lynchaj/duodyne/!Development/16 input-output.VDCENET, V1.0/readme.txt

The VDCENET IO board provides MOSTEK 8568 VDC video and an RTL8019AS wired Ethernet interface
