lynchaj/duodyne/!Development/22 input-output.BusExtender, V1.0/readme.md

This board extends the duodyne bus to the top of the other boards to aid in debugging and new board development
