lynchaj/duodyne/!Development/21 input-output.MCU-CPLD, V1.0/readme.txt

This board provides a SAB80535 MCU and EPM7128S for prototyping electronic projects with prototyping area.
