lynchaj/duodyne/!Development/Slick/readme.txt

The processor.Z80 board is the central processor for the duodyne system.  It uses a Z80 8-bit CPU and includes dual-DMA channels.  It supports Interrupt Mode 2 (IM2) and an extended memory mapper.

Known Issues
1. Missing pull-up resistors on ~DREQ0 and ~DREQ1
