lynchaj/duodyne/!Development/13 input-output.GDC, V1.0/readme.txt

This board provides a blank template for making input-output boards.  GAL information is notional and should be replaced with project specifics using Digital
