lynchaj/duodyne/!Development/08 input-output.Disk, V1.1/readme.txt

This board provides PPIDE for IDE hard drives and/or CF adapters and floppy drive controller.  Primary intended uses are for CF adapters and 3.5" floppy drives
