lynchaj/duodyne/duodyne.interrupt.survey.pdf

BOARD | DEVICE | INTERRUPTS | ENABLE JUMPER | IN/OUT
Processor.Z80 | DMA1 | INT0 | YES | OUT
Processor.Z80 | DMA2 | INT0 | YES | OUT
Processor.Z80 | IM2 | INT0 | YES | OUT
Processor.Z80 | UART | EIRQ0 | YES | OUT
IO.Zilog | 1CTC | INT0 | YES | OUT
IO.Zilog | SIO | INT0 | YES | OUT
IO.Zilog | 1PIO | INT0 | YES | OUT
IO.Zilog | 2PIO | INT0 | YES | OUT
IO.Zilog | 2CTC | INT1, INT2 | YES | IN
IO.Zilog | 2CTC | INT0 | YES | OUT
IO.Multi | DUART.A | INT0, EIRQ0-7 | YES | OUT
IO.Multi | DUART.B | INT0, EIRQ0-7 | YES | OUT
IO.Multi | Parallel | INT0, EIRQ0-7 | YES | OUT
IO.Multi | KBDMSE | INT0, EIRQ0-7 | YES | OUT
IO.Multi | USB | INT0, EIRQ0-7 | YES | OUT
IO.Disk | FDC | INT0, EIRQ0-7 | YES | OUT
IO.Disk | Ethernet | INT0, EIRQ0-7 | YES | OUT
IO.Voice | ADC | INT0, EIRQ0-7 | YES | OUT
IO.Media | VDP | INT0, EIRQ0-7 | YES | OUT

All=
