lynchaj/duodyne/00 enclosure, V1.0/20250329_211026.jpg

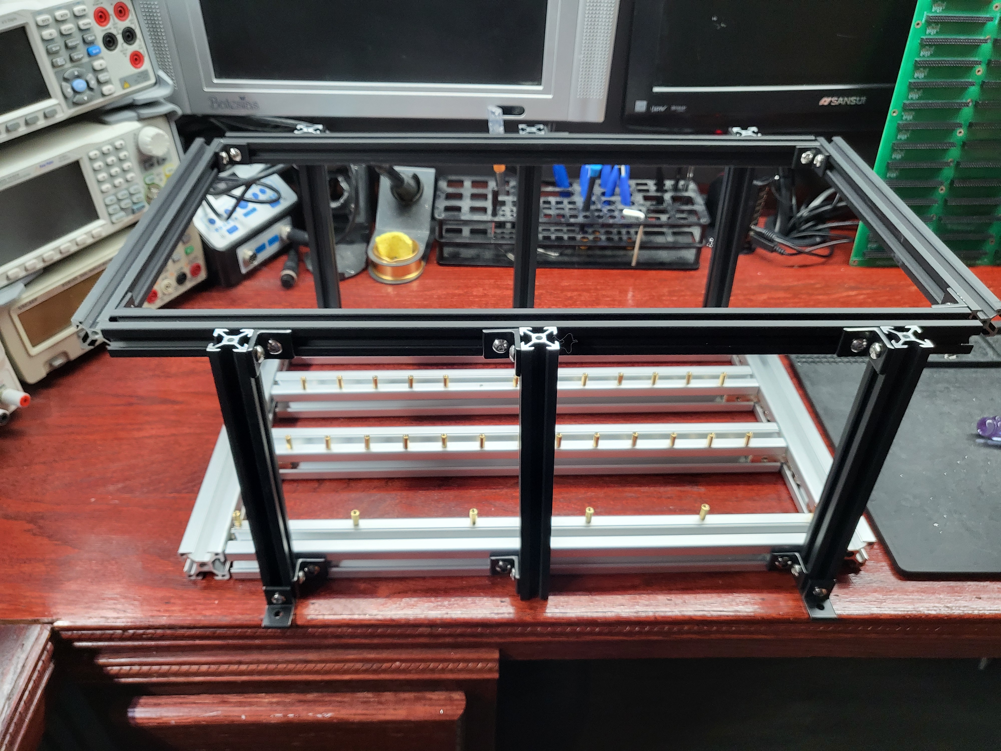
00 enclosure, V1.0/20250329_211026.jpg
