lynchaj/duodyne/00 enclosure, V1.0/Picture1.jpg

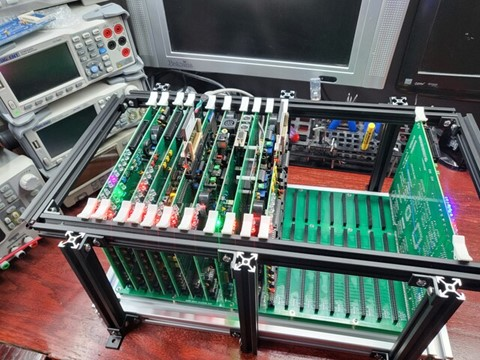
00 enclosure, V1.0/Picture1.jpg
