lynchaj/duodyne/00 enclosure, V1.0/Picture2.jpg

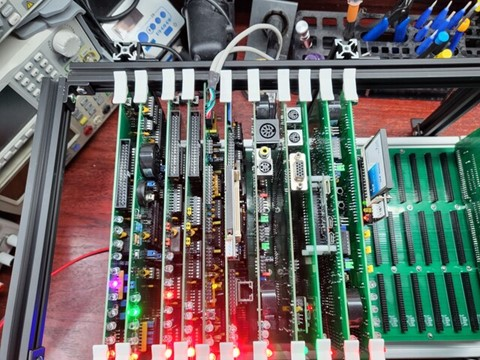
00 enclosure, V1.0/Picture2.jpg
