lynchaj/duodyne/01 template.prototyping, V1.0/template.prototyping.jpg

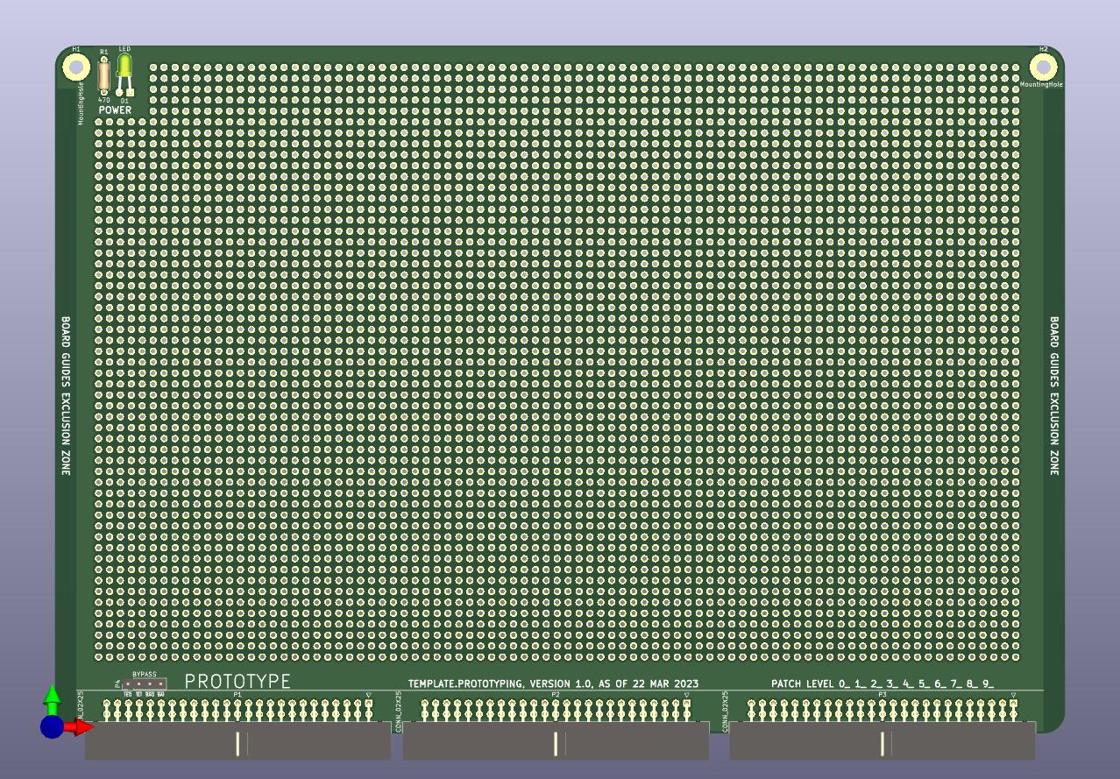
01 template.prototyping, V1.0/template.prototyping.jpg
