lynchaj/duodyne/02 backplane.8-slot, V1.0/backplane.8-slot.jpg

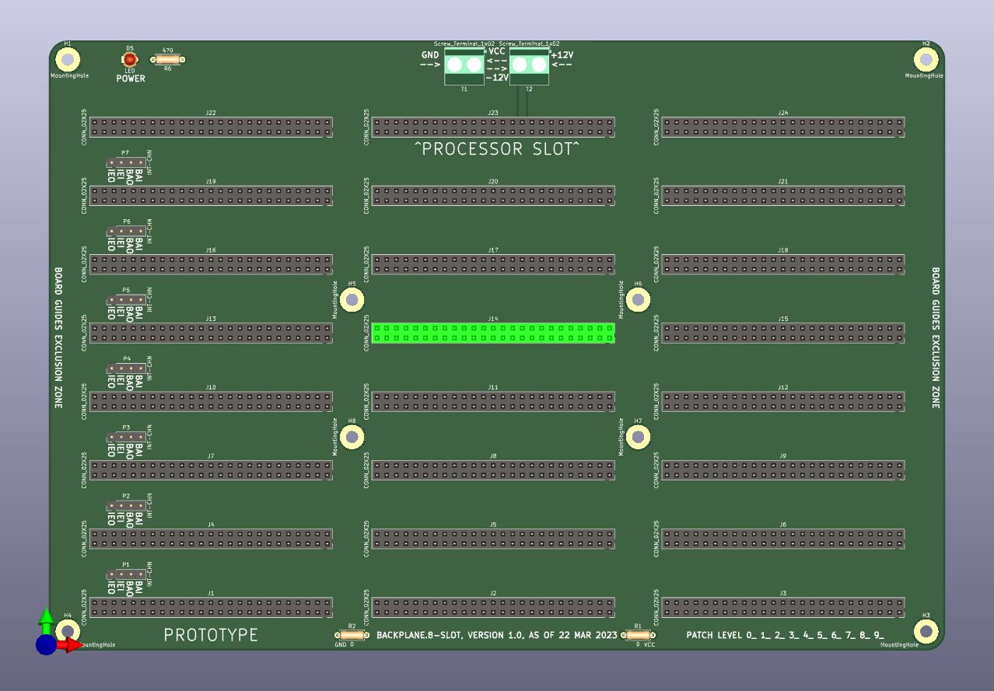
02 backplane.8-slot, V1.0/backplane.8-slot.jpg
