lynchaj/duodyne/03 processor.Z80, V1.1/CPU-DATA-DIR-GAL-V3.png

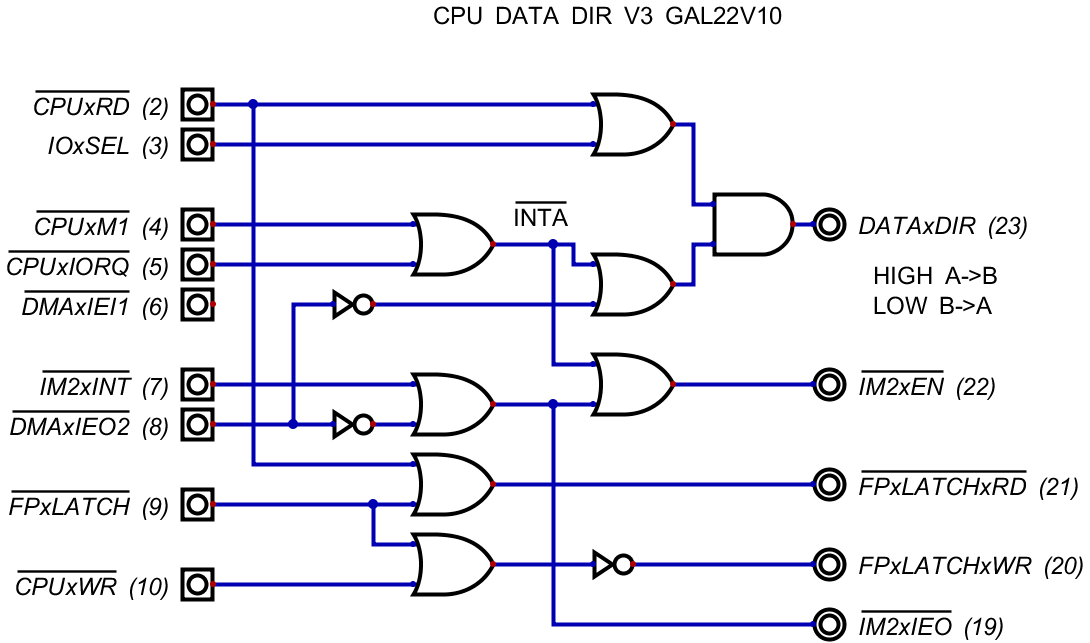
03 processor.Z80, V1.1/CPU-DATA-DIR-GAL-V3.png
