lynchaj/duodyne/03 processor.Z80, V1.1/CPU-MAPPER-V3.png

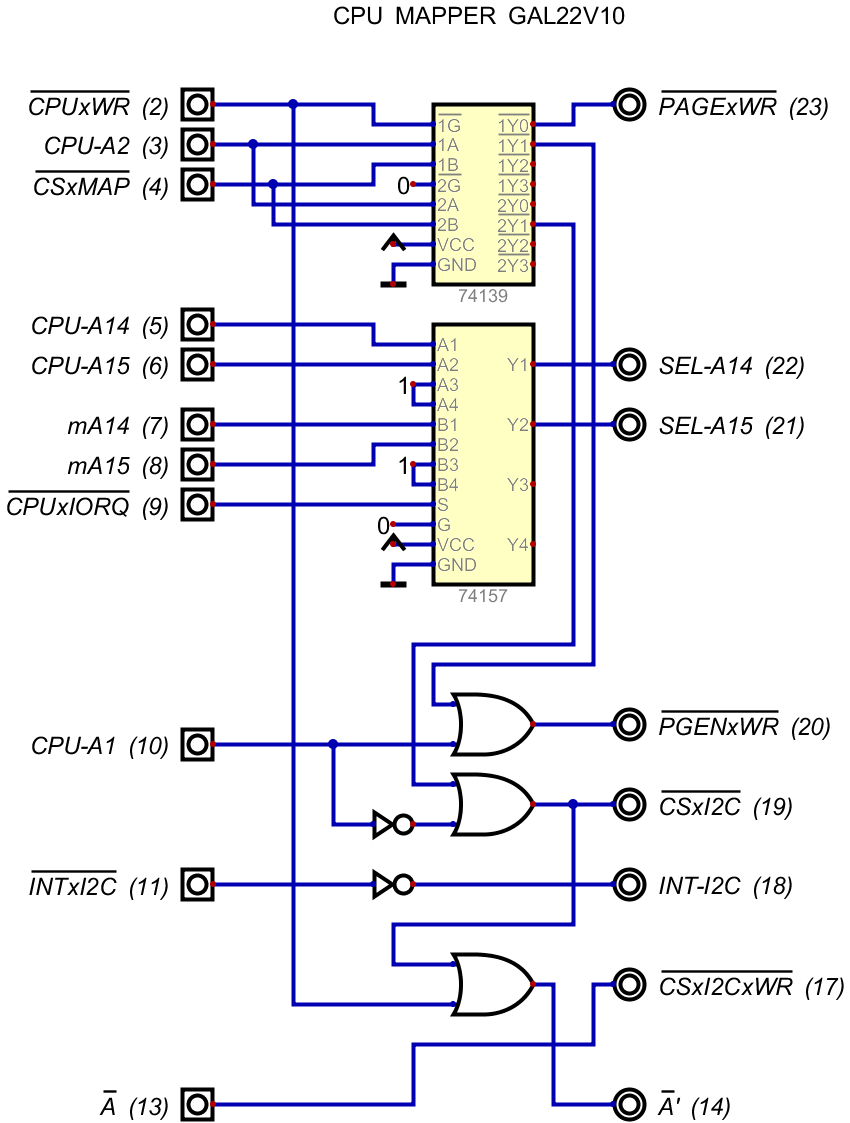
03 processor.Z80, V1.1/CPU-MAPPER-V3.png
