lynchaj/duodyne/03 processor.Z80, V1.1/DMA-CS-GAL-V4.png

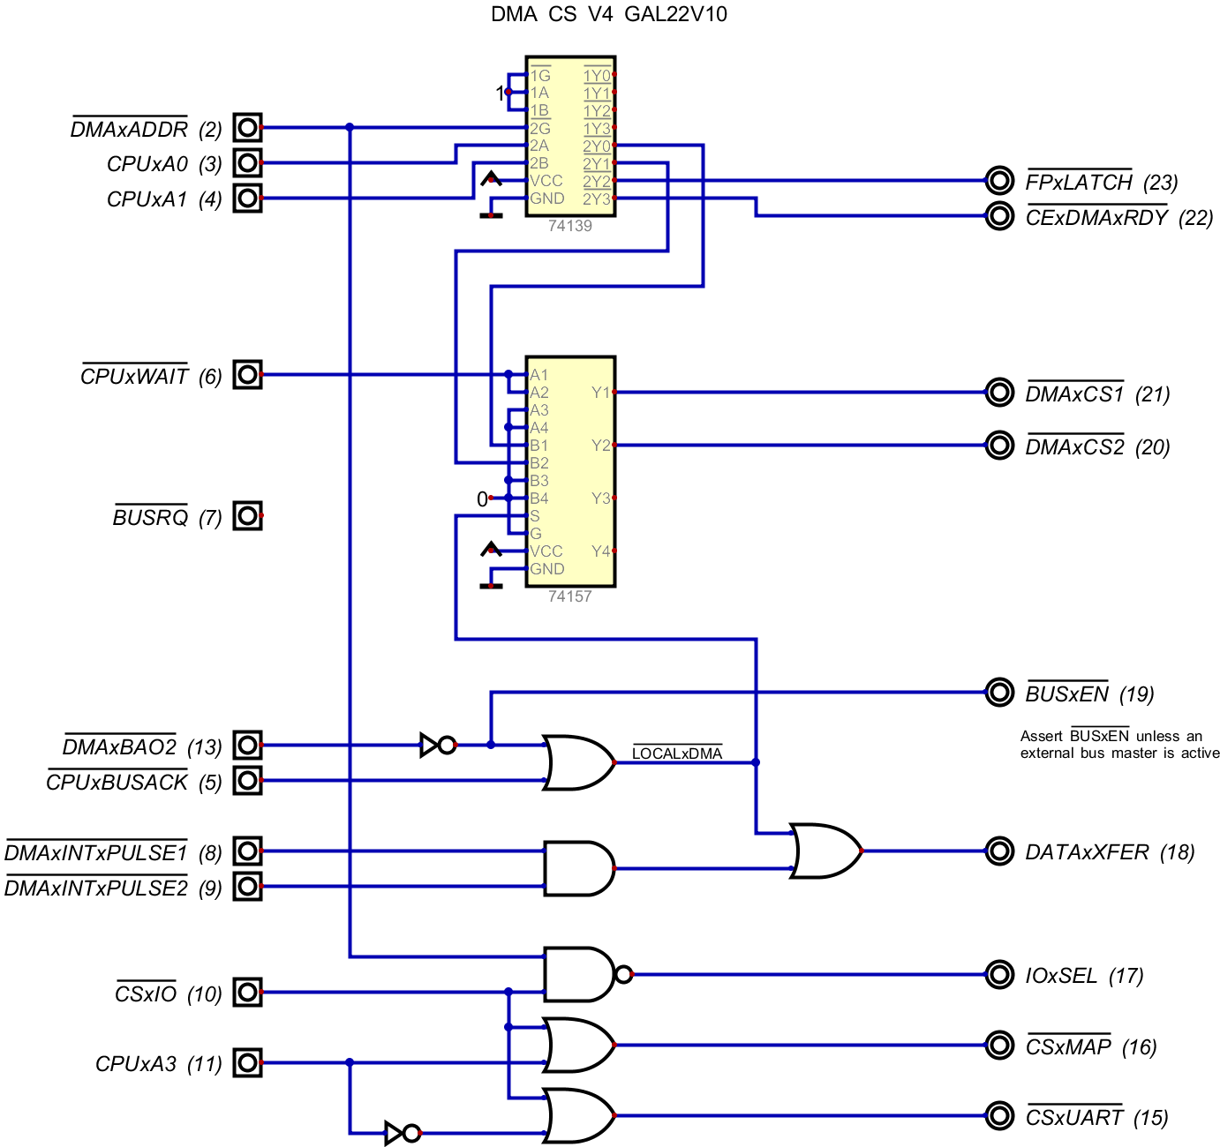
03 processor.Z80, V1.1/DMA-CS-GAL-V4.png
