lynchaj/duodyne/03 processor.Z80, V1.1/processor.Z80.jpg

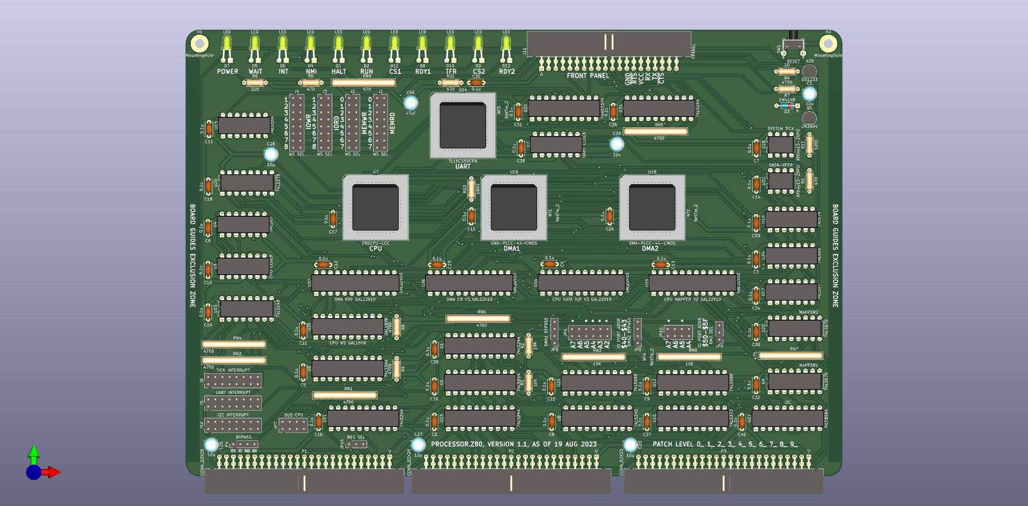
03 processor.Z80, V1.1/processor.Z80.jpg
