lynchaj/duodyne/04 memory.ROMRAM.8-bit, V1.1/memory.ROMRAM.jpg

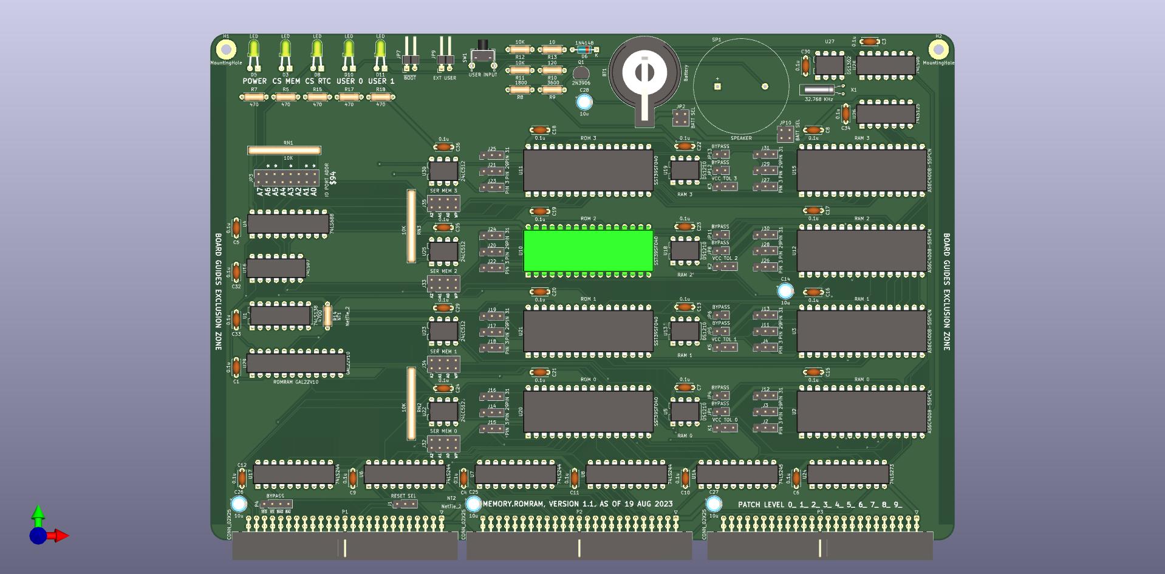
04 memory.ROMRAM.8-bit, V1.1/memory.ROMRAM.jpg
