lynchaj/duodyne/05 input-output.Zilog, V1.1/input-output.Zilog.jpg

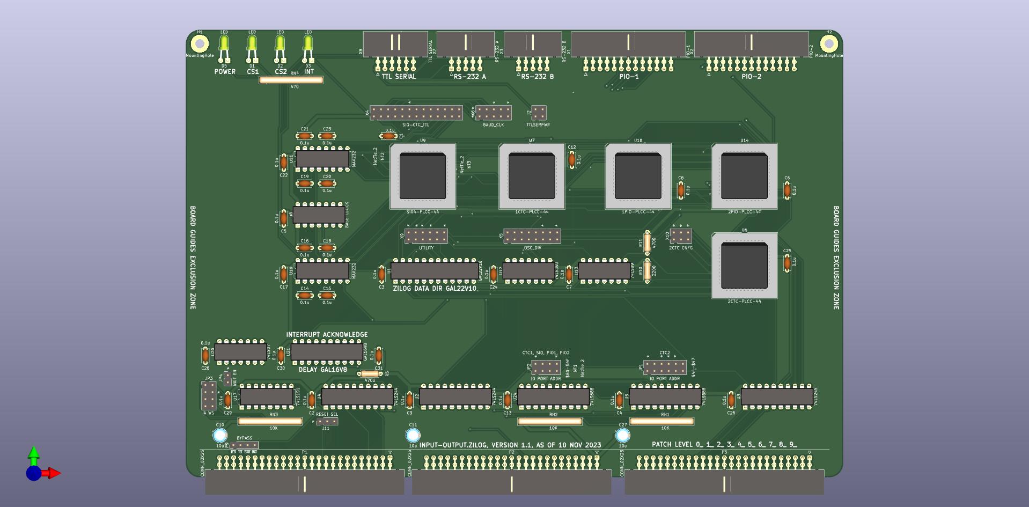
05 input-output.Zilog, V1.1/input-output.Zilog.jpg
