lynchaj/duodyne/05 input-output.Zilog, V1.1/temp/ZP-DATA-DIR-GAL.png

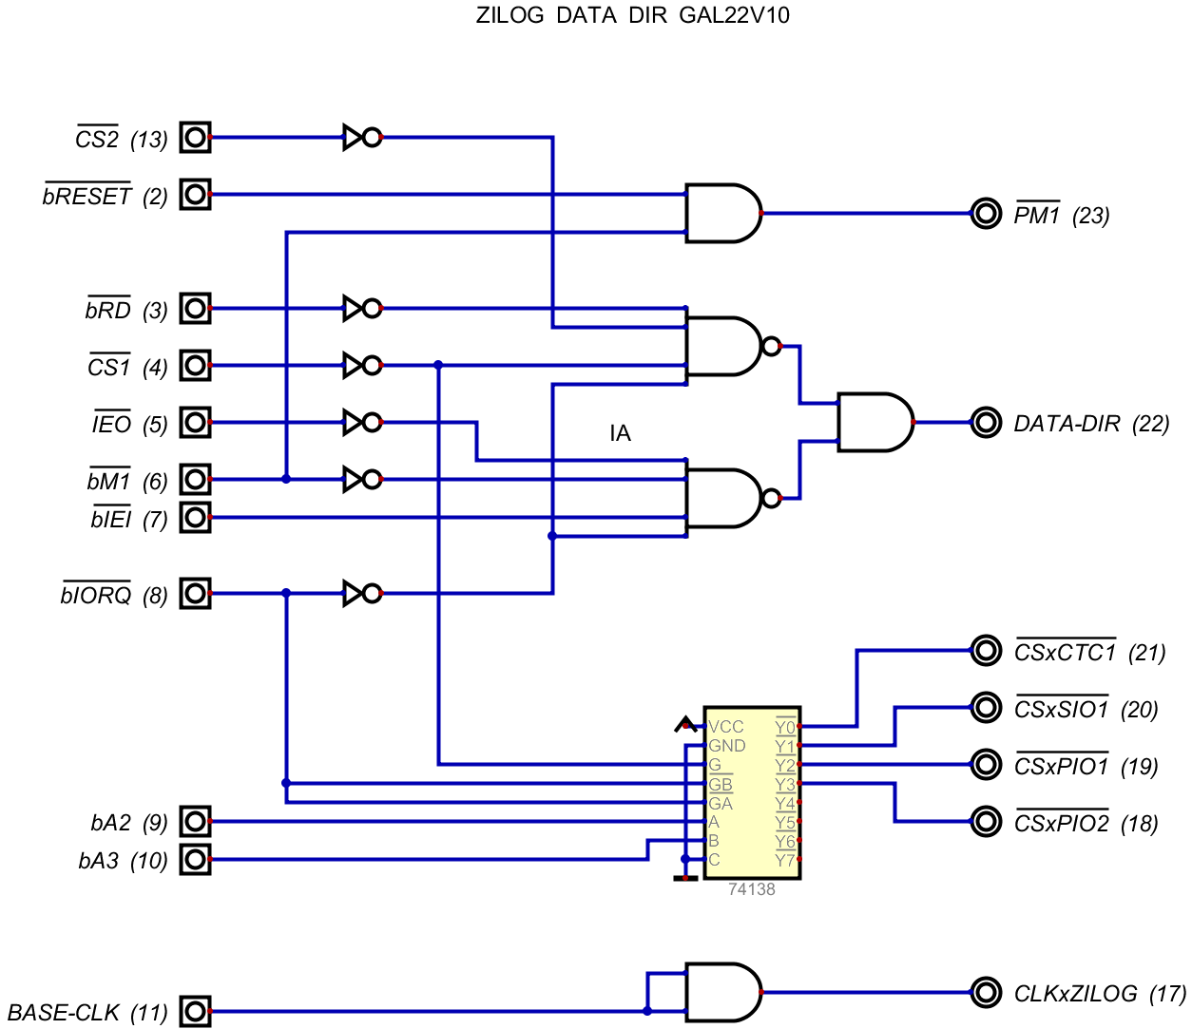
05 input-output.Zilog, V1.1/temp/ZP-DATA-DIR-GAL.png
