lynchaj/duodyne/05 input-output.Zilog, V1.1/ZP-DATA-DIR-GAL-V2.png

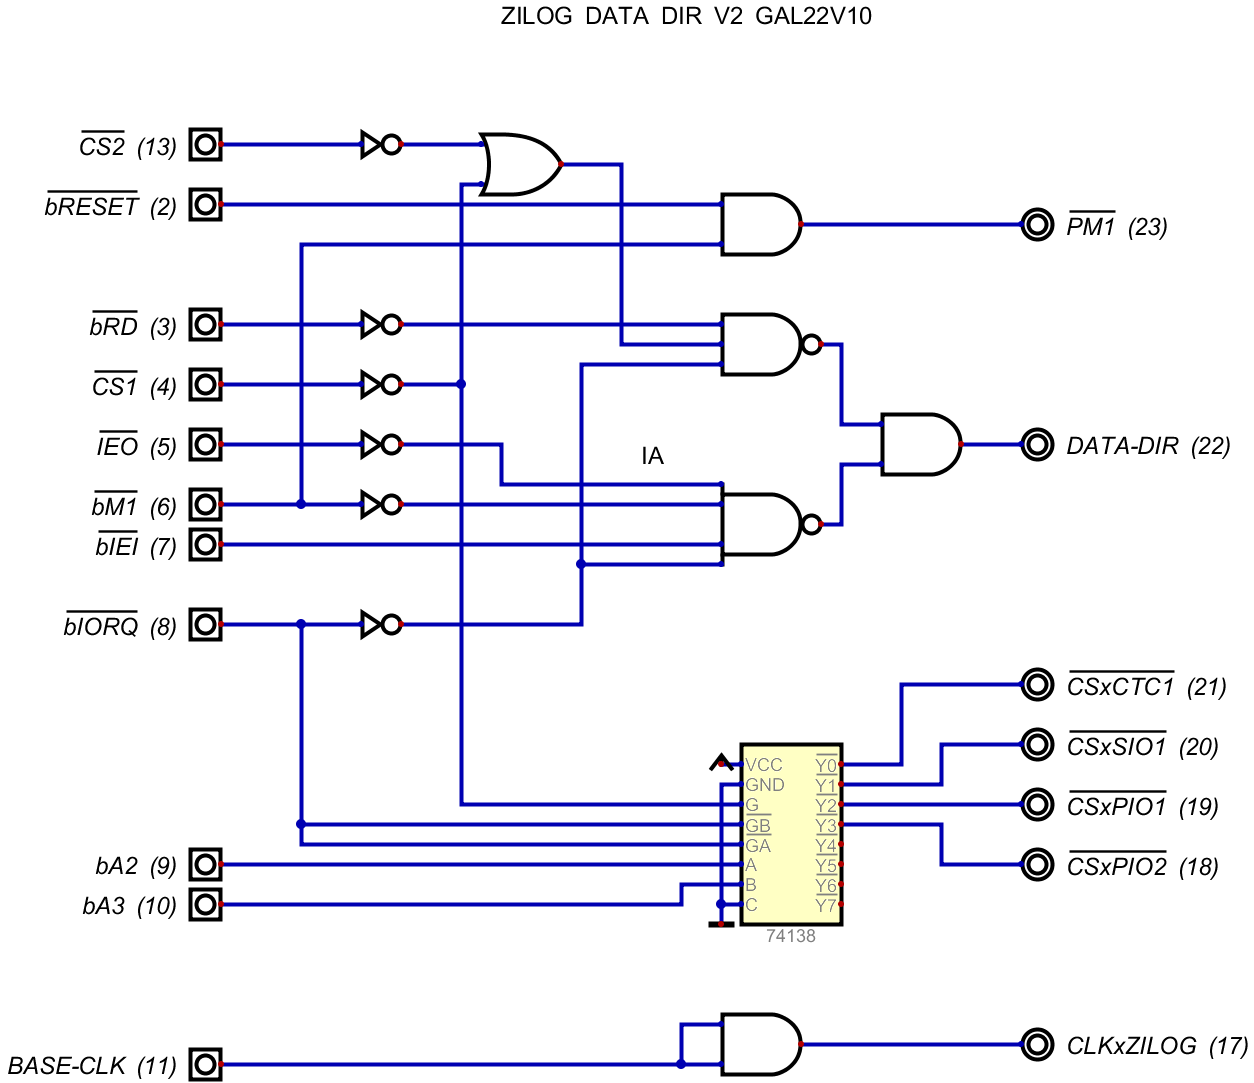
05 input-output.Zilog, V1.1/ZP-DATA-DIR-GAL-V2.png
