lynchaj/duodyne/05 input-output.Zilog, V1.1/ZP-IA-DELAY-GAL.png

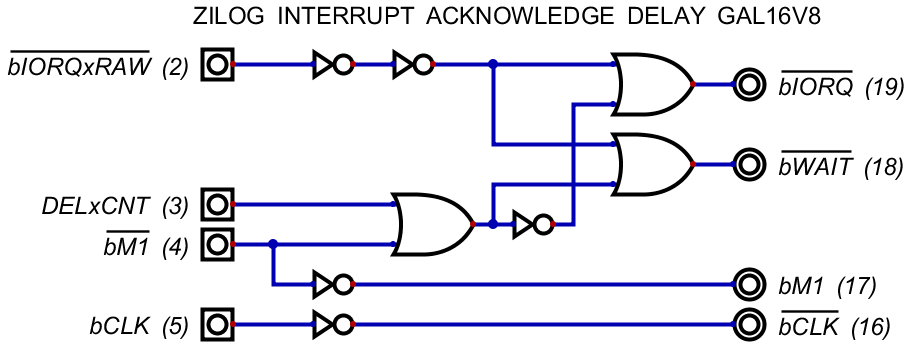
05 input-output.Zilog, V1.1/ZP-IA-DELAY-GAL.png
