lynchaj/duodyne/06 input-output.Multi, V1.0/input-output.Multi.jpg

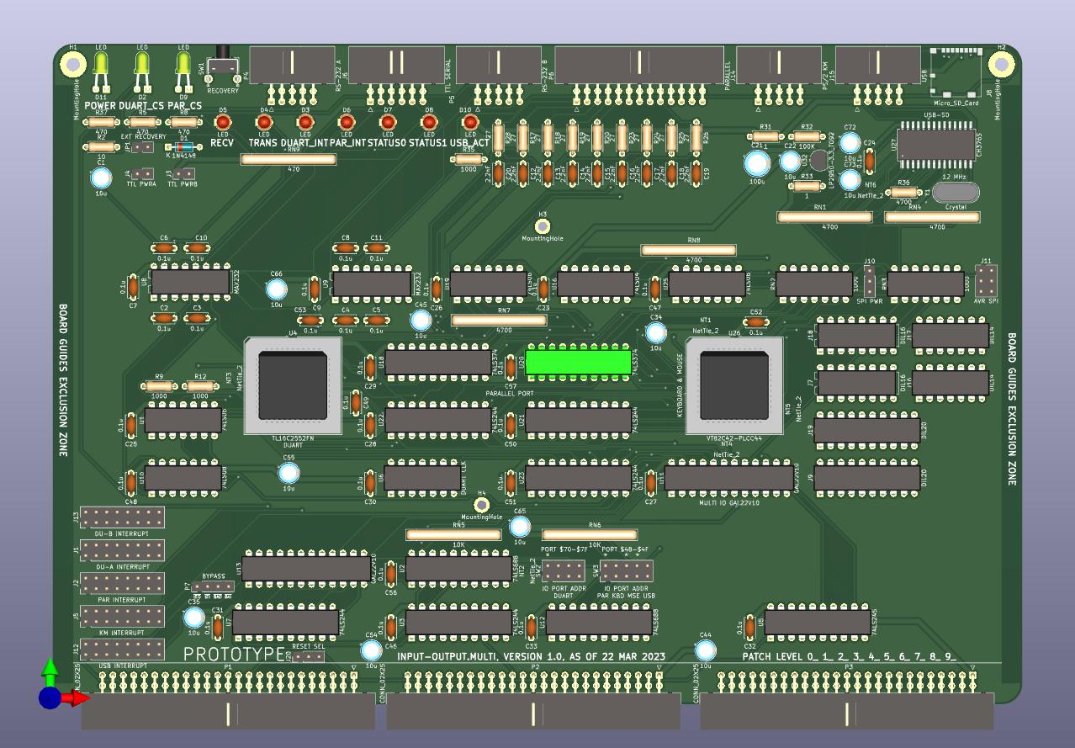
06 input-output.Multi, V1.0/input-output.Multi.jpg
