lynchaj/duodyne/07 backplane.4-slot, V1.0/backplane.4-slot.jpg

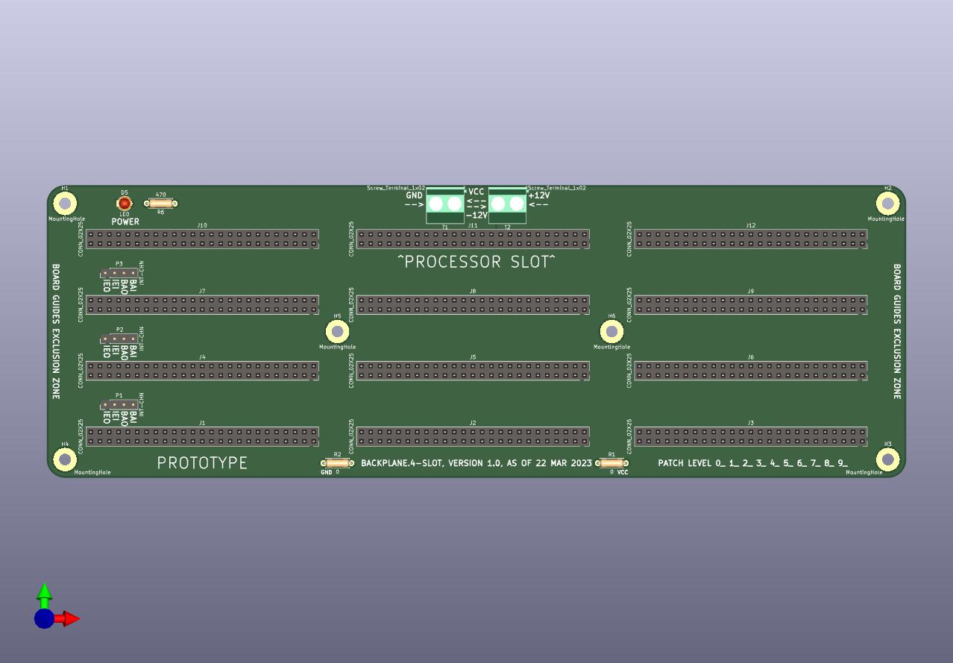
07 backplane.4-slot, V1.0/backplane.4-slot.jpg
