lynchaj/duodyne/08 input-output.Disk, V1.0/temp/3D-View_SD-Card_Holder.png

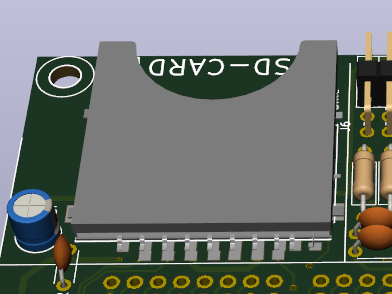
08 input-output.Disk, V1.0/temp/3D-View_SD-Card_Holder.png
