lynchaj/duodyne/08 input-output.Disk, V1.0/temp/FDC-CS-GAL.png

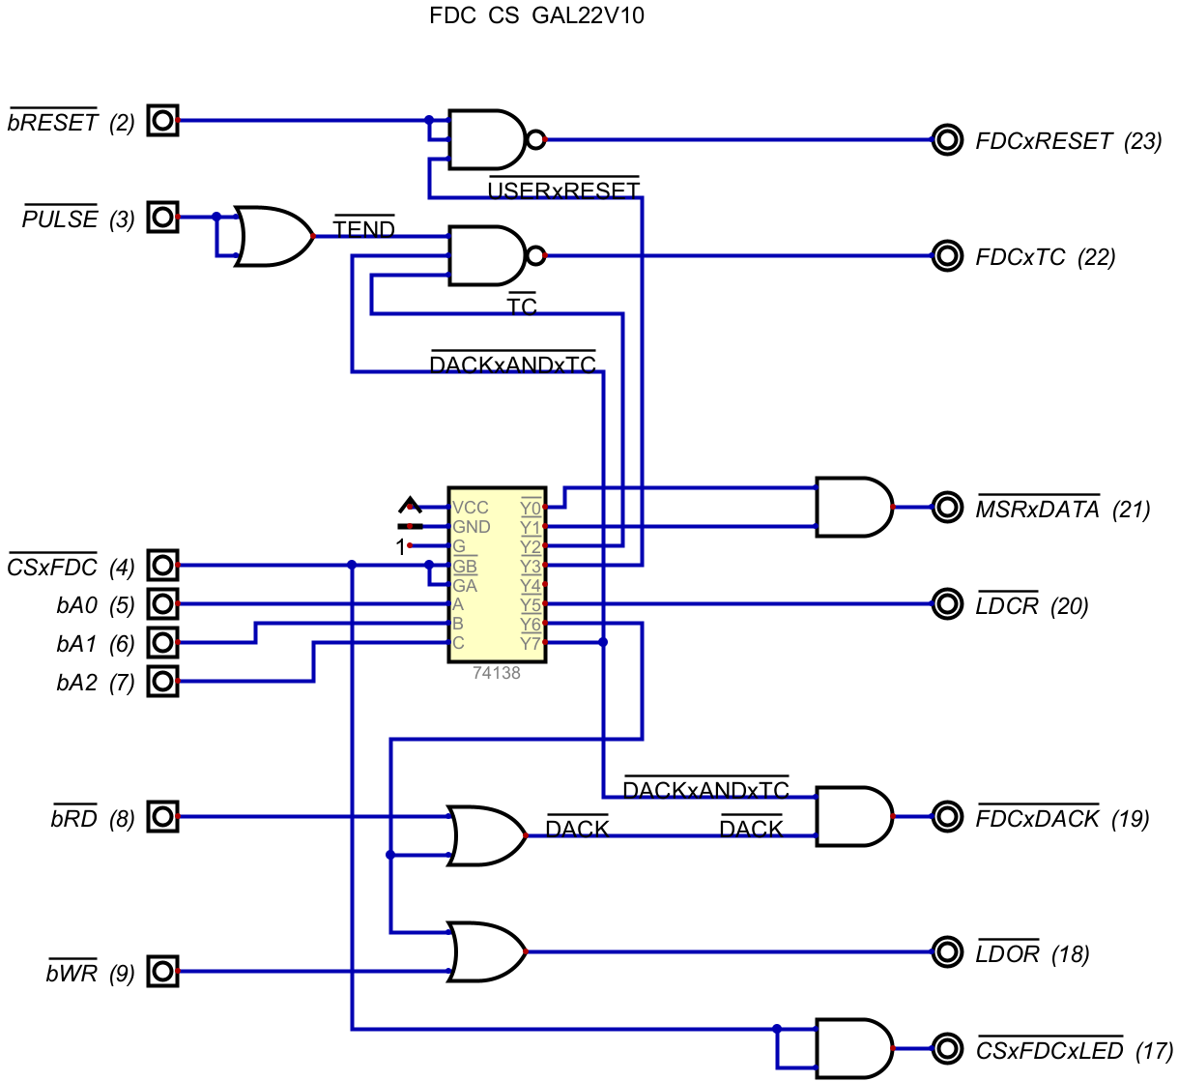
08 input-output.Disk, V1.0/temp/FDC-CS-GAL.png
