lynchaj/duodyne/08 input-output.Disk, V1.0/temp/SD-Card_Footprint_on_PCB.png

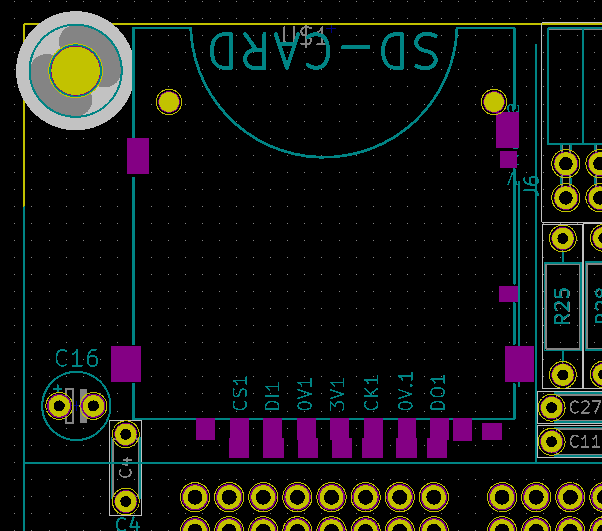
08 input-output.Disk, V1.0/temp/SD-Card_Footprint_on_PCB.png
