lynchaj/duodyne/10 input-output.Voice, V1.0/input-output.Voice.jpg

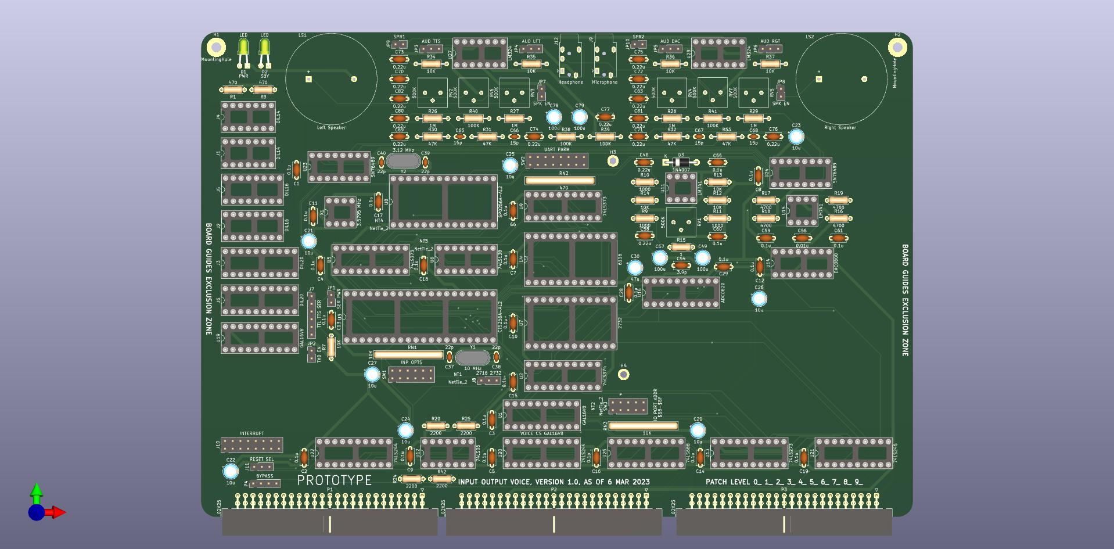
10 input-output.Voice, V1.0/input-output.Voice.jpg
