lynchaj/duodyne/10 input-output.Voice, V1.0/temp/VOICE-CS-GAL-V2.png

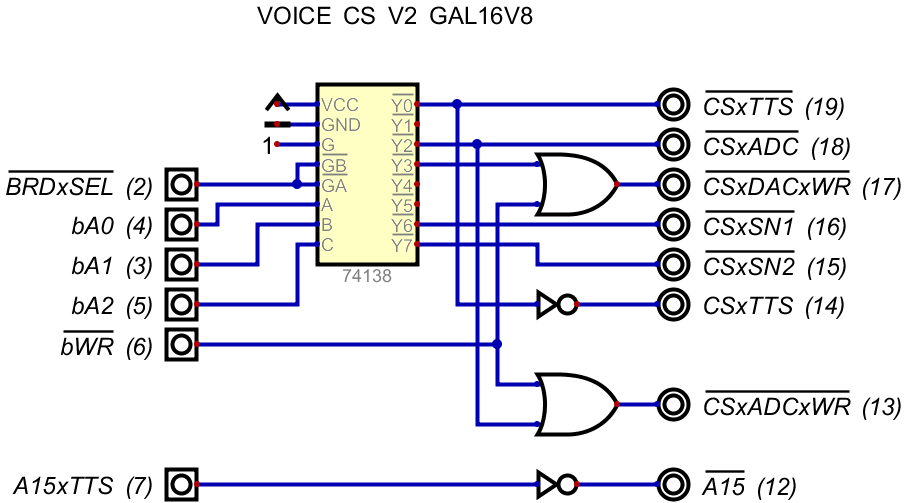
10 input-output.Voice, V1.0/temp/VOICE-CS-GAL-V2.png
