lynchaj/duodyne/10 input-output.Voice, V1.0/temp/Z180GDCV2-SND/U10.png

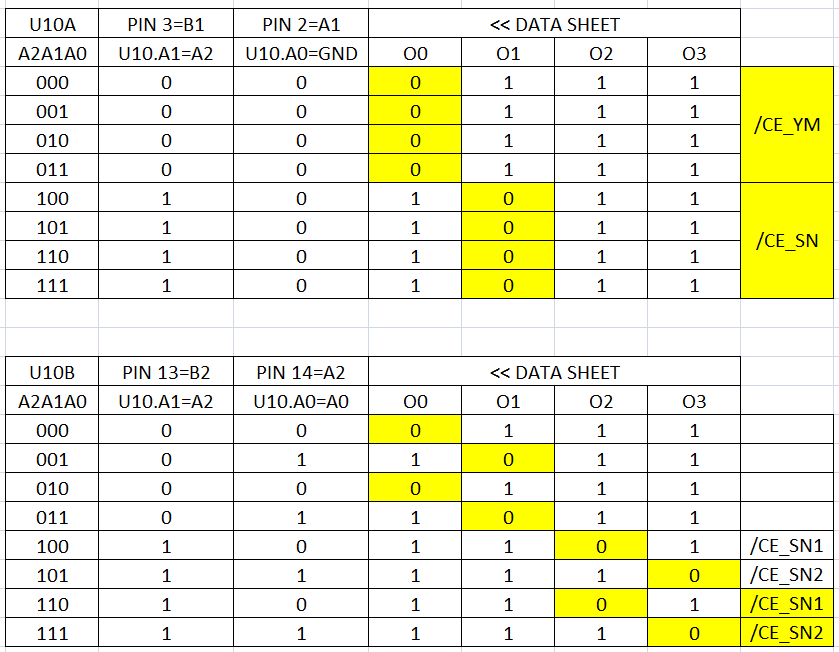
10 input-output.Voice, V1.0/temp/Z180GDCV2-SND/U10.png
