lynchaj/duodyne/10 input-output.Voice, V1.0/VOICE-CS-GAL-V3.png

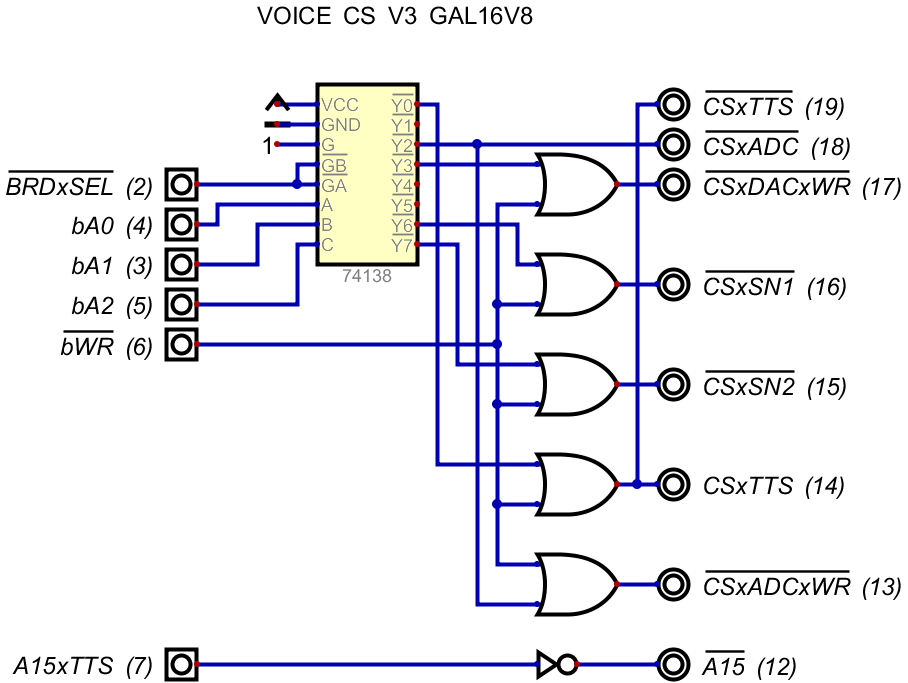
10 input-output.Voice, V1.0/VOICE-CS-GAL-V3.png
