lynchaj/duodyne/11 input-output.Media, V1.1/FPGA Emulator Interface.png

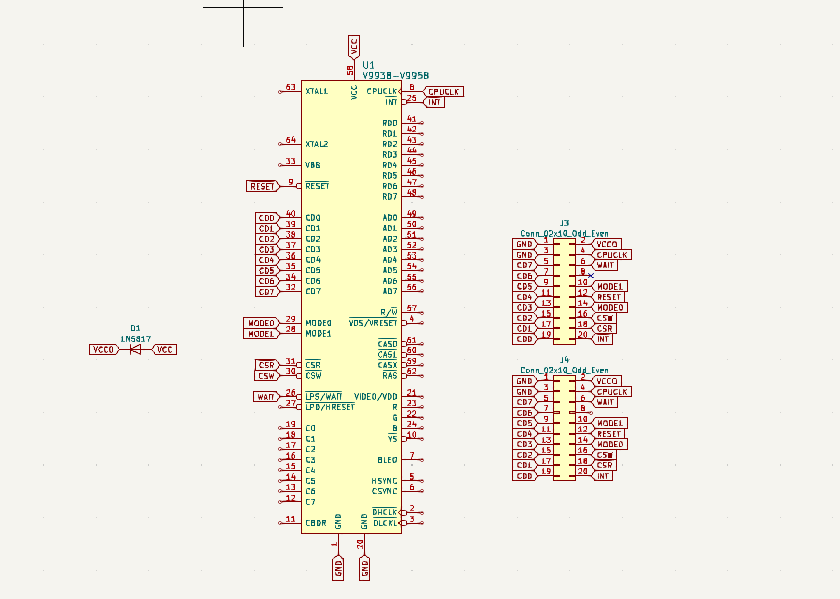
11 input-output.Media, V1.1/FPGA Emulator Interface.png
