lynchaj/duodyne/11 input-output.Media, V1.1/image001.png

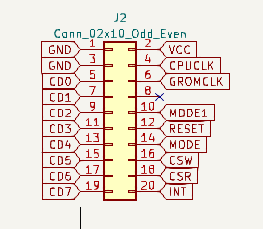
11 input-output.Media, V1.1/image001.png
