lynchaj/duodyne/11 input-output.Media, V1.1/input-output.Media-BACK.jpg

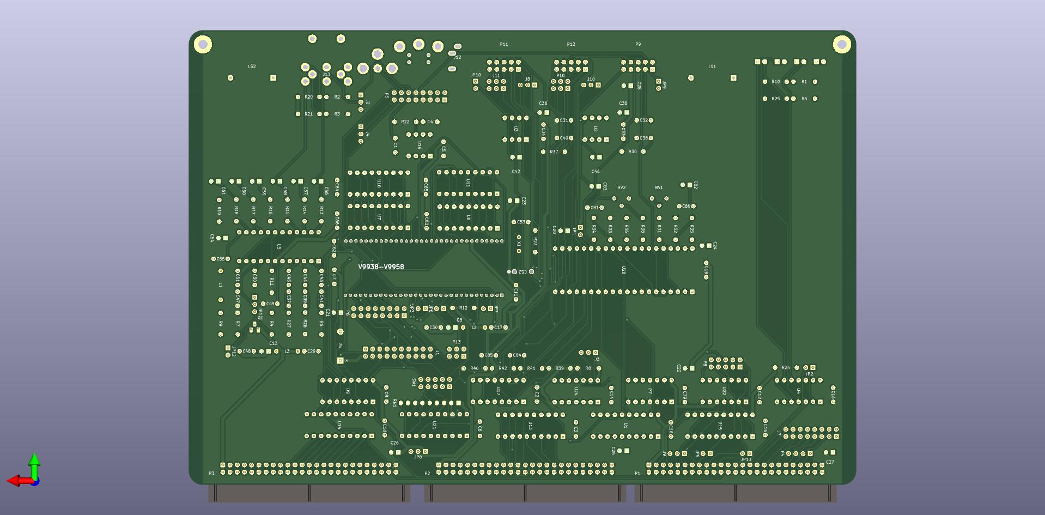
11 input-output.Media, V1.1/input-output.Media-BACK.jpg
