lynchaj/duodyne/11 input-output.Media, V1.1/MEDIA-CS-GAL-V3.png

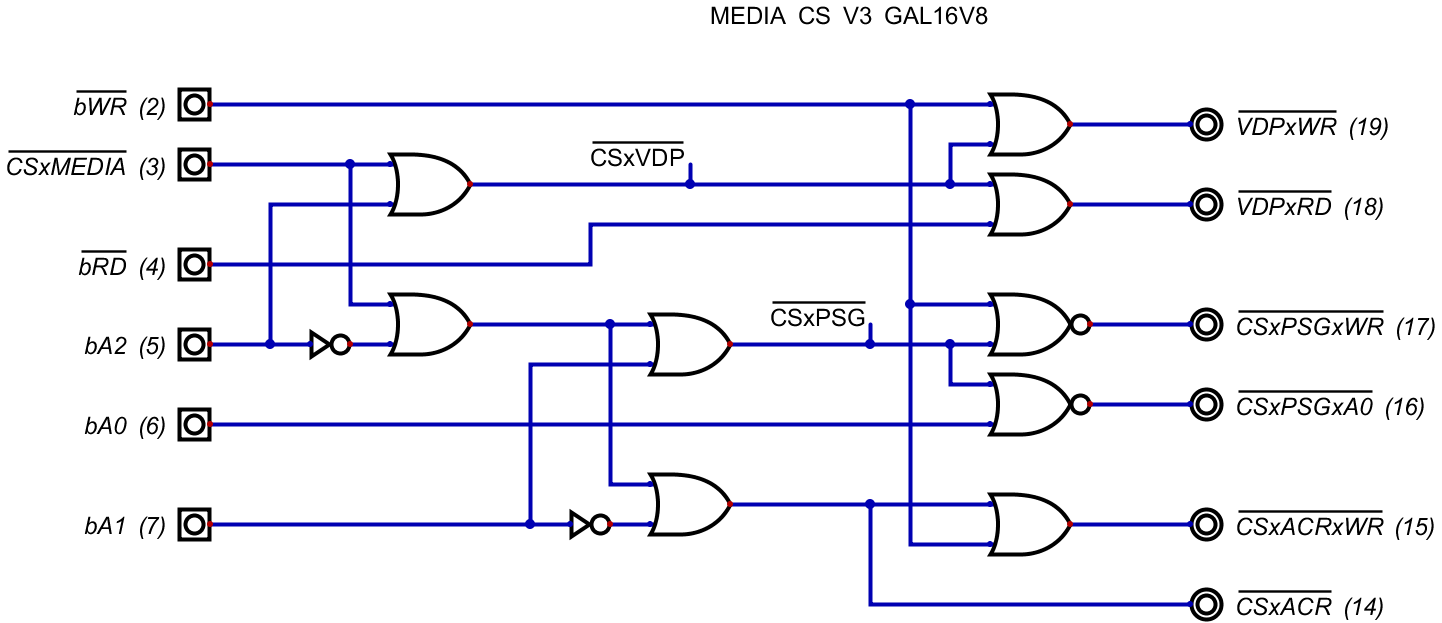
11 input-output.Media, V1.1/MEDIA-CS-GAL-V3.png
