lynchaj/duodyne/11 input-output.Media, V1.1/temp/MEDIA-CS-GAL.png

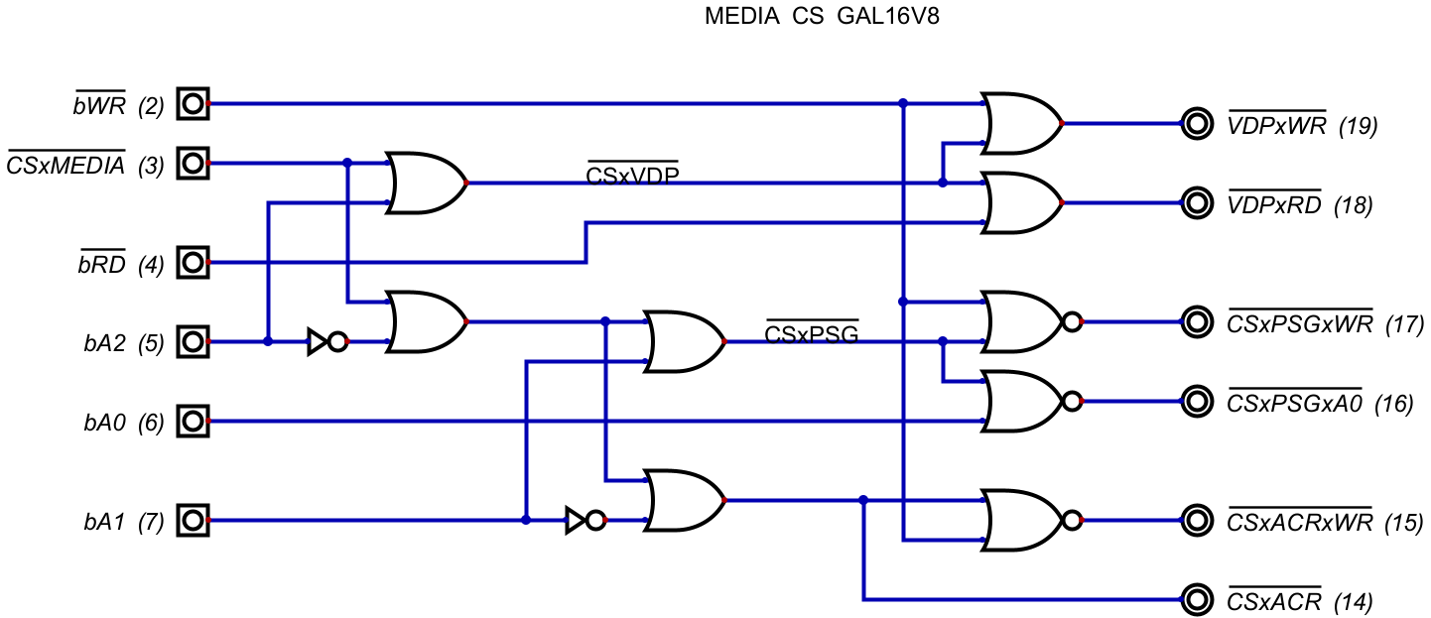
11 input-output.Media, V1.1/temp/MEDIA-CS-GAL.png
