lynchaj/duodyne/11 input-output.Media, V1.1/temp/MEDIA-CS-V2-GAL.png

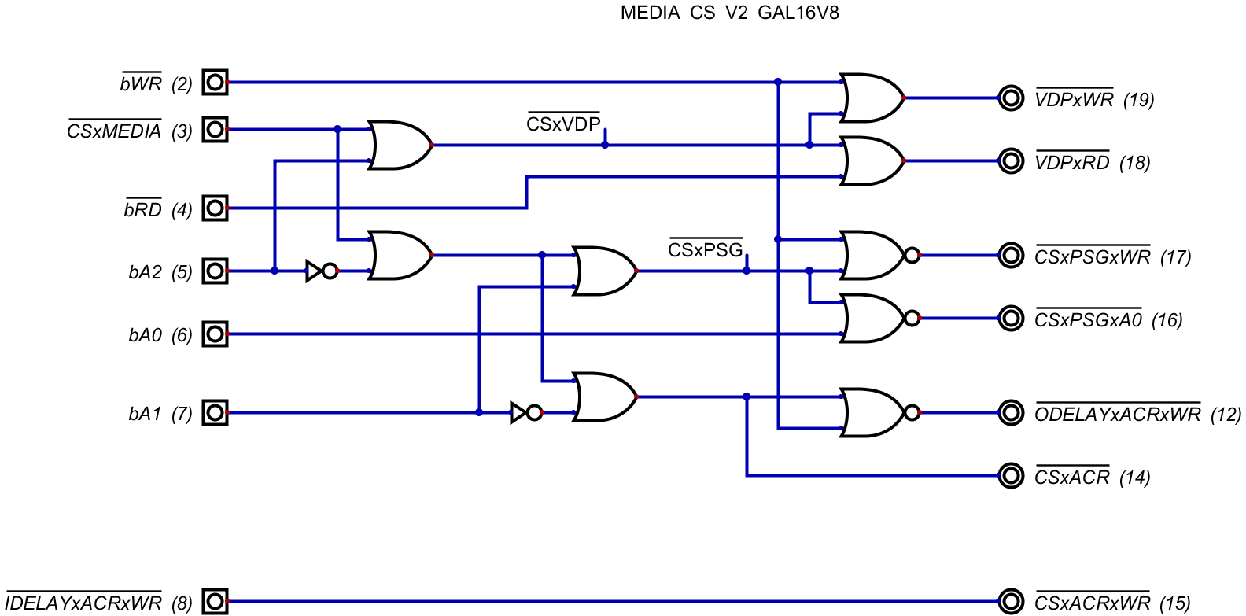
11 input-output.Media, V1.1/temp/MEDIA-CS-V2-GAL.png
