lynchaj/duodyne/13 front-panel.processor ALT/hardware/wayne front panel concept.png

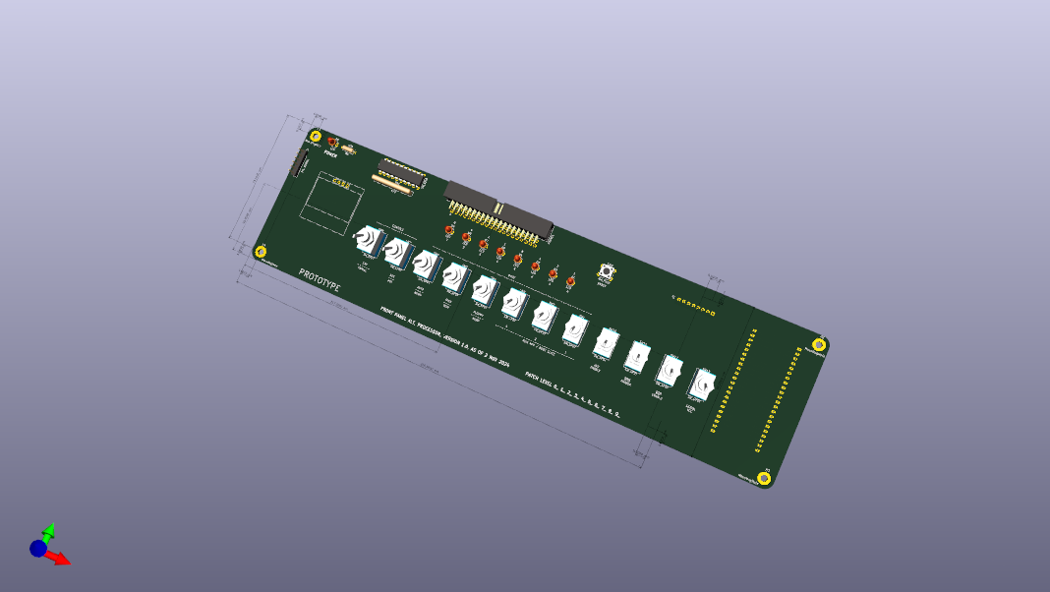
13 front-panel.processor ALT/hardware/wayne front panel concept.png
