lynchaj/duodyne/17 input-output.DualESP32, V1.0/hardware/DUALESP32 GAL.png

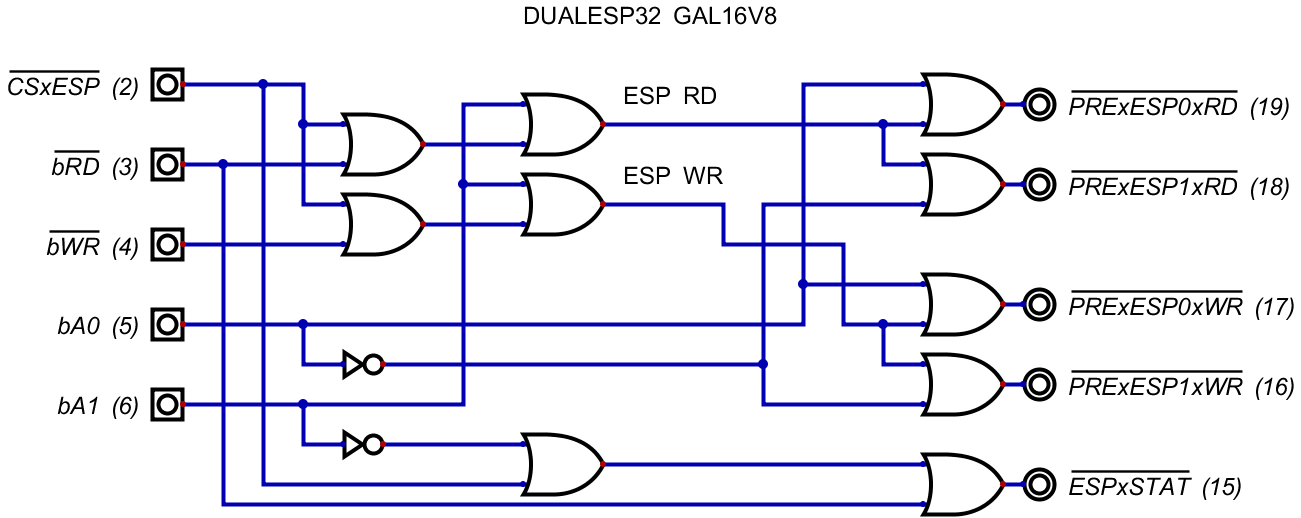
17 input-output.DualESP32, V1.0/hardware/DUALESP32 GAL.png
