lynchaj/duodyne/18 processor.65816, V1.0/processor.65816.jpg

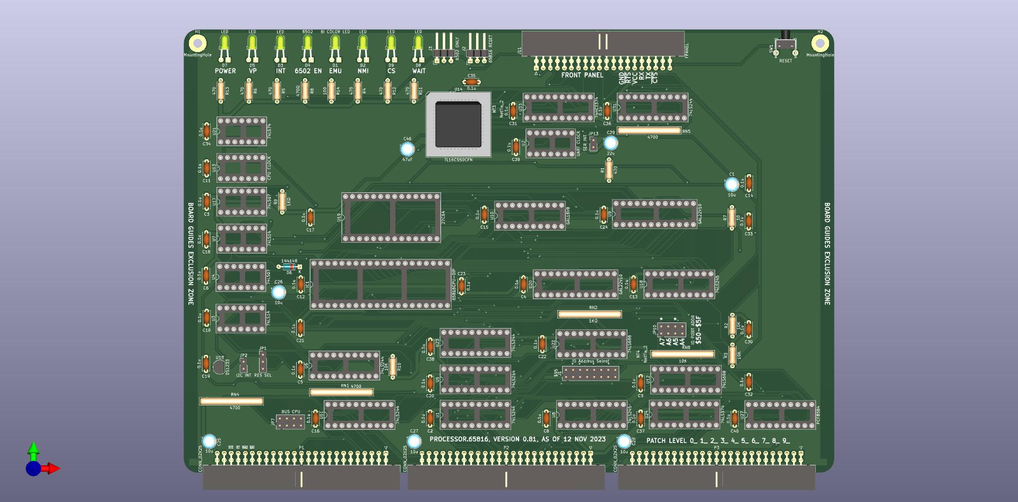
18 processor.65816, V1.0/processor.65816.jpg
