lynchaj/duodyne/20 processor.TMS9995/hardware/processor.tms9995.jpg

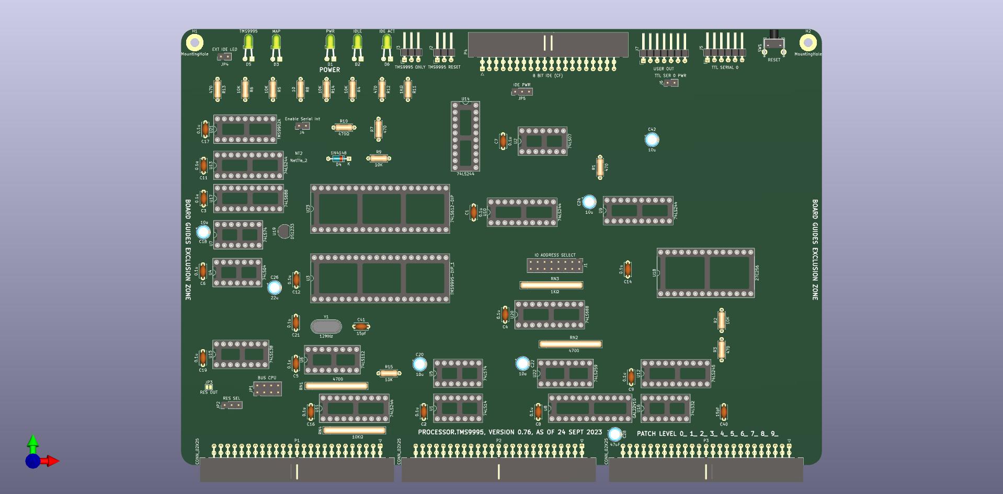
20 processor.TMS9995/hardware/processor.tms9995.jpg
