lynchaj/duodyne/23 processor.6809/hardware/processor.6809.jpg

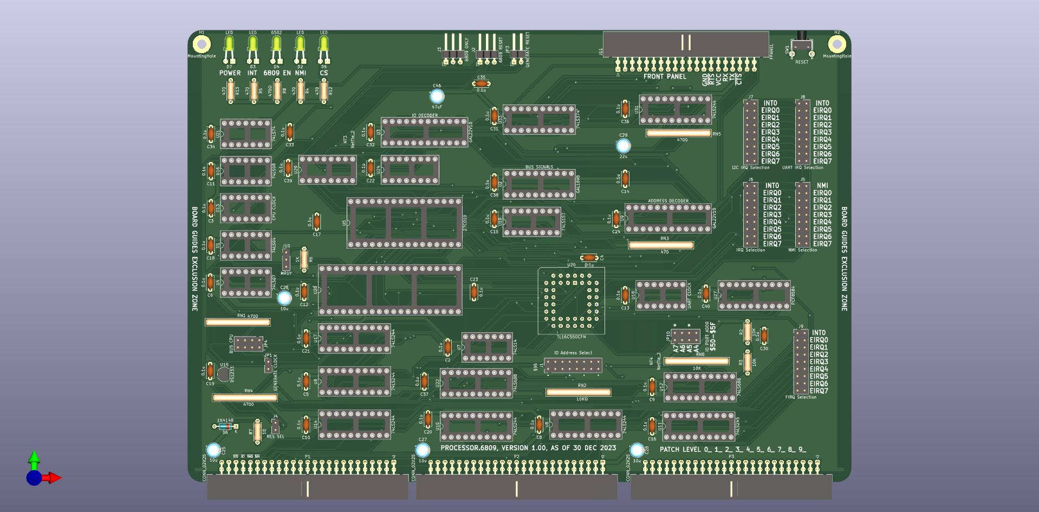
23 processor.6809/hardware/processor.6809.jpg
