lynchaj/duodyne/!Development/06 input-output.Multi, V1.1/input-output.Multi.jpg

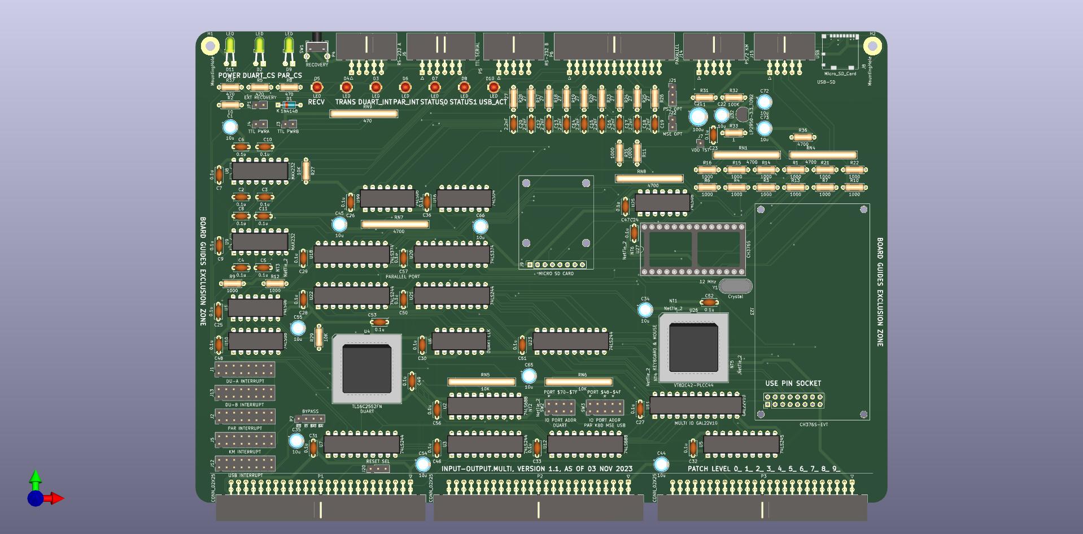
!Development/06 input-output.Multi, V1.1/input-output.Multi.jpg
