lynchaj/duodyne/!Development/06 input-output.Multi, V1.1/multi-GAL1.png

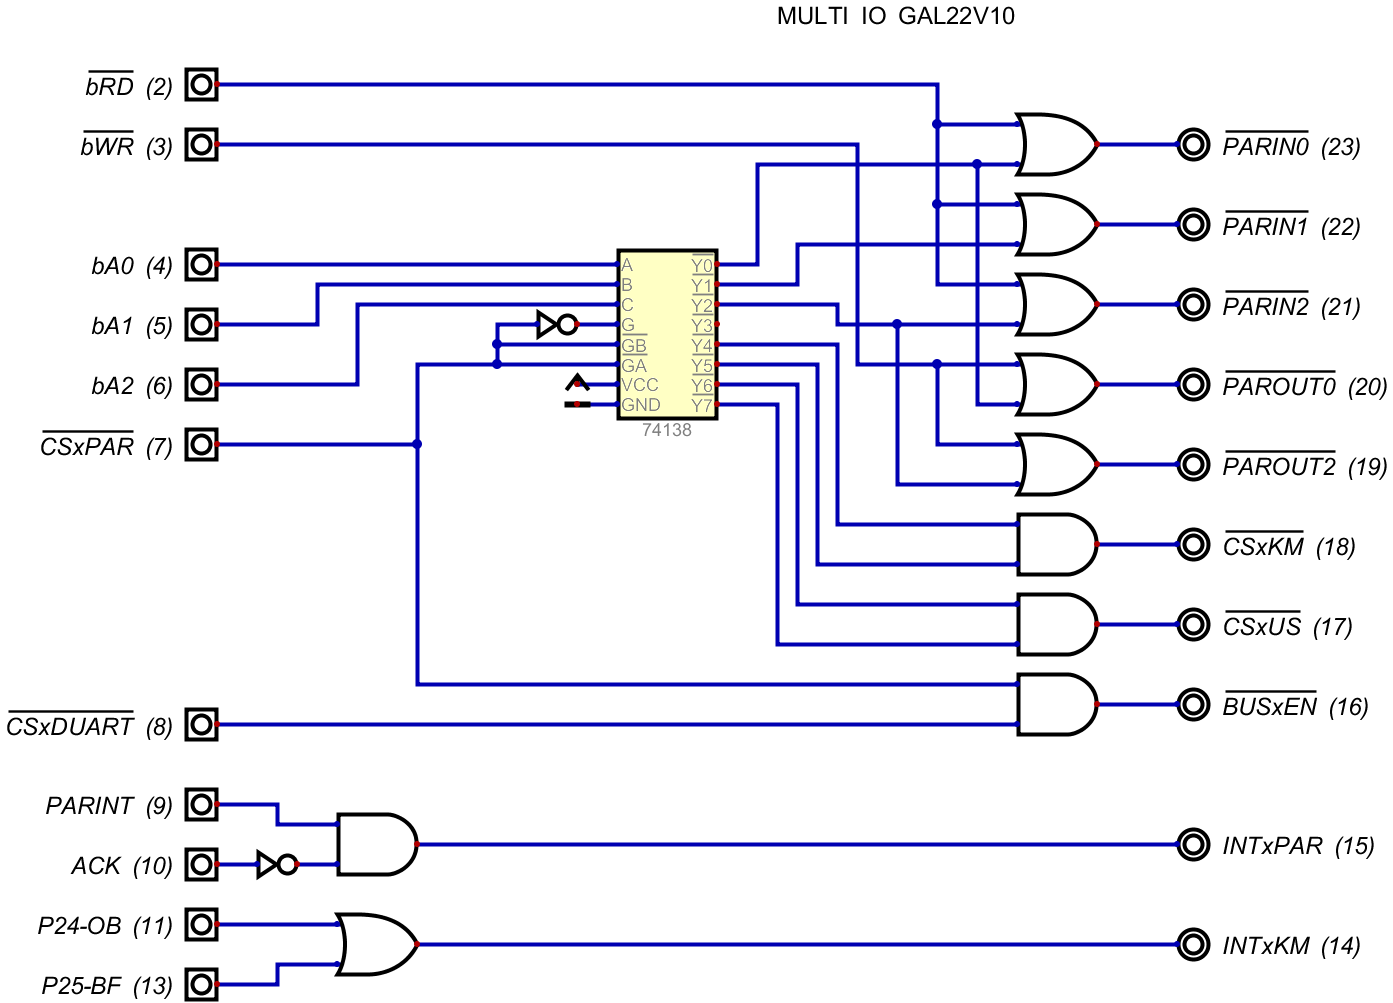
!Development/06 input-output.Multi, V1.1/multi-GAL1.png
