lynchaj/duodyne/!Development/08 input-output.Disk, V1.1/DISK-CS-GAL.png

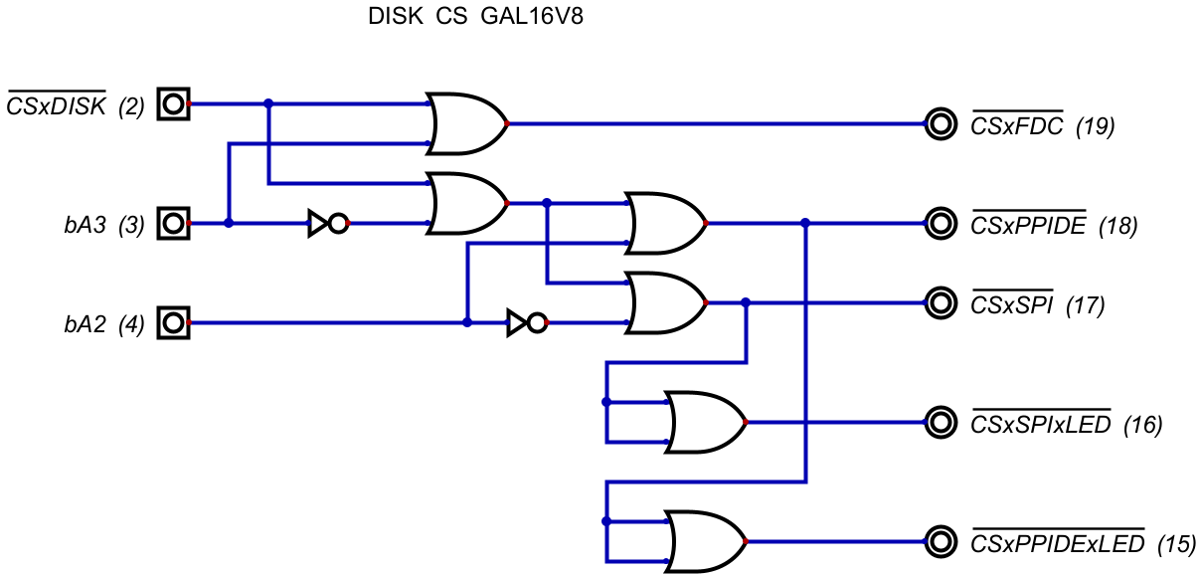
!Development/08 input-output.Disk, V1.1/DISK-CS-GAL.png
