lynchaj/duodyne/!Development/08 input-output.Disk, V1.1/input-output.Disk.jpg

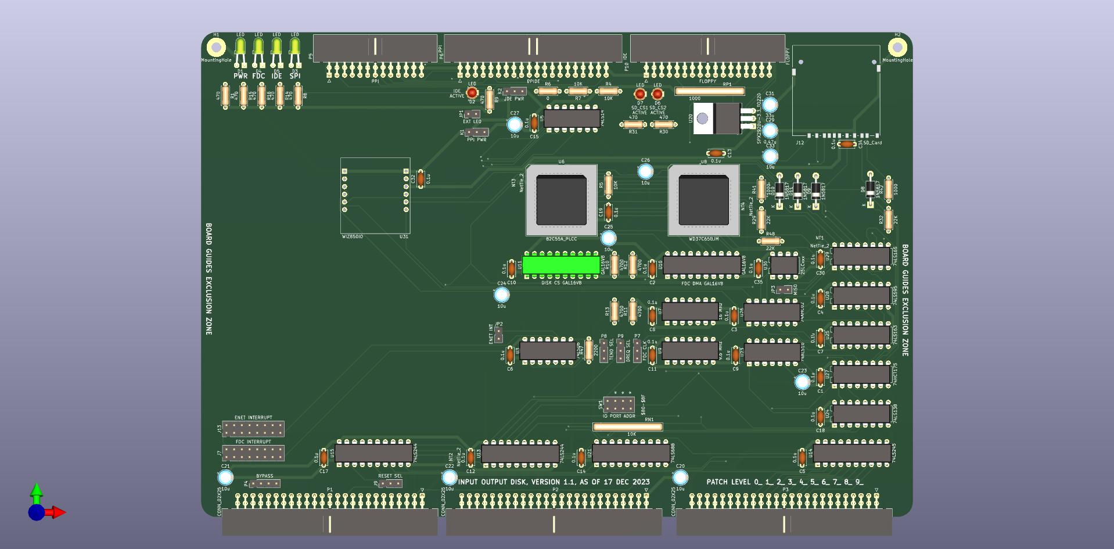
!Development/08 input-output.Disk, V1.1/input-output.Disk.jpg
