lynchaj/duodyne/!Development/12 front-panel.processor, V1.1/adafruit_products_fabprint.png

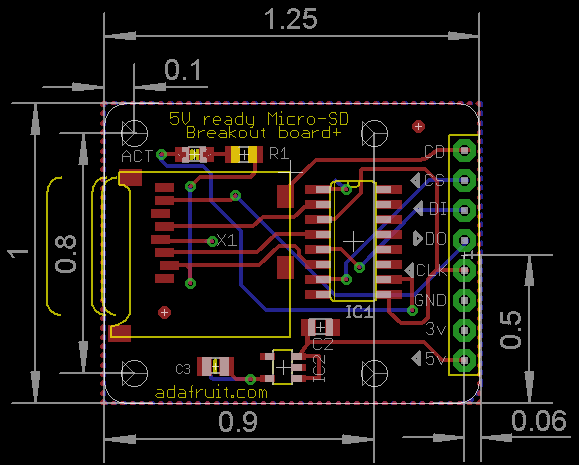
!Development/12 front-panel.processor, V1.1/adafruit_products_fabprint.png
