lynchaj/duodyne/!Development/12 front-panel.processor, V1.1/front-panel.processor.jpg

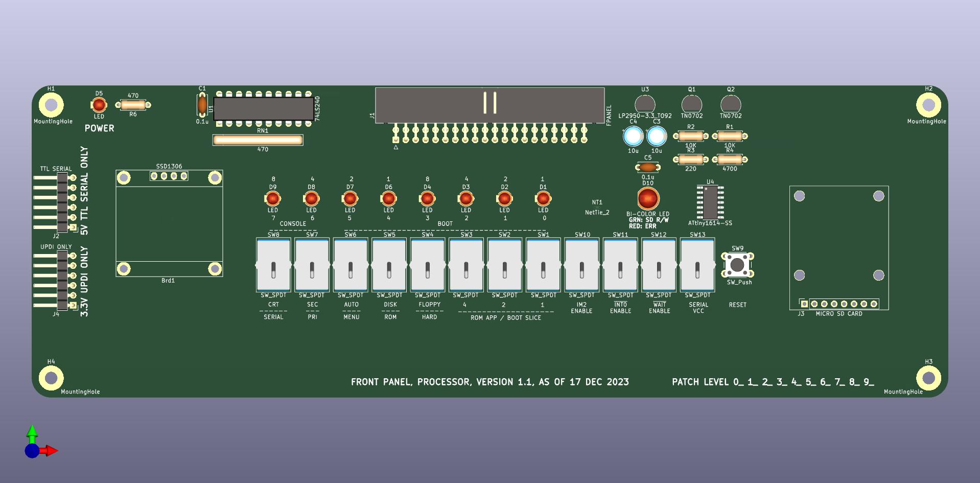
!Development/12 front-panel.processor, V1.1/front-panel.processor.jpg
