lynchaj/duodyne/!Development/12 front-panel.processor, V1.1/MC096-015.jpg

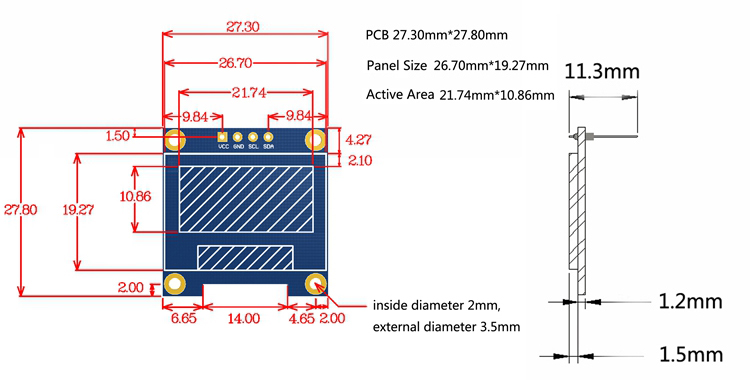
!Development/12 front-panel.processor, V1.1/MC096-015.jpg
