lynchaj/duodyne/!Development/12 front-panel.processor, V1.1/wayne front panel concept.png

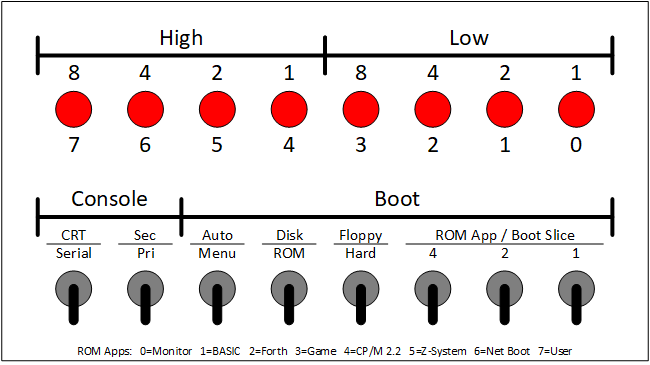
!Development/12 front-panel.processor, V1.1/wayne front panel concept.png
