lynchaj/duodyne/!Development/13 input-output.GDC, V1.0/GDC-CS-GAL.png

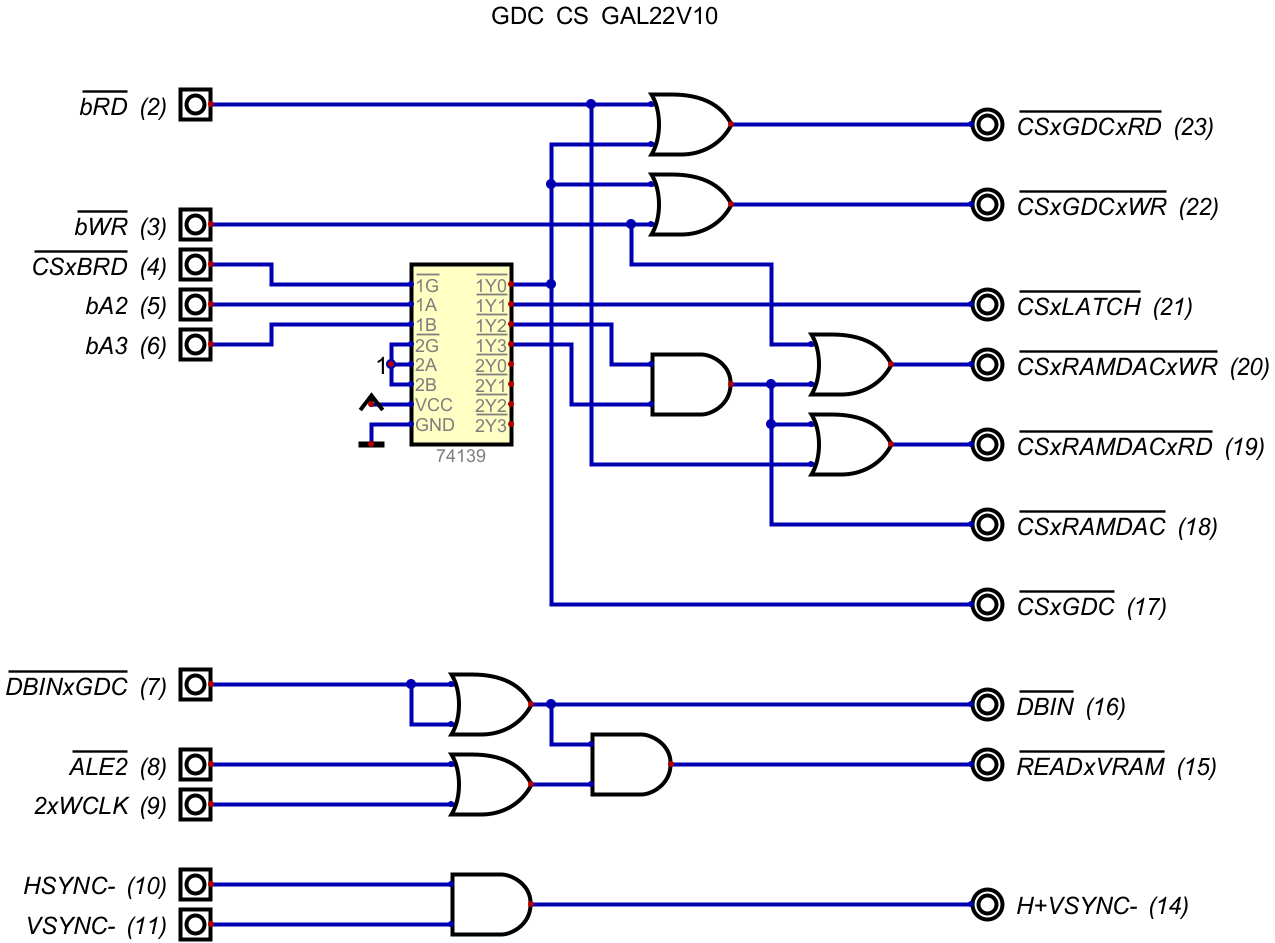
!Development/13 input-output.GDC, V1.0/GDC-CS-GAL.png
