lynchaj/duodyne/!Development/13 input-output.GDC, V1.0/input-output.GDC.jpg

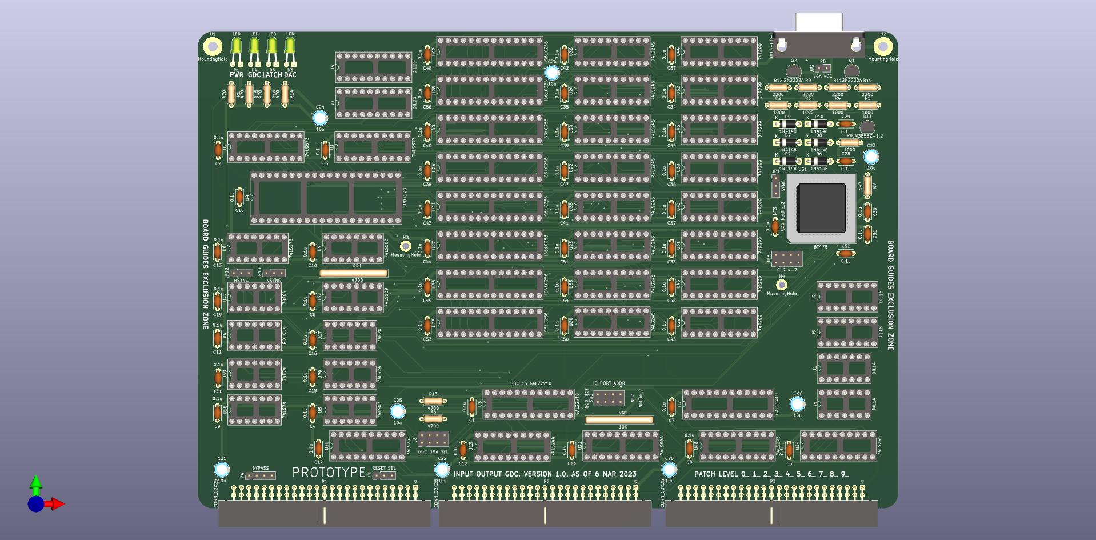
!Development/13 input-output.GDC, V1.0/input-output.GDC.jpg
