lynchaj/duodyne/!Development/13 input-output.GDC, V1.0/temp/GDC-MISC-GAL.png

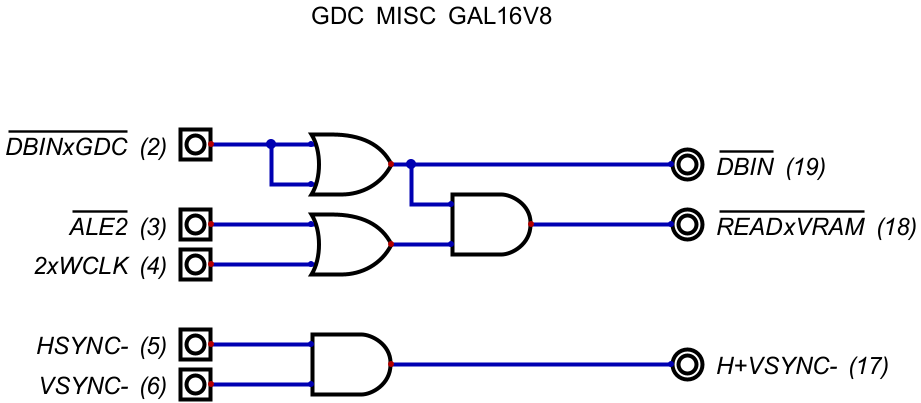
!Development/13 input-output.GDC, V1.0/temp/GDC-MISC-GAL.png
