lynchaj/duodyne/!Development/14 input-output.Text, V1.0/gdc_cc_jena_s.png

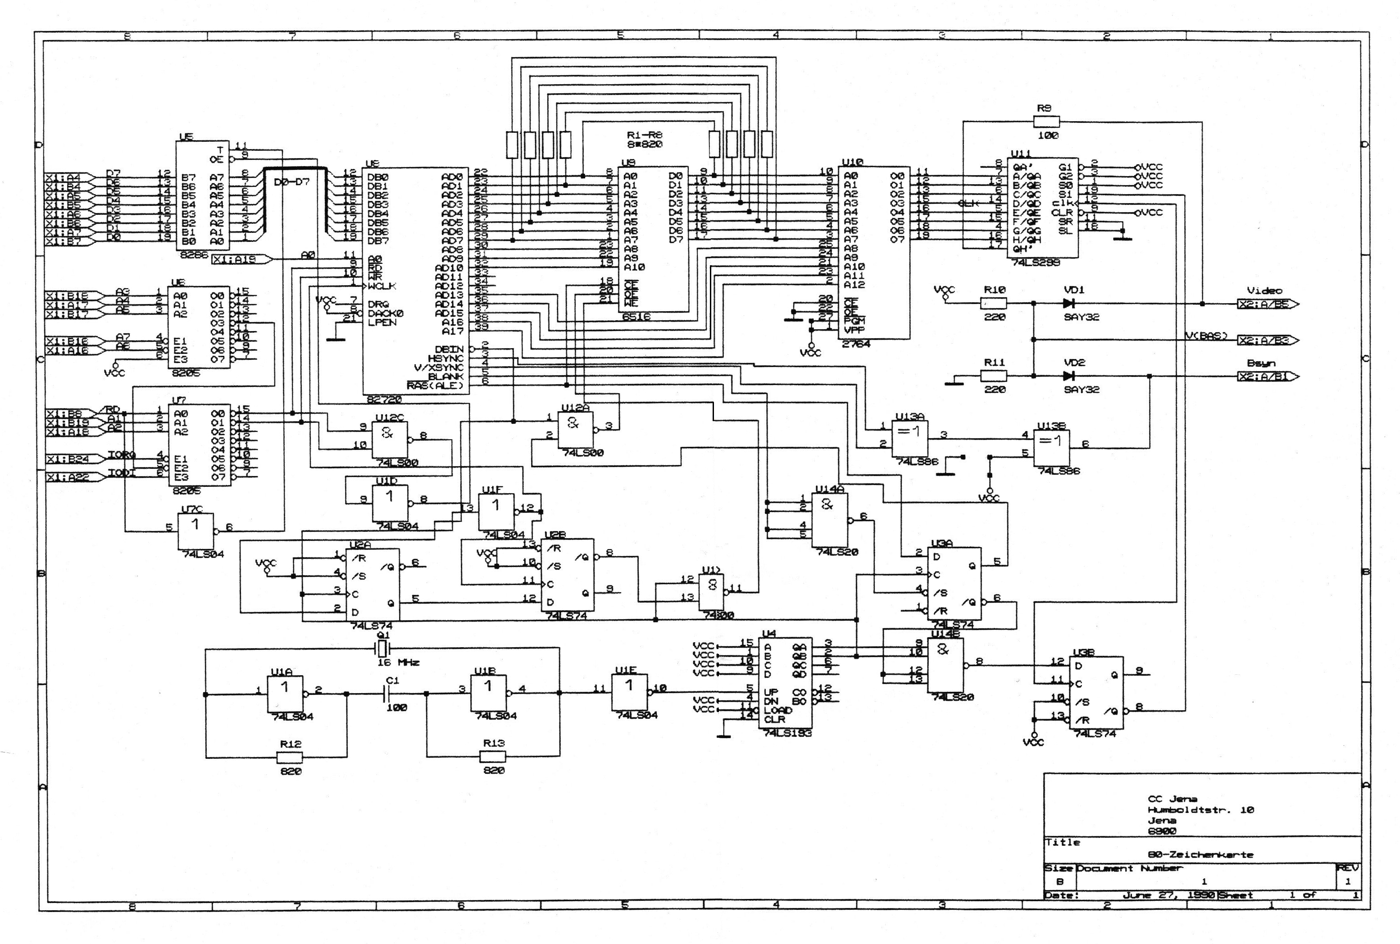
!Development/14 input-output.Text, V1.0/gdc_cc_jena_s.png
