lynchaj/duodyne/!Development/14 input-output.Text, V1.0/input-output.Text.jpg

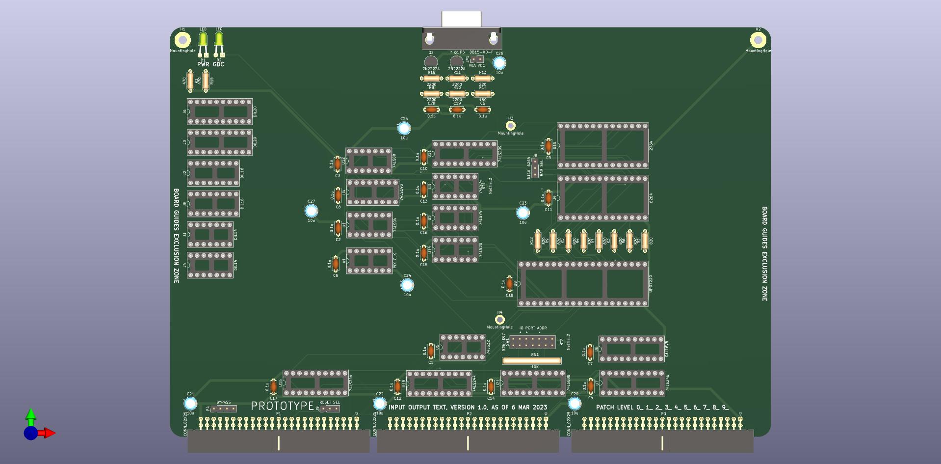
!Development/14 input-output.Text, V1.0/input-output.Text.jpg
