lynchaj/duodyne/!Development/15 input-output.PropESP32, V1.0/input-output.PropESP32.jpg

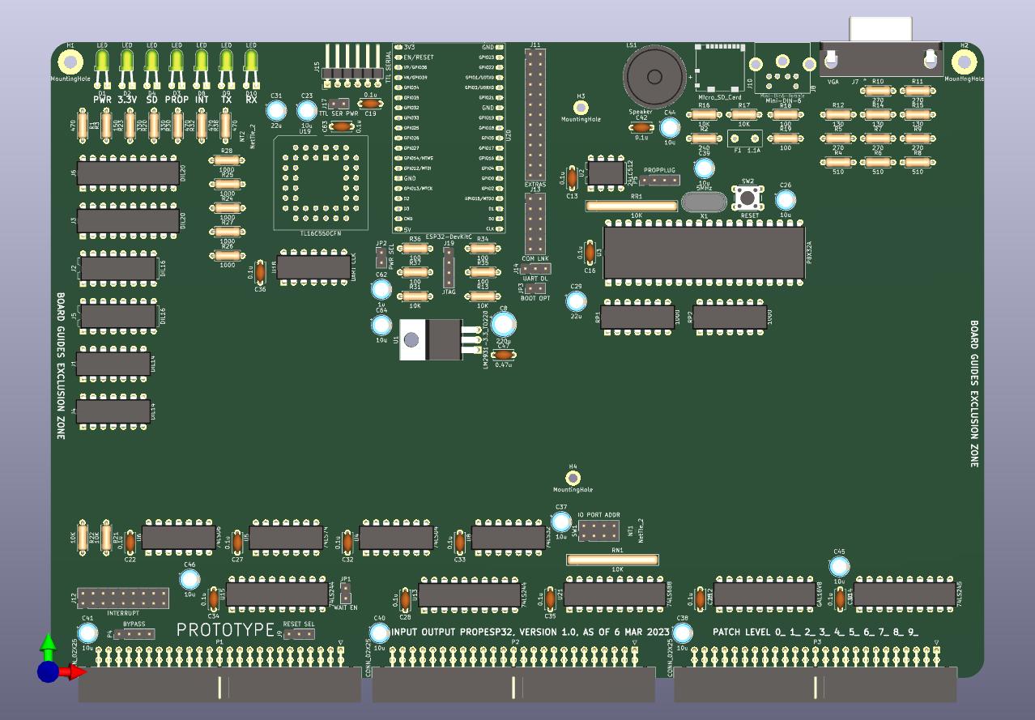
!Development/15 input-output.PropESP32, V1.0/input-output.PropESP32.jpg
