lynchaj/duodyne/!Development/16 input-output.VDCENET, V1.0/input-output.VDCENET.jpg

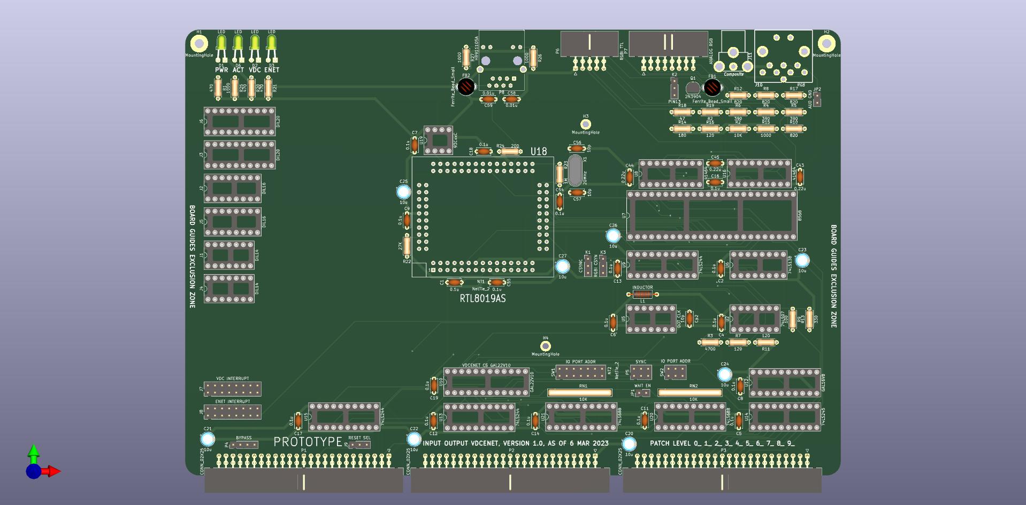
!Development/16 input-output.VDCENET, V1.0/input-output.VDCENET.jpg
