lynchaj/duodyne/!Development/16 input-output.VDCENET, V1.0/PQFP-100-Adapter/PQFP-100-Adapter.jpg

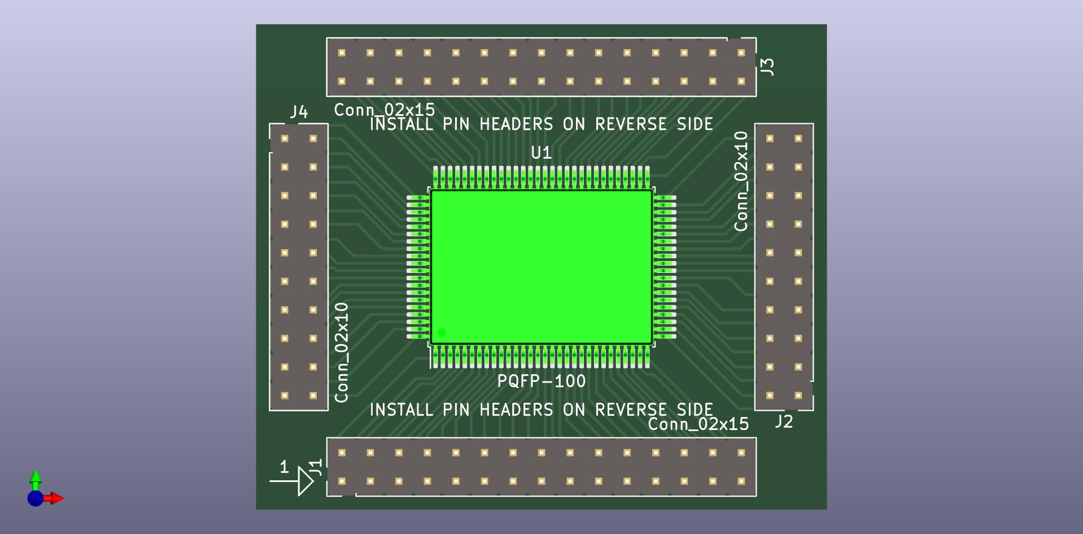
!Development/16 input-output.VDCENET, V1.0/PQFP-100-Adapter/PQFP-100-Adapter.jpg
