lynchaj/duodyne/!Development/16 input-output.VDCENET, V1.0/VDCENET-CS-GAL.png

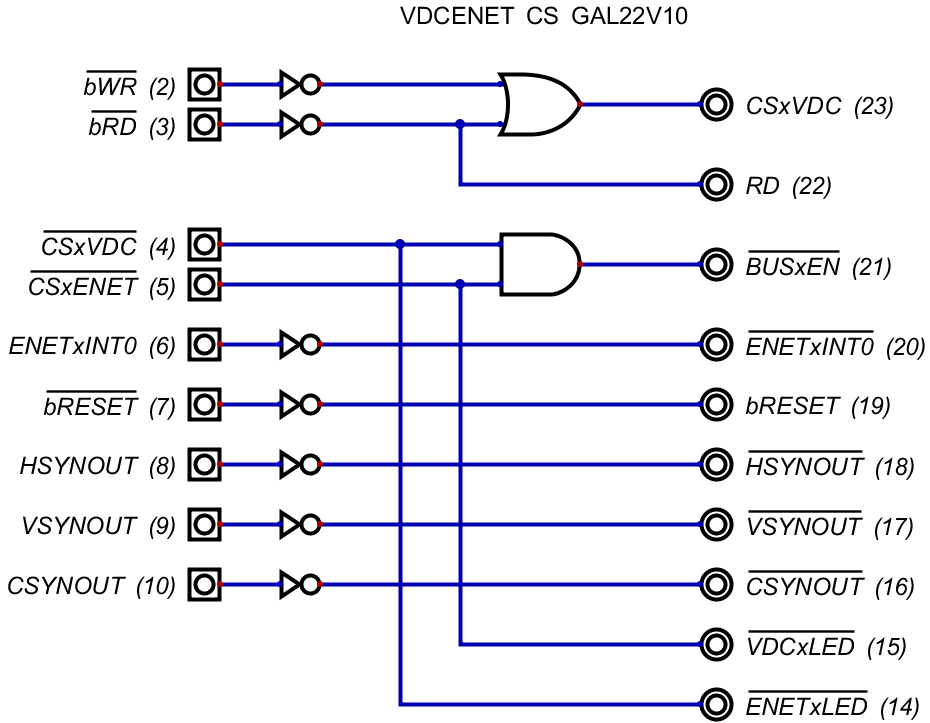
!Development/16 input-output.VDCENET, V1.0/VDCENET-CS-GAL.png
