lynchaj/duodyne/!Development/19 input-output.SelfHost, V1.1/0825-zero2w-img21.png

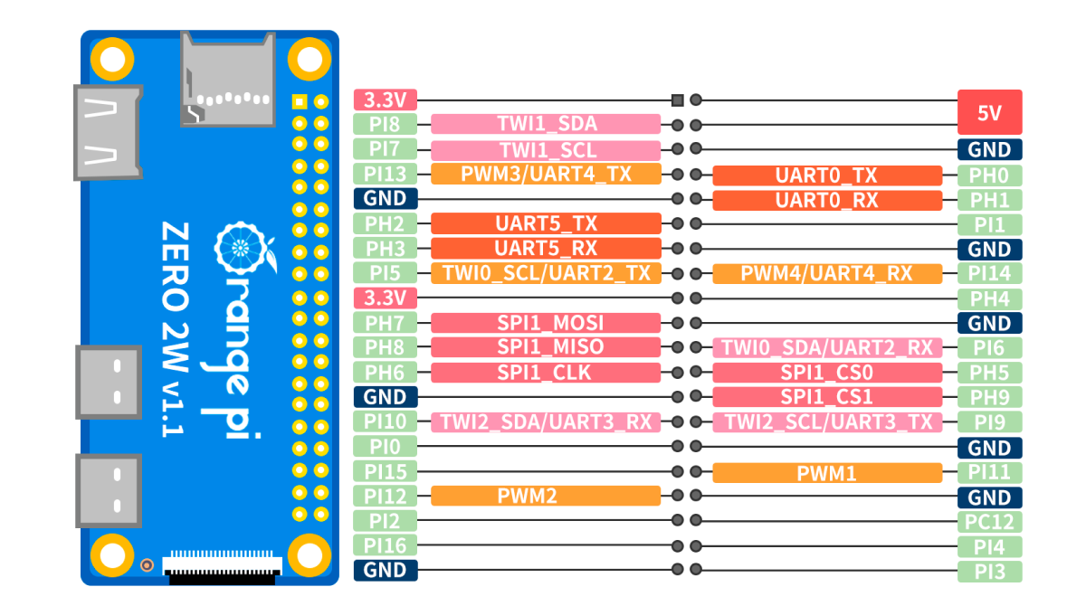
!Development/19 input-output.SelfHost, V1.1/0825-zero2w-img21.png
