lynchaj/duodyne/!Development/19 input-output.SelfHost, V1.1/input-output.SelfHost.jpg

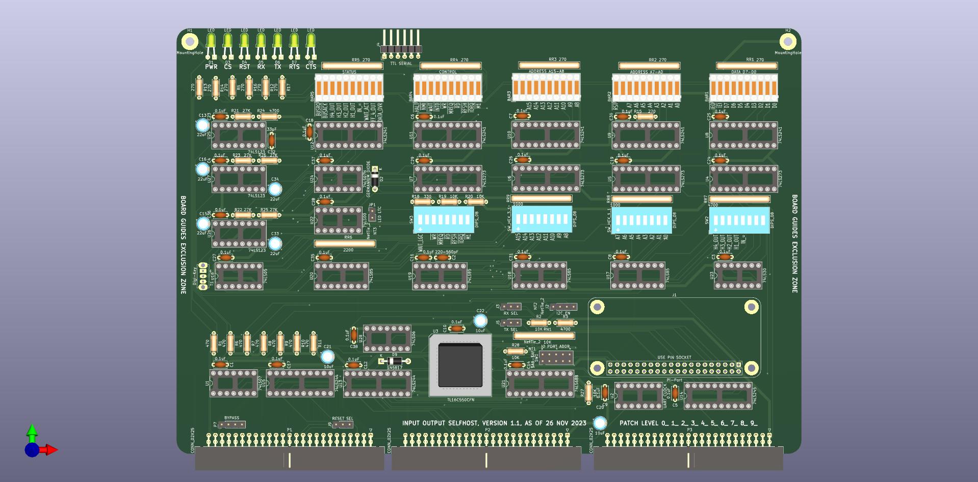
!Development/19 input-output.SelfHost, V1.1/input-output.SelfHost.jpg
