lynchaj/duodyne/!Development/19 input-output.SelfHost, V1.1/raspberry-pi-zero-2-w-dimensions.png

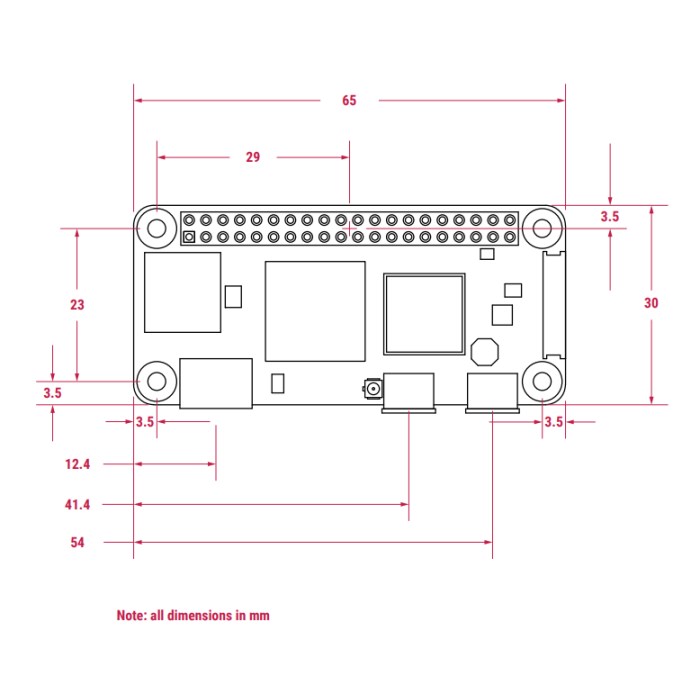
!Development/19 input-output.SelfHost, V1.1/raspberry-pi-zero-2-w-dimensions.png
