lynchaj/duodyne/!Development/21 input-output.MCU-CPLD, V1.0/input-output.MCU-CPLD.jpg

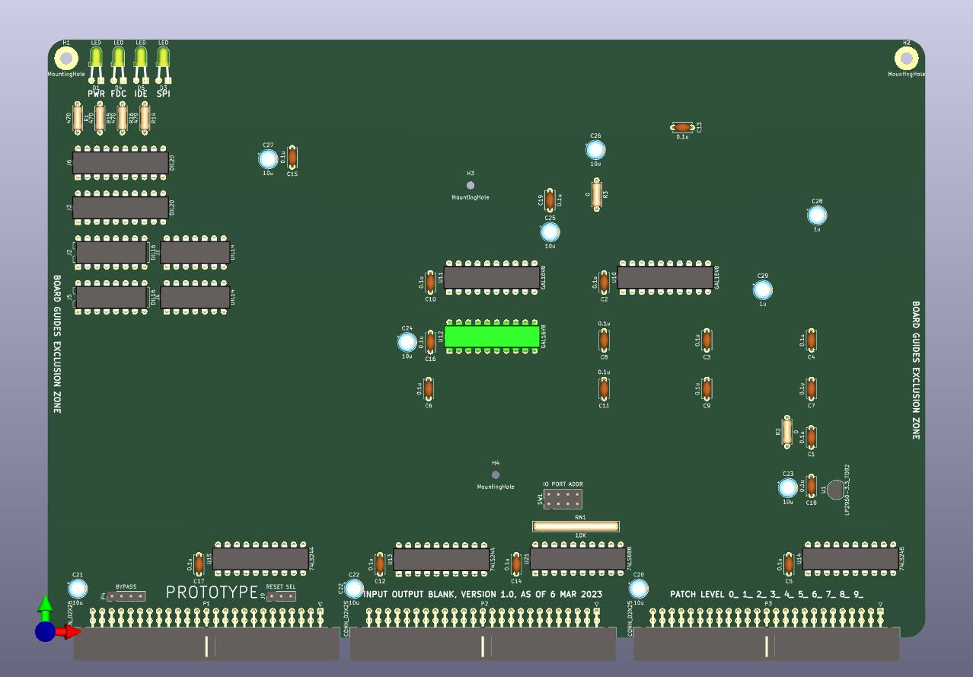
!Development/21 input-output.MCU-CPLD, V1.0/input-output.MCU-CPLD.jpg
