lynchaj/duodyne/!Development/22 input-output.BusExtender, V1.0/input-output.BusExtender.jpg

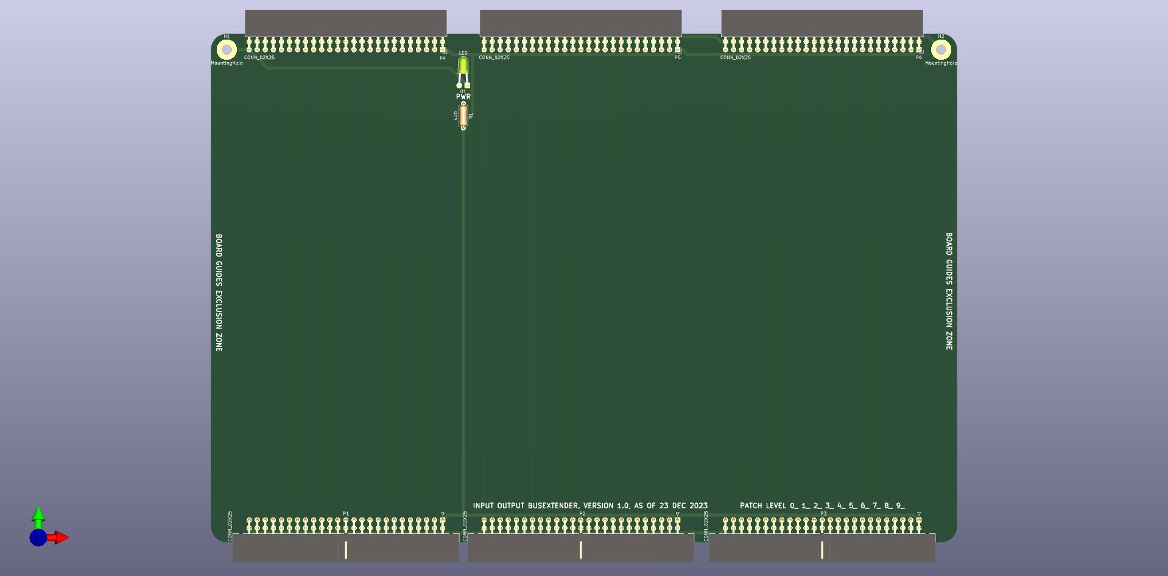
!Development/22 input-output.BusExtender, V1.0/input-output.BusExtender.jpg
