lynchaj/duodyne/!Development/24 DAISY256, V1.0/846665245_ChandlerBoards-2.jpg.8caed54e01b741a42bd71a7072ca7554.jpg

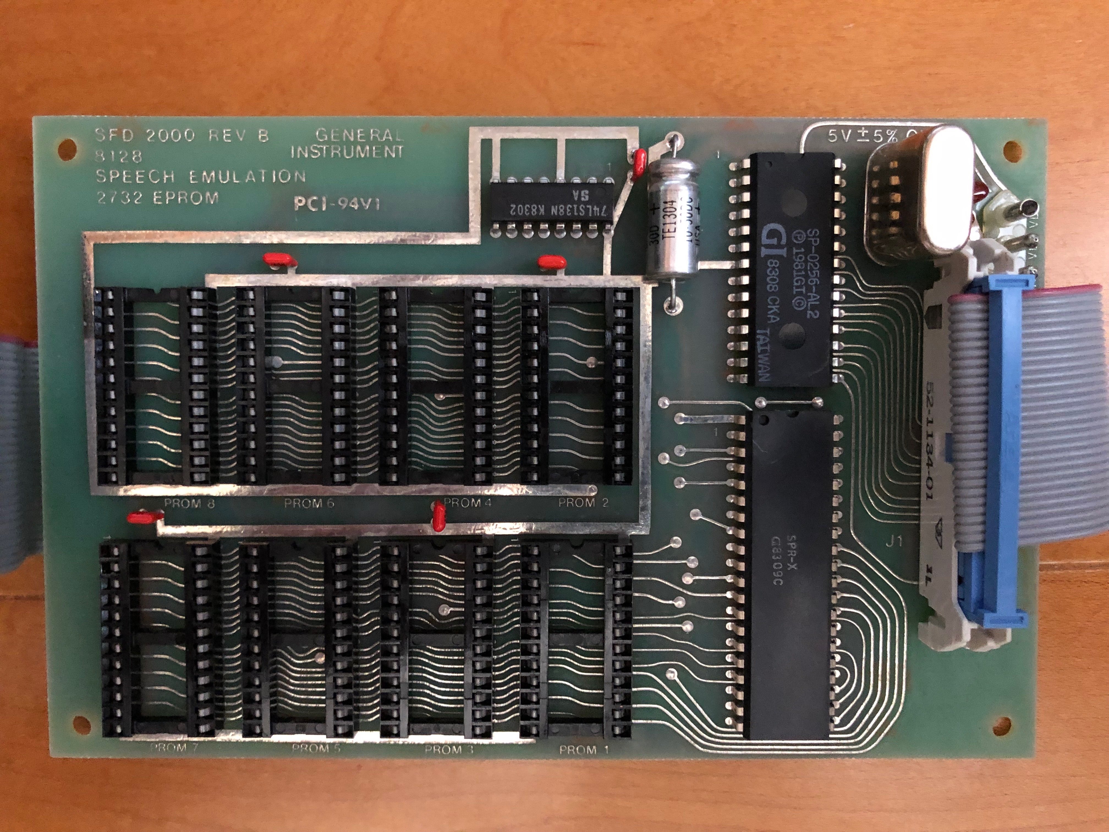
!Development/24 DAISY256, V1.0/846665245_ChandlerBoards-2.jpg.8caed54e01b741a42bd71a7072ca7554.jpg
