lynchaj/duodyne/!Development/24 DAISY256, V1.0/DAISY256.jpg

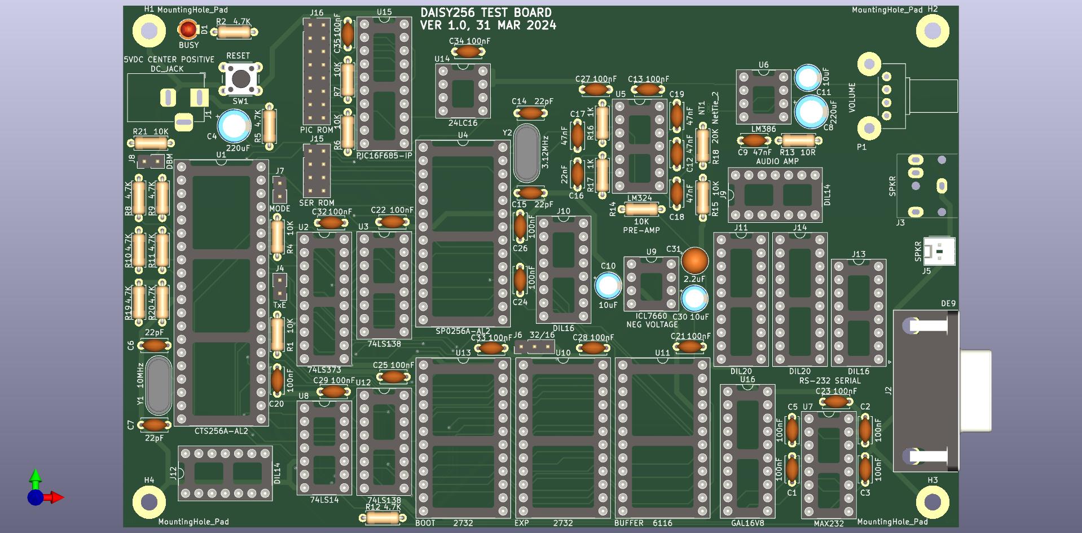
!Development/24 DAISY256, V1.0/DAISY256.jpg
