lynchaj/duodyne/!Development/24 DAISY256, V1.0/temp/Talker.jpg

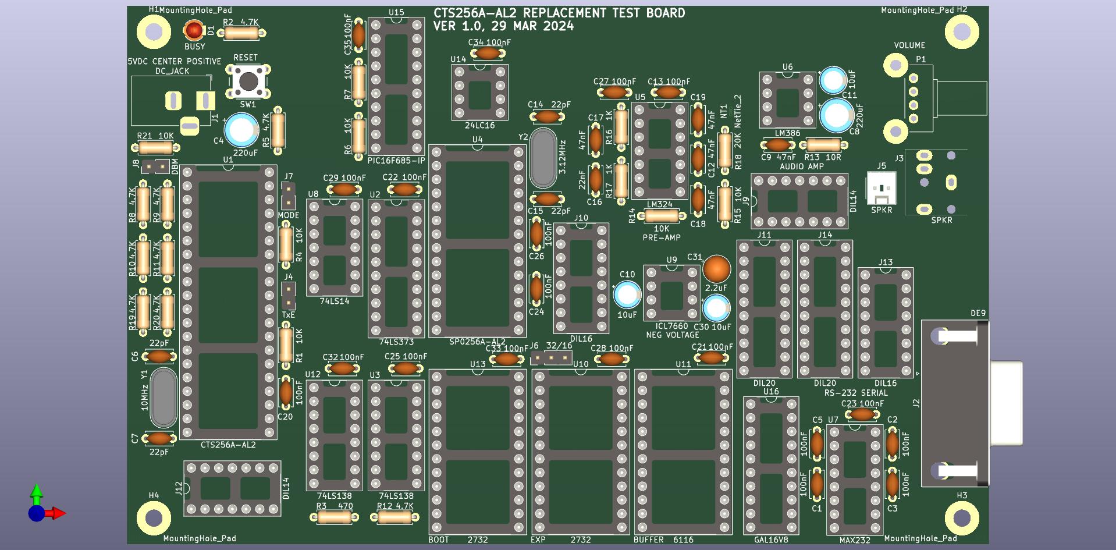
!Development/24 DAISY256, V1.0/temp/Talker.jpg
