lynchaj/duodyne/!Development/24 DAISY256, V1.0/temp/Talker_PCB.jpg

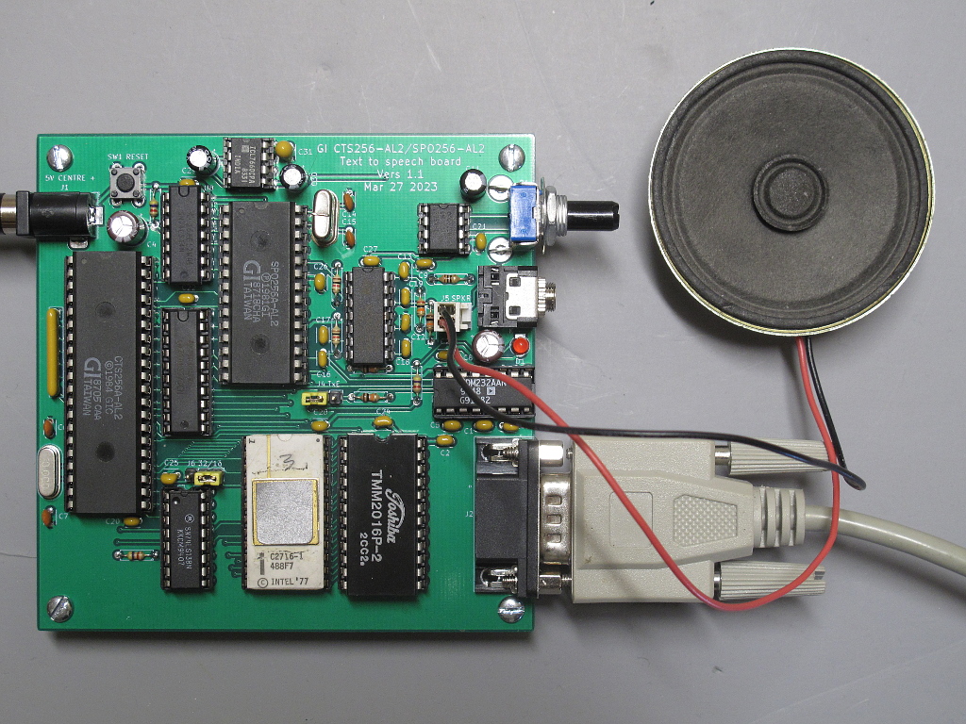
!Development/24 DAISY256, V1.0/temp/Talker_PCB.jpg
