lynchaj/duodyne/!Development/FirstZ80 V1.0/FirstZ80.jpg

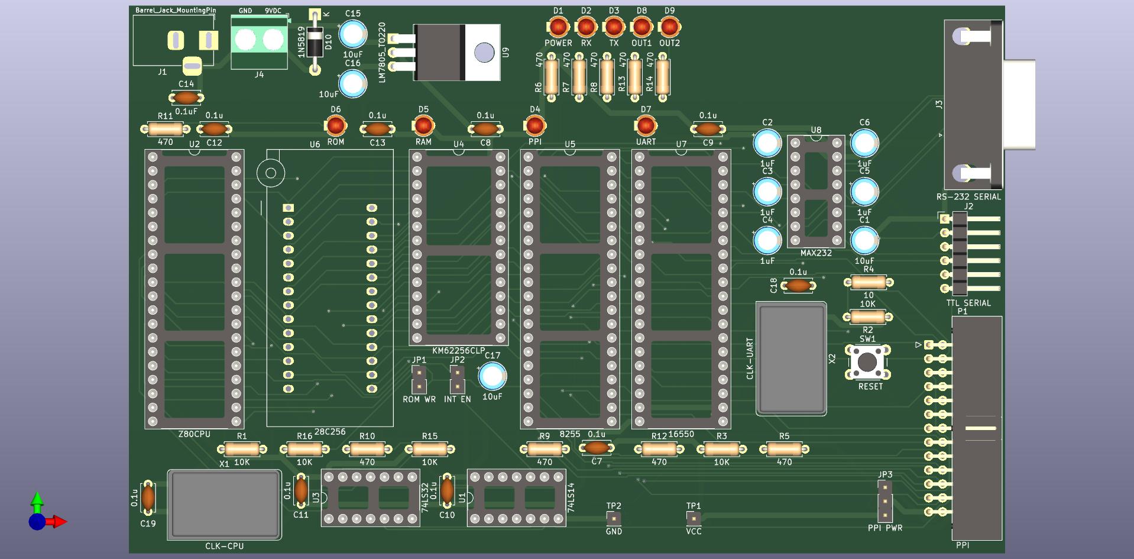
!Development/FirstZ80 V1.0/FirstZ80.jpg
