lynchaj/duodyne/!Development/retro-programmer/0J1073.1200.png

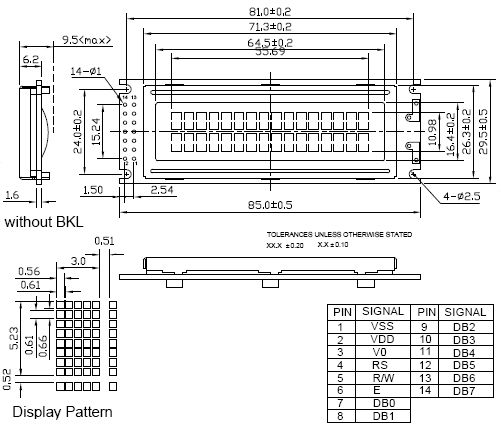
!Development/retro-programmer/0J1073.1200.png
