lynchaj/duodyne/!Development/retro-programmer/SAB80535-CS-1.png

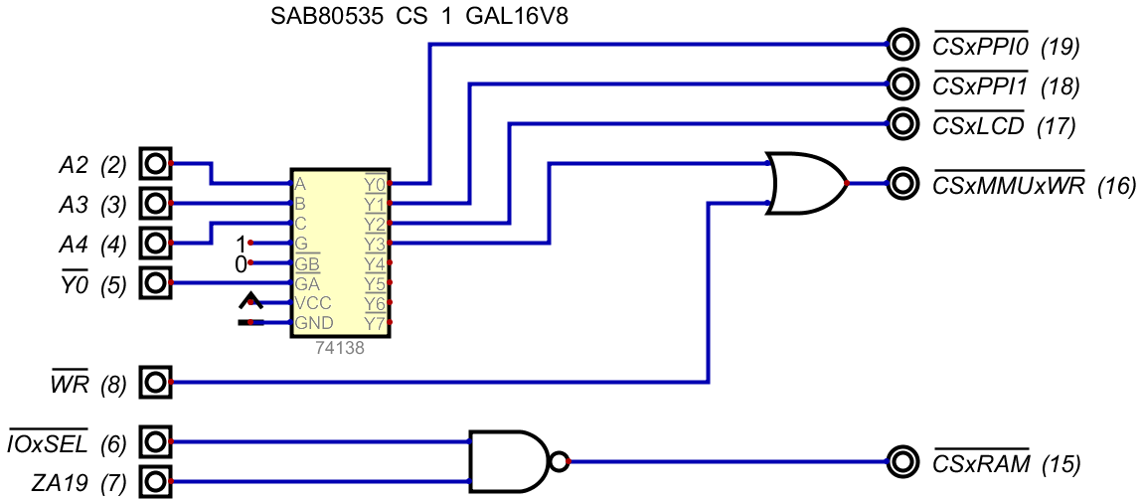
!Development/retro-programmer/SAB80535-CS-1.png
