lynchaj/duodyne/!Development/retro-programmer/SAB80535-CS-2.png

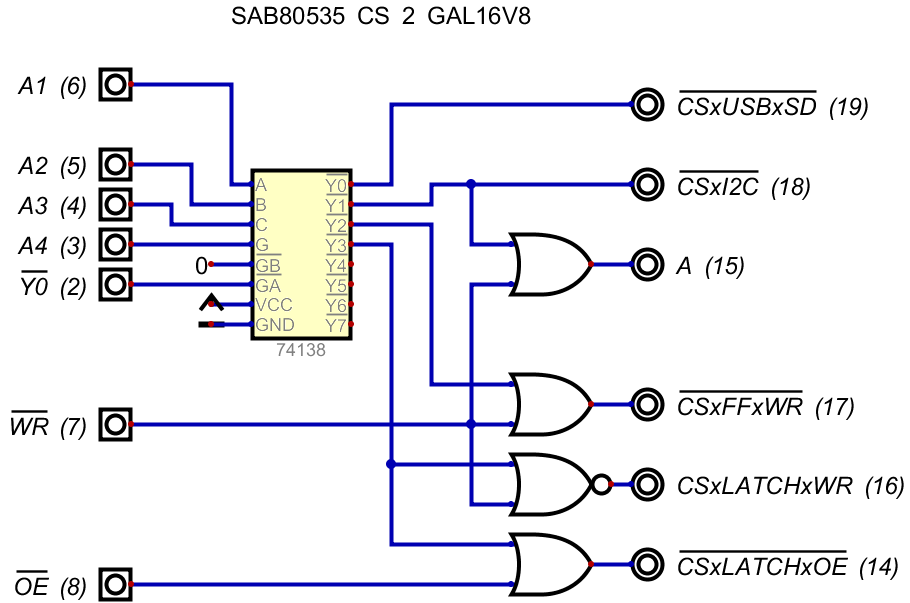
!Development/retro-programmer/SAB80535-CS-2.png
