lynchaj/duodyne/!Development/retro-programmer/SAB80535-RX-TX-V2.png

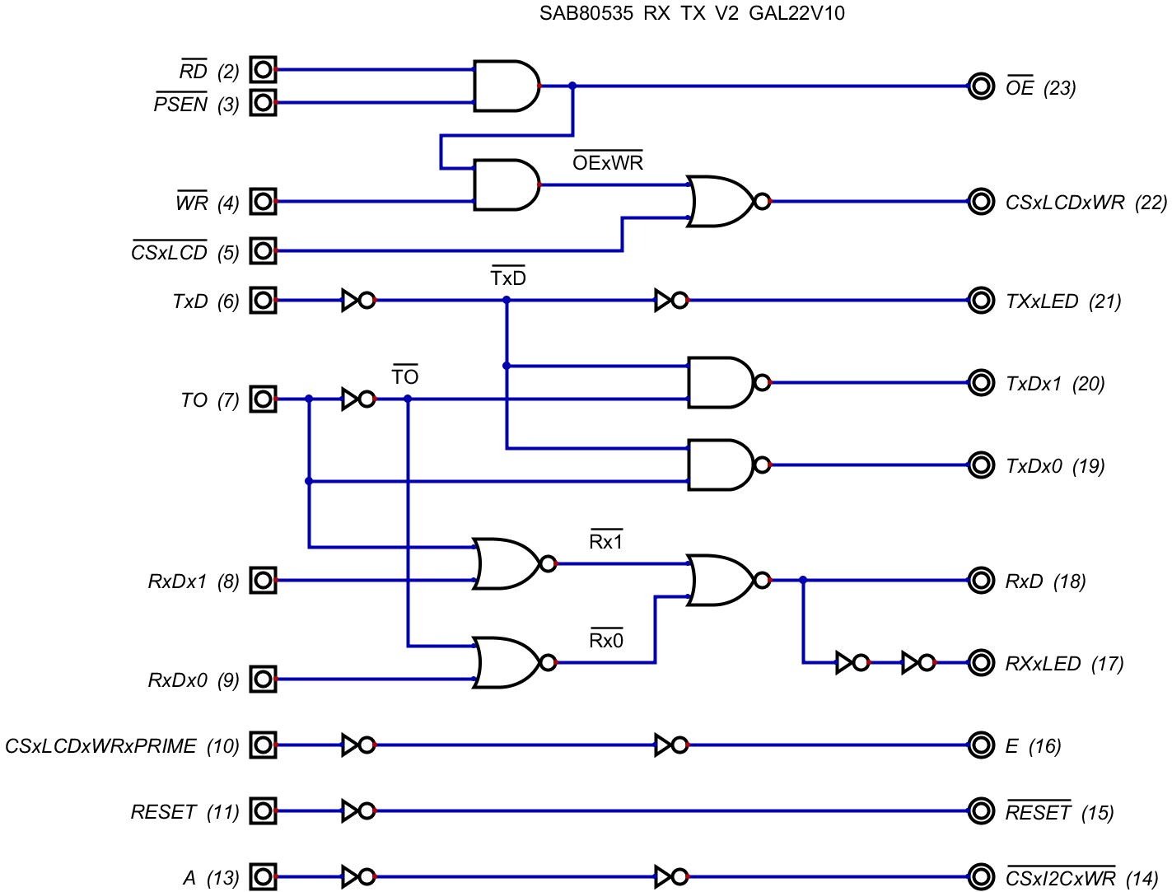
!Development/retro-programmer/SAB80535-RX-TX-V2.png
