lynchaj/duodyne/!Development/SAB80535-Dev-Board V1.1/3-Figure2-1.png

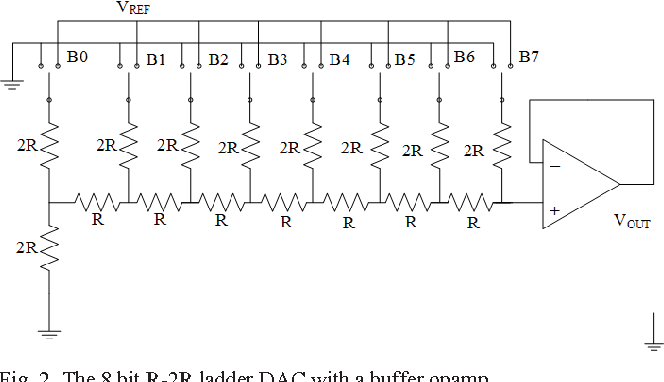
!Development/SAB80535-Dev-Board V1.1/3-Figure2-1.png
