lynchaj/duodyne/!Development/SAB80535-Dev-Board V1.1/Covox-Stecker.svg.png

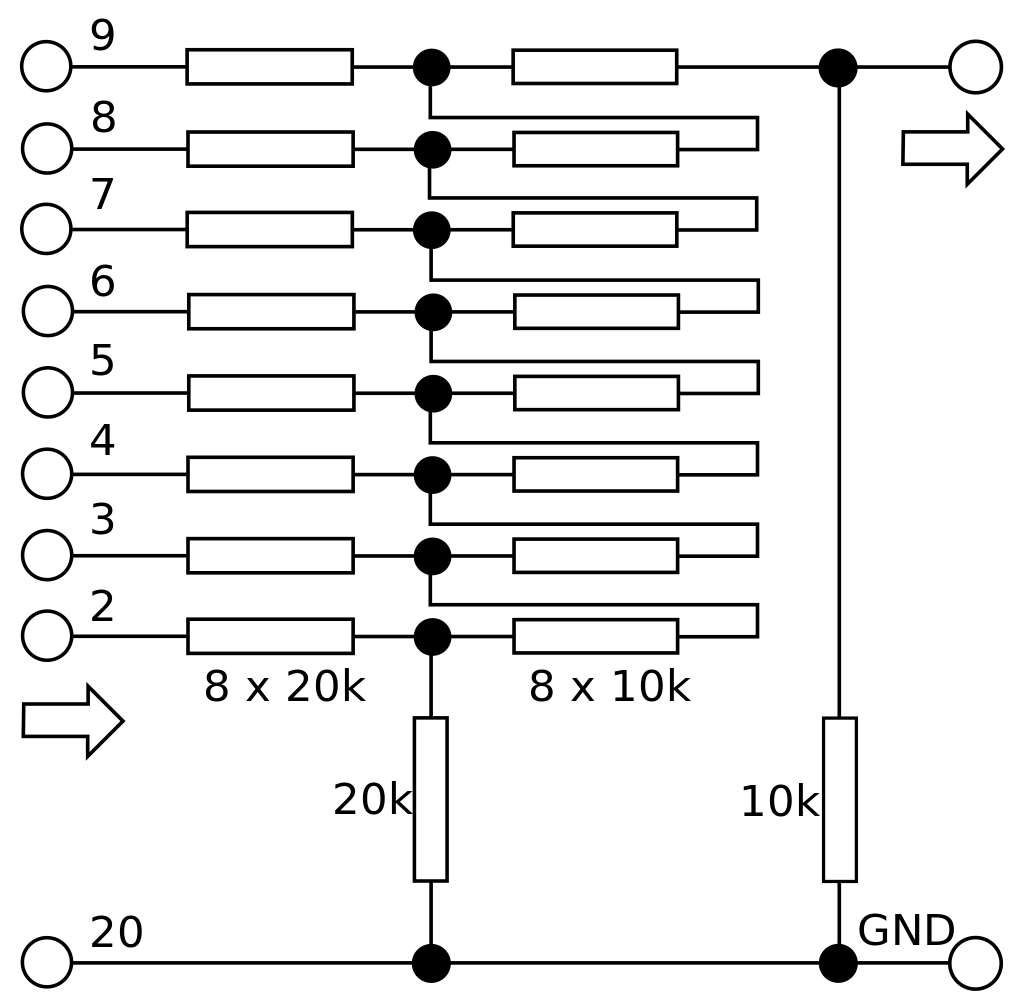
!Development/SAB80535-Dev-Board V1.1/Covox-Stecker.svg.png
