lynchaj/duodyne/!Development/SAB80535-Dev-Board V1.1/SAB80535-CS-1.png

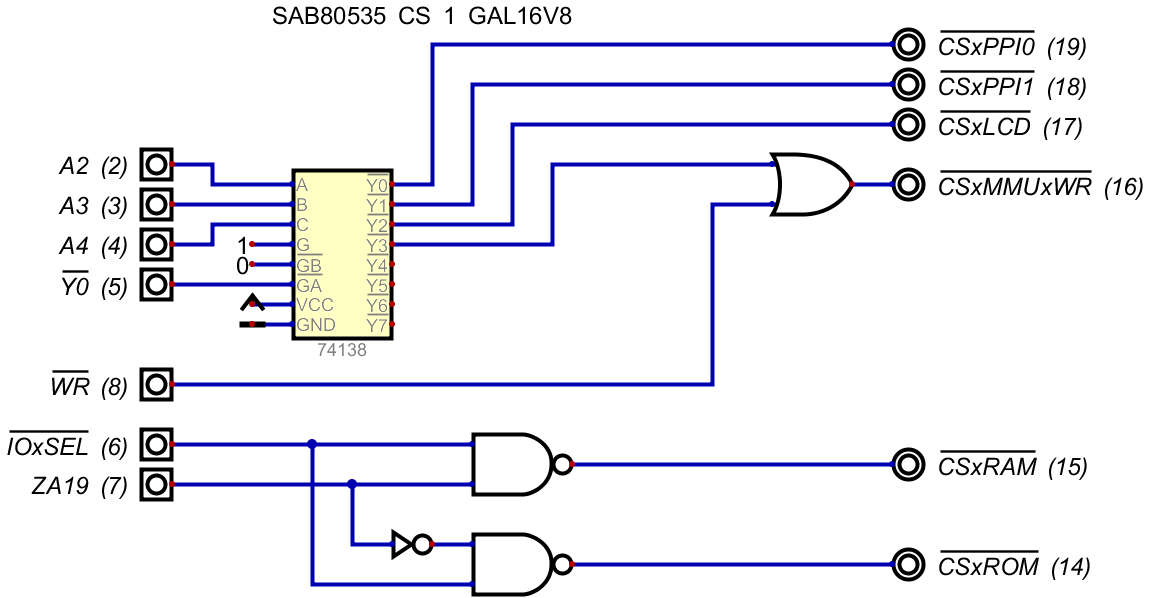
!Development/SAB80535-Dev-Board V1.1/SAB80535-CS-1.png
