lynchaj/duodyne/!Development/SAB80535-Dev-Board V1.1/SAB80535-Dev-Board.jpg

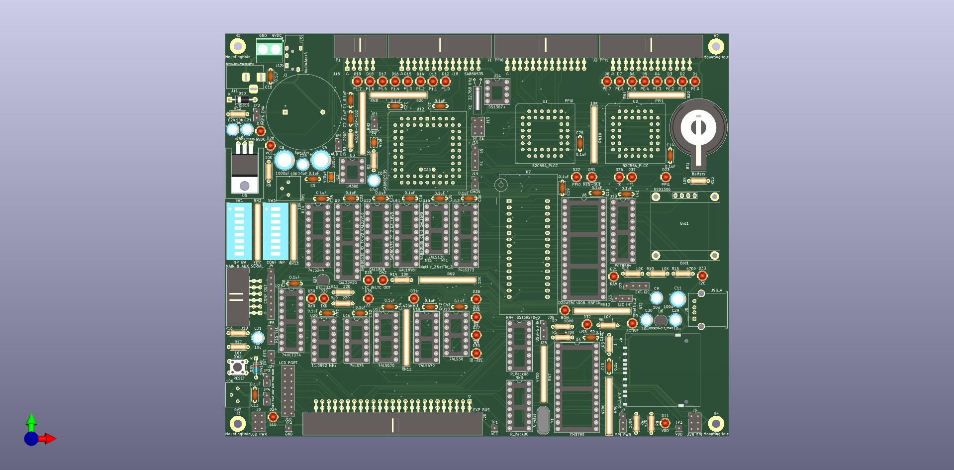
!Development/SAB80535-Dev-Board V1.1/SAB80535-Dev-Board.jpg
