lynchaj/duodyne/!Development/SAB80535-Dev-Board V1.1/temp/SAB80535-CS-V2.png

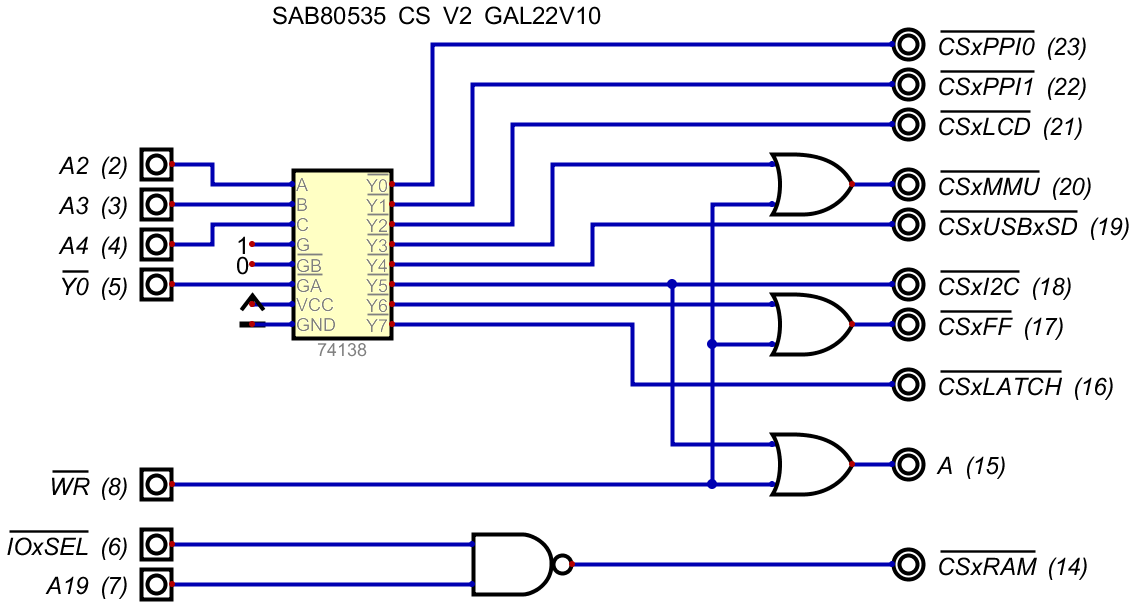
!Development/SAB80535-Dev-Board V1.1/temp/SAB80535-CS-V2.png
