lynchaj/duodyne/!Development/SAB80535-Dev-Board V1.1/temp/SAB80535-IO-SELECT.png

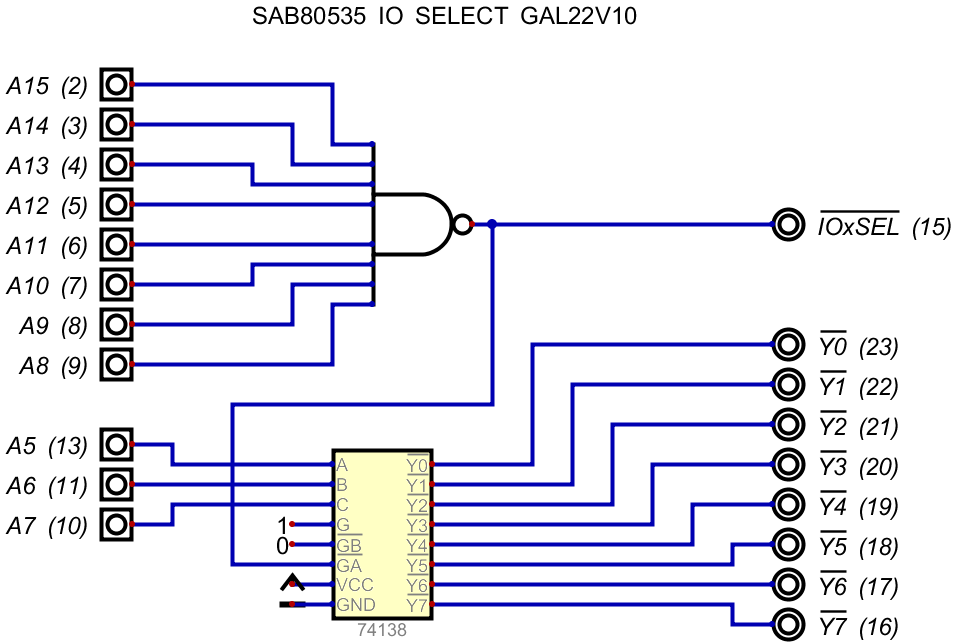
!Development/SAB80535-Dev-Board V1.1/temp/SAB80535-IO-SELECT.png
