lynchaj/duodyne/!Development/Slick/CPLDs/z80-processor-CPU/Z80-processor-CPU.png

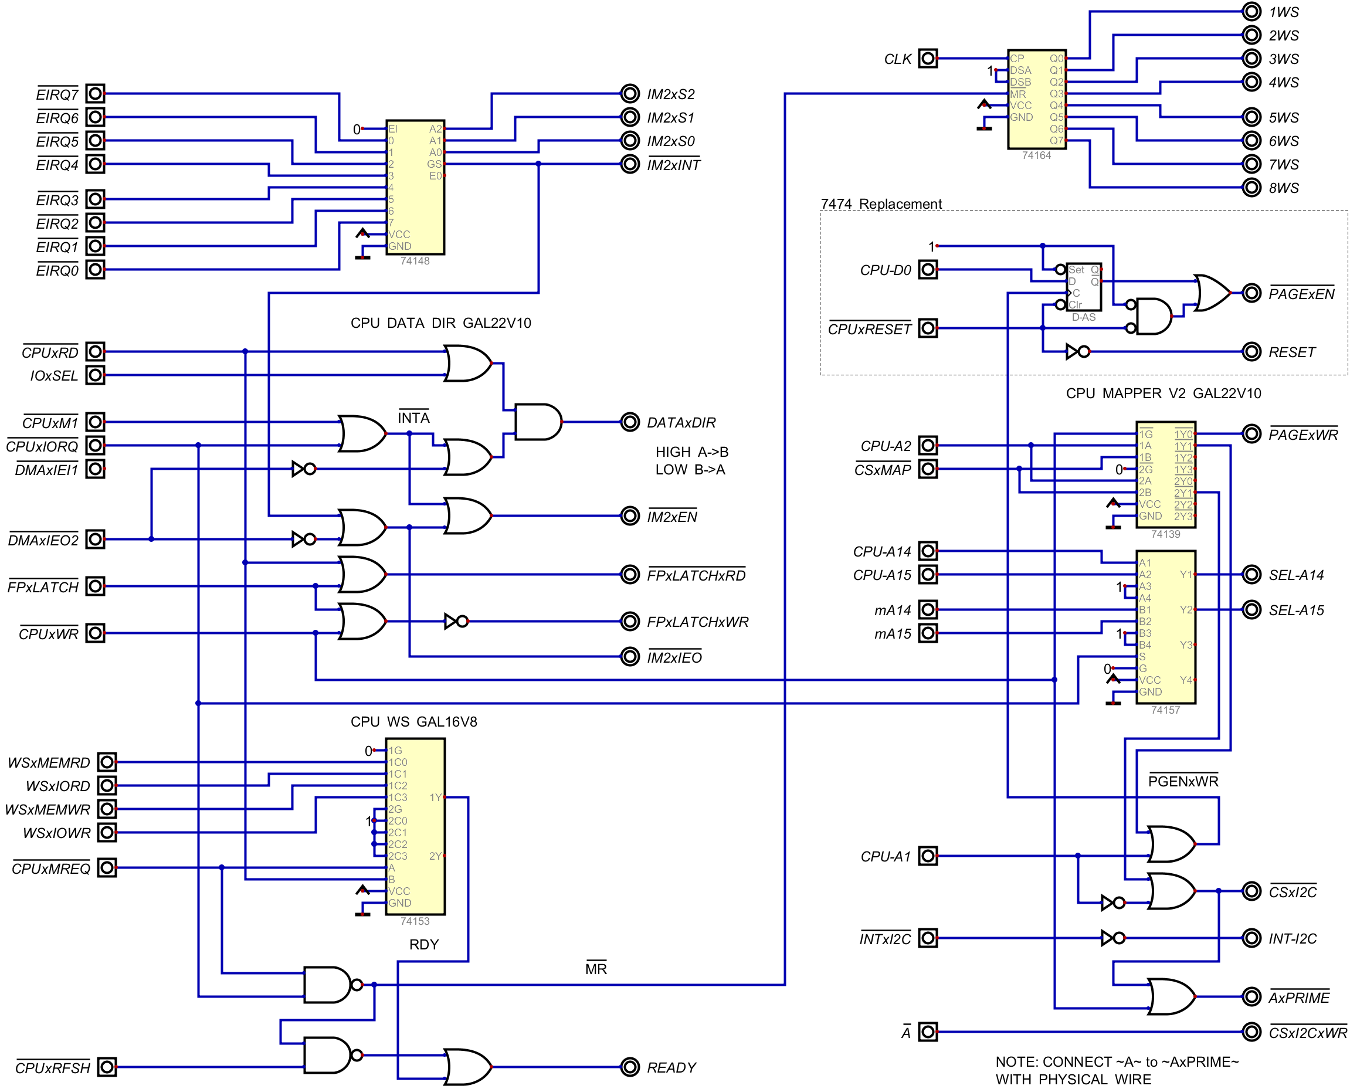
!Development/Slick/CPLDs/z80-processor-CPU/Z80-processor-CPU.png
