lynchaj/duodyne/!Development/Slick/CPLDs/z80-processor-DMA/Z80-processor-DMA.png

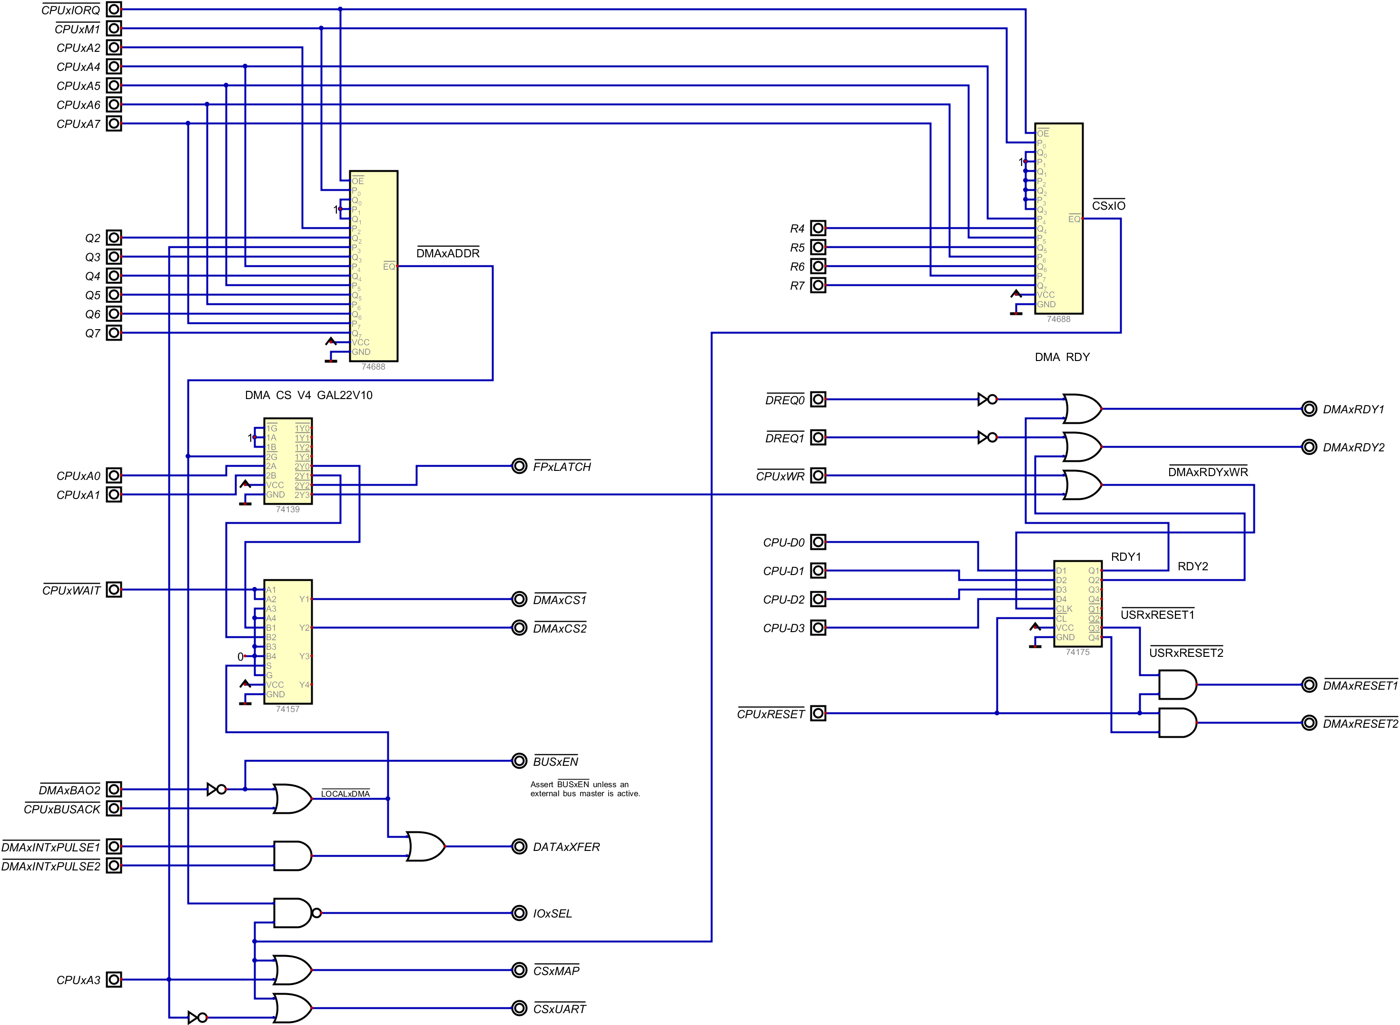
!Development/Slick/CPLDs/z80-processor-DMA/Z80-processor-DMA.png
