lynchaj/duodyne/!Development/Slick/Slick.jpg

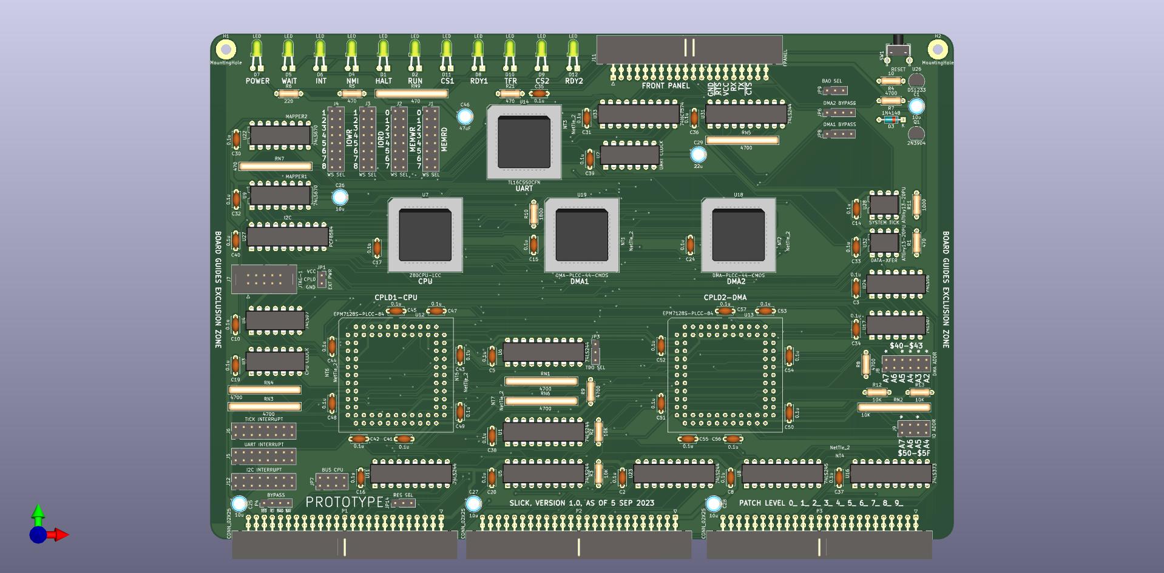
!Development/Slick/Slick.jpg
