lynchaj/duodyne/!Development/Slick/temp/processor.Z80.CPLD.jpg

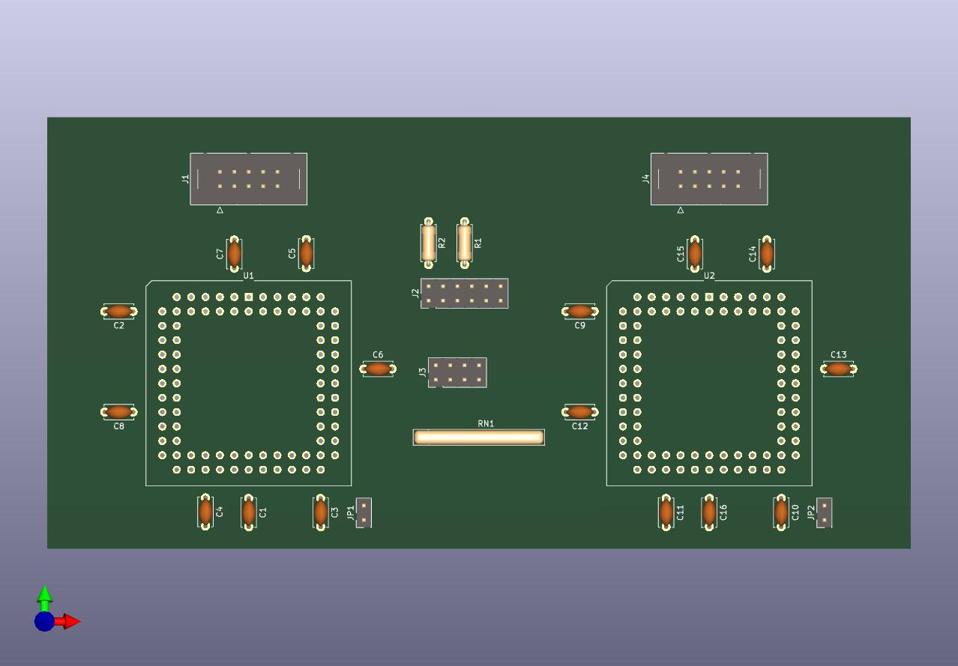
!Development/Slick/temp/processor.Z80.CPLD.jpg
