lynchaj/duodyne/EPM7128S-Dev-Board/EPM7128S-Dev-Board.jpg

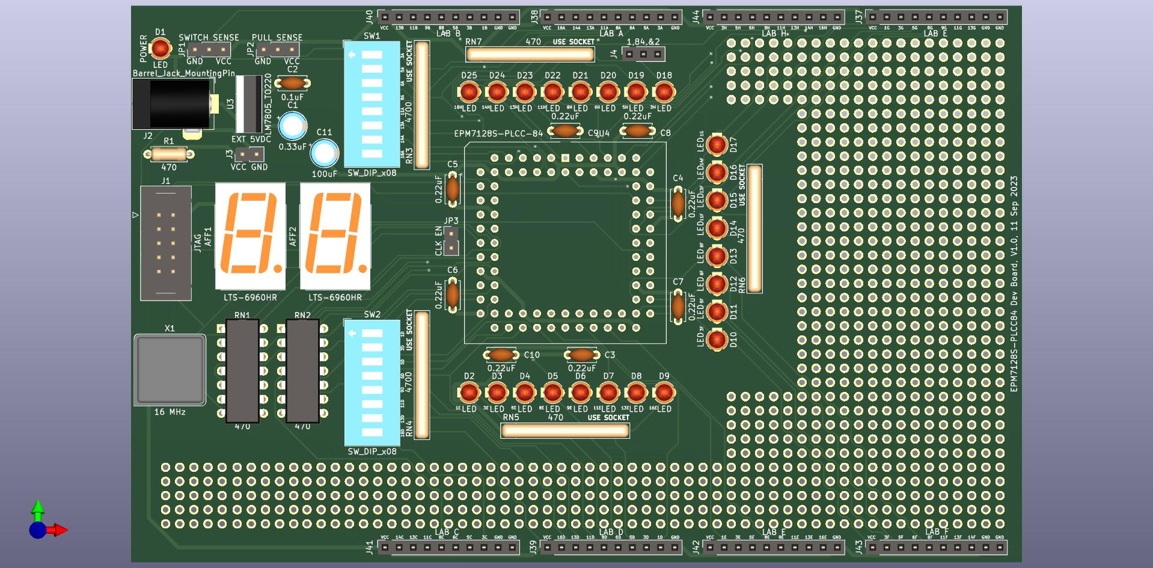
EPM7128S-Dev-Board/EPM7128S-Dev-Board.jpg
