lynchaj/duodyne/05 input-output.Zilog, V1.1/input-output.Zilog.csv

Source: | C:\Users\Andrew\Desktop\System CD Updates\data\duodyne\GitHub\05 input-output.Zilog, V1.1\input-output.Zilog.kicad_sch
Date: | 10/31/2023 6:13:35 AM
Tool: | Eeschema (6.0.11)
Generator: | C:\Program Files\KiCad\6.0\bin\scripting\plugins/bom_csv_grouped_by_value_with_fp.py
Component Count: | 83
Ref | Qnty | Value | Cmp name | Footprint | Description | Vendor
C1, C2, C3, C4, C5, C6, C7, C8, C9, C12, C13, C14, C15, C16, C17, C18, C19, C20, C21, C22, C23, C24, C25, C26, C28, C29, C30, C31, | 28 | 0.1u | C | Capacitor_THT:C_Disc_D5.0mm_W2.5mm_P5.00mm | Unpolarized capacitor
C10, C11, C27, | 3 | 10u | C_Polarized | Capacitor_THT:CP_Radial_D5.0mm_P2.50mm | Polarized capacitor
D1, D2, D3, D5, | 4 | LED | LED | LED_THT:LED_D3.0mm_Horizontal_O3.81mm_Z2.0mm | Light emitting diode
H1, H2, | 2 | MountingHole | MountingHole_Pad | MountingHole:MountingHole_3.2mm_M3_Pad | Mounting Hole with connection
J2, | 1 | TTLSERPWR | Conn_02x02_Odd_Even | Connector_PinHeader_2.54mm:PinHeader_2x02_P2.54mm_Vertical | Generic connector, double row, 02x02, odd/even pin numbering scheme (row 1 odd numbers, row 2 even numbers), script generated (kicad-library-utils/schlib/autogen/connector/)
J11, | 1 | RESET SEL | Conn_01x03 | Connector_PinHeader_2.54mm:PinHeader_1x03_P2.54mm_Vertical | Generic connector, single row, 01x03, script generated (kicad-library-utils/schlib/autogen/connector/)
JP1, | 1 | IO PORT ADDR | Conn_02x06_Odd_Even | Connector_PinHeader_2.54mm:PinHeader_2x06_P2.54mm_Vertical | Generic connector, double row, 02x06, odd/even pin numbering scheme (row 1 odd numbers, row 2 even numbers), script generated (kicad-library-utils/schlib/autogen/connector/)
JP2, | 1 | IO PORT ADDR | Conn_02x04_Odd_Even | Connector_PinHeader_2.54mm:PinHeader_2x04_P2.54mm_Vertical | Generic connector, double row, 02x04, odd/even pin numbering scheme (row 1 odd numbers, row 2 even numbers), script generated (kicad-library-utils/schlib/autogen/connector/)
JP3, | 1 | IA WS | Conn_02x04_Odd_Even | Connector_PinHeader_2.54mm:PinHeader_2x04_P2.54mm_Vertical | Generic connector, double row, 02x04, odd/even pin numbering scheme (row 1 odd numbers, row 2 even numbers), script generated (kicad-library-utils/schlib/autogen/connector/)
JP4, | 1 | WAIT EN | Jumper_2_Open | Connector_PinHeader_2.54mm:PinHeader_1x02_P2.54mm_Vertical | Jumper, 2-pole, open
P1, P2, P3, | 3 | CONN_02X25 | Conn_02x25_Odd_Even | Connector_IDC:IDC-Header_2x25_P2.54mm_Horizontal | Generic connector, double row, 02x25, odd/even pin numbering scheme (row 1 odd numbers, row 2 even numbers), script generated (kicad-library-utils/schlib/autogen/connector/)
P9, | 1 | BYPASS | Conn_01x04 | Connector_PinHeader_2.54mm:PinHeader_1x04_P2.54mm_Vertical | Generic connector, single row, 01x04, script generated (kicad-library-utils/schlib/autogen/connector/)
R5, R11, | 2 | 4700 | R | Resistor_THT:R_Axial_DIN0207_L6.3mm_D2.5mm_P7.62mm_Horizontal | Resistor
R10, | 1 | 2200 | R | Resistor_THT:R_Axial_DIN0207_L6.3mm_D2.5mm_P7.62mm_Horizontal | Resistor
RN1, RN2, RN3, | 3 | 10K | R_Network08 | Resistor_THT:R_Array_SIP9 | 8 resistor network, star topology, bussed resistors, small symbol
RN4, | 1 | 470 | R_Network08 | Resistor_THT:R_Array_SIP9 | 8 resistor network, star topology, bussed resistors, small symbol
U1, | 1 | GAL22V10 | GAL22V10 | Package_DIP:DIP-24_W7.62mm
U2, U4, | 2 | 74LS244 | 74LS244 | Package_DIP:DIP-20_W7.62mm | Octal Buffer and Line Driver With 3-State Output, active-low enables, non-inverting outputs
U3, | 1 | 74LS245 | 74LS245 | Package_DIP:DIP-20_W7.62mm | Octal BUS Transceivers, 3-State outputs
U5, U24, | 2 | 74LS688 | 74LS688 | Package_DIP:DIP-20_W7.62mm | 8-bit magnitude comparator
U6, | 1 | 2CTC-PLCC-44 | CTC-PLCC-44 | Package_LCC:PLCC-44_THT-Socket | Z8430 Zilog CTC
U7, | 1 | 1CTC-PLCC-44 | CTC-PLCC-44 | Package_LCC:PLCC-44_THT-Socket | Z8430 Zilog CTC
U8, | 1 | BASE CLOCK | Conn_02x07_Counter_Clockwise | Package_DIP:DIP-14_W7.62mm | Generic connector, double row, 02x07, counter clockwise pin numbering scheme (similar to DIP package numbering), script generated (kicad-library-utils/schlib/autogen/connector/)
U9, | 1 | SIO4-PLCC-44 | SIO3-PLCC-44 | Package_LCC:PLCC-44_THT-Socket | Z80 CMOS SIO/3 Z84C43 Zilog
U10, U11, | 2 | MAX232 | MAX232 | Package_DIP:DIP-16_W7.62mm | Dual RS232 driver/receiver, 5V supply, 120kb/s, 0C-70C
U12, | 1 | 74LS393 | 74LS393 | Package_DIP:DIP-14_W7.62mm | Dual BCD 4-bit counter
U13, | 1 | 74LS09 | 74LS09 | Package_DIP:DIP-14_W7.62mm | Quad 2-input AND Open Collect
U14, | 1 | 2PIO-PLCC-44 | PIO-PLCC-44 | Package_LCC:PLCC-44_THT-Socket | Z80 PIO Z84C20 Z8420 ZILOG, PLCC 44
U17, | 1 | 74LS191 | 74LS191 | Package_DIP:DIP-16_W7.62mm | 4-bit Synchronous Up/Down binary Counter
U18, | 1 | 1PIO-PLCC-44 | PIO-PLCC-44 | Package_LCC:PLCC-44_THT-Socket | Z80 PIO Z84C20 Z8420 ZILOG, PLCC 44
U20, | 1 | 74LS07 | 74LS07 | Package_DIP:DIP-14_W7.62mm | Hex Buffers and Drivers With Open Collector High Voltage Outputs
U21, | 1 | GAL16V8 | GAL16V8 | Package_DIP:DIP-20_W7.62mm | Programmable Logic Array, DIP-20/SOIC-20/PLCC-20
X1, | 1 | PIO-1 | Conn_02x13_Odd_Even | Connector_IDC:IDC-Header_2x13_P2.54mm_Horizontal | Generic connector, double row, 02x13, odd/even pin numbering scheme (row 1 odd numbers, row 2 even numbers), script generated (kicad-library-utils/schlib/autogen/connector/)
X2, | 1 | PIO-2 | Conn_02x13_Odd_Even | Connector_IDC:IDC-Header_2x13_P2.54mm_Horizontal | Generic connector, double row, 02x13, odd/even pin numbering scheme (row 1 odd numbers, row 2 even numbers), script generated (kicad-library-utils/schlib/autogen/connector/)
X3, | 1 | RS-232 B | Conn_02x05_Odd_Even | Connector_IDC:IDC-Header_2x05_P2.54mm_Horizontal | Generic connector, double row, 02x05, odd/even pin numbering scheme (row 1 odd numbers, row 2 even numbers), script generated (kicad-library-utils/schlib/autogen/connector/)
X4, | 1 | SIO-CTC_TTL | Conn_02x13_Odd_Even | Connector_PinHeader_2.54mm:PinHeader_2x13_P2.54mm_Vertical | Generic connector, double row, 02x13, odd/even pin numbering scheme (row 1 odd numbers, row 2 even numbers), script generated (kicad-library-utils/schlib/autogen/connector/)
X5, | 1 | OSC_DIV | Conn_02x08_Odd_Even | Connector_PinHeader_2.54mm:PinHeader_2x08_P2.54mm_Vertical | Generic connector, double row, 02x08, odd/even pin numbering scheme (row 1 odd numbers, row 2 even numbers), script generated (kicad-library-utils/schlib/autogen/connector/)
X6, | 1 | BAUD_CLK | Conn_02x05_Odd_Even | Connector_PinHeader_2.54mm:PinHeader_2x05_P2.54mm_Vertical | Generic connector, double row, 02x05, odd/even pin numbering scheme (row 1 odd numbers, row 2 even numbers), script generated (kicad-library-utils/schlib/autogen/connector/)
X7, | 1 | RS-232 A | Conn_02x05_Odd_Even | Connector_IDC:IDC-Header_2x05_P2.54mm_Horizontal | Generic connector, double row, 02x05, odd/even pin numbering scheme (row 1 odd numbers, row 2 even numbers), script generated (kicad-library-utils/schlib/autogen/connector/)
X8, | 1 | TTL SERIAL | Conn_02x06_Odd_Even | Connector_IDC:IDC-Header_2x06_P2.54mm_Horizontal | Generic connector, double row, 02x06, odd/even pin numbering scheme (row 1 odd numbers, row 2 even numbers), script generated (kicad-library-utils/schlib/autogen/connector/)
X9, | 1 | UTILITY | Conn_02x06_Odd_Even | Connector_PinHeader_2.54mm:PinHeader_2x06_P2.54mm_Vertical | Generic connector, double row, 02x06, odd/even pin numbering scheme (row 1 odd numbers, row 2 even numbers), script generated (kicad-library-utils/schlib/autogen/connector/)
X10, | 1 | 2CTC CNFG | Conn_02x03_Odd_Even | Connector_PinHeader_2.54mm:PinHeader_2x03_P2.54mm_Vertical | Generic connector, double row, 02x03, odd/even pin numbering scheme (row 1 odd numbers, row 2 even numbers), script generated (kicad-library-utils/schlib/autogen/connector/)
