lynchaj/duodyne/!Development/24 DAISY256, V1.0/DAISY256.csv

Source: | C:\Users\Andrew\Desktop\System CD Updates\data\Old designs\DAISY256\DAISY256.kicad_sch
Date: | 4/1/2024 3:28:49 PM
Tool: | Eeschema (6.0.11)
Generator: | C:\Program Files\KiCad\6.0\bin\scripting\plugins/bom_csv_grouped_by_value_with_fp.py
Component Count: | 96
Ref | Qnty | Value | Cmp name | Footprint | Description | Vendor
C1, C2, C3, C5, C13, C20, C21, C22, C23, C24, C25, C26, C27, C28, C29, C32, C33, C34, C35, | 19 | 100nF | C_Small | Capacitor_THT:C_Disc_D5.0mm_W2.5mm_P5.00mm | Unpolarized capacitor, small symbol
C4, C8, | 2 | 220uF | C_Polarized_US | Capacitor_THT:CP_Radial_D6.3mm_P2.50mm | Polarized capacitor, US symbol
C6, C7, C14, C15, | 4 | 22pF | C_Small | Capacitor_THT:C_Disc_D5.0mm_W2.5mm_P5.00mm | Unpolarized capacitor, small symbol
C9, C12, C17, C18, C19, | 5 | 47nF | C_Small | Capacitor_THT:C_Disc_D5.0mm_W2.5mm_P5.00mm | Unpolarized capacitor, small symbol
C10, C11, C30, | 3 | 10uF | C_Polarized_US | Capacitor_THT:CP_Radial_D5.0mm_P2.00mm | Polarized capacitor, US symbol
C16, | 1 | 22nF | C_Small | Capacitor_THT:C_Disc_D5.0mm_W2.5mm_P5.00mm | Unpolarized capacitor, small symbol
C31, | 1 | 2.2uF | C_Polarized_US | Capacitor_THT:CP_Radial_Tantal_D5.0mm_P2.50mm | Polarized capacitor, US symbol
D1, | 1 | BUSY | LED | LED_THT:LED_D3.0mm | Light emitting diode
H1, H2, H3, H4, | 4 | MountingHole_Pad | MountingHole_Pad | MountingHole:MountingHole_3.2mm_M3_Pad | Mounting Hole with connection
J1, | 1 | DC_JACK | Barrel_Jack_Switch | Connector_BarrelJack:BarrelJack_Horizontal | DC Barrel Jack with an internal switch
J2, | 1 | DE9 | DB9_Female_MountingHoles | Connector_Dsub:DSUB-9_Female_Horizontal_P2.77x2.84mm_EdgePinOffset7.70mm_Housed_MountingHolesOffset9.12mm | 9-pin female D-SUB connector, Mounting Hole
J3, | 1 | Audio Out | AudioJack3_SwitchT | Audio Jack:Jack_3.5mm_CUI_SJ1-3544_Horizontal | Audio Jack, 3 Poles (Stereo / TRS), Switched T Pole (Normalling)
J4, | 1 | TxE | Conn_01x02 | Connector_PinHeader_2.54mm:PinHeader_1x02_P2.54mm_Vertical | Generic connector, single row, 01x02, script generated (kicad-library-utils/schlib/autogen/connector/)
J5, | 1 | SPKR | Conn_01x02 | Connector_Molex:Molex_KK-254_AE-6410-02A_1x02_P2.54mm_Vertical | Generic connector, single row, 01x02, script generated (kicad-library-utils/schlib/autogen/connector/)
J6, | 1 | 32/16 | Conn_01x03 | Connector_PinHeader_2.54mm:PinHeader_1x03_P2.54mm_Vertical | Generic connector, single row, 01x03, script generated (kicad-library-utils/schlib/autogen/connector/)
J7, | 1 | MODE | Conn_01x02 | Connector_PinHeader_2.54mm:PinHeader_1x02_P2.54mm_Vertical | Generic connector, single row, 01x02, script generated (kicad-library-utils/schlib/autogen/connector/)
J8, | 1 | DBM | Conn_01x02 | Connector_PinHeader_2.54mm:PinHeader_1x02_P2.54mm_Vertical | Generic connector, single row, 01x02, script generated (kicad-library-utils/schlib/autogen/connector/)
J9, J12, | 2 | DIL14 | Conn_02x07_Counter_Clockwise | Package_DIP:DIP-14_W7.62mm_Socket_LongPads | Generic connector, double row, 02x07, counter clockwise pin numbering scheme (similar to DIP package numbering), script generated (kicad-library-utils/schlib/autogen/connector/)
J10, J13, | 2 | DIL16 | Conn_02x08_Counter_Clockwise | Package_DIP:DIP-16_W7.62mm_Socket_LongPads | Generic connector, double row, 02x08, counter clockwise pin numbering scheme (similar to DIP package numbering), script generated (kicad-library-utils/schlib/autogen/connector/)
J11, J14, | 2 | DIL20 | Conn_02x10_Counter_Clockwise | Package_DIP:DIP-20_W7.62mm_Socket_LongPads | Generic connector, double row, 02x10, counter clockwise pin numbering scheme (similar to DIP package numbering), script generated (kicad-library-utils/schlib/autogen/connector/)
J15, | 1 | SER ROM | Conn_02x04_Odd_Even | Connector_PinHeader_2.54mm:PinHeader_2x04_P2.54mm_Vertical | Generic connector, double row, 02x04, odd/even pin numbering scheme (row 1 odd numbers, row 2 even numbers), script generated (kicad-library-utils/schlib/autogen/connector/)
J16, | 1 | PIC ROM | Conn_02x08_Odd_Even | Connector_PinHeader_2.54mm:PinHeader_2x08_P2.54mm_Vertical | Generic connector, double row, 02x08, odd/even pin numbering scheme (row 1 odd numbers, row 2 even numbers), script generated (kicad-library-utils/schlib/autogen/connector/)
P1, | 1 | 10K | R_Potentiometer_US | Potentiometer:Potentiometer_Bourns_PTV111-1_Single_Horizontal | Potentiometer, US symbol
R1, R4, R6, R7, R14, R15, R21, | 7 | 10K | R | Resistor_THT:R_Axial_DIN0207_L6.3mm_D2.5mm_P7.62mm_Horizontal | Resistor
R2, R5, R8, R9, R10, R11, R12, R19, R20, | 9 | 4.7K | R | Resistor_THT:R_Axial_DIN0207_L6.3mm_D2.5mm_P7.62mm_Horizontal | Resistor
R13, | 1 | 10R | R | Resistor_THT:R_Axial_DIN0207_L6.3mm_D2.5mm_P7.62mm_Horizontal | Resistor
R16, R17, | 2 | 1K | R | Resistor_THT:R_Axial_DIN0207_L6.3mm_D2.5mm_P7.62mm_Horizontal | Resistor
R18, | 1 | 20K | R | Resistor_THT:R_Axial_DIN0207_L6.3mm_D2.5mm_P7.62mm_Horizontal | Resistor
SW1, | 1 | RESET | SW_Push | Button_Switch_THT:SW_PUSH_6mm | Push button switch, generic, two pins
U1, | 1 | CTS256A-AL2 | CTS256A-AL2 | Package_DIP:DIP-40_W15.24mm_Socket_LongPads
U2, | 1 | 74LS373 | 74LS373 | Package_DIP:DIP-20_W7.62mm_Socket_LongPads | 8-bit Latch, 3-state outputs
U3, U12, | 2 | 74LS138 | 74LS138 | Package_DIP:DIP-16_W7.62mm_Socket_LongPads | Decoder 3 to 8 active low outputs
U4, | 1 | SP0256A-AL2 | SP0256A-AL2 | Package_DIP:DIP-28_W15.24mm_Socket_LongPads
U5, | 1 | LM324 | LM324 | Package_DIP:DIP-14_W7.62mm_Socket_LongPads | Low-Power, Quad-Operational Amplifiers, DIP-14/SOIC-14/SSOP-14
U6, | 1 | LM386 | LM386 | Package_DIP:DIP-8_W7.62mm_Socket_LongPads | Low Voltage Audio Power Amplifier, DIP-8/SOIC-8/SSOP-8
U7, | 1 | MAX232 | MAX232 | Package_DIP:DIP-16_W7.62mm_Socket_LongPads | Dual RS232 driver/receiver, 5V supply, 120kb/s, 0C-70C
U8, | 1 | 74LS14 | 74LS14 | Package_DIP:DIP-14_W7.62mm_Socket_LongPads | Hex inverter schmitt trigger
U9, | 1 | ICL7660 | ICL7660 | Package_DIP:DIP-8_W7.62mm_Socket_LongPads | Switched-Capacitor Voltage Converter, 1.5V to 10.0V operating supply voltage, 10mA with a 0.5V output drop, SO-8/DIP-8/µMAX-8/TO-99
U10, U13, | 2 | 2732 | 2732 | Package_DIP:DIP-24_W15.24mm_Socket_LongPads
U11, | 1 | 6116 | 6116 | Package_DIP:DIP-24_W15.24mm_Socket_LongPads
U14, | 1 | 24LC16 | 24LC16 | Package_DIP:DIP-8_W7.62mm_Socket_LongPads | I2C Serial EEPROM, 16Kb, DIP-8/SOIC-8/TSSOP-8/DFN-8
U15, | 1 | PIC16F685-IP | PIC16F685-IP | Package_DIP:DIP-20_W7.62mm_Socket_LongPads | 4096W Flash, 256B SRAM, 256B EEPROM, DIP20
U16, | 1 | GAL16V8 | GAL16V8 | Package_DIP:DIP-20_W7.62mm_Socket_LongPads | Programmable Logic Array, DIP-20/SOIC-20/PLCC-20
Y1, | 1 | 10MHz | Crystal_Small | Crystal:Crystal_HC49-4H_Vertical | Two pin crystal, small symbol
Y2, | 1 | 3.12MHz | Crystal_Small | Crystal:Crystal_HC49-U_Vertical | Two pin crystal, small symbol
