lynchaj/duodyne/!Development/08 input-output.Disk, V1.1/input-output.Disk.csv

Source: | C:\Users\Andrew\Desktop\System CD Updates\data\duodyne\GitHub\08 input-output.Disk, V1.1\input-output.Disk.kicad_sch
Date: | 1/15/2024 12:08:55 PM
Tool: | Eeschema (6.0.11)
Generator: | C:\Program Files\KiCad\6.0\bin\scripting\plugins/bom_csv_grouped_by_value_with_fp.py
Component Count: | 112
Ref | Qnty | Value | Cmp name | Footprint | Description | Vendor
C1, C2, C3, C4, C5, C6, C7, C8, C9, C10, C11, C12, C13, C14, C15, C17, C18, C19, C30, C32, C34, C35, | 22 | 0.1u | C | Capacitor_THT:C_Disc_D5.0mm_W2.5mm_P5.00mm | Unpolarized capacitor
C20, C21, C22, C23, C24, C25, C26, C27, C33, | 9 | 10u | C_Polarized | Capacitor_THT:CP_Radial_D5.0mm_P2.50mm | Polarized capacitor
C29, | 1 | 0.47u | C_Polarized | Capacitor_THT:CP_Radial_D5.0mm_P2.50mm | Polarized capacitor
C31, | 1 | 33u | C_Polarized | Capacitor_THT:CP_Radial_D5.0mm_P2.50mm | Polarized capacitor
D1, D3, D4, D5, | 4 | LED | LED | LED_THT:LED_D3.0mm_Horizontal_O3.81mm_Z2.0mm | Light emitting diode
D2, D6, D7, | 3 | LED | LED | LED_THT:LED_D3.0mm | Light emitting diode
D8, D9, D10, D11, | 4 | 1N5817 | 1N5817 | Diode_THT:D_DO-41_SOD81_P10.16mm_Horizontal | 20V 1A Schottky Barrier Rectifier Diode, DO-41
H1, H2, | 2 | MountingHole | MountingHole_Pad | MountingHole:MountingHole_3.2mm_M3_Pad | Mounting Hole with connection
J7, | 1 | FDC INTERRUPT | Conn_02x08_Odd_Even | Connector_PinHeader_2.54mm:PinHeader_2x08_P2.54mm_Vertical | Generic connector, double row, 02x08, odd/even pin numbering scheme (row 1 odd numbers, row 2 even numbers), script generated (kicad-library-utils/schlib/autogen/connector/)
J9, | 1 | RESET SEL | Conn_01x03 | Connector_PinHeader_2.54mm:PinHeader_1x03_P2.54mm_Vertical | Generic connector, single row, 01x03, script generated (kicad-library-utils/schlib/autogen/connector/)
J12, | 1 | SD_Card | SD_Card | Amphenol SD Card:SD_Card_Receptacle | SD Card Reader
J13, | 1 | ENET INTERRUPT | Conn_02x08_Odd_Even | Connector_PinHeader_2.54mm:PinHeader_2x08_P2.54mm_Vertical | Generic connector, double row, 02x08, odd/even pin numbering scheme (row 1 odd numbers, row 2 even numbers), script generated (kicad-library-utils/schlib/autogen/connector/)
JP1, | 1 | EXT LED | Jumper_2_Open | Connector_PinHeader_2.54mm:PinHeader_1x02_P2.54mm_Vertical | Jumper, 2-pole, open
JP2, | 1 | ENET INT | Jumper_2_Open | Connector_PinHeader_2.54mm:PinHeader_1x02_P2.54mm_Vertical | Jumper, 2-pole, open
JP3, | 1 | MISO | Jumper_2_Open | Connector_PinHeader_2.54mm:PinHeader_1x02_P2.54mm_Vertical | Jumper, 2-pole, open
K1, | 1 | PPI PWR | Conn_01x03 | Connector_PinHeader_2.54mm:PinHeader_1x03_P2.54mm_Vertical | Generic connector, single row, 01x03, script generated (kicad-library-utils/schlib/autogen/connector/)
K2, | 1 | IDE PWR | Conn_01x03 | Connector_PinHeader_2.54mm:PinHeader_1x03_P2.54mm_Vertical | Generic connector, single row, 01x03, script generated (kicad-library-utils/schlib/autogen/connector/)
P1, P2, P3, | 3 | CONN_02X25 | Conn_02x25_Odd_Even | Connector_IDC:IDC-Header_2x25_P2.54mm_Horizontal | Generic connector, double row, 02x25, odd/even pin numbering scheme (row 1 odd numbers, row 2 even numbers), script generated (kicad-library-utils/schlib/autogen/connector/)
P4, | 1 | BYPASS | Conn_01x04 | Connector_PinHeader_2.54mm:PinHeader_1x04_P2.54mm_Vertical | Generic connector, single row, 01x04, script generated (kicad-library-utils/schlib/autogen/connector/)
P5, | 1 | PPI | Conn_02x13_Odd_Even | Connector_IDC:IDC-Header_2x13_P2.54mm_Horizontal | Generic connector, double row, 02x13, odd/even pin numbering scheme (row 1 odd numbers, row 2 even numbers), script generated (kicad-library-utils/schlib/autogen/connector/)
P6, | 1 | IDE | Conn_02x20_Odd_Even | Connector_IDC:IDC-Header_2x20_P2.54mm_Horizontal | Generic connector, double row, 02x20, odd/even pin numbering scheme (row 1 odd numbers, row 2 even numbers), script generated (kicad-library-utils/schlib/autogen/connector/)
P7, | 1 | FDC CLK | Conn_01x03 | Connector_PinHeader_2.54mm:PinHeader_1x03_P2.54mm_Vertical | Generic connector, single row, 01x03, script generated (kicad-library-utils/schlib/autogen/connector/)
P8, | 1 | TEND SEL | Conn_01x03 | Connector_PinHeader_2.54mm:PinHeader_1x03_P2.54mm_Vertical | Generic connector, single row, 01x03, script generated (kicad-library-utils/schlib/autogen/connector/)
P9, | 1 | DREQ SEL | Conn_01x03 | Connector_PinHeader_2.54mm:PinHeader_1x03_P2.54mm_Vertical | Generic connector, single row, 01x03, script generated (kicad-library-utils/schlib/autogen/connector/)
P10, | 1 | FLOPPY | Conn_02x17_Odd_Even | Connector_IDC:IDC-Header_2x17_P2.54mm_Horizontal | Generic connector, double row, 02x17, odd/even pin numbering scheme (row 1 odd numbers, row 2 even numbers), script generated (kicad-library-utils/schlib/autogen/connector/)
R1, R8, R9, R14, R15, R16, R30, R31, | 8 | 470 | R | Resistor_THT:R_Axial_DIN0207_L6.3mm_D2.5mm_P7.62mm_Horizontal | Resistor
R4, R5, R7, | 3 | 10K | R | Resistor_THT:R_Axial_DIN0207_L6.3mm_D2.5mm_P7.62mm_Horizontal | Resistor
R6, | 1 | 0 | R | Resistor_THT:R_Axial_DIN0207_L6.3mm_D2.5mm_P7.62mm_Horizontal | Resistor
R10, R11, R12, R13, | 4 | 4700 | R | Resistor_THT:R_Axial_DIN0207_L6.3mm_D2.5mm_P7.62mm_Horizontal | Resistor
R29, R32, R48, | 3 | 22K | R | Resistor_THT:R_Axial_DIN0207_L6.3mm_D2.5mm_P7.62mm_Horizontal | Resistor
R41, R42, | 2 | 1000 | R | Resistor_THT:R_Axial_DIN0207_L6.3mm_D2.5mm_P7.62mm_Horizontal | Resistor
R47, | 1 | 2200 | R | Resistor_THT:R_Axial_DIN0207_L6.3mm_D2.5mm_P7.62mm_Horizontal | Resistor
RN1, | 1 | 10K | R_Network08 | Resistor_THT:R_Array_SIP9 | 8 resistor network, star topology, bussed resistors, small symbol
RP1, | 1 | 1000 | R_Network08 | Resistor_THT:R_Array_SIP9 | 8 resistor network, star topology, bussed resistors, small symbol
SW1, | 1 | IO PORT ADDR | Conn_02x04_Odd_Even | Connector_PinHeader_2.54mm:PinHeader_2x04_P2.54mm_Vertical | Generic connector, double row, 02x04, odd/even pin numbering scheme (row 1 odd numbers, row 2 even numbers), script generated (kicad-library-utils/schlib/autogen/connector/)
U3, | 1 | 74LS06 | 74LS06 | Package_DIP:DIP-14_W7.62mm | Inverter Open Collect
U5, | 1 | 74LS14 | 74LS14 | Package_DIP:DIP-14_W7.62mm | Hex inverter schmitt trigger
U6, | 1 | 82C55A_PLCC | 82C55A_PLCC | Package_LCC:PLCC-44_THT-Socket | CHMOS Programmable Peripheral Interface, PLCC-44
U7, | 1 | 16 MHz | Conn_02x07_Counter_Clockwise | Package_DIP:DIP-14_W7.62mm | Generic connector, double row, 02x07, counter clockwise pin numbering scheme (similar to DIP package numbering), script generated (kicad-library-utils/schlib/autogen/connector/)
U8, | 1 | WD37C65BJM | WD37C65BJW | Package_LCC:PLCC-44_THT-Socket
U9, | 1 | 9.6 MHz | Conn_02x07_Counter_Clockwise | Package_DIP:DIP-14_W7.62mm | Generic connector, double row, 02x07, counter clockwise pin numbering scheme (similar to DIP package numbering), script generated (kicad-library-utils/schlib/autogen/connector/)
U10, U11, | 2 | GAL16V8 | GAL16V8 | Package_DIP:DIP-20_W7.62mm | Programmable Logic Array, DIP-20/SOIC-20/PLCC-20
U13, U15, | 2 | 74LS244 | 74LS244 | Package_DIP:DIP-20_W7.62mm | Octal Buffer and Line Driver With 3-State Output, active-low enables, non-inverting outputs
U14, | 1 | 74LS245 | 74LS245 | Package_DIP:DIP-20_W7.62mm | Octal BUS Transceivers, 3-State outputs
U20, | 1 | SPX2920U-3.3_TO220 | SPX2920U-3.3_TO220 | Package_TO_SOT_THT:TO-220-3_Horizontal_TabDown | 400mA Low drop-out regulator, Fixed Output 3.3V, TO-220
U21, | 1 | 74LS688 | 74LS688 | Package_DIP:DIP-20_W7.62mm | 8-bit magnitude comparator
U23, | 1 | 74ALS10 | 74LS10 | Package_DIP:DIP-14_W7.62mm | Triple 3-input NAND
U24, | 1 | 74LS138 | 74LS138 | Package_DIP:DIP-16_W7.62mm | Decoder 3 to 8 active low outputs
U25, | 1 | 74LS163 | 74LS163 | Package_DIP:DIP-16_W7.62mm | Synchronous 4-bit programmable binary Counter
U26, | 1 | 74AHC02 | 74HC02 | Package_DIP:DIP-14_W7.62mm | quad 2-input NOR gate
U27, | 1 | 74HCT175 | 74LS175 | Package_DIP:DIP-16_W7.62mm | 4-bit D Flip-Flop, reset
U28, | 1 | 74LS595 | 74LS595 | Package_DIP:DIP-16_W7.62mm | 8-bit serial in/out Shift Register 3-State Outputs
U29, | 1 | 74LS165 | 74LS165 | Package_DIP:DIP-16_W7.62mm | Shift Register 8-bit, parallel load
U30, | 1 | 25LCxxx | 25LCxxx | Package_DIP:DIP-8_W7.62mm | SPI Serial EEPROM, DIP-8/SOIC-8/TSSOP-8
U31, | 1 | WIZ850IO | WIZ850IO | WIZ850IO:WIZ850IO
