lynchaj/duodyne/!Development/13 input-output.GDC, V1.0/input-output.GDC.csv

Source: | C:\Users\Andrew\Desktop\System CD Updates\data\duodyne\GitHub\13 input-output.GDC, V1.0\input-output.GDC.kicad_sch
Date: | 1/15/2024 9:13:48 AM
Tool: | Eeschema (6.0.11)
Generator: | C:\Program Files\KiCad\6.0\bin\scripting\plugins/bom_csv_grouped_by_value_with_fp.py
Component Count: | 157
Ref | Qnty | Value | Cmp name | Footprint | Description | Vendor
C1, C2, C3, C4, C5, C6, C7, C8, C9, C10, C11, C12, C13, C14, C15, C16, C17, C18, C19, C28, C29, C30, C31, C32, C33, C34, C35, C36, C37, C38, C39, C40, C41, C42, C43, C44, C45, C46, C47, C48, C49, C50, C51, C52, C53, C54, C55, C56, C57, C58, | 50 | 0.1u | C | Capacitor_THT:C_Disc_D5.0mm_W2.5mm_P5.00mm | Unpolarized capacitor
C20, C21, C22, C23, C24, C25, C26, C27, | 8 | 10u | C_Polarized | Capacitor_THT:CP_Radial_D5.0mm_P2.50mm | Polarized capacitor
D1, D3, D4, D5, | 4 | LED | LED | LED_THT:LED_D3.0mm_Horizontal_O3.81mm_Z2.0mm | Light emitting diode
D2, D6, D7, D8, D9, D10, | 6 | 1N4148 | D | Diode_THT:D_DO-41_SOD81_P7.62mm_Horizontal | Diode
D11, | 1 | LM385BZ-1.2 | D_Zener | Package_TO_SOT_THT:TO-92L_HandSolder | Zener diode
H1, H2, | 2 | MountingHole | MountingHole_Pad | MountingHole:MountingHole_3.2mm_M3_Pad | Mounting Hole with connection
H3, H4, | 2 | MountingHole | MountingHole | MountingHole:MountingHole_2.2mm_M2_DIN965_Pad | Mounting Hole without connection
J1, J4, | 2 | DIL14 | Conn_02x07_Counter_Clockwise | Package_DIP:DIP-14_W7.62mm_Socket | Generic connector, double row, 02x07, counter clockwise pin numbering scheme (similar to DIP package numbering), script generated (kicad-library-utils/schlib/autogen/connector/)
J2, J5, | 2 | DIL16 | Conn_02x08_Counter_Clockwise | Package_DIP:DIP-16_W7.62mm_Socket | Generic connector, double row, 02x08, counter clockwise pin numbering scheme (similar to DIP package numbering), script generated (kicad-library-utils/schlib/autogen/connector/)
J3, J6, | 2 | DIL20 | Conn_02x10_Counter_Clockwise | Package_DIP:DIP-20_W7.62mm_Socket | Generic connector, double row, 02x10, counter clockwise pin numbering scheme (similar to DIP package numbering), script generated (kicad-library-utils/schlib/autogen/connector/)
J8, | 1 | GDC DMA SEL | Conn_02x04_Odd_Even | Connector_PinHeader_2.54mm:PinHeader_2x04_P2.54mm_Vertical | Generic connector, double row, 02x04, odd/even pin numbering scheme (row 1 odd numbers, row 2 even numbers), script generated (kicad-library-utils/schlib/autogen/connector/)
J9, | 1 | RESET SEL | Conn_01x03 | Connector_PinHeader_2.54mm:PinHeader_1x03_P2.54mm_Vertical | Generic connector, single row, 01x03, script generated (kicad-library-utils/schlib/autogen/connector/)
JP1, | 1 | SYNC | Conn_01x03 | Connector_PinHeader_2.54mm:PinHeader_1x03_P2.54mm_Vertical | Generic connector, single row, 01x03, script generated (kicad-library-utils/schlib/autogen/connector/)
JP2, | 1 | VGA VCC | Jumper_2_Open | Connector_PinHeader_2.54mm:PinHeader_1x02_P2.54mm_Vertical | Jumper, 2-pole, open
JP3, | 1 | CLR 4-7 | Conn_02x04_Odd_Even | Connector_PinHeader_2.54mm:PinHeader_2x04_P2.54mm_Vertical | Generic connector, double row, 02x04, odd/even pin numbering scheme (row 1 odd numbers, row 2 even numbers), script generated (kicad-library-utils/schlib/autogen/connector/)
JP12, | 1 | HSYNC | Conn_01x03 | Connector_PinHeader_2.54mm:PinHeader_1x03_P2.54mm_Vertical | Generic connector, single row, 01x03, script generated (kicad-library-utils/schlib/autogen/connector/)
JP13, | 1 | VSYNC | Conn_01x03 | Connector_PinHeader_2.54mm:PinHeader_1x03_P2.54mm_Vertical | Generic connector, single row, 01x03, script generated (kicad-library-utils/schlib/autogen/connector/)
P1, P2, P3, | 3 | CONN_02X25 | Conn_02x25_Odd_Even | Connector_IDC:IDC-Header_2x25_P2.54mm_Horizontal | Generic connector, double row, 02x25, odd/even pin numbering scheme (row 1 odd numbers, row 2 even numbers), script generated (kicad-library-utils/schlib/autogen/connector/)
P4, | 1 | BYPASS | Conn_01x04 | Connector_PinHeader_2.54mm:PinHeader_1x04_P2.54mm_Vertical | Generic connector, single row, 01x04, script generated (kicad-library-utils/schlib/autogen/connector/)
P5, | 1 | DB15-HD-F | DB15_Female_HighDensity_MountingHoles | Connector_Dsub:DSUB-15-HD_Female_Horizontal_P2.29x1.98mm_EdgePinOffset3.03mm_Housed_MountingHolesOffset4.94mm | 15-pin female D-SUB connector, High density (3 columns), Triple Row, Generic, VGA-connector, Mounting Hole
Q1, Q2, | 2 | 2N2222A | Q_NPN_EBC | Package_TO_SOT_THT:TO-92L_HandSolder | NPN transistor, emitter/base/collector
R1, R14, R15, R16, | 4 | 470 | R | Resistor_THT:R_Axial_DIN0207_L6.3mm_D2.5mm_P7.62mm_Horizontal | Resistor
R2, R3, R4, R5, R8, | 5 | 1000 | R | Resistor_THT:R_Axial_DIN0207_L6.3mm_D2.5mm_P7.62mm_Horizontal | Resistor
R6, R13, | 2 | 4700 | R | Resistor_THT:R_Axial_DIN0207_L6.3mm_D2.5mm_P7.62mm_Horizontal | Resistor
R7, | 1 | 147 | R | Resistor_THT:R_Axial_DIN0207_L6.3mm_D2.5mm_P7.62mm_Horizontal | Resistor
R9, R10, R11, R12, | 4 | 2200 | R | Resistor_THT:R_Axial_DIN0207_L6.3mm_D2.5mm_P7.62mm_Horizontal | Resistor
RN1, | 1 | 10K | R_Network08 | Resistor_THT:R_Array_SIP9 | 8 resistor network, star topology, bussed resistors, small symbol
RR1, | 1 | 4700 | R_Network08 | Resistor_THT:R_Array_SIP9 | 8 resistor network, star topology, bussed resistors, small symbol
SW1, | 1 | IO PORT ADDR | Conn_02x04_Odd_Even | Connector_PinHeader_2.54mm:PinHeader_2x04_P2.54mm_Vertical | Generic connector, double row, 02x04, odd/even pin numbering scheme (row 1 odd numbers, row 2 even numbers), script generated (kicad-library-utils/schlib/autogen/connector/)
U1, U2, | 2 | 74LS573 | 74LS573 | Package_DIP:DIP-20_W7.62mm_Socket | 8-bit Latch 3-state outputs
U3, U7, | 2 | GAL22V10 | GAL22V10 | Package_DIP:DIP-24_W7.62mm_Socket
U4, | 1 | uPD7220 | UPD7220 | Package_DIP:DIP-40_W15.24mm_Socket
U5, | 1 | 74LS07 | 74LS07 | Package_DIP:DIP-14_W7.62mm_Socket | Hex Buffers and Drivers With Open Collector High Voltage Outputs
U6, | 1 | 74LS175 | 74LS175 | Package_DIP:DIP-16_W7.62mm_Socket | 4-bit D Flip-Flop, reset
U9, | 1 | 74LS163 | 74LS163 | Package_DIP:DIP-16_W7.62mm_Socket | Synchronous 4-bit programmable binary Counter
U13, U15, | 2 | 74LS244 | 74LS244 | Package_DIP:DIP-20_W7.62mm_Socket | Octal Buffer and Line Driver With 3-State Output, active-low enables, non-inverting outputs
U14, U20, U22, U23, U24, U33, U34, U35, U36, | 9 | 74LS245 | 74LS245 | Package_DIP:DIP-20_W7.62mm_Socket | Octal BUS Transceivers, 3-State outputs
U17, | 1 | 74F20 | 74LS20 | Package_DIP:DIP-12_W7.62mm_Socket | Dual 4-input NAND
U18, U79, | 2 | 74LS74 | 74LS74 | Package_DIP:DIP-14_W7.62mm_Socket | Dual D Flip-flop, Set & Reset
U21, | 1 | 74LS688 | 74LS688 | Package_DIP:DIP-20_W7.62mm_Socket | 8-bit magnitude comparator
U25, U26, U27, U28, U38, U40, U41, U42, | 8 | IS61C256 | KM62256CLP | Package_DIP:DIP-28_W7.62mm_Socket | 32Kx8 bit Low Power CMOS Static RAM, 55/70ns, DIP-28
U29, U30, U31, U32, U43, U44, U45, U46, | 8 | 74F299 | 74LS299 | Package_DIP:DIP-20_W7.62mm_Socket | 8-bit Universal shift/storage Register
U37, | 1 | 74LS139 | 74LS139 | Package_DIP:DIP-16_W7.62mm_Socket | Dual Decoder 1 of 4, Active low outputs
U47, | 1 | 74F04 | 74LS04 | Package_DIP:DIP-14_W7.62mm_Socket | Hex Inverter
U48, | 1 | 74LS273 | 74LS273 | Package_DIP:DIP-20_W7.62mm_Socket | 8-bit D Flip-Flop, reset
U51, | 1 | BT478 | BT478-brooktre1 | Package_LCC:PLCC-44_THT-Socket
U59, | 1 | 74F74 | 74LS74 | Package_DIP:DIP-14_W7.62mm_Socket | Dual D Flip-flop, Set & Reset
X4, | 1 | PIX CLK | Conn_02x07_Counter_Clockwise | Package_DIP:DIP-14_W7.62mm_Socket | Generic connector, double row, 02x07, counter clockwise pin numbering scheme (similar to DIP package numbering), script generated (kicad-library-utils/schlib/autogen/connector/)
