lynchaj/duodyne/!Development/22 input-output.BusExtender, V1.0/input-output.BusExtender.csv

Source: | C:\Users\Andrew\Desktop\System CD Updates\data\duodyne\GitHub\22 input-output.BusExtender, V1.0\input-output.BusExtender.kicad_sch
Date: | 12/23/2023 11:40:26 AM
Tool: | Eeschema (6.0.11)
Generator: | C:\Program Files\KiCad\6.0\bin\scripting\plugins/bom_csv_grouped_by_value_with_fp.py
Component Count: | 10
Ref | Qnty | Value | Cmp name | Footprint | Description | Vendor
D1, | 1 | LED | LED | LED_THT:LED_D3.0mm_Horizontal_O3.81mm_Z2.0mm | Light emitting diode
H1, H2, | 2 | MountingHole | MountingHole_Pad | MountingHole:MountingHole_3.2mm_M3_Pad | Mounting Hole with connection
P1, P2, P3, | 3 | CONN_02X25 | Conn_02x25_Odd_Even | Connector_IDC:IDC-Header_2x25_P2.54mm_Horizontal | Generic connector, double row, 02x25, odd/even pin numbering scheme (row 1 odd numbers, row 2 even numbers), script generated (kicad-library-utils/schlib/autogen/connector/)
P4, P5, P6, | 3 | CONN_02X25 | Conn_02x25_Odd_Even | Connector_PinSocket_2.54mm:PinSocket_2x25_P2.54mm_Horizontal | Generic connector, double row, 02x25, odd/even pin numbering scheme (row 1 odd numbers, row 2 even numbers), script generated (kicad-library-utils/schlib/autogen/connector/)
R1, | 1 | 470 | R | Resistor_THT:R_Axial_DIN0207_L6.3mm_D2.5mm_P7.62mm_Horizontal | Resistor
