lynchaj/duodyne/10 input-output.Voice, V1.0/temp/Z180GDCV2-SND/Terminal block 5mm.step

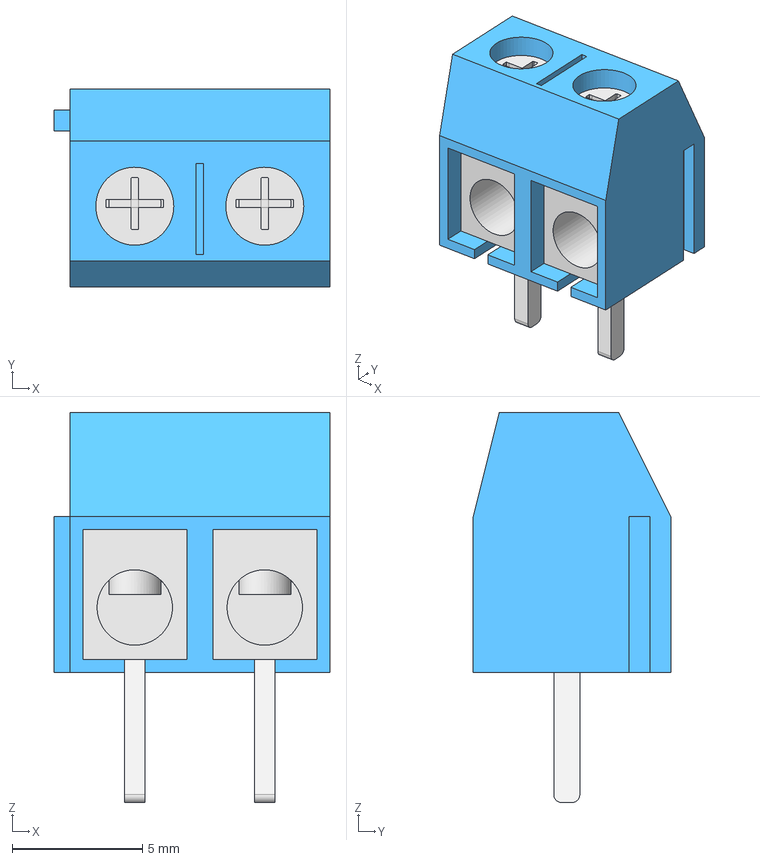
[picture p96: CAD file, 2023-04-09]
10 input-output.Voice, V1.0/temp/Z180GDCV2-SND/Terminal block 5mm.step
10.6 x 7.60 x 15.0 mm
Tornillos001
