lynchaj/duodyne/!Initial Build and Test/Andrew's DualESP32 build.jpg

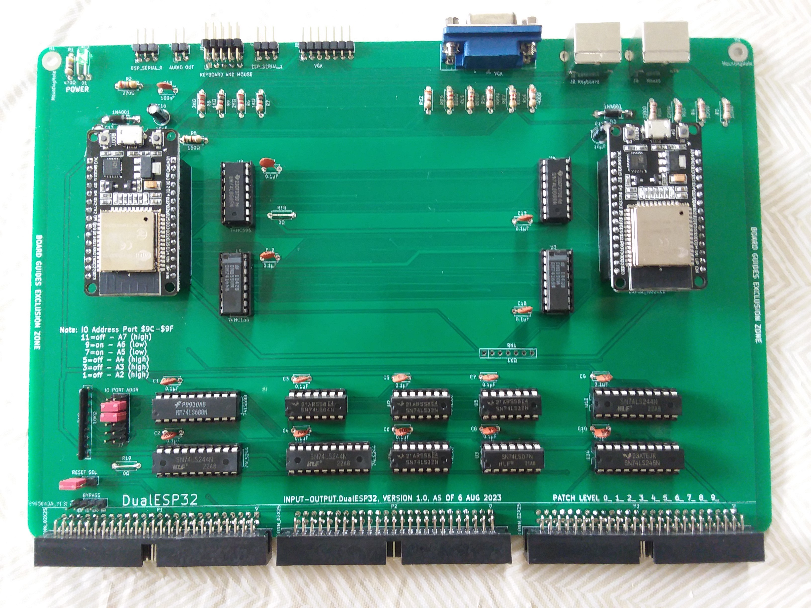
!Initial Build and Test/Andrew's DualESP32 build.jpg
