lynchaj/duodyne/!Initial Build and Test/Andrew's power supply.jpg

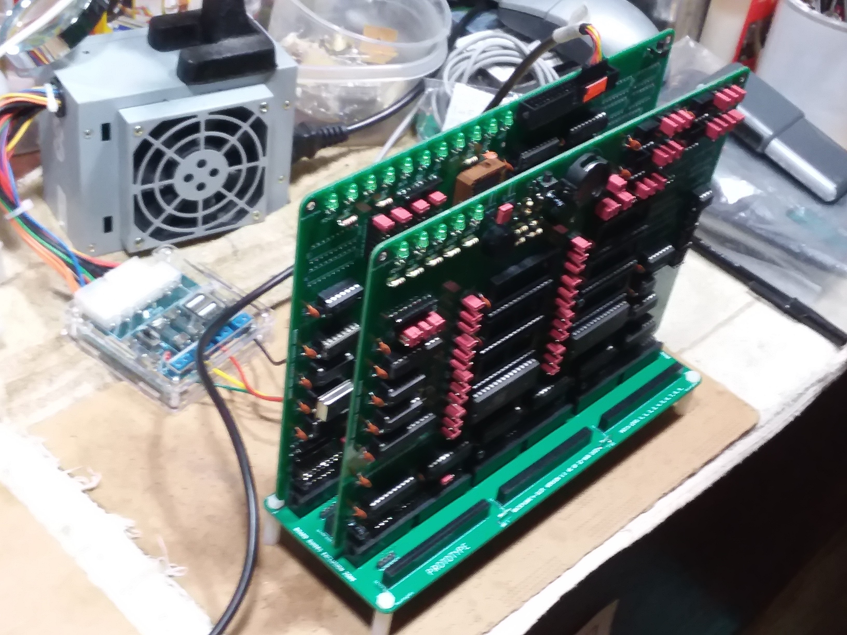
!Initial Build and Test/Andrew's power supply.jpg
