lynchaj/duodyne/!Initial Build and Test/Andrew's ROMWBW boot.jpg

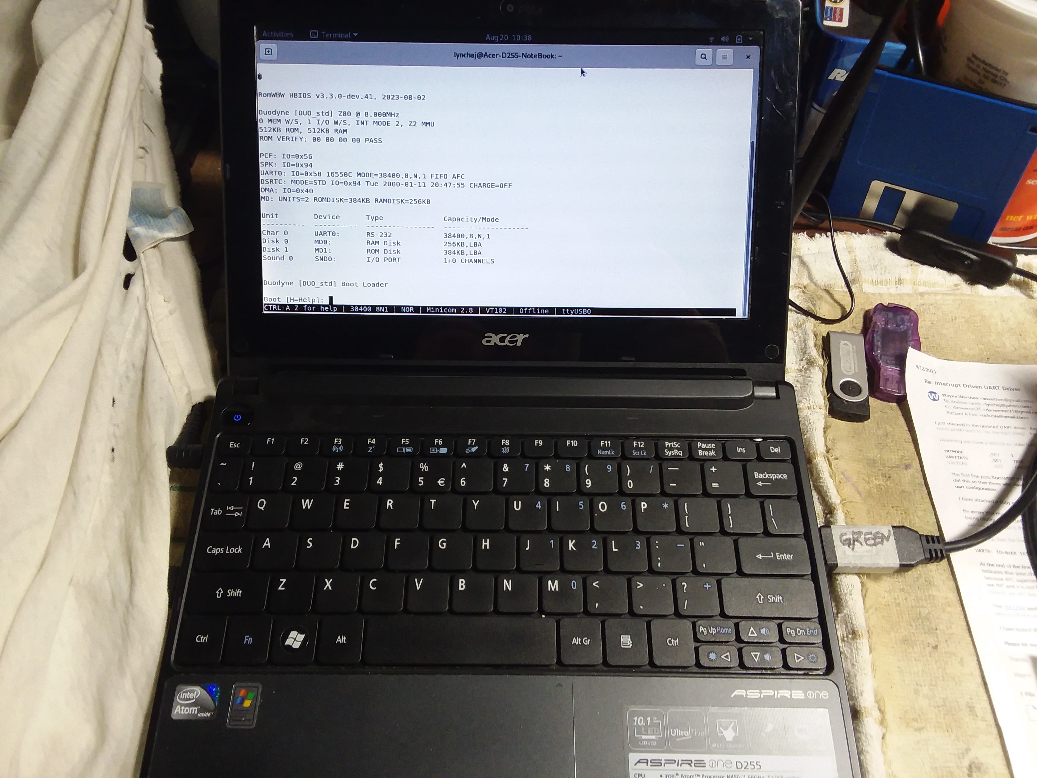
!Initial Build and Test/Andrew's ROMWBW boot.jpg
