lynchaj/duodyne/!Initial Build and Test/Dan's ESP32 build.jpg

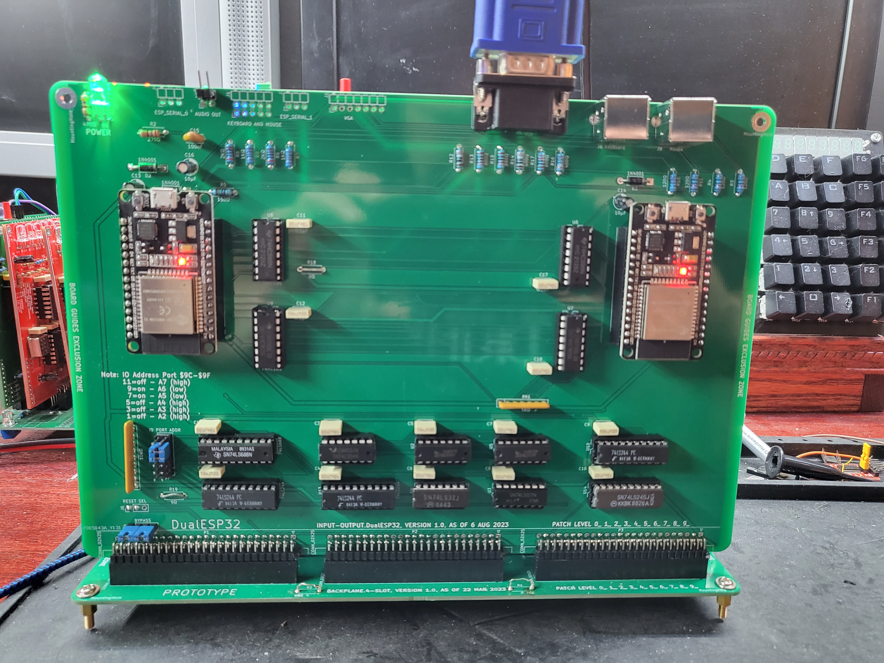
!Initial Build and Test/Dan's ESP32 build.jpg
