lynchaj/duodyne/!Initial Build and Test/Dan's ESP32 demo.jpg

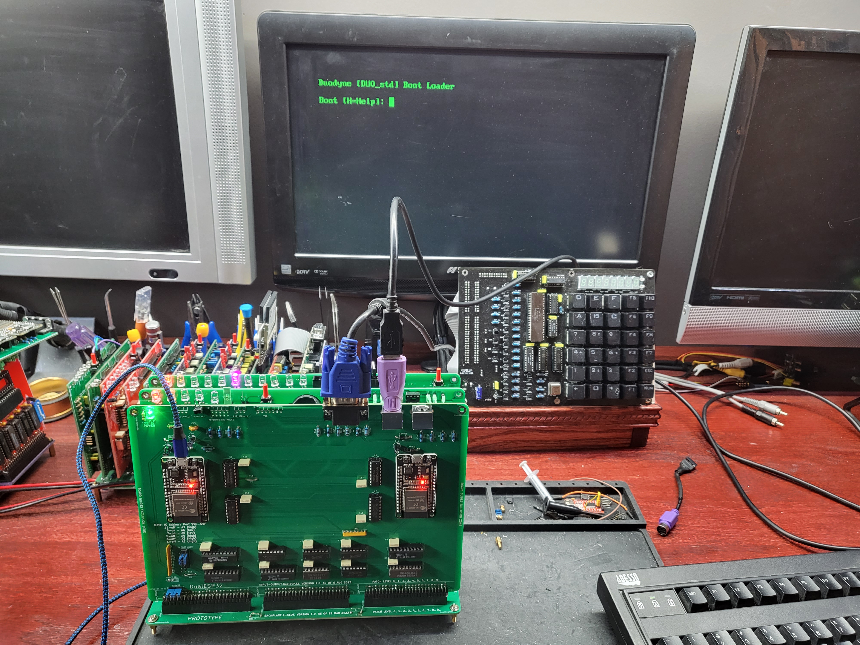
!Initial Build and Test/Dan's ESP32 demo.jpg
