lynchaj/duodyne/!Initial Build and Test/Dan's ROMRAM build.jpg

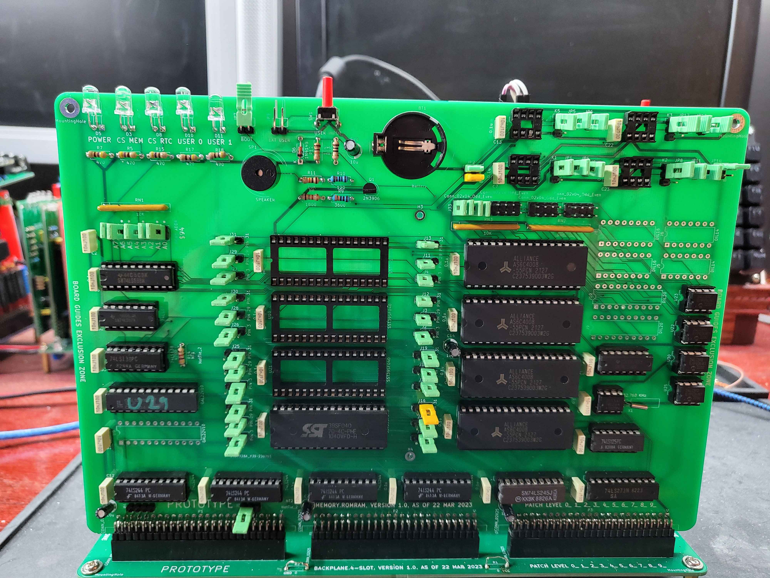
!Initial Build and Test/Dan's ROMRAM build.jpg
