lynchaj/duodyne/!Initial Build and Test/Dan's Z80 processor build.jpg

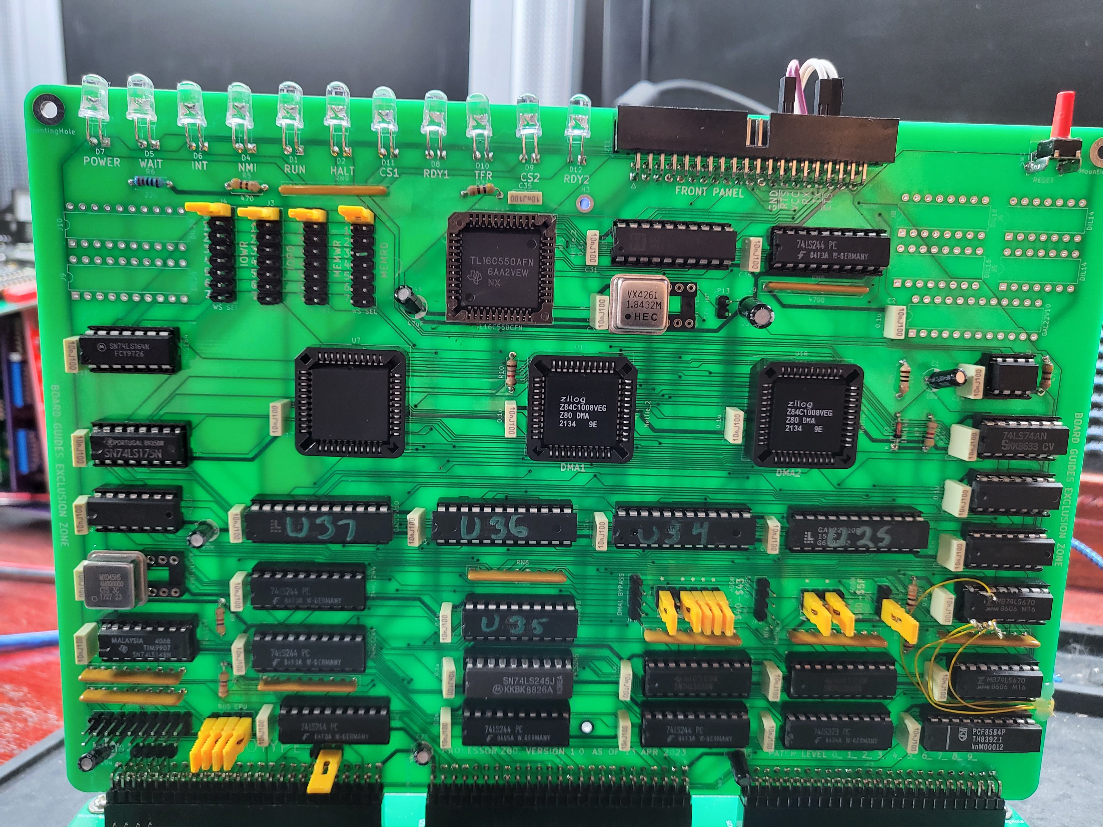
!Initial Build and Test/Dan's Z80 processor build.jpg
