lynchaj/duodyne/!Initial Build and Test/Phil's ROMRAM build.jpg

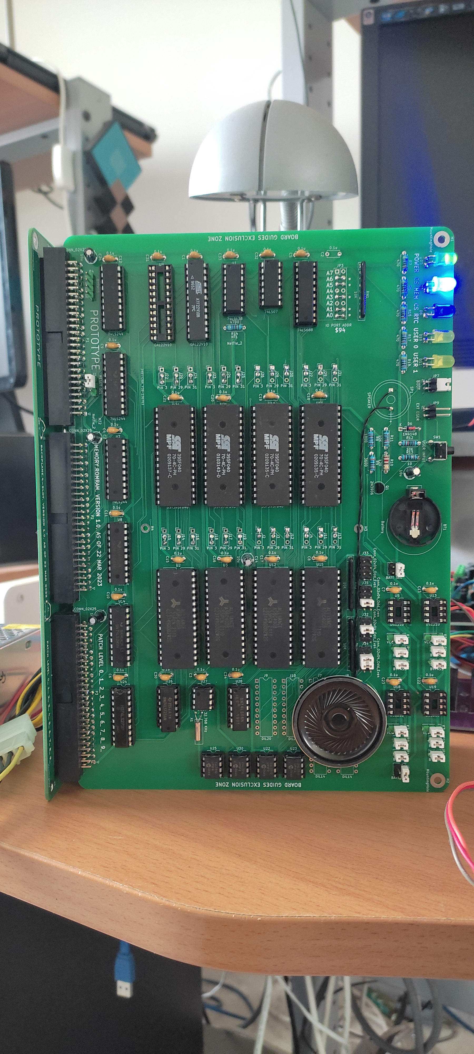
!Initial Build and Test/Phil's ROMRAM build.jpg
