lynchaj/duodyne/!Initial Build and Test/Phil's Z80 processor build.jpg

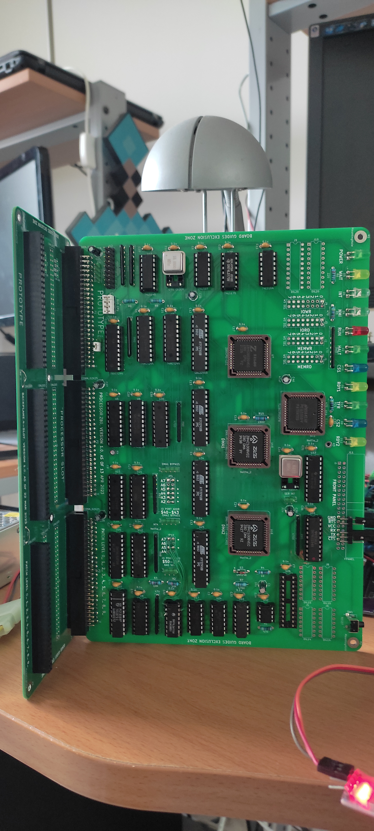
!Initial Build and Test/Phil's Z80 processor build.jpg
