lynchaj/duodyne/!Initial Build and Test/Phil's Z80 processor patches.jpg

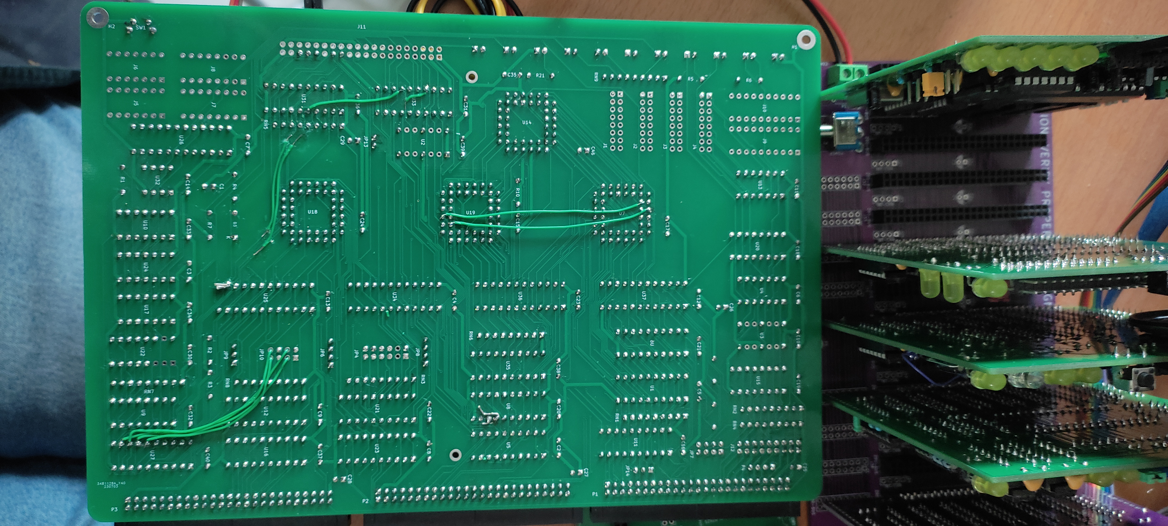
!Initial Build and Test/Phil's Z80 processor patches.jpg
