lynchaj/duodyne/!Initial Build and Test/Rob's Z80 processor board.png

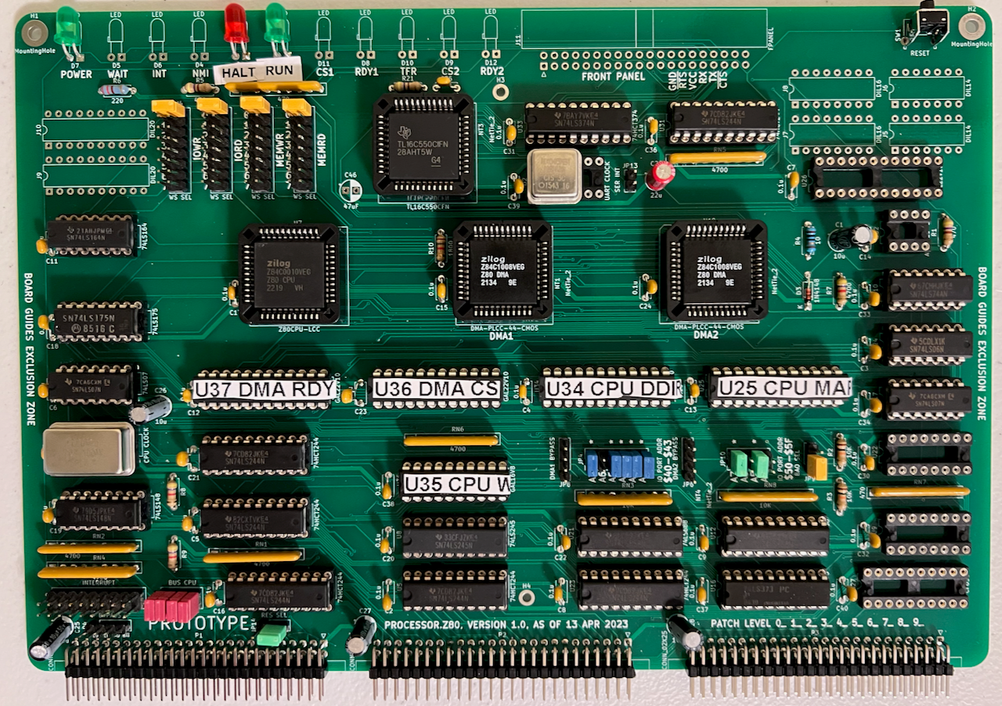
!Initial Build and Test/Rob's Z80 processor board.png
