lynchaj/duodyne/!Initial Build and Test/Wayne's Media IO.jpg

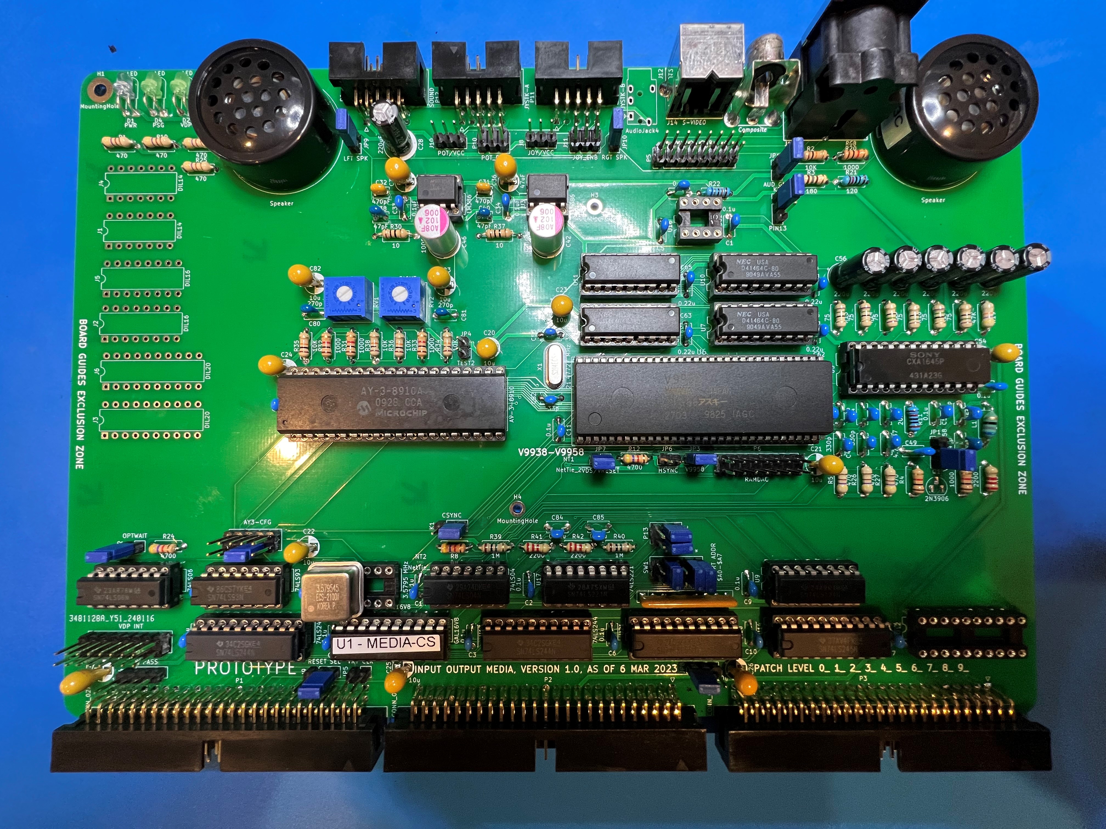
!Initial Build and Test/Wayne's Media IO.jpg
