lynchaj/duodyne/!Initial Build and Test/Wayne's Zilog IO.jpg

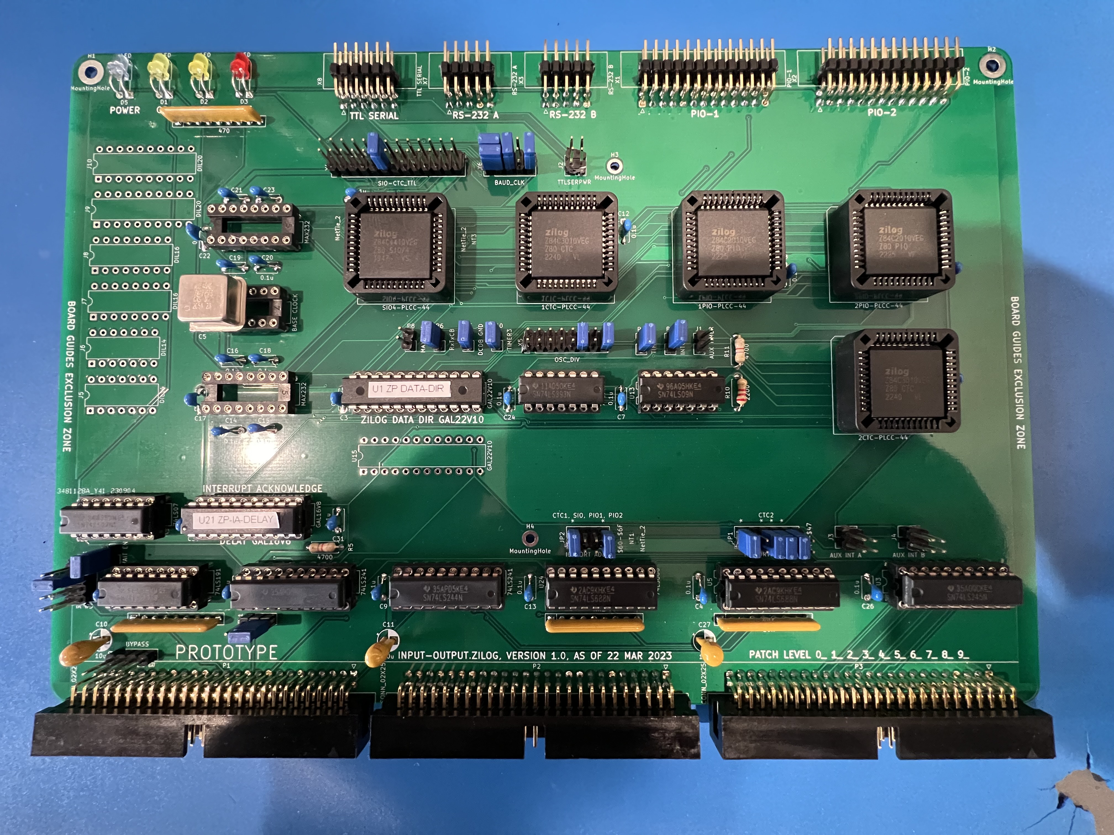
!Initial Build and Test/Wayne's Zilog IO.jpg
