lynchaj/duodyne/!Development/Slick/CPLDs/z80-processor-DMA/fix-data-dir.png

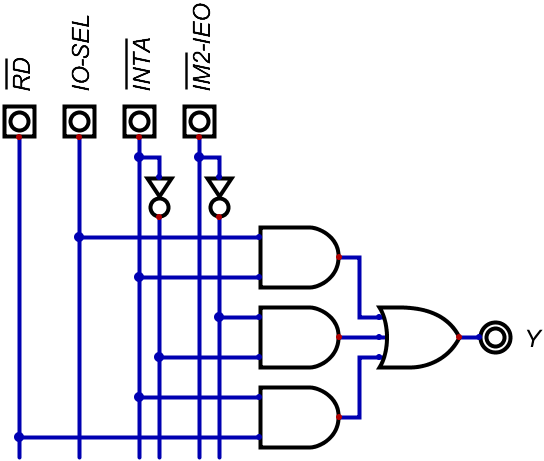
!Development/Slick/CPLDs/z80-processor-DMA/fix-data-dir.png
