lynchaj/duodyne/02 backplane.8-slot, V1.0/backplane.8-slot.schematic.pdf

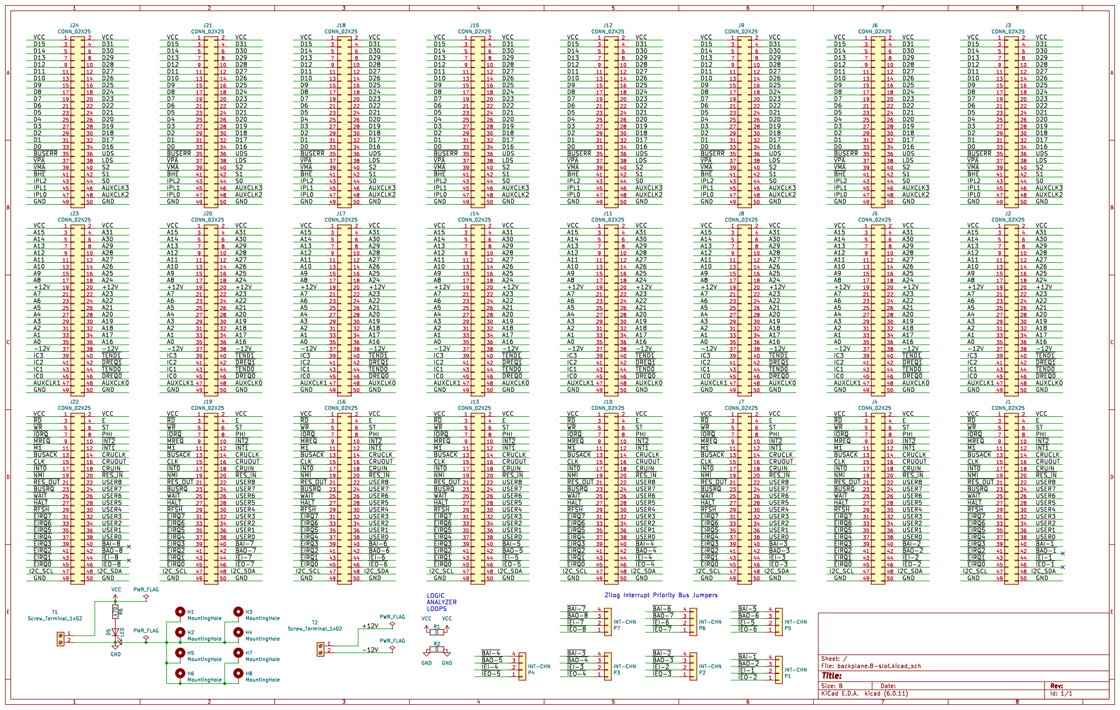
[picture p194: page 1]
