lynchaj/duodyne/07 backplane.4-slot, V1.0/backplane.4-slot.schematic.pdf

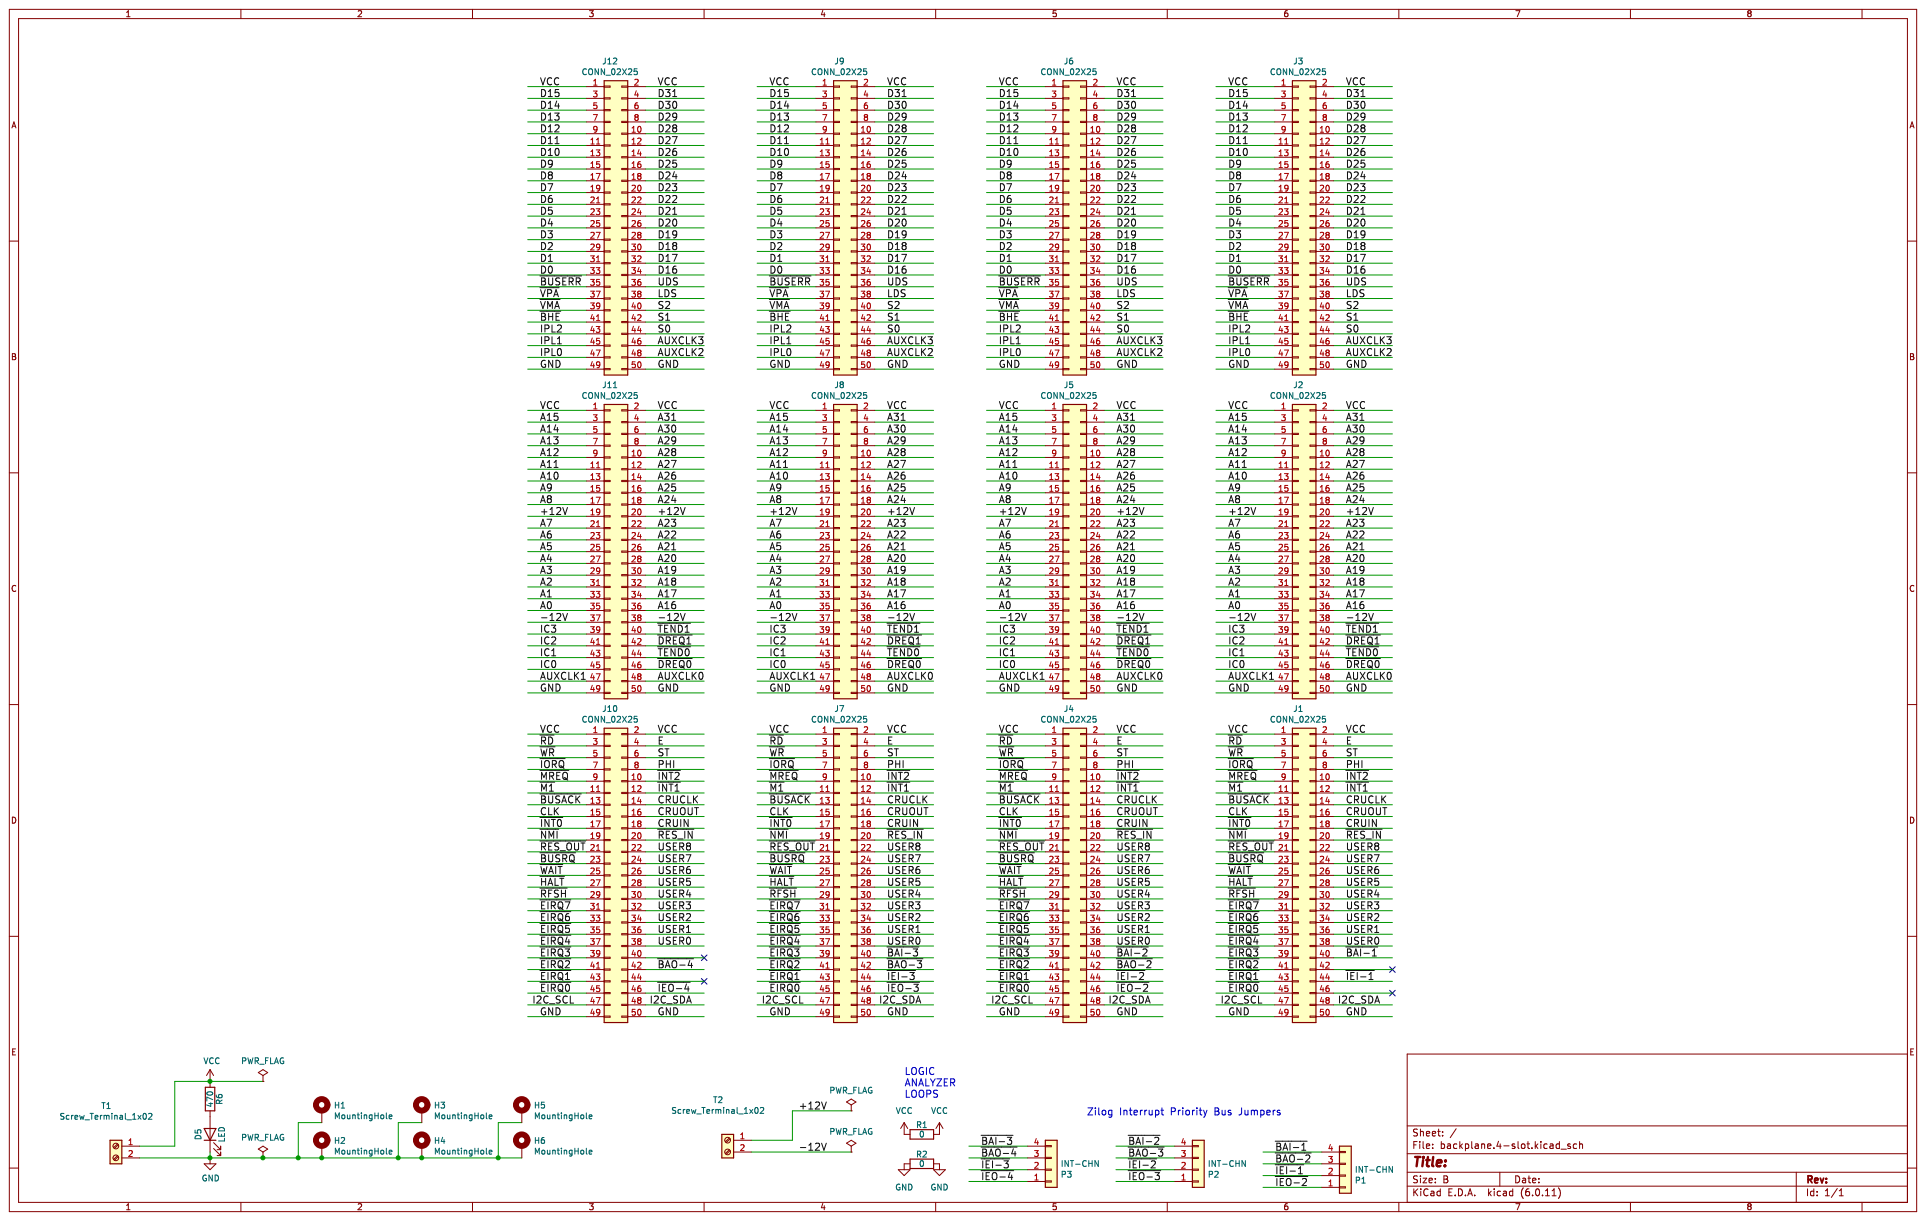
[picture p195: page 1]
