lynchaj/duodyne/10 input-output.Voice, V1.0/CTS256-SP0256 Schematic.pdf

9600 baud,
7 data bits,

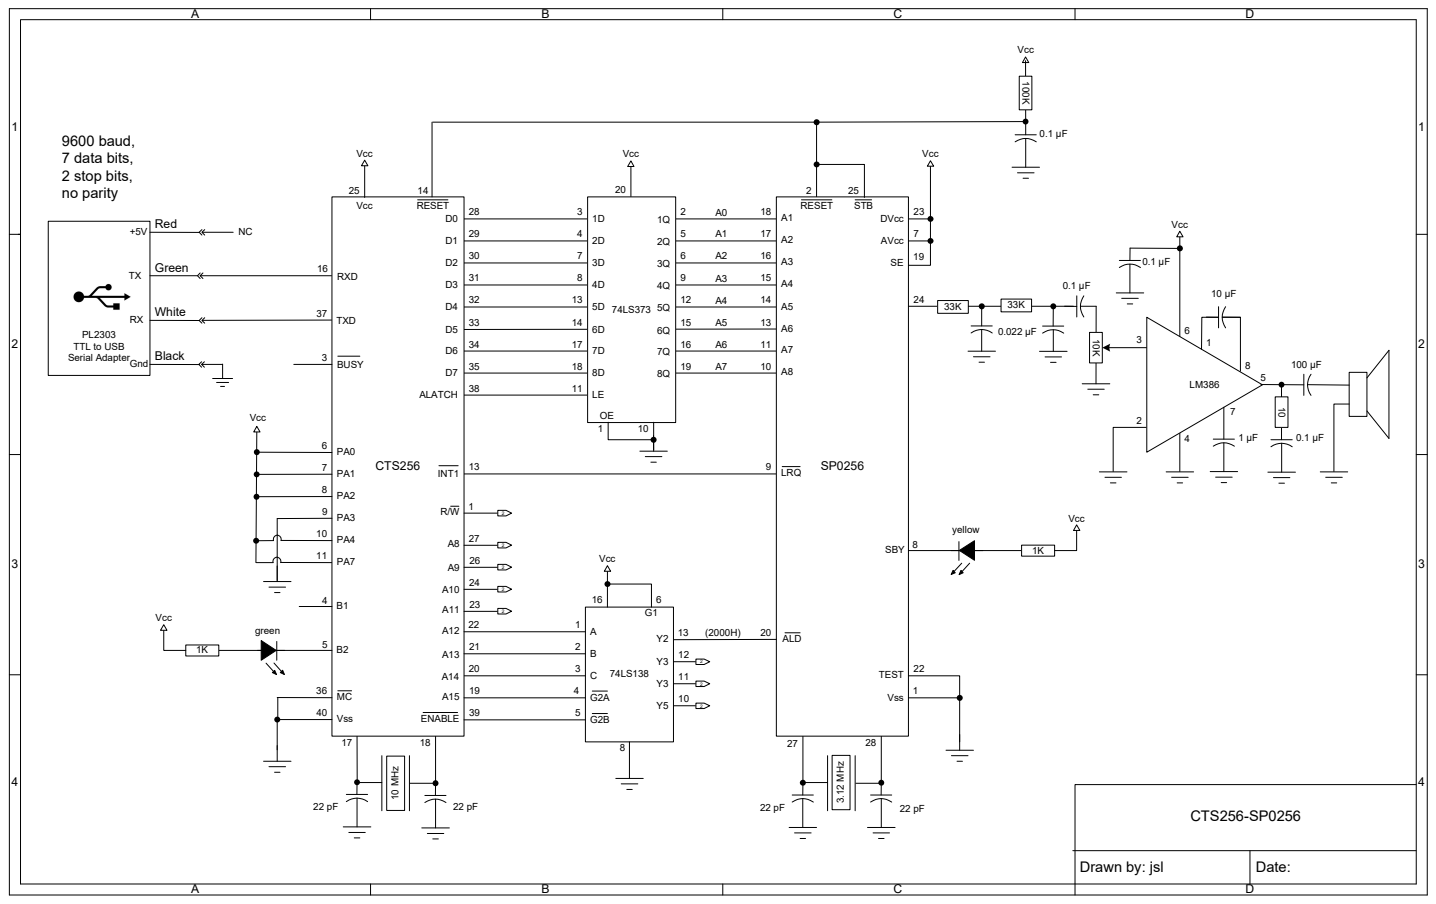
[picture p196: page 1]

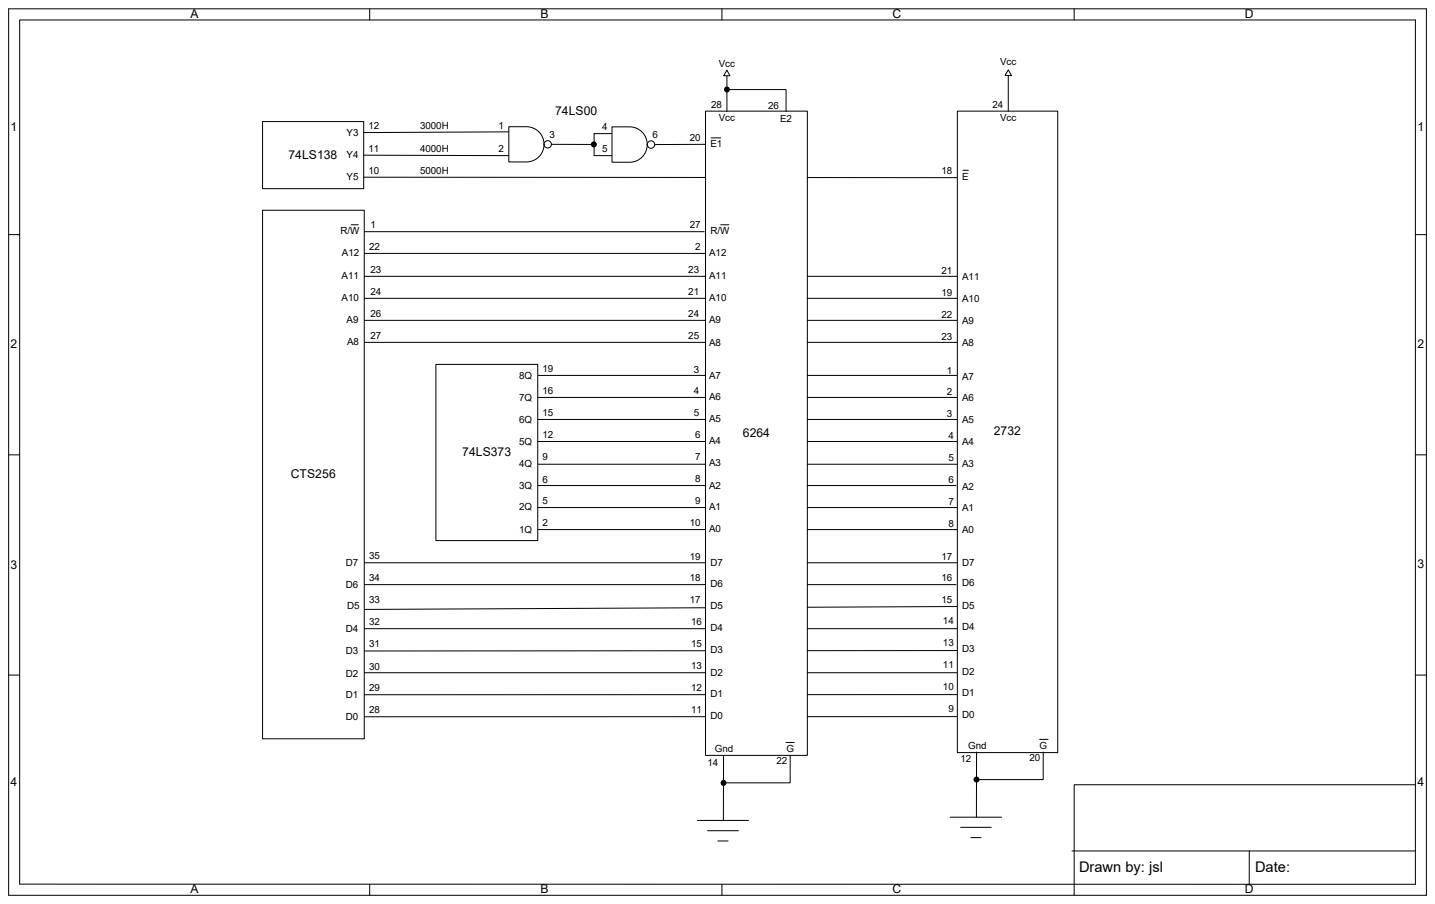
[picture p197: page 2]
