lynchaj/duodyne/13 front-panel.processor ALT/hardware/FrontPanel_ALT_BRD_V1.1.pdf

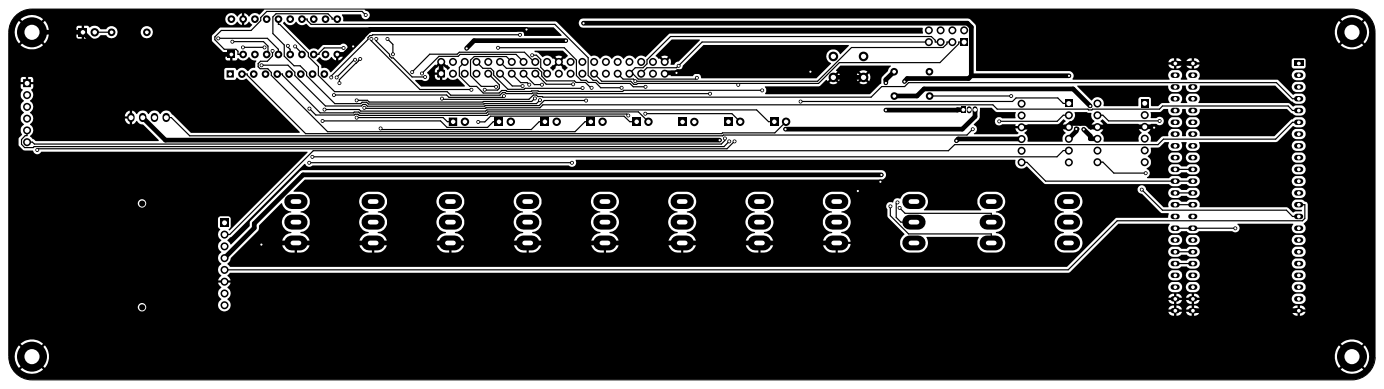
[picture p198: page 1]

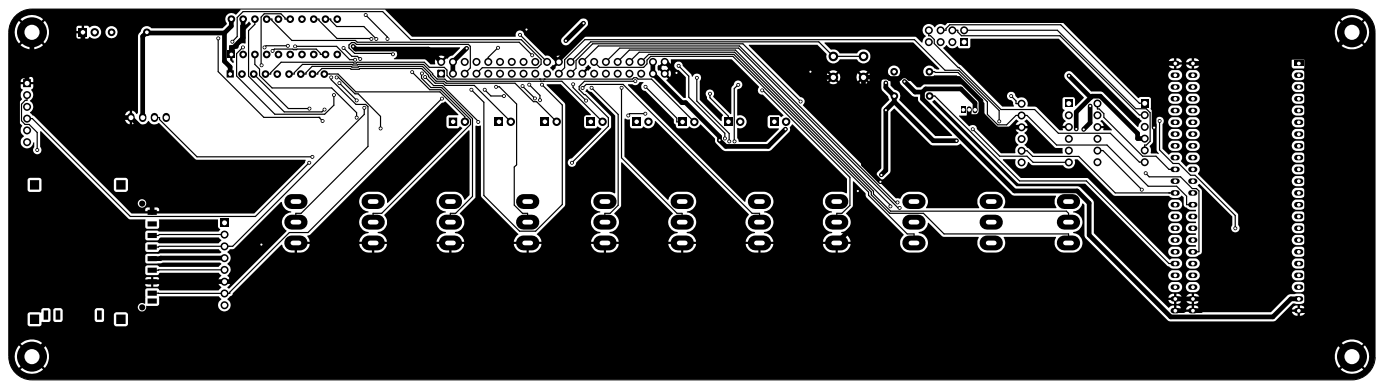
[picture p199: page 2]

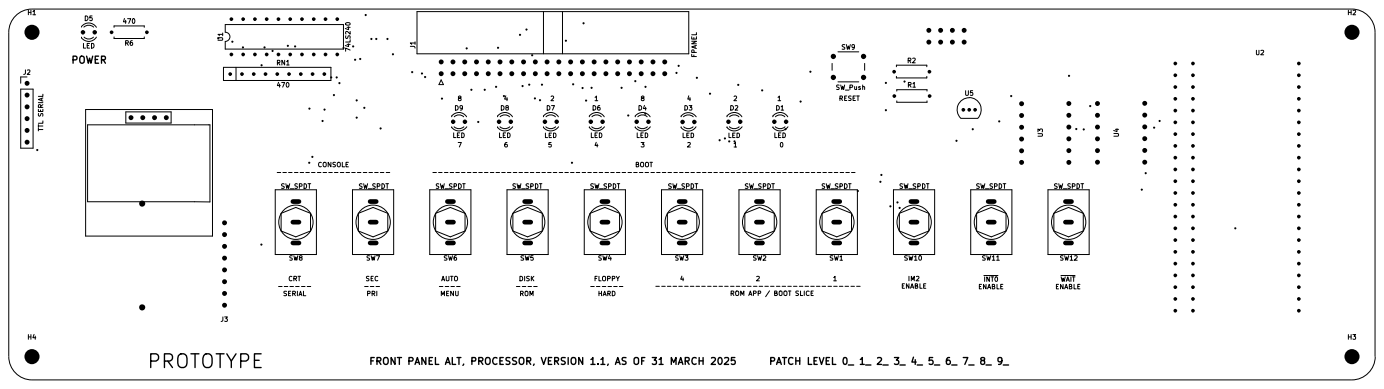
[picture p200: page 3]

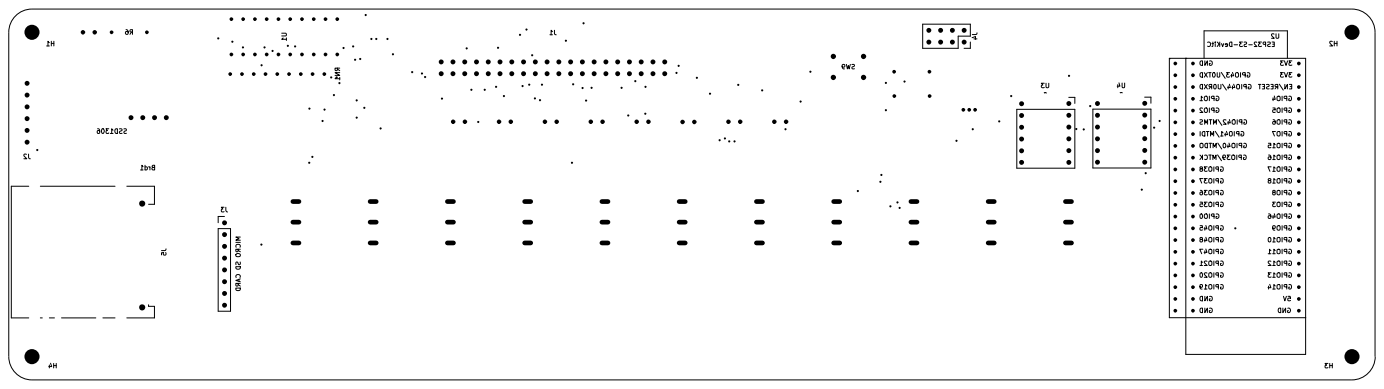
[picture p201: page 4]

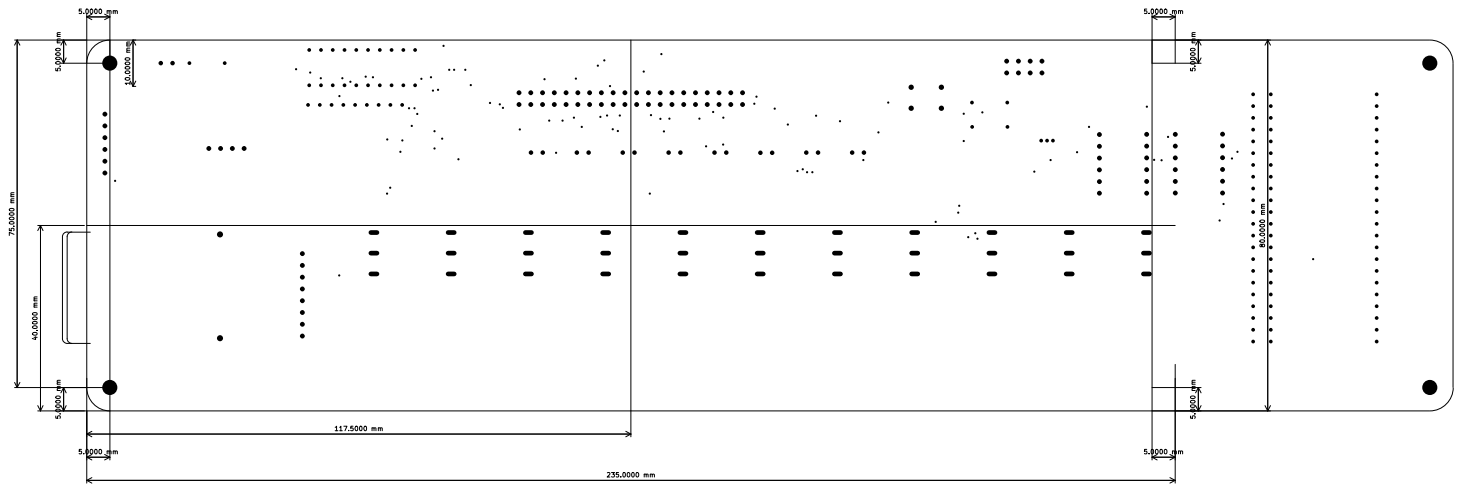
[picture p202: page 5]

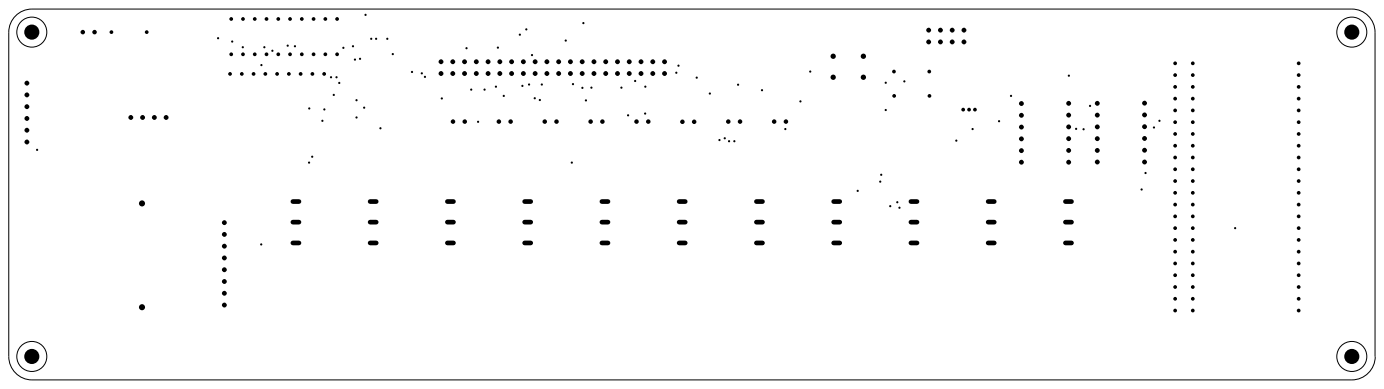
[picture p203: page 6]

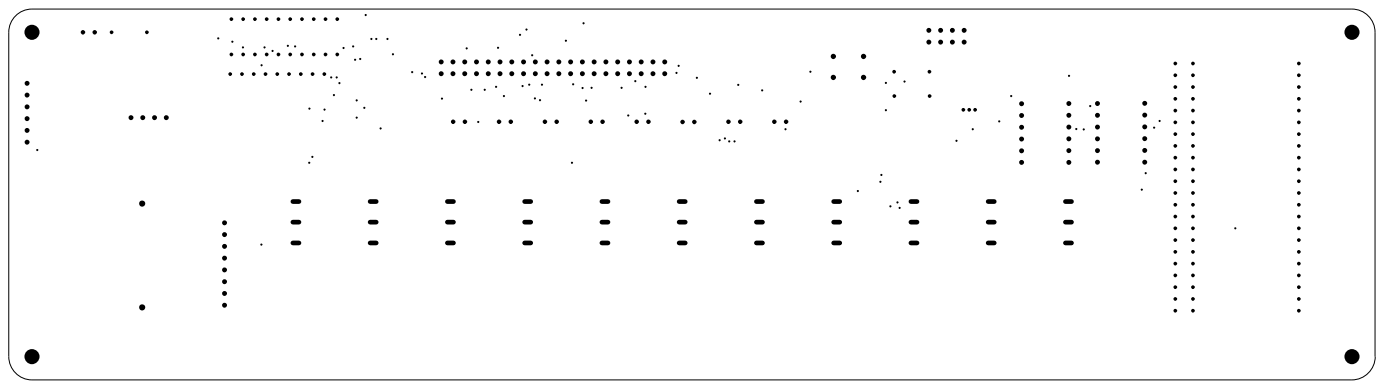
[picture p204: page 7]
