lynchaj/duodyne/13 front-panel.processor ALT/hardware/FrontPanel_ALT_V1.1.pdf

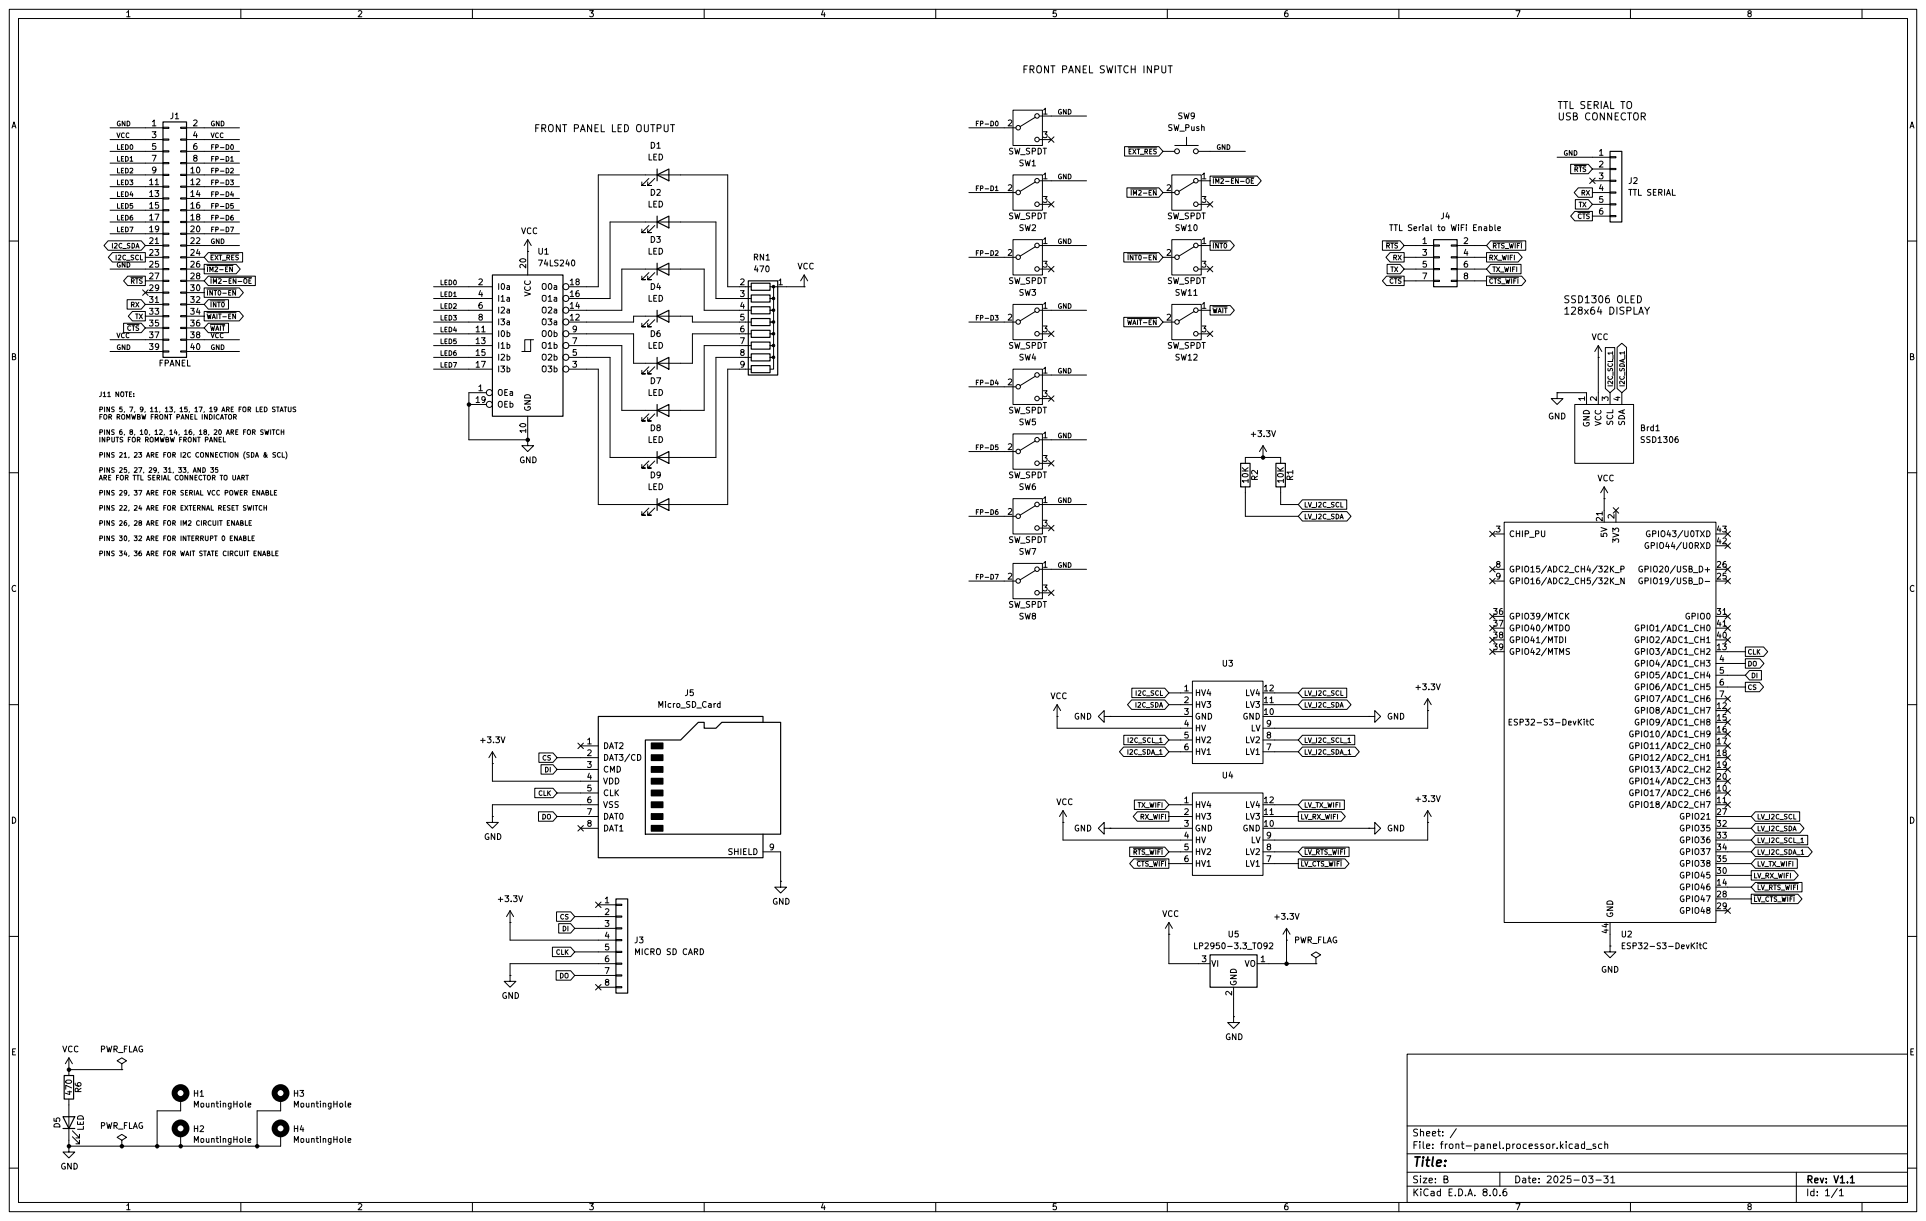
[picture p205: page 1]
