lynchaj/duodyne/20 processor.TMS9995/hardware/processor_TMS9995_PCB_V1.1.pdf

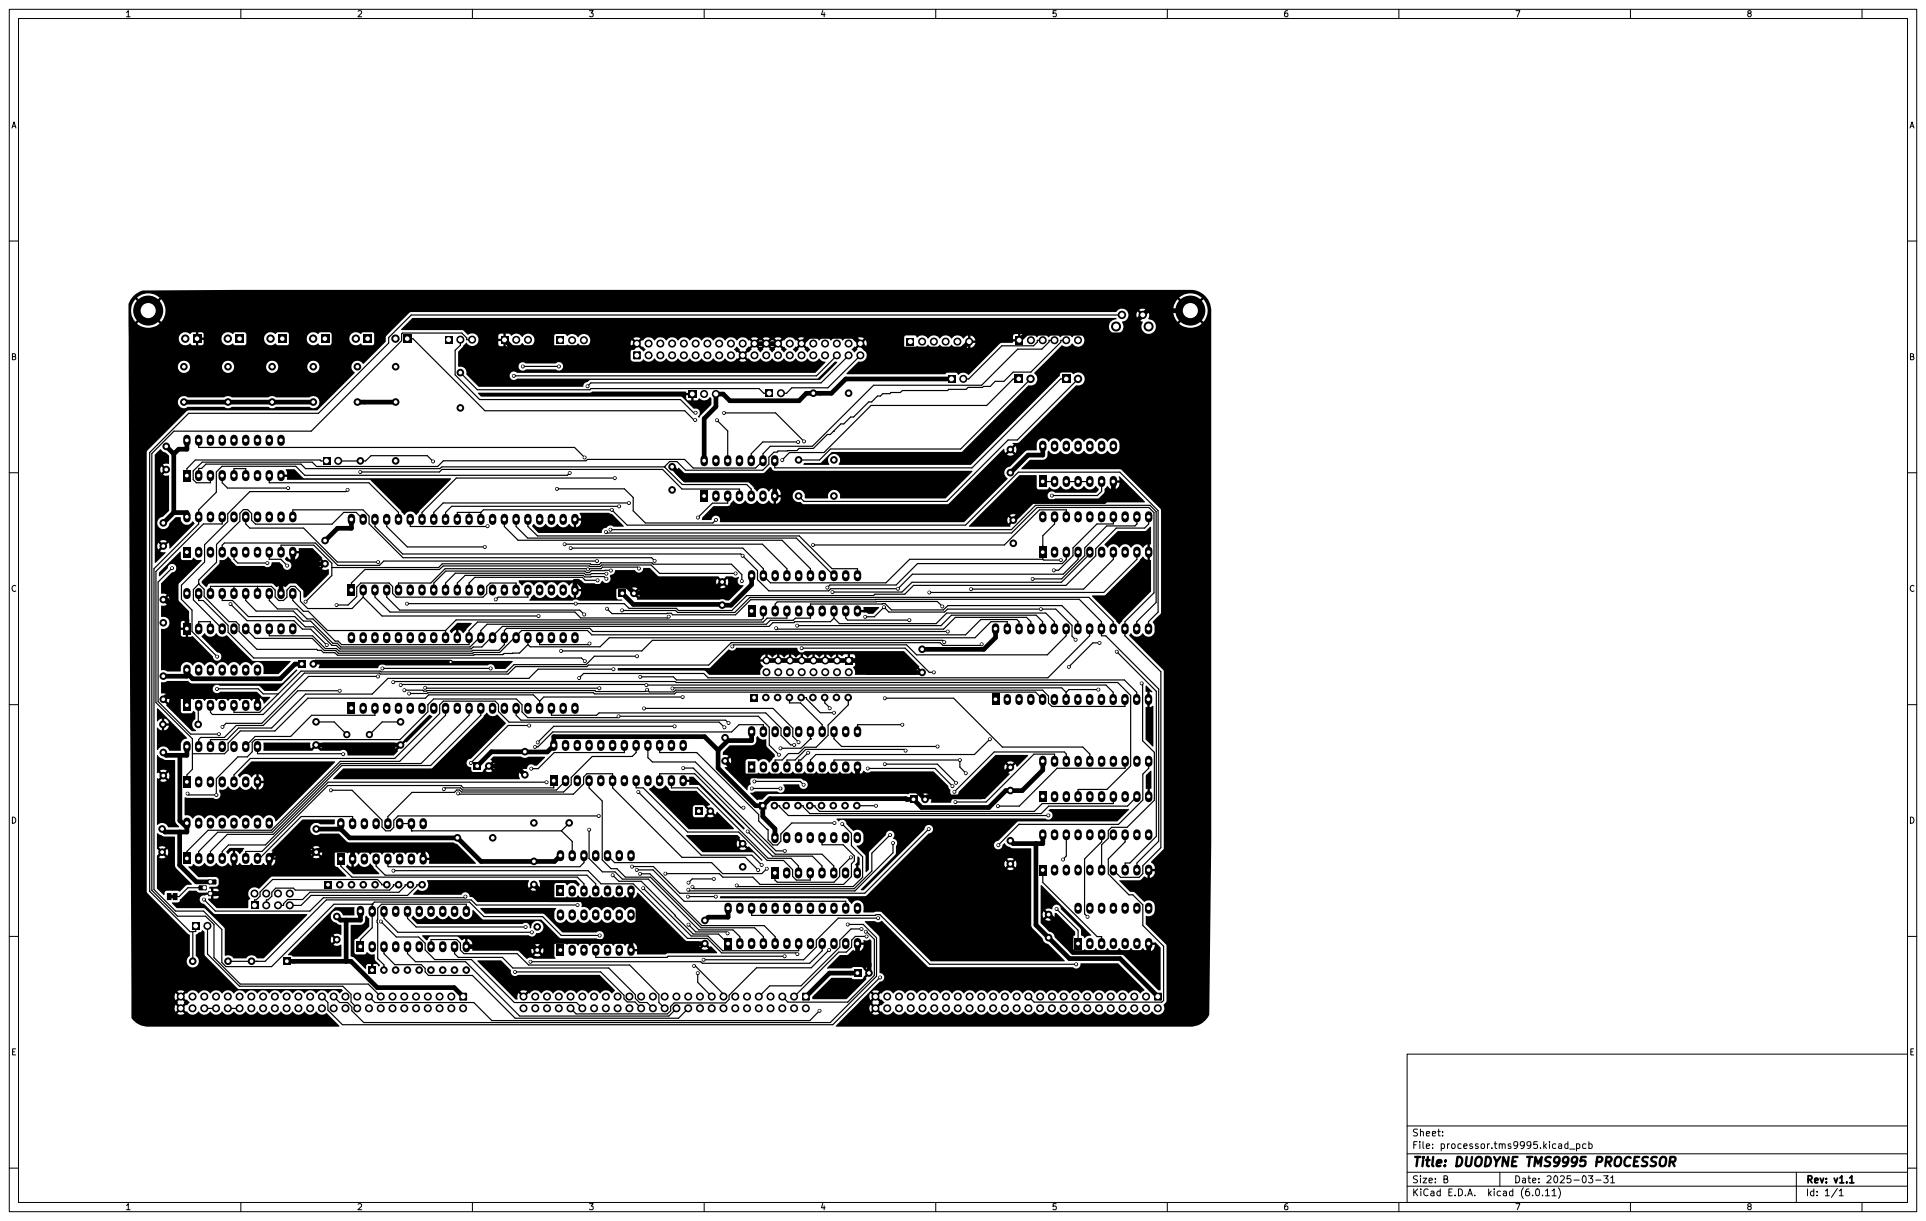
[picture p206: page 1]

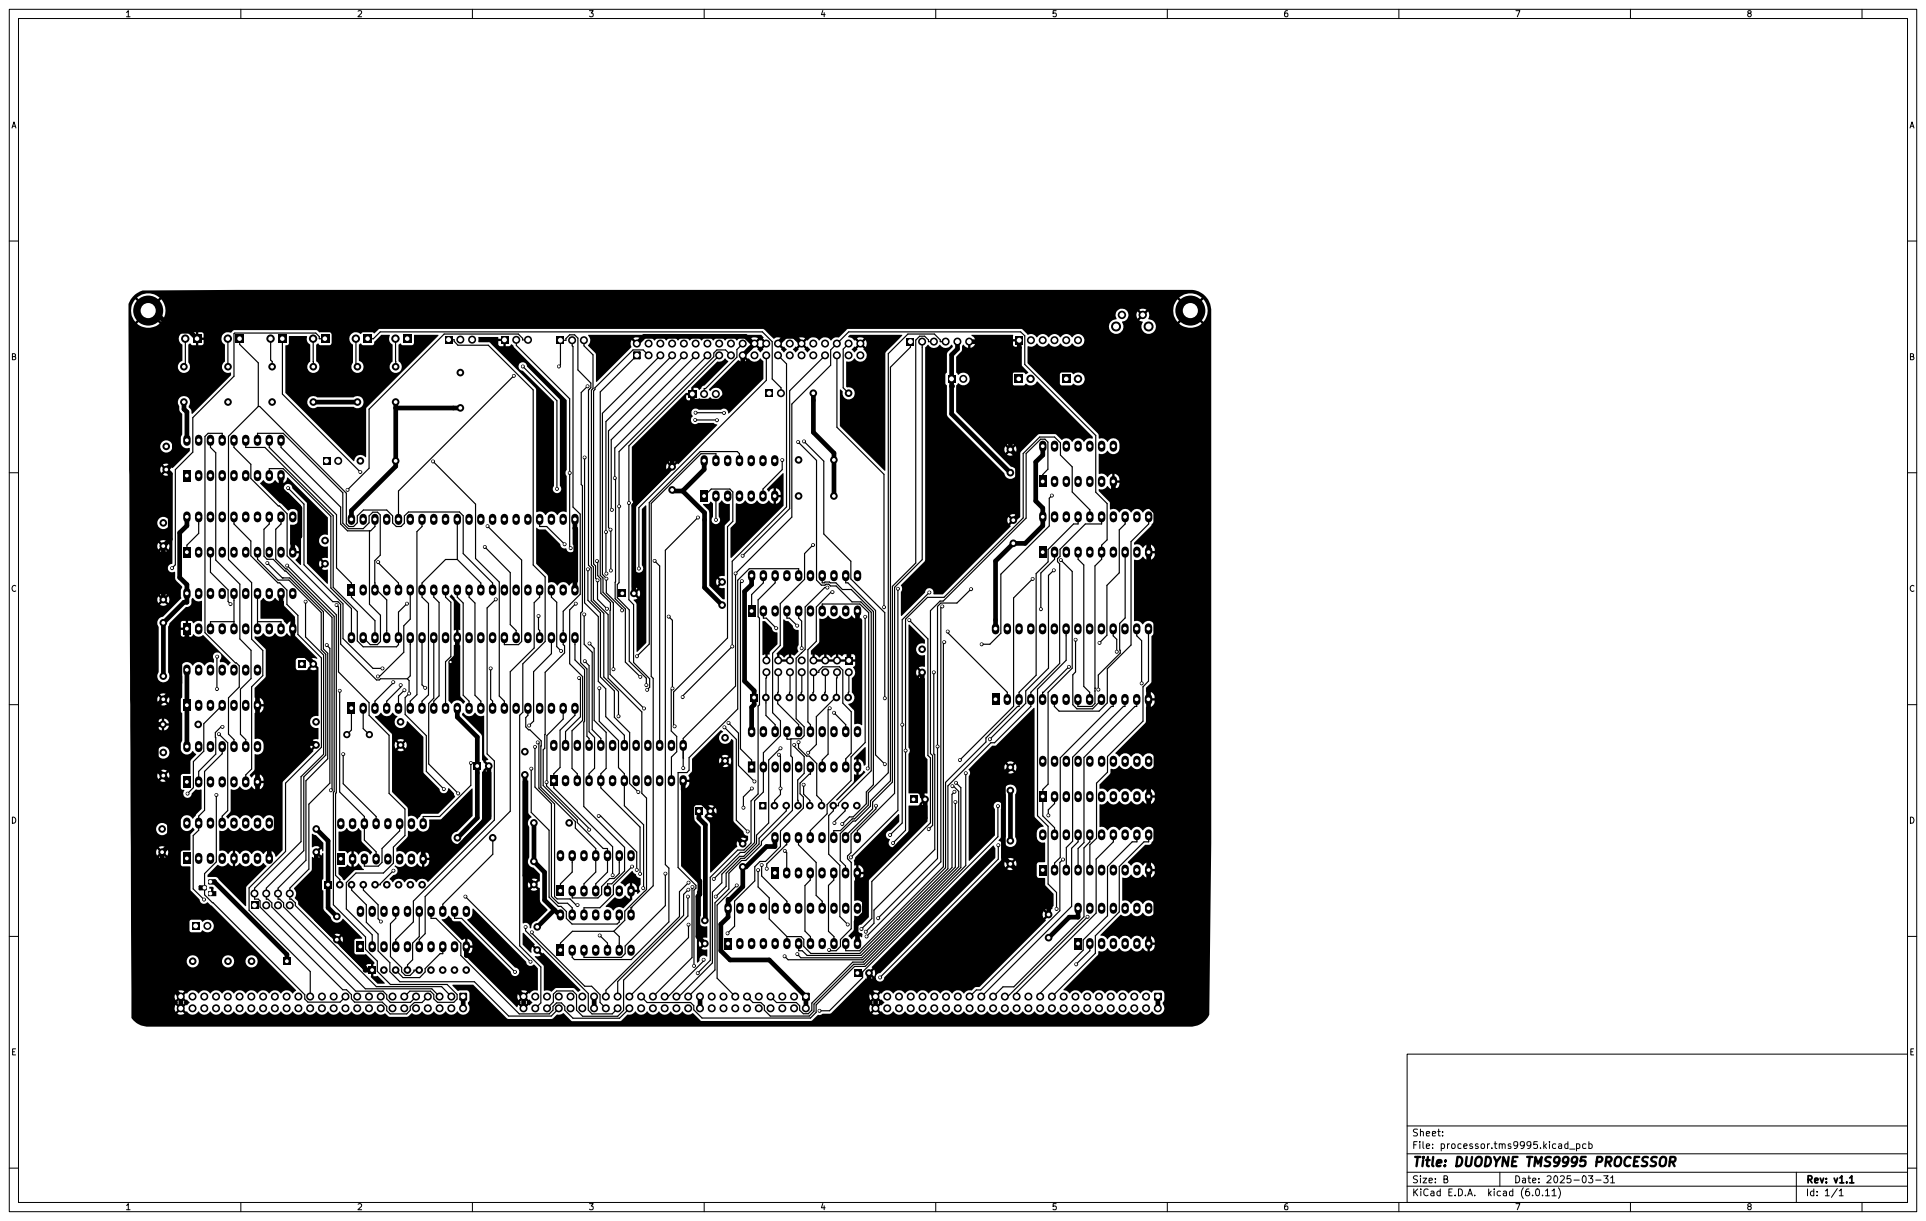
[picture p207: page 2]

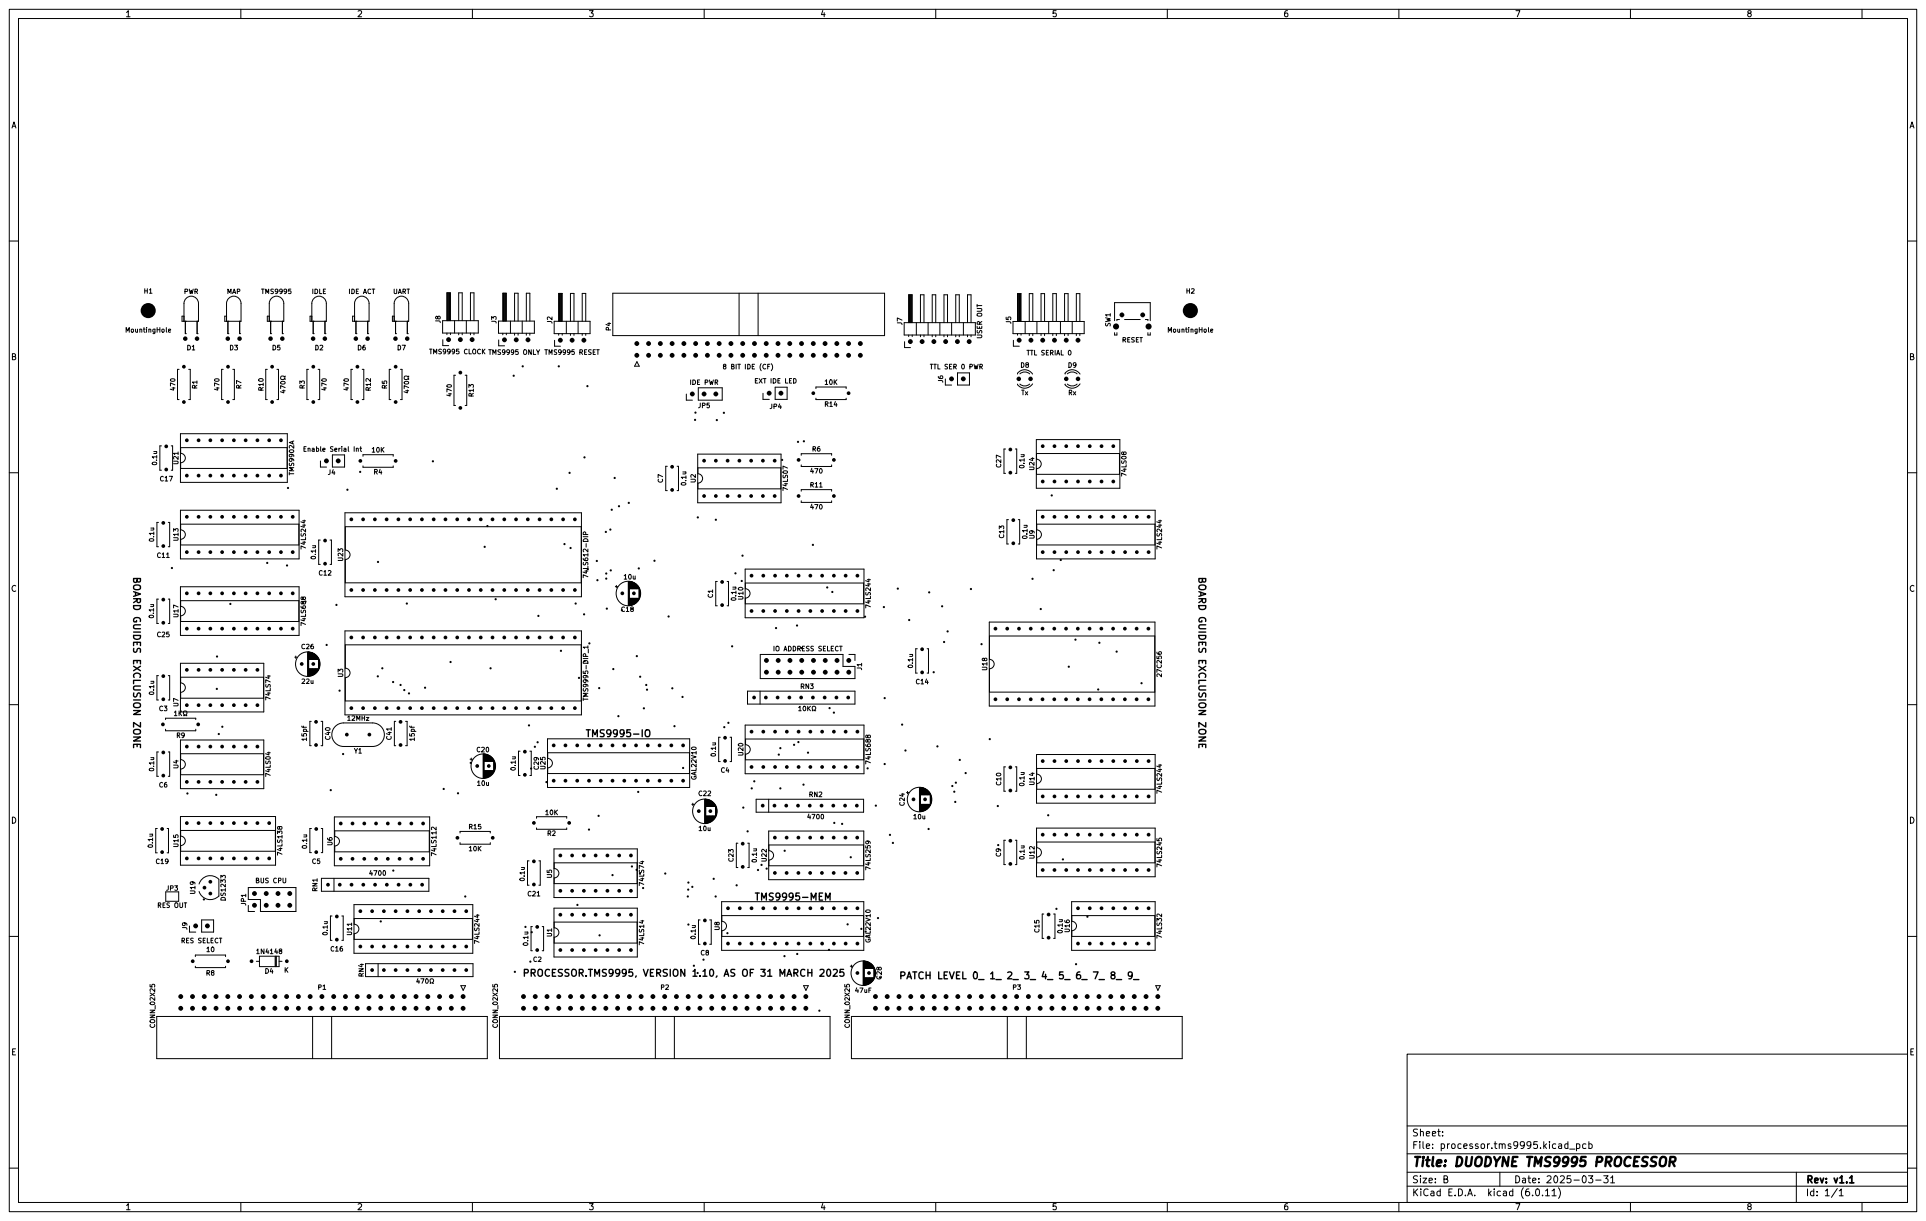
[picture p208: page 3]

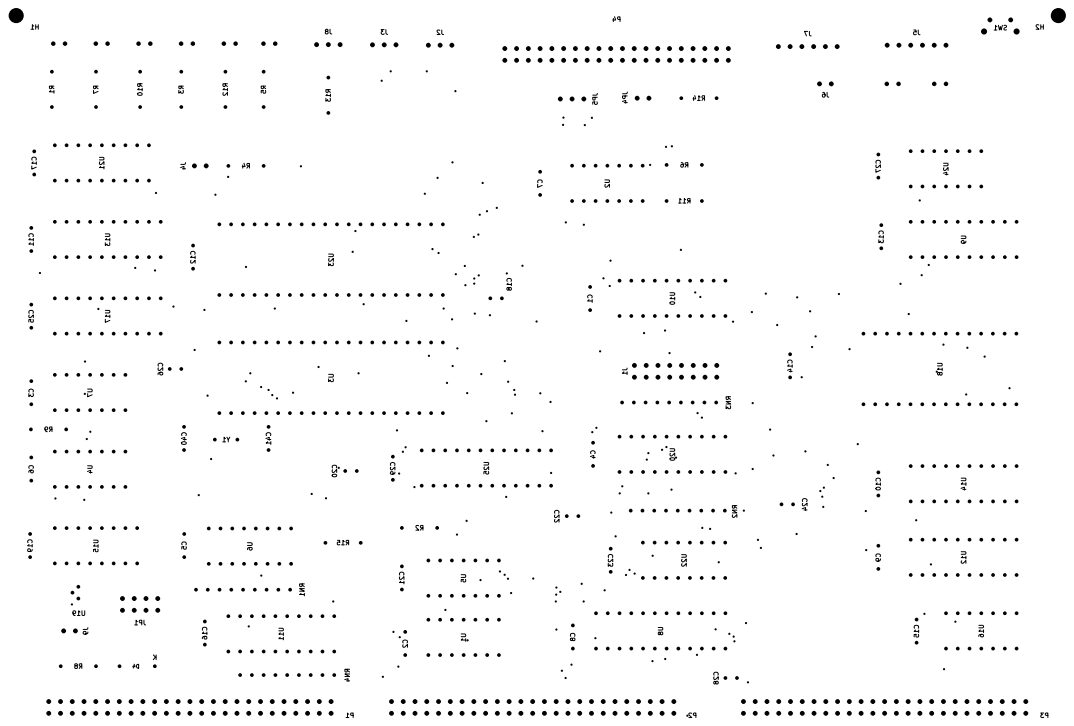
[picture p209: page 4]

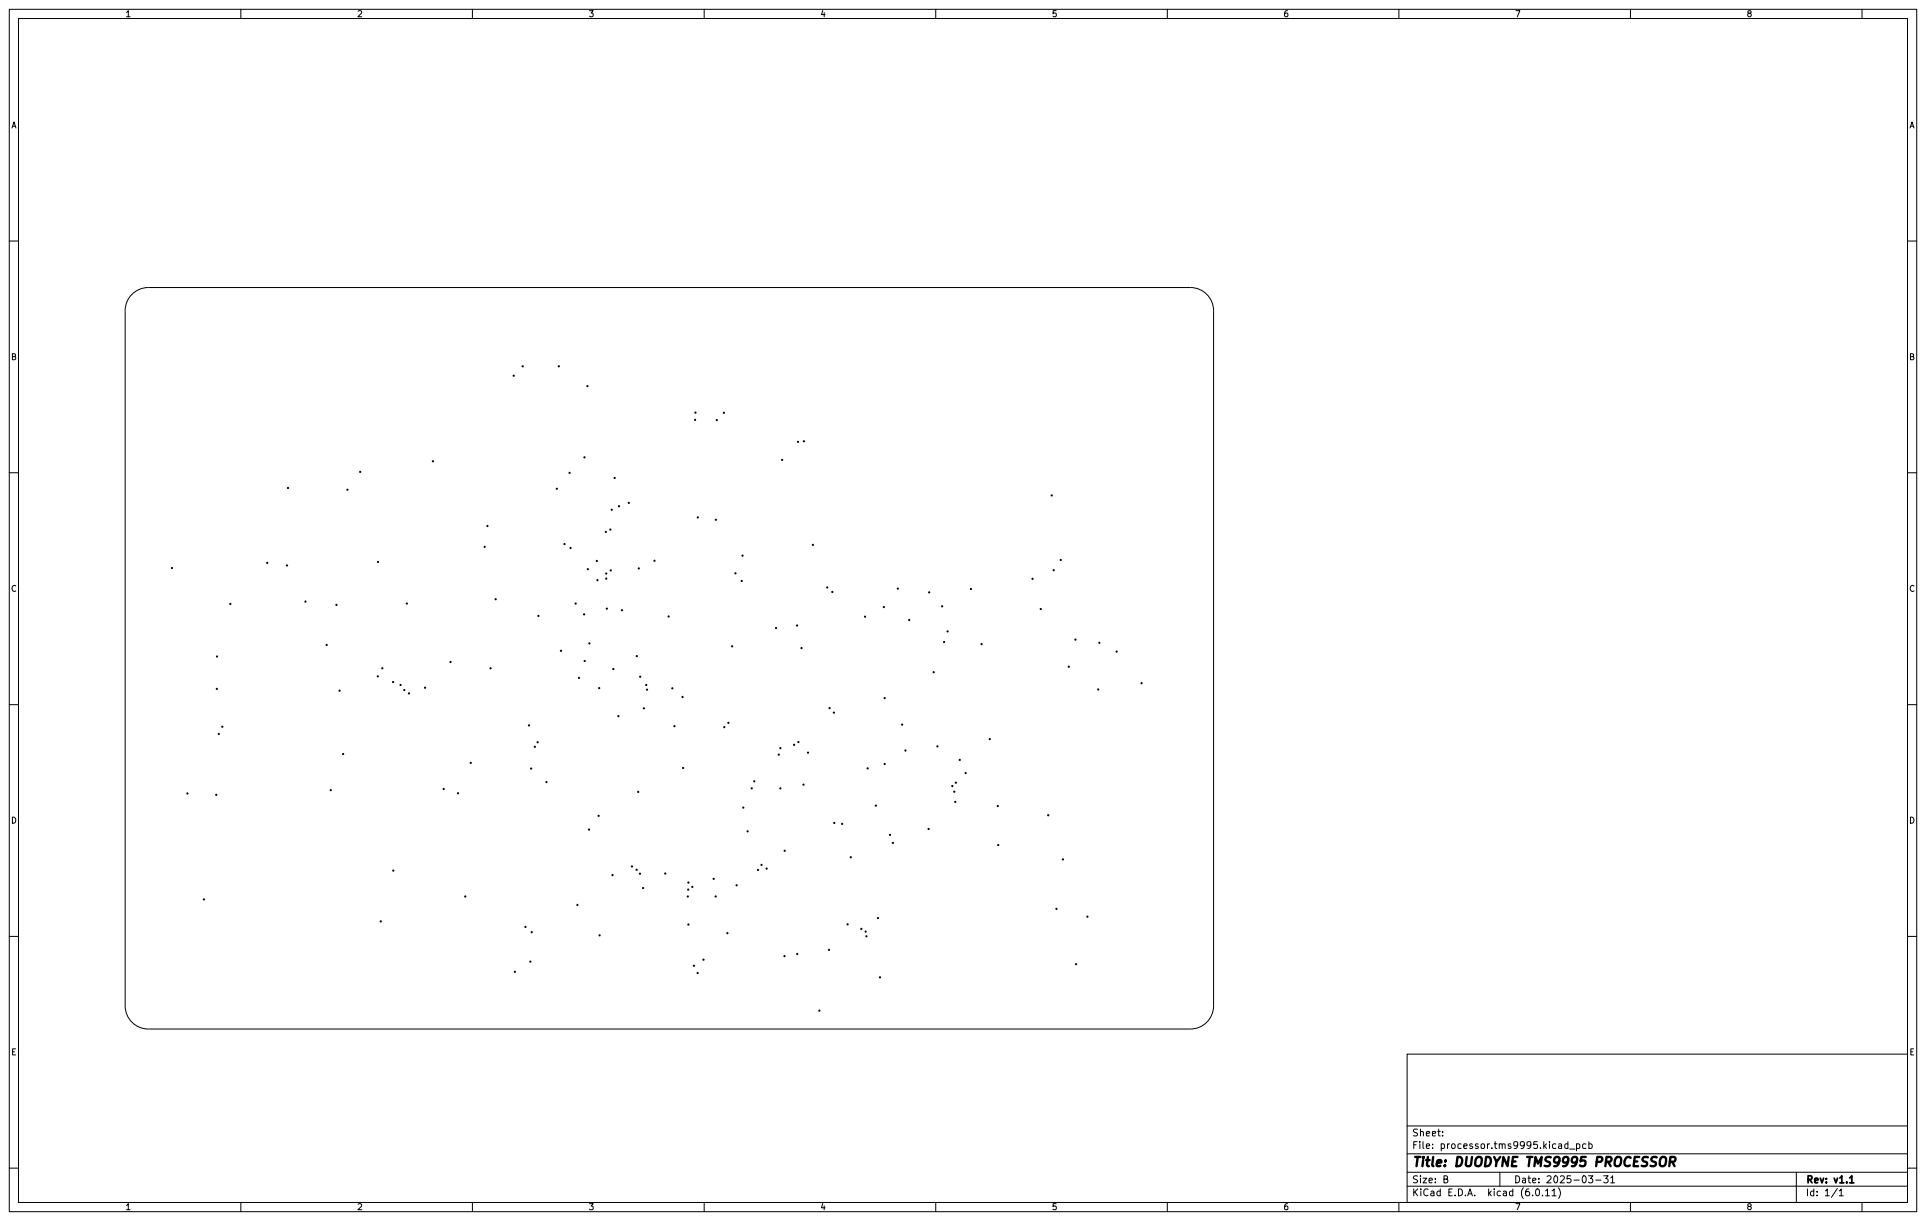
[picture p210: page 5]

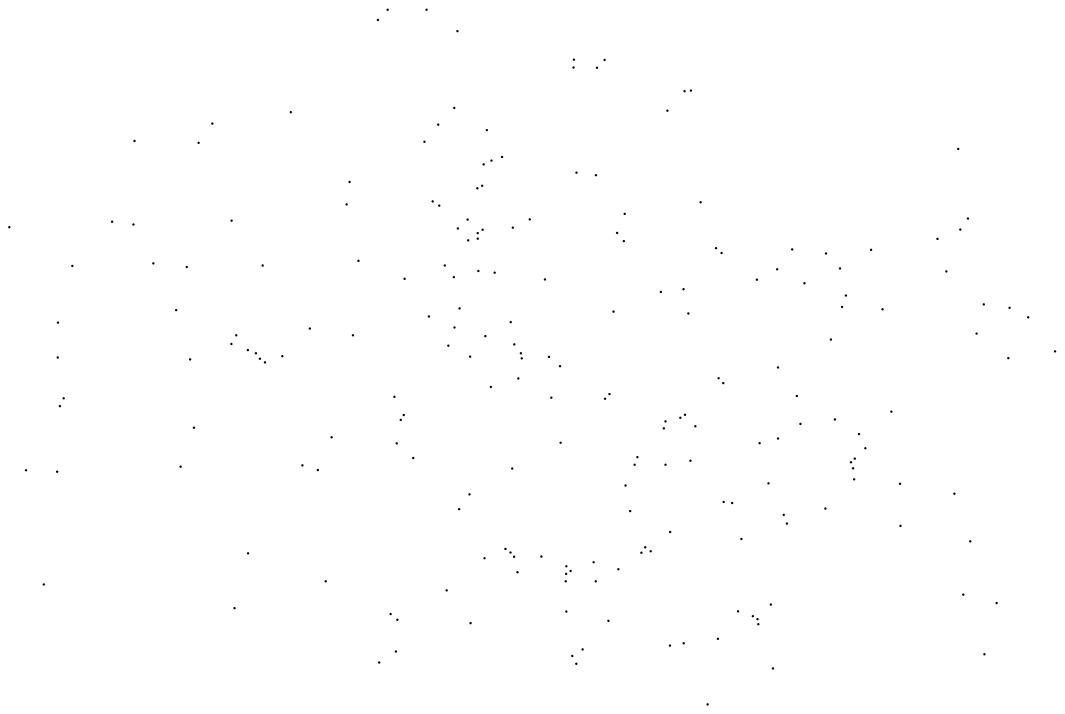
[picture p211: page 6]

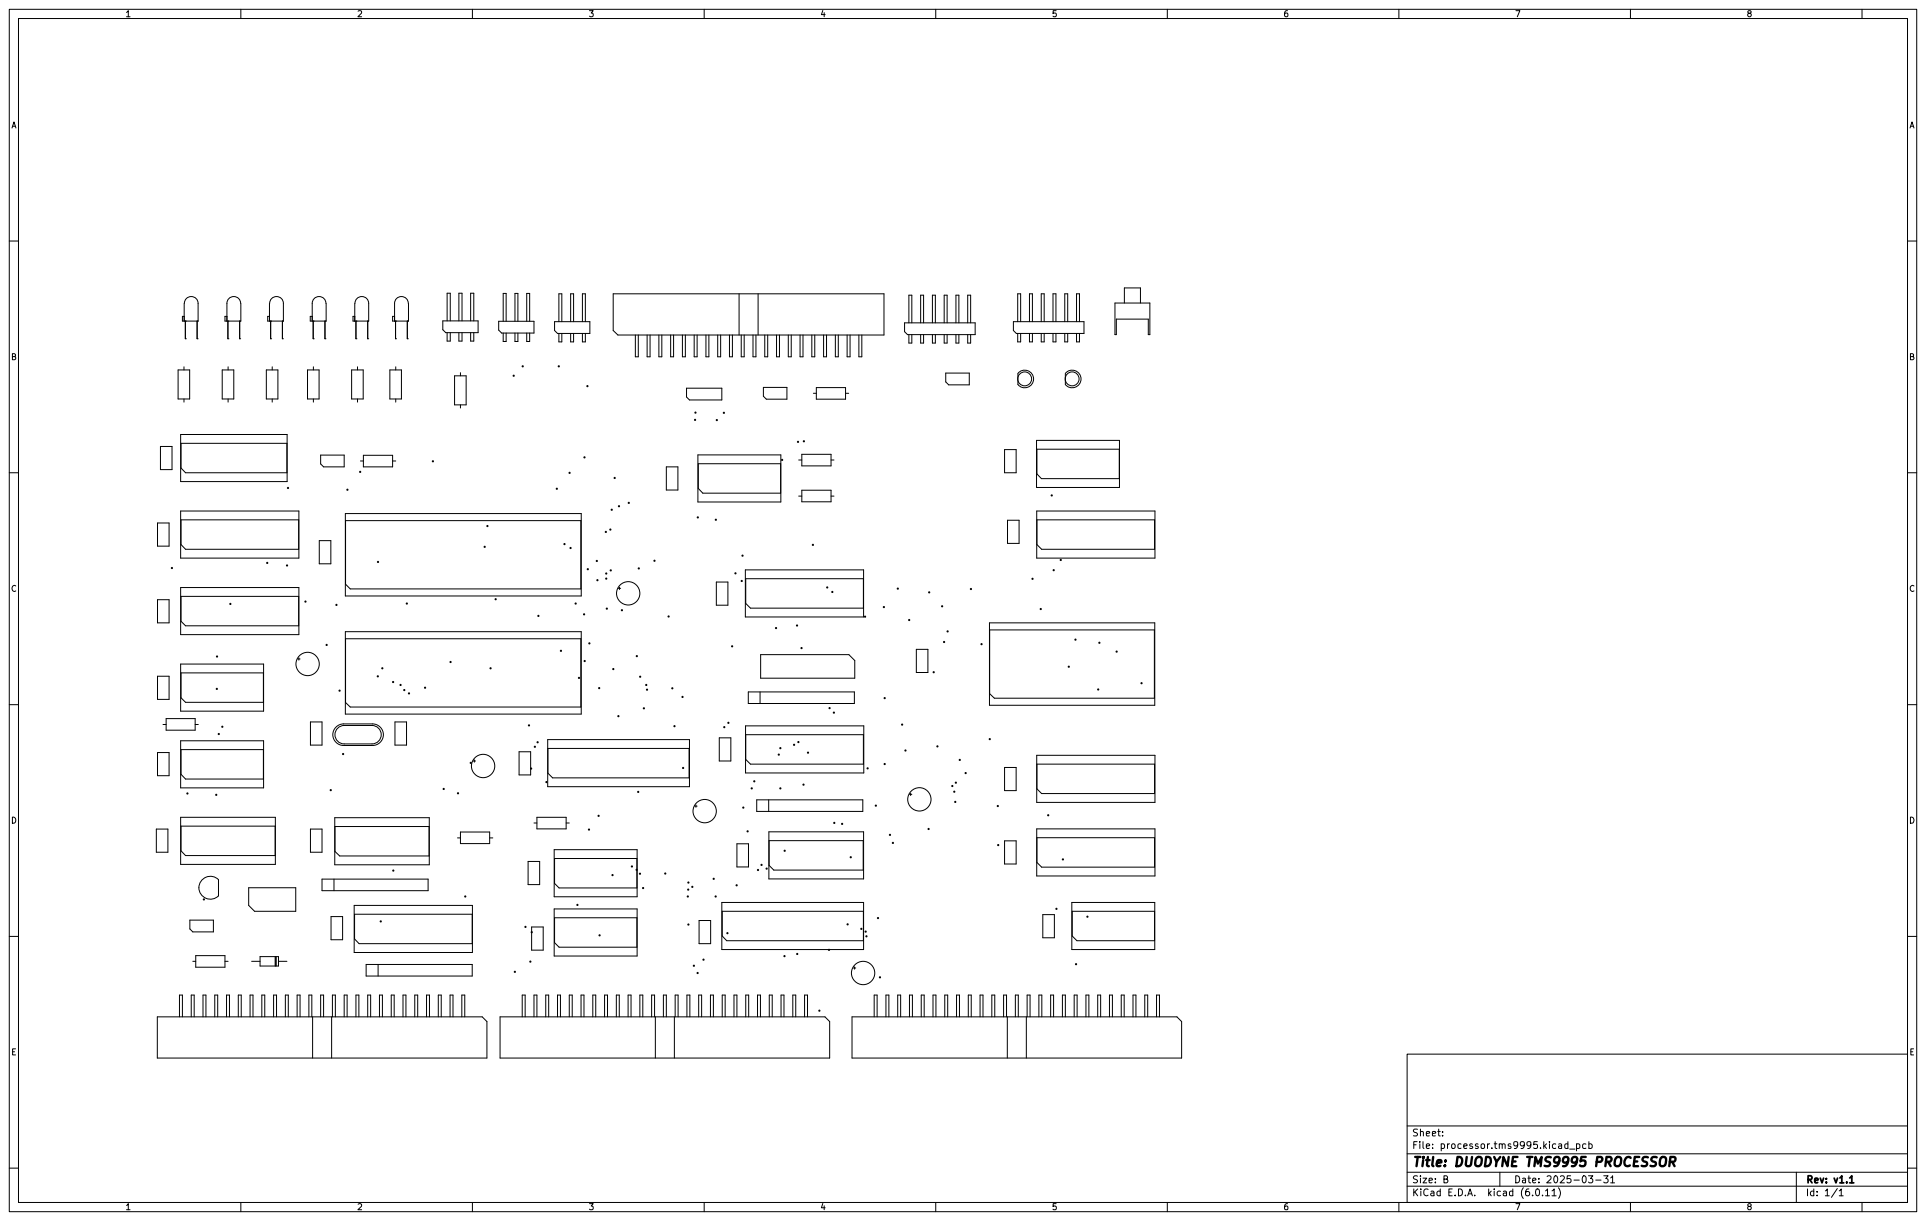
[picture p212: page 7]
