lynchaj/duodyne/20 processor.TMS9995/hardware/processor_TMS9995_SCHEMATIC_V1.1.pdf

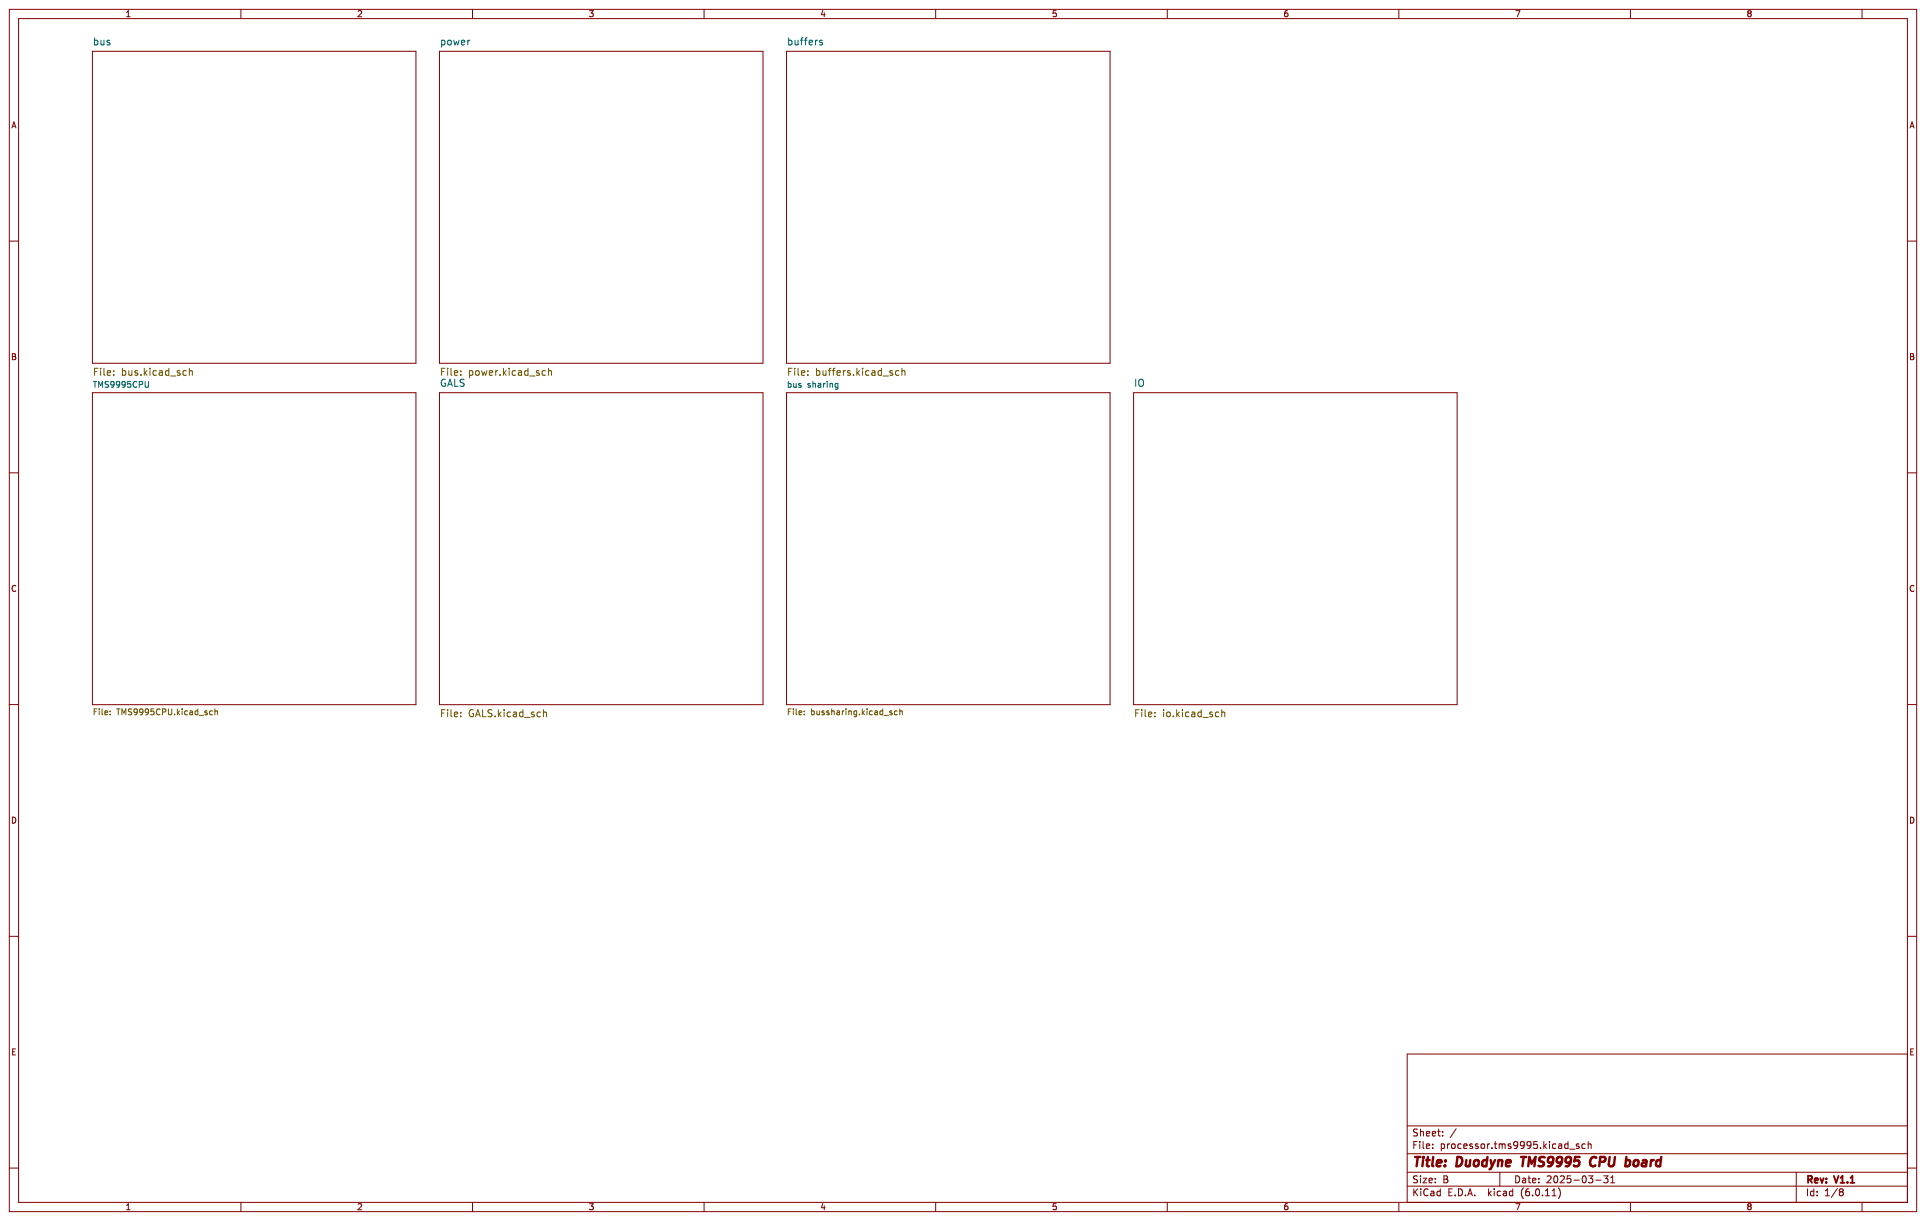
[picture p213: page 1]

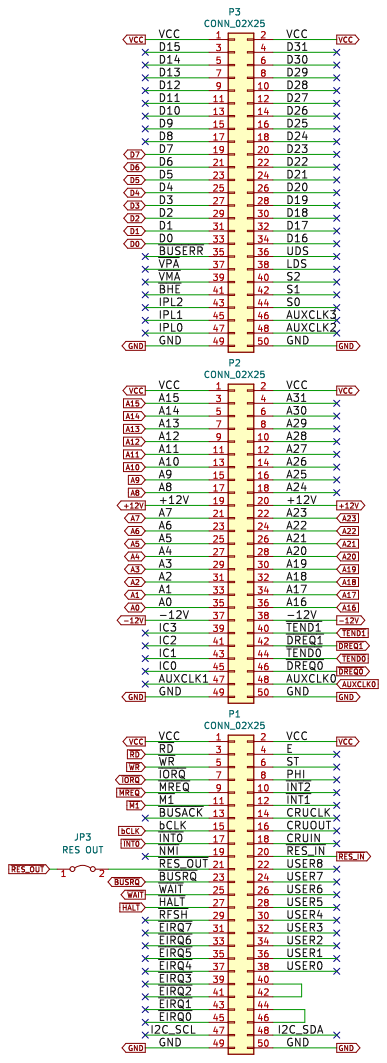
[picture p214: page 2]

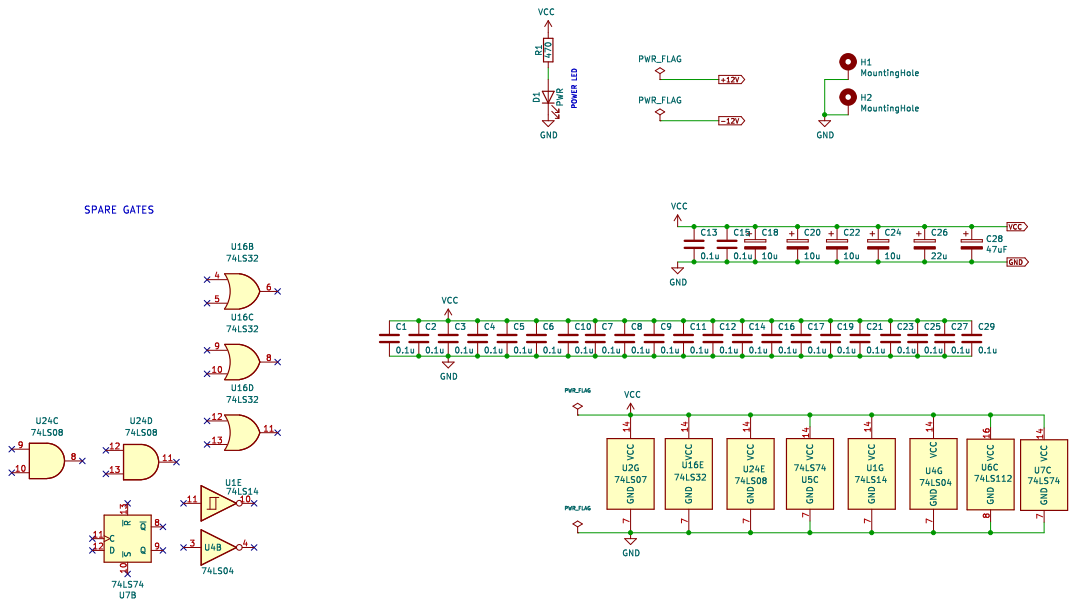
[picture p215: page 3]

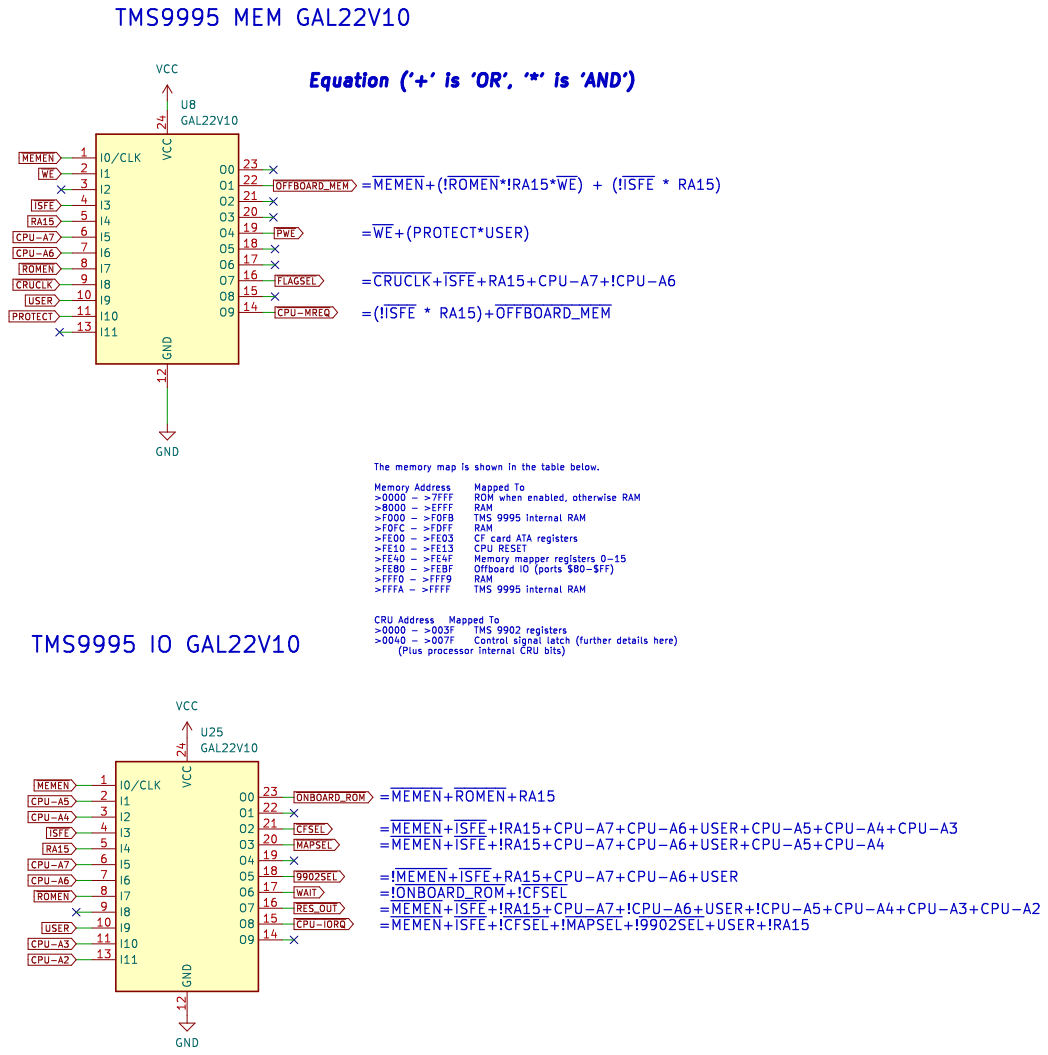
[picture p216: page 4]

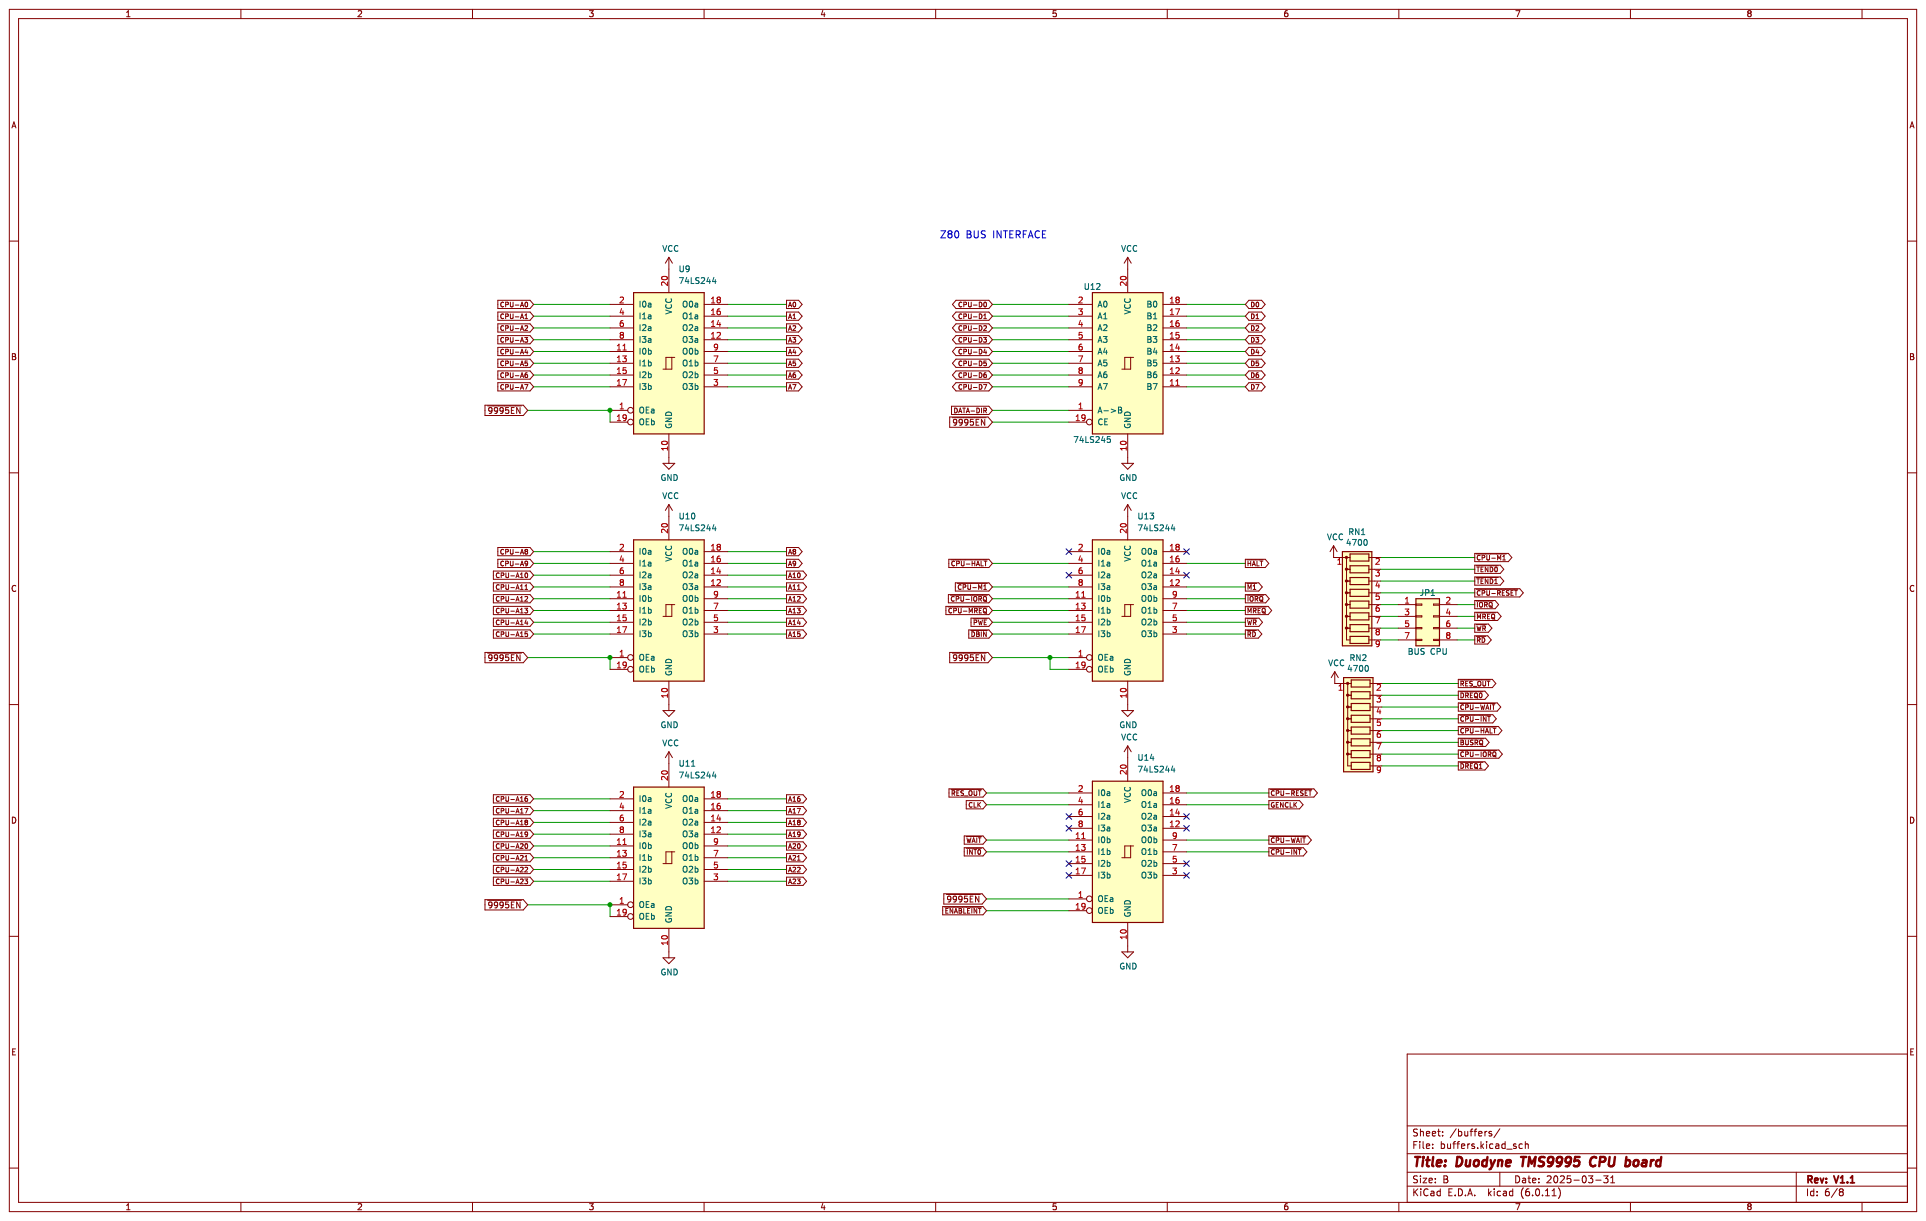
[picture p217: page 5]

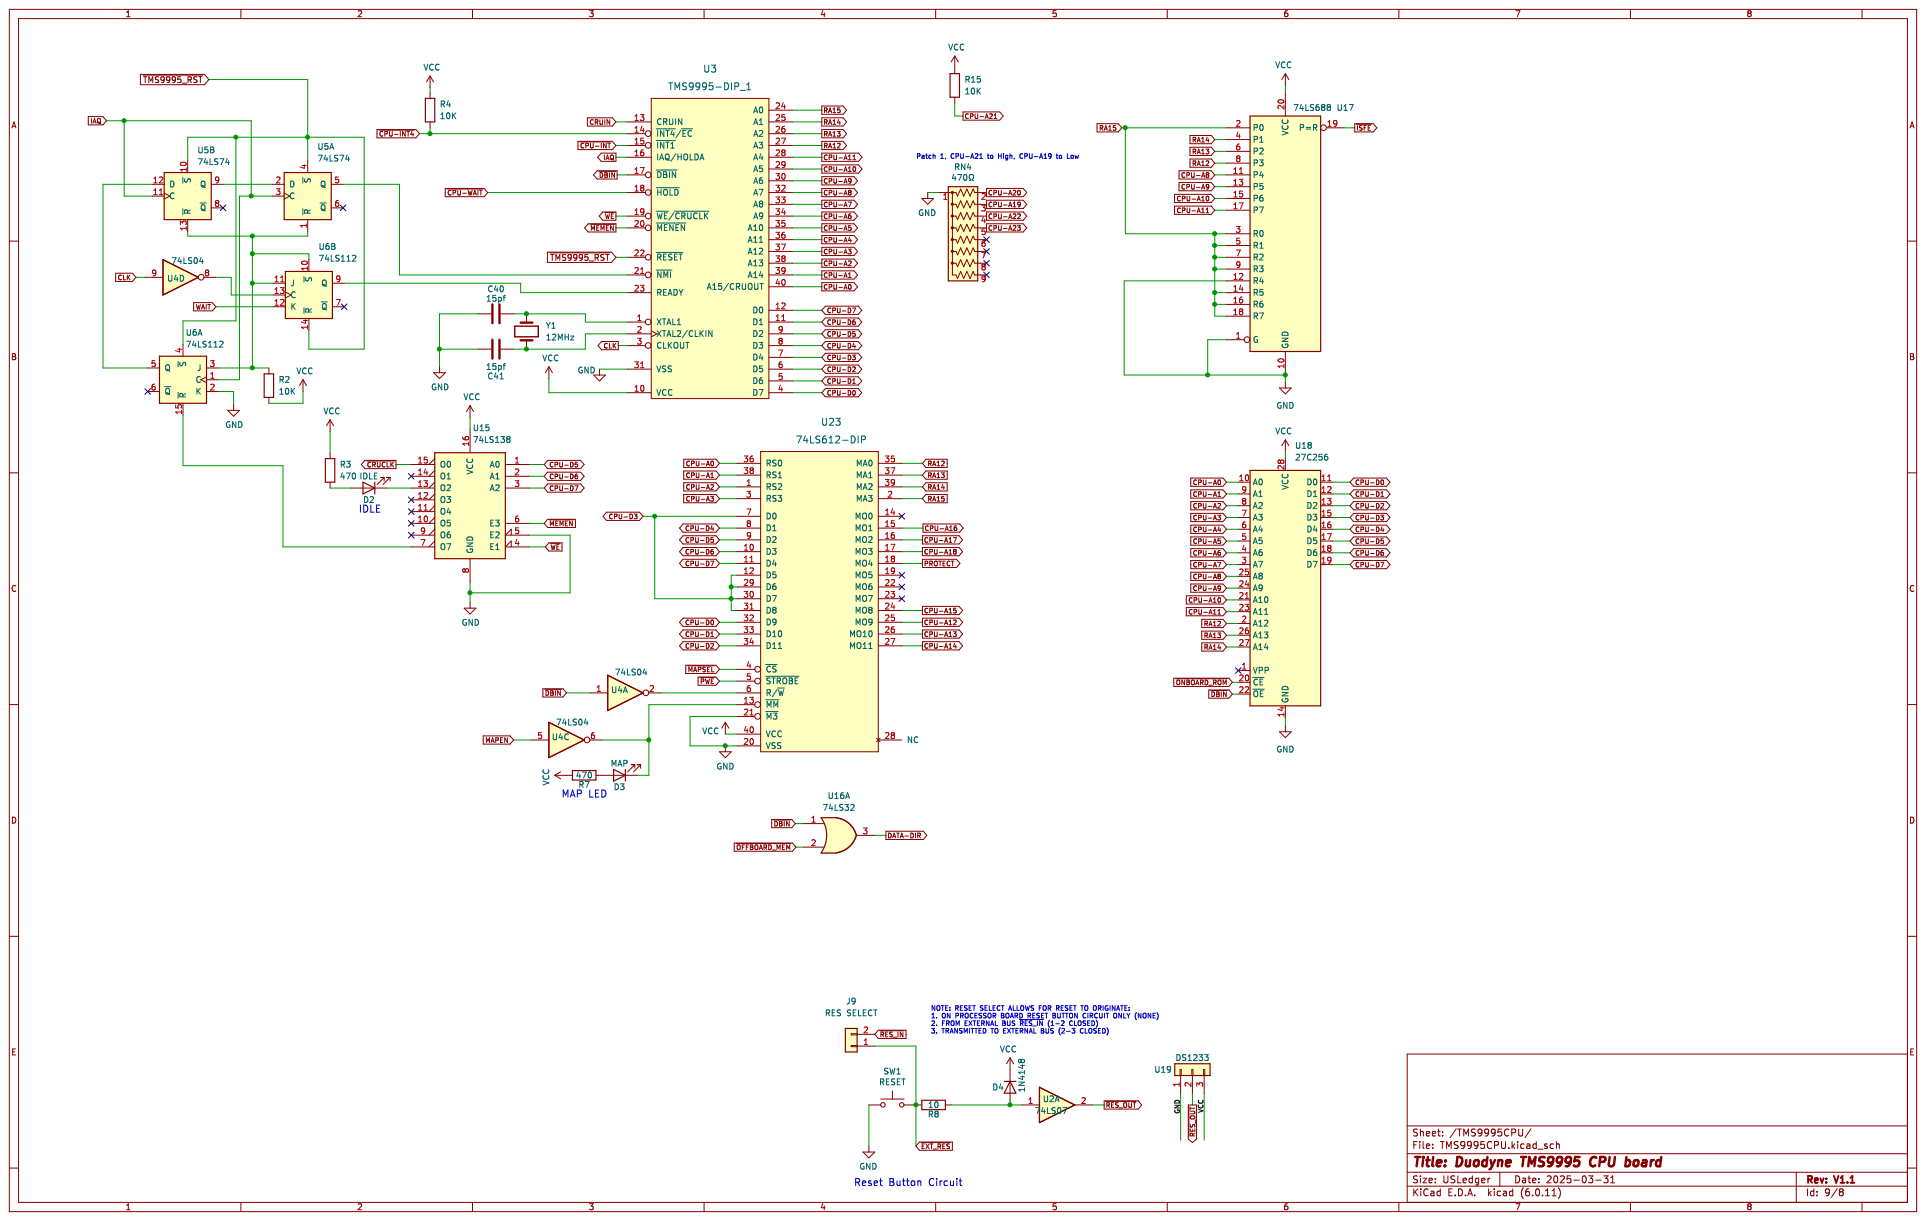
[picture p218: page 6]

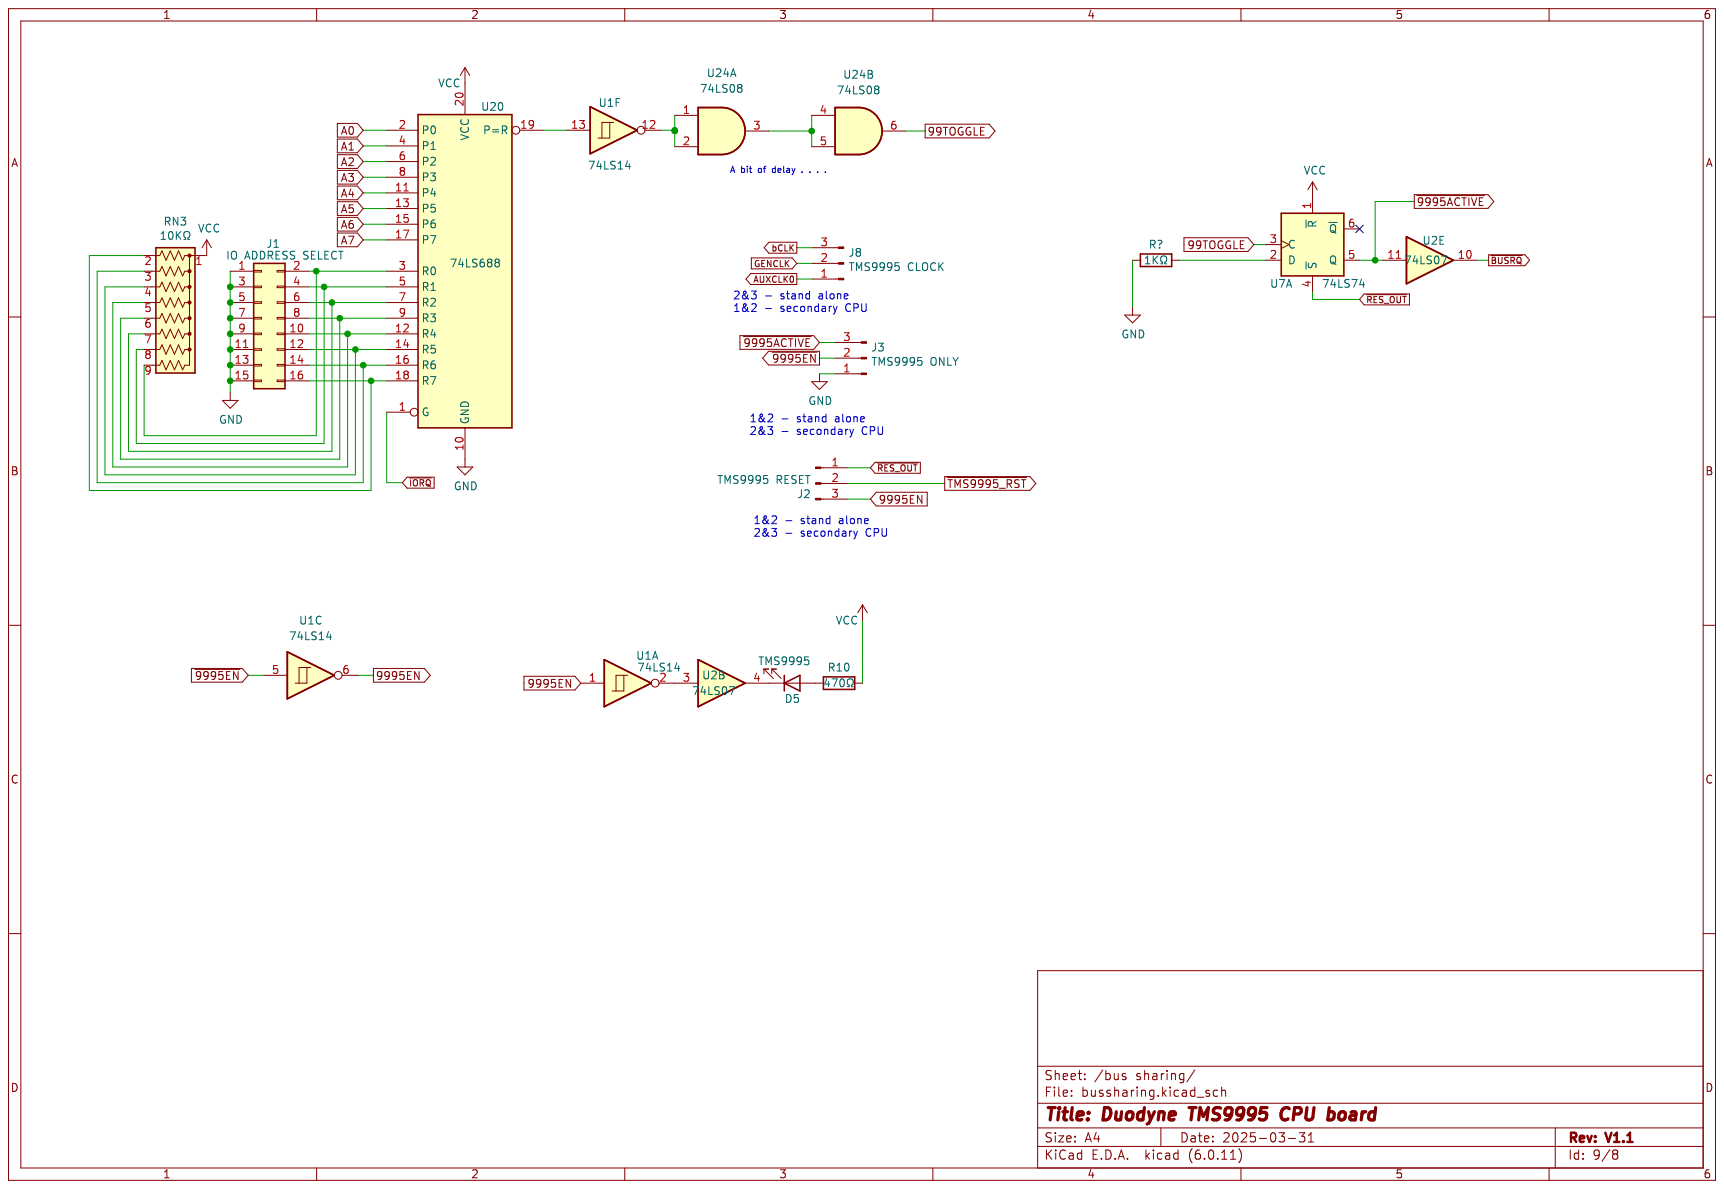
[picture p219: page 7]

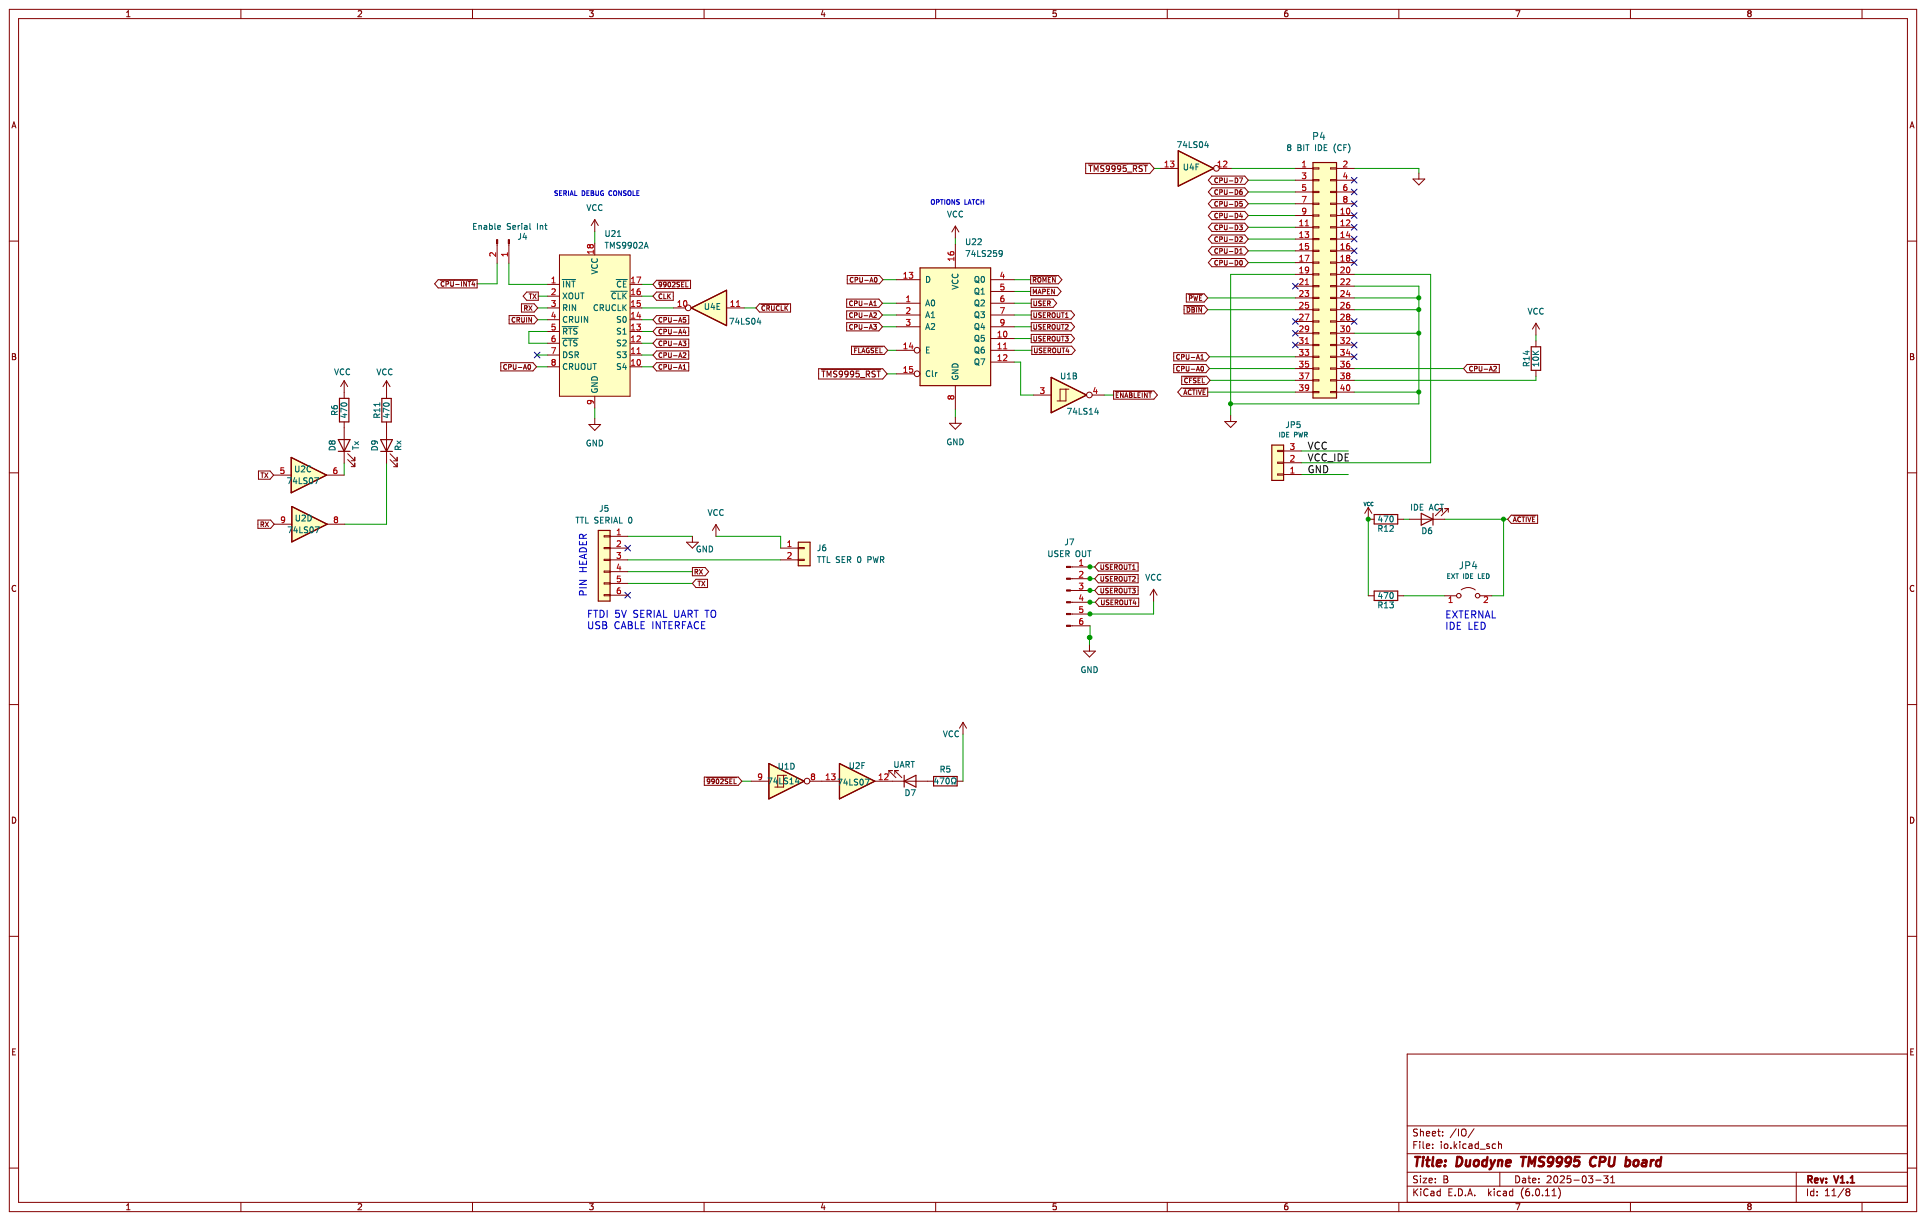
[picture p220: page 8]
