lynchaj/duodyne/25 processor.80c188/hardware/PROCESSOR.80C188.PCB-v0.90.pdf

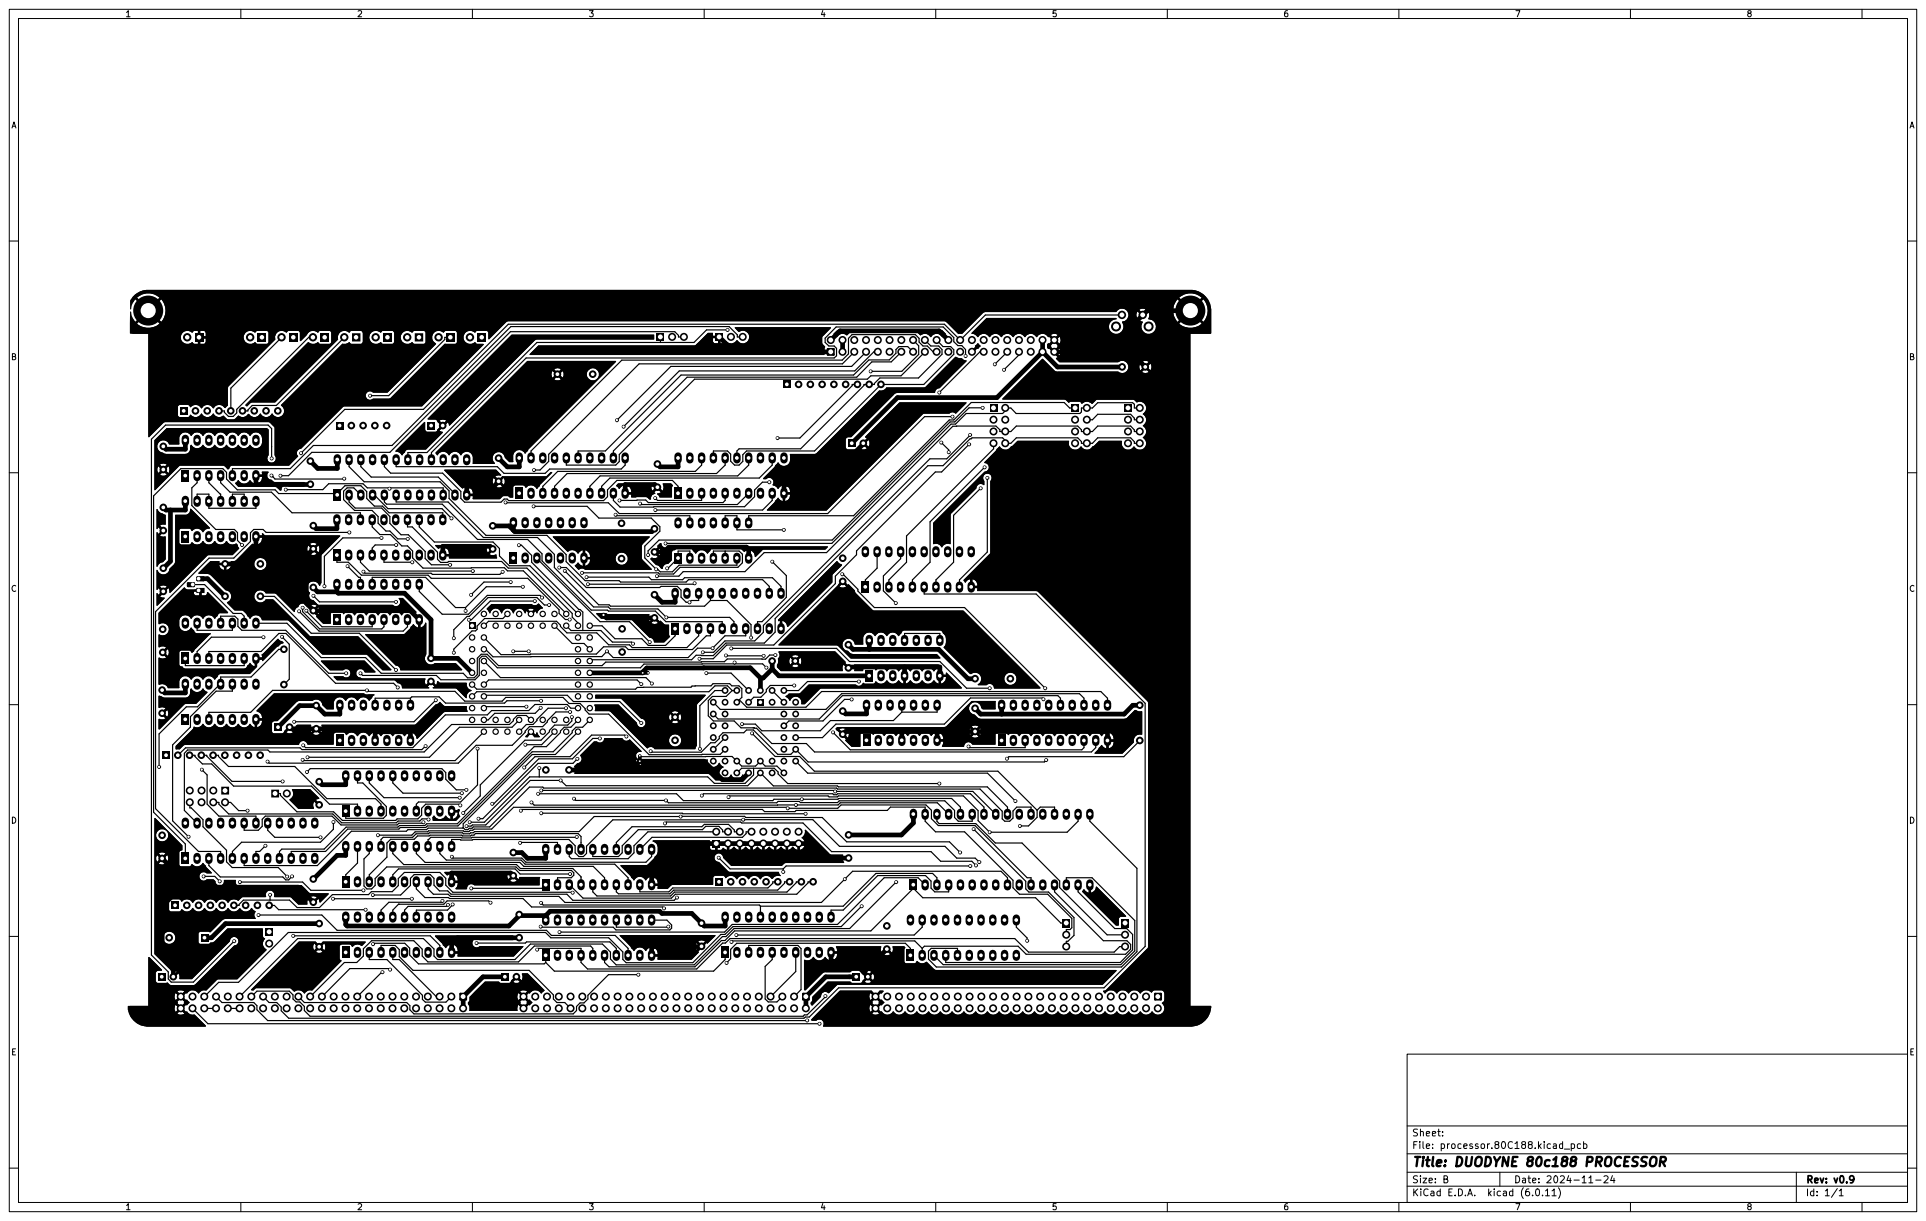
[picture p221: page 1]

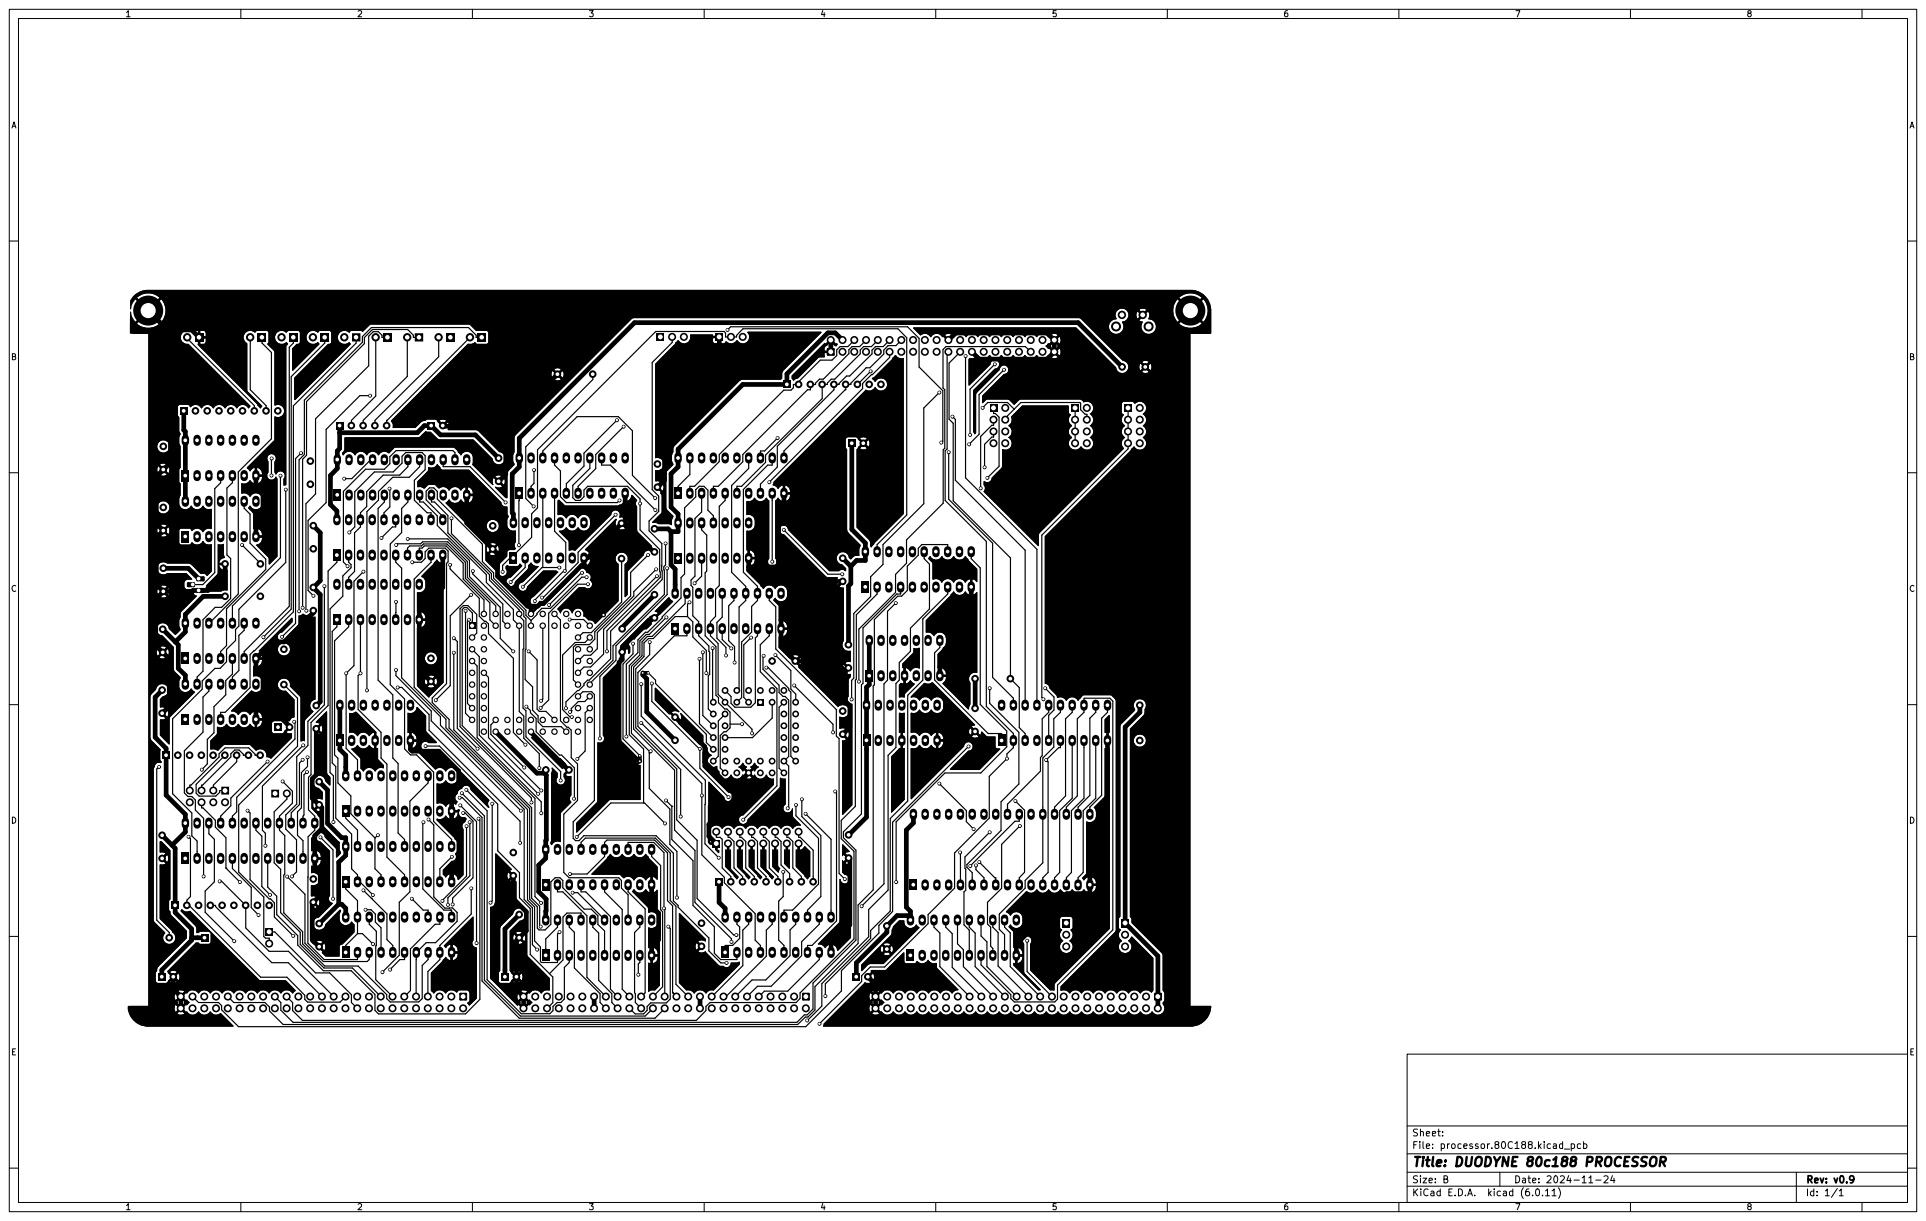
[picture p222: page 2]

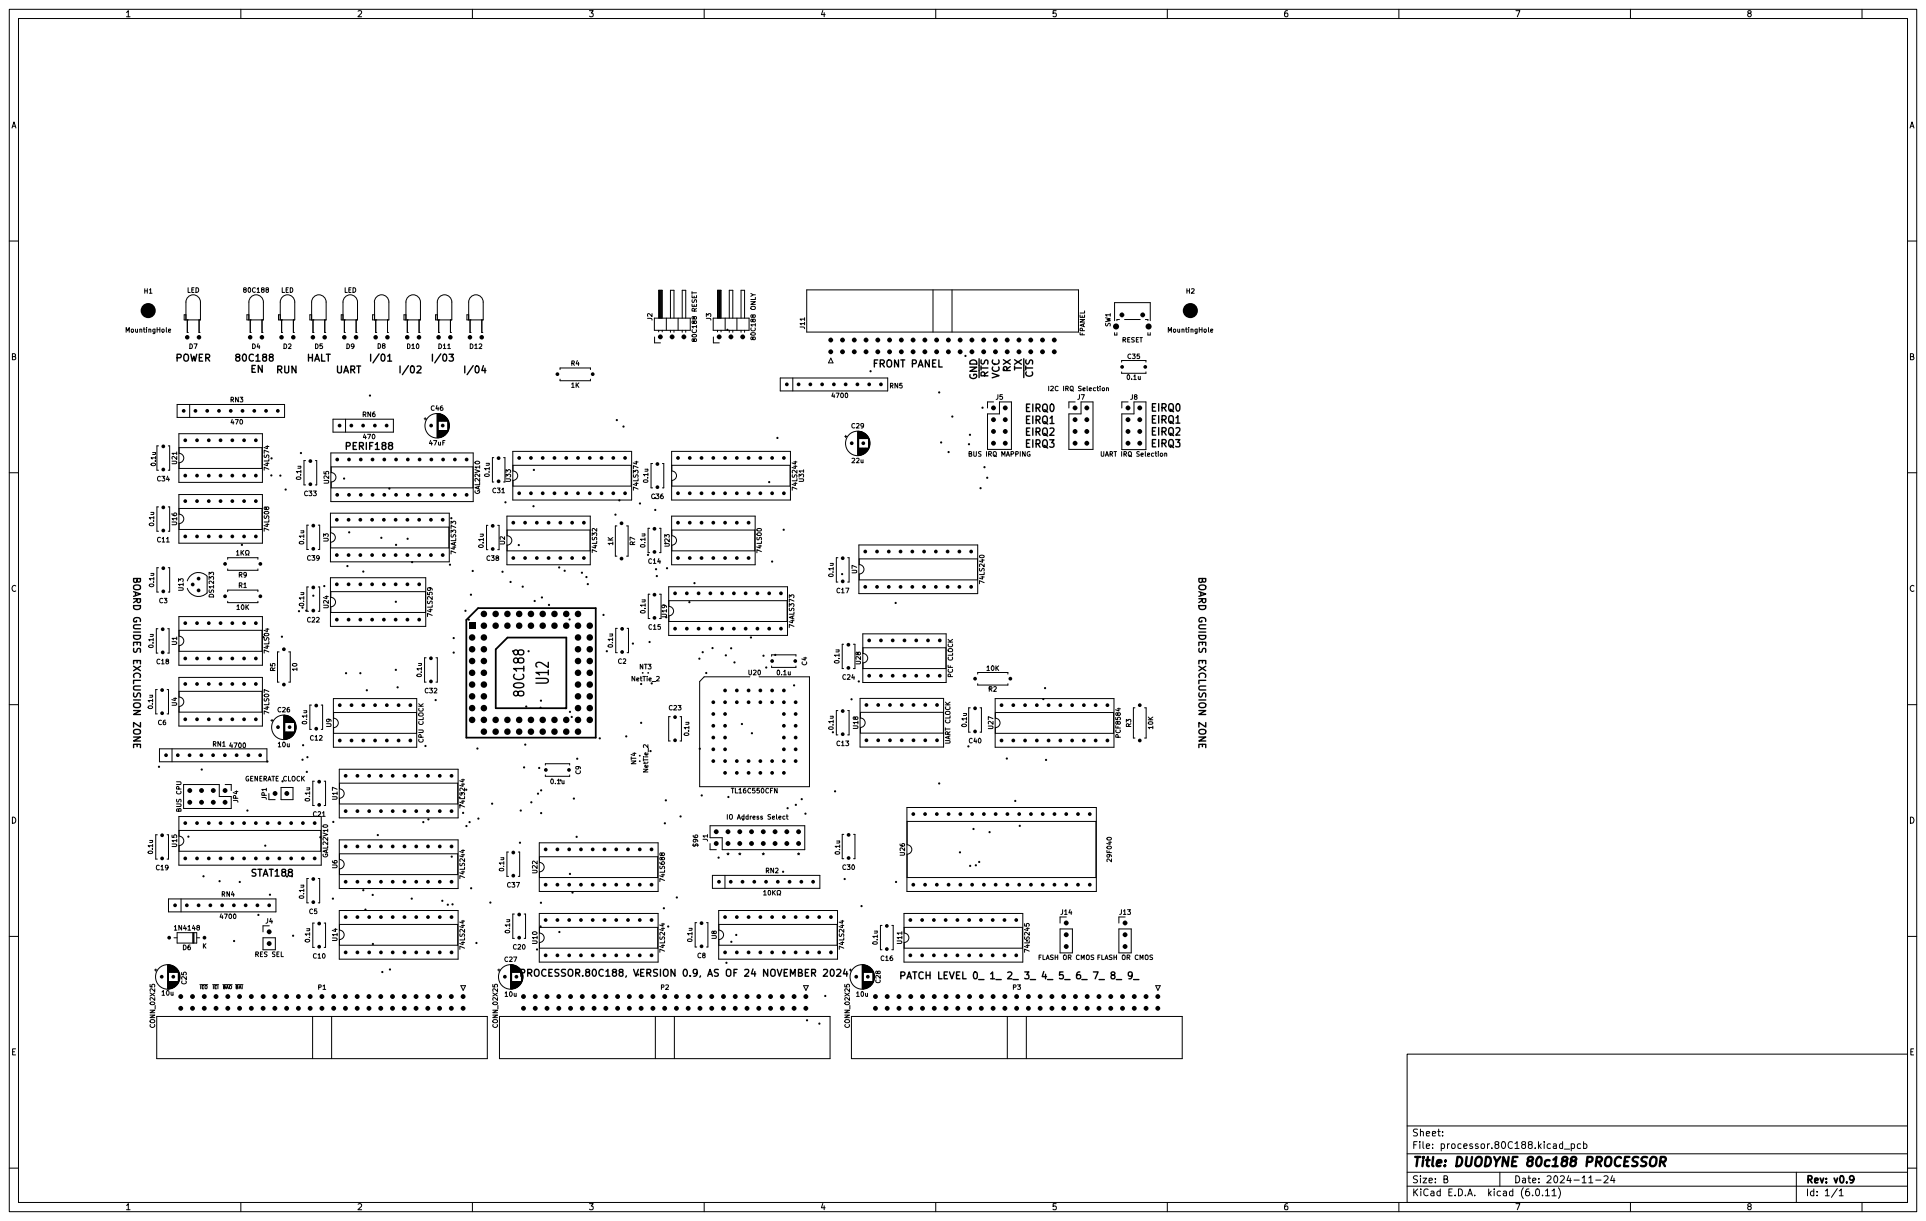
[picture p223: page 3]

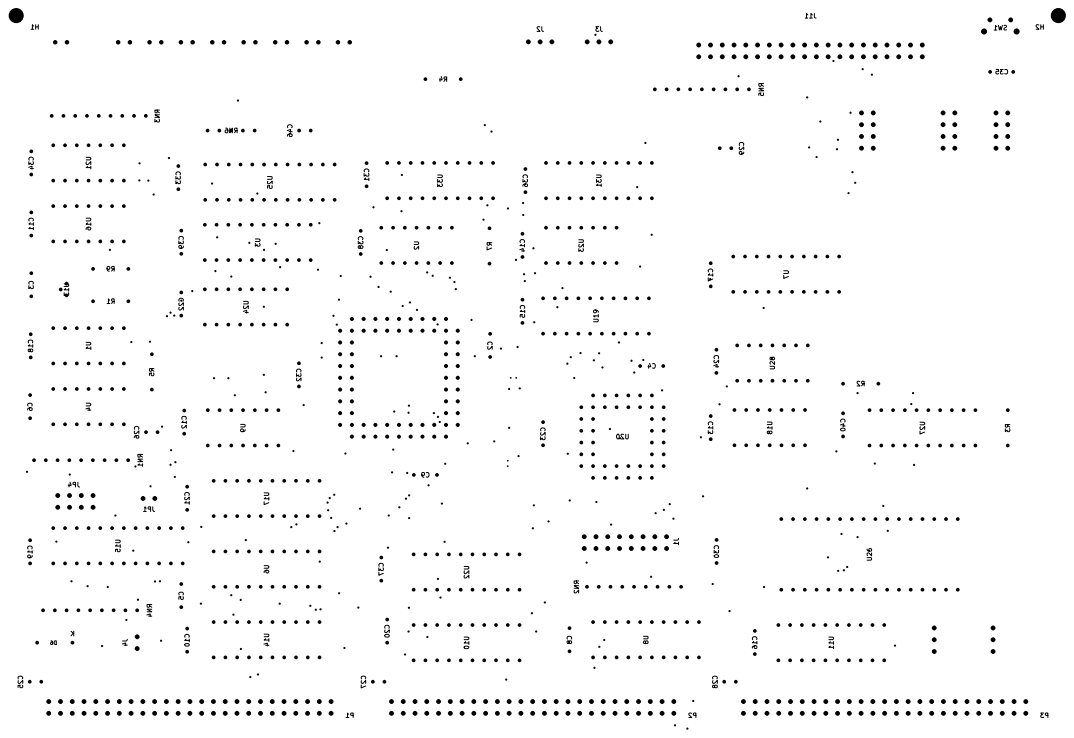
[picture p224: page 4]

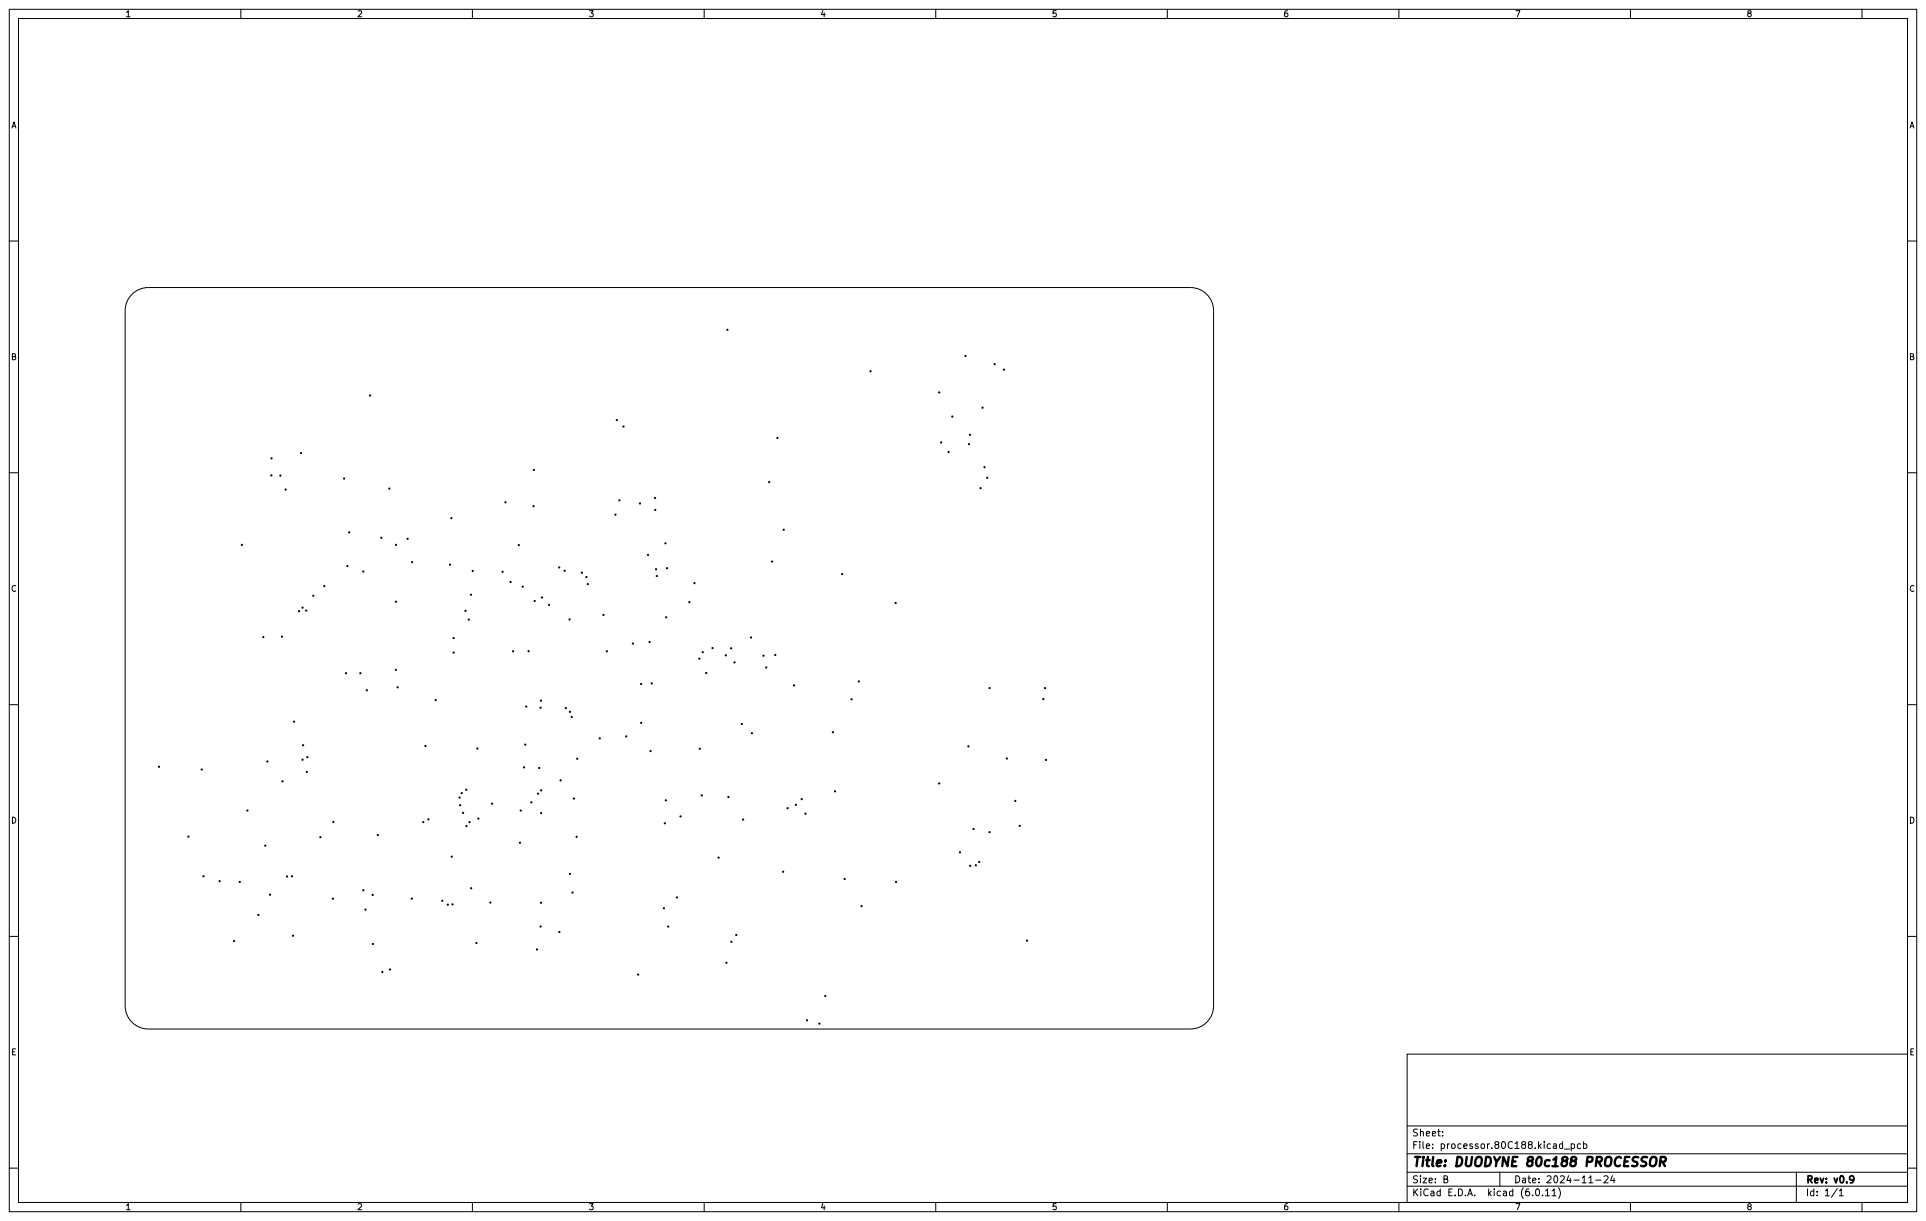
[picture p225: page 5]

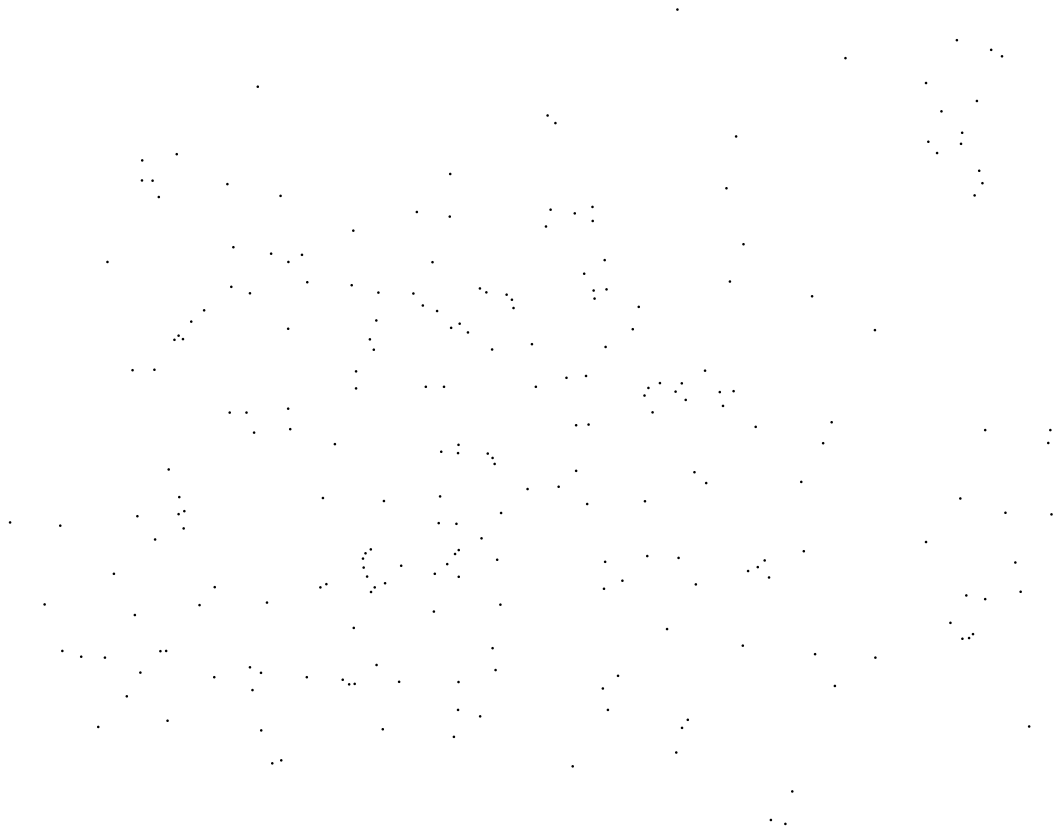
[picture p226: page 6]

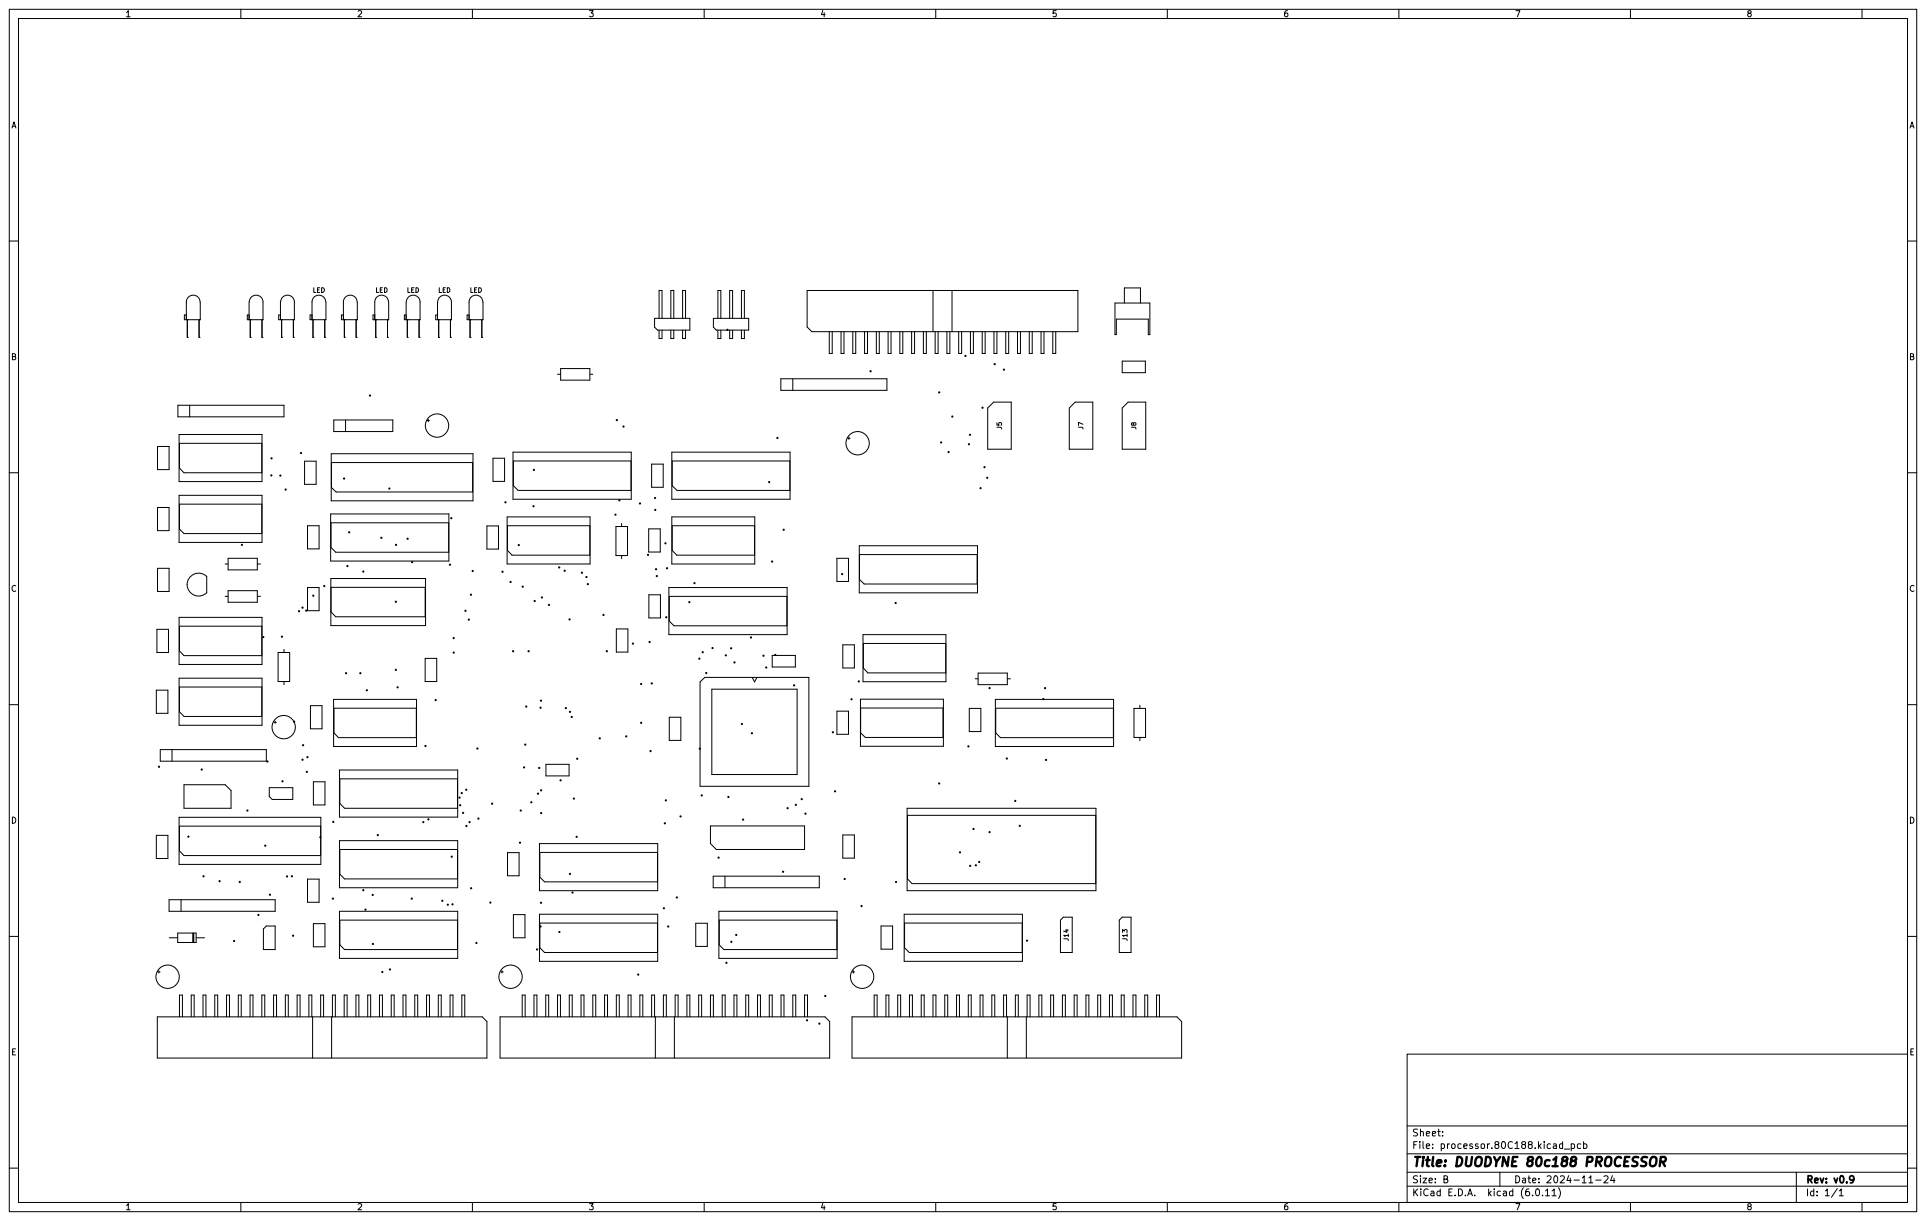
[picture p227: page 7]
