lynchaj/duodyne/25 processor.80c188/hardware/PROCESSOR.80C188.SCHEMATIC-v0.90.pdf

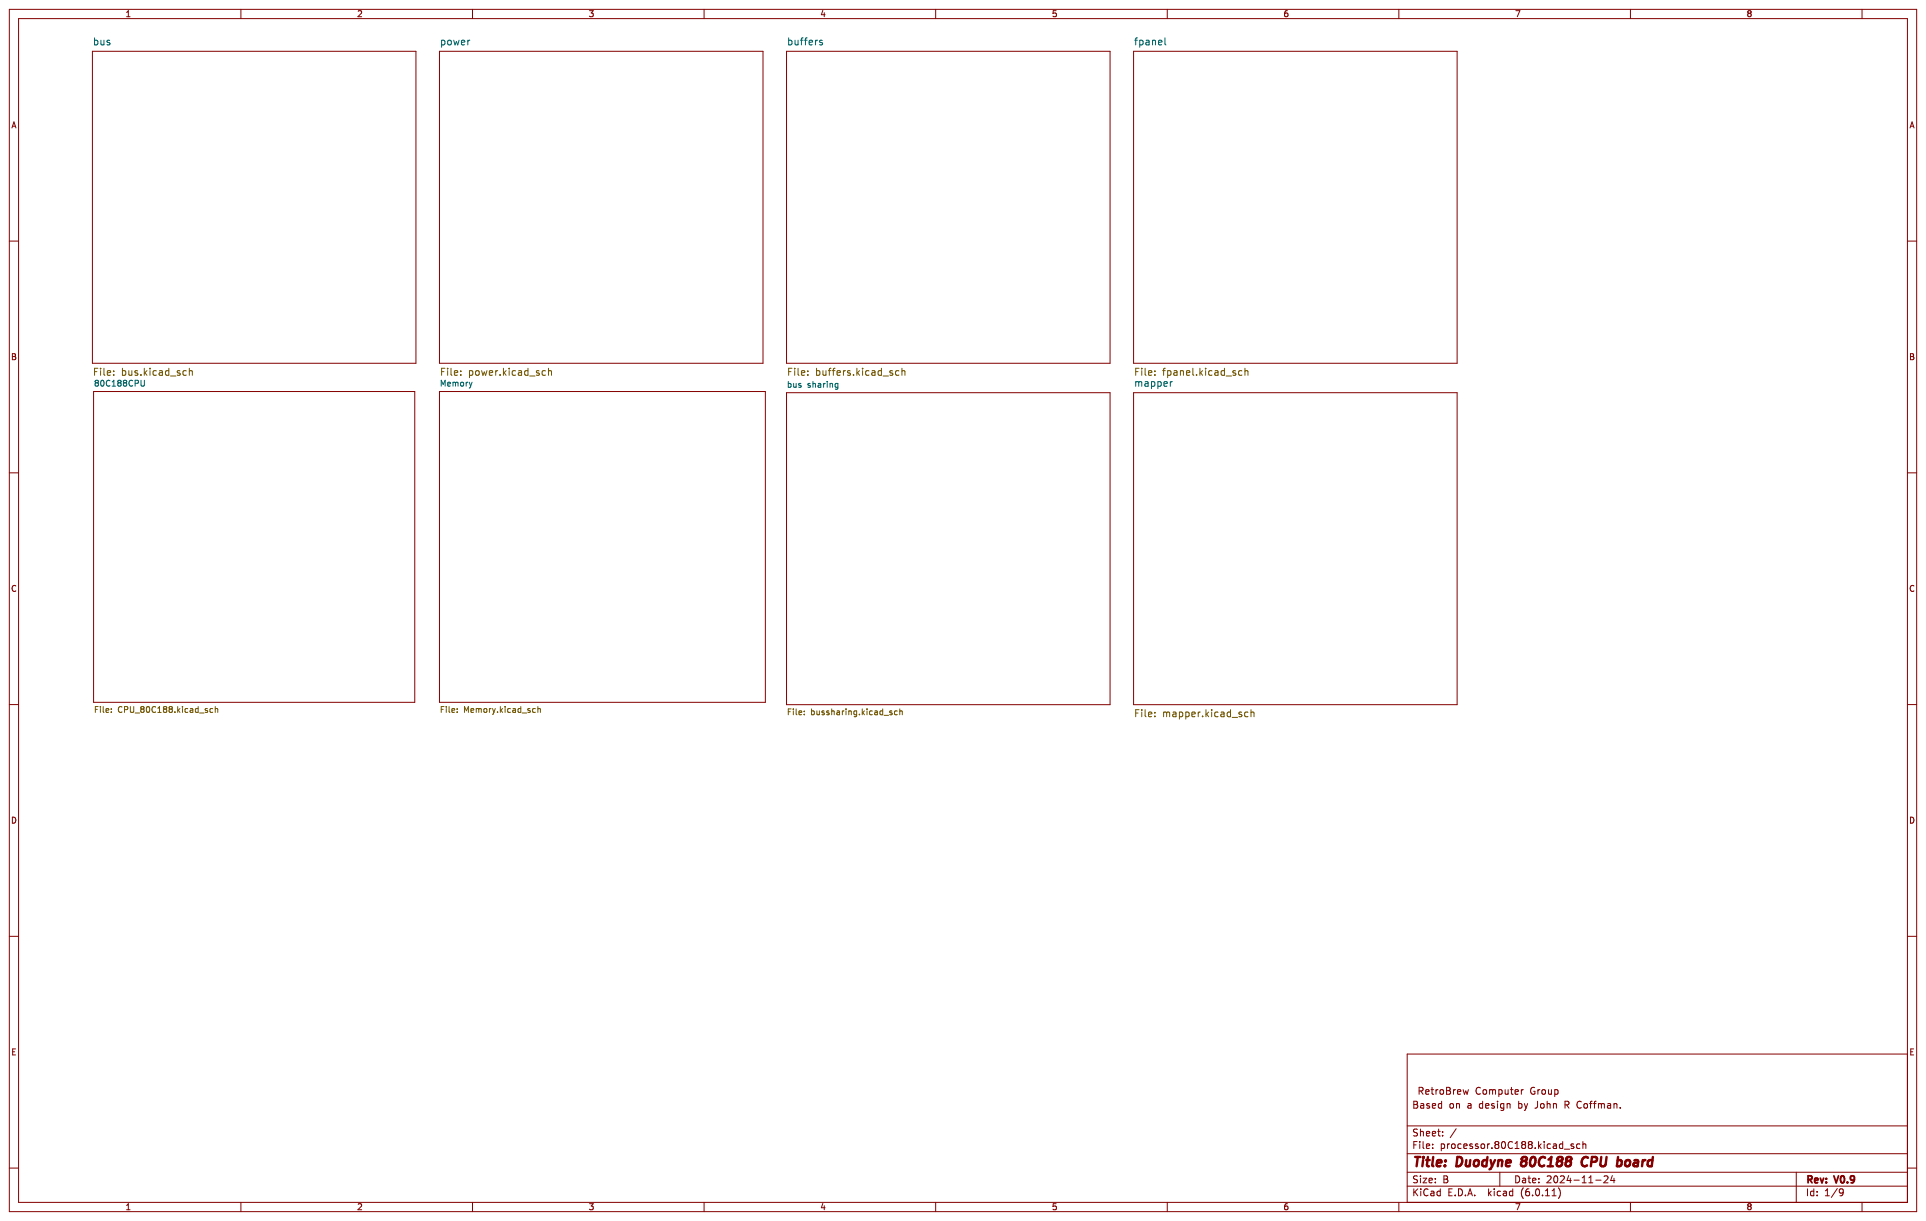
[picture p228: page 1]

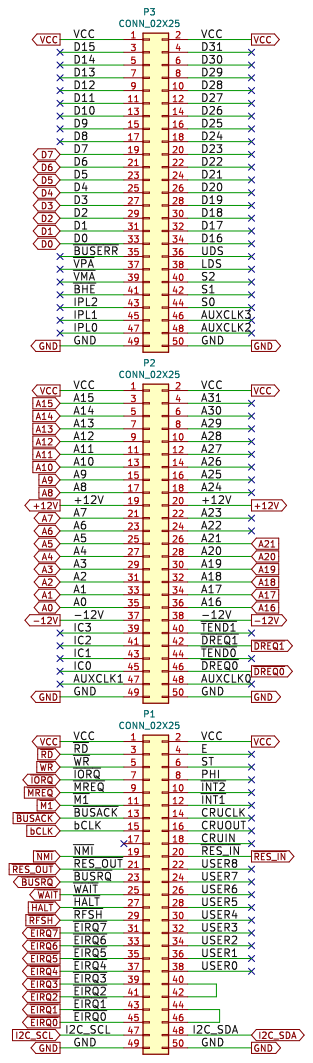
[picture p229: page 2]

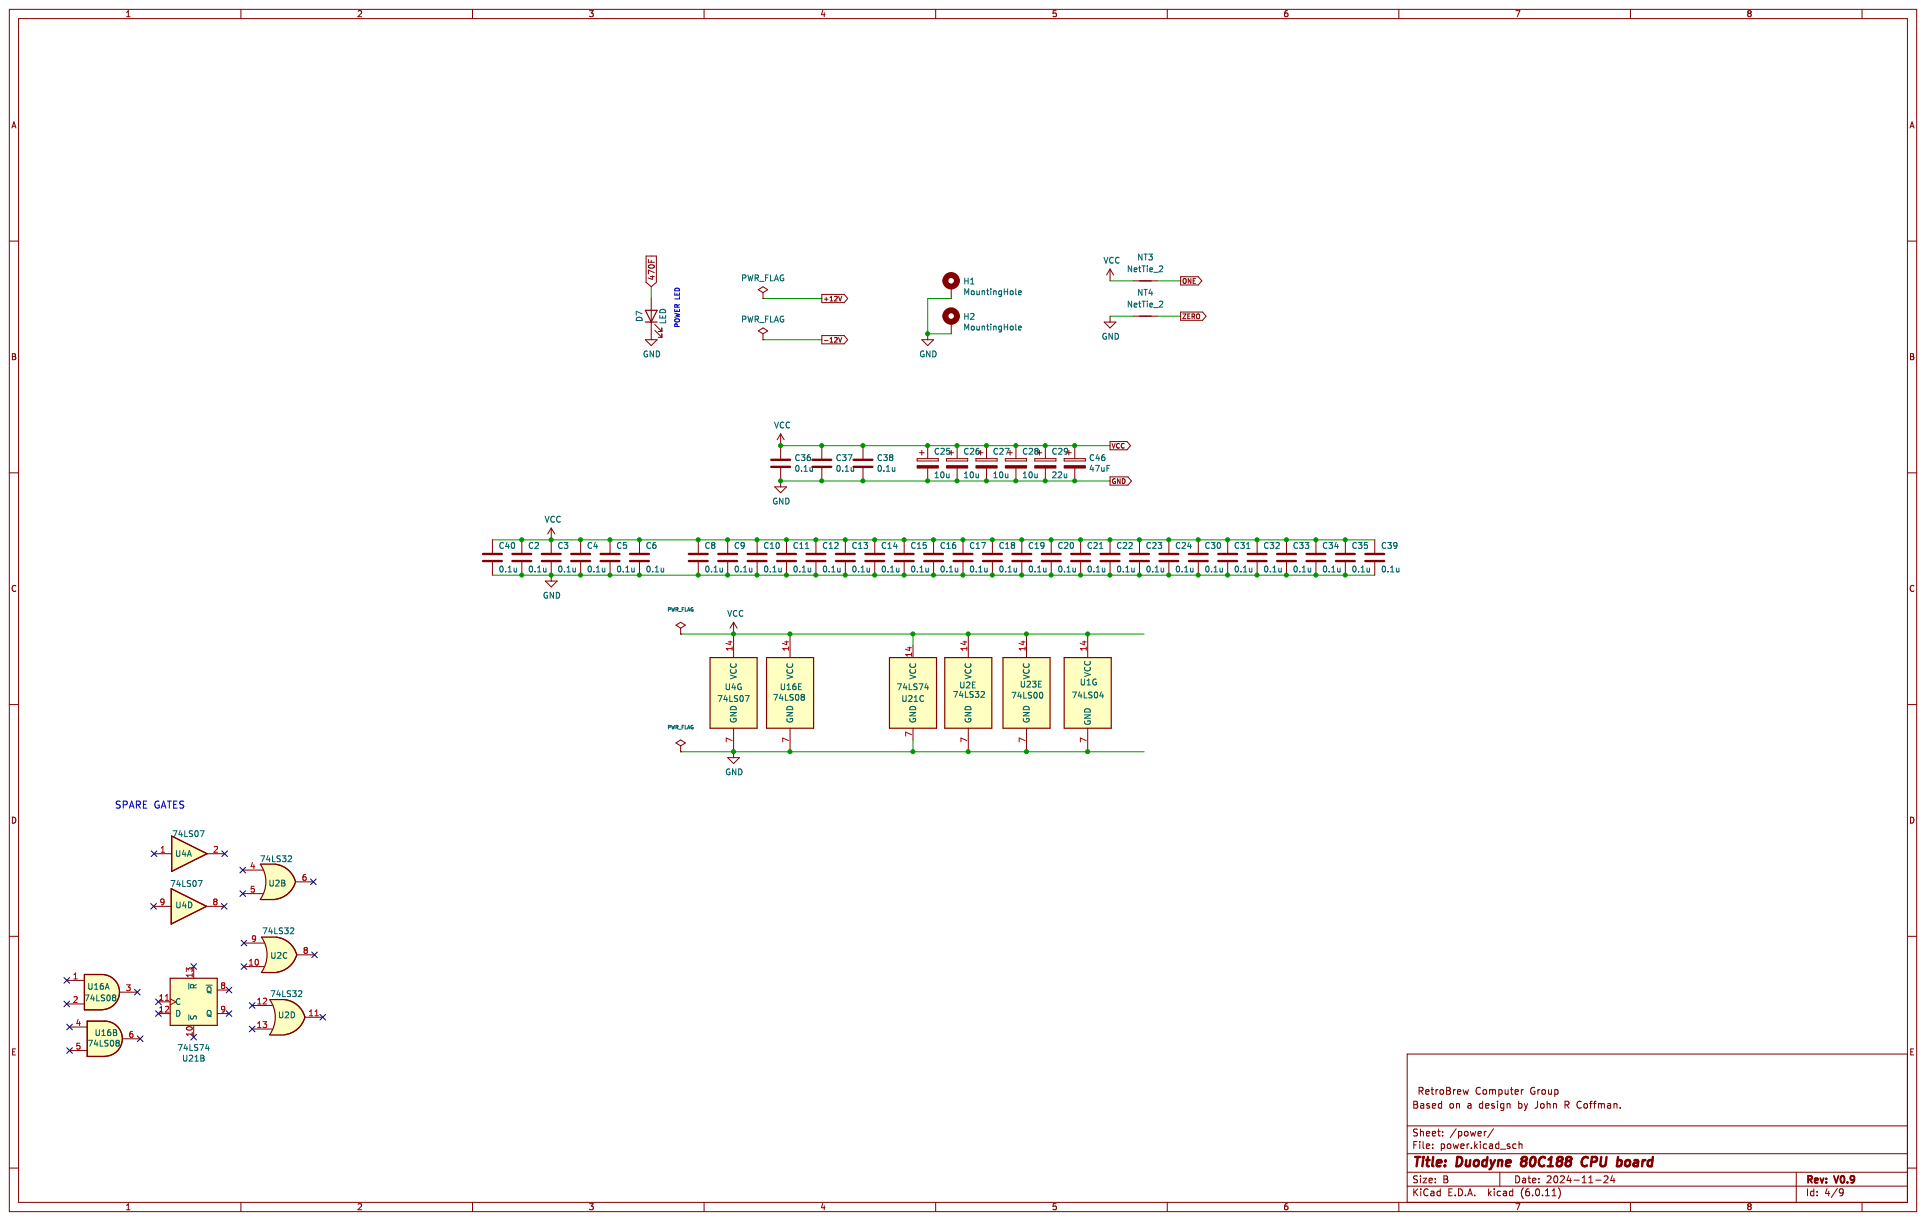
[picture p230: page 3]

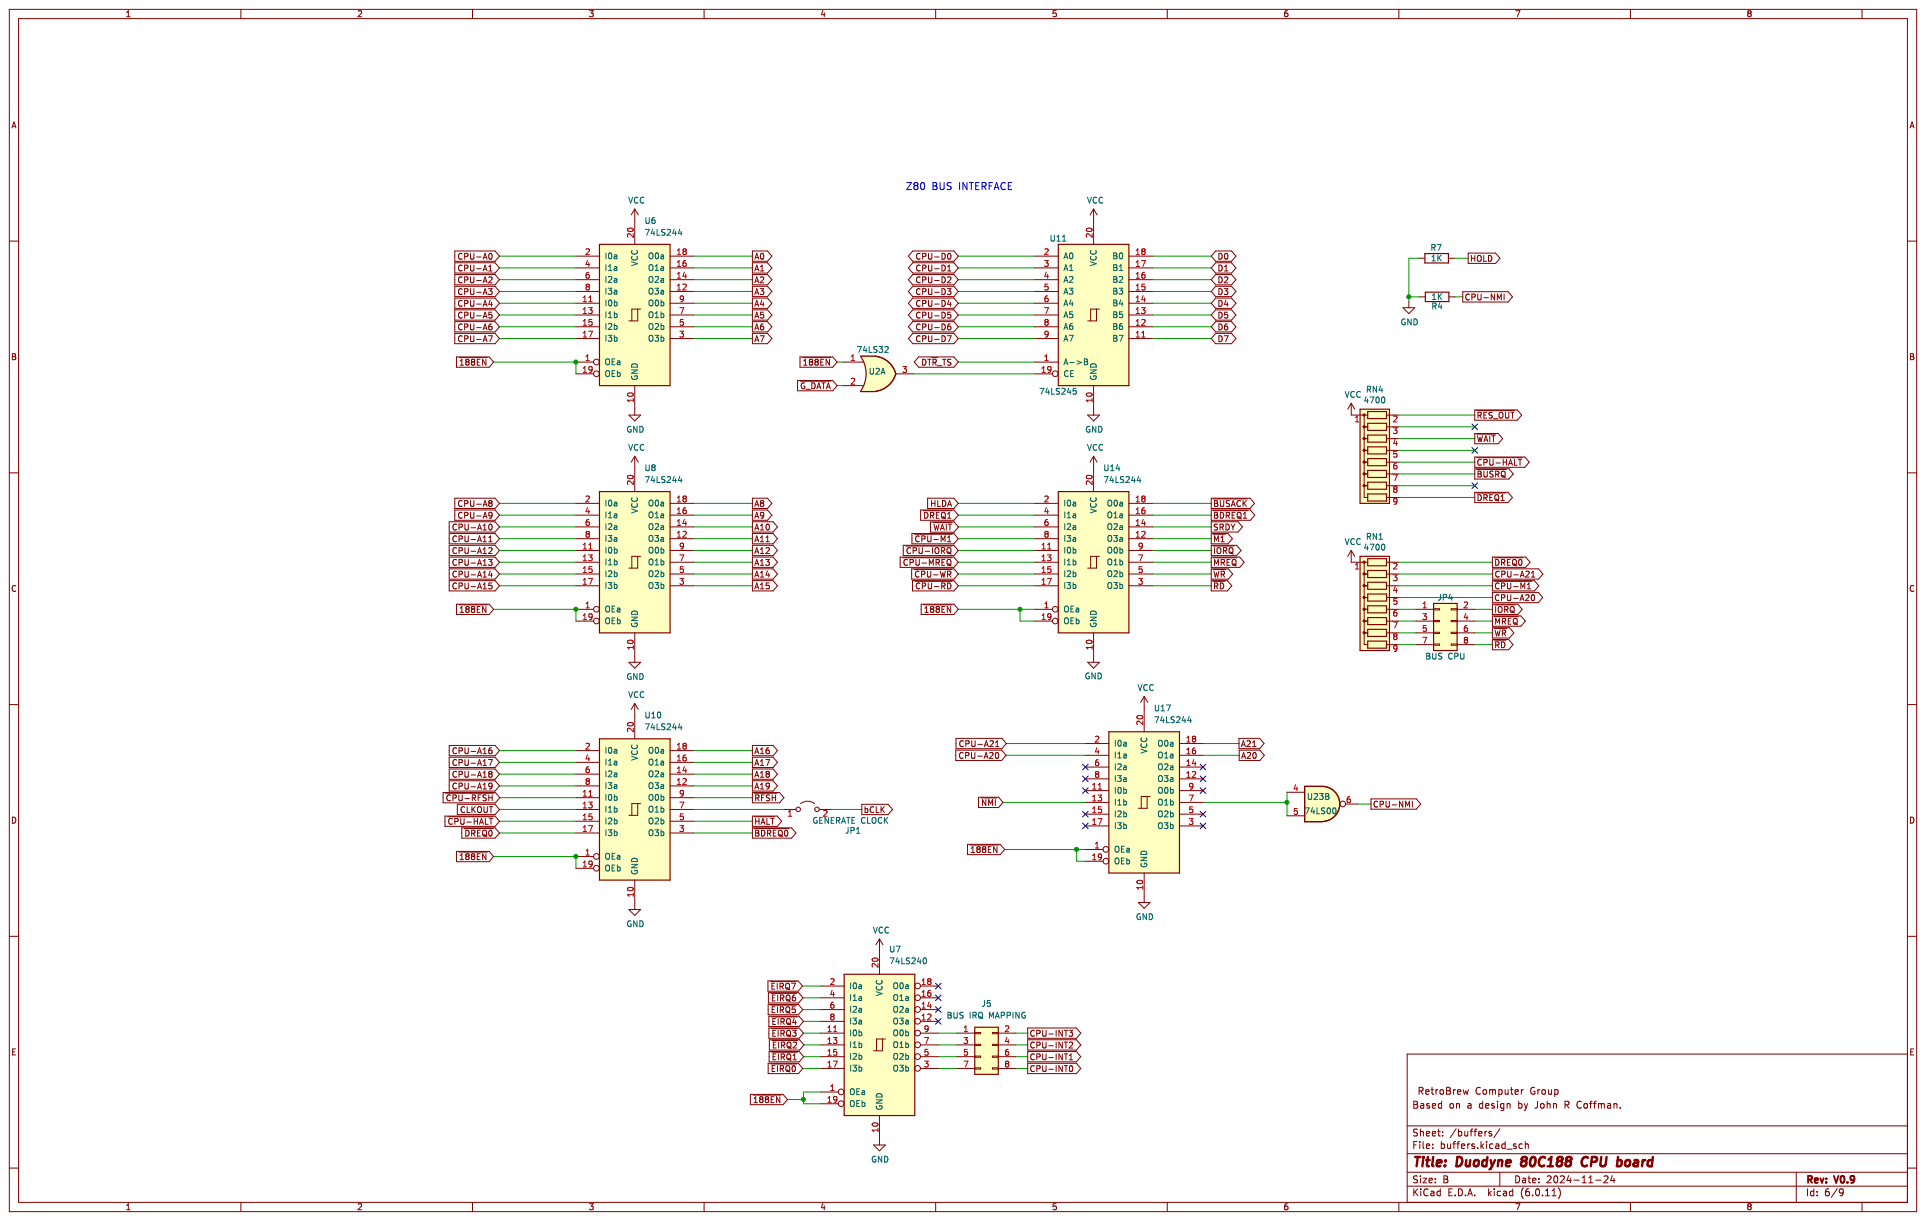
[picture p231: page 4]

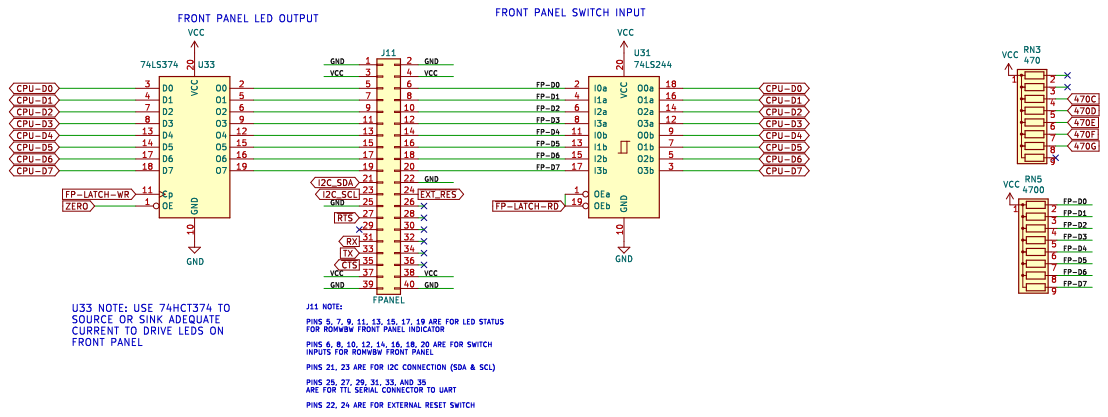
[picture p232: page 5]

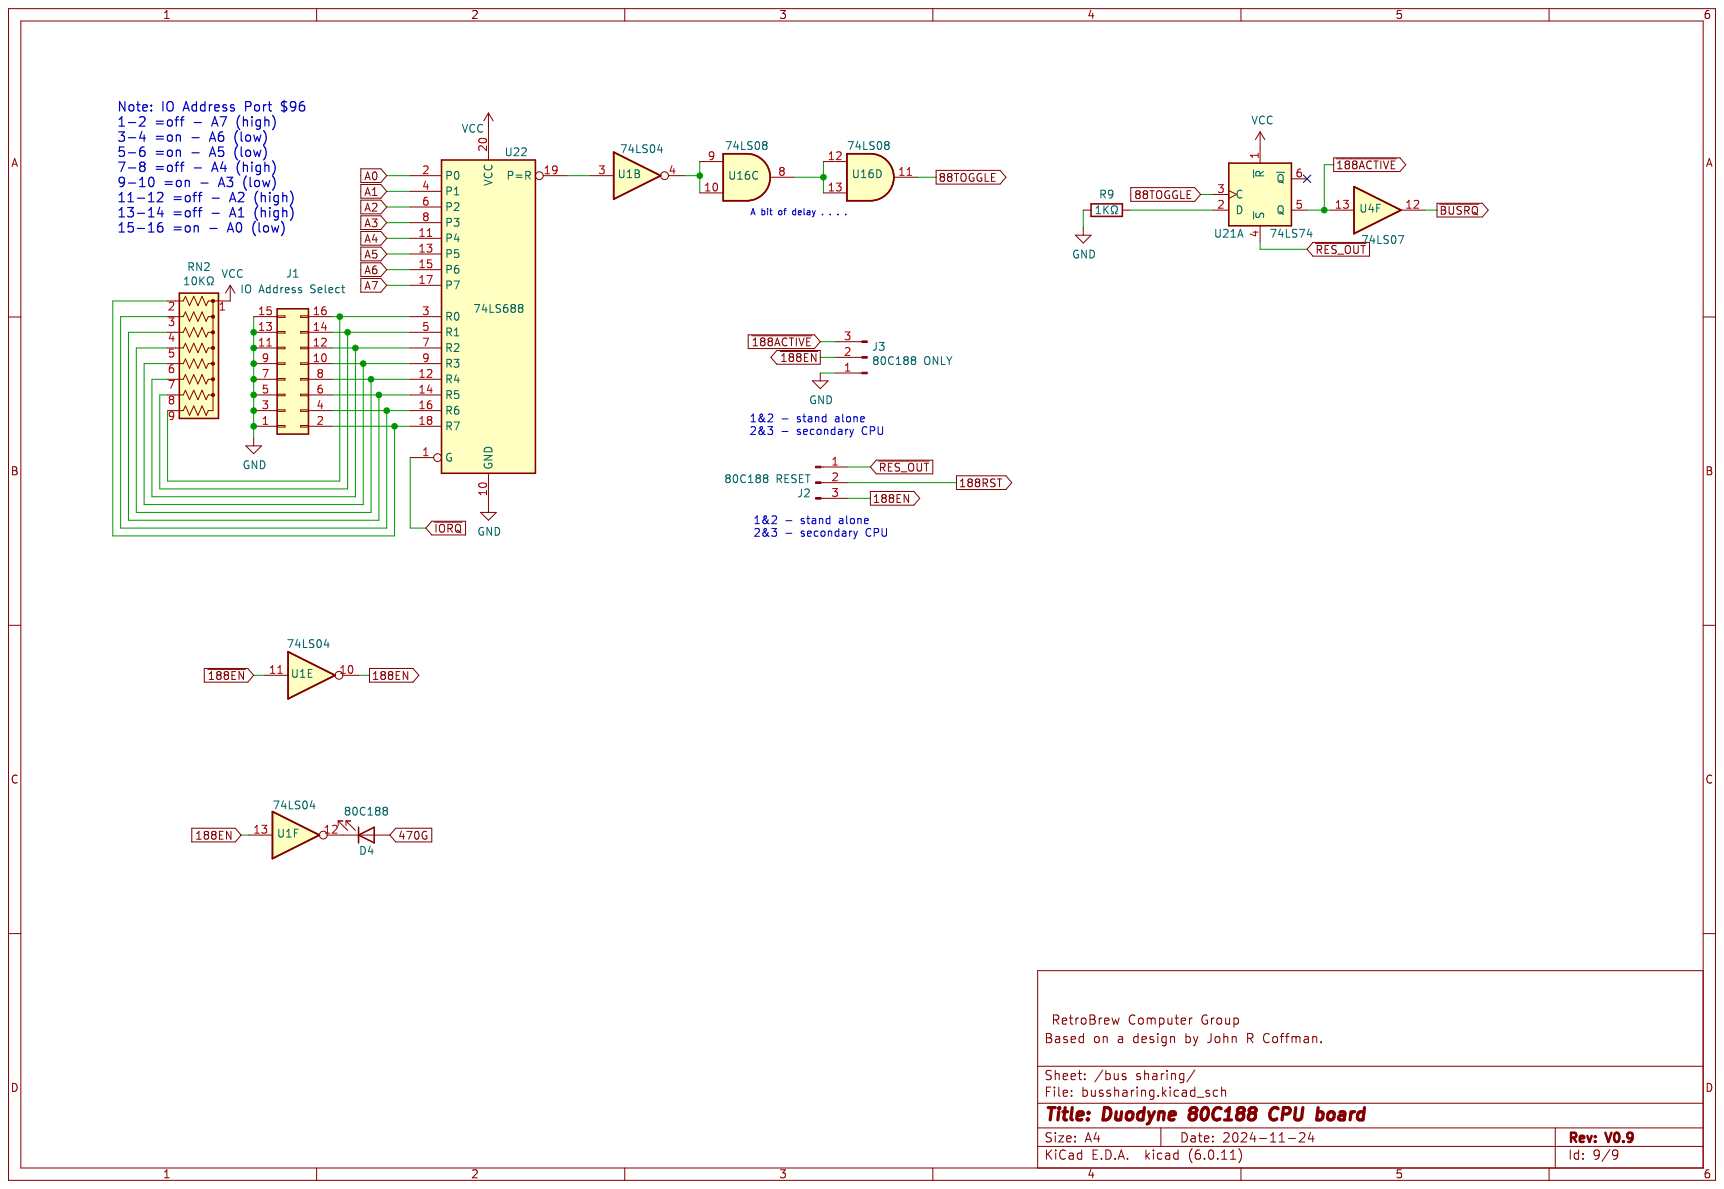
[picture p233: page 6]

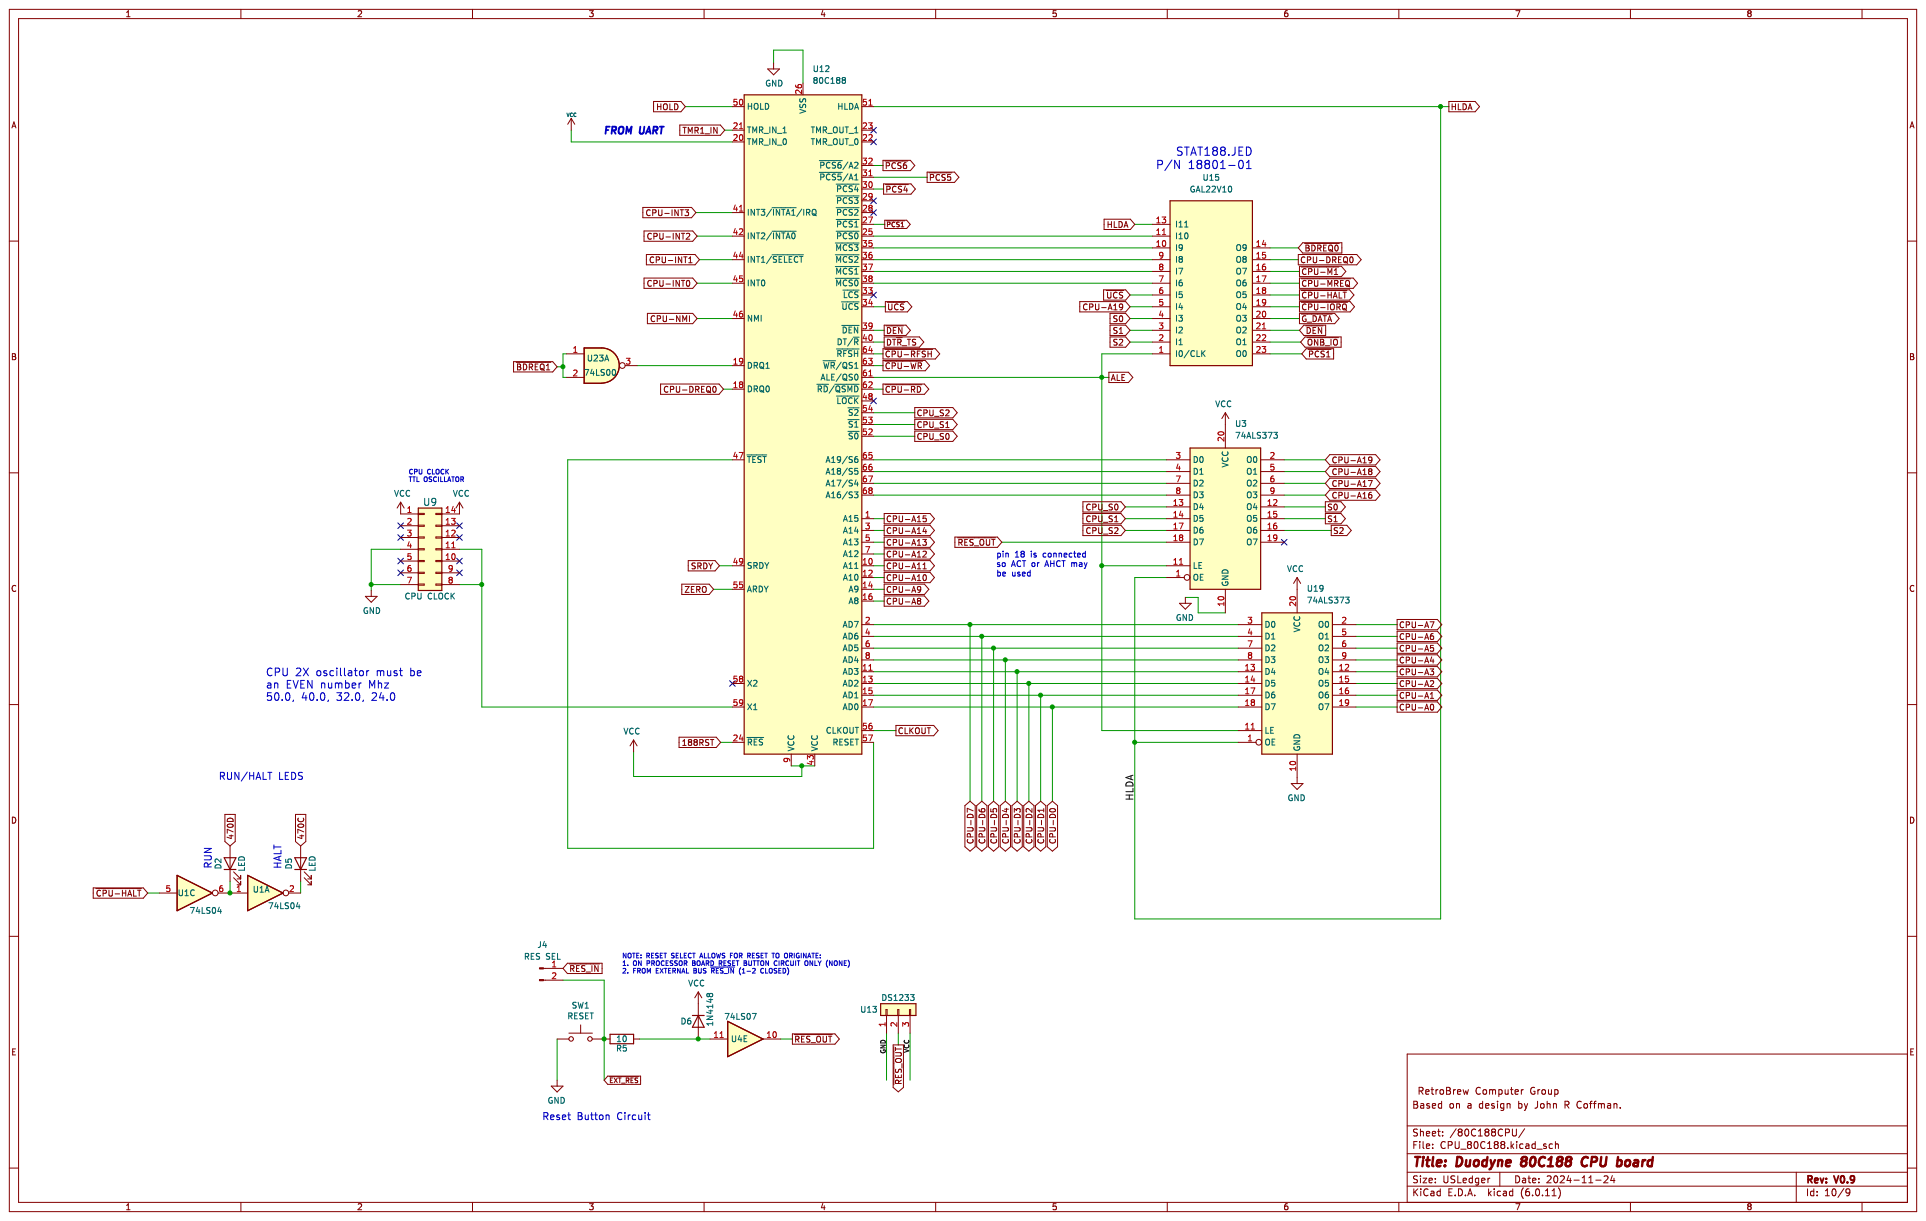
[picture p234: page 7]

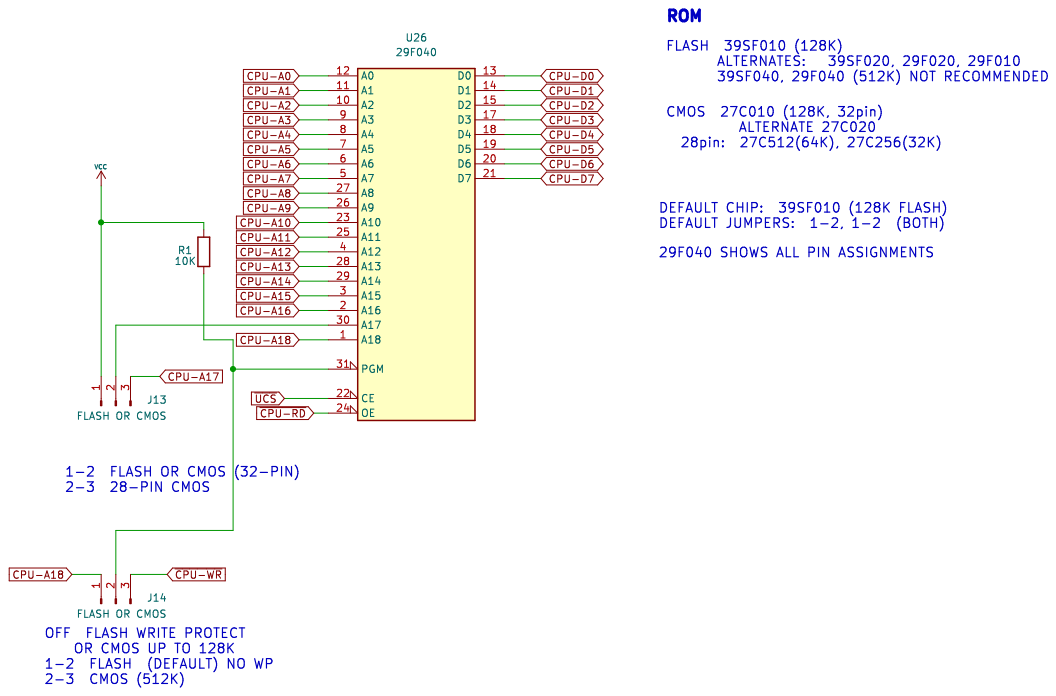
[picture p235: page 8]

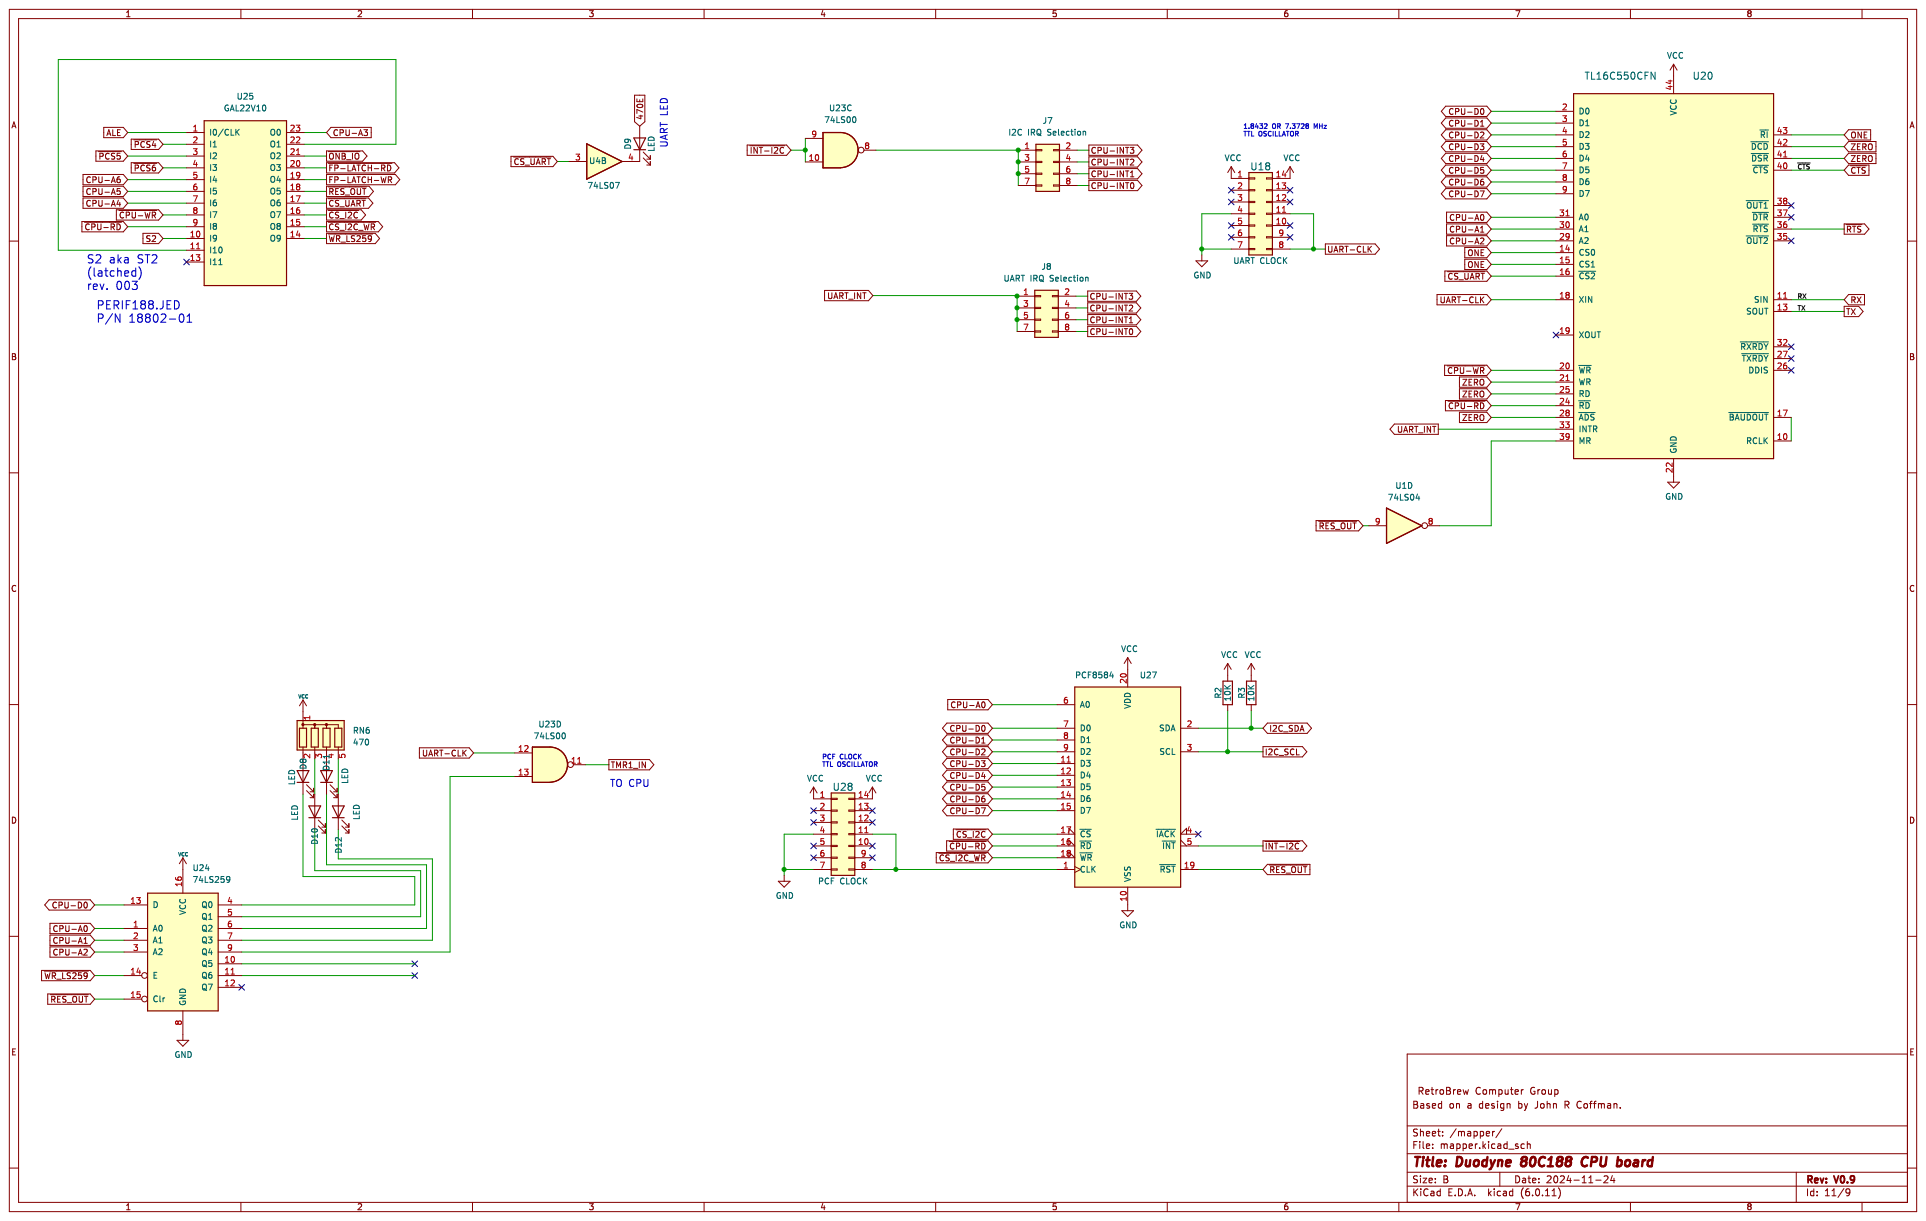
[picture p236: page 9]
