lynchaj/duodyne/23 processor.6809/hardware/PCB6809_PCB_V1.2.pdf

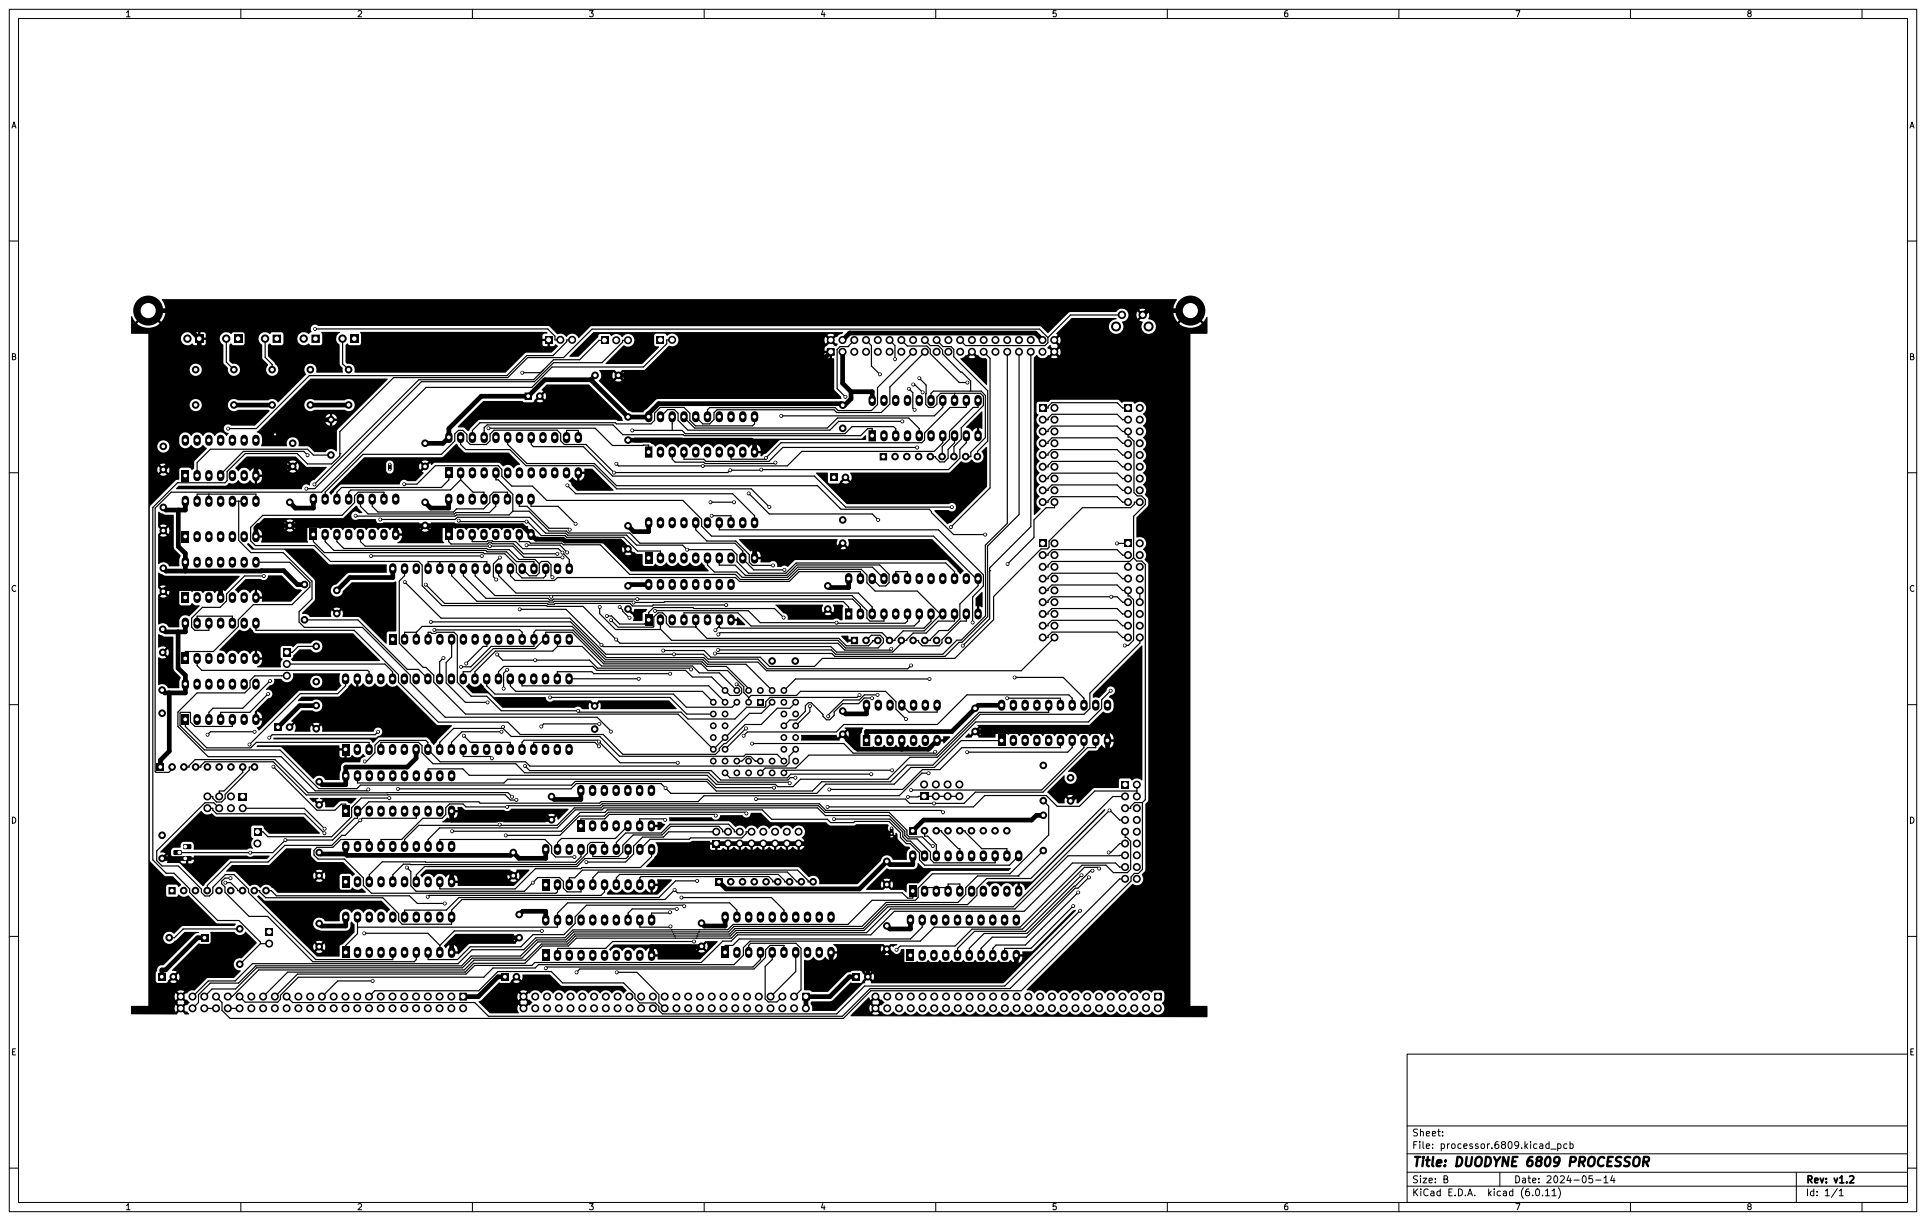
[picture p237: page 1]

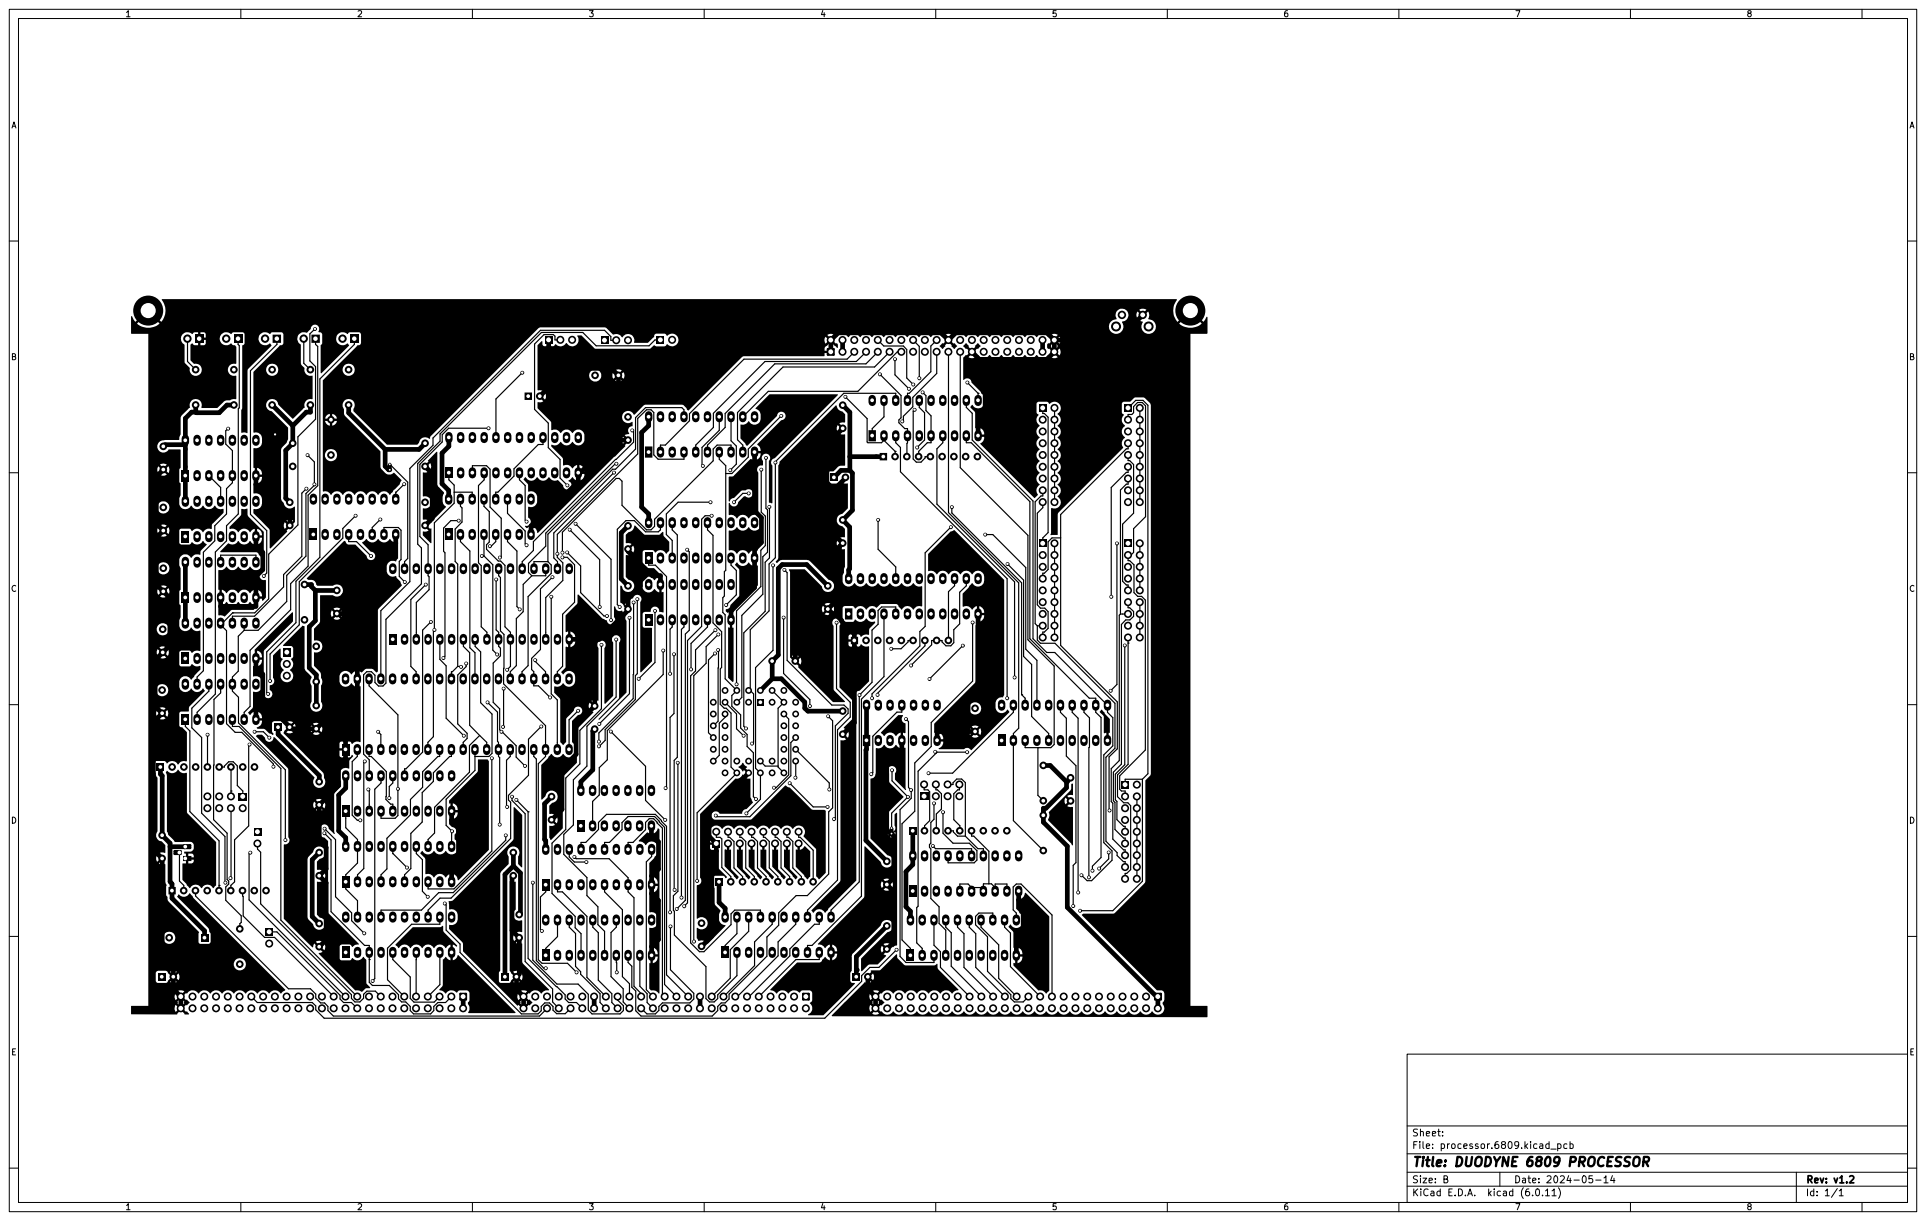
[picture p238: page 2]

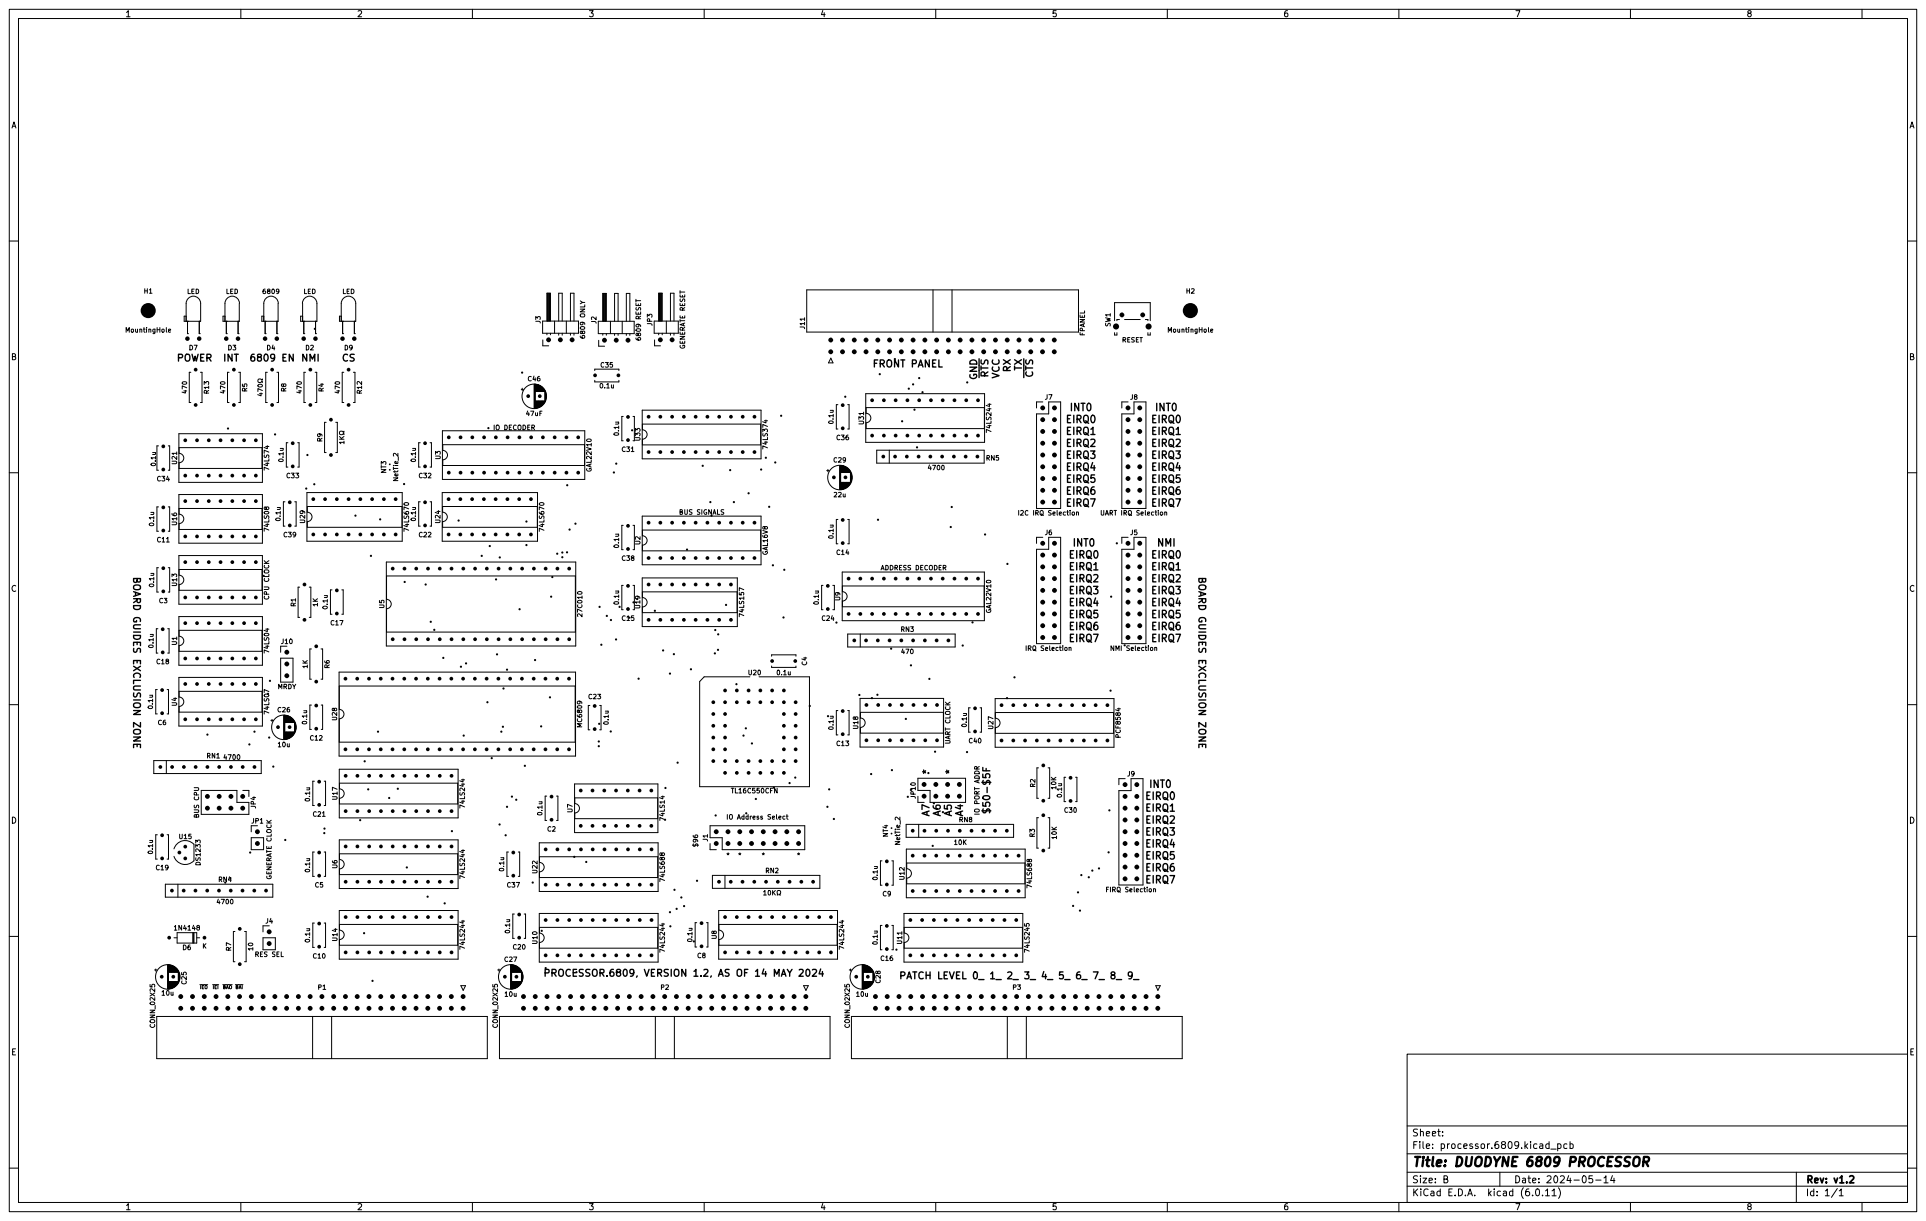
[picture p239: page 3]

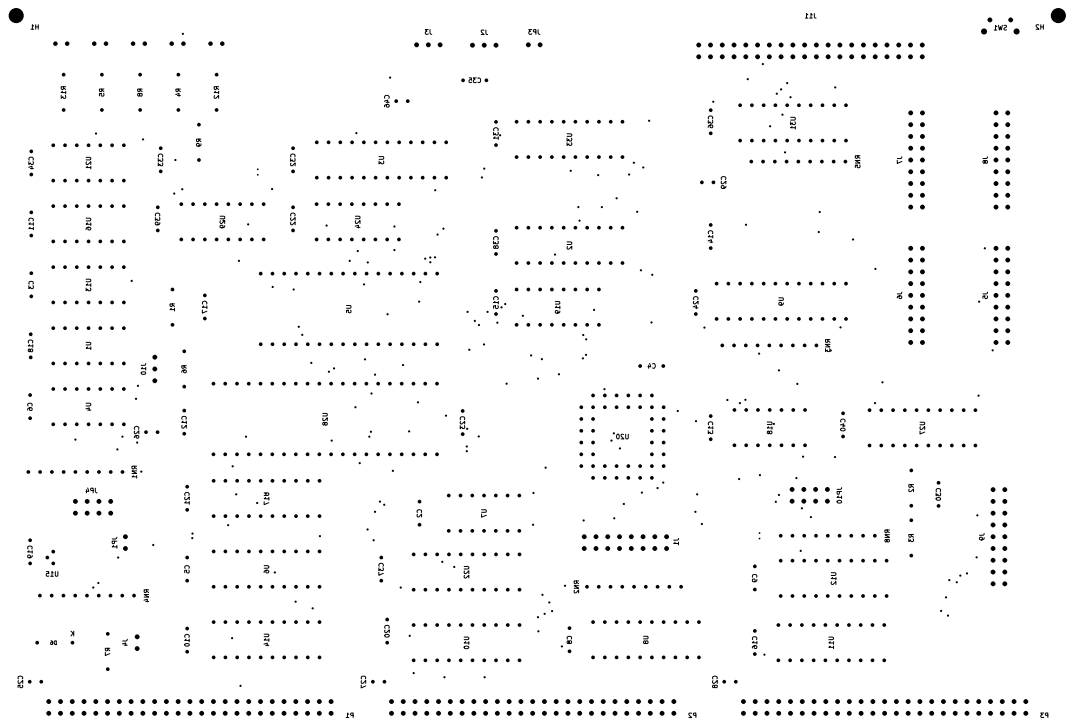
[picture p240: page 4]

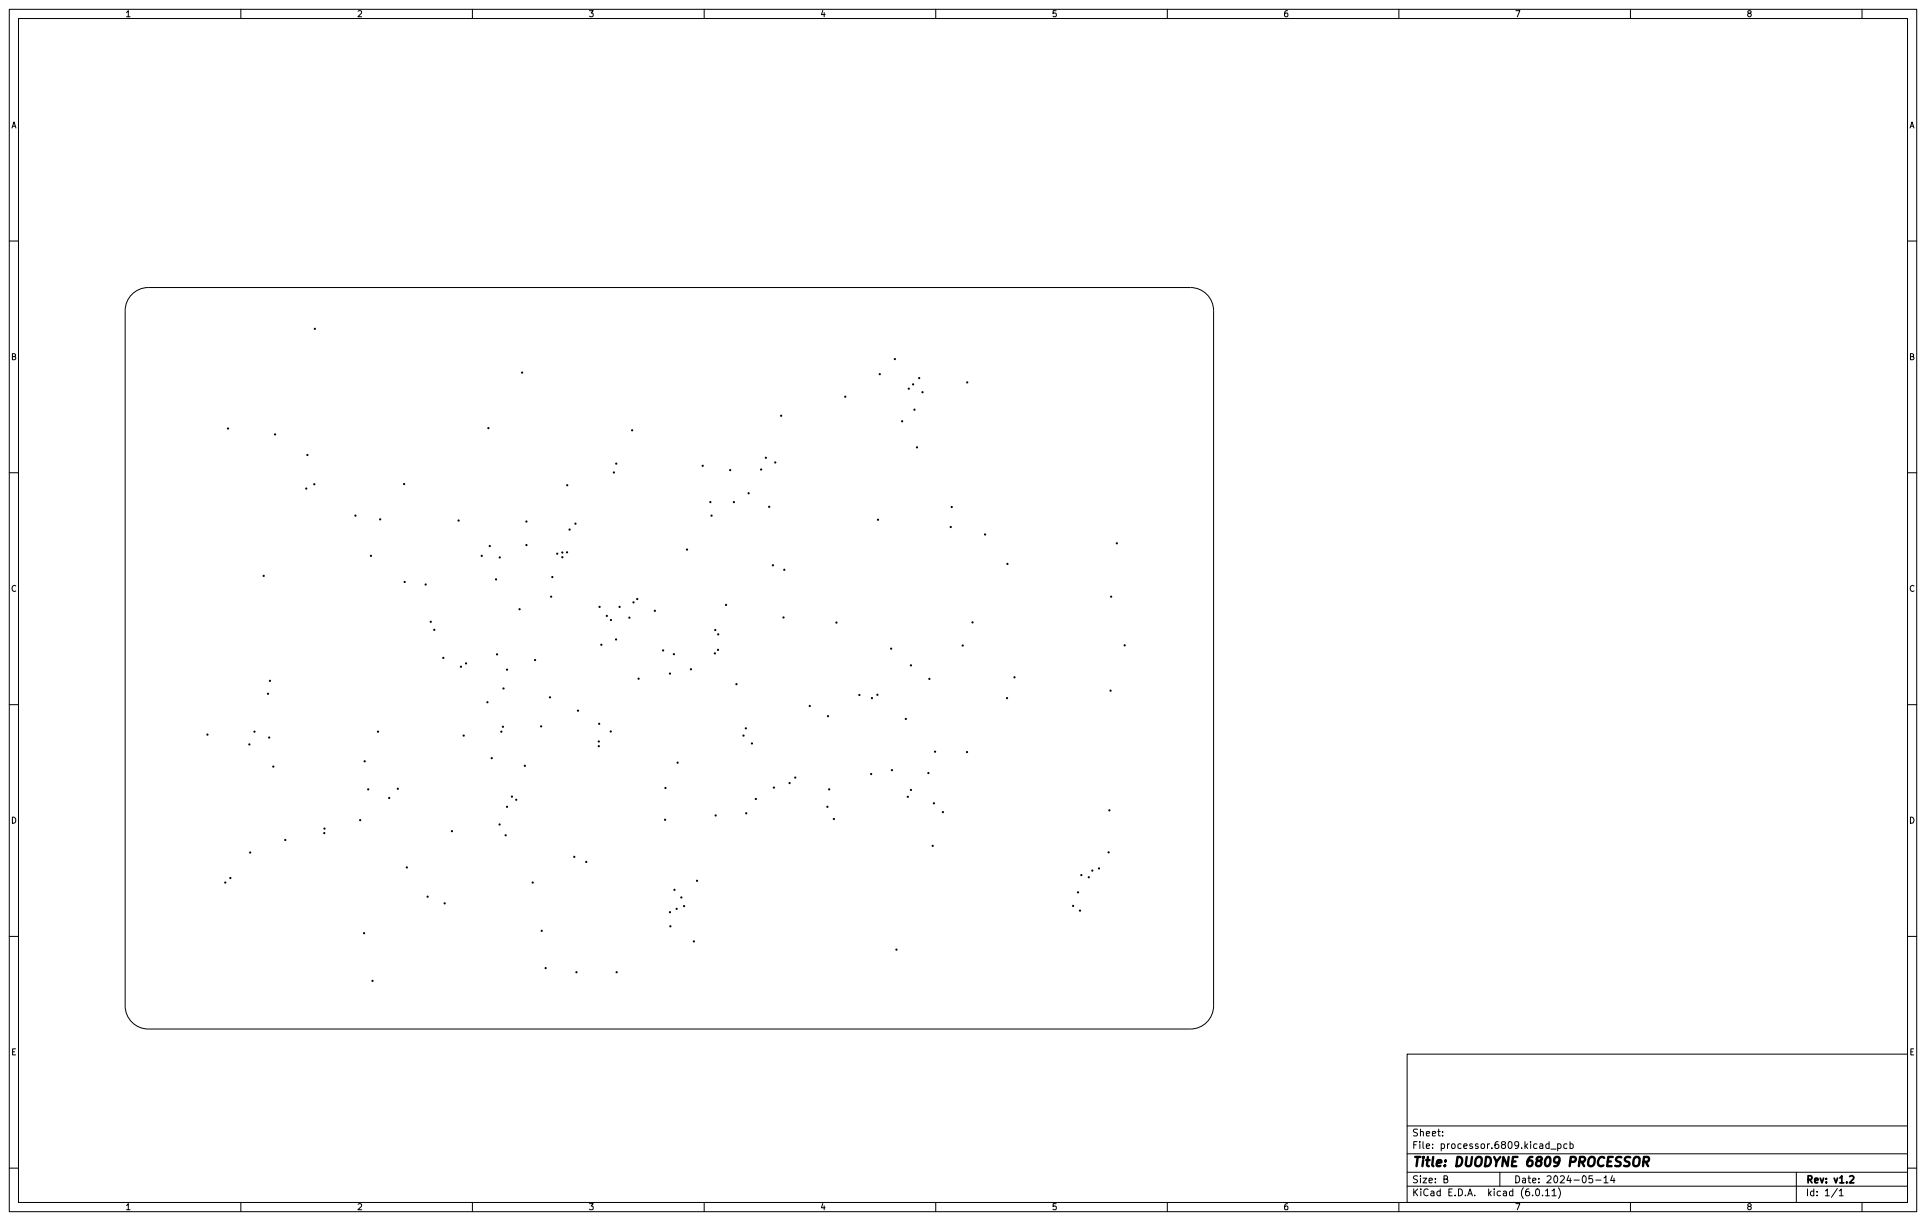
[picture p241: page 5]

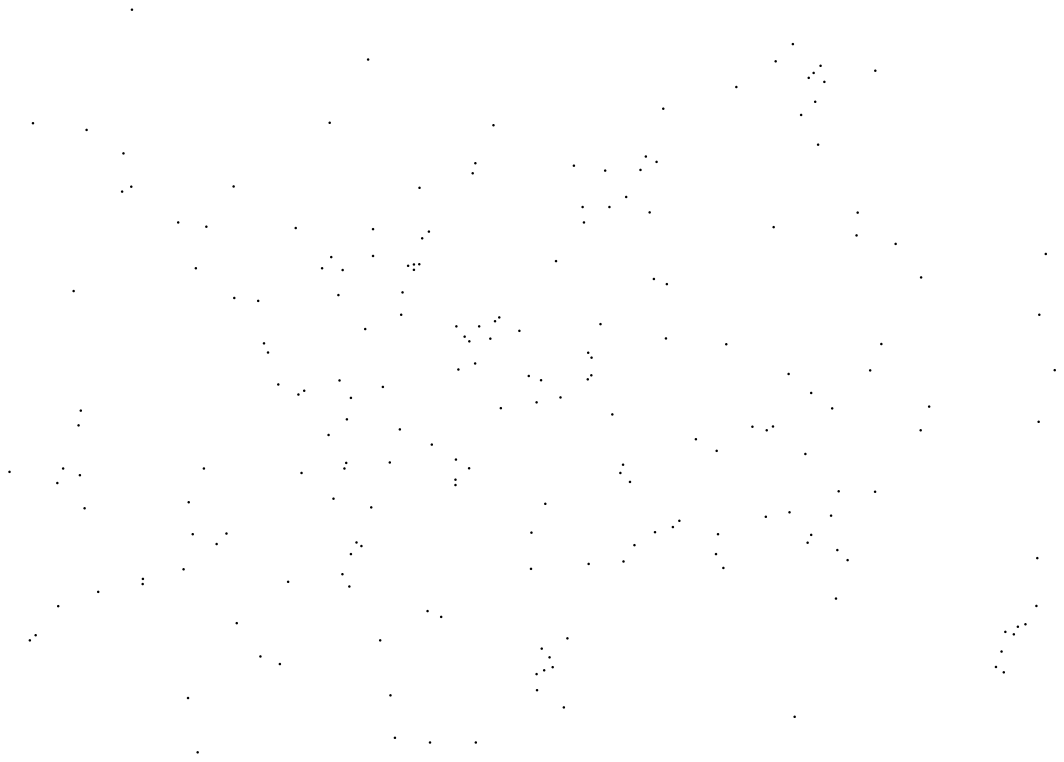
[picture p242: page 6]

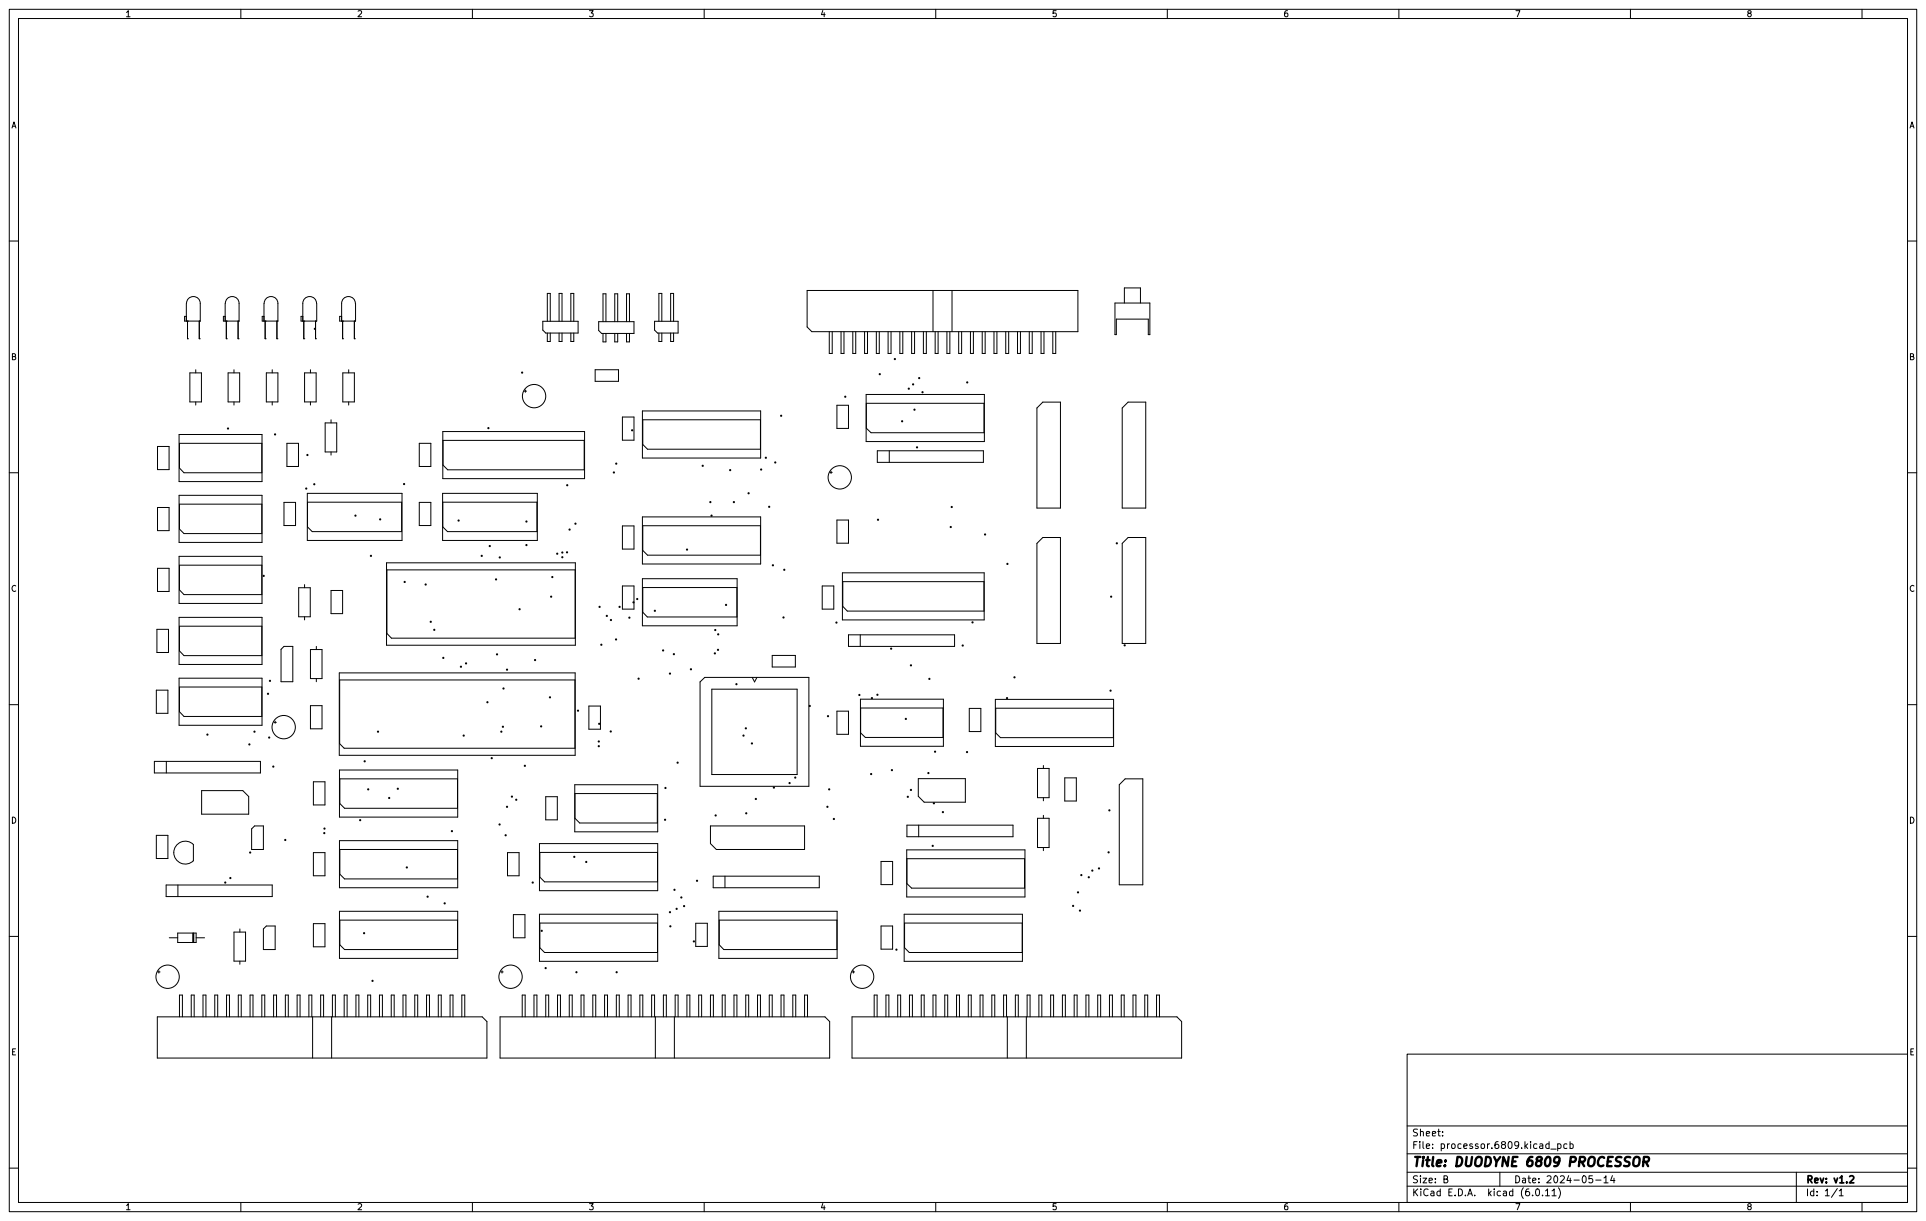
[picture p243: page 7]
