lynchaj/duodyne/23 processor.6809/hardware/PCB6809_SCHEMATIC_V1.2.pdf

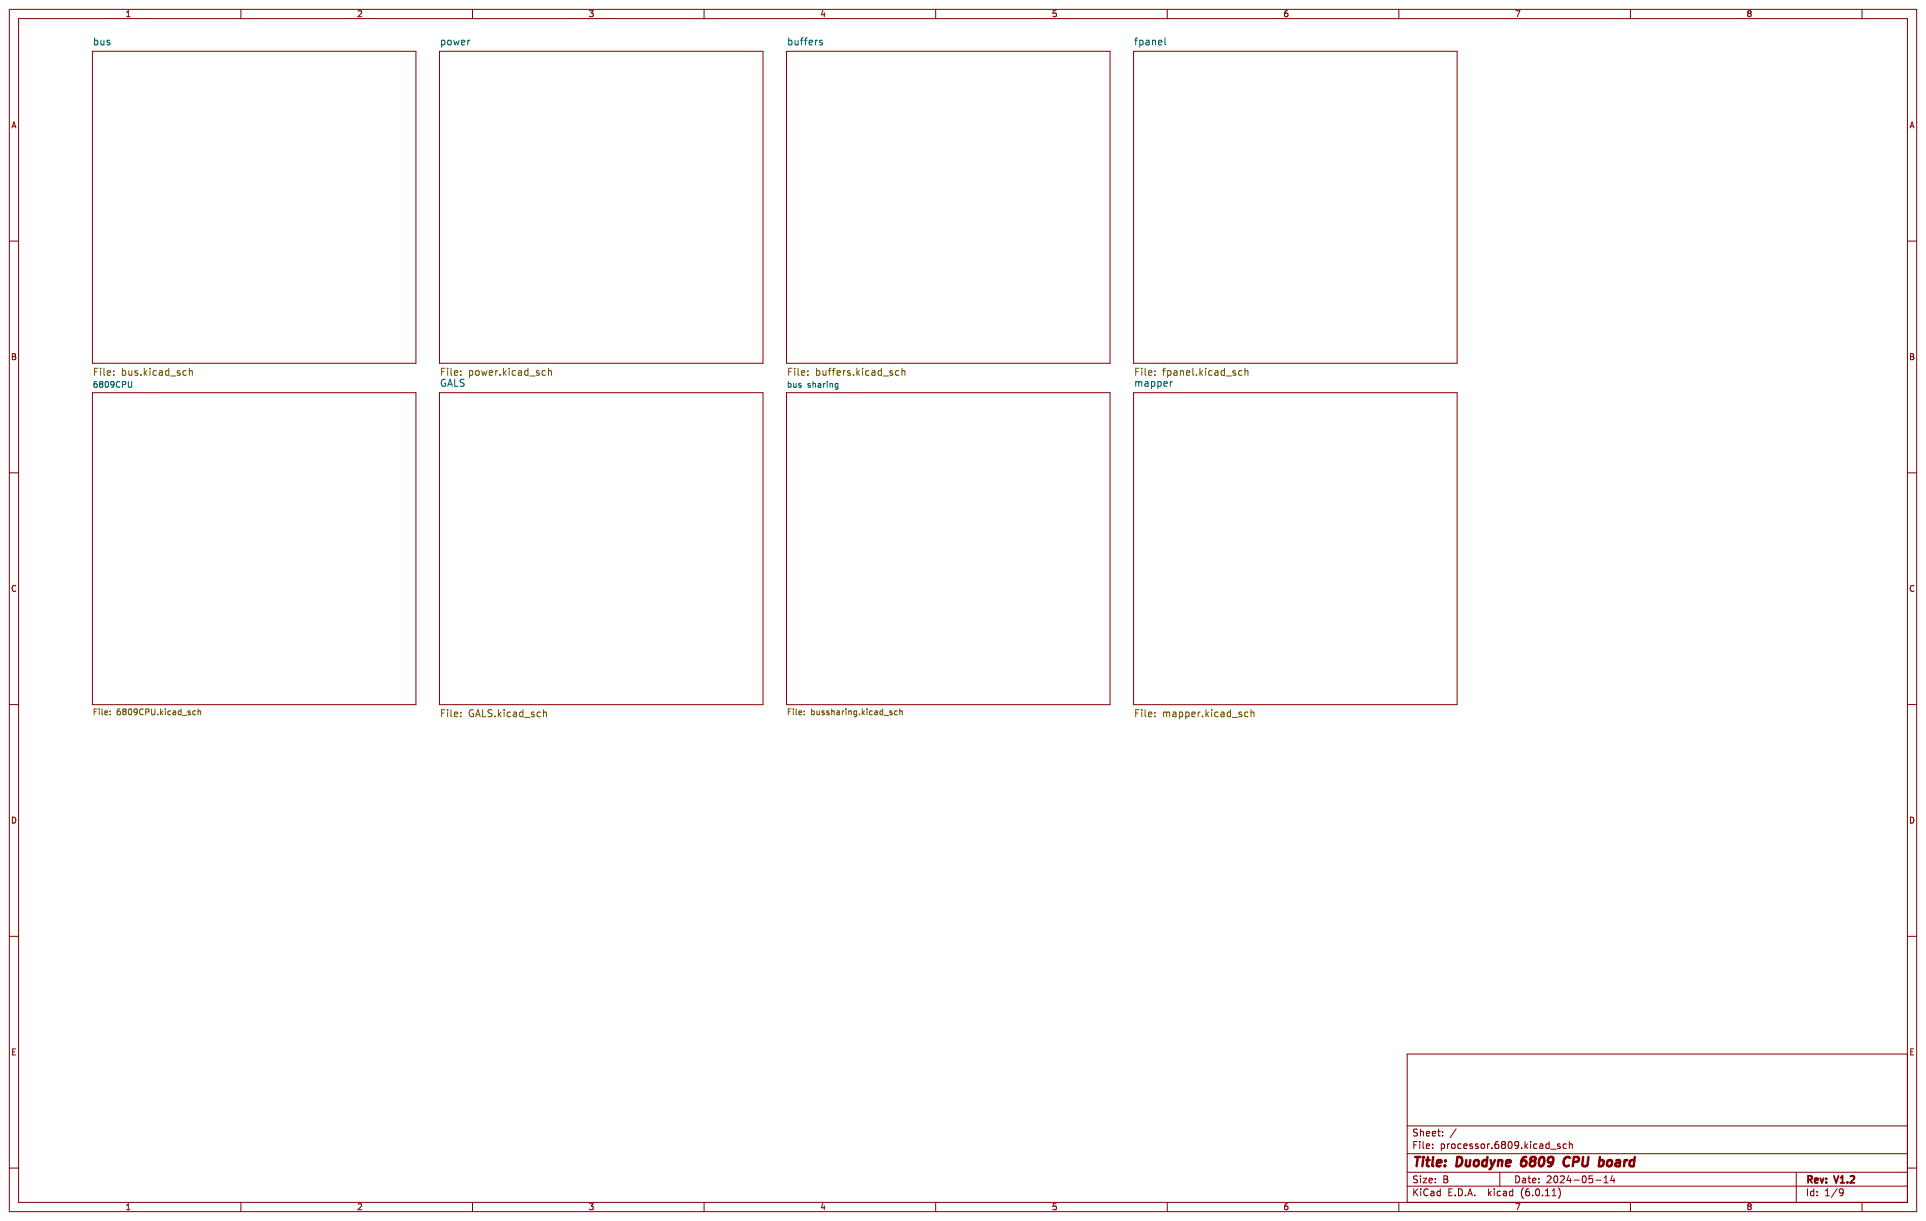
[picture p244: page 1]

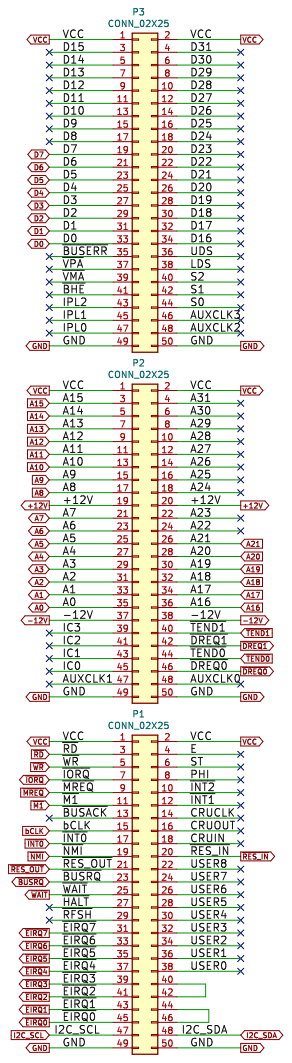
[picture p245: page 2]

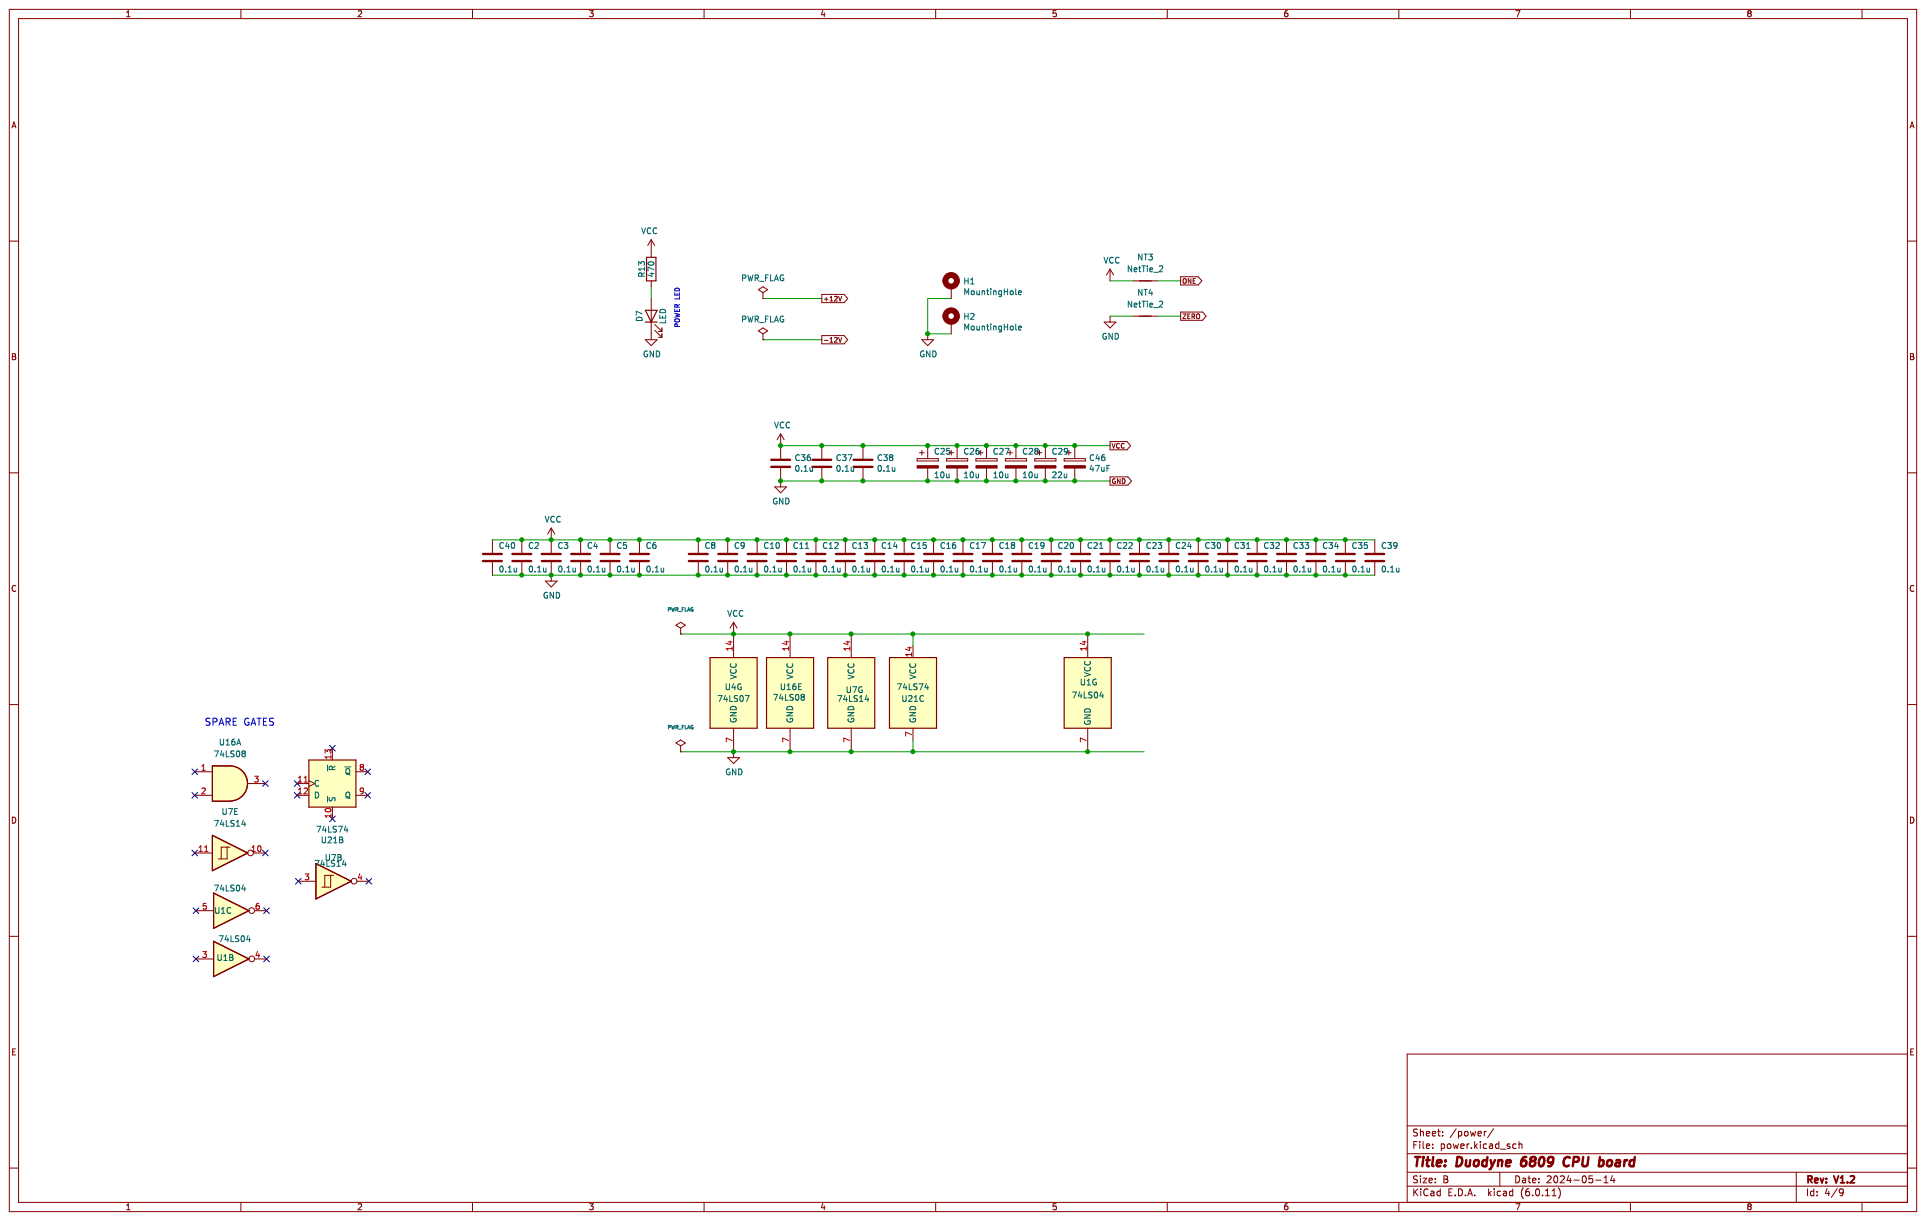
[picture p246: page 3]

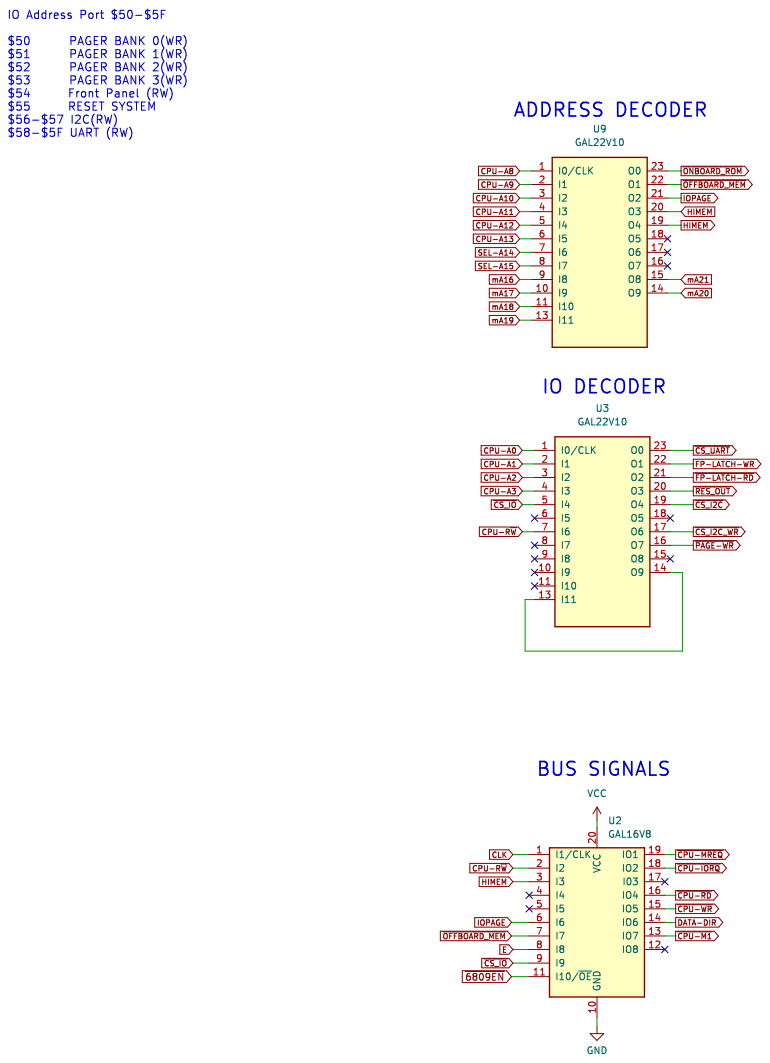
[picture p247: page 4]

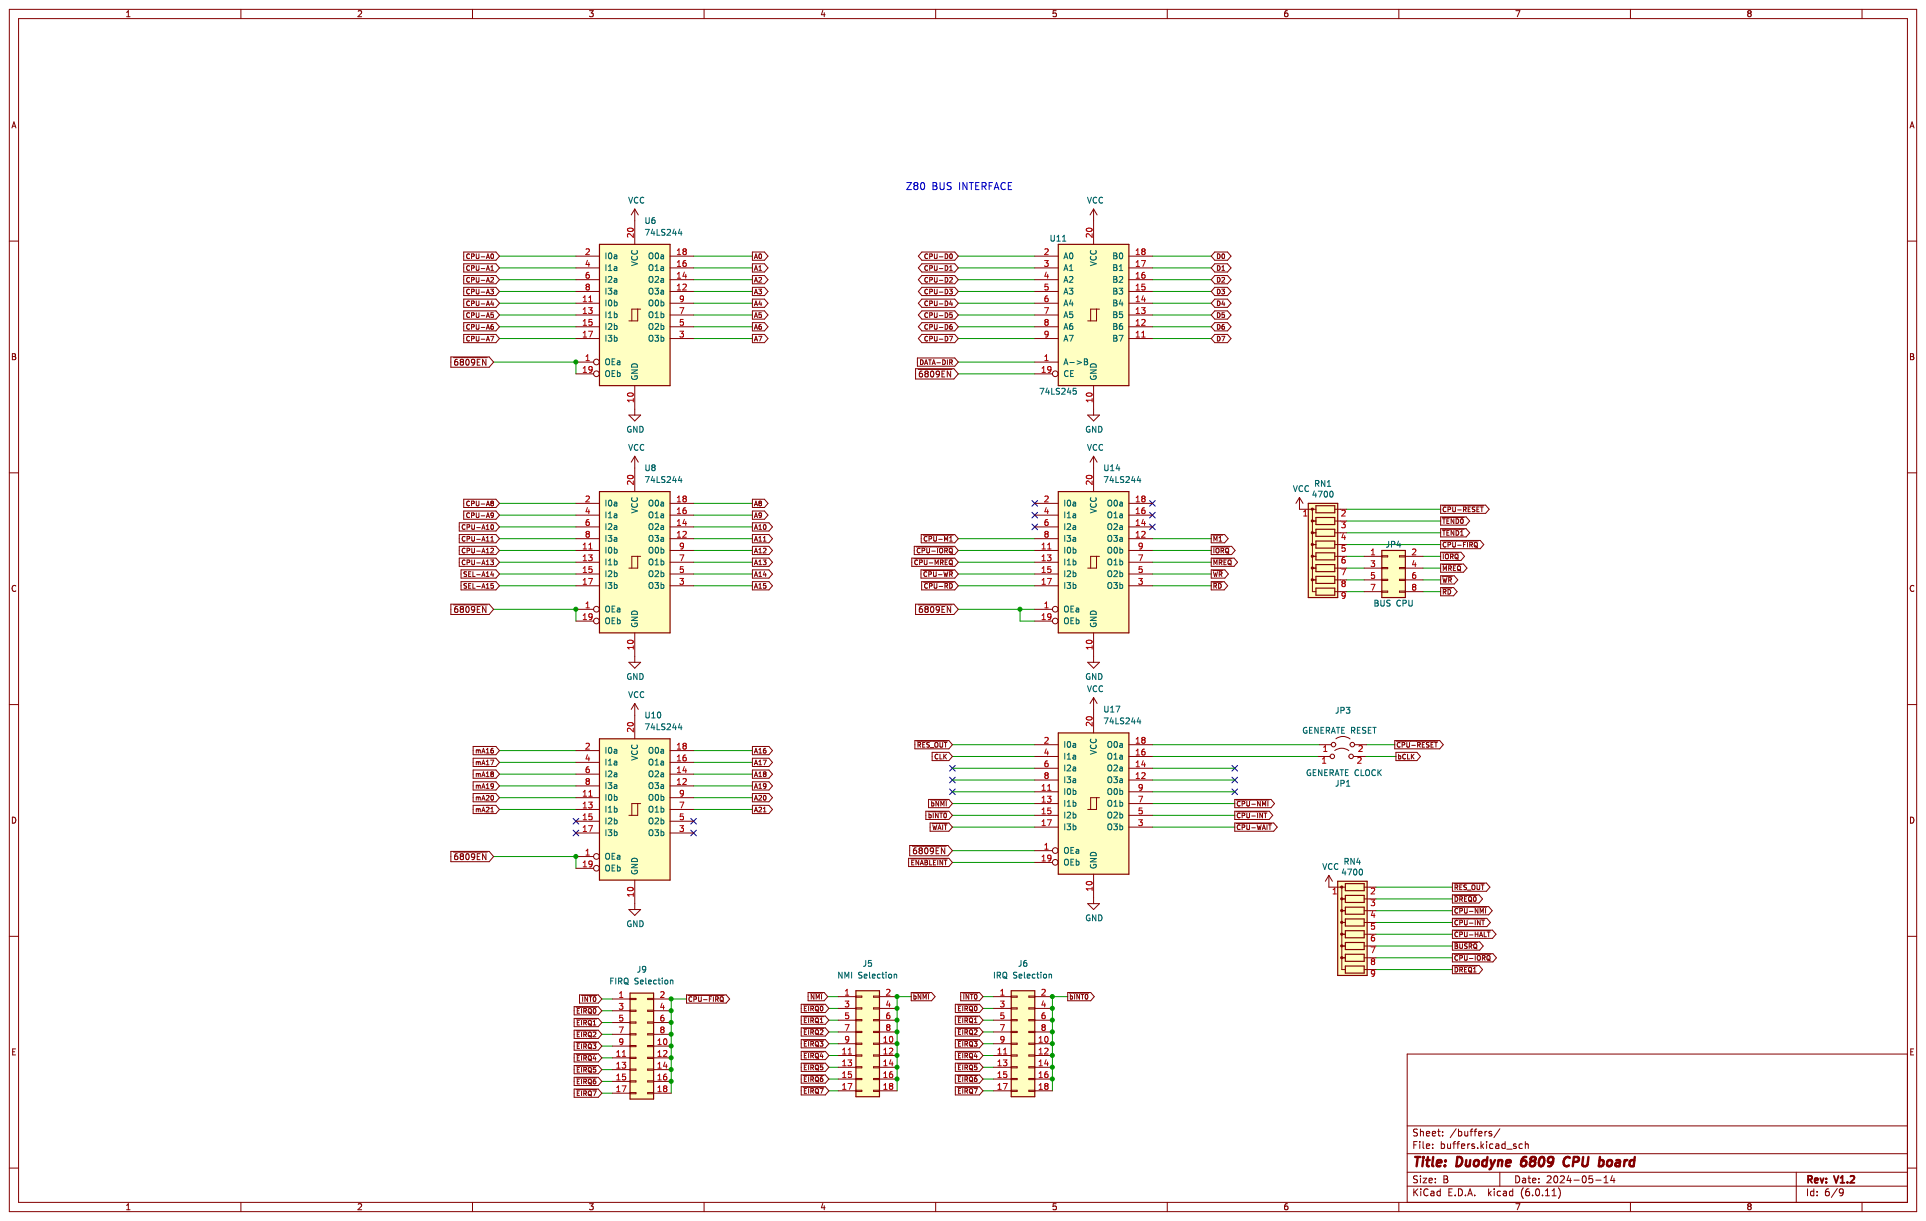
[picture p248: page 5]

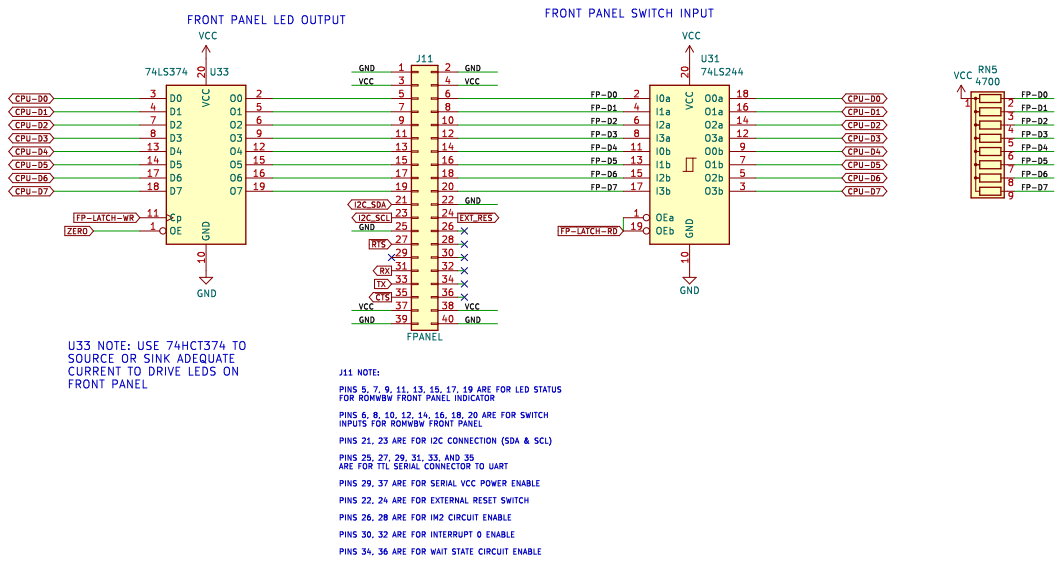
[picture p249: page 6]

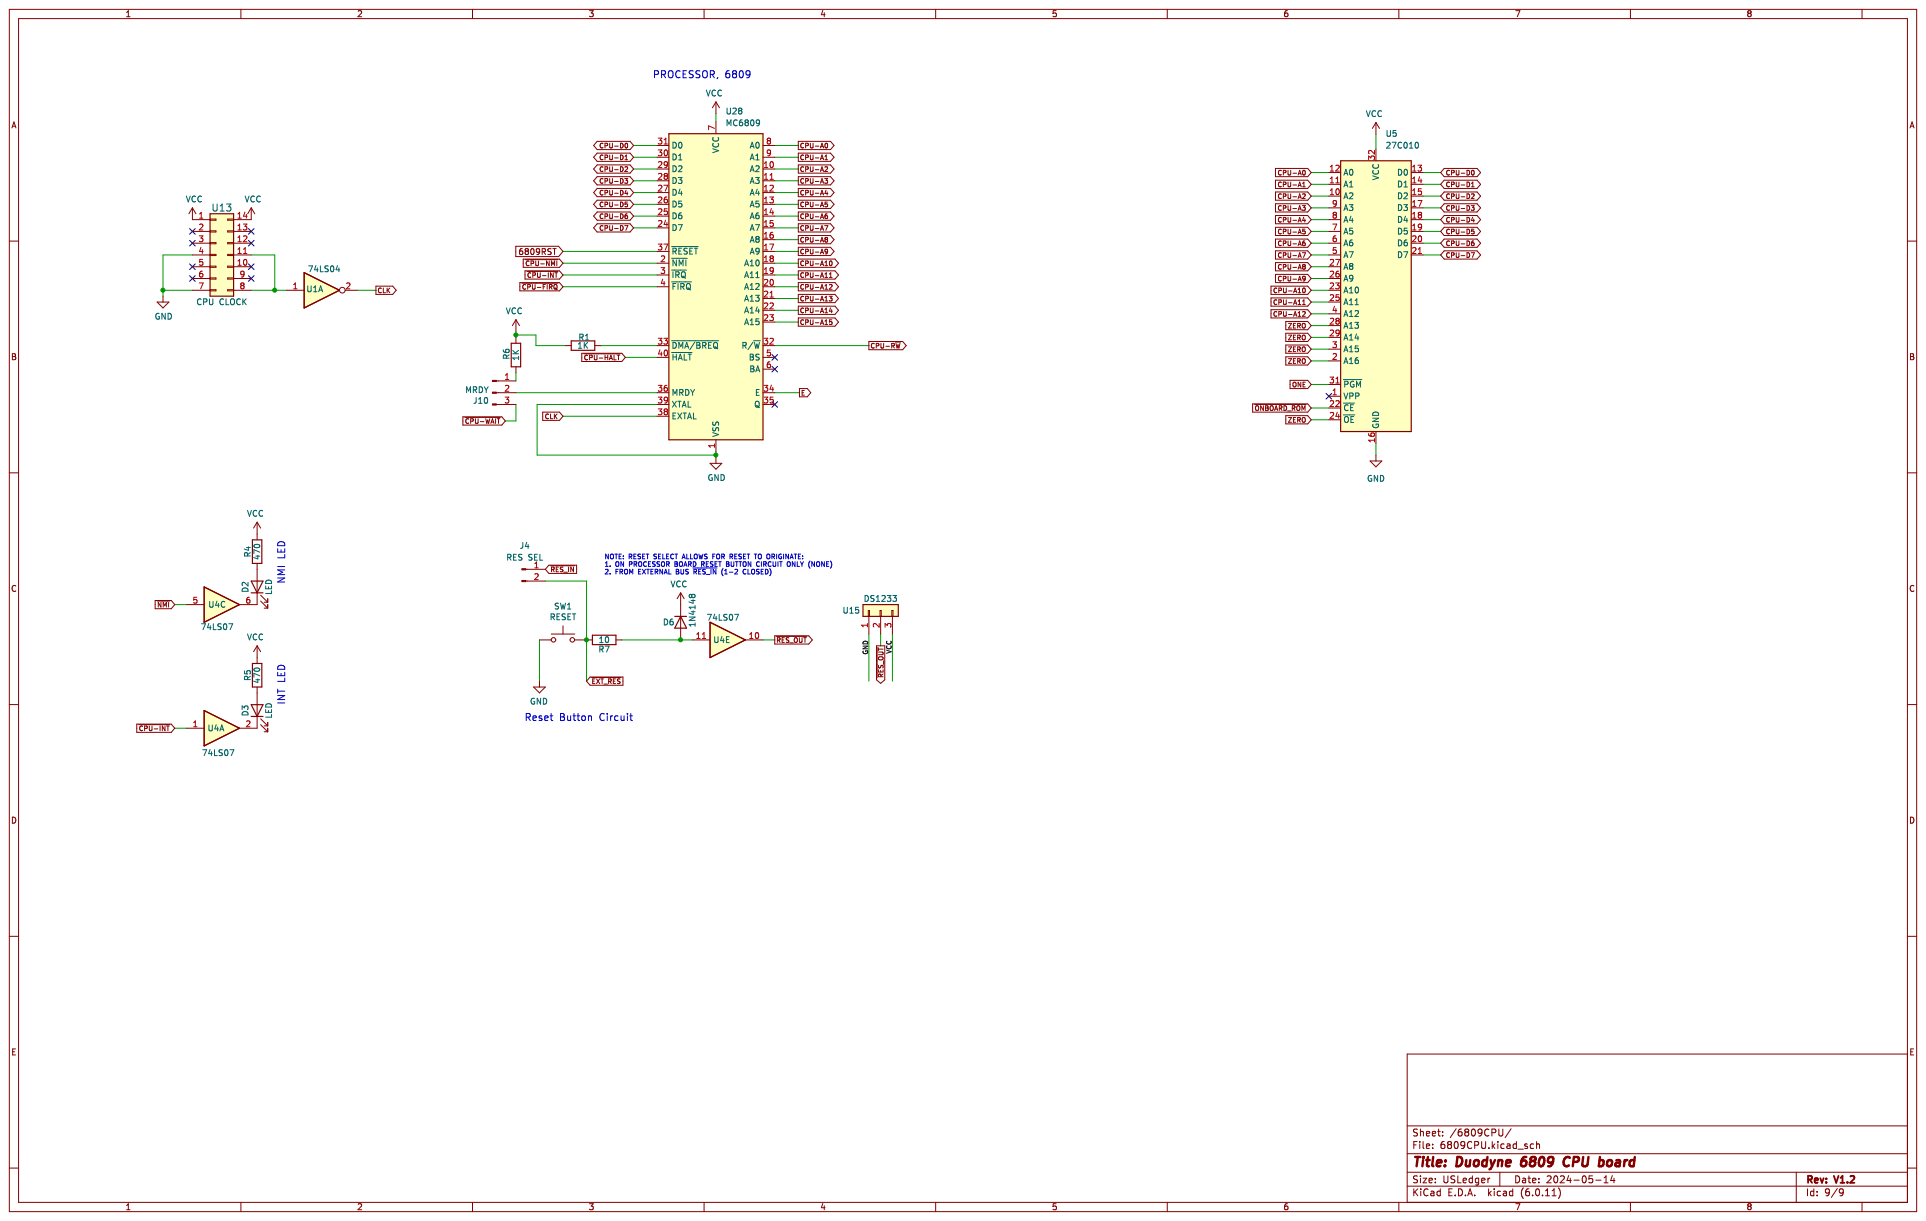
[picture p250: page 7]

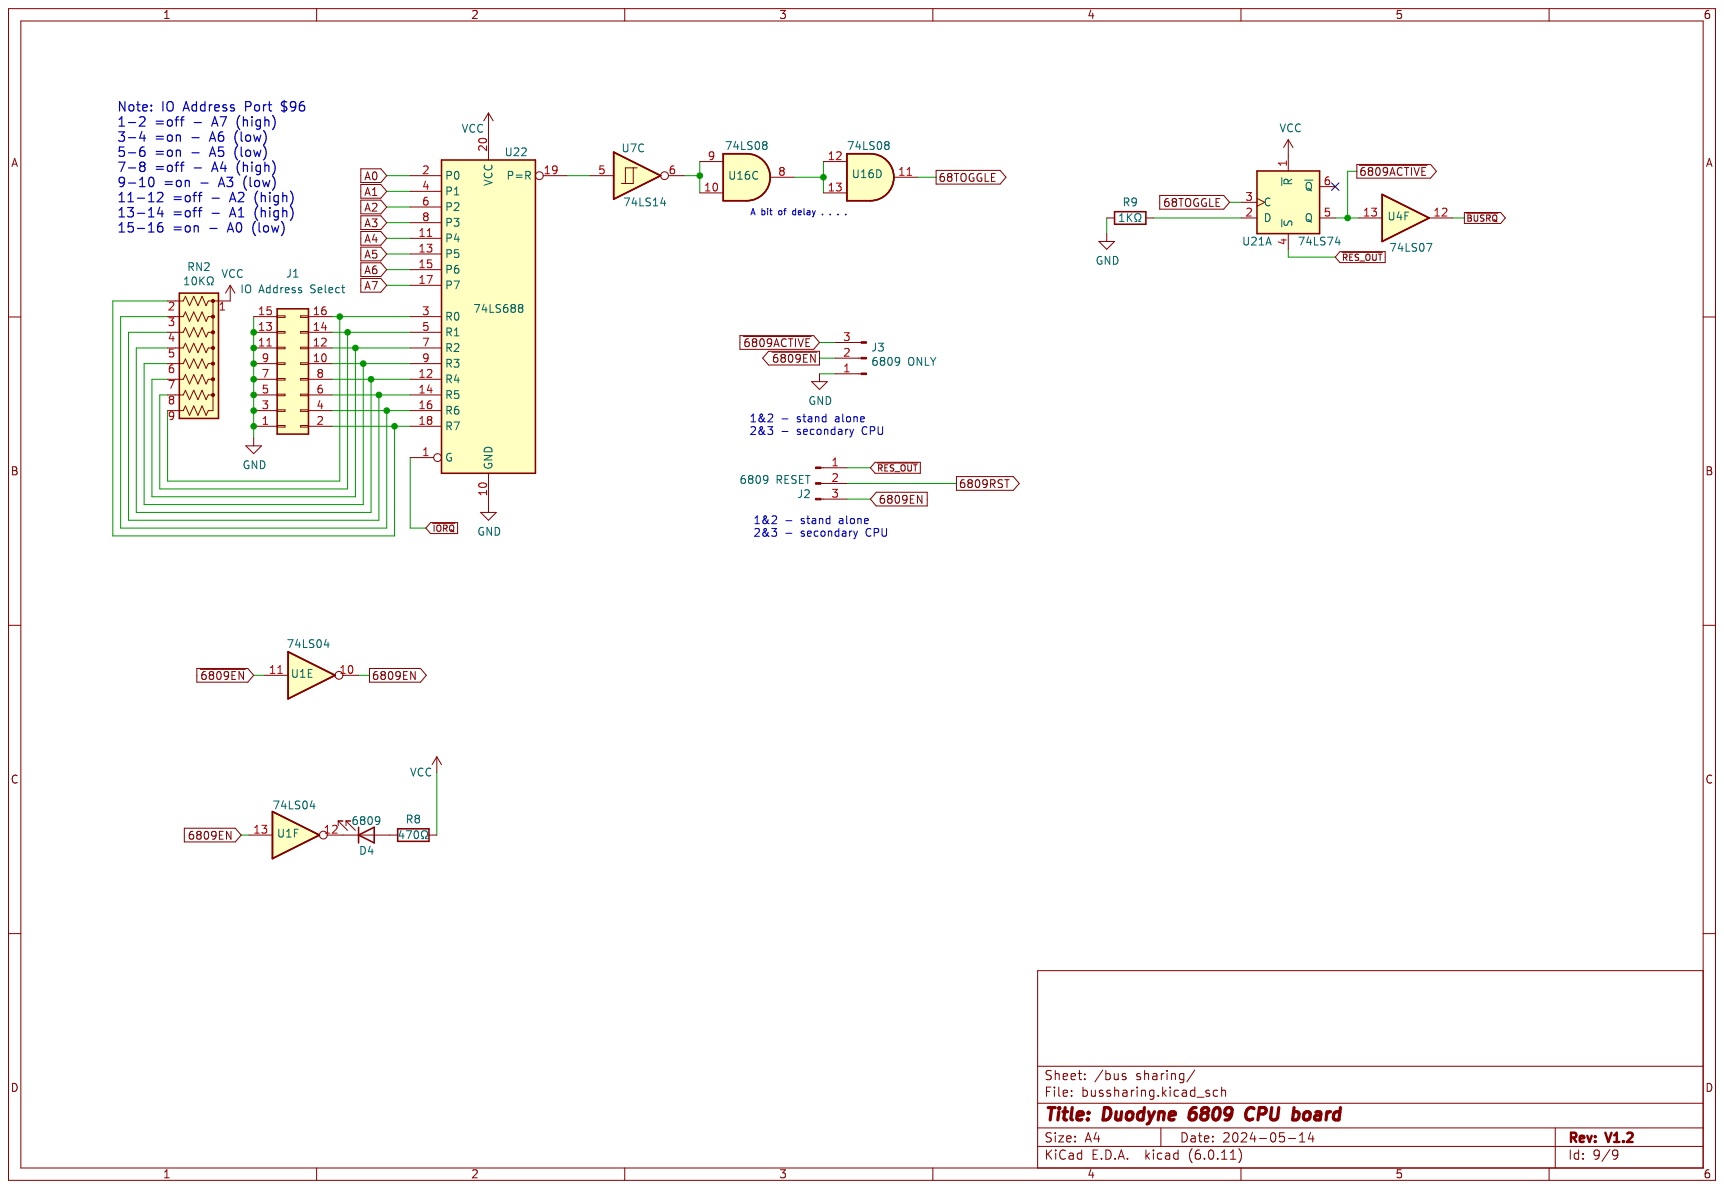
[picture p251: page 8]

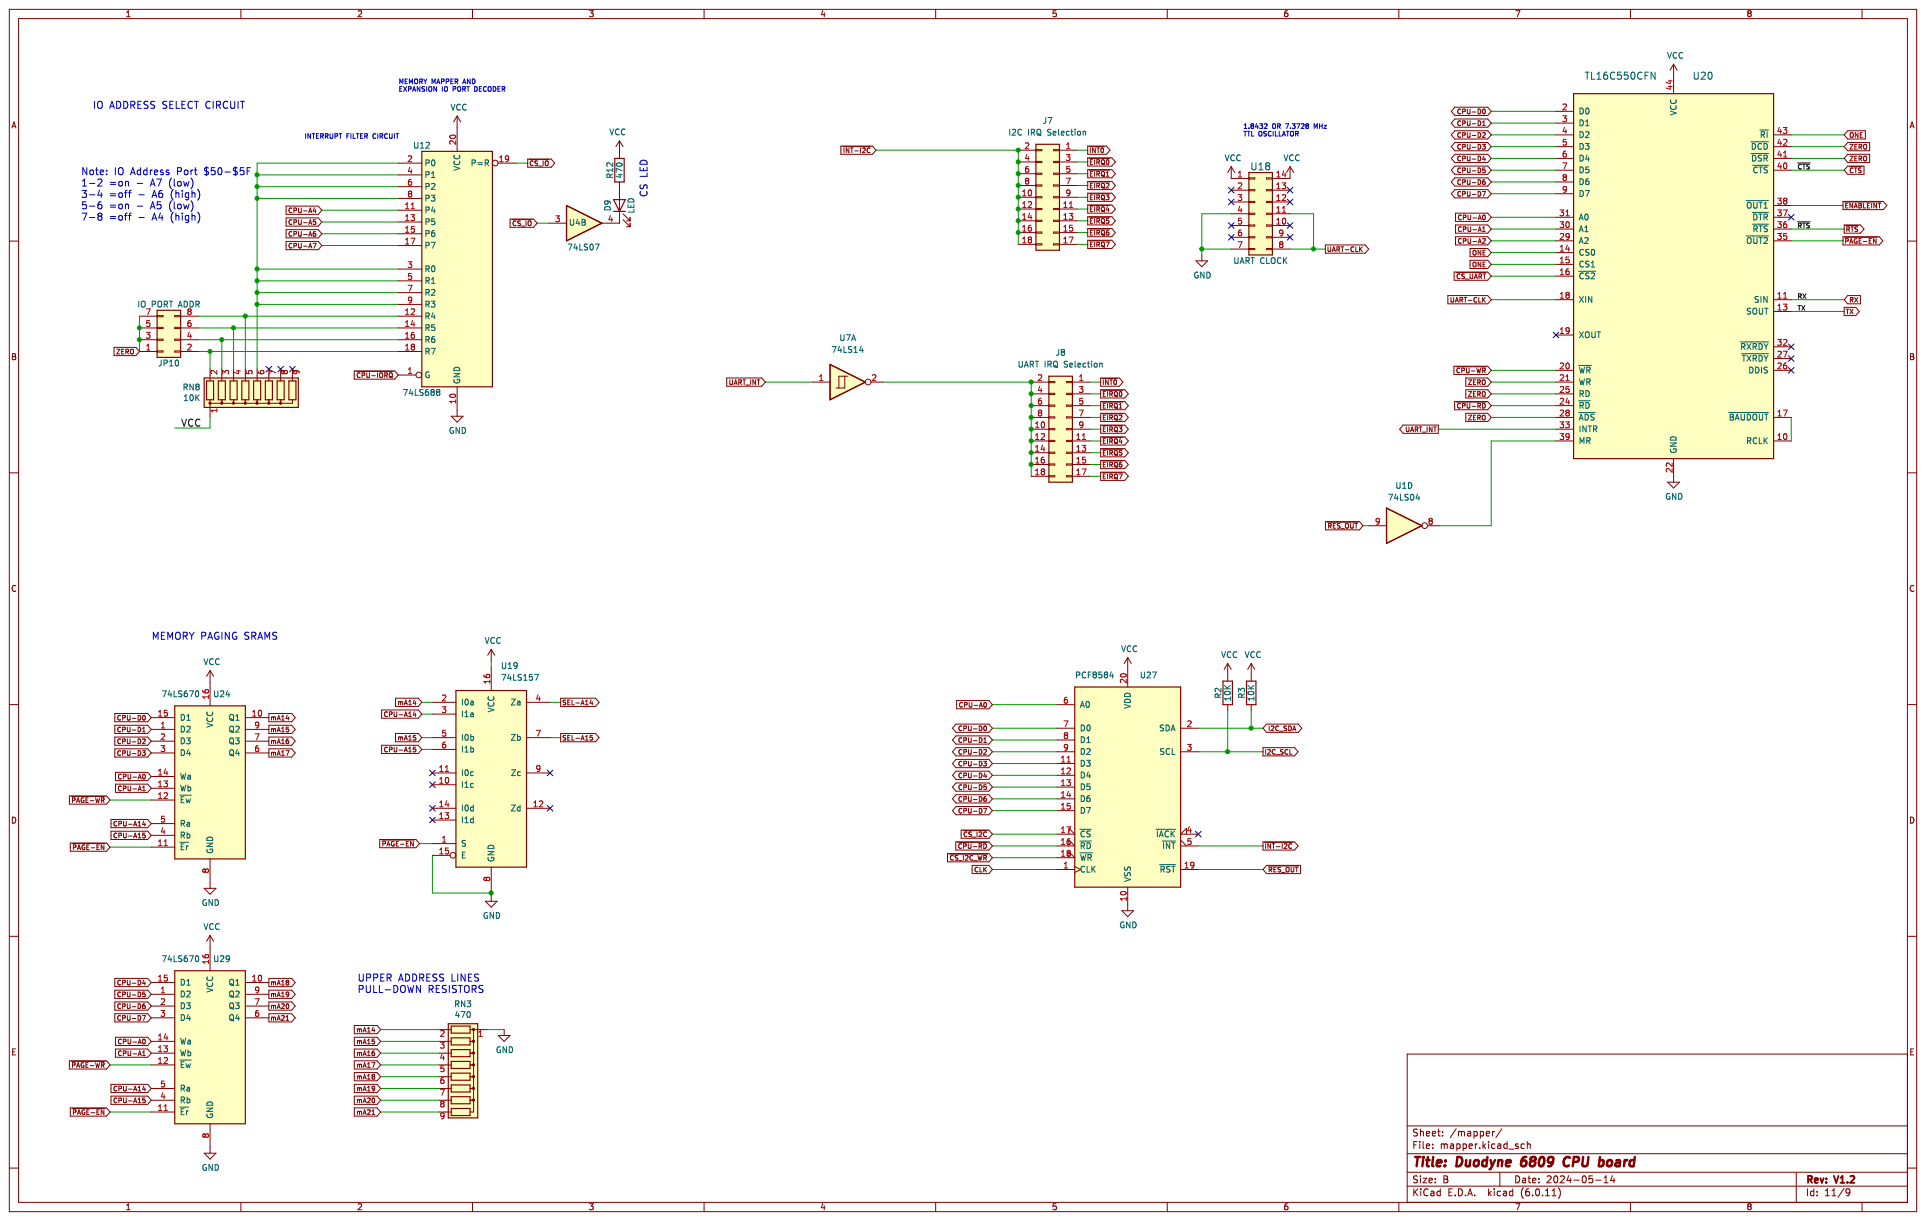
[picture p252: page 9]
