lynchaj/duodyne/!Development/24 DAISY256, V1.0/DAISY256.schematic.pdf

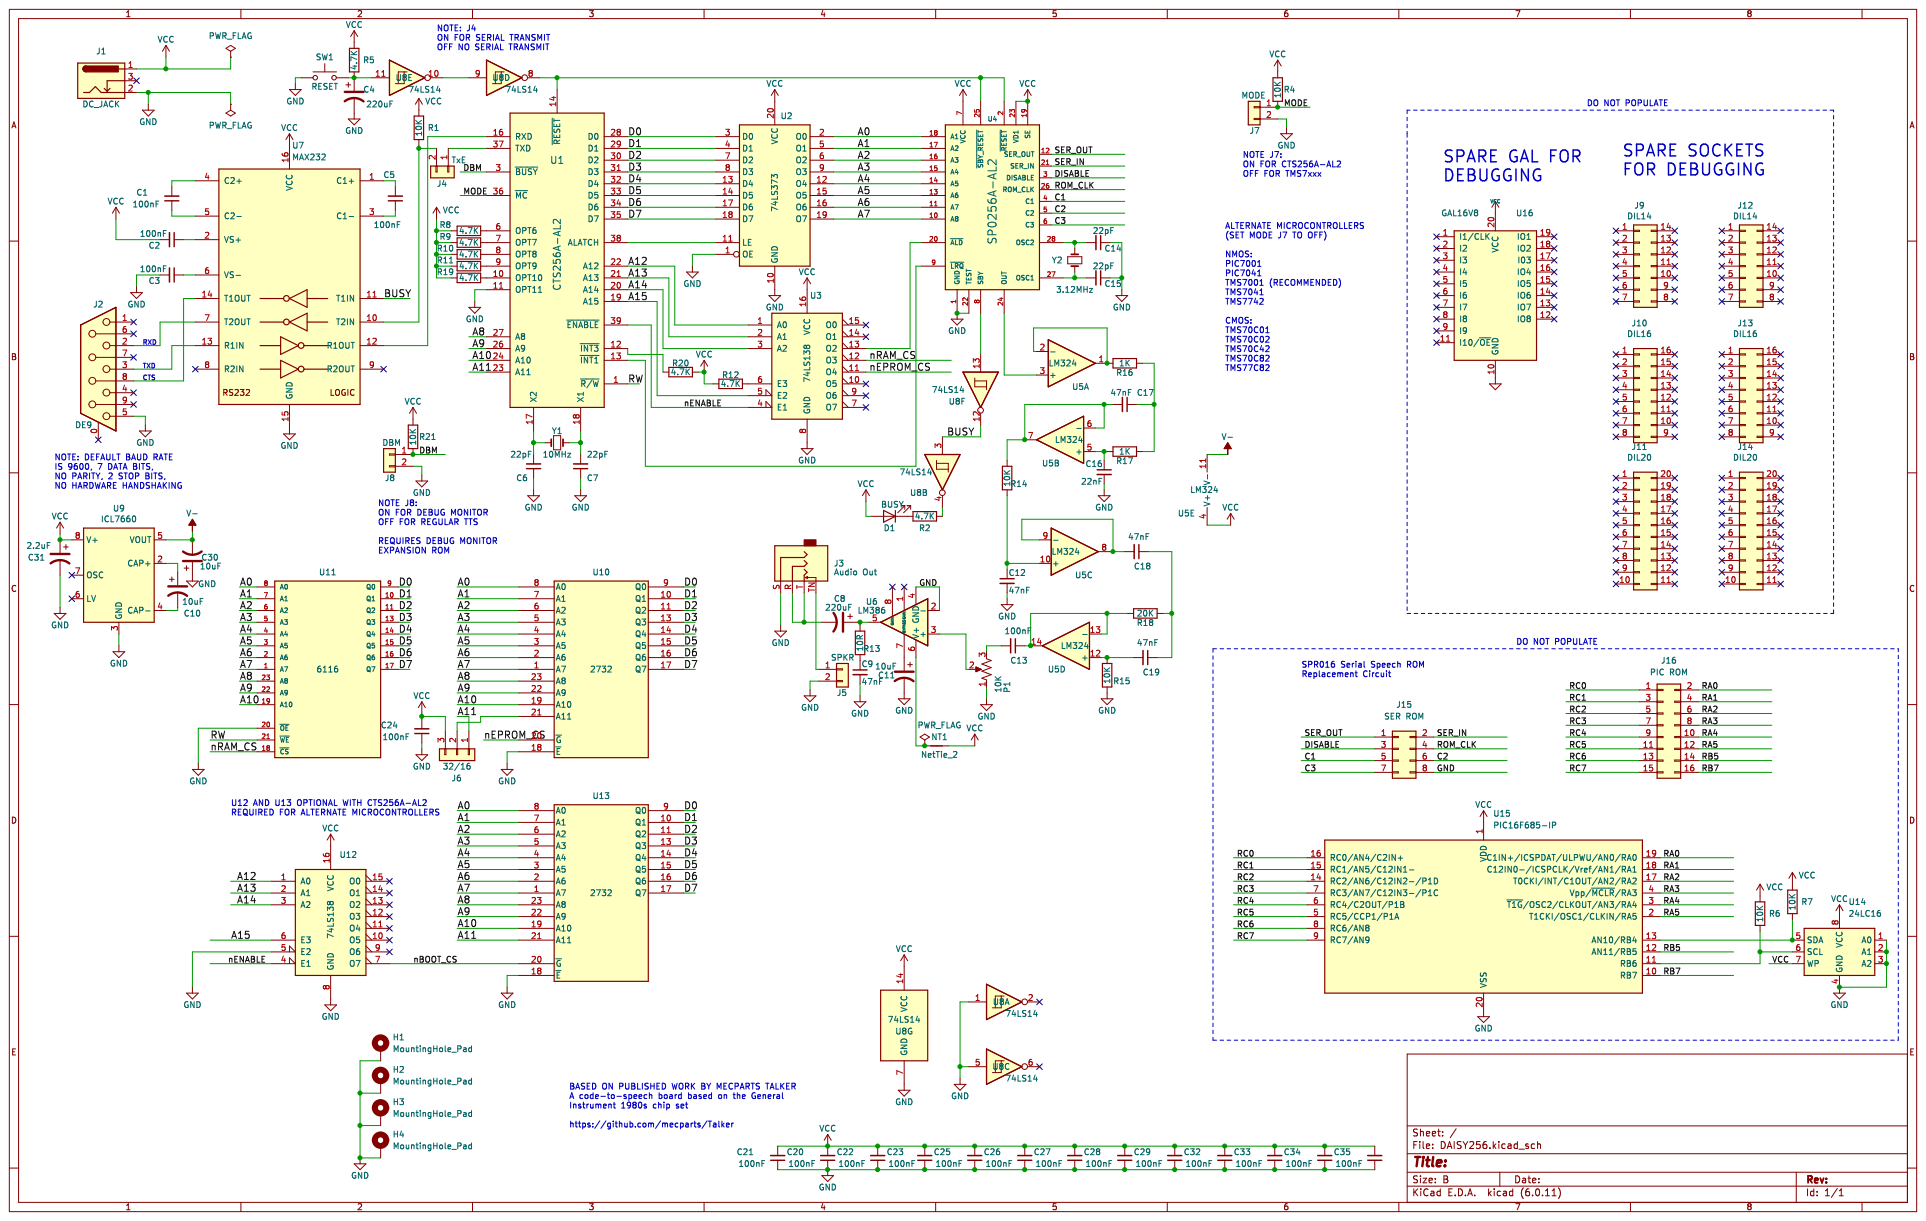
[picture p253: page 1]
