lynchaj/duodyne/!Development/06 input-output.Multi, V1.1/input-output.Multi.schematic.pdf

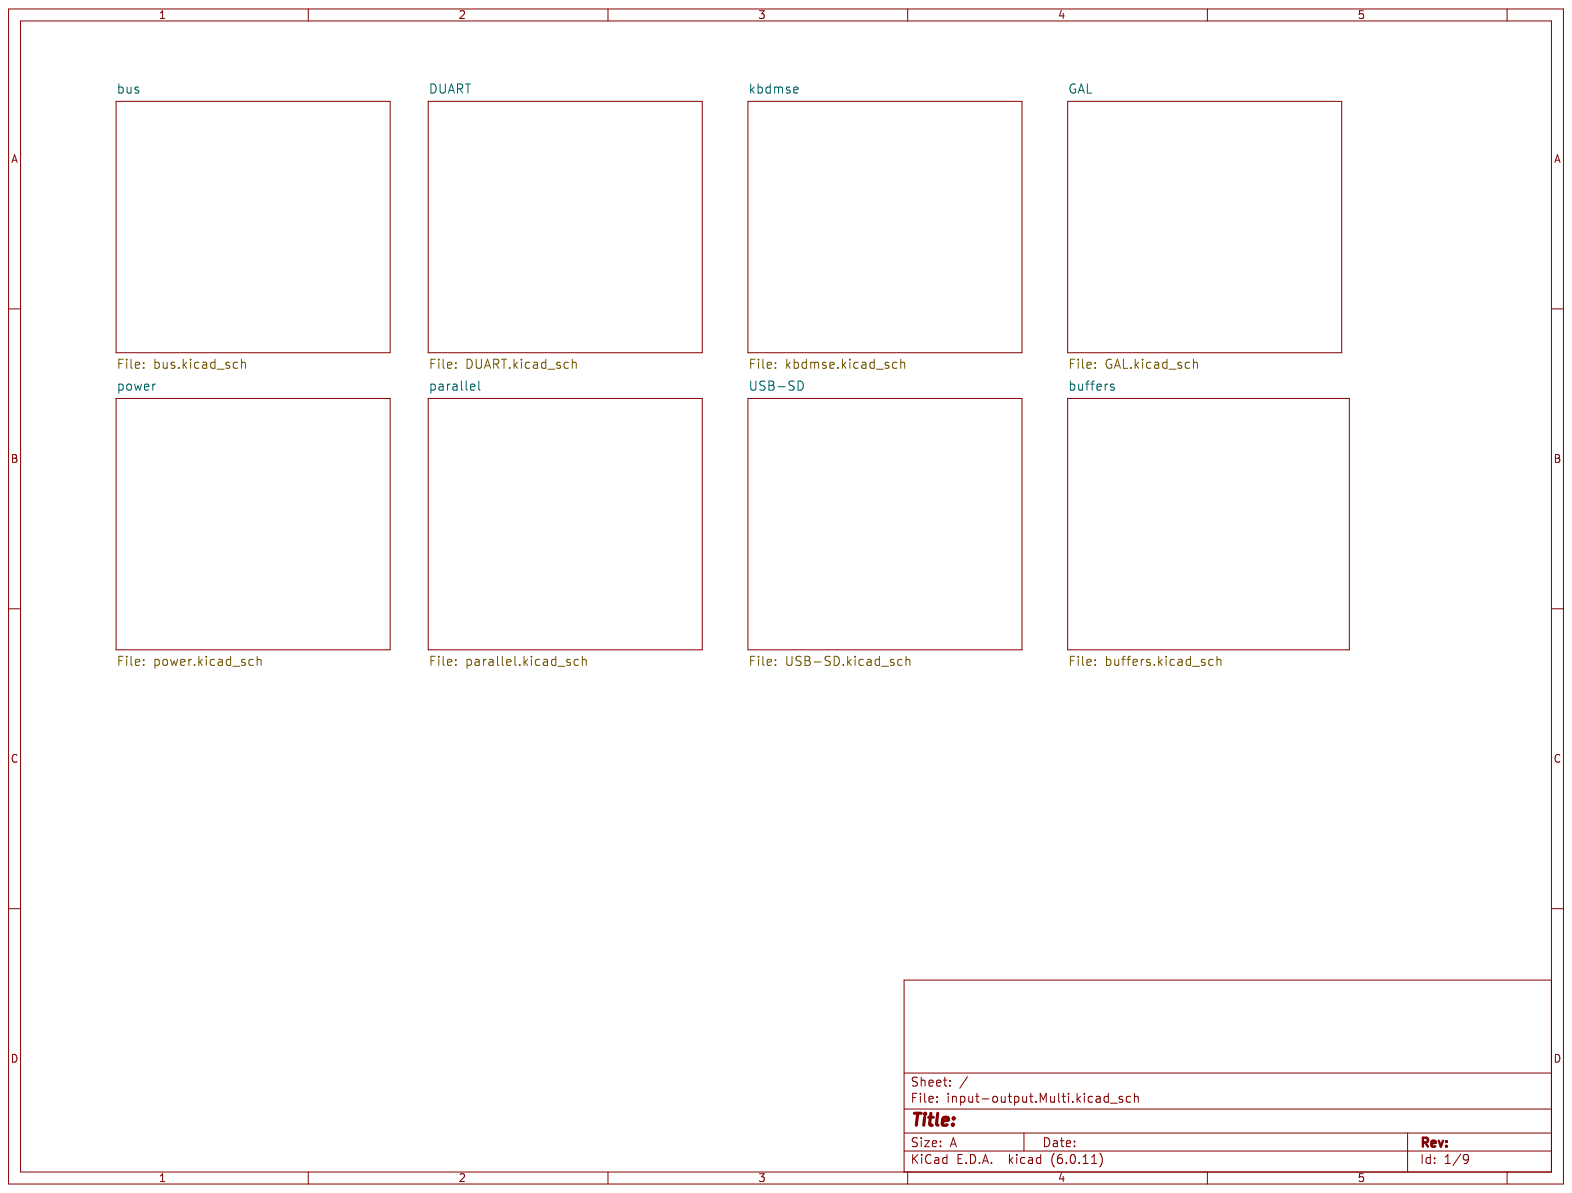
[picture p254: page 1]


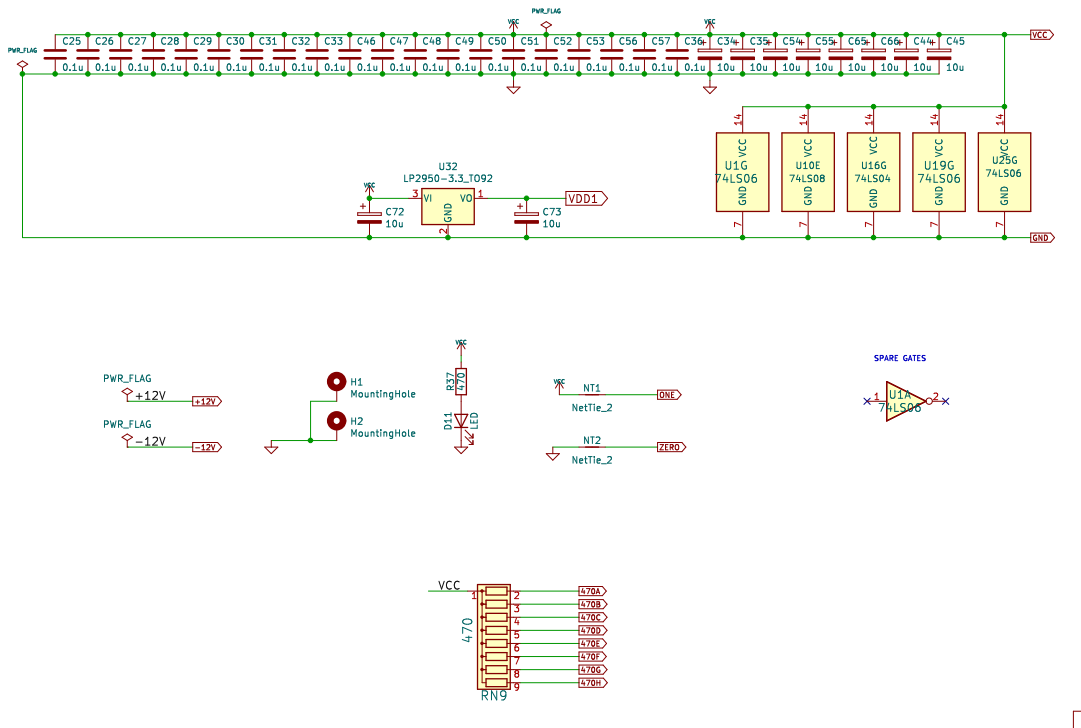
[picture p255: page 3]

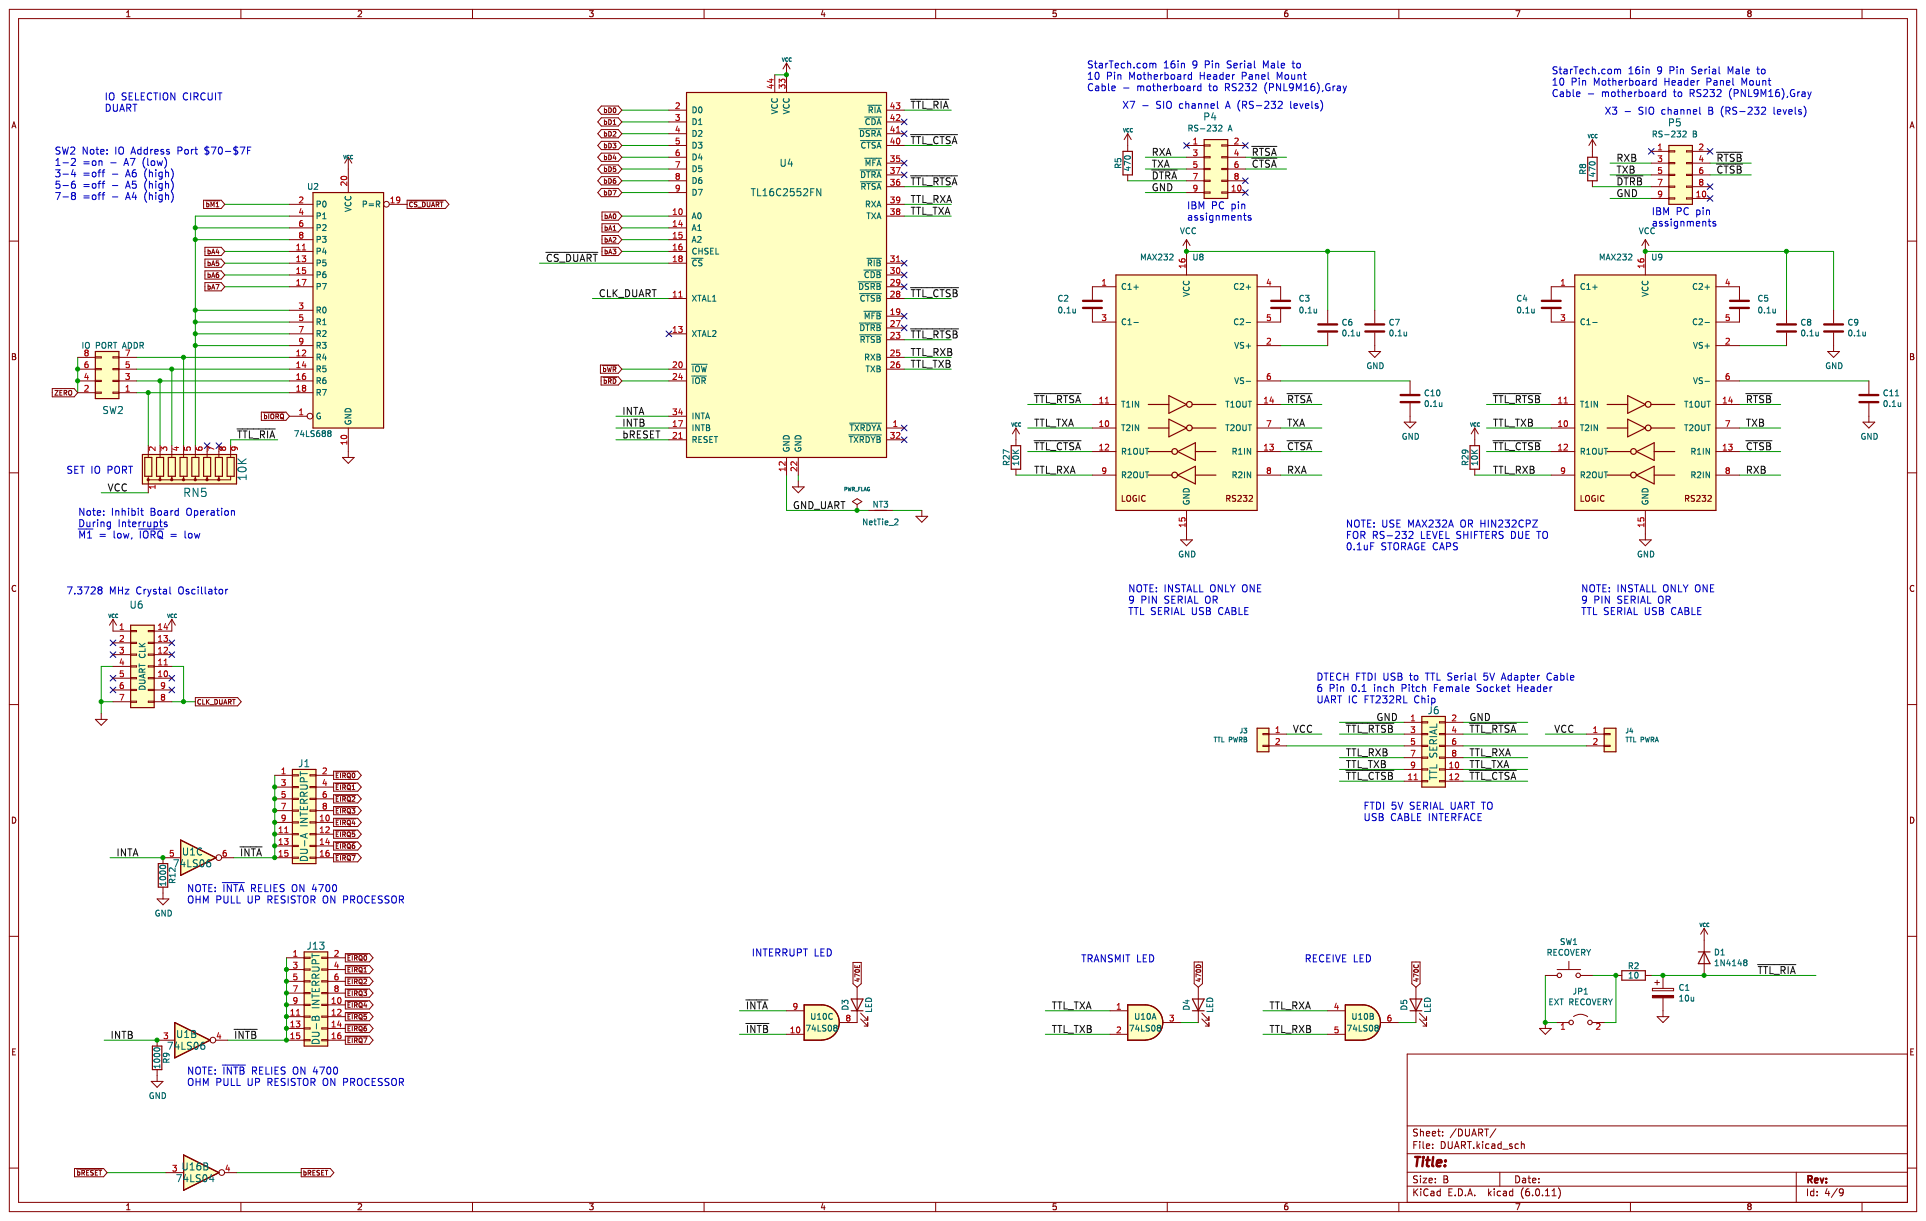
[picture p256: page 4]


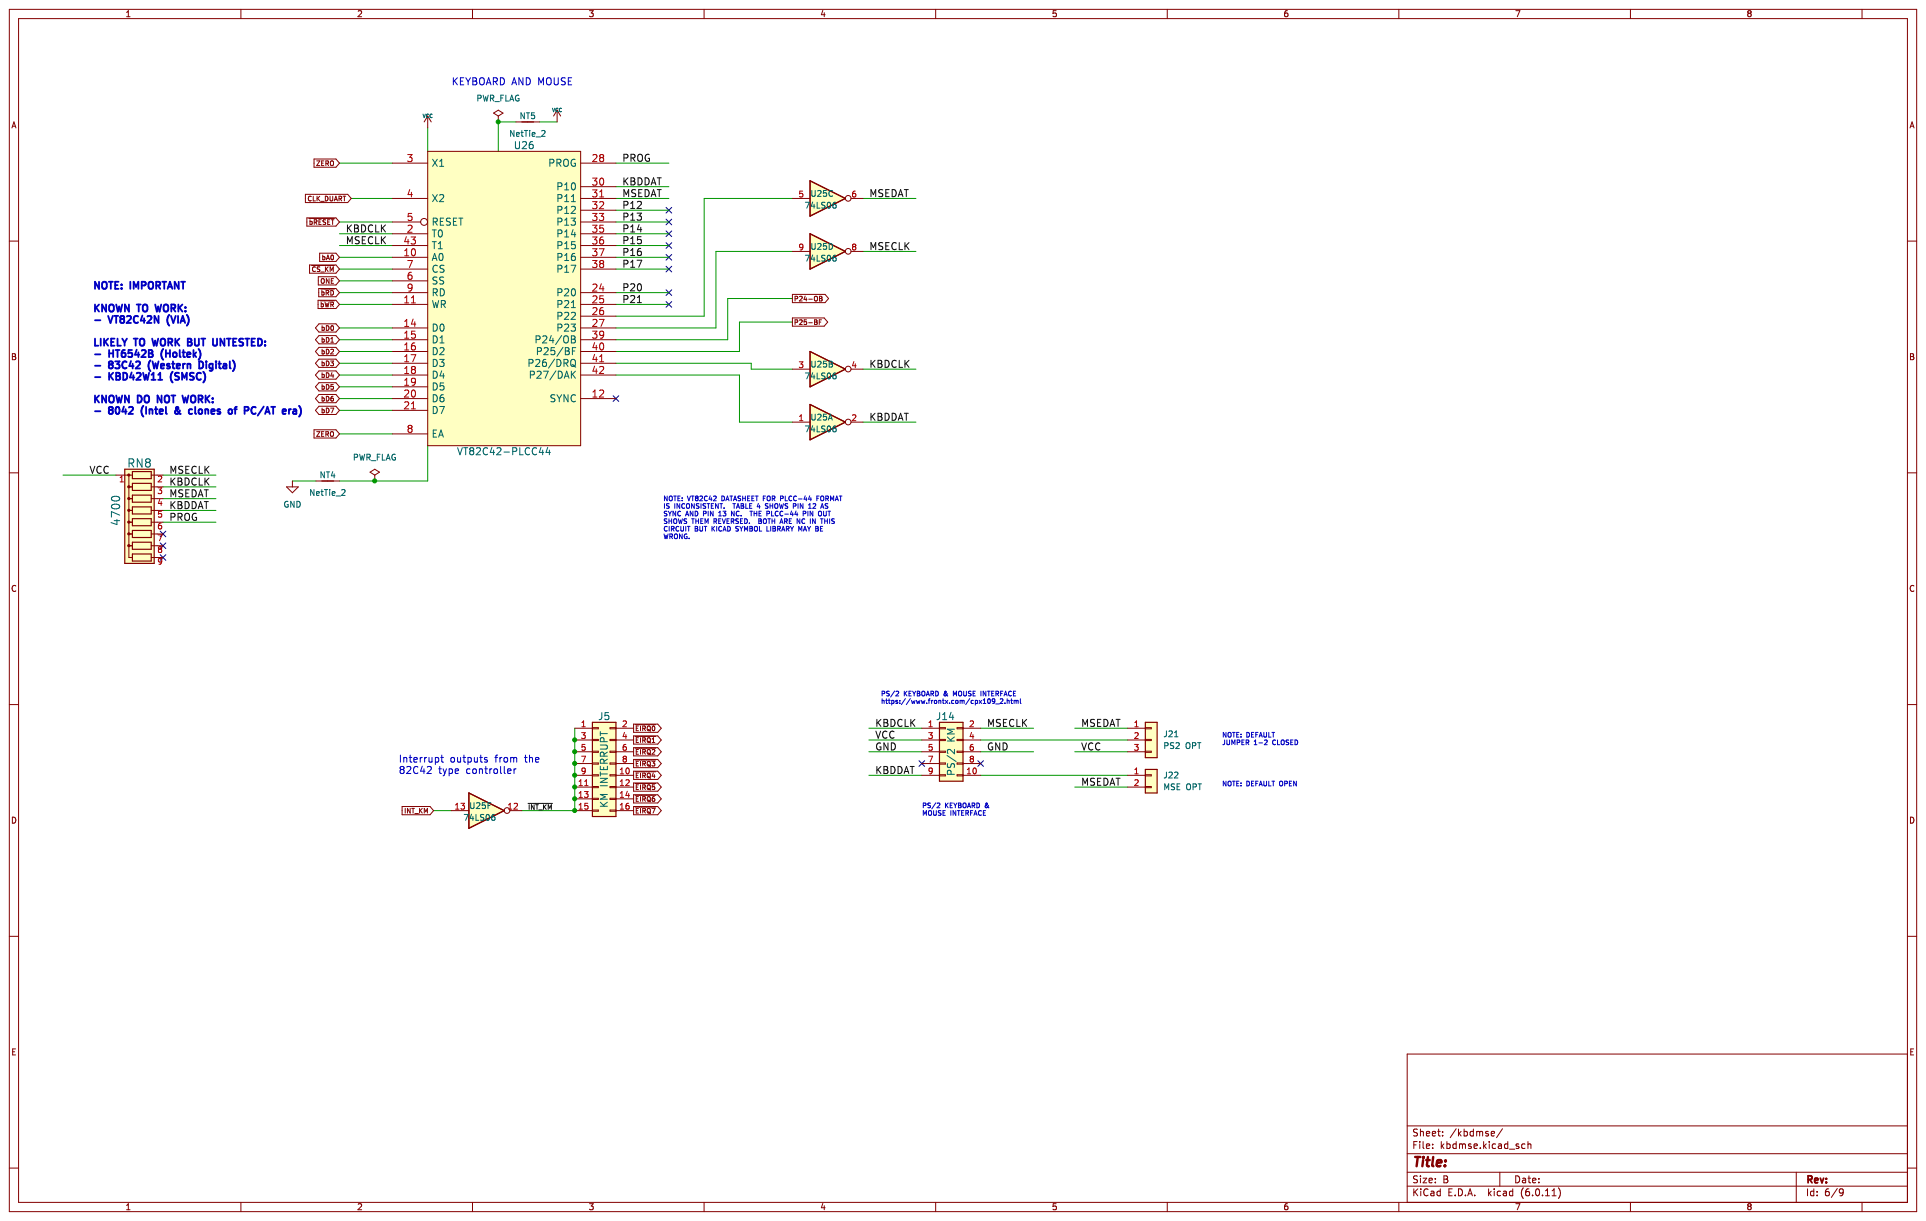
[picture p257: page 6]

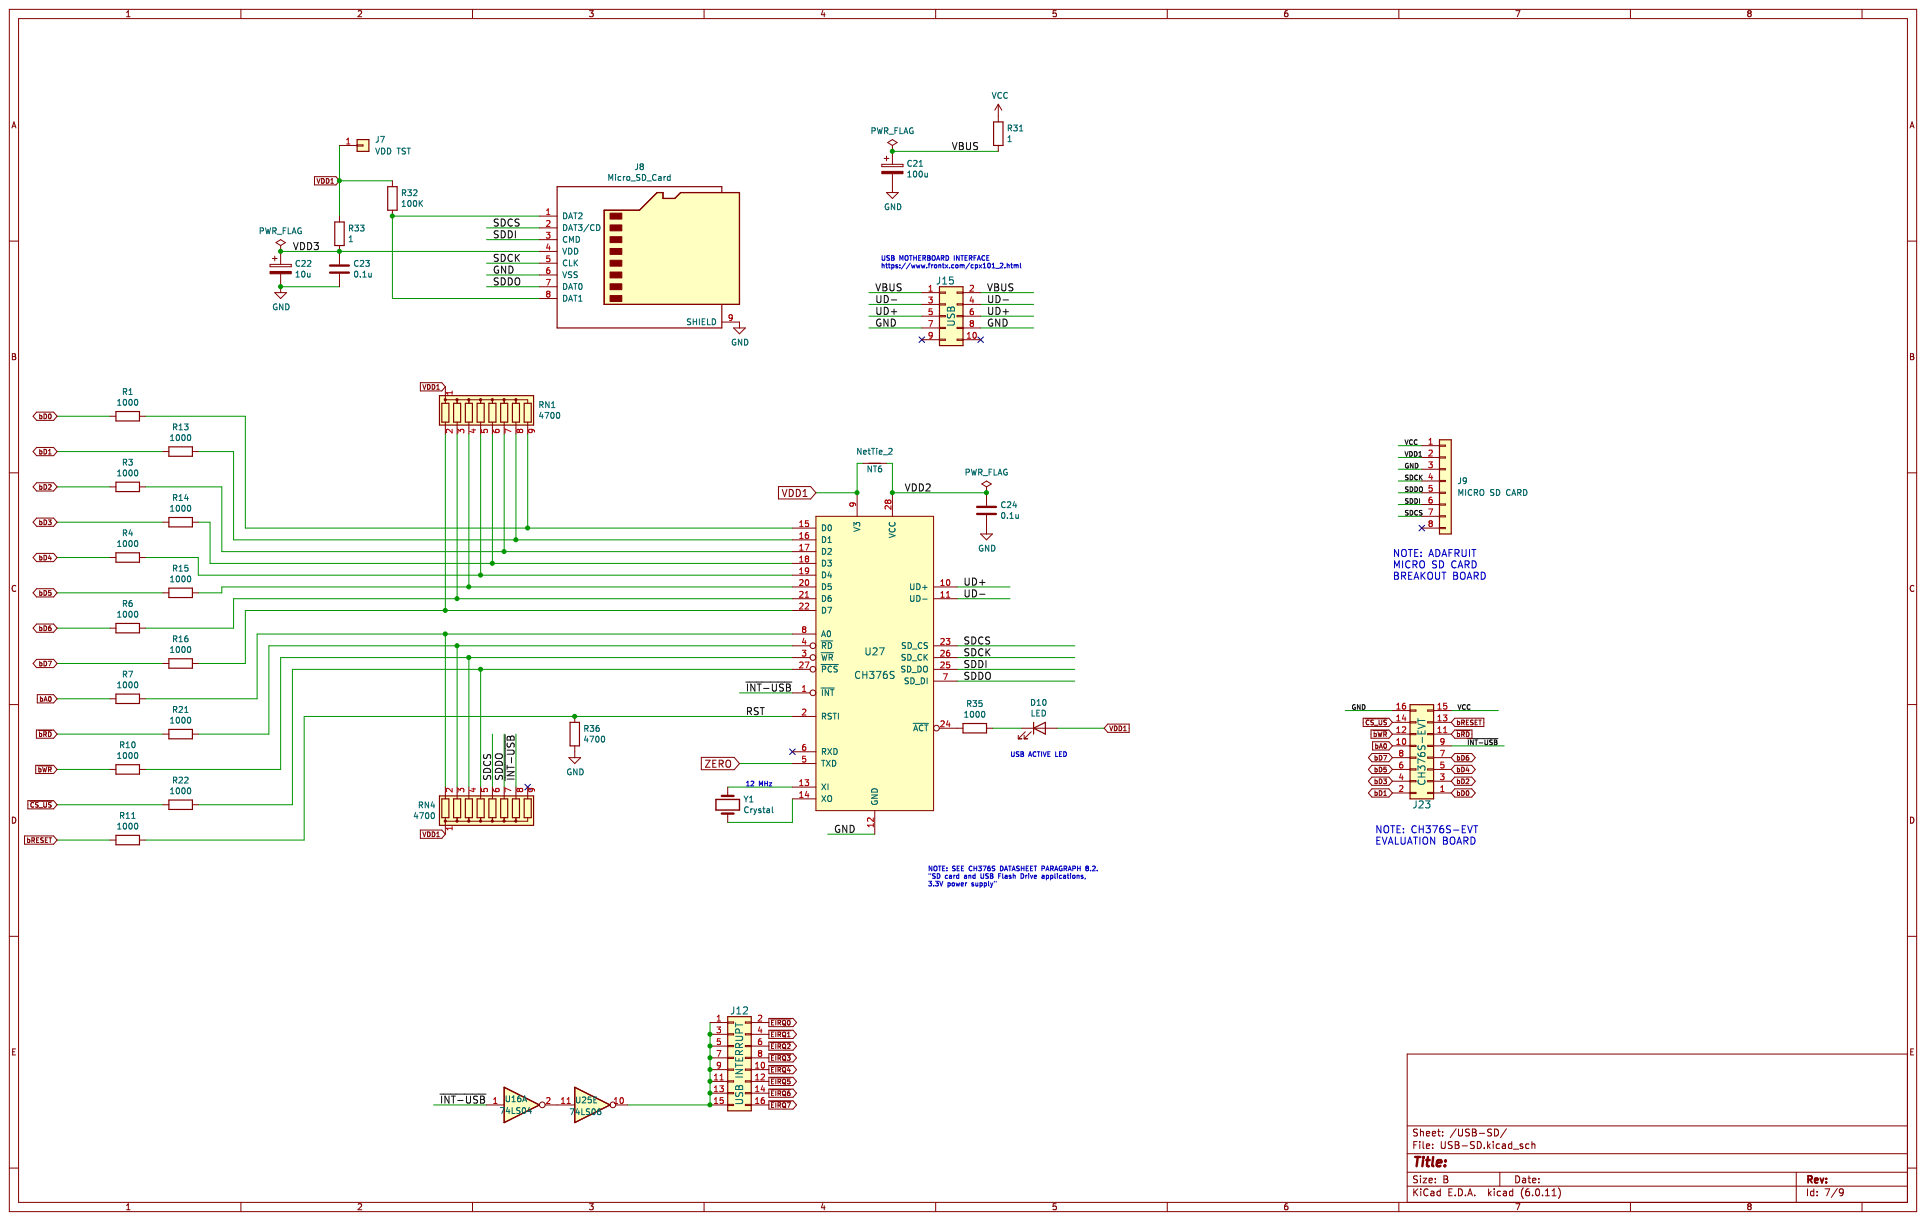
[picture p258: page 7]
