lynchaj/duodyne/!Development/19 input-output.SelfHost, V1.1/input-output.SelfHost.schematic.pdf

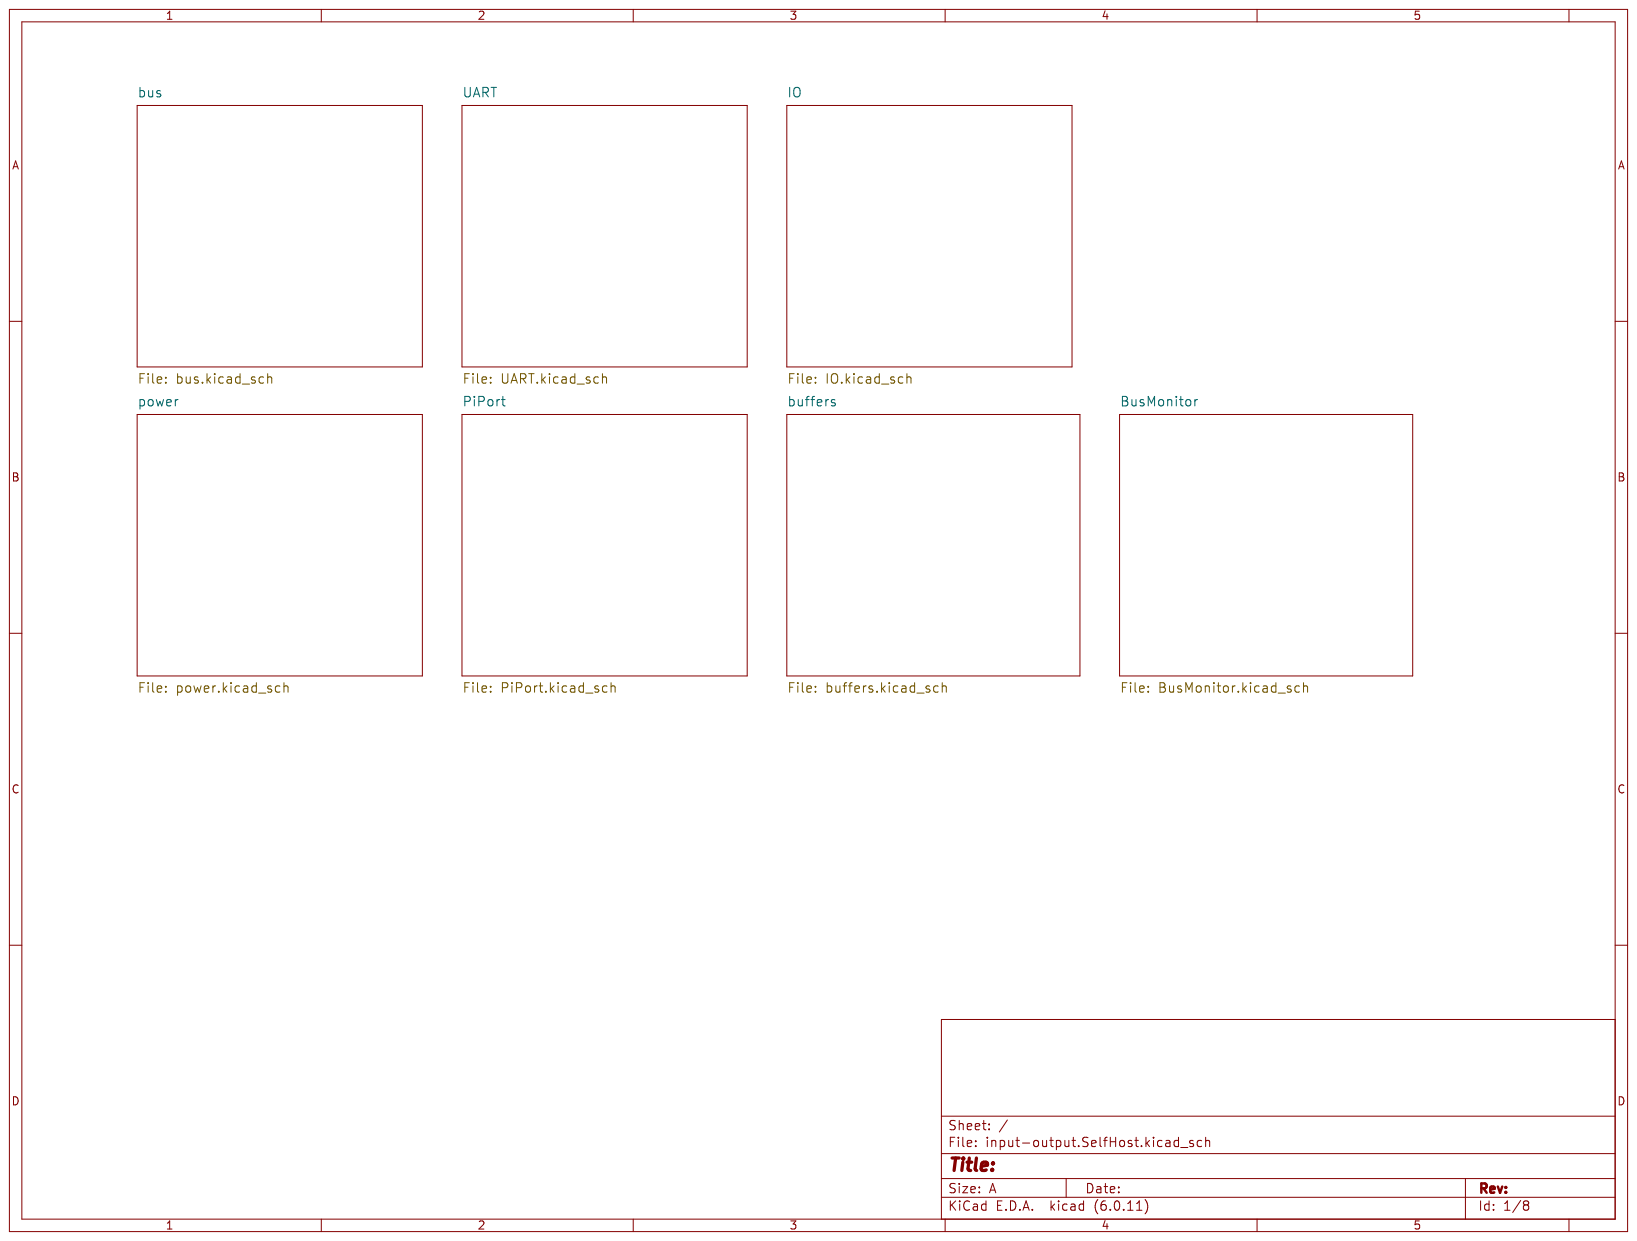
[picture p259: page 1]

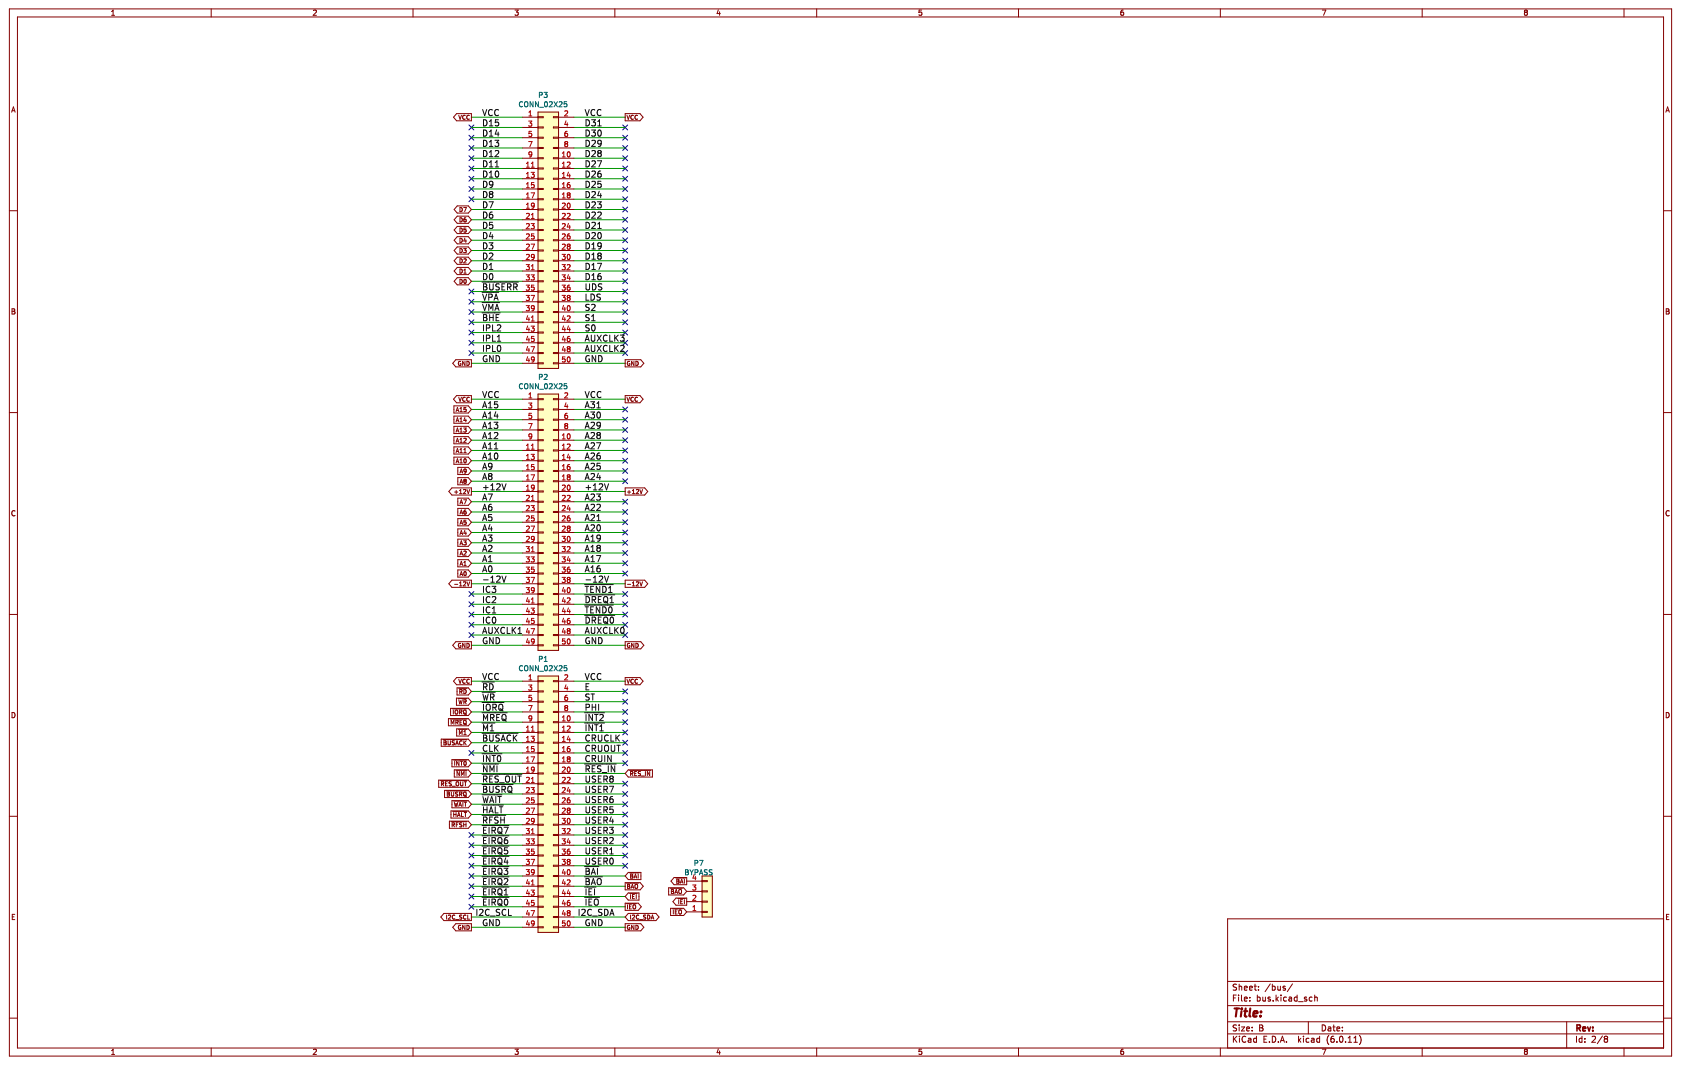
[picture p260: page 2]

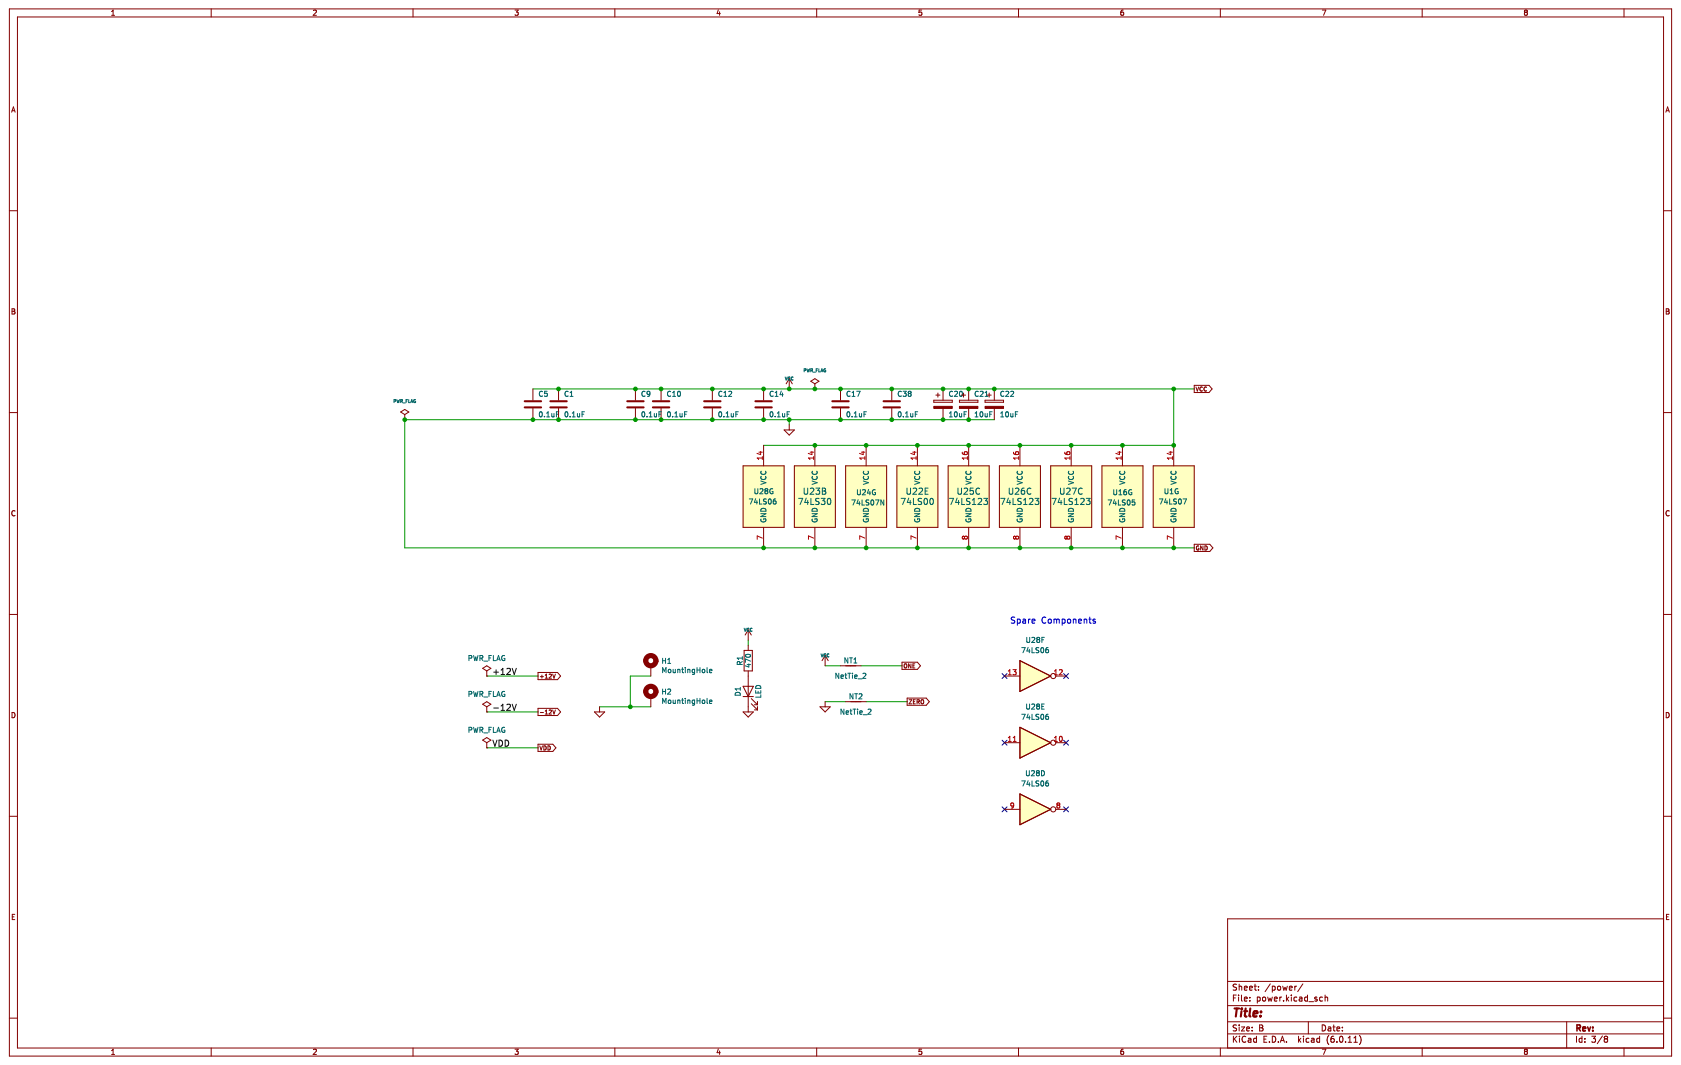
[picture p261: page 3]

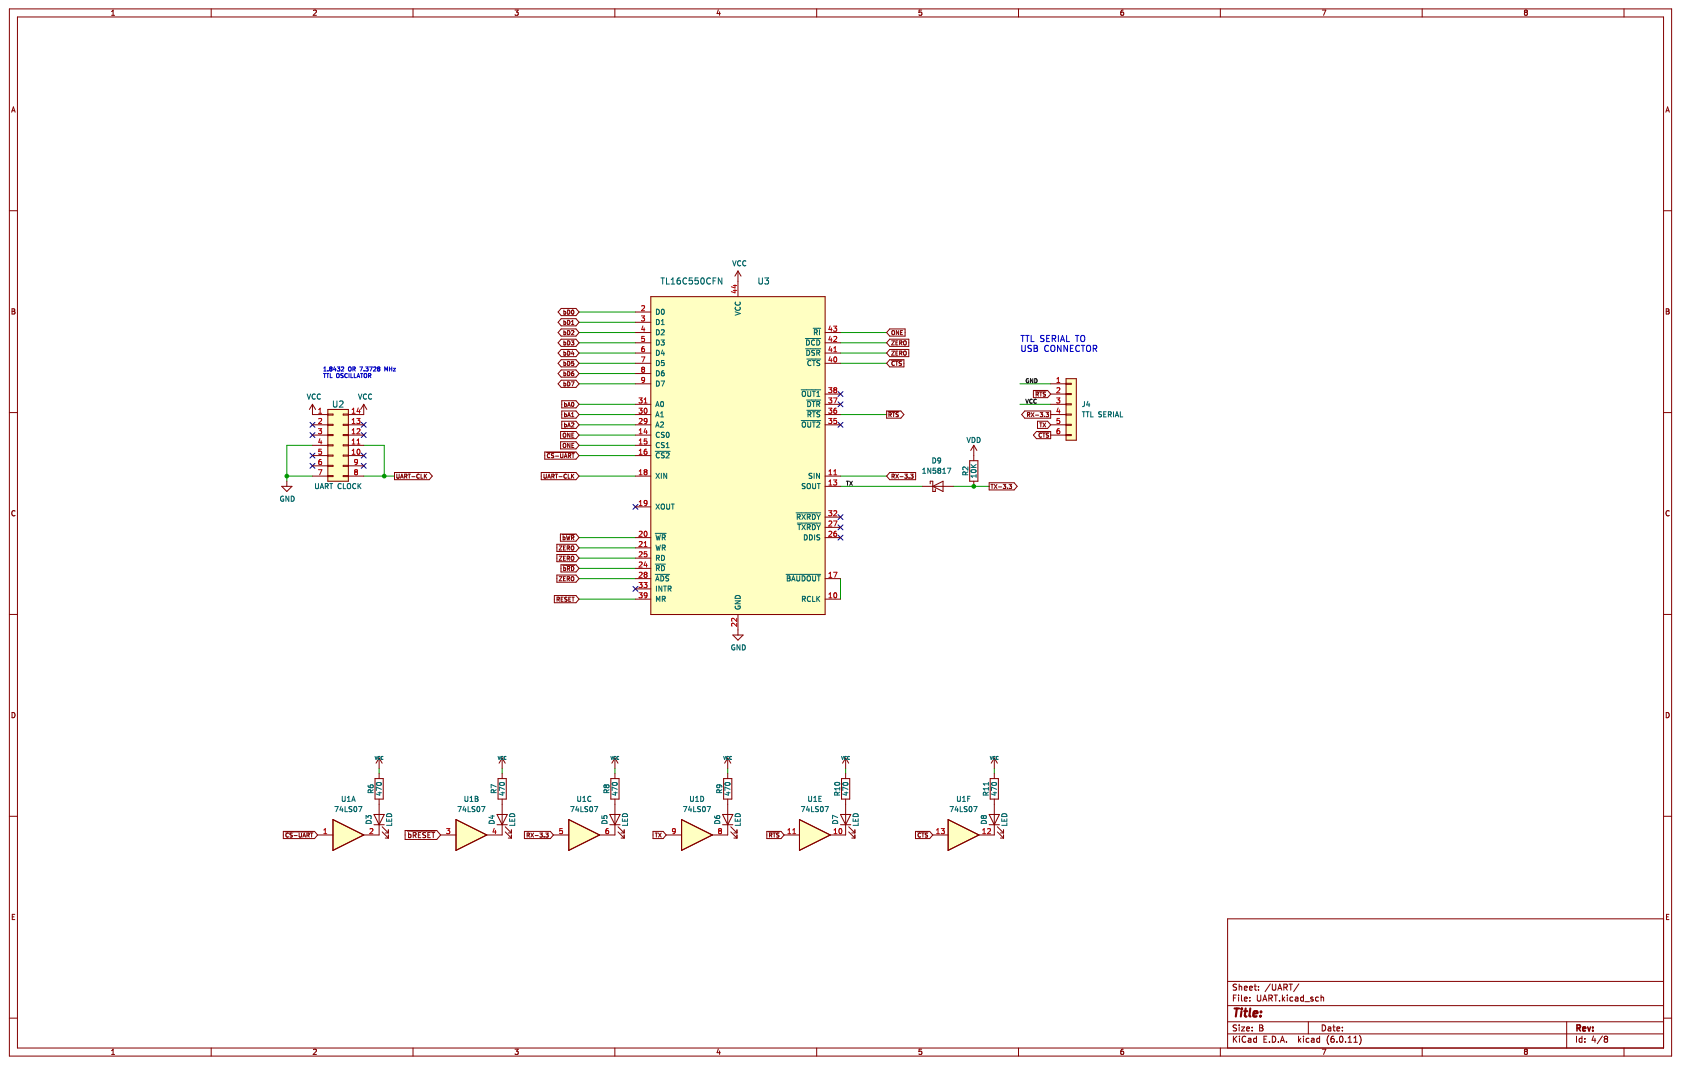
[picture p262: page 4]

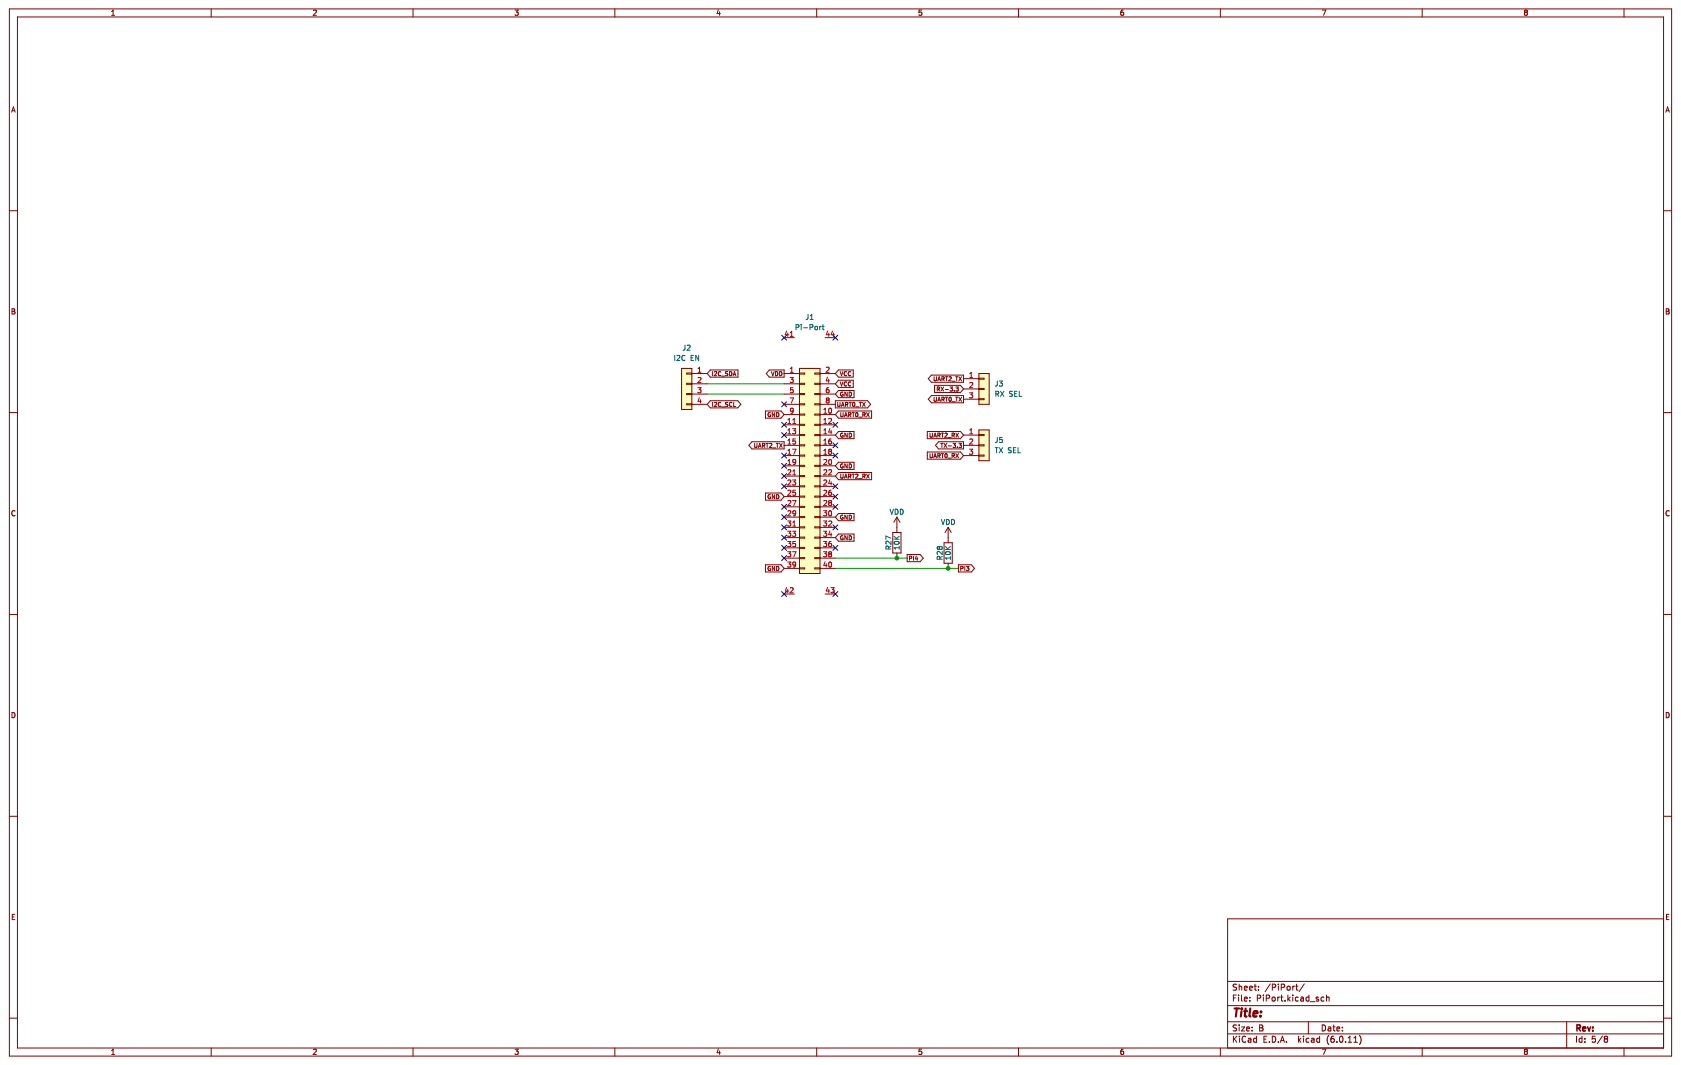
[picture p263: page 5]

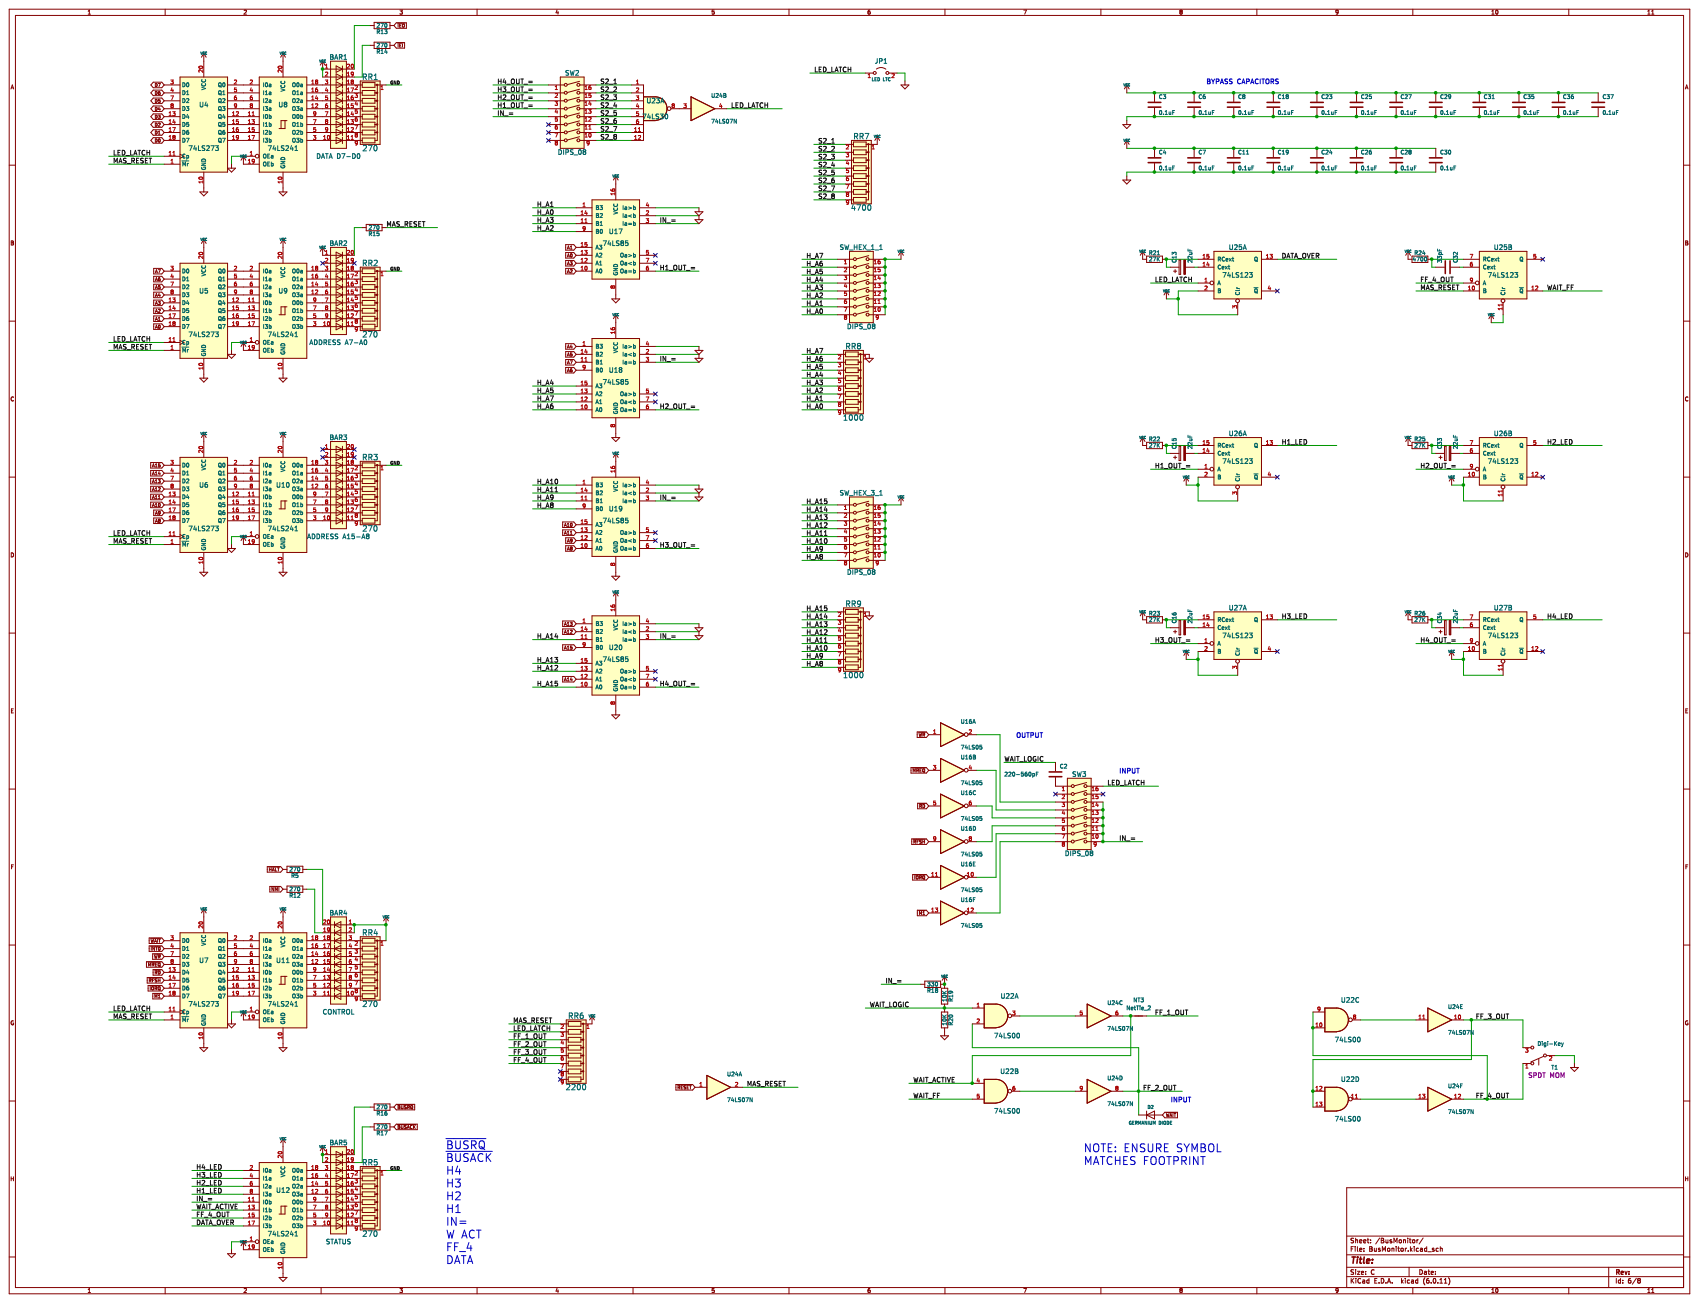
[picture p264: page 6]

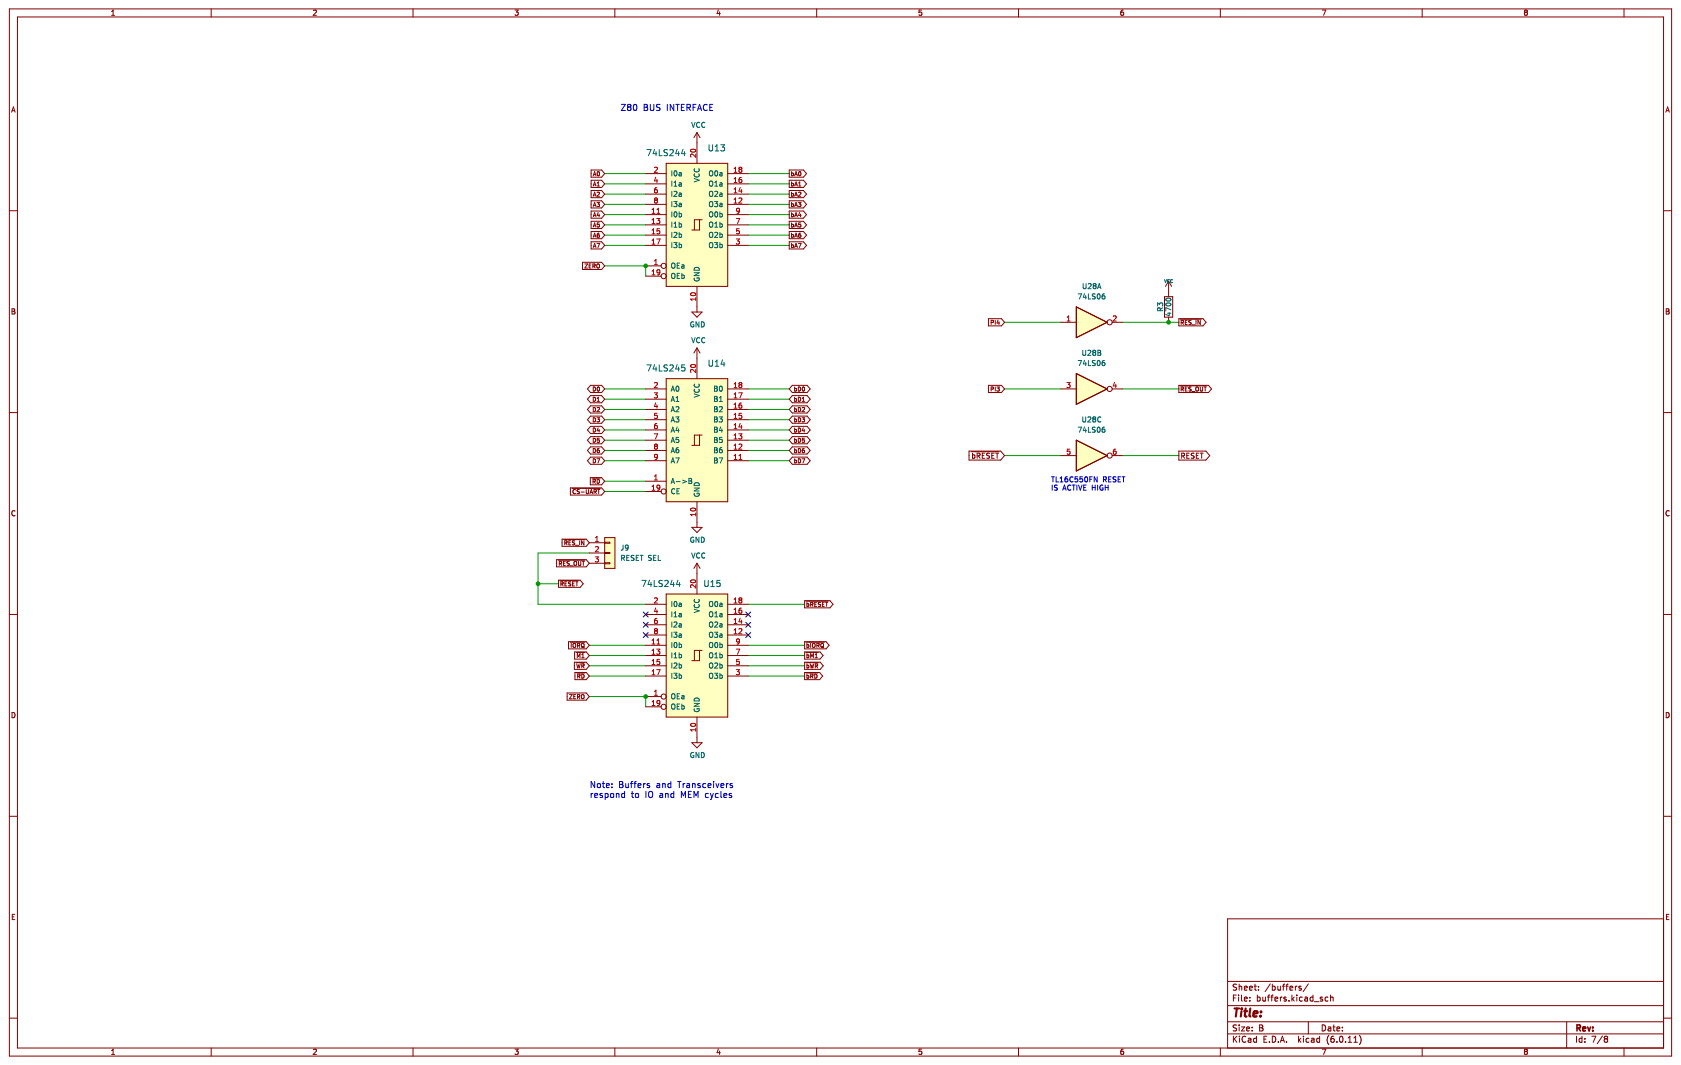
[picture p265: page 7]

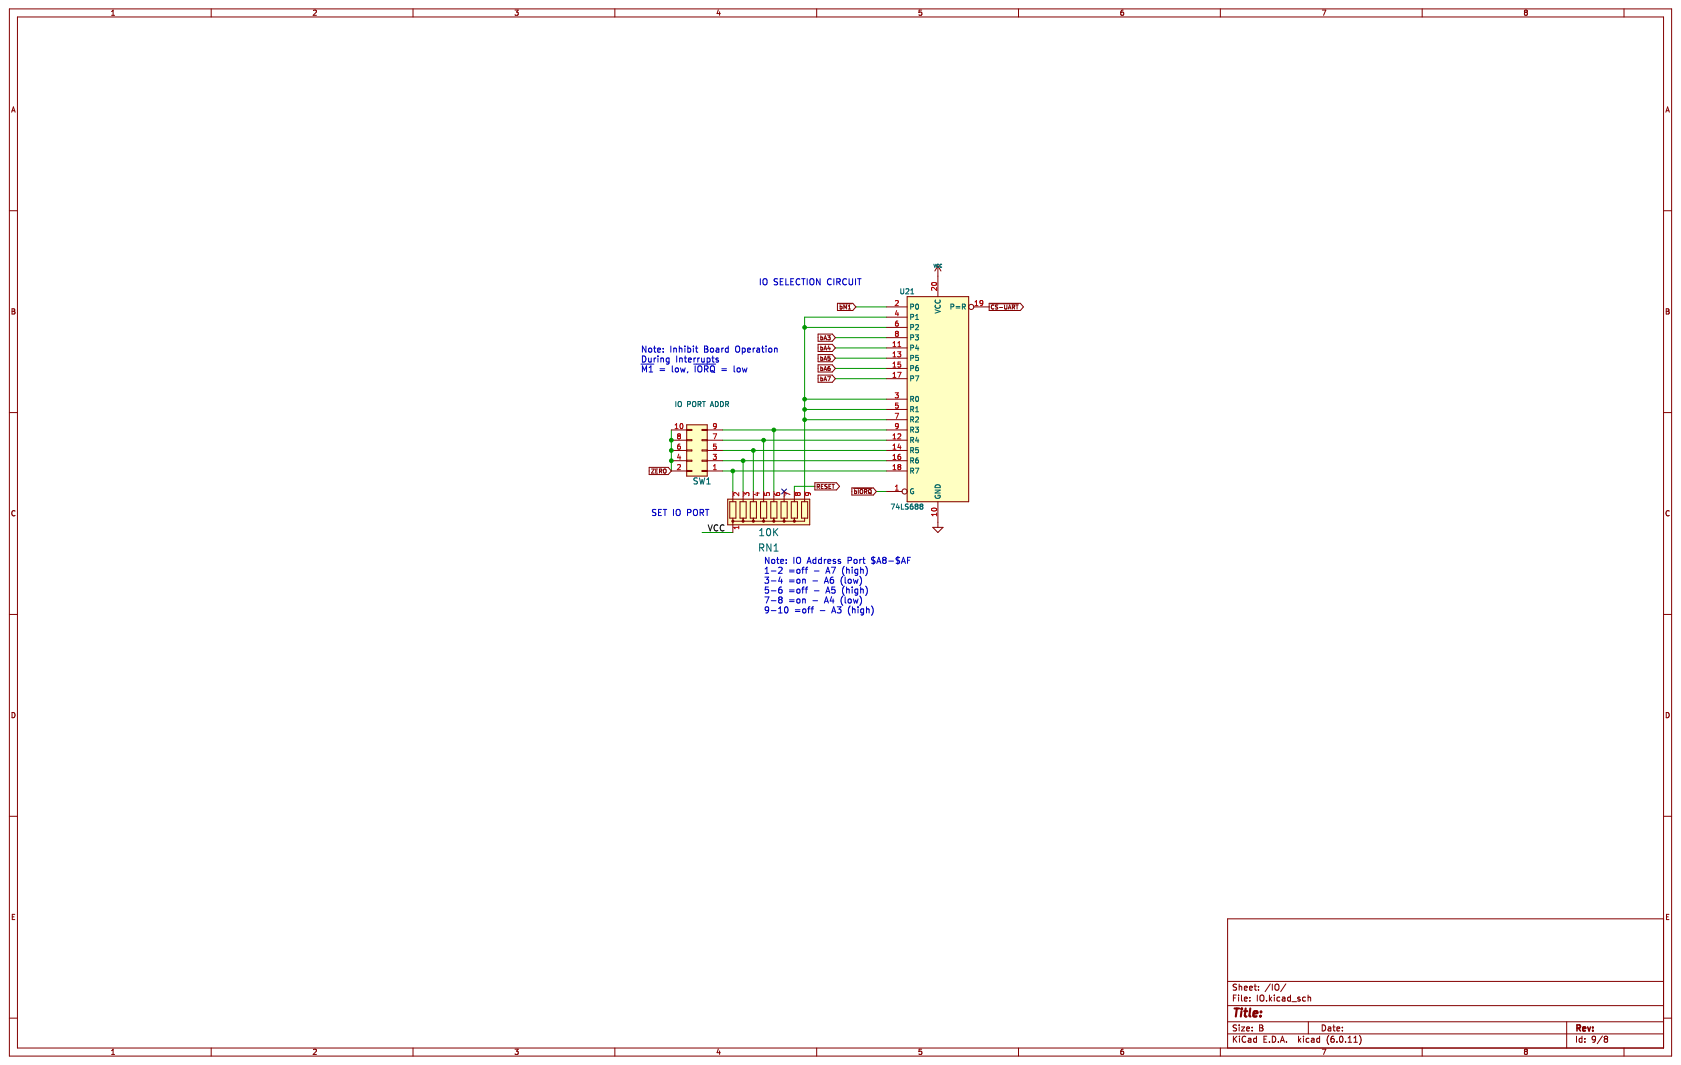
[picture p266: page 8]
