lynchaj/duodyne/!Development/FirstZ80 V1.0/FirstZ80.schematic.pdf

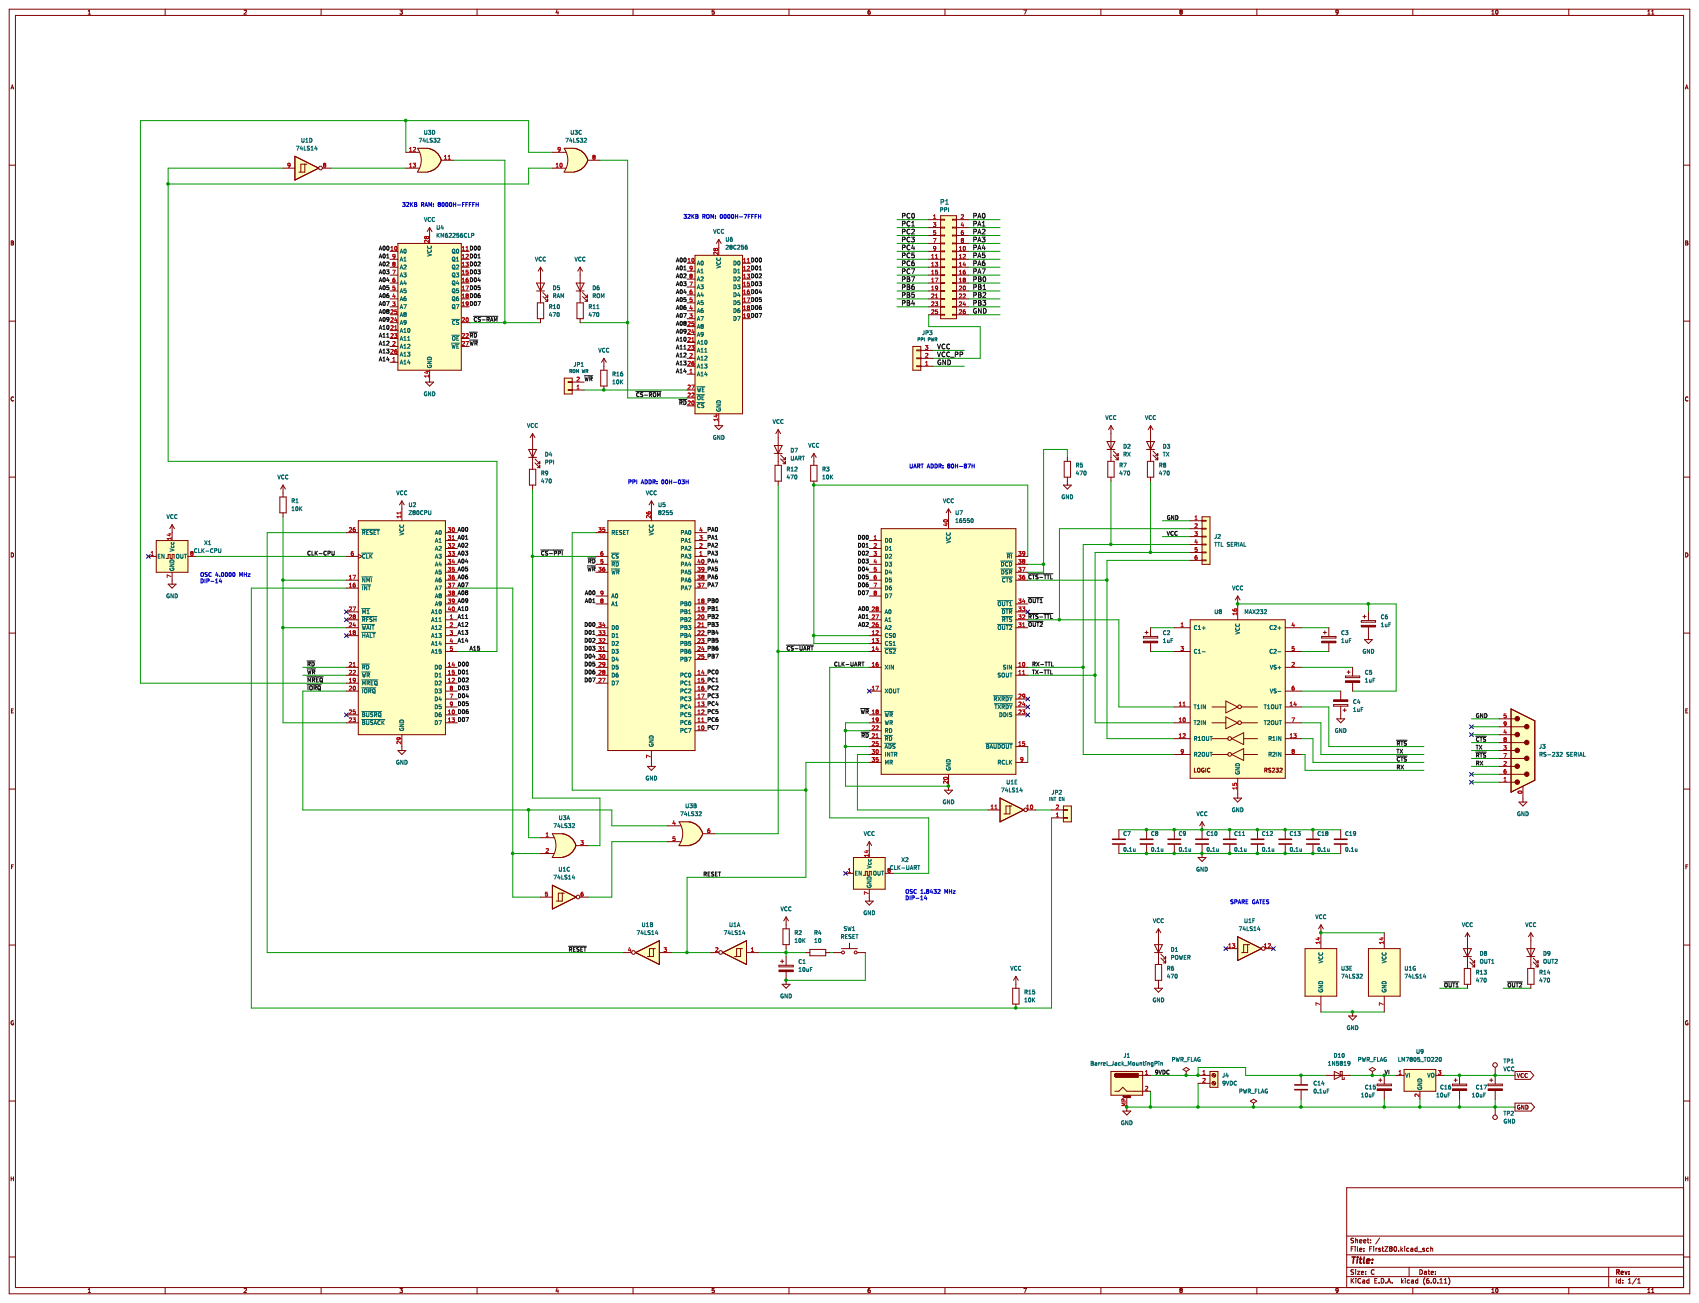
[picture p267: page 1]
