lynchaj/duodyne/!Development/14 input-output.Text, V1.0/input-output.Text.schematic.pdf

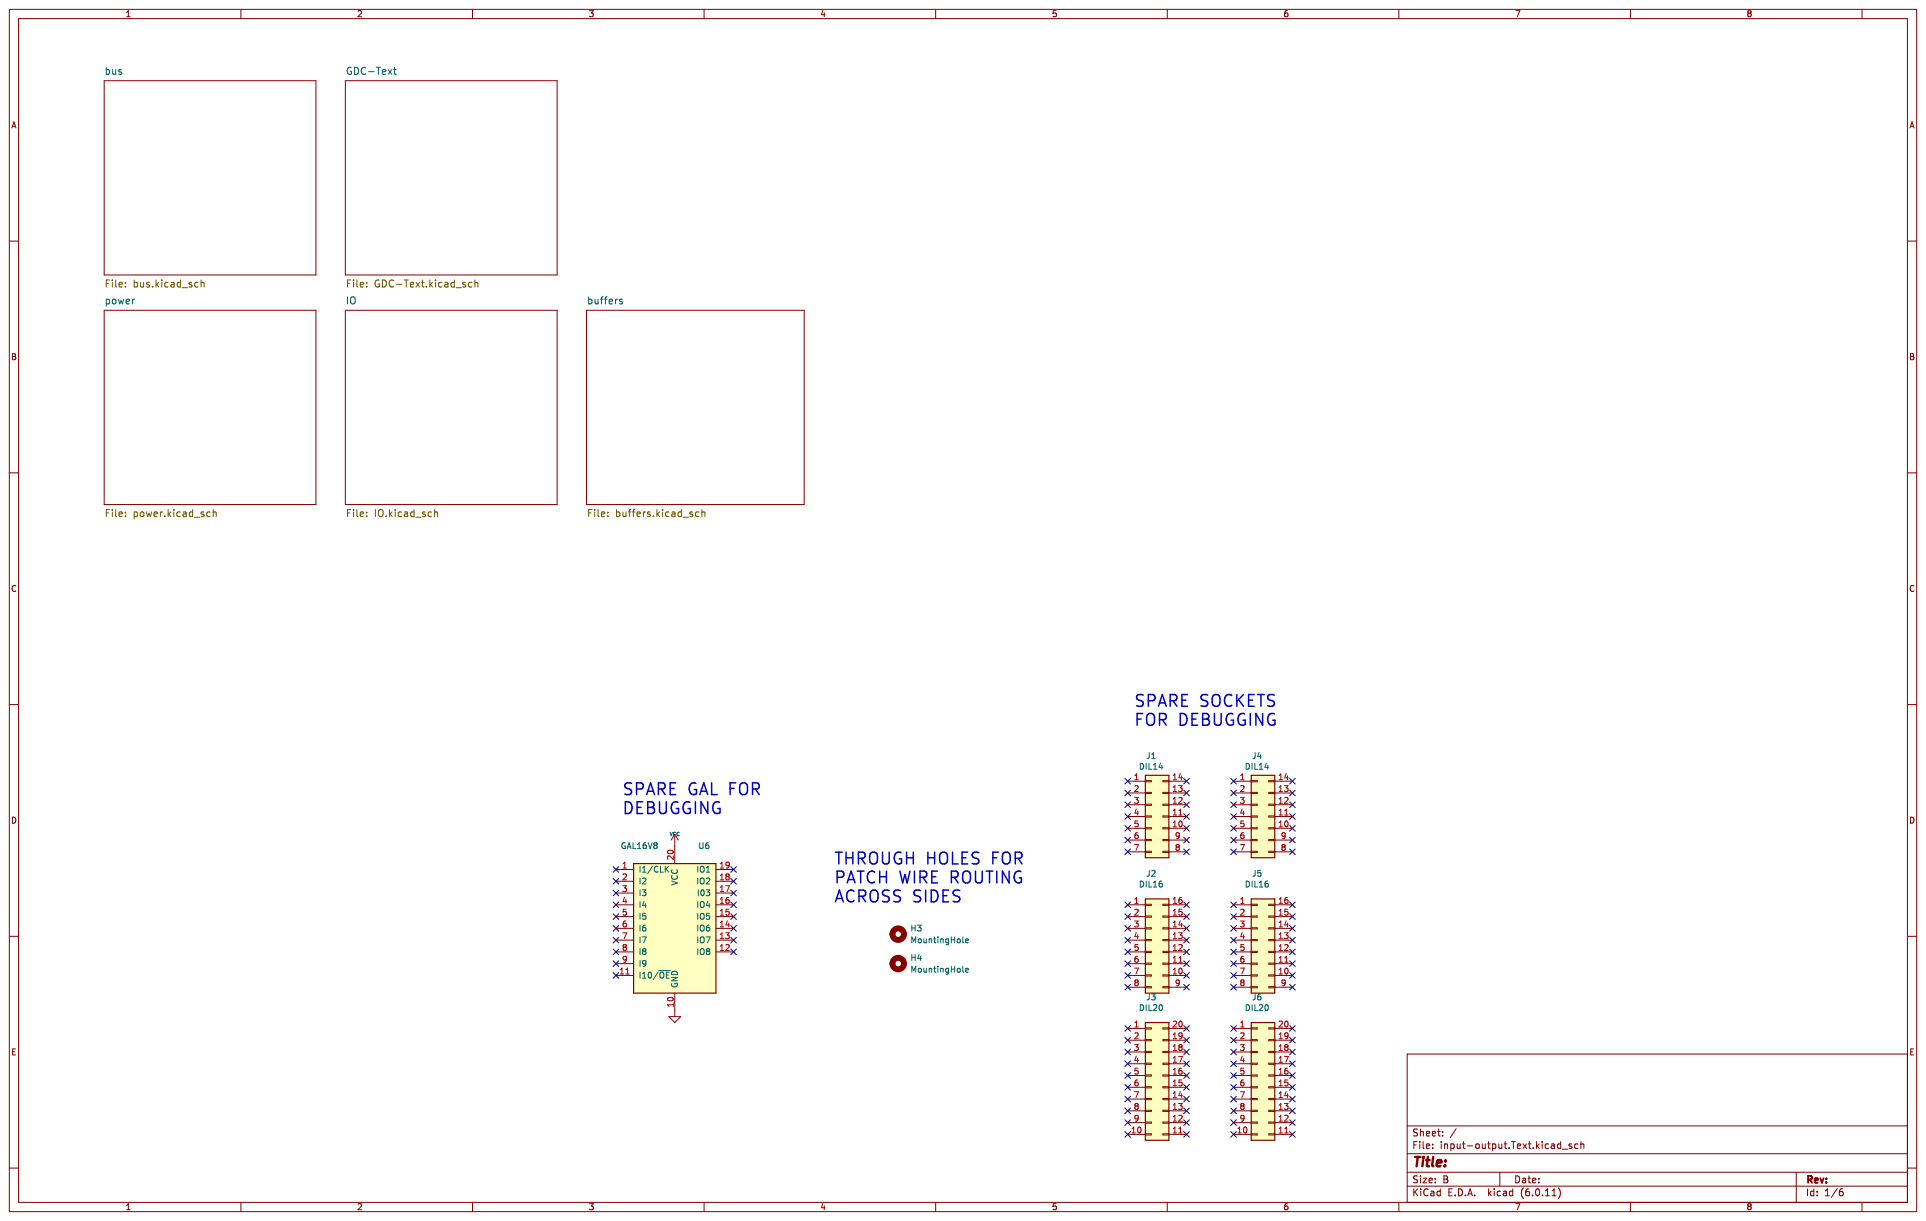
[picture p268: page 1]

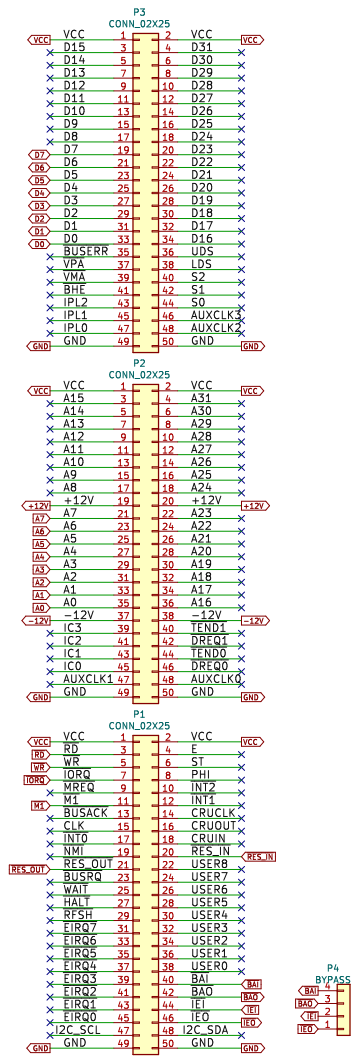
[picture p269: page 2]

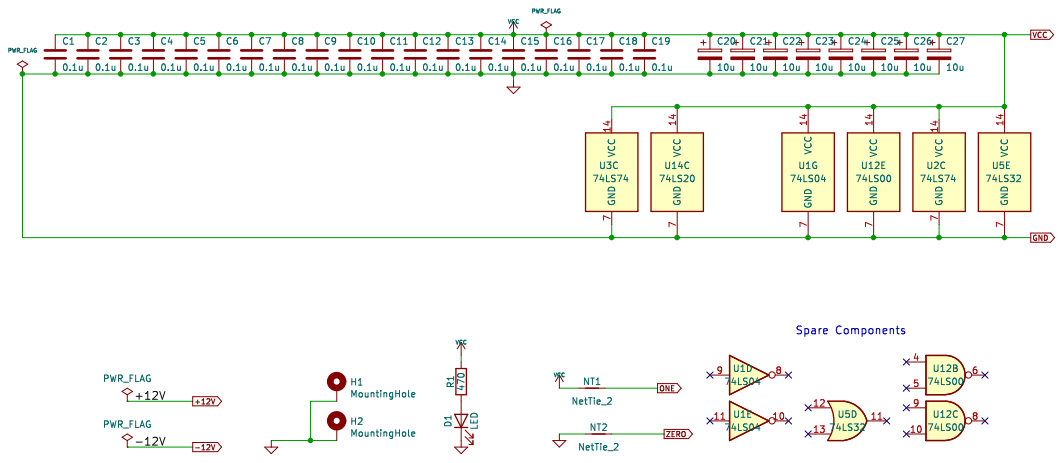
[picture p270: page 3]

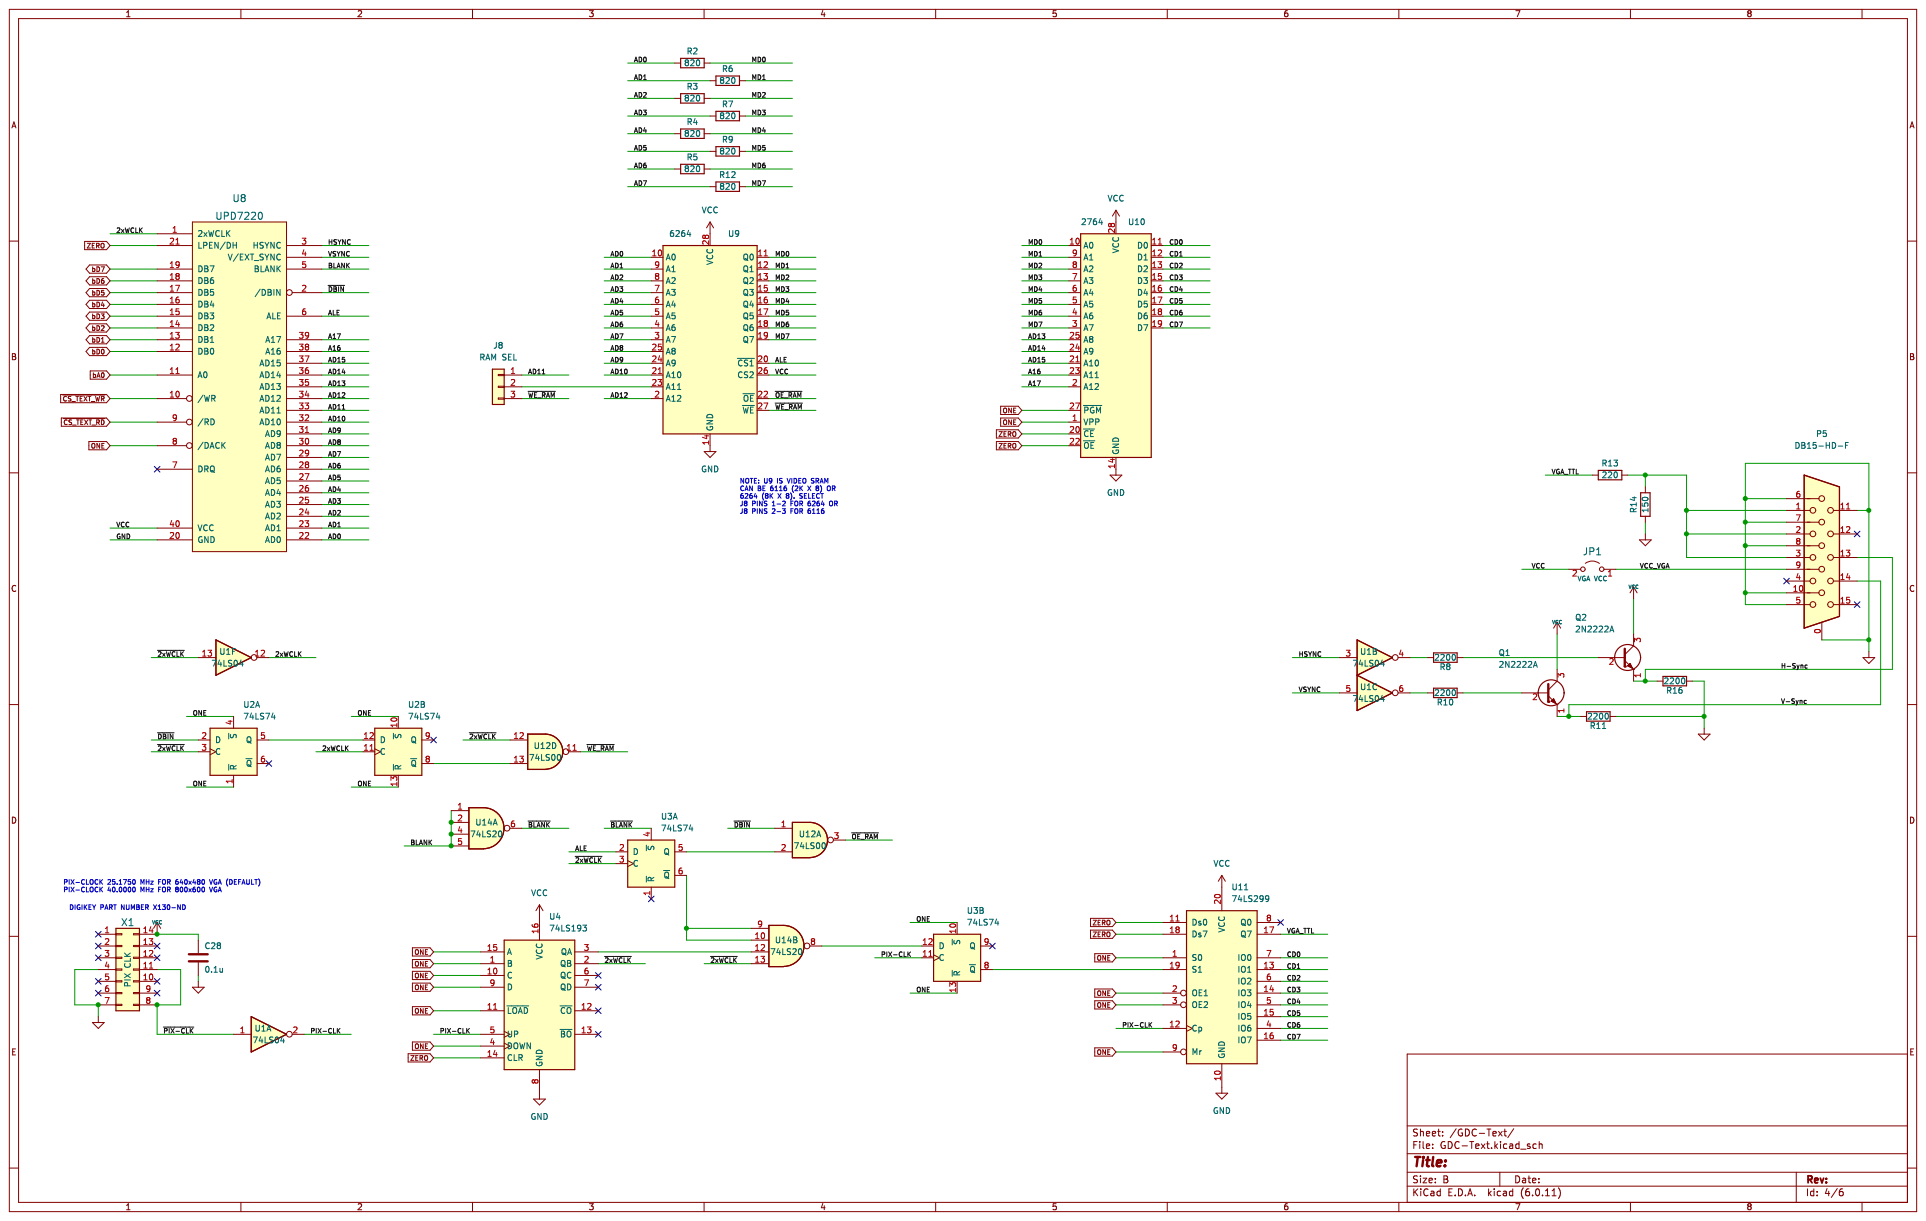
[picture p271: page 4]

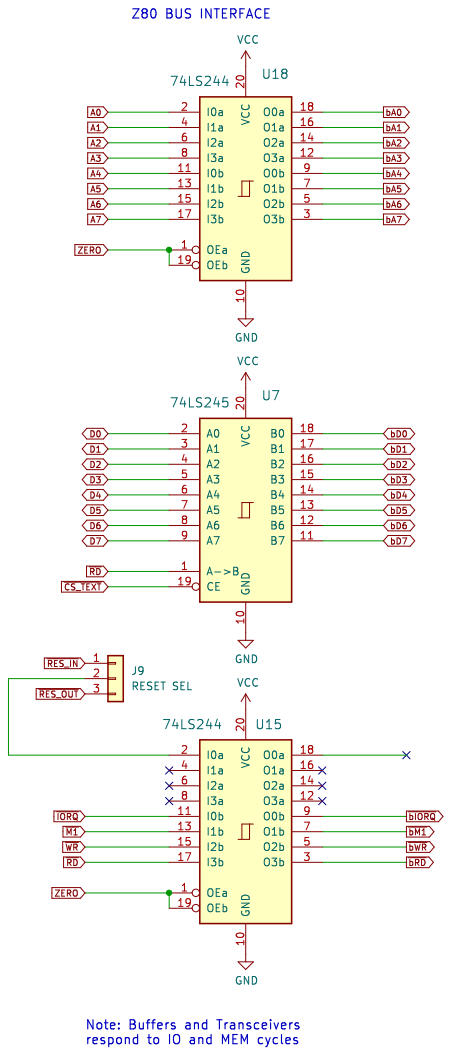
[picture p272: page 5]

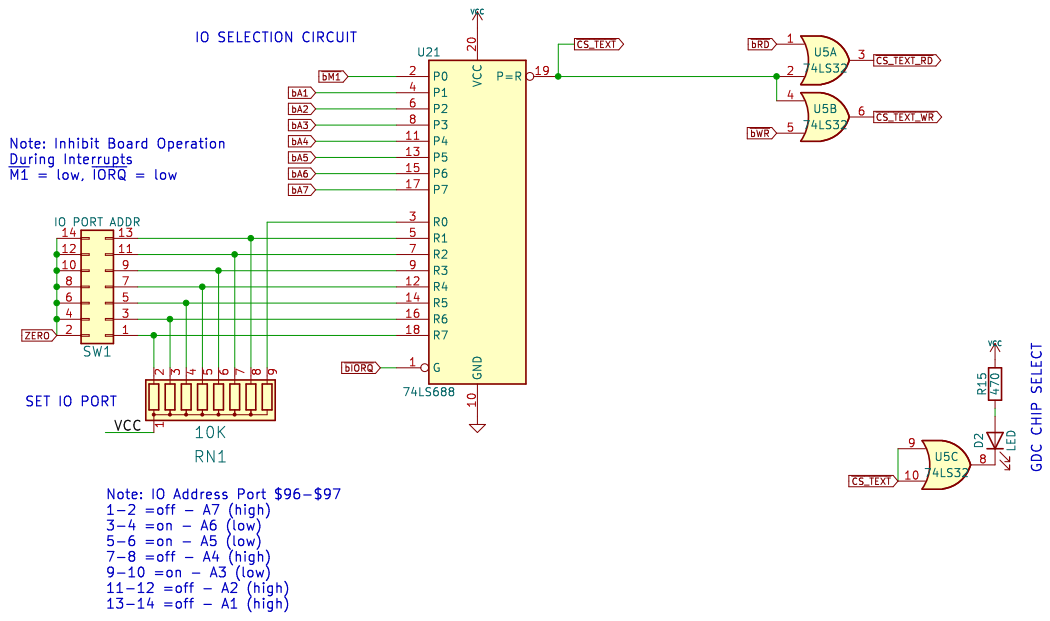
[picture p273: page 6]
