lynchaj/duodyne/!Development/08 input-output.Disk, V1.1/input-output.Disk.schematic.pdf

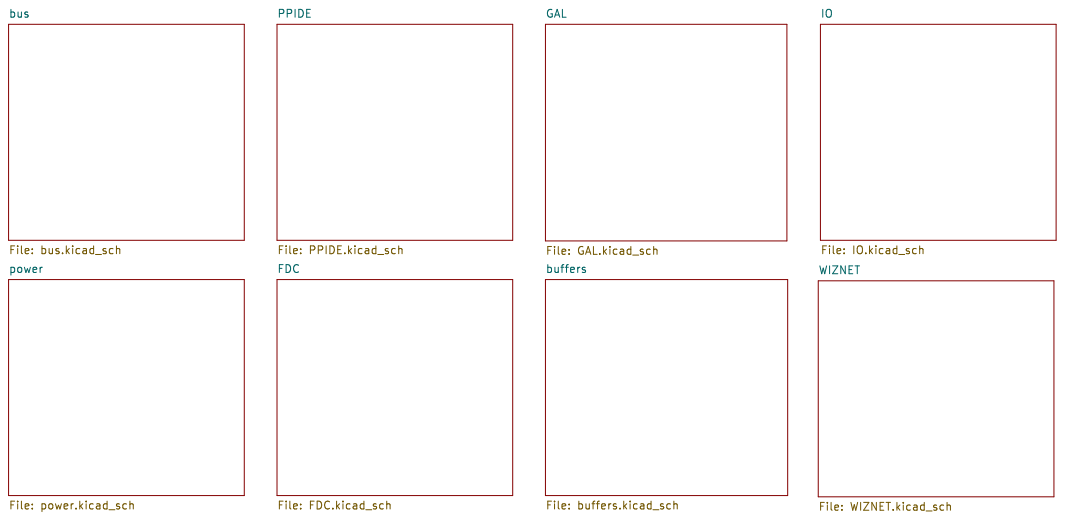
[picture p274: page 1]

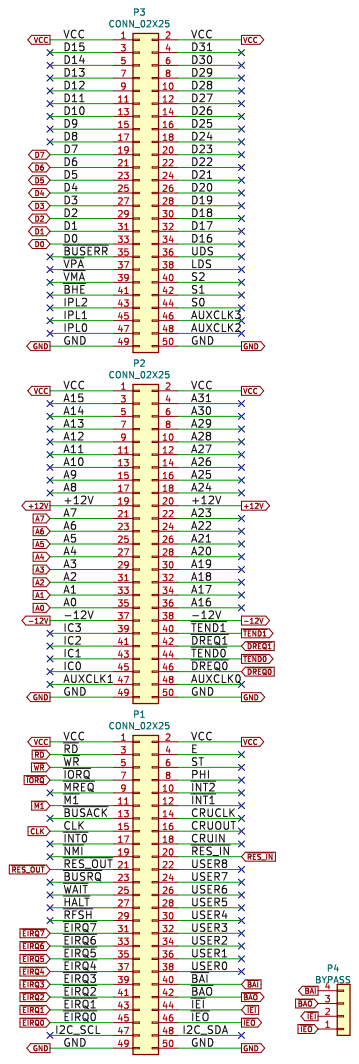
[picture p275: page 2]

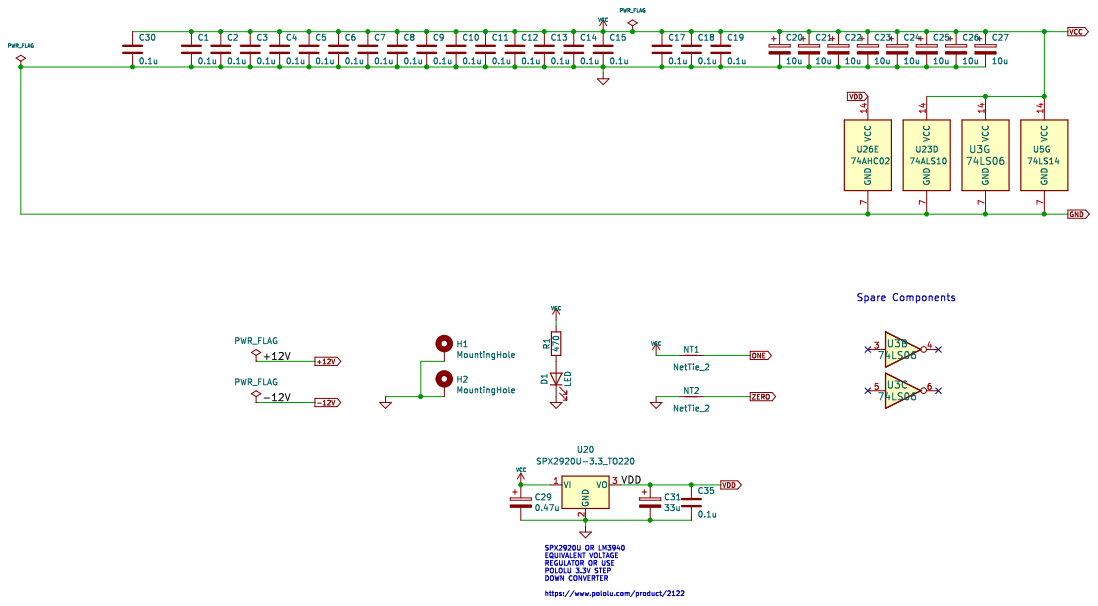
[picture p276: page 3]

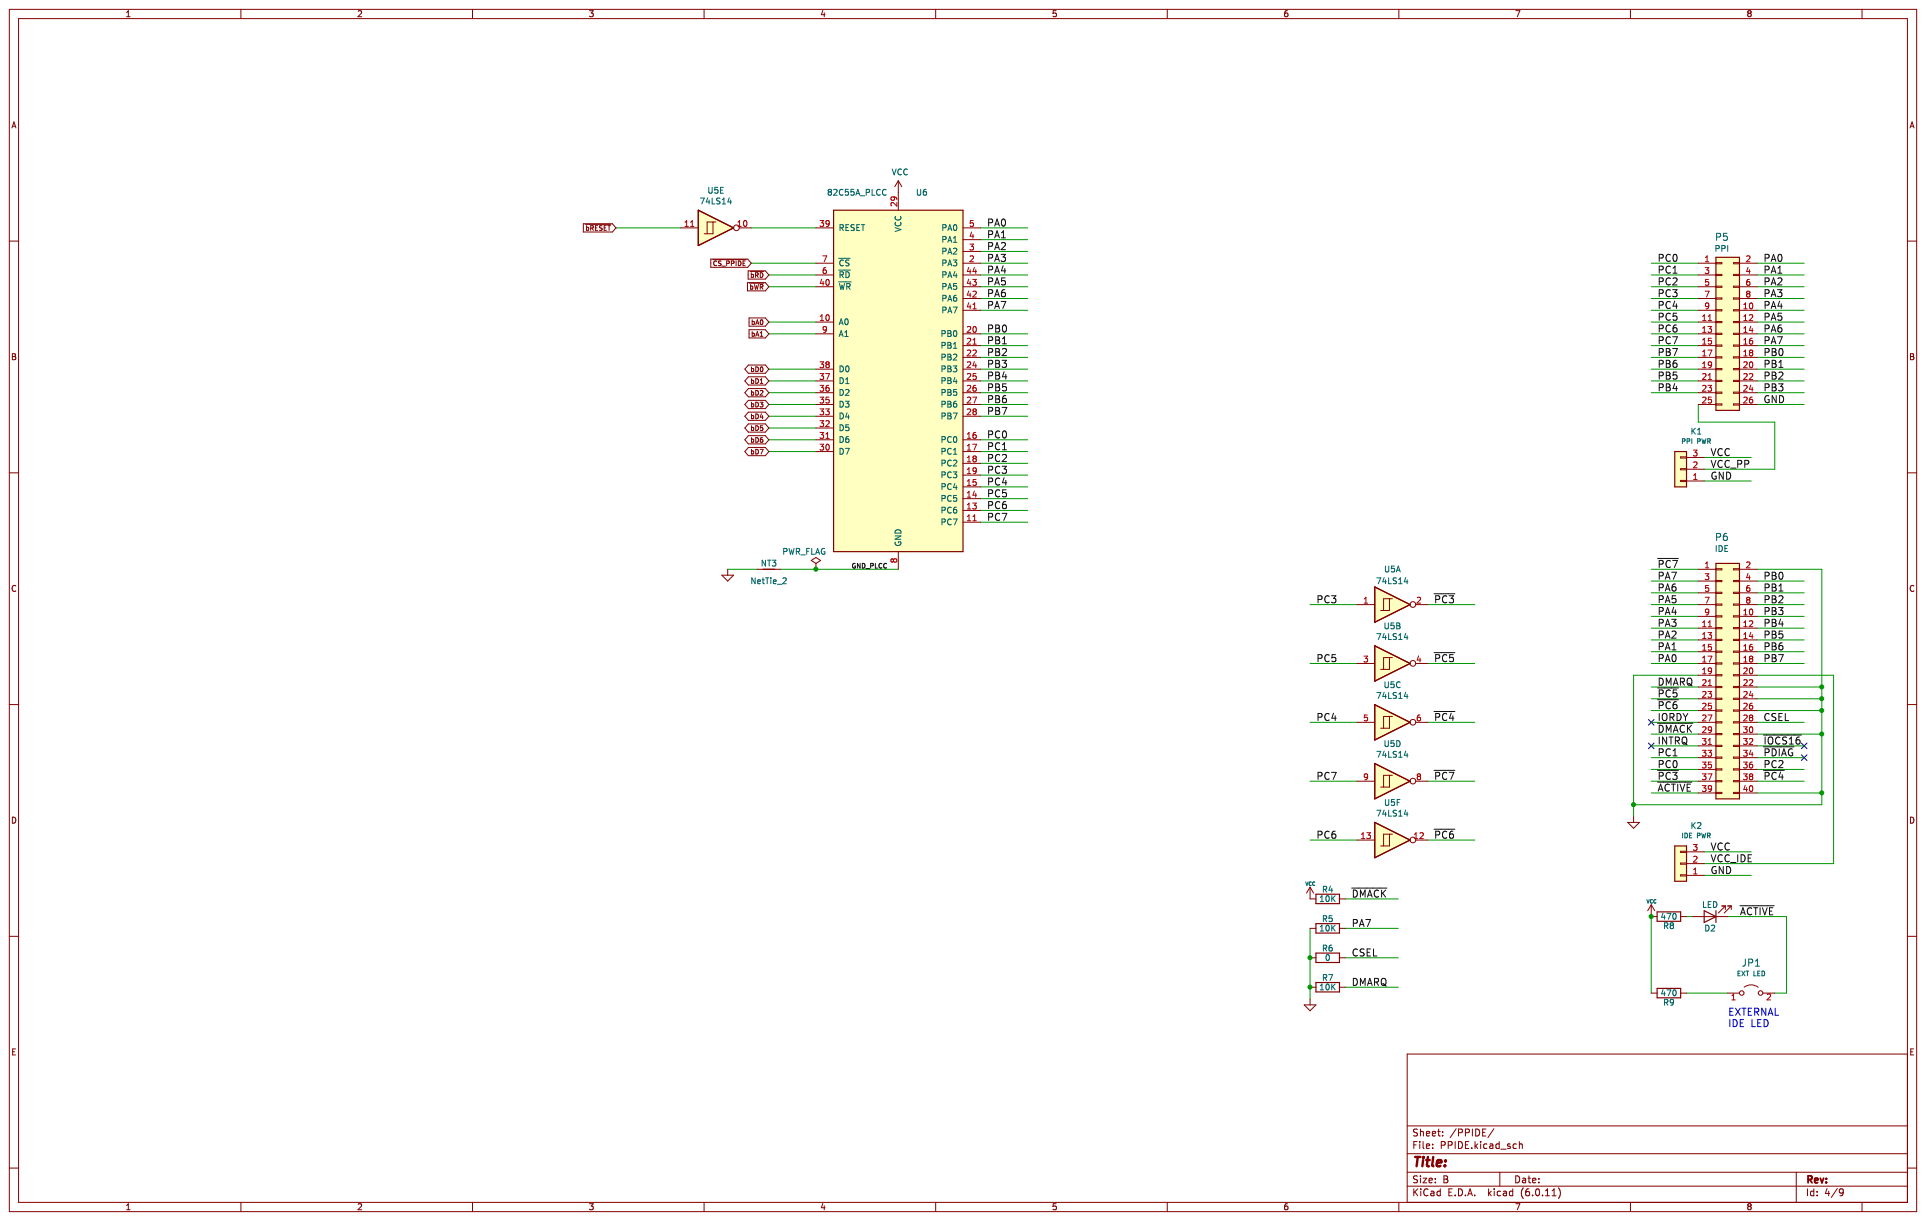
[picture p277: page 4]

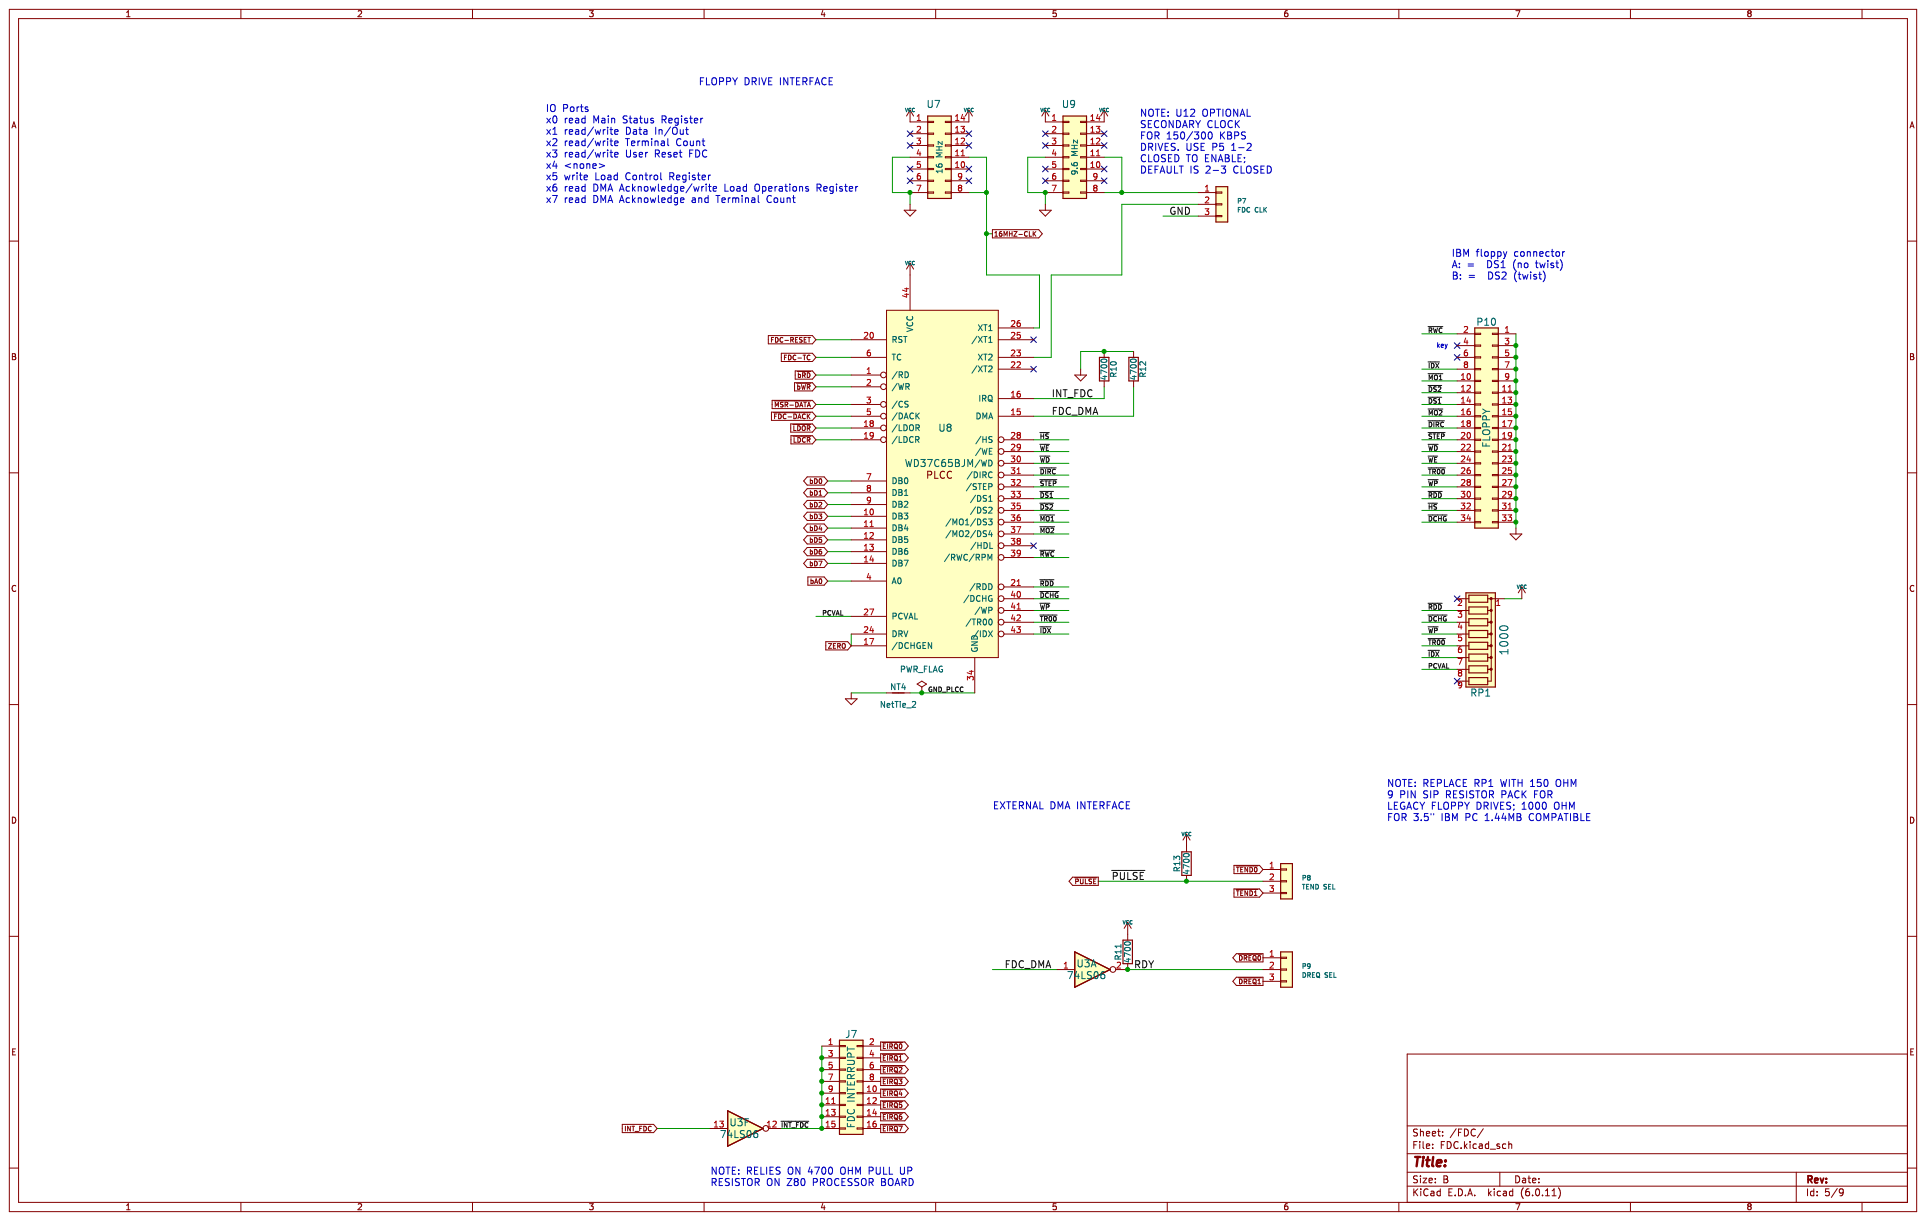
[picture p278: page 5]

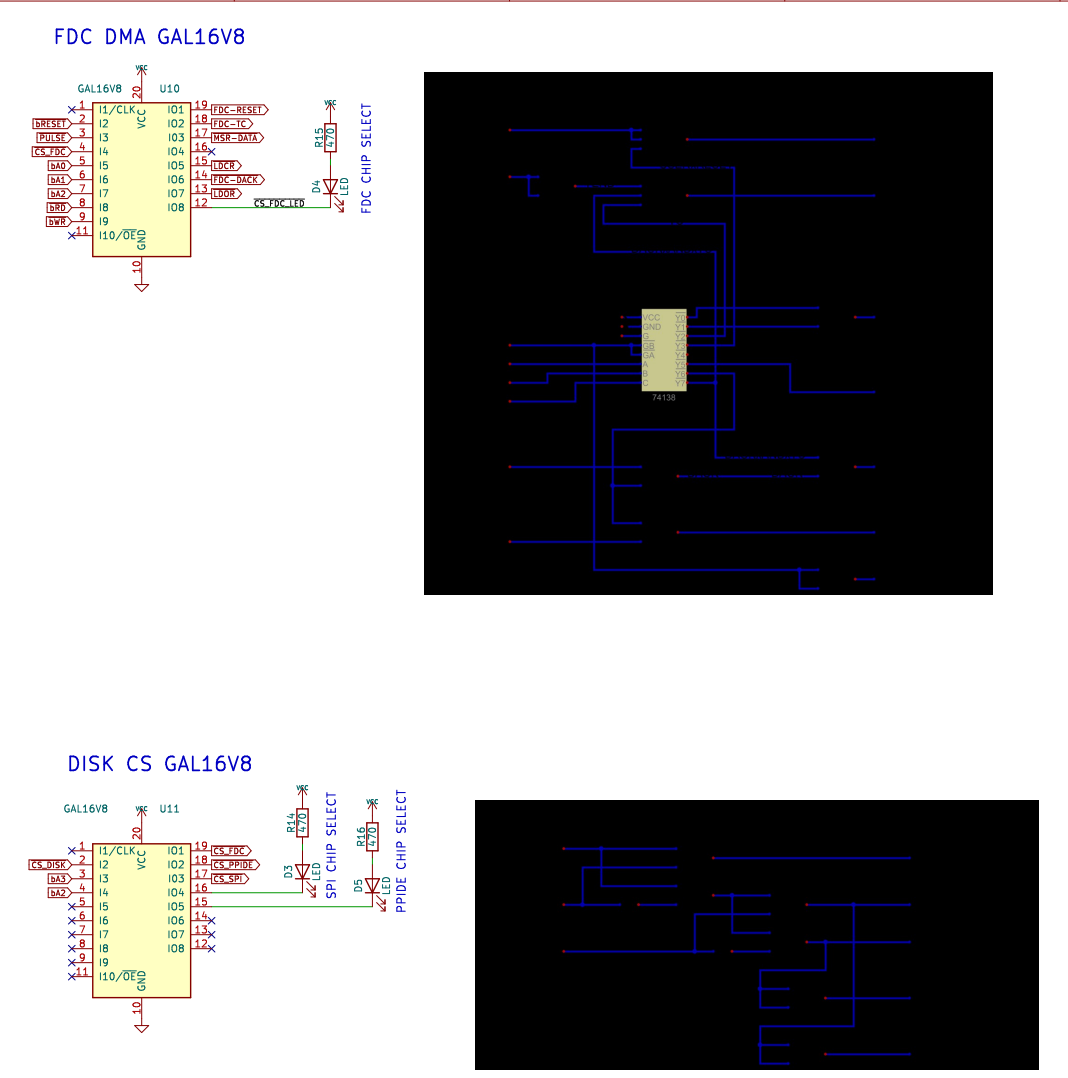
[picture p279: page 6]

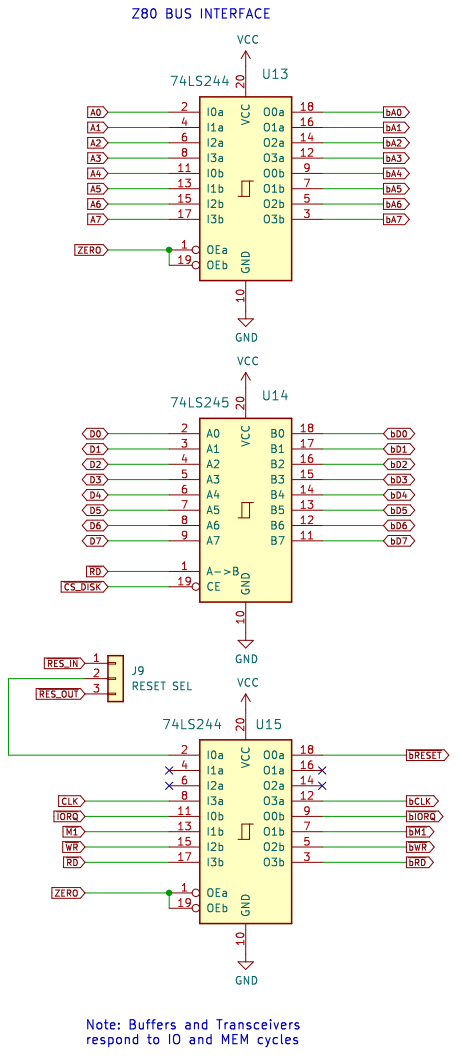
[picture p280: page 7]

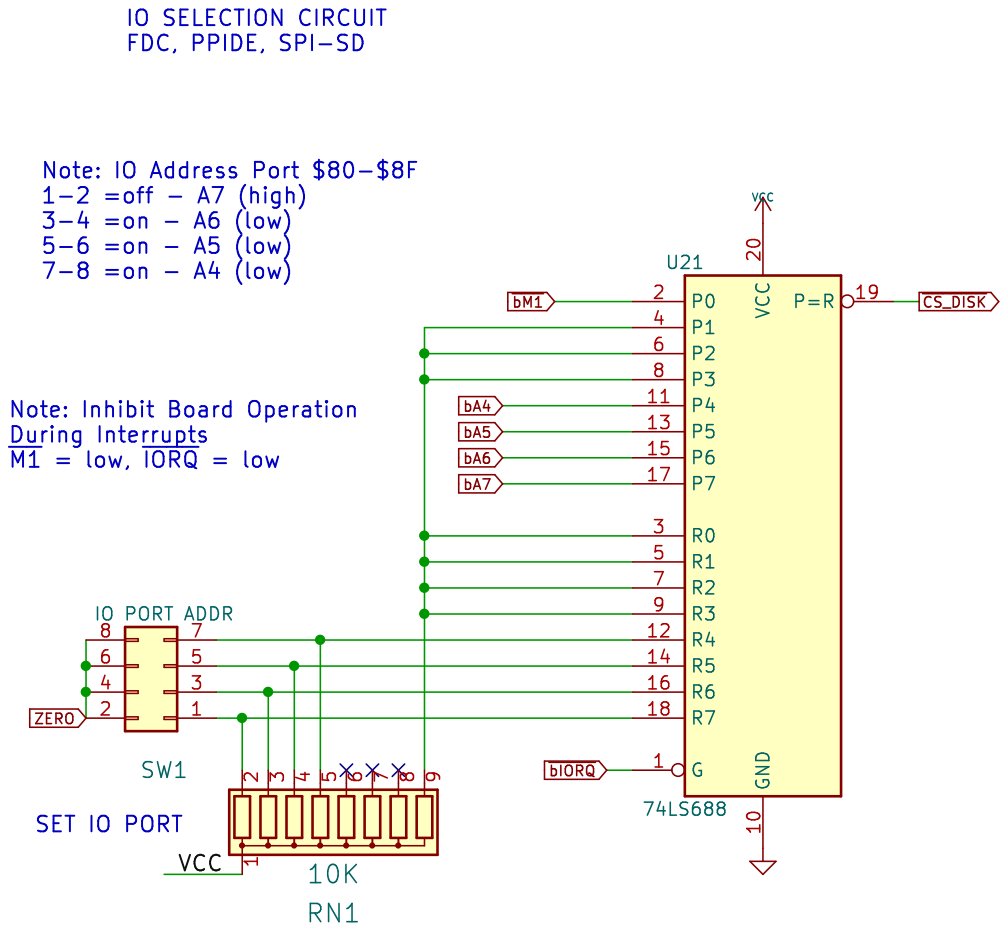
[picture p281: page 8]

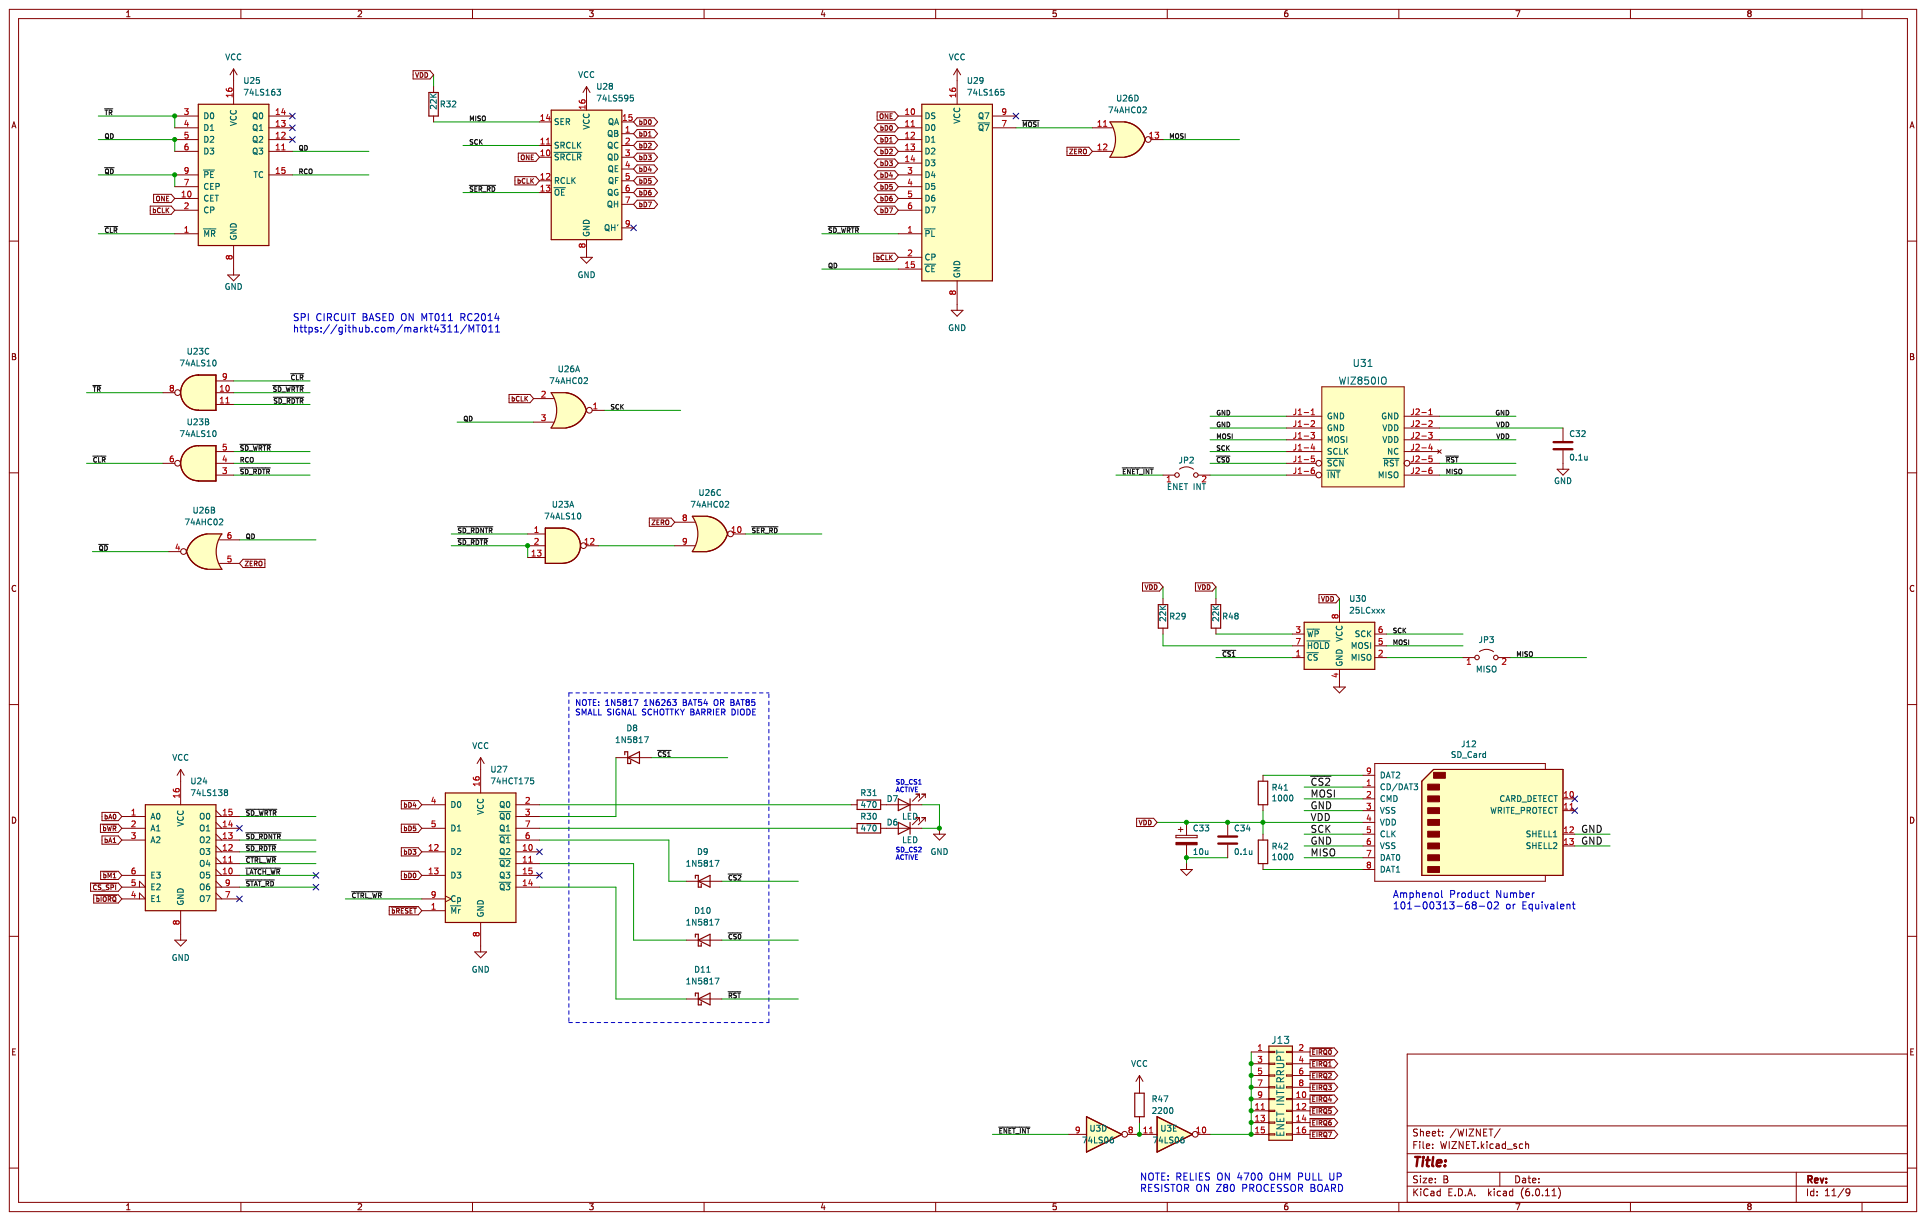
[picture p282: page 9]
