lynchaj/duodyne/!Development/13 input-output.GDC, V1.0/input-output.GDC.schematic.pdf

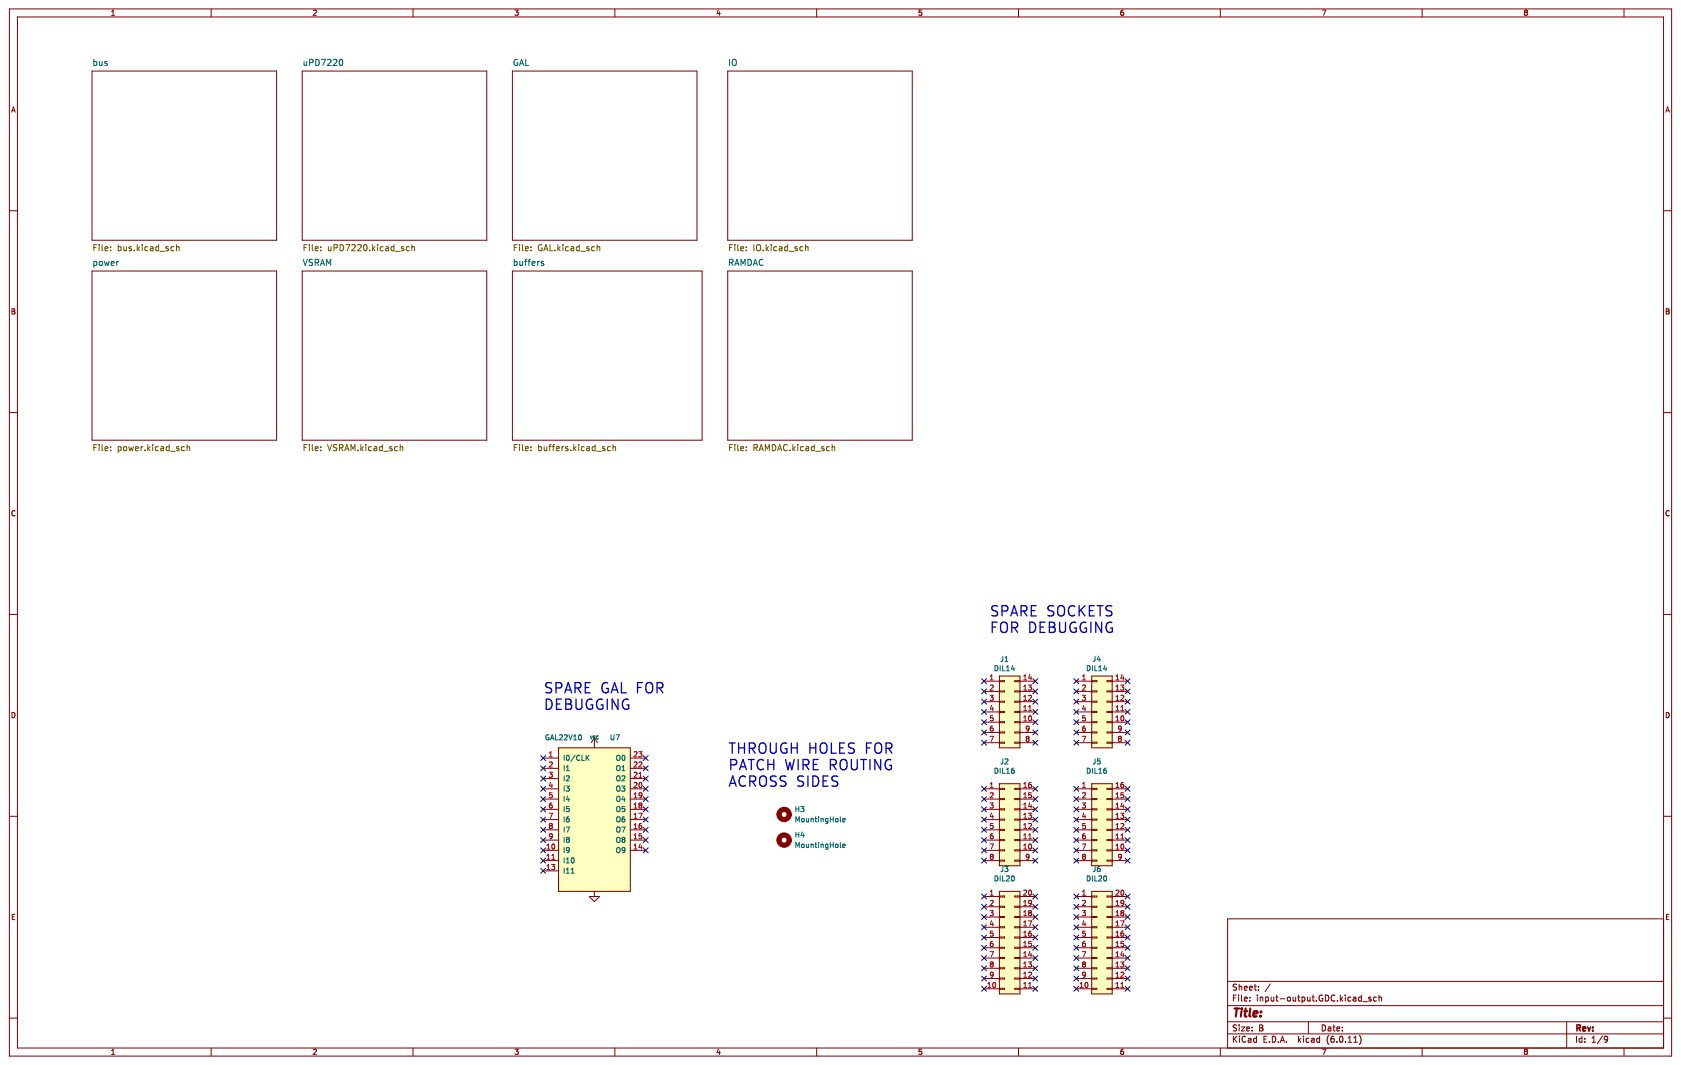
[picture p283: page 1]

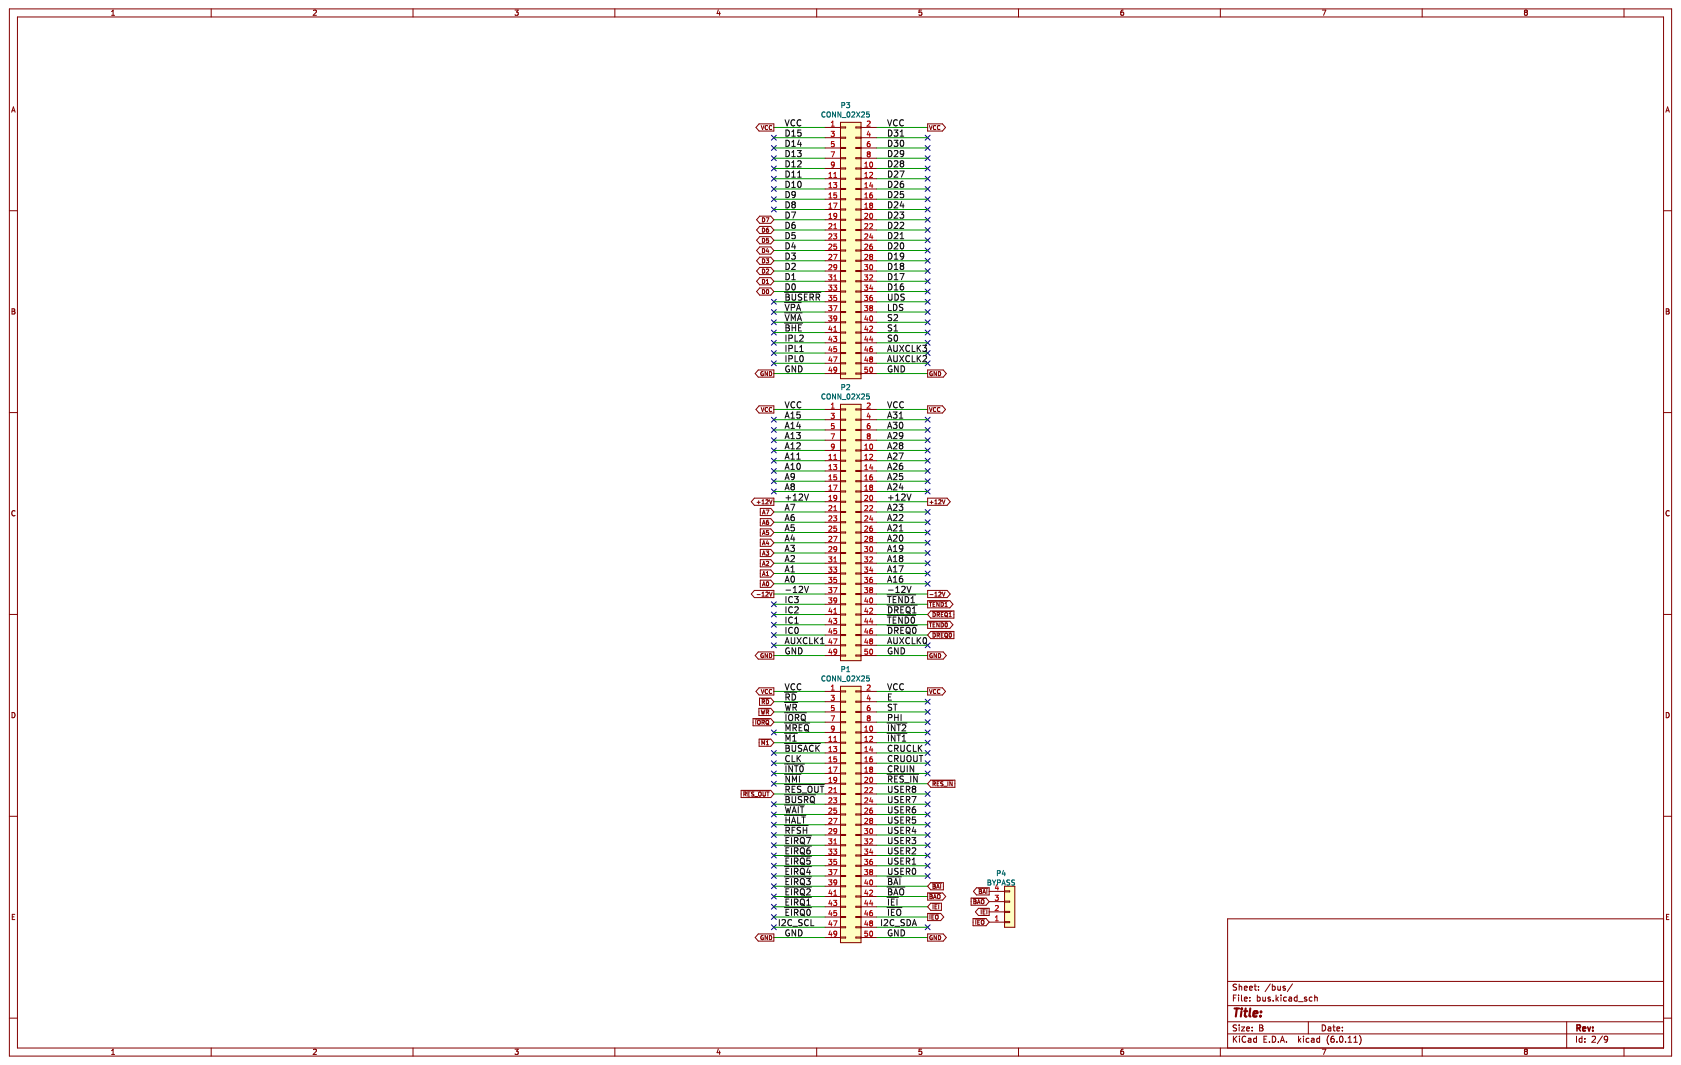
[picture p284: page 2]

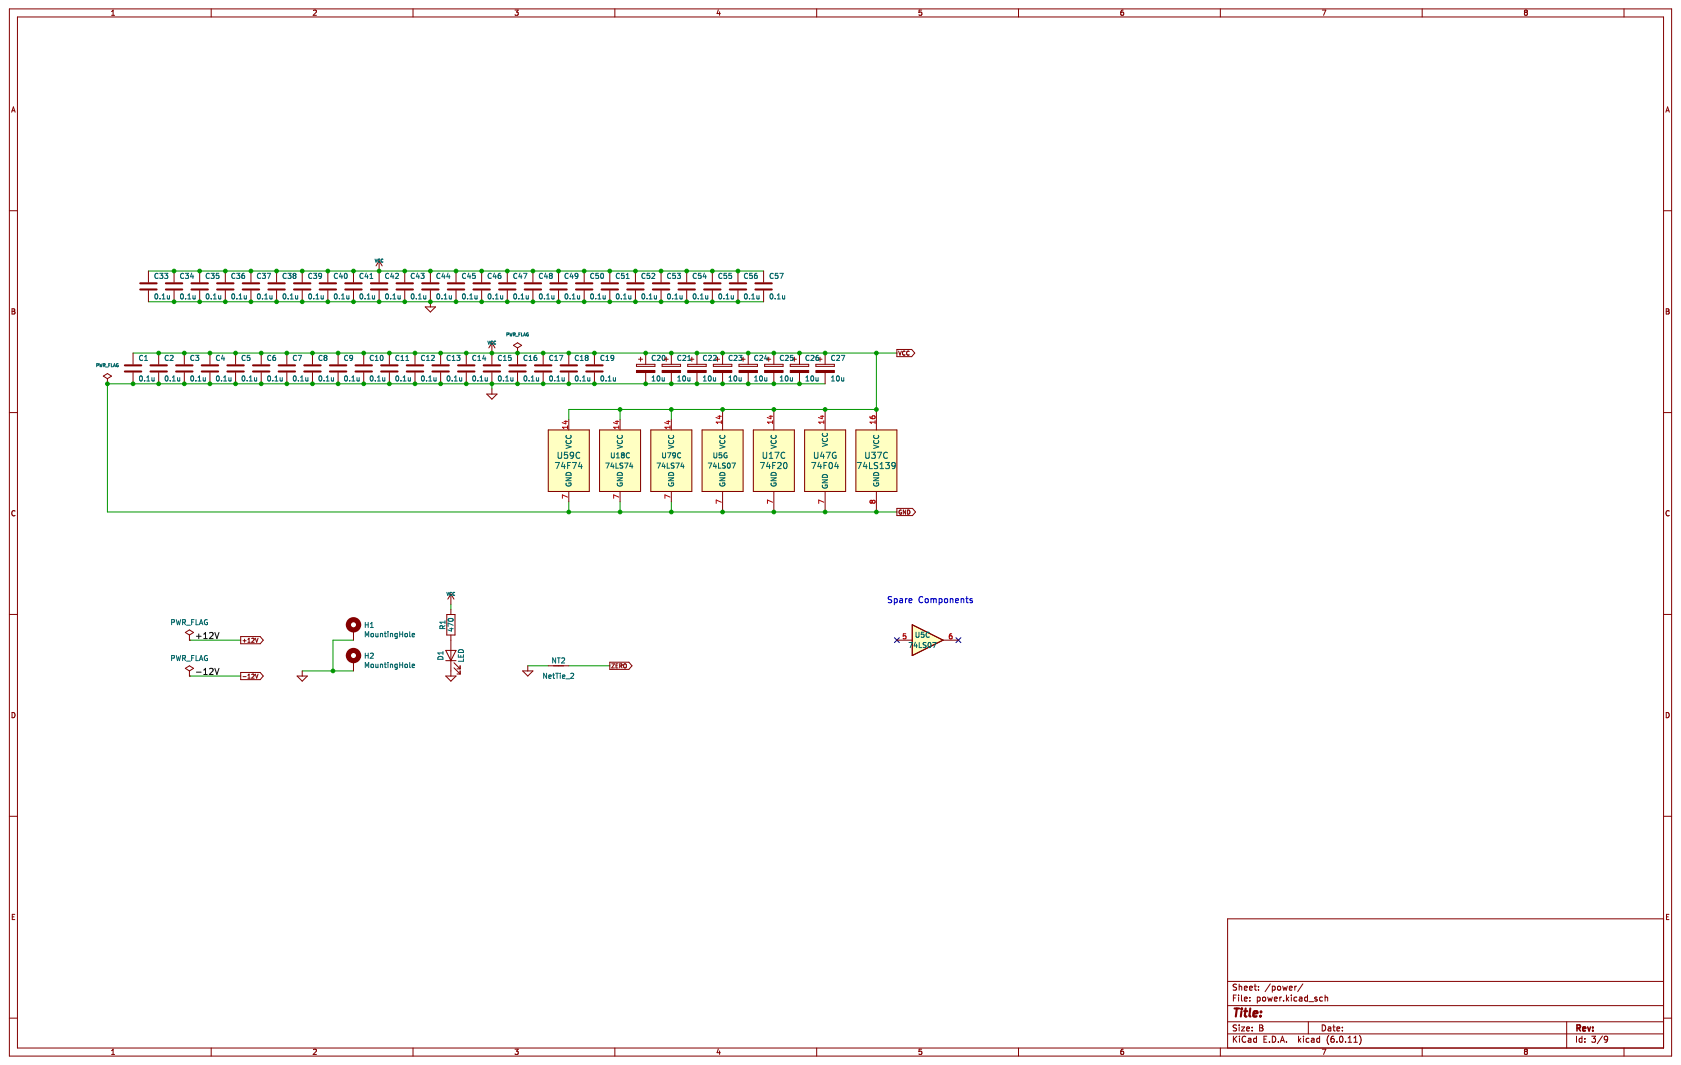
[picture p285: page 3]

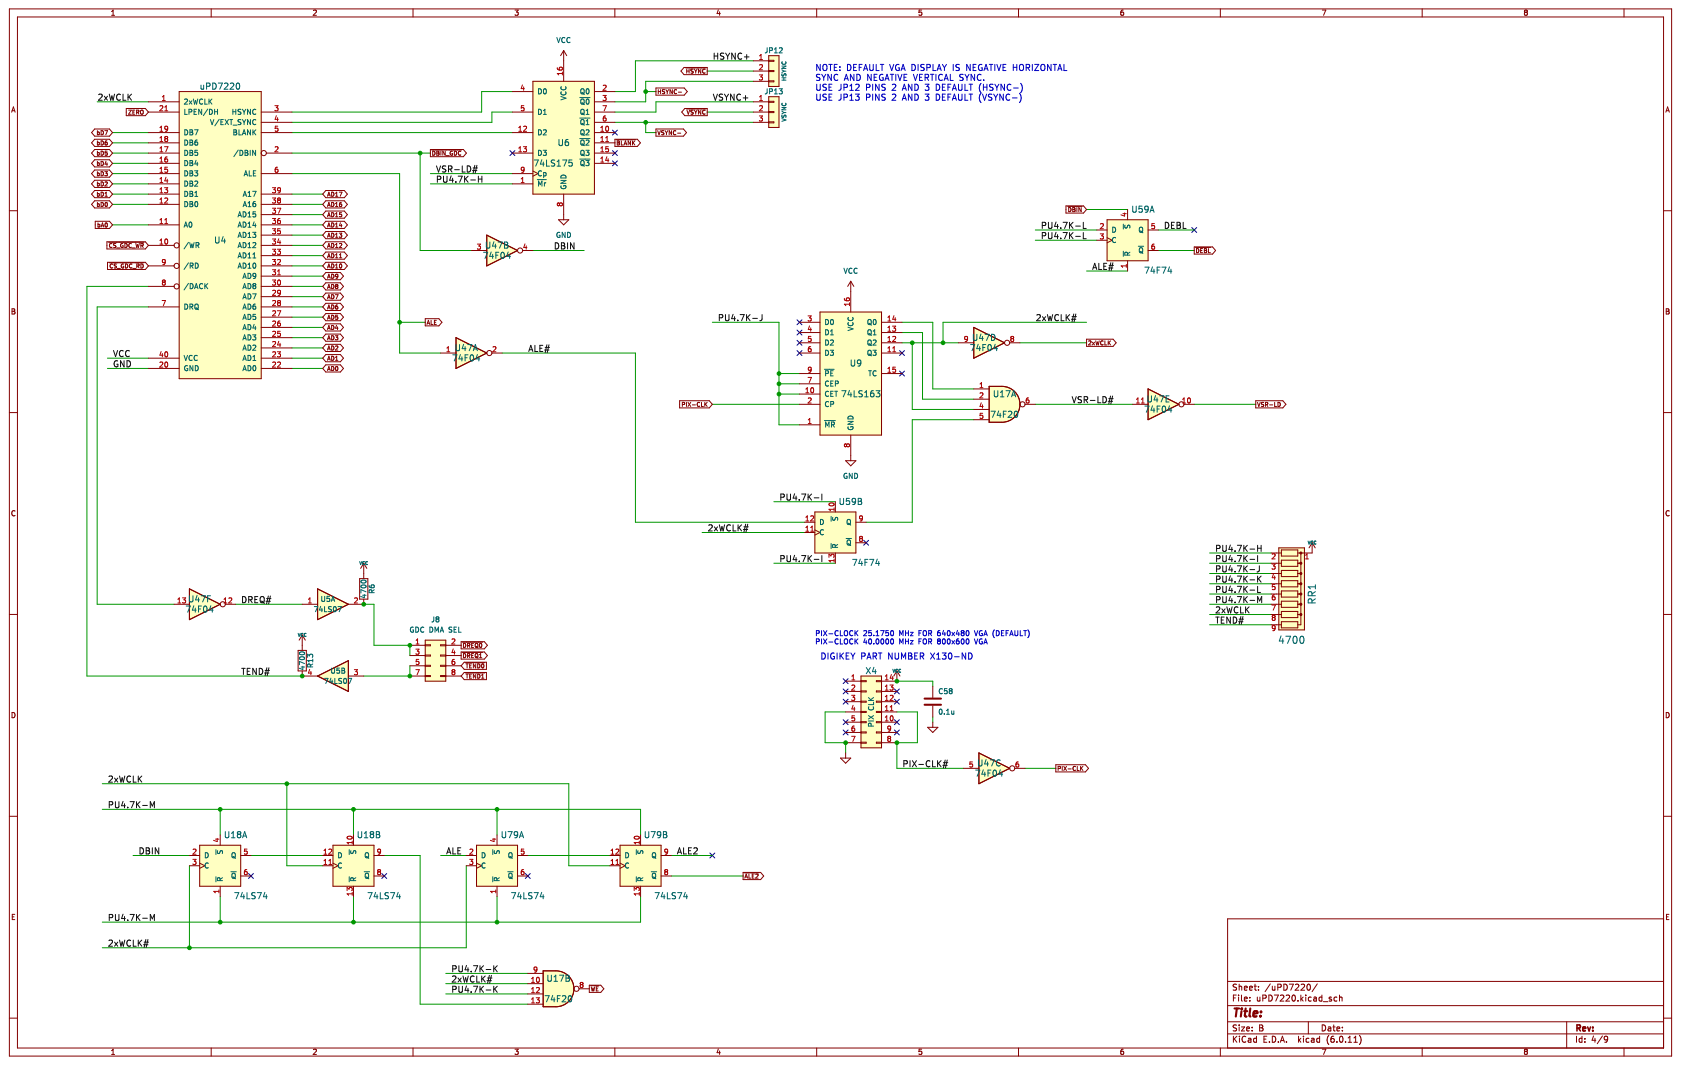
[picture p286: page 4]

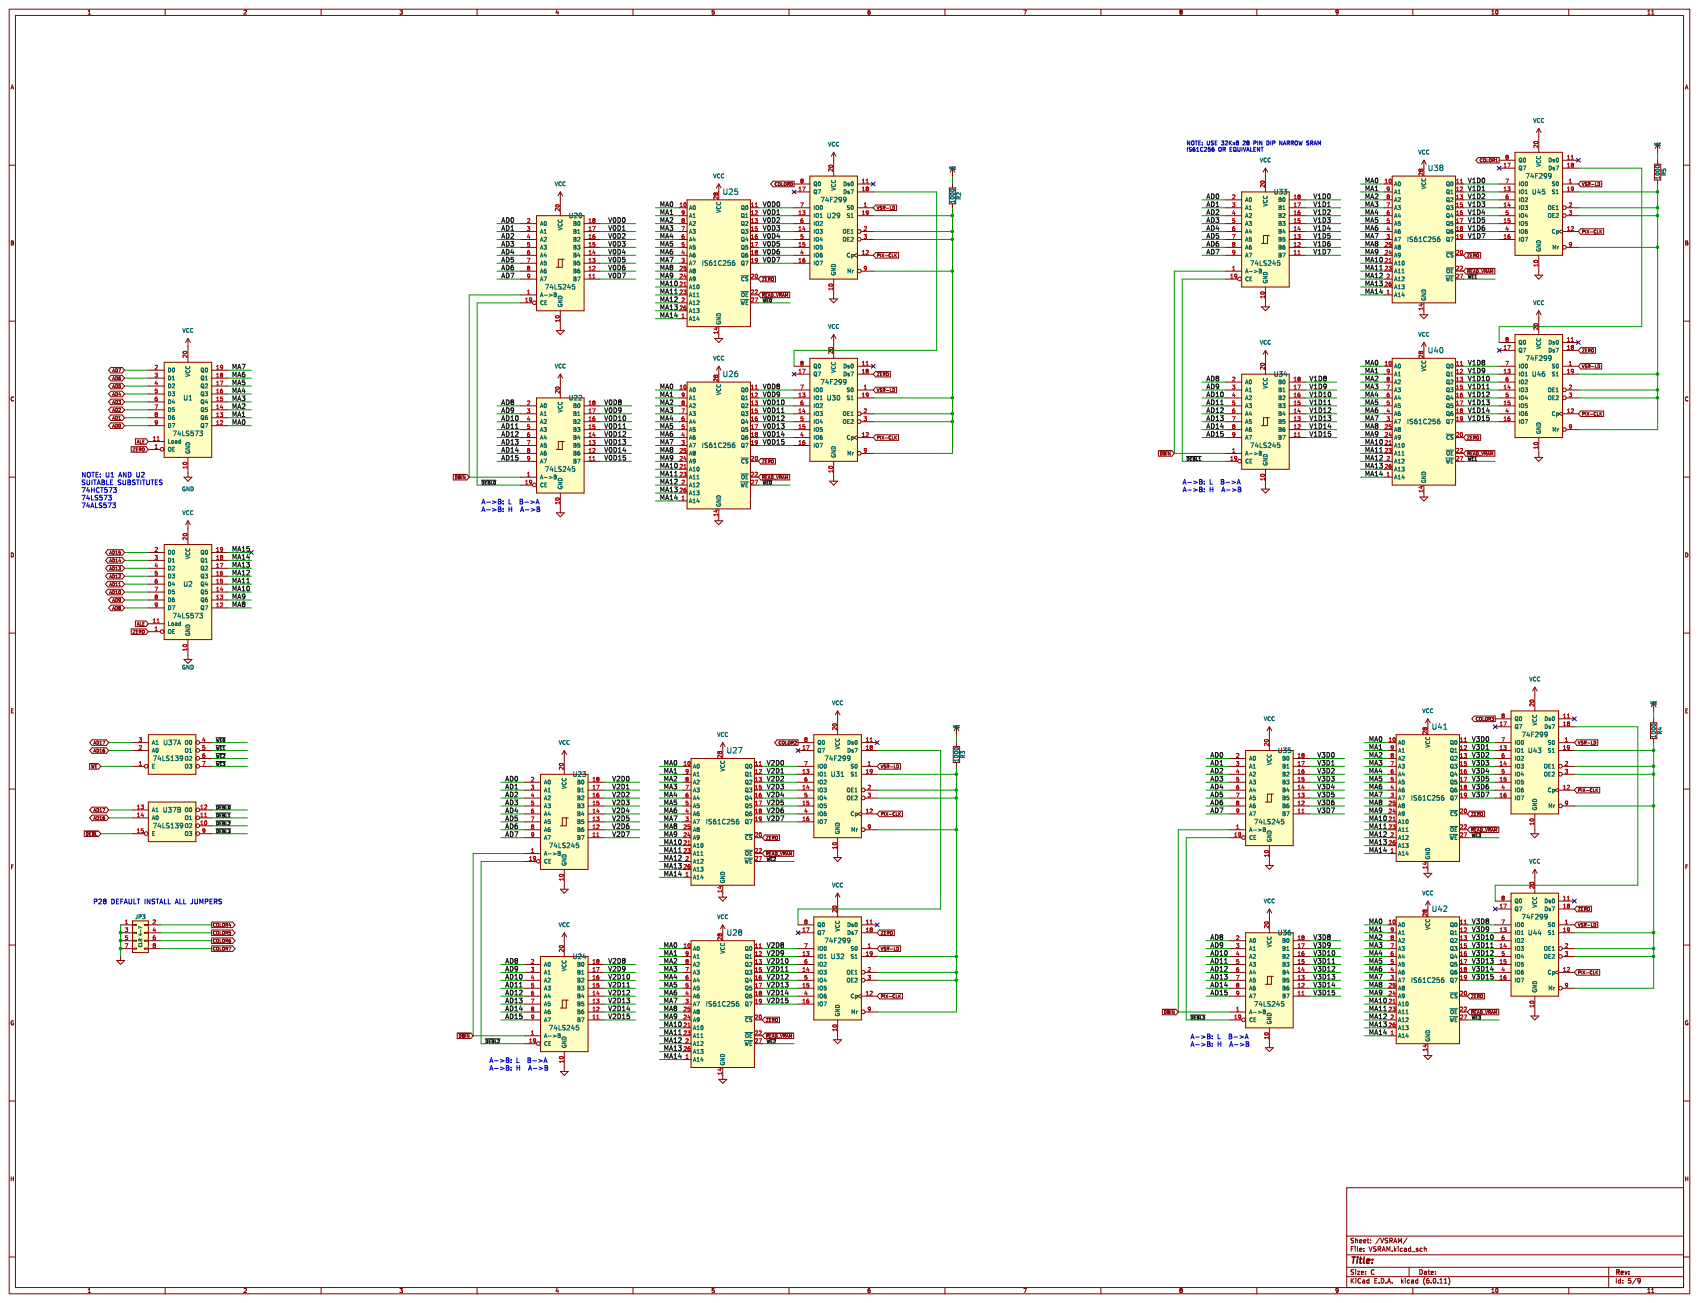
[picture p287: page 5]

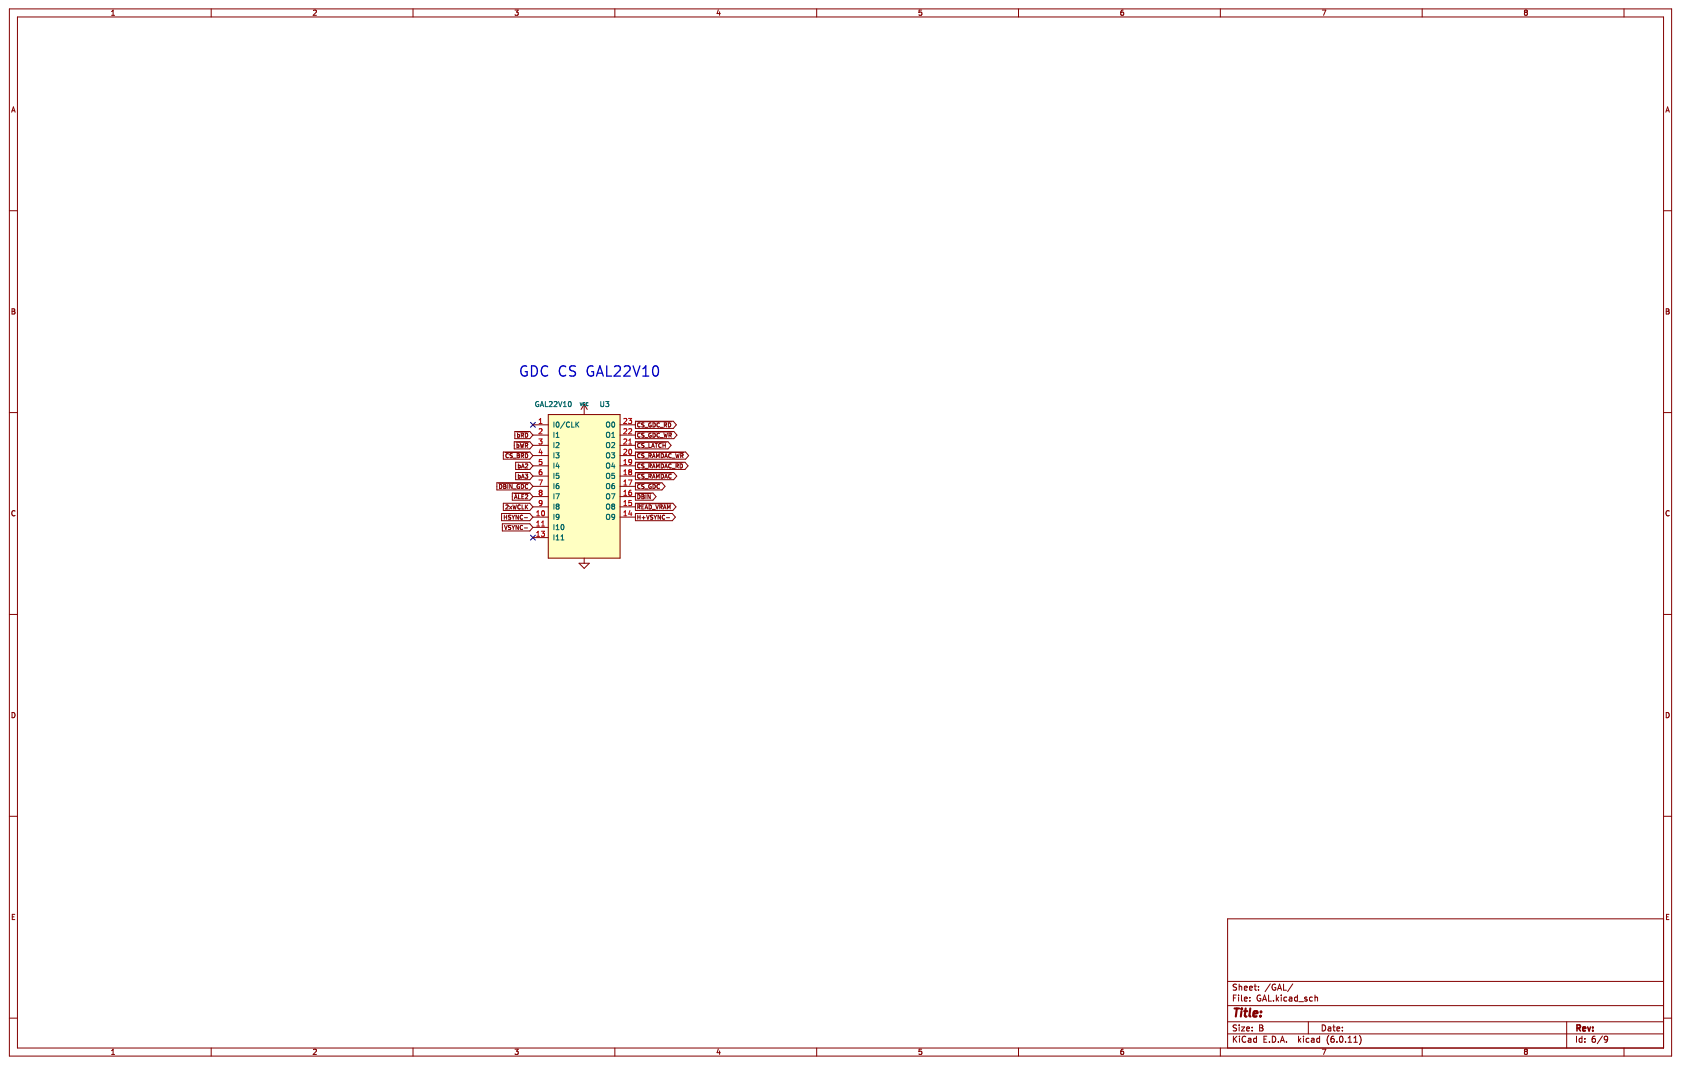
[picture p288: page 6]

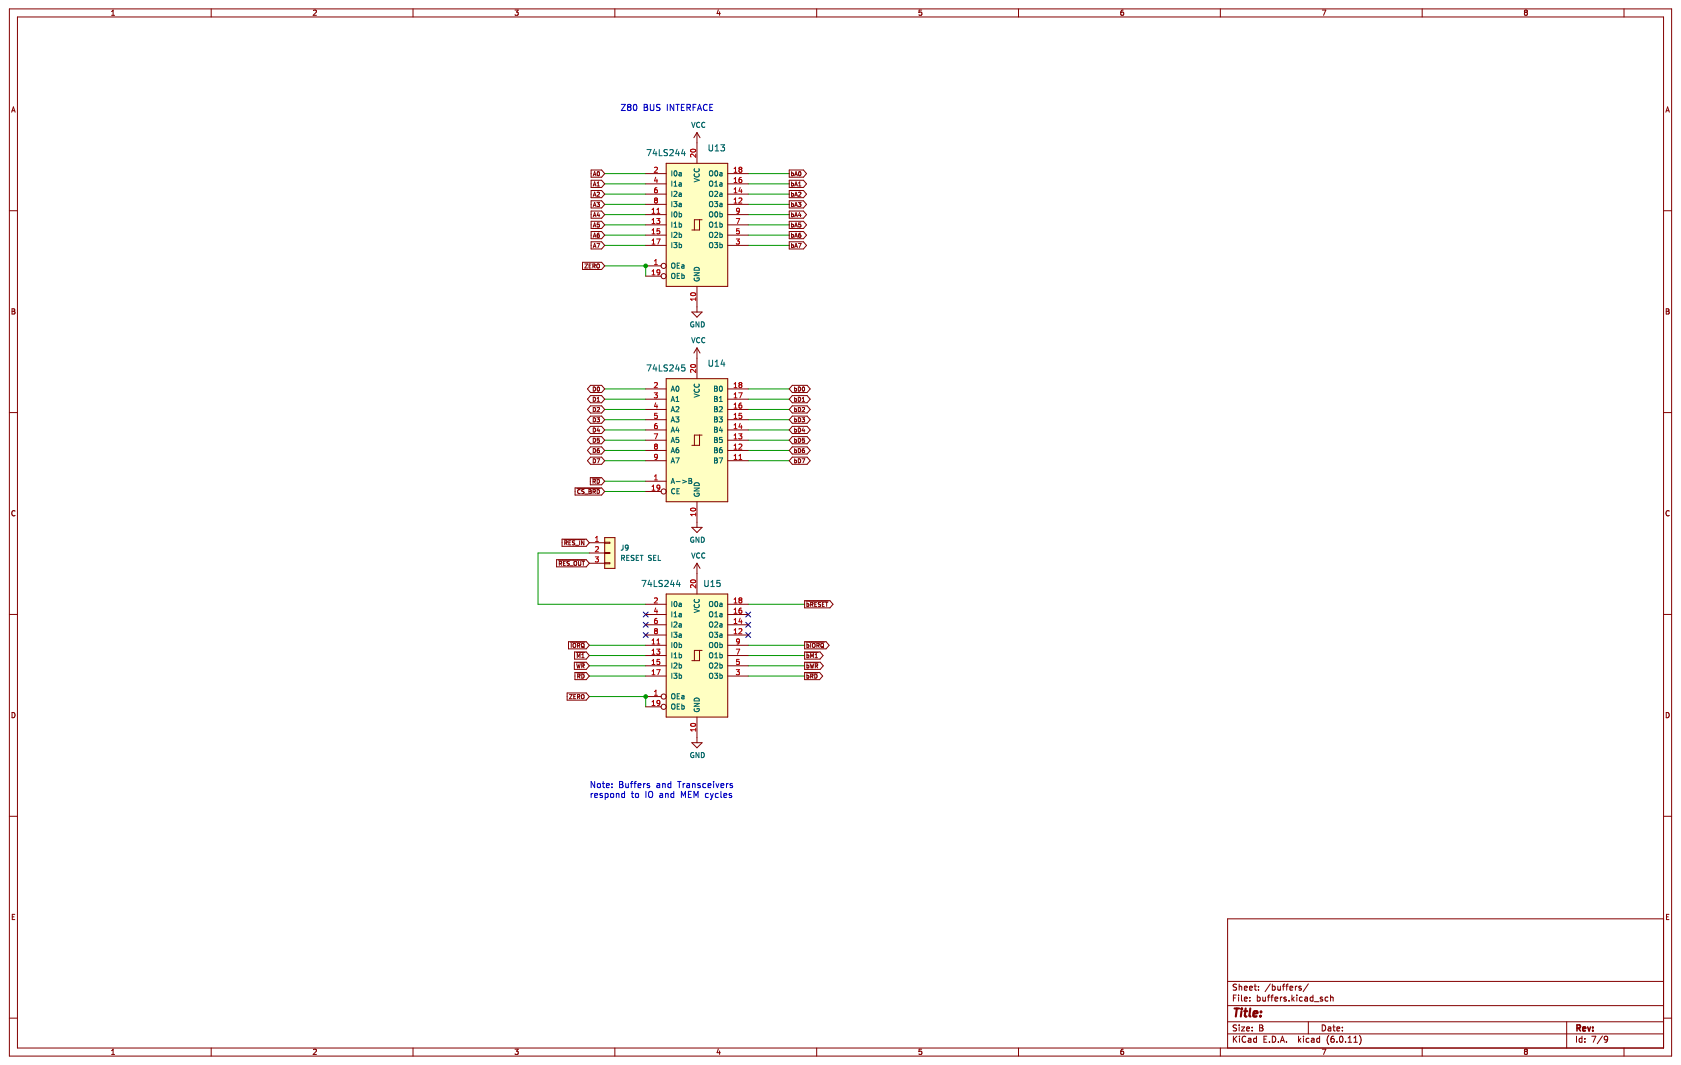
[picture p289: page 7]

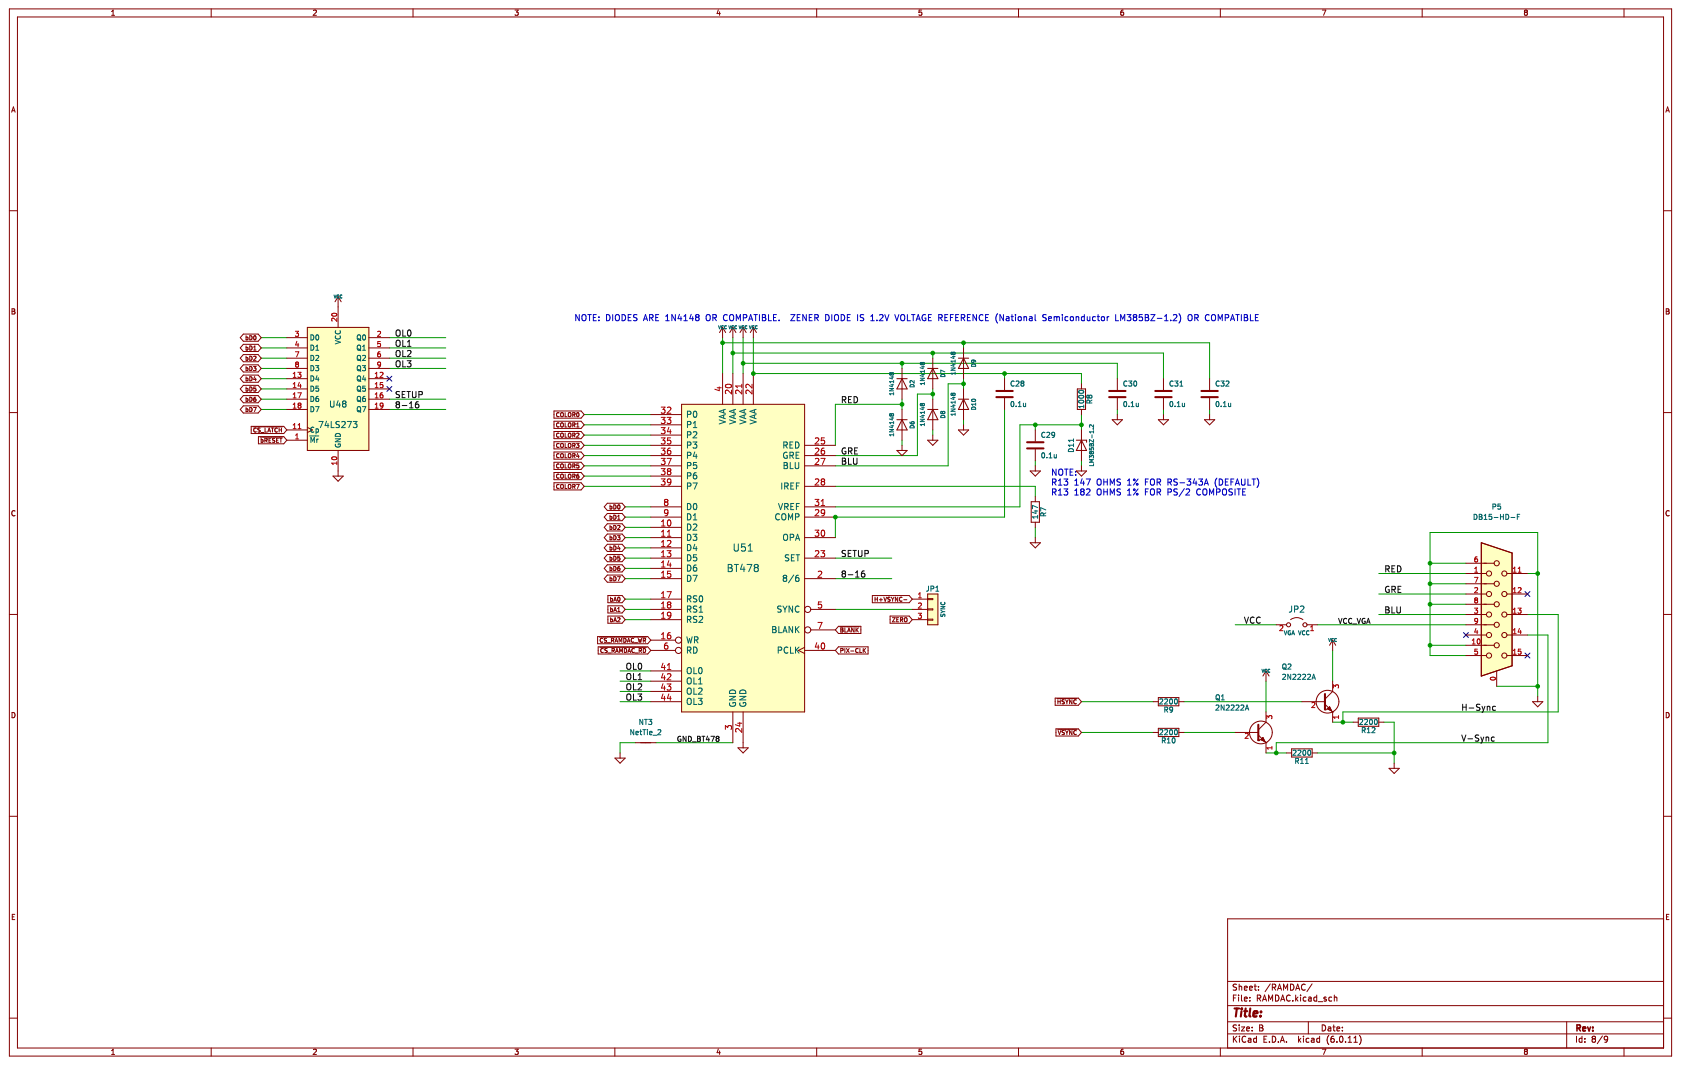
[picture p290: page 8]

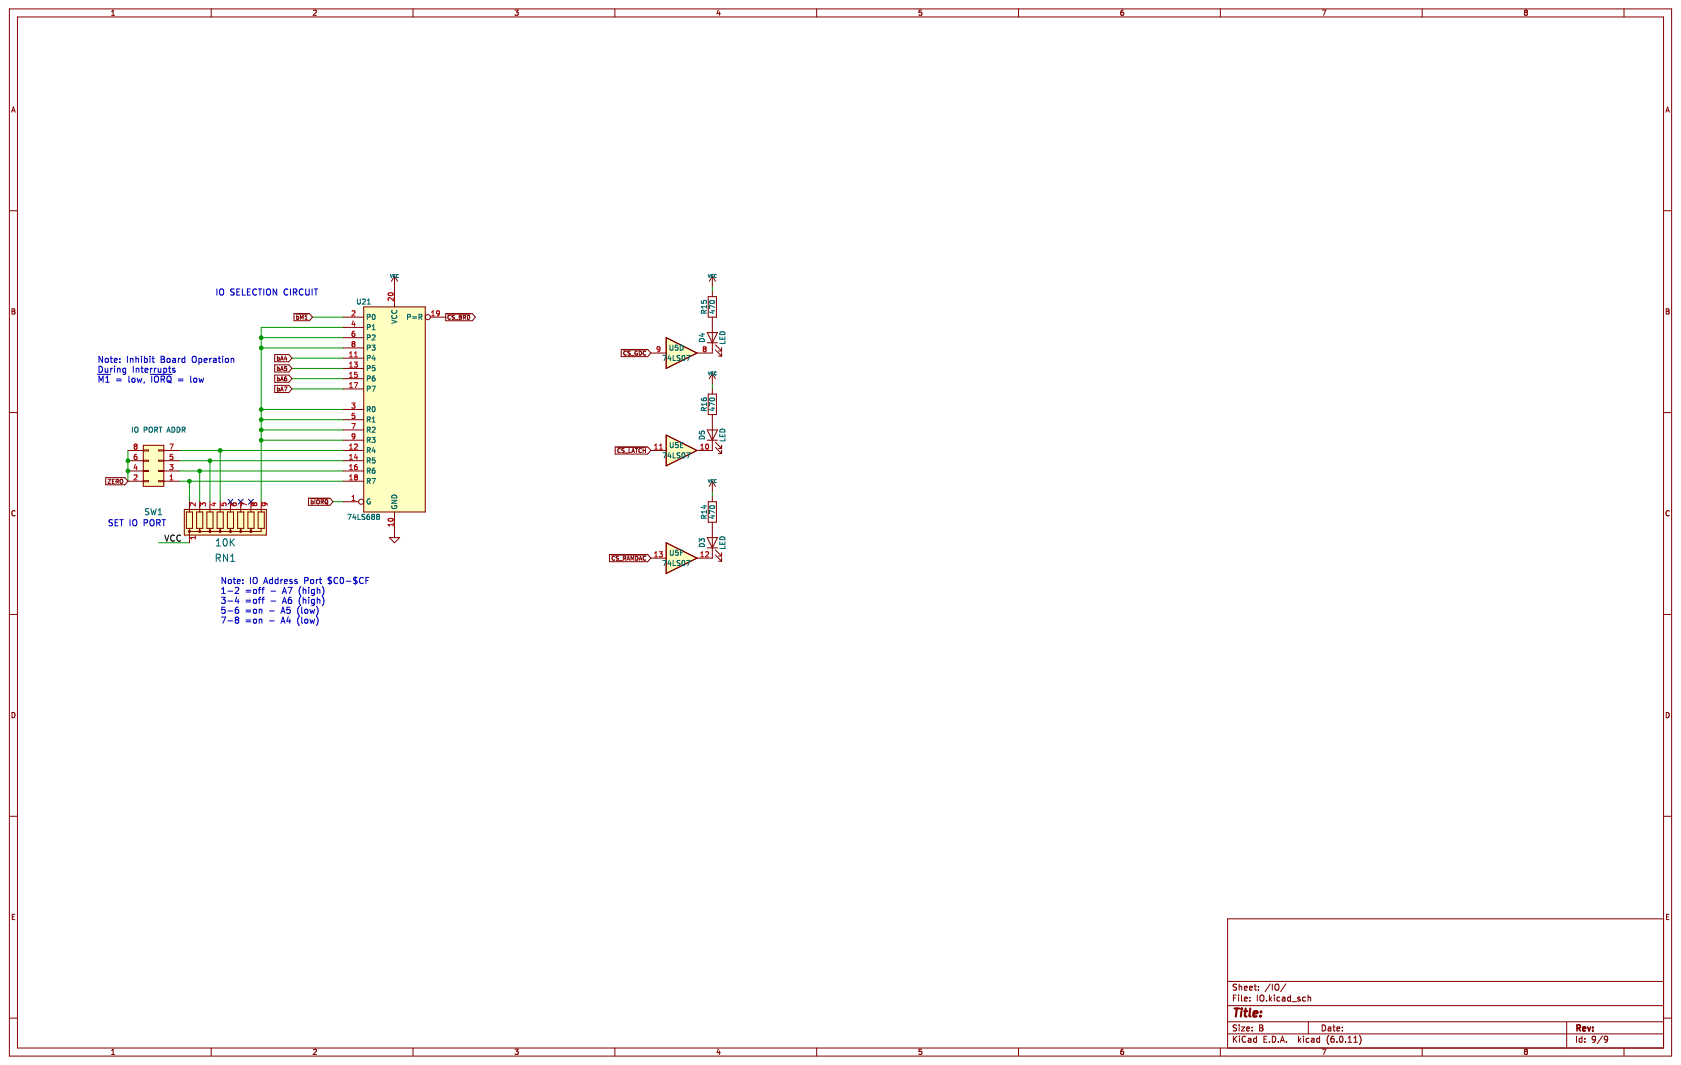
[picture p291: page 9]
