lynchaj/duodyne/!Development/SAB80535-Dev-Board V1.1/SAB80535-Dev-Board.schematic.pdf

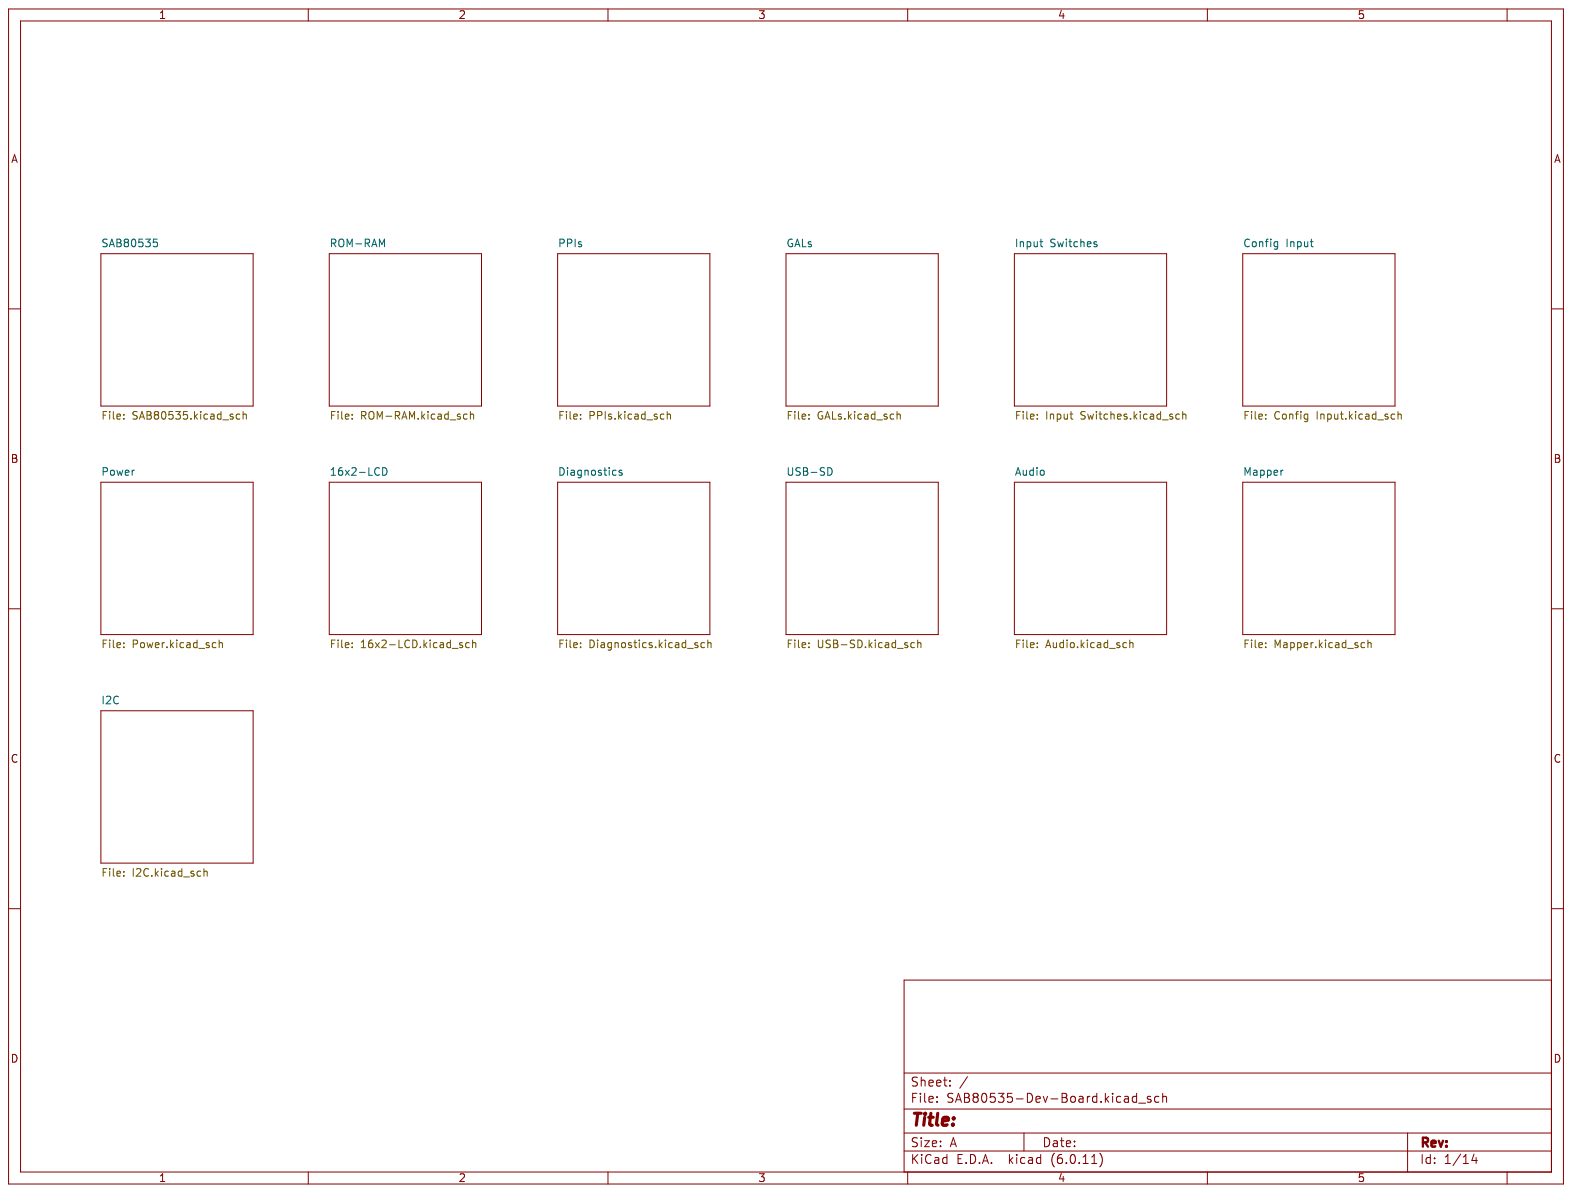
[picture p292: page 1]

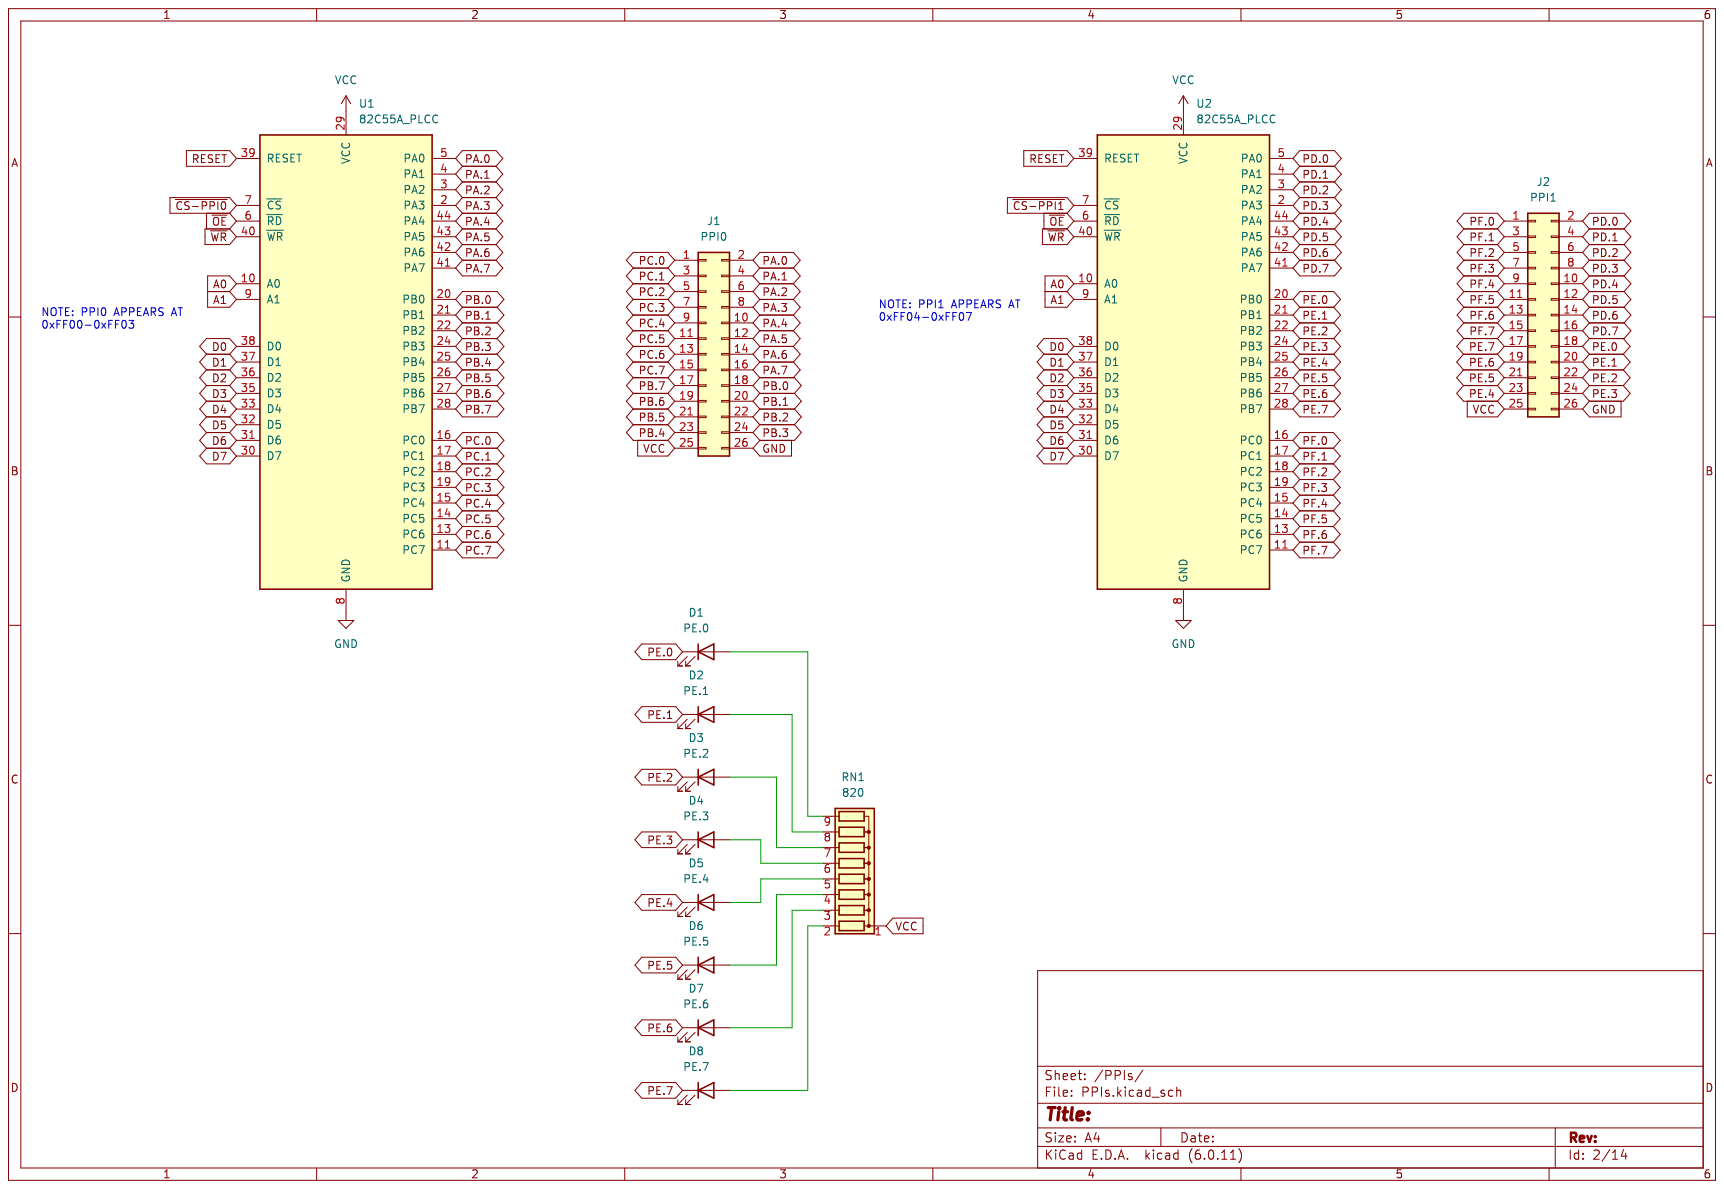
[picture p293: page 2]

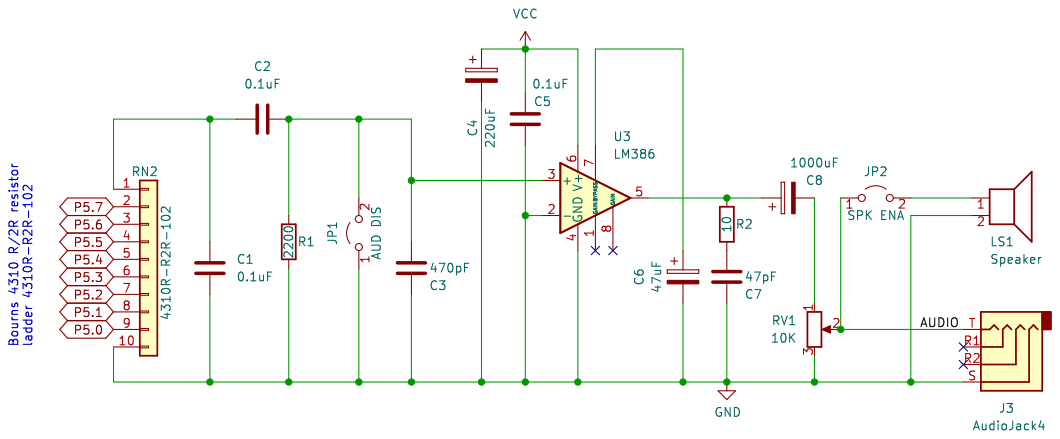
[picture p294: page 3]

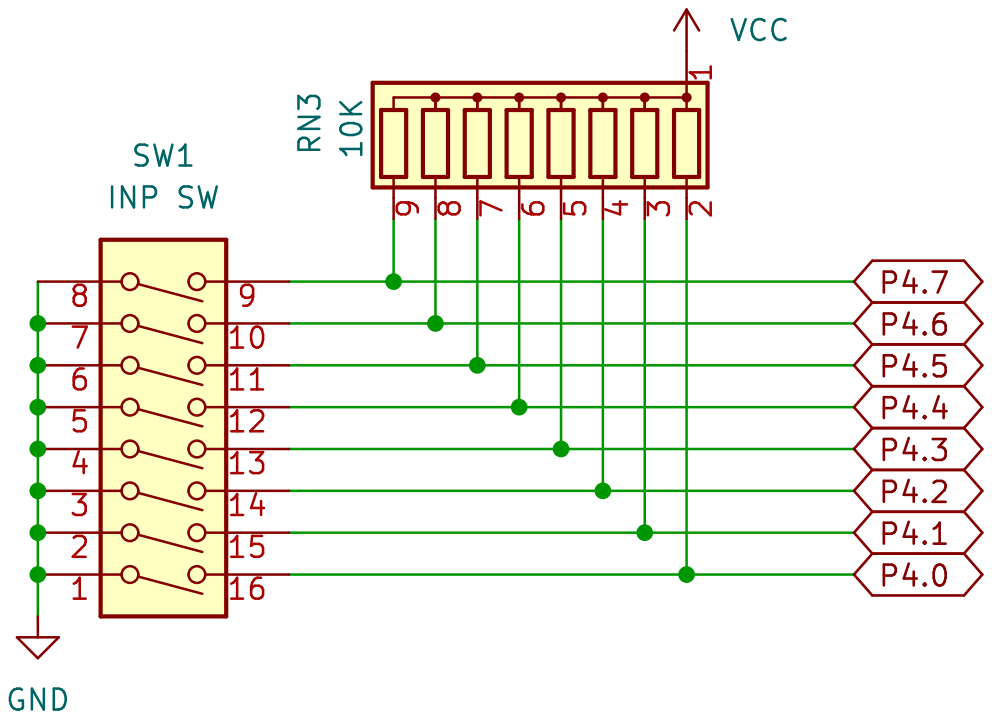
[picture p295: page 4]

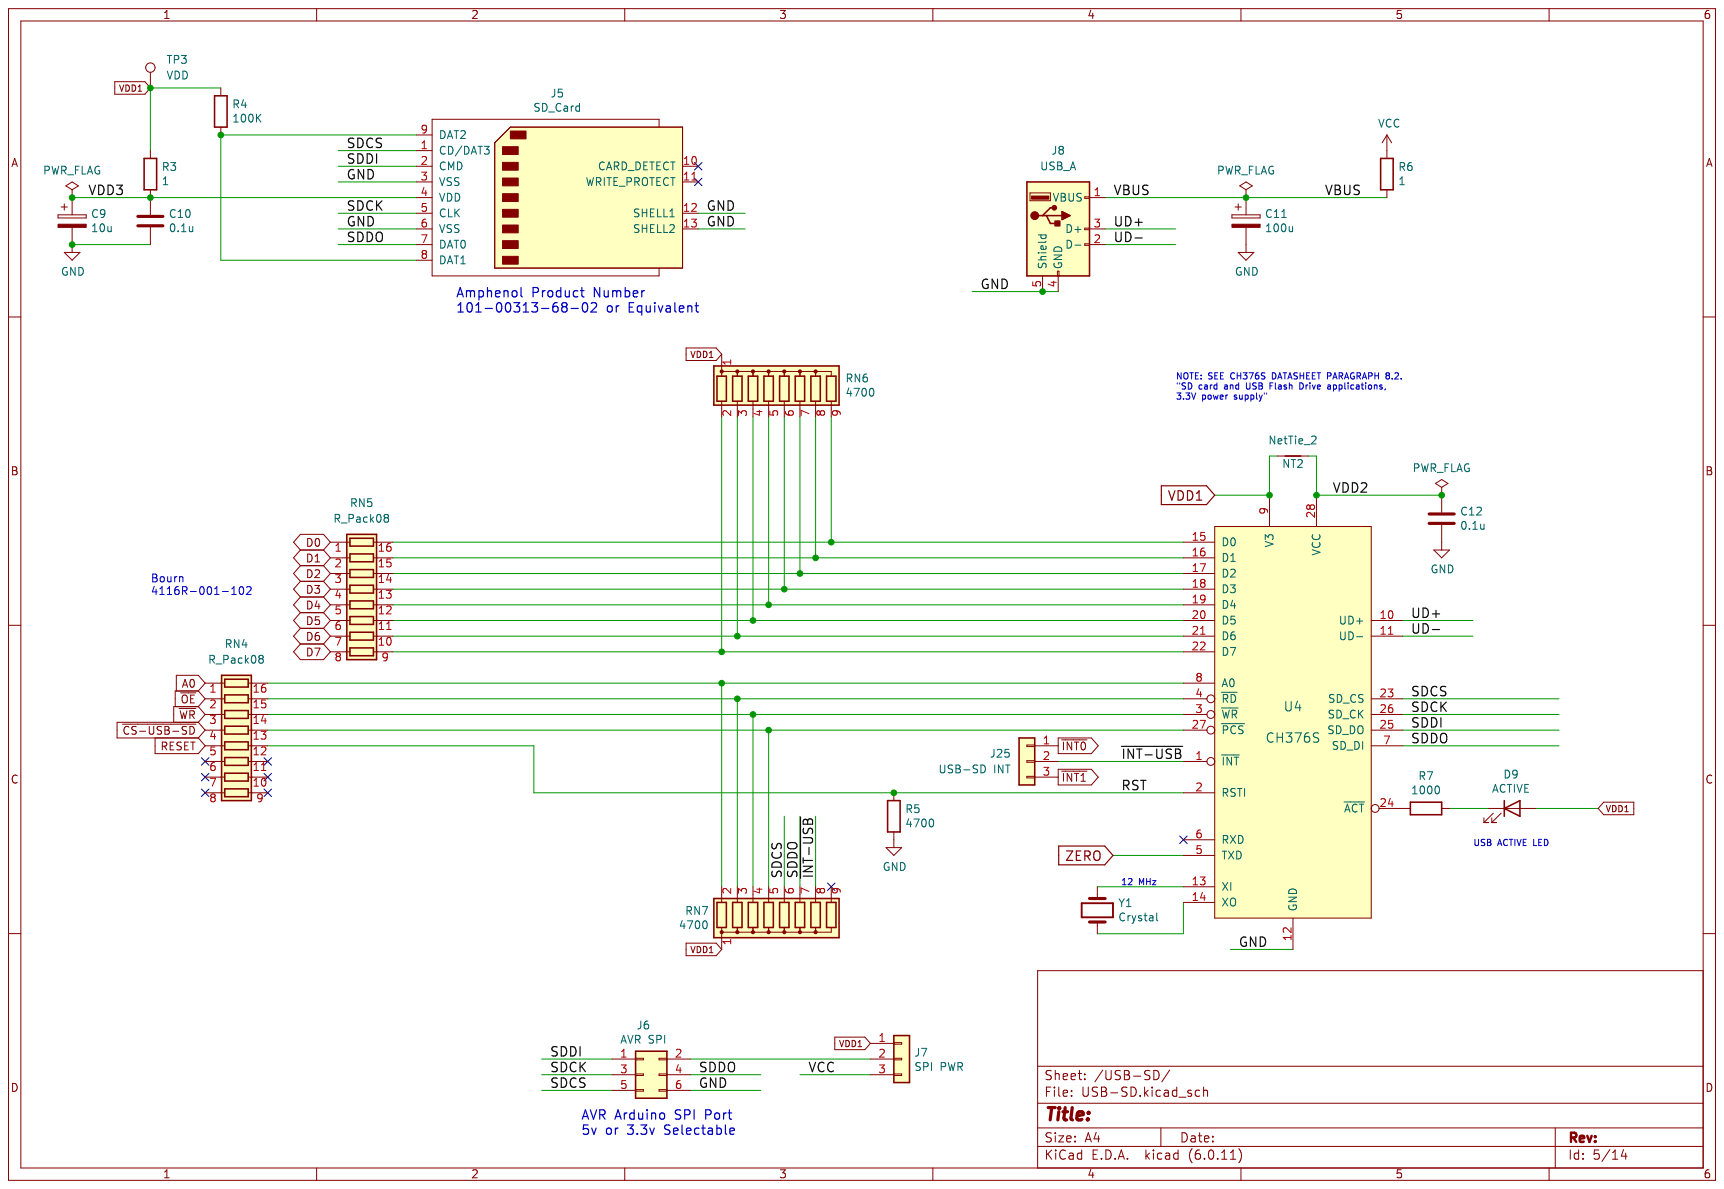
[picture p296: page 5]

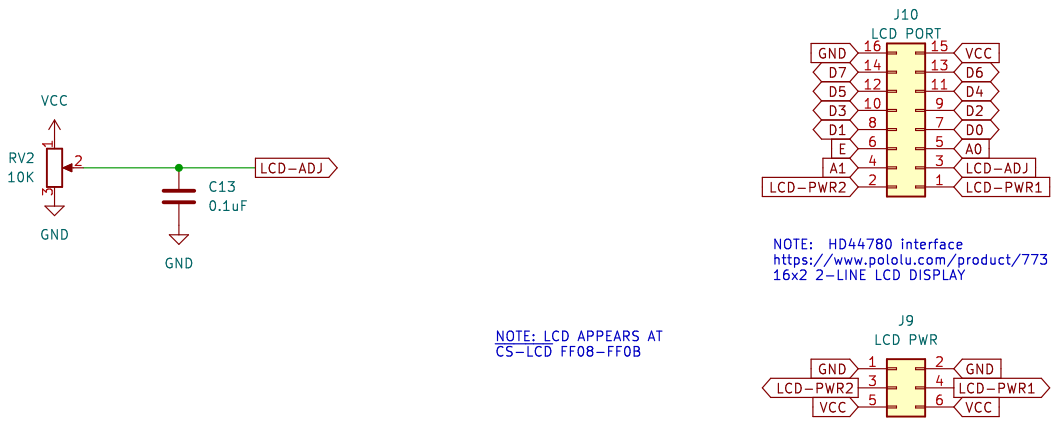
[picture p297: page 6]

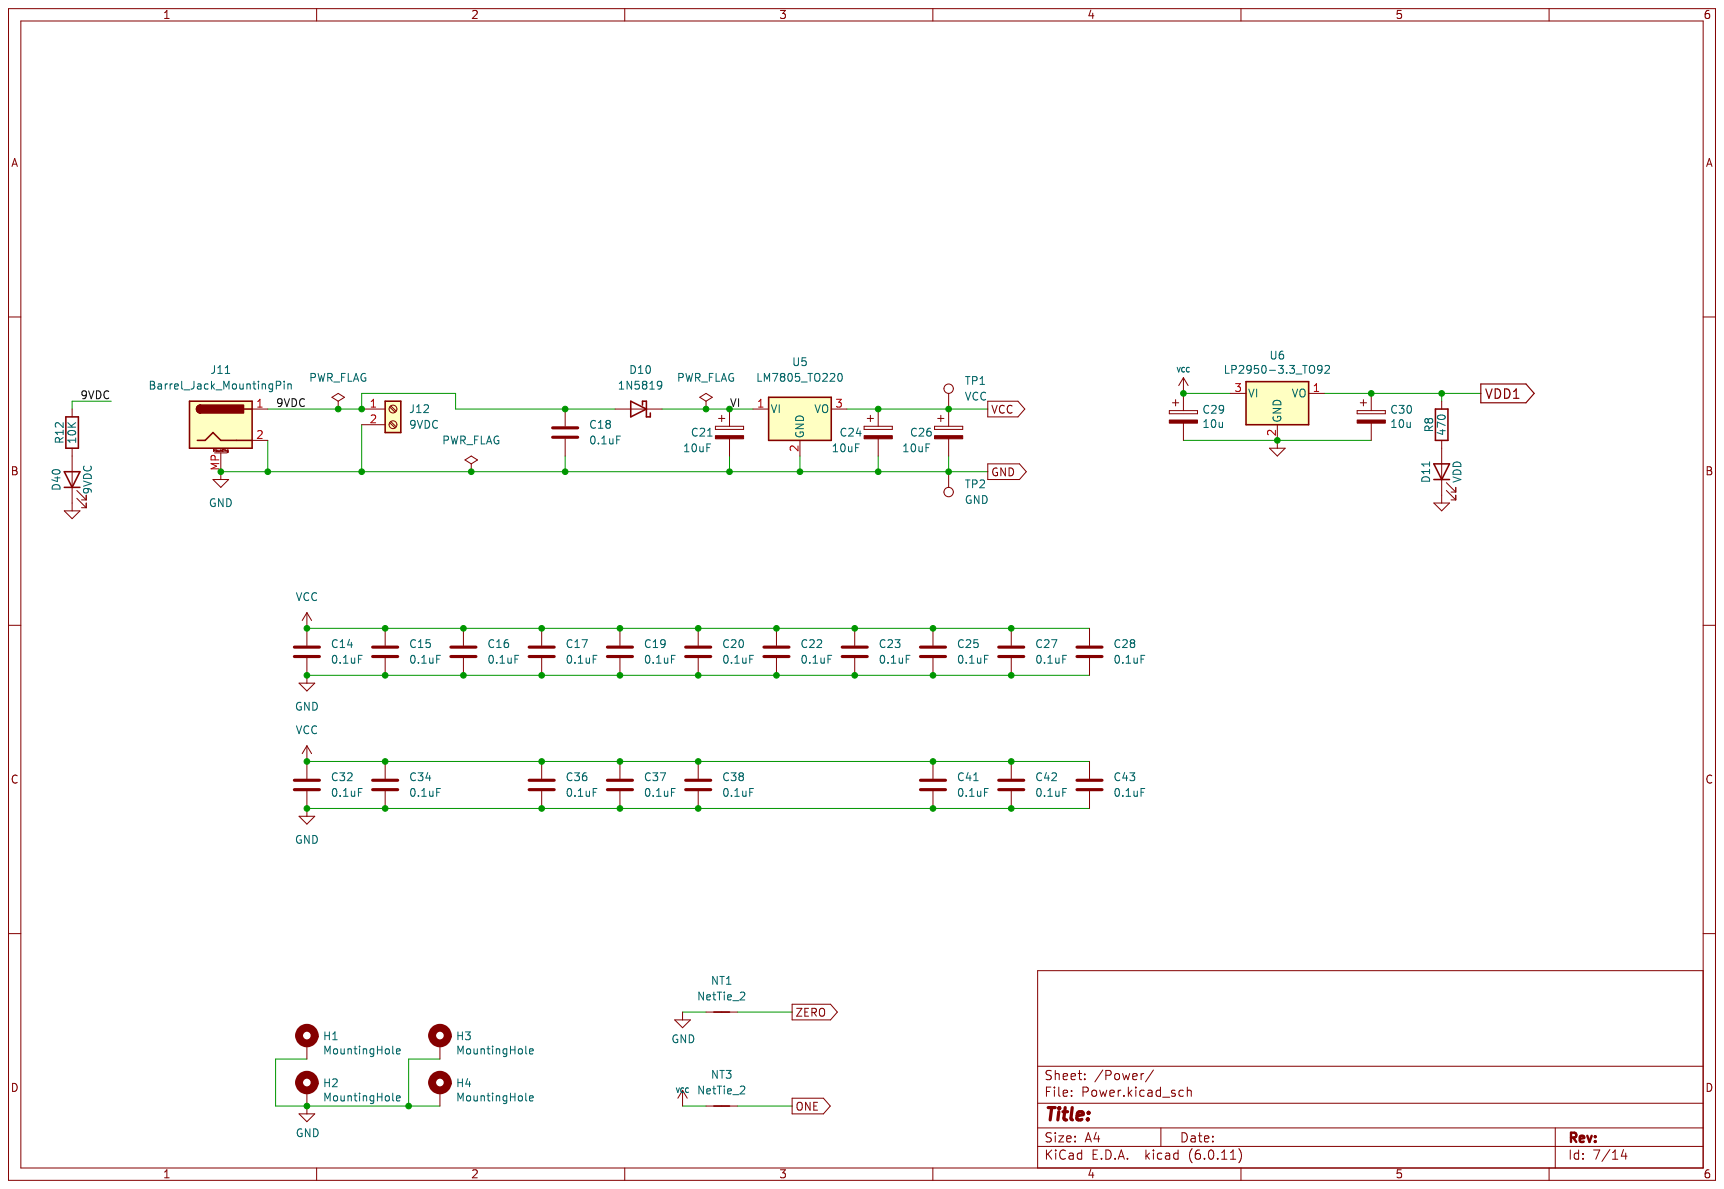
[picture p298: page 7]

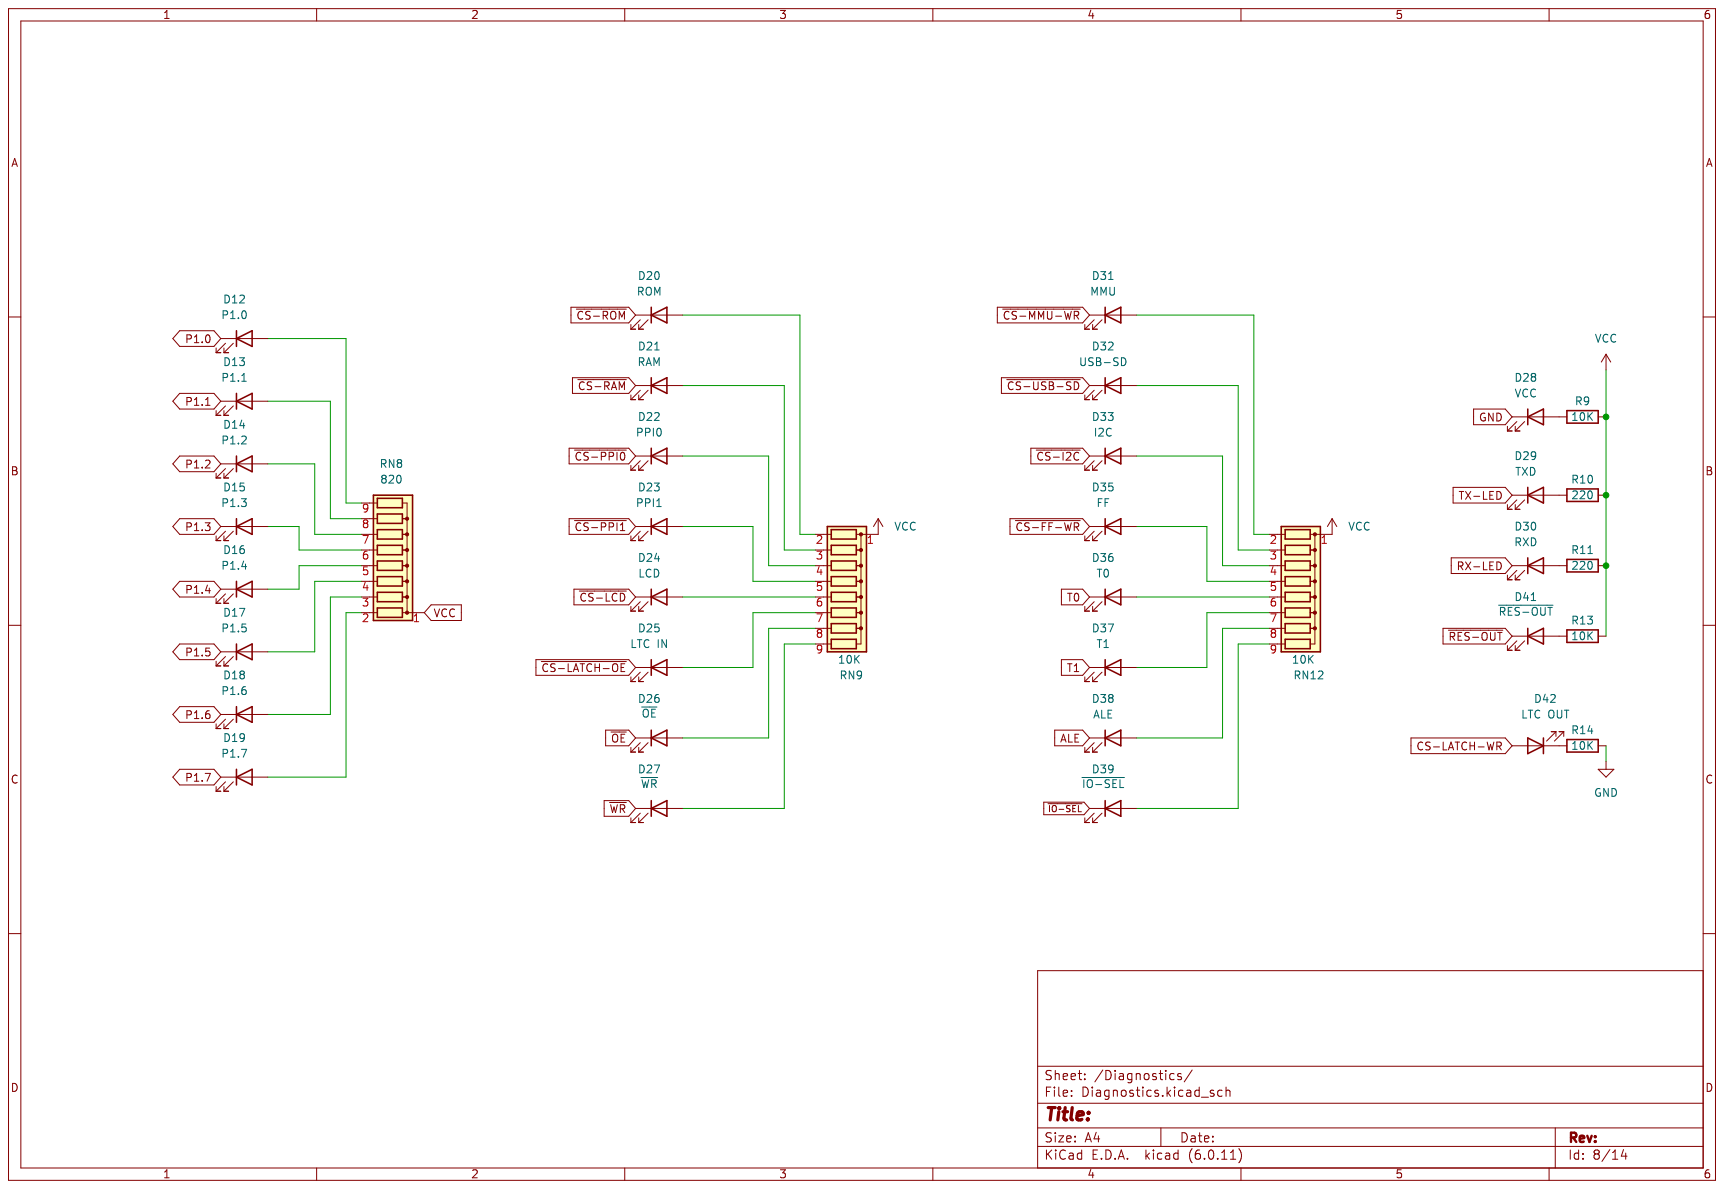
[picture p299: page 8]

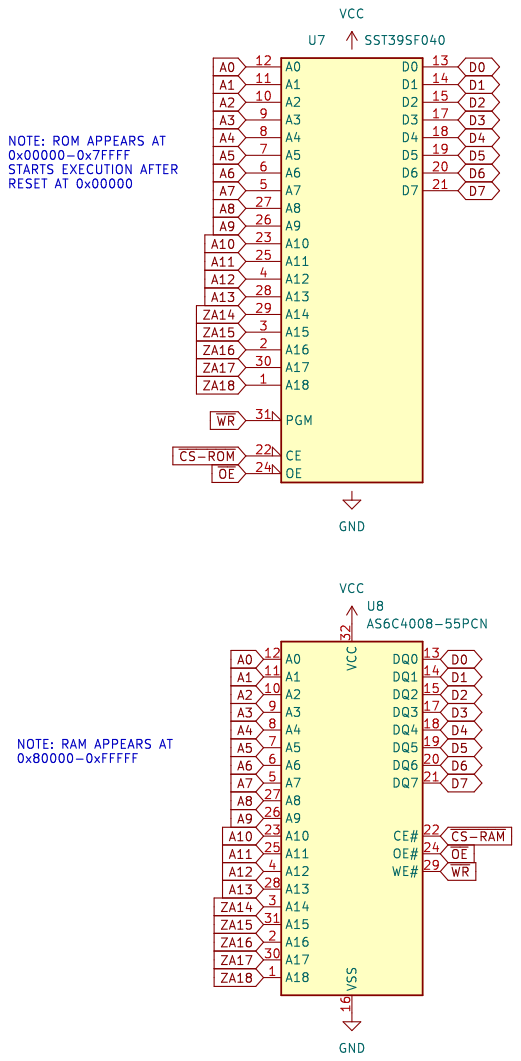
[picture p300: page 9]

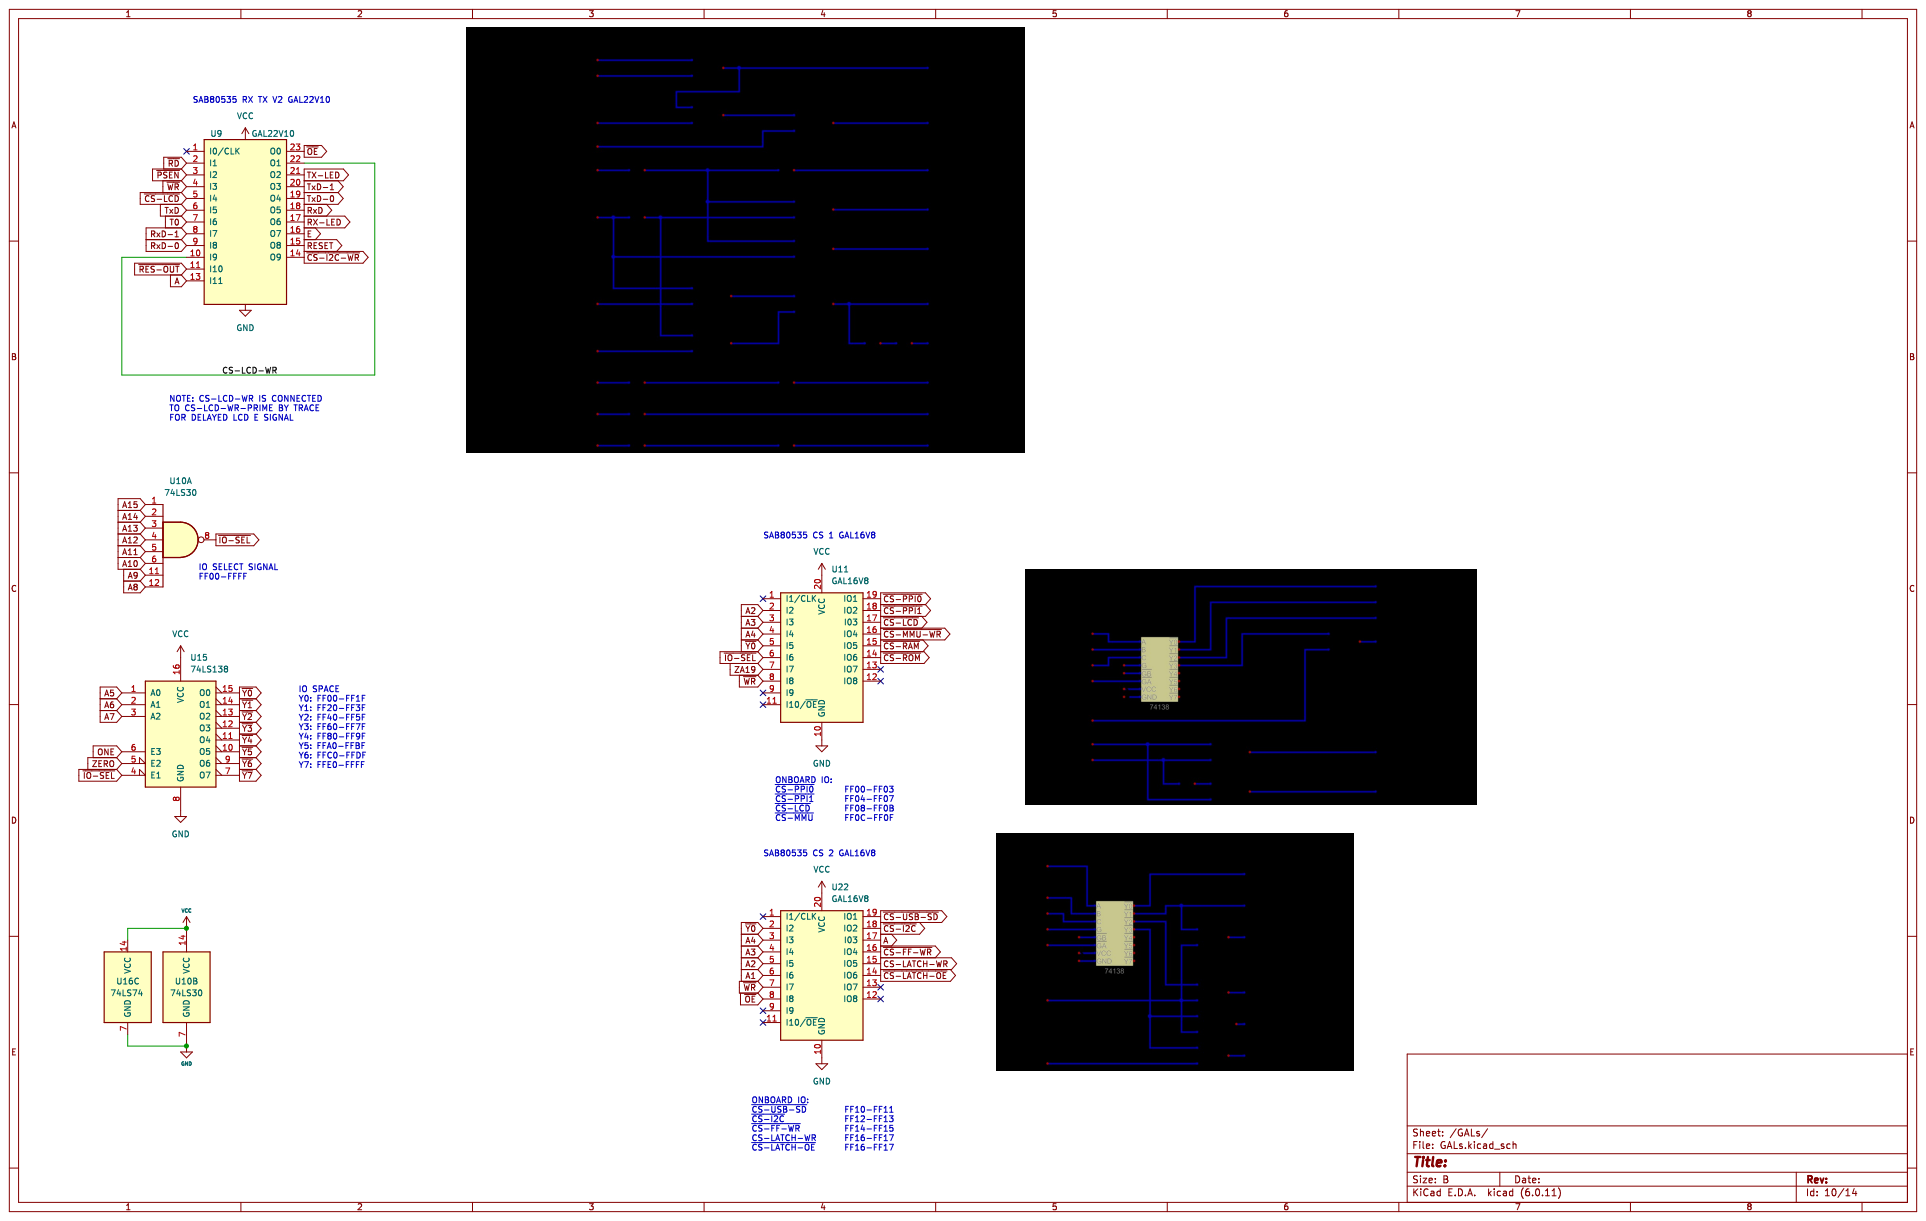
[picture p301: page 10]

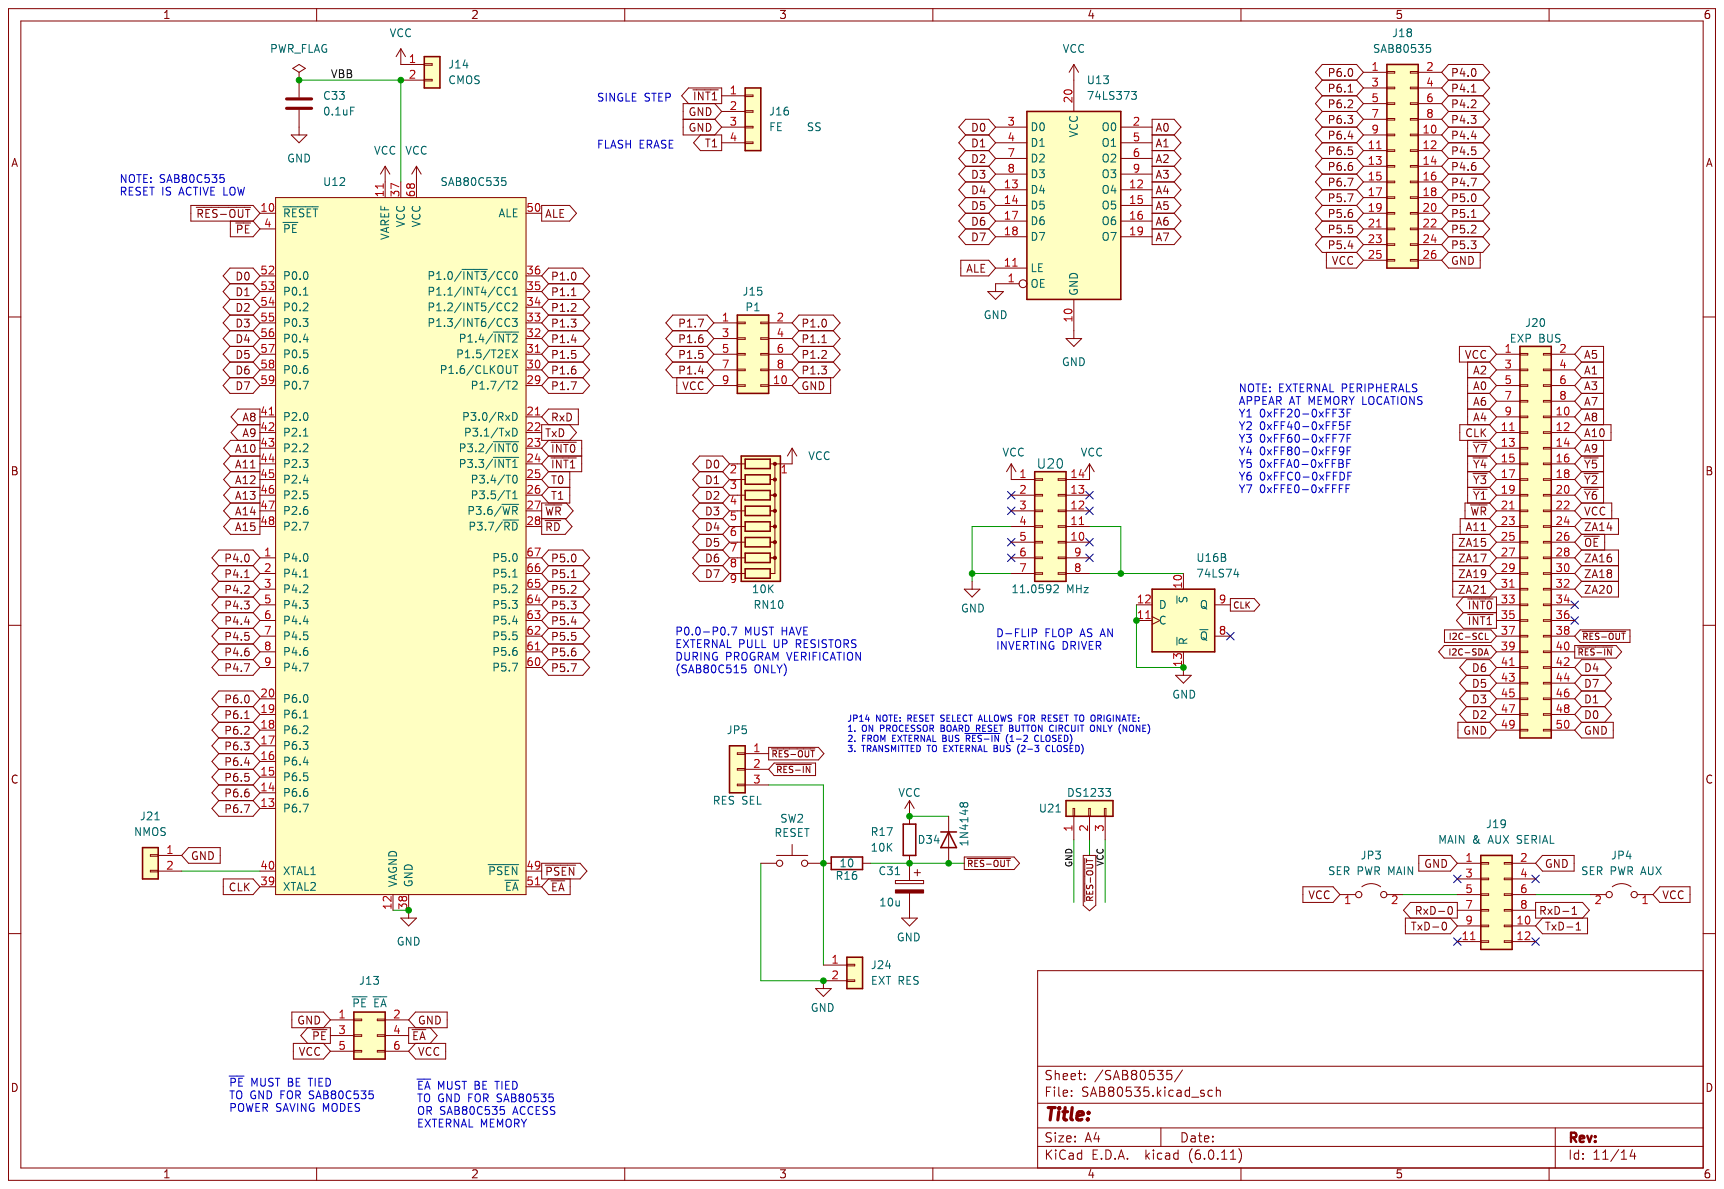
[picture p302: page 11]

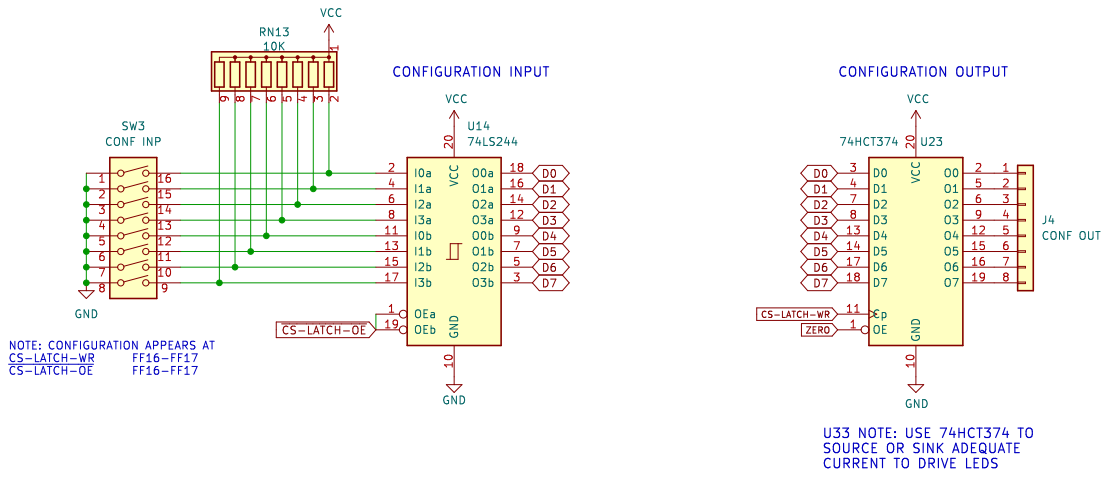
[picture p303: page 12]

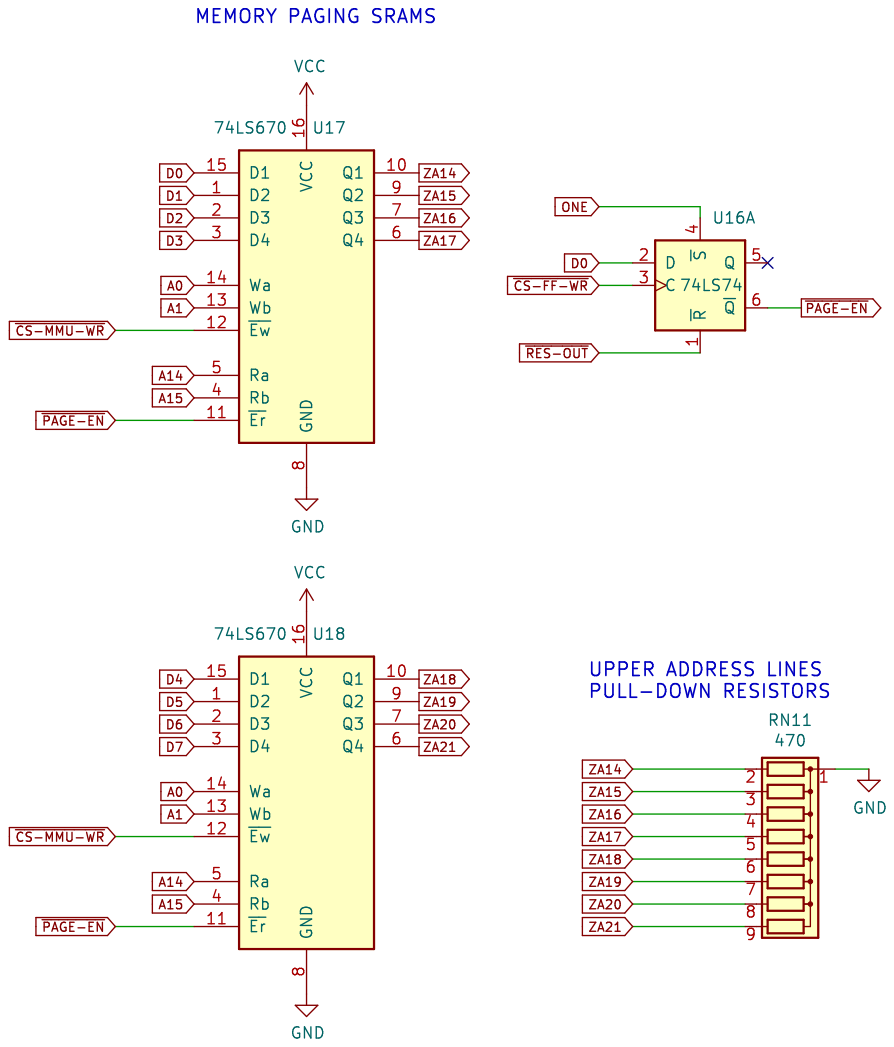
[picture p304: page 13]

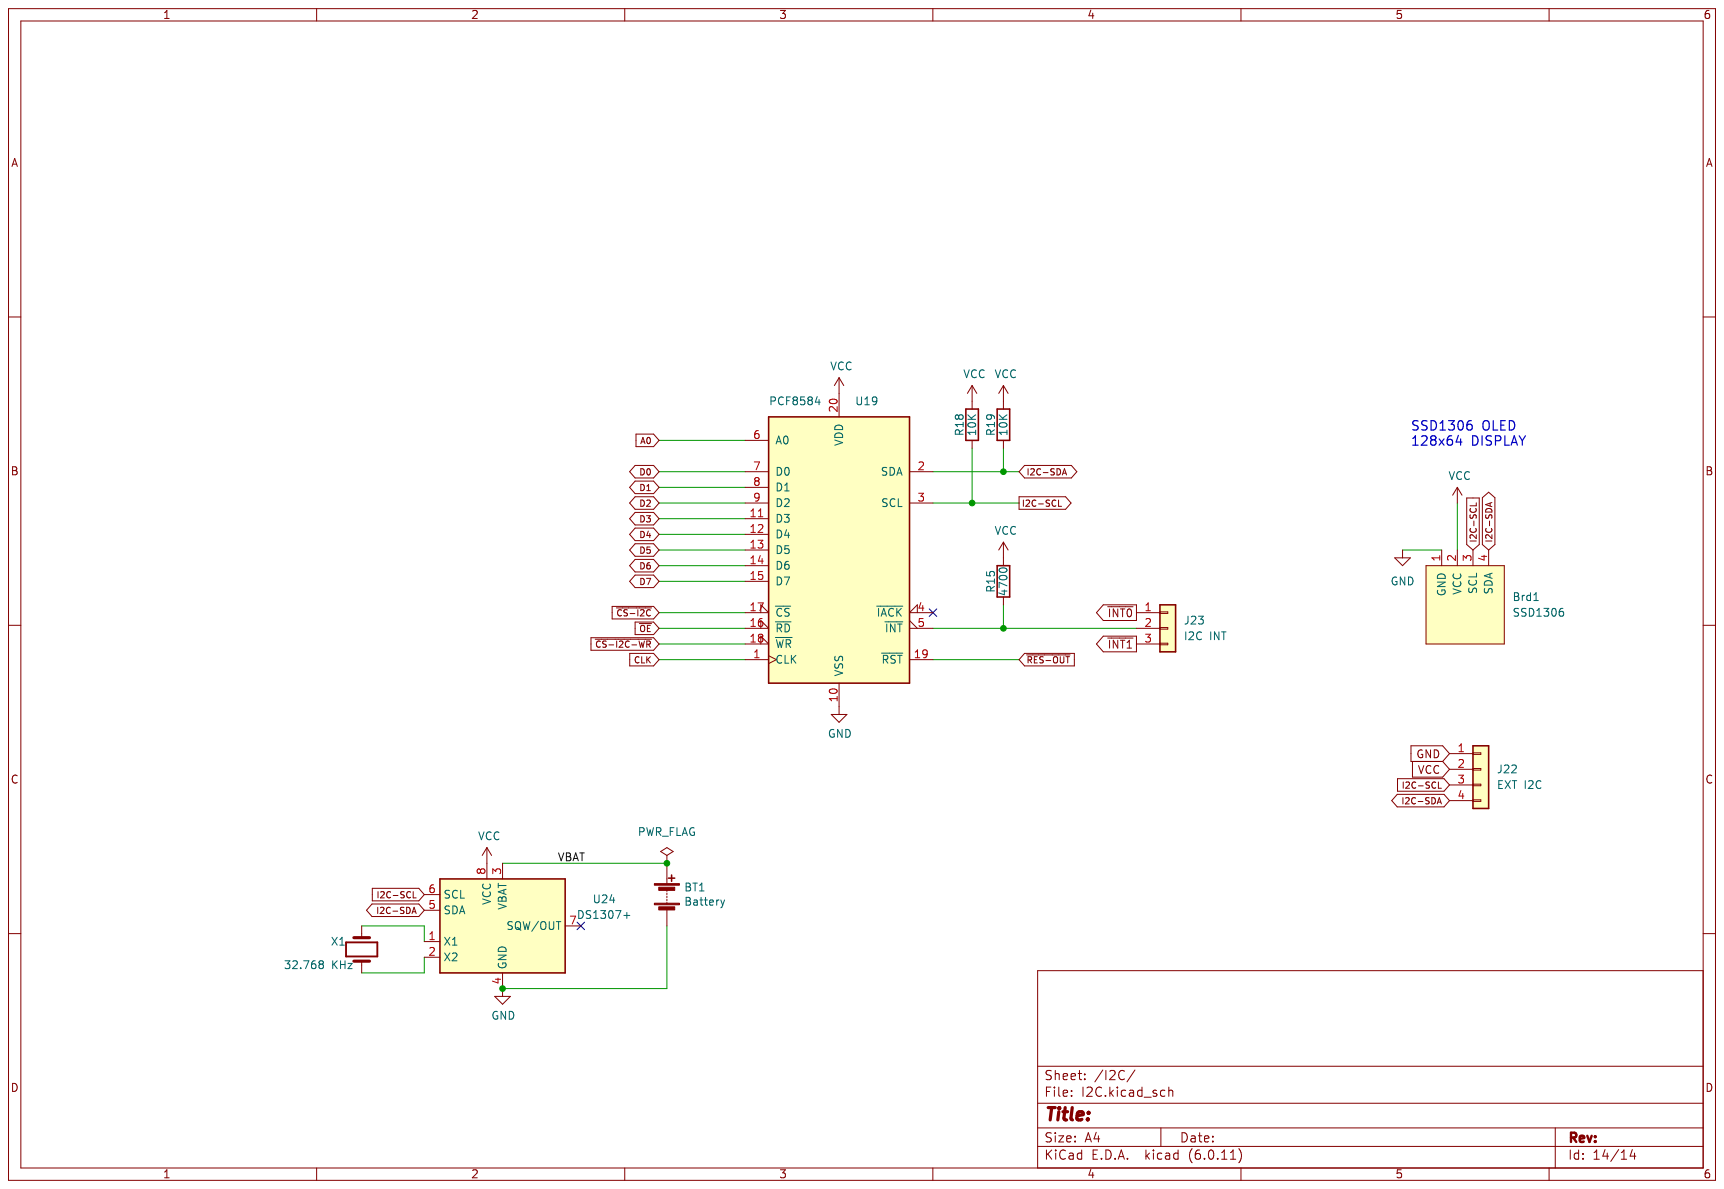
[picture p305: page 14]
