lynchaj/duodyne/!Development/16 input-output.VDCENET, V1.0/input-output.VDCENET.schematic.pdf

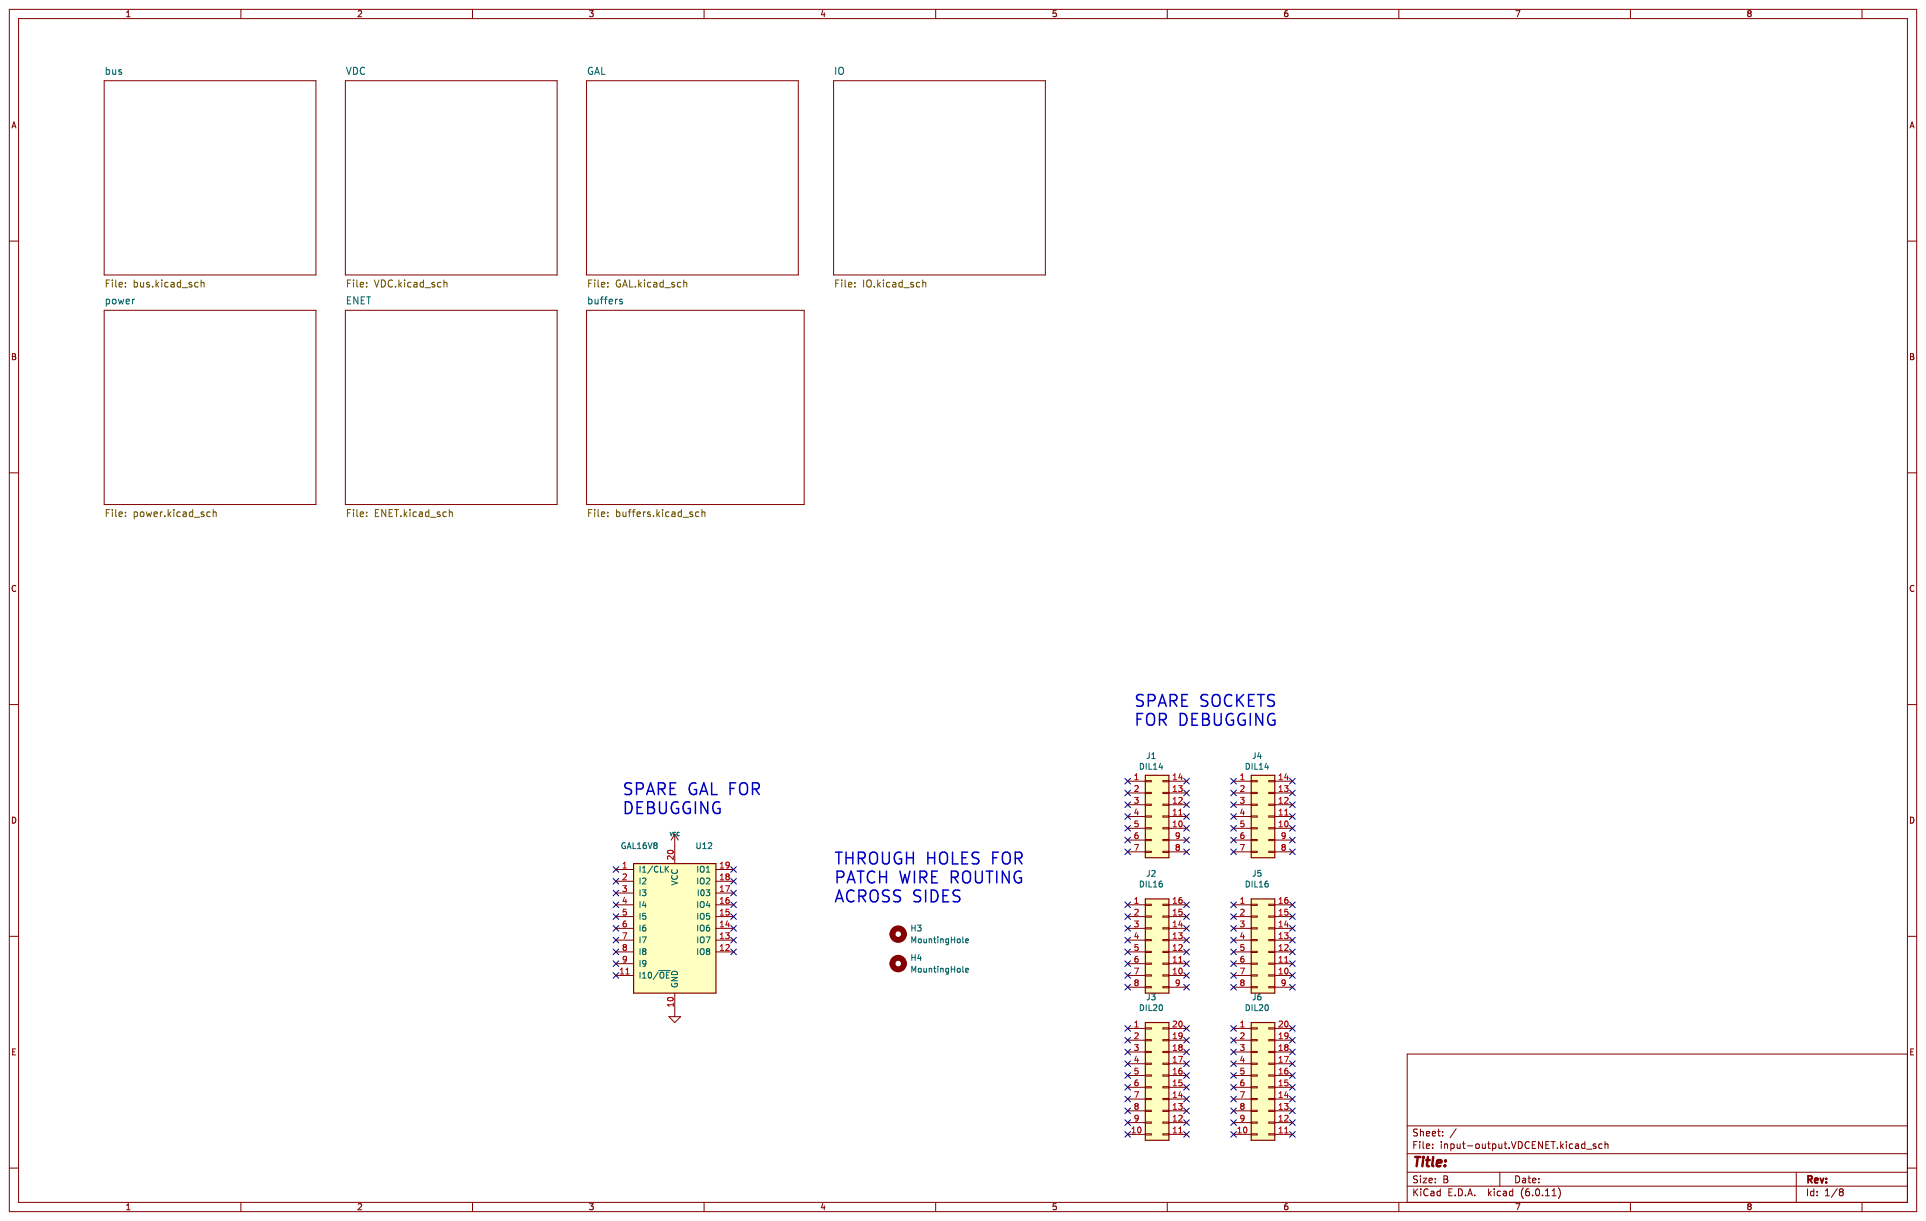
[picture p306: page 1]


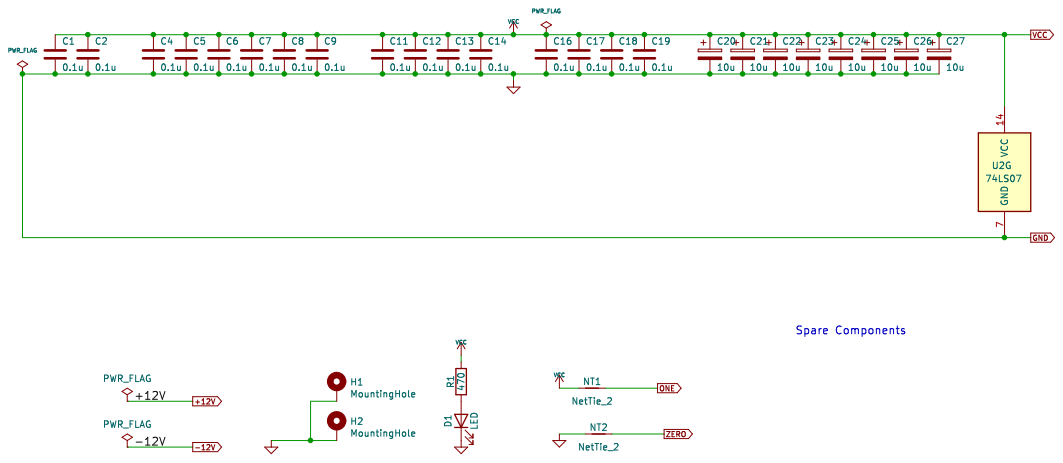
[picture p307: page 3]

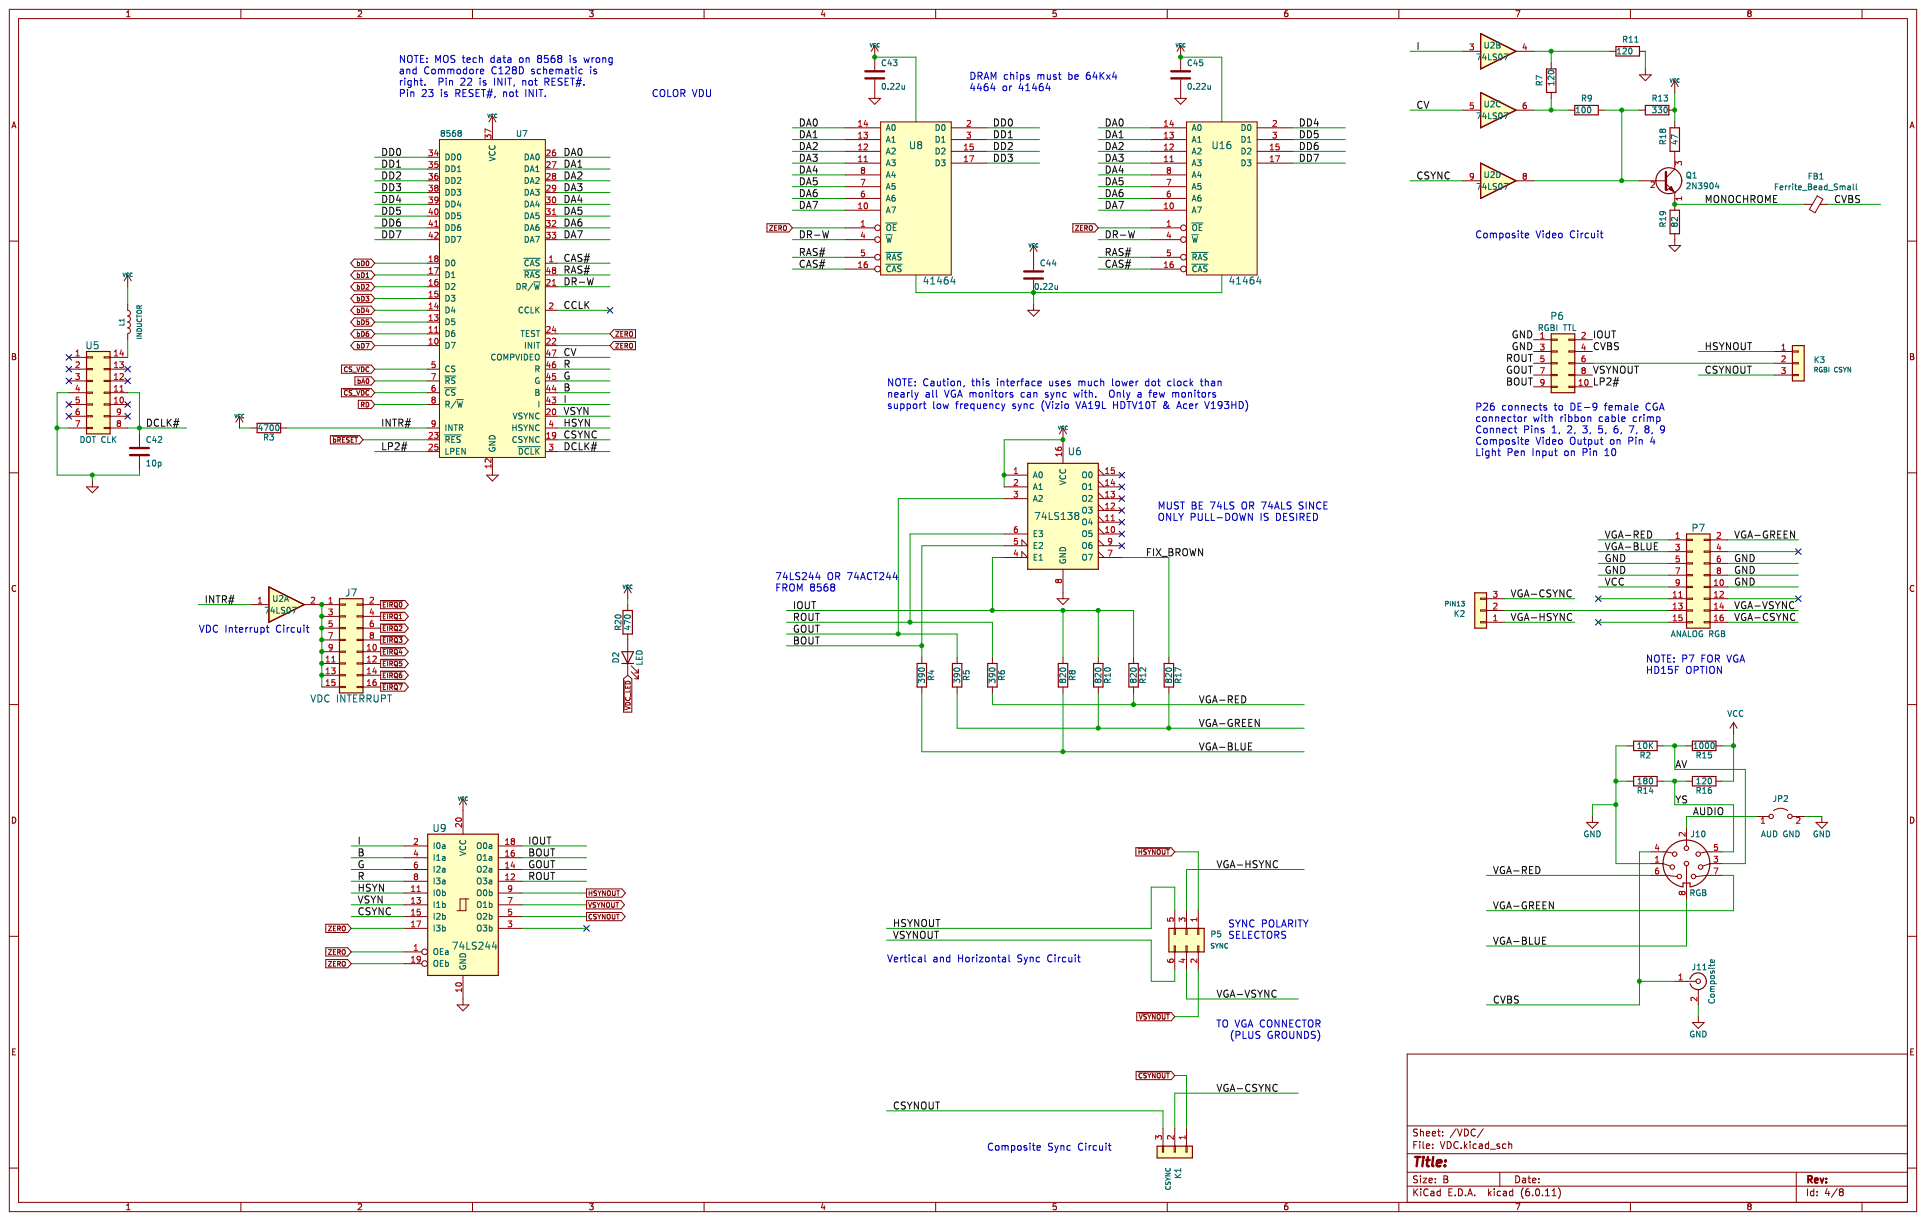
[picture p308: page 4]

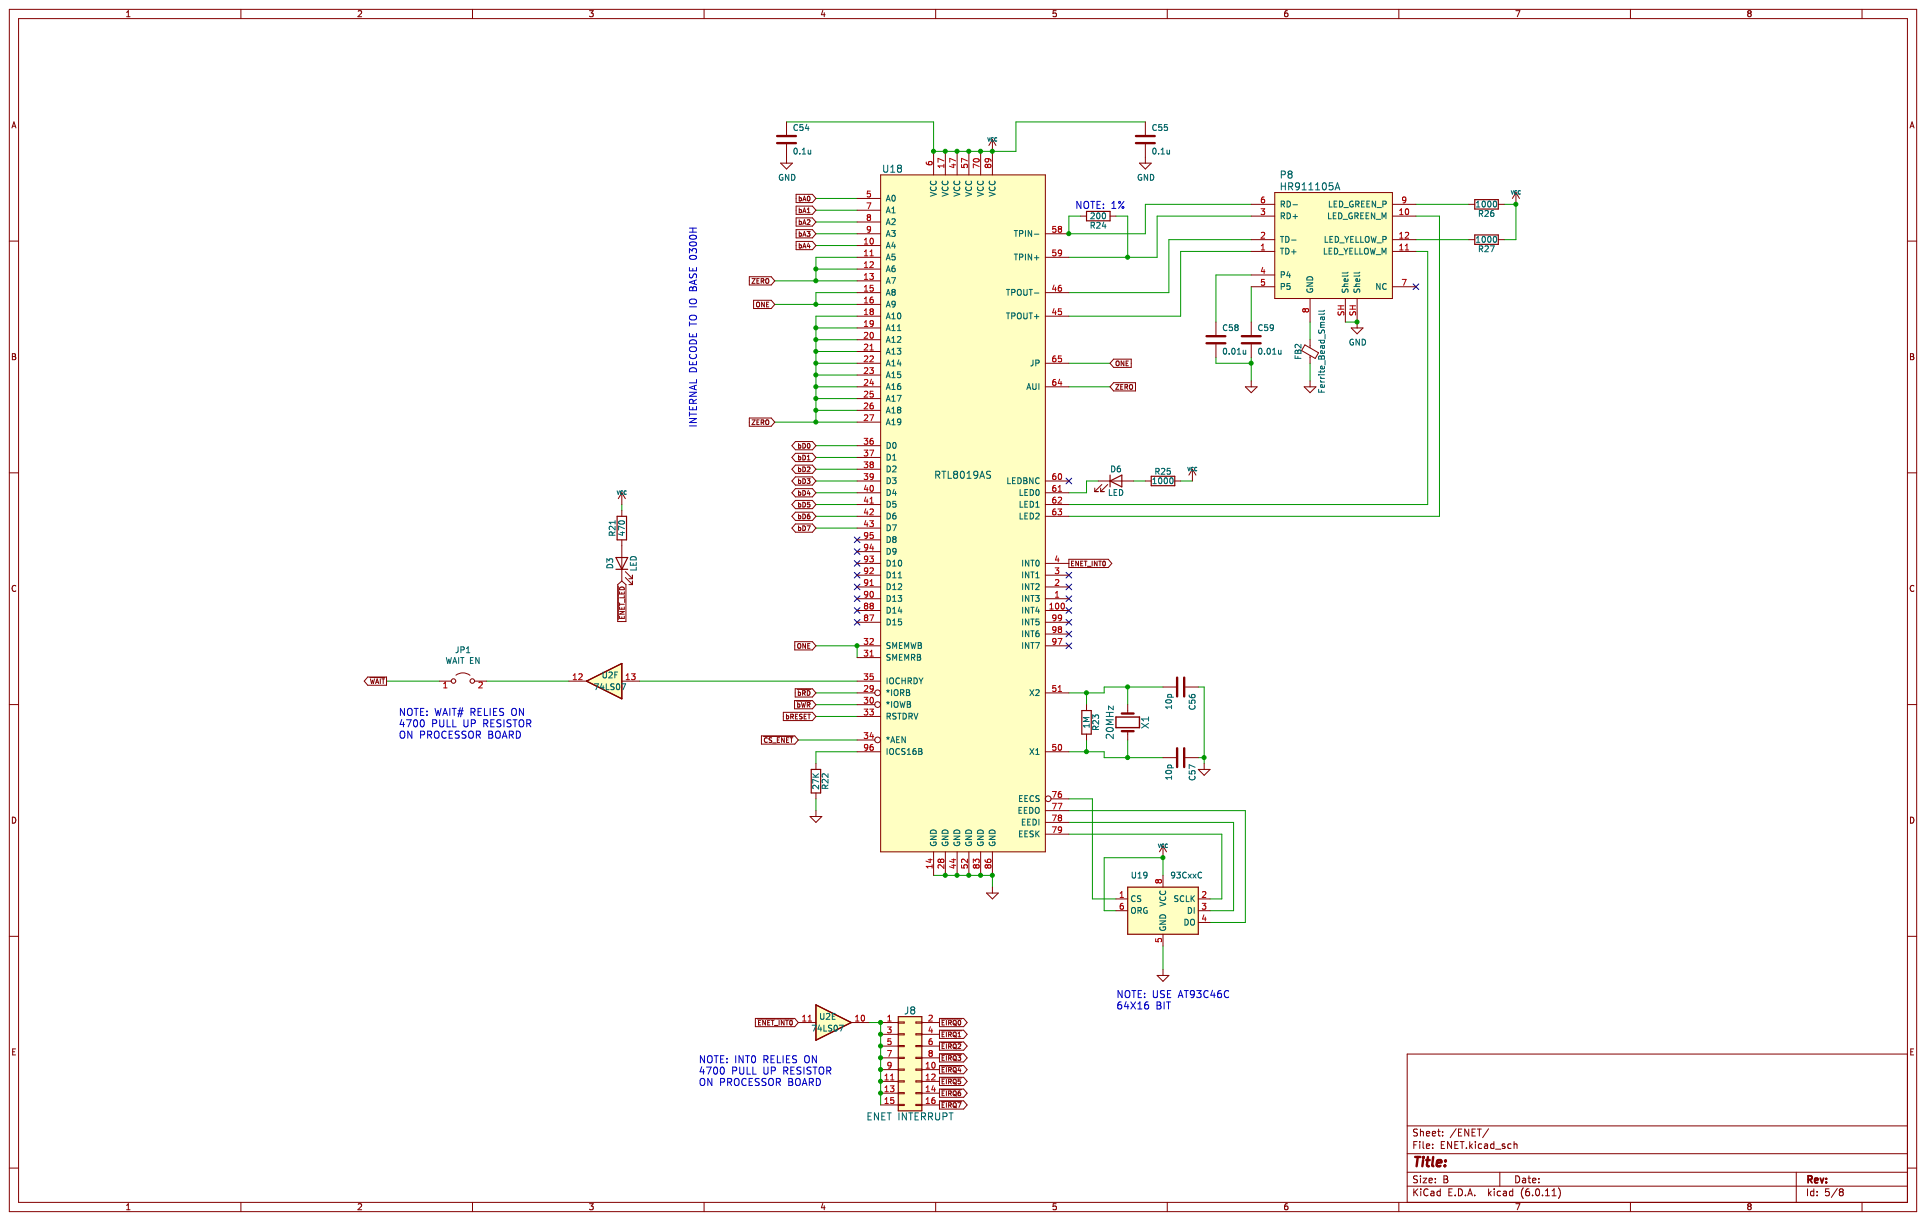
[picture p309: page 5]

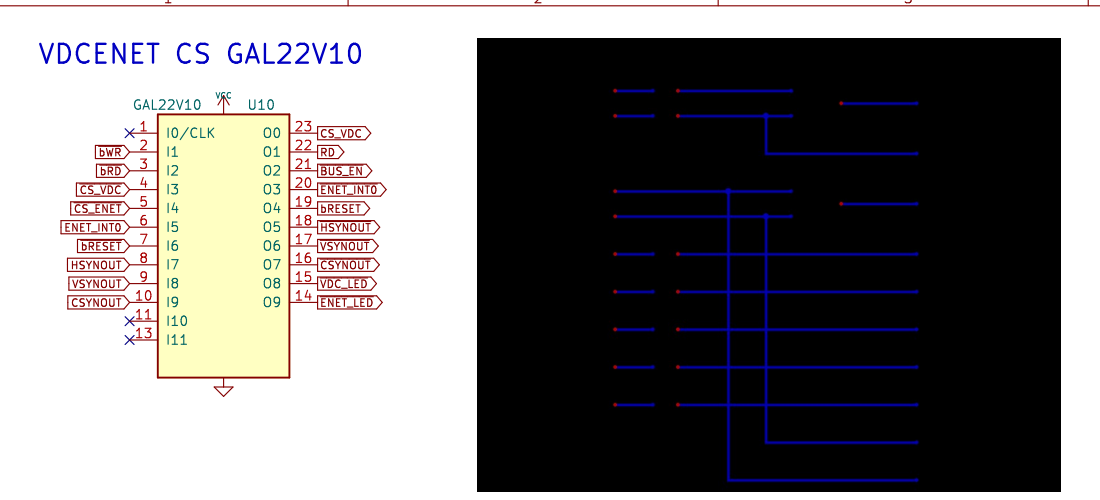
[picture p310: page 6]

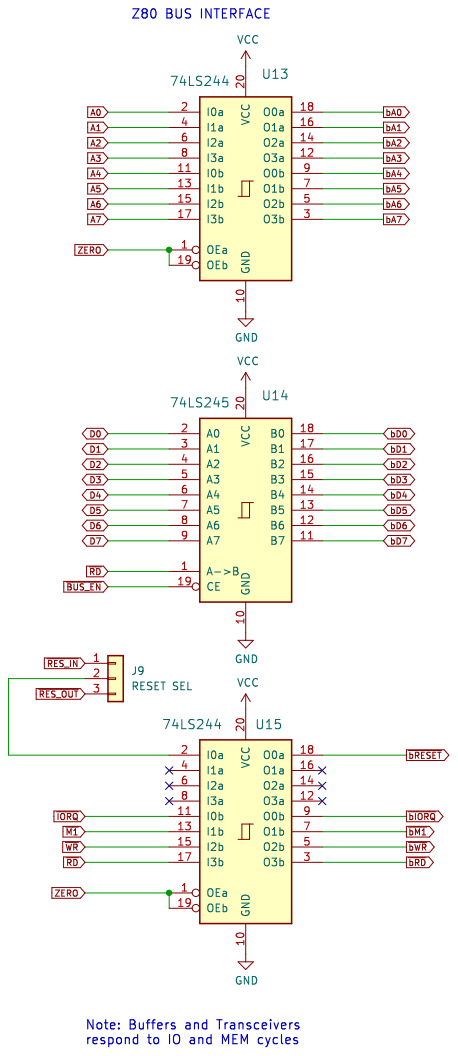
[picture p311: page 7]

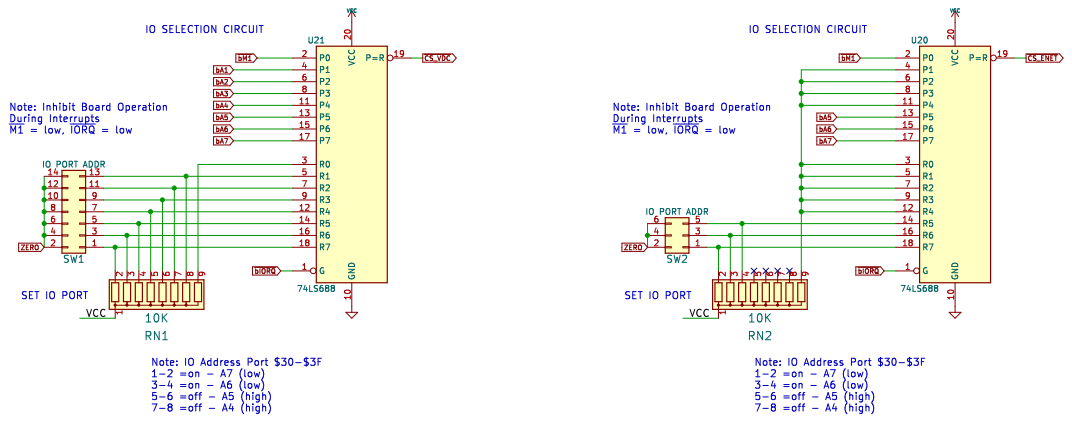
[picture p312: page 8]
