lynchaj/duodyne/!Development/14 input-output.Text, V1.0/input-output.Text.kicad_pcb

## KiCad design !Development/14 input-output.Text, V1.0/input-output.Text.kicad_pcb (2024-01-17)

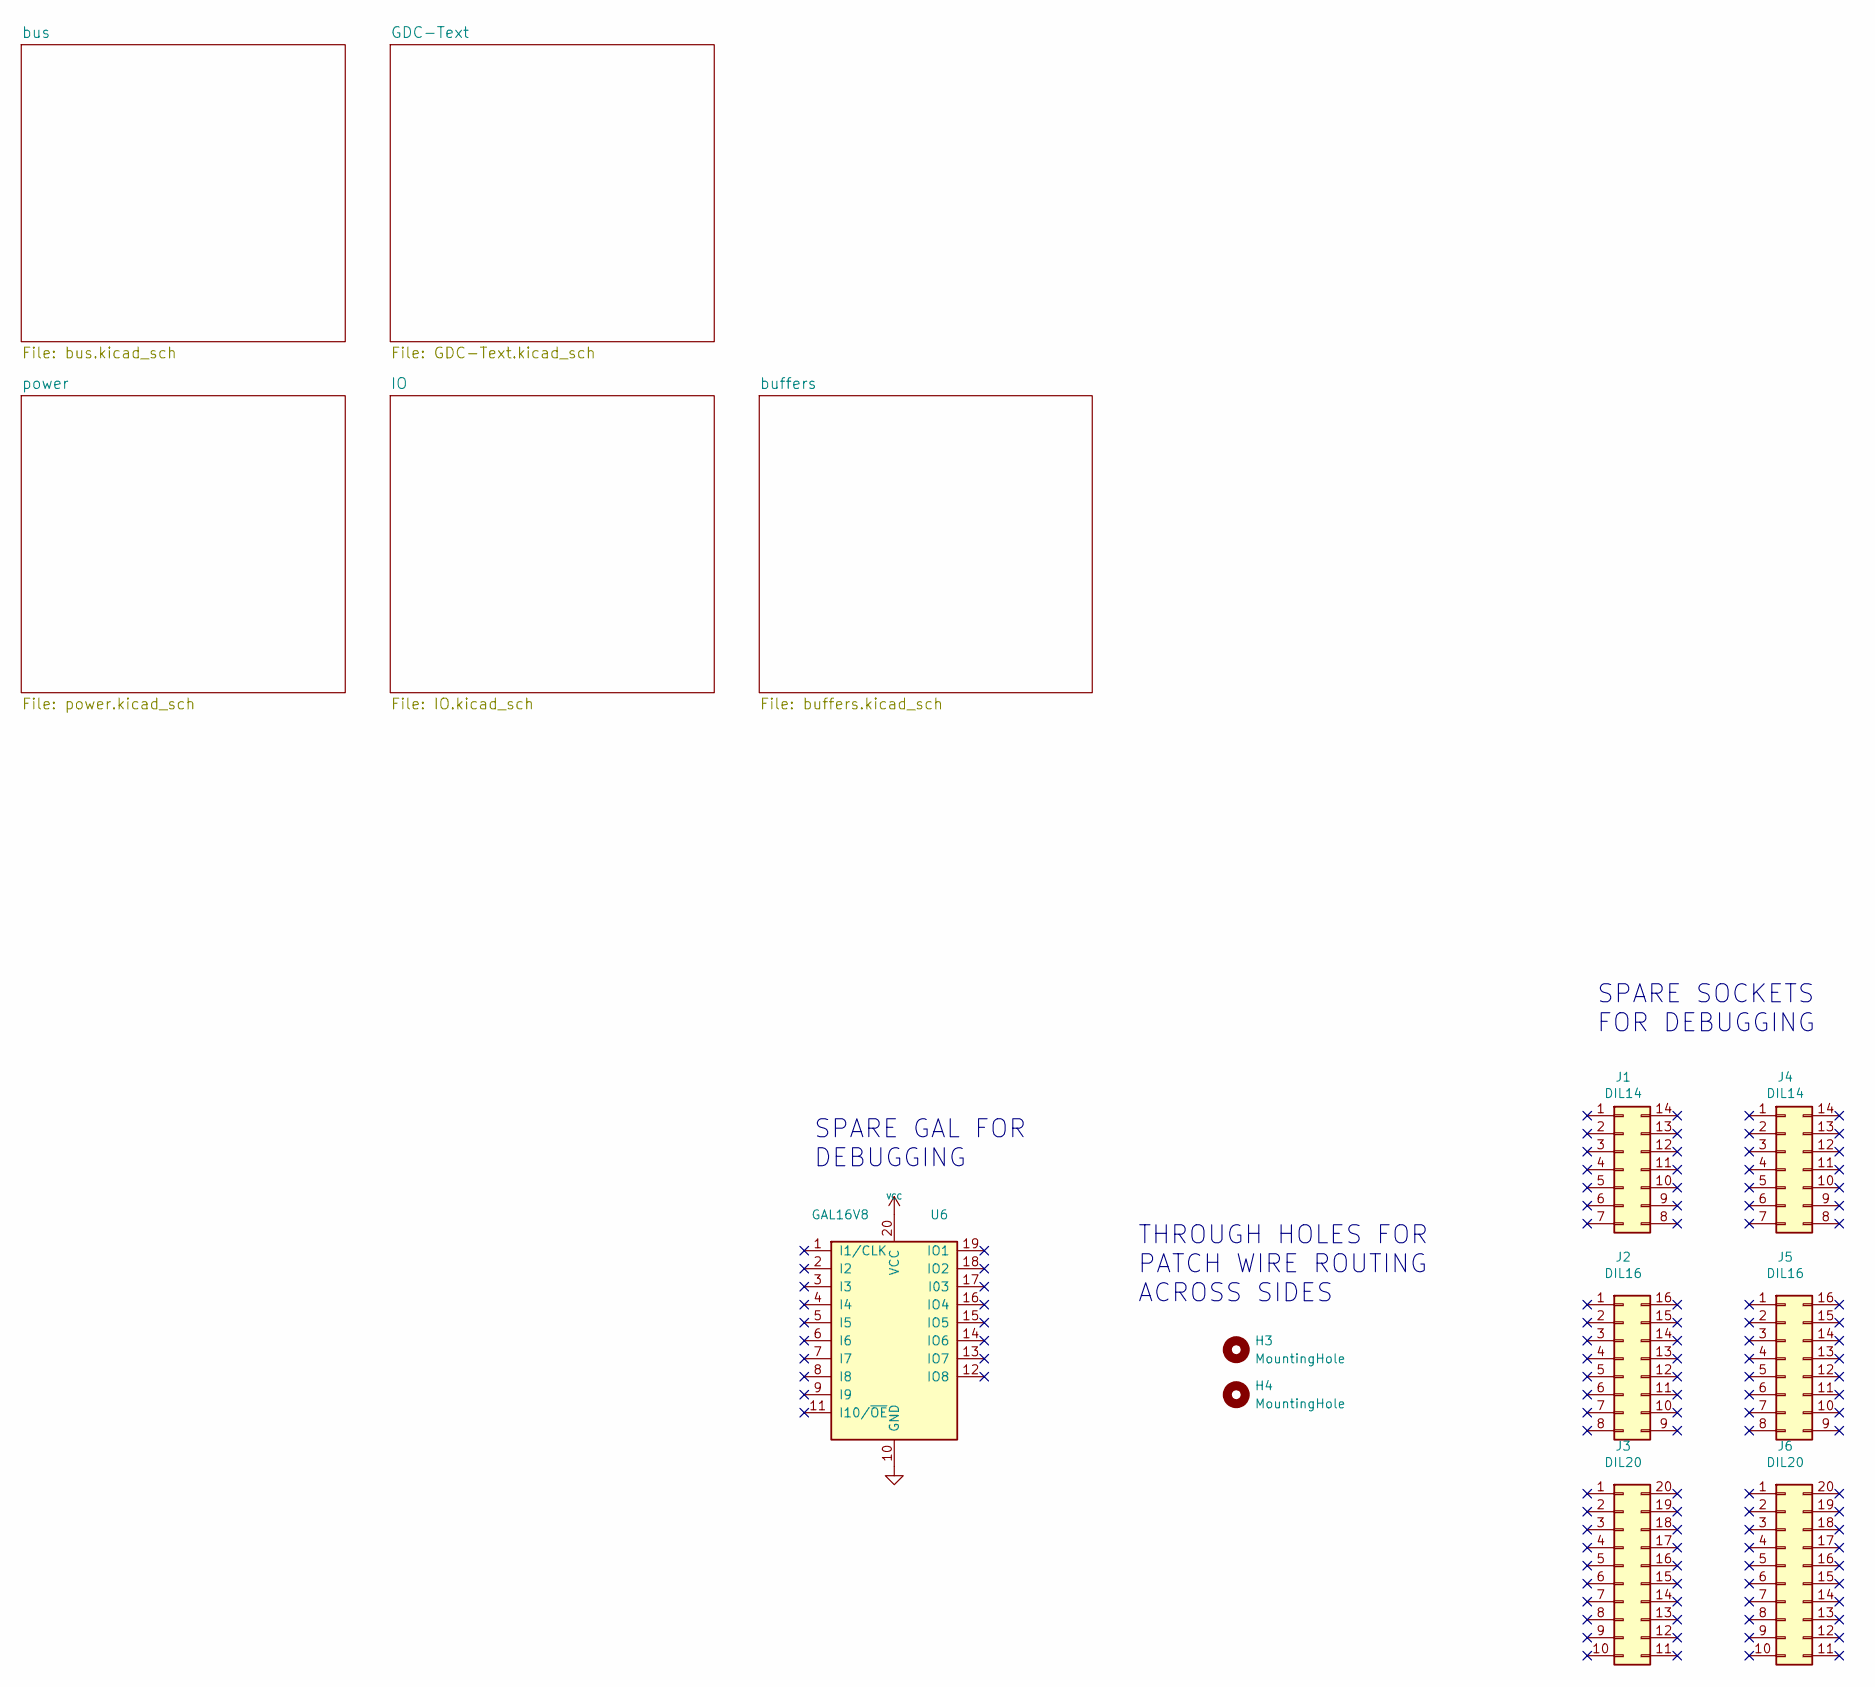
[picture p400: schematic input-output.Text.kicad_sch]

Parts:
H3, H4: MountingHole; MountingHole_2.2mm_M2_DIN965_Pad
J1, J4: DIL14; DIP-14_W7.62mm_Socket
J2, J5: DIL16; DIP-16_W7.62mm_Socket
J3, J6: DIL20; DIP-20_W7.62mm_Socket
U6: GAL16V8; DIP-20_W7.62mm_Socket

Connections:
VCC: U6.20 (VCC); also elsewhere on the board

Notes on the sheet:
SPARE SOCKETS FOR DEBUGGING
SPARE GAL FOR DEBUGGING
THROUGH HOLES FOR PATCH WIRE ROUTING ACROSS SIDES

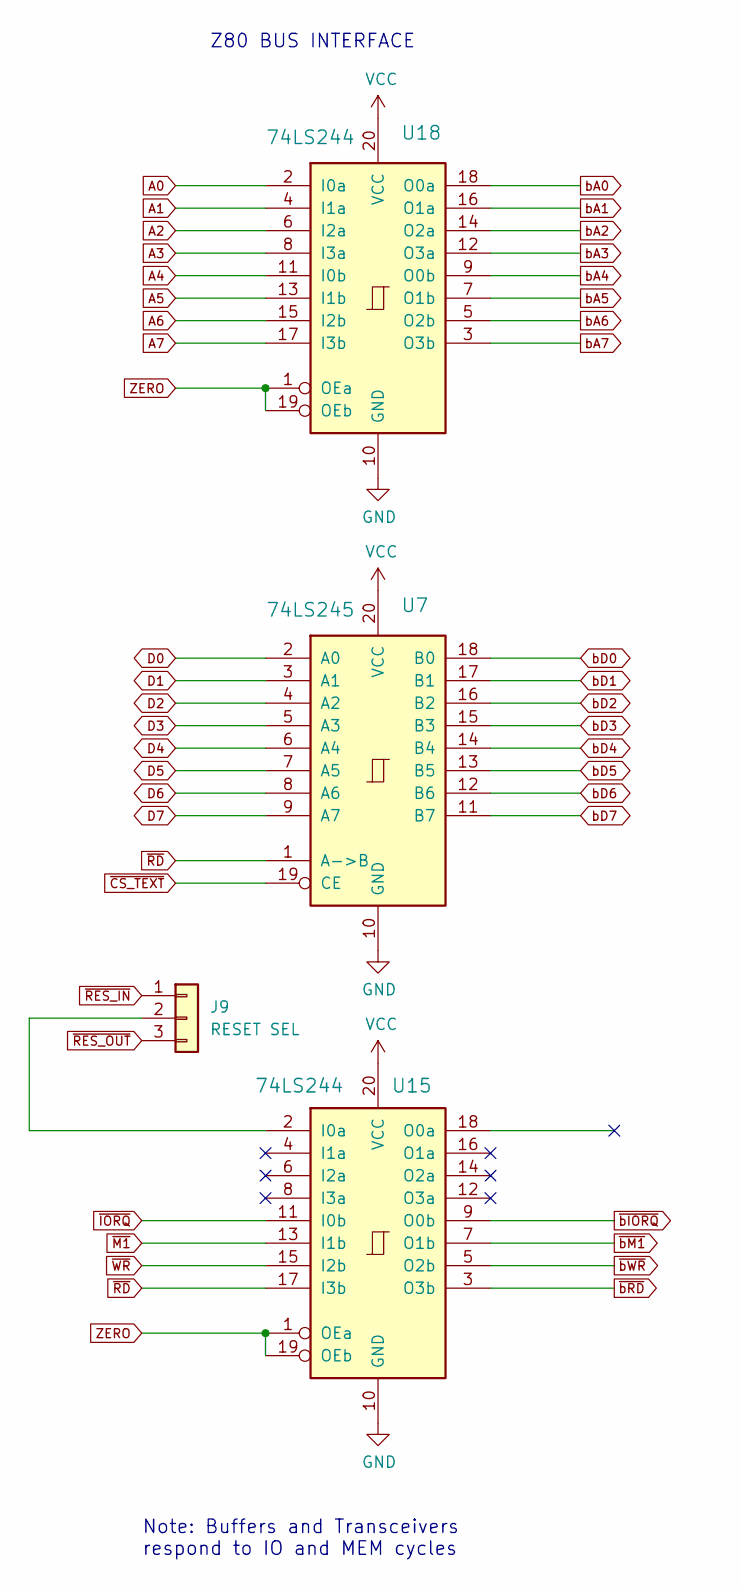
[picture p401: schematic buffers.kicad_sch]

Parts:
J9: RESET SEL; PinHeader_1x03_P2.54mm_Vertical
U7: 74LS245; DIP-20_W7.62mm_Socket
U15, U18: 74LS244; DIP-20_W7.62mm_Socket

Connections:
A0: U18.2 (I0a); also elsewhere on the board
A1: U18.4 (I1a); also elsewhere on the board
A2: U18.6 (I2a); also elsewhere on the board
A3: U18.8 (I3a); also elsewhere on the board
A4: U18.11 (I0b); also elsewhere on the board
A5: U18.13 (I1b); also elsewhere on the board
A6: U18.15 (I2b); also elsewhere on the board
A7: U18.17 (I3b); also elsewhere on the board
D0: U7.2 (A0); also elsewhere on the board
D1: U7.3 (A1); also elsewhere on the board
D2: U7.4 (A2); also elsewhere on the board
D3: U7.5 (A3); also elsewhere on the board
D4: U7.6 (A4); also elsewhere on the board
D5: U7.7 (A5); also elsewhere on the board
D6: U7.8 (A6); also elsewhere on the board
D7: U7.9 (A7); also elsewhere on the board
unnamed: J9.2, U15.2 (I0a)
VCC: U7.20 (VCC), U15.20 (VCC), U18.20 (VCC); also elsewhere on the board
ZERO: U15.1 (OEa), U15.19 (OEb), U18.1 (OEa), U18.19 (OEb); also elsewhere on the board
bA0: U18.18 (O0a); also elsewhere on the board
bA1: U18.16 (O1a); also elsewhere on the board
bA2: U18.14 (O2a); also elsewhere on the board
bA3: U18.12 (O3a); also elsewhere on the board
bA4: U18.9 (O0b); also elsewhere on the board
bA5: U18.7 (O1b); also elsewhere on the board
bA6: U18.5 (O2b); also elsewhere on the board
bA7: U18.3 (O3b); also elsewhere on the board
bD0: U7.18 (B0); also elsewhere on the board
bD1: U7.17 (B1); also elsewhere on the board
bD2: U7.16 (B2); also elsewhere on the board
bD3: U7.15 (B3); also elsewhere on the board
bD4: U7.14 (B4); also elsewhere on the board
bD5: U7.13 (B5); also elsewhere on the board
bD6: U7.12 (B6); also elsewhere on the board
bD7: U7.11 (B7); also elsewhere on the board
~CS_TEXT: U7.19 (CE); also elsewhere on the board
~IORQ: U15.11 (I0b); also elsewhere on the board
~M1: U15.13 (I1b); also elsewhere on the board
~RD: U7.1 (A->B), U15.17 (I3b); also elsewhere on the board
~RES_IN: J9.1; also elsewhere on the board
~RES_OUT: J9.3; also elsewhere on the board
~WR: U15.15 (I2b); also elsewhere on the board
~bIORQ: U15.9 (O0b); also elsewhere on the board
~bM1: U15.7 (O1b); also elsewhere on the board
~bRD: U15.3 (O3b); also elsewhere on the board
~bWR: U15.5 (O2b); also elsewhere on the board

Notes on the sheet:
Z80 BUS INTERFACE
Note: Buffers and Transceivers respond to IO and MEM cycles

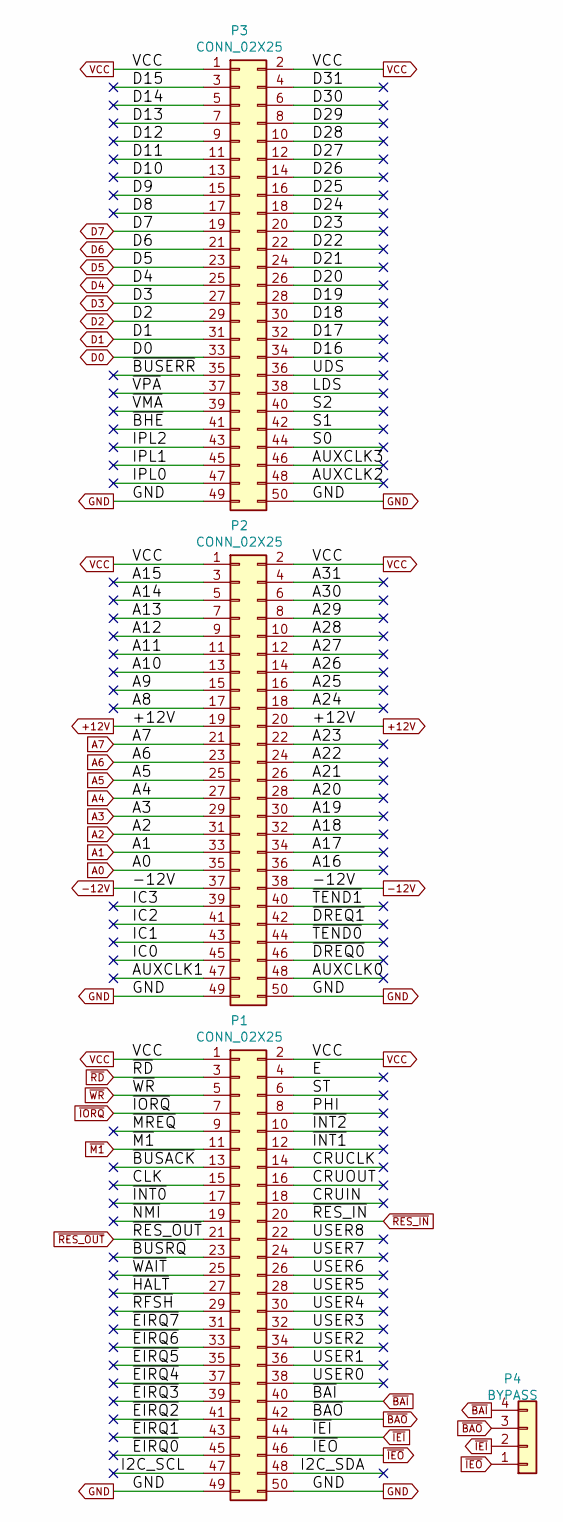
[picture p402: schematic bus.kicad_sch]

Parts:
P1, P2, P3: CONN_02X25; IDC-Header_2x25_P2.54mm_Horizontal
P4: BYPASS; PinHeader_1x04_P2.54mm_Vertical

Connections:
+12V: P2.19, P2.20
-12V: P2.37, P2.38
/bus/A8: P2.17
/bus/A9: P2.15
/bus/A10: P2.13
/bus/A11: P2.11
/bus/A12: P2.9
/bus/A13: P2.7
/bus/A14: P2.5
/bus/A15: P2.3
/bus/A16: P2.36
/bus/A17: P2.34
/bus/A18: P2.32
/bus/A19: P2.30
/bus/A20: P2.28
/bus/A21: P2.26
/bus/A22: P2.24
/bus/A23: P2.22
/bus/A24: P2.18
/bus/A25: P2.16
/bus/A26: P2.14
/bus/A27: P2.12
/bus/A28: P2.10
/bus/A29: P2.8
/bus/A30: P2.6
/bus/A31: P2.4
/bus/AUXCLK0: P2.48
/bus/AUXCLK1: P2.47
/bus/AUXCLK2: P3.48
/bus/AUXCLK3: P3.46
/bus/CLK: P1.15
/bus/CRUCLK: P1.14
/bus/CRUIN: P1.18
/bus/CRUOUT: P1.16
/bus/D8: P3.17
/bus/D9: P3.15
/bus/D10: P3.13
/bus/D11: P3.11
/bus/D12: P3.9
/bus/D13: P3.7
/bus/D14: P3.5
/bus/D15: P3.3
/bus/D16: P3.34
/bus/D17: P3.32
/bus/D18: P3.30
/bus/D19: P3.28
/bus/D20: P3.26
/bus/D21: P3.24
/bus/D22: P3.22
/bus/D23: P3.20
/bus/D24: P3.18
/bus/D25: P3.16
/bus/D26: P3.14
/bus/D27: P3.12
/bus/D28: P3.10
/bus/D29: P3.8
/bus/D30: P3.6
/bus/D31: P3.4
/bus/E: P1.4
/bus/I2C_SCL: P1.47
/bus/I2C_SDA: P1.48
/bus/IC0: P2.45
/bus/IC1: P2.43
/bus/IC2: P2.41
/bus/IC3: P2.39
/bus/IPL0: P3.47
/bus/IPL1: P3.45
/bus/IPL2: P3.43
/bus/LDS: P3.38
/bus/PHI: P1.8
/bus/S0: P3.44
/bus/S1: P3.42
/bus/S2: P3.40
/bus/ST: P1.6
/bus/UDS: P3.36
/bus/USER0: P1.38
/bus/USER1: P1.36
/bus/USER2: P1.34
/bus/USER3: P1.32
/bus/USER4: P1.30
/bus/USER5: P1.28
/bus/USER6: P1.26
/bus/USER7: P1.24
/bus/USER8: P1.22
/bus/~BHE: P3.41
/bus/~BUSACK: P1.13
/bus/~BUSERR: P3.35
/bus/~BUSRQ: P1.23
/bus/~DREQ0: P2.46
/bus/~DREQ1: P2.42
/bus/~EIRQ0: P1.45
/bus/~EIRQ1: P1.43
/bus/~EIRQ2: P1.41
/bus/~EIRQ3: P1.39
/bus/~EIRQ4: P1.37
/bus/~EIRQ5: P1.35
/bus/~EIRQ6: P1.33
/bus/~EIRQ7: P1.31
/bus/~HALT: P1.27
/bus/~INT0: P1.17
/bus/~INT1: P1.12
/bus/~INT2: P1.10
/bus/~MREQ: P1.9
/bus/~NMI: P1.19
/bus/~RFSH: P1.29
/bus/~TEND0: P2.44
/bus/~TEND1: P2.40
/bus/~VMA: P3.39
/bus/~VPA: P3.37
/bus/~WAIT: P1.25
A0: P2.35; also elsewhere on the board
A1: P2.33; also elsewhere on the board
A2: P2.31; also elsewhere on the board
A3: P2.29; also elsewhere on the board
A4: P2.27; also elsewhere on the board
A5: P2.25; also elsewhere on the board
A6: P2.23; also elsewhere on the board
A7: P2.21; also elsewhere on the board
D0: P3.33; also elsewhere on the board
D1: P3.31; also elsewhere on the board
D2: P3.29; also elsewhere on the board
D3: P3.27; also elsewhere on the board
D4: P3.25; also elsewhere on the board
D5: P3.23; also elsewhere on the board
D6: P3.21; also elsewhere on the board
D7: P3.19; also elsewhere on the board
VCC: P1.1, P1.2, P2.1, P2.2, P3.1, P3.2; also elsewhere on the board
~BAI: P1.40, P4.4
~BAO: P1.42, P4.3
~IEI: P1.44, P4.2
~IEO: P1.46, P4.1
~IORQ: P1.7; also elsewhere on the board
~M1: P1.11; also elsewhere on the board
~RD: P1.3; also elsewhere on the board
~RES_IN: P1.20; also elsewhere on the board
~RES_OUT: P1.21; also elsewhere on the board
~WR: P1.5; also elsewhere on the board

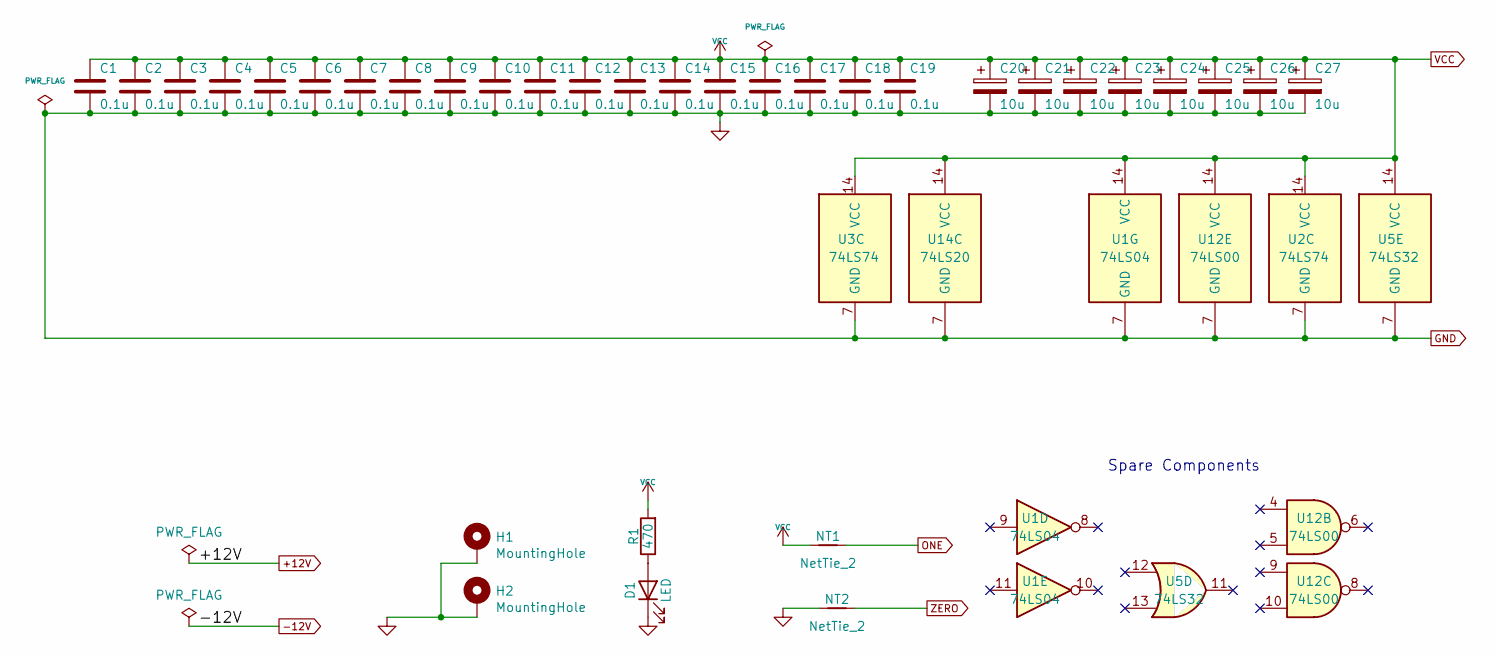
[picture p403: schematic power.kicad_sch]

Parts:
C1, C2, C3, C4, C5, C6, C7, C8, C9, C10, C11, C12, C13, C14, C15, C16, C17, C18, C19: 0.1u; C_Disc_D5.0mm_W2.5mm_P5.00mm
C20, C21, C22, C23, C24, C25, C26, C27: 10u; CP_Radial_D5.0mm_P2.50mm
D1: LED; LED_D3.0mm_Horizontal_O3.81mm_Z2.0mm
H1, H2: MountingHole; MountingHole_3.2mm_M3_Pad
NT1, NT2: NetTie_2; NetTie-2_THT_Pad0.3mm
R1: 470; R_Axial_DIN0207_L6.3mm_D2.5mm_P7.62mm_Horizontal
U1: 74LS04; DIP-14_W7.62mm_Socket
U2, U3: 74LS74; DIP-14_W7.62mm_Socket
U5: 74LS32; DIP-14_W7.62mm_Socket
U12: 74LS00; DIP-14_W7.62mm_Socket
U14: 74LS20; DIP-14_W7.62mm_Socket

Connections:
unnamed: D1.2 (A), R1.1
ONE: NT1.2; also elsewhere on the board
VCC: C1.1, C2.1, C3.1, C4.1, C5.1, C6.1, C7.1, C8.1, C9.1, C10.1, C11.1, C12.1, C13.1, C14.1, C15.1, C16.1, C17.1, C18.1, C19.1, C20.1, C21.1, C22.1, C23.1, C24.1, C25.1, C26.1, C27.1, NT1.1, R1.2, U1.14 (VCC), U2.14 (VCC), U3.14 (VCC), U5.14 (VCC), U12.14 (VCC), U14.14 (VCC); also elsewhere on the board
ZERO: NT2.2; also elsewhere on the board

Notes on the sheet:
Spare Components

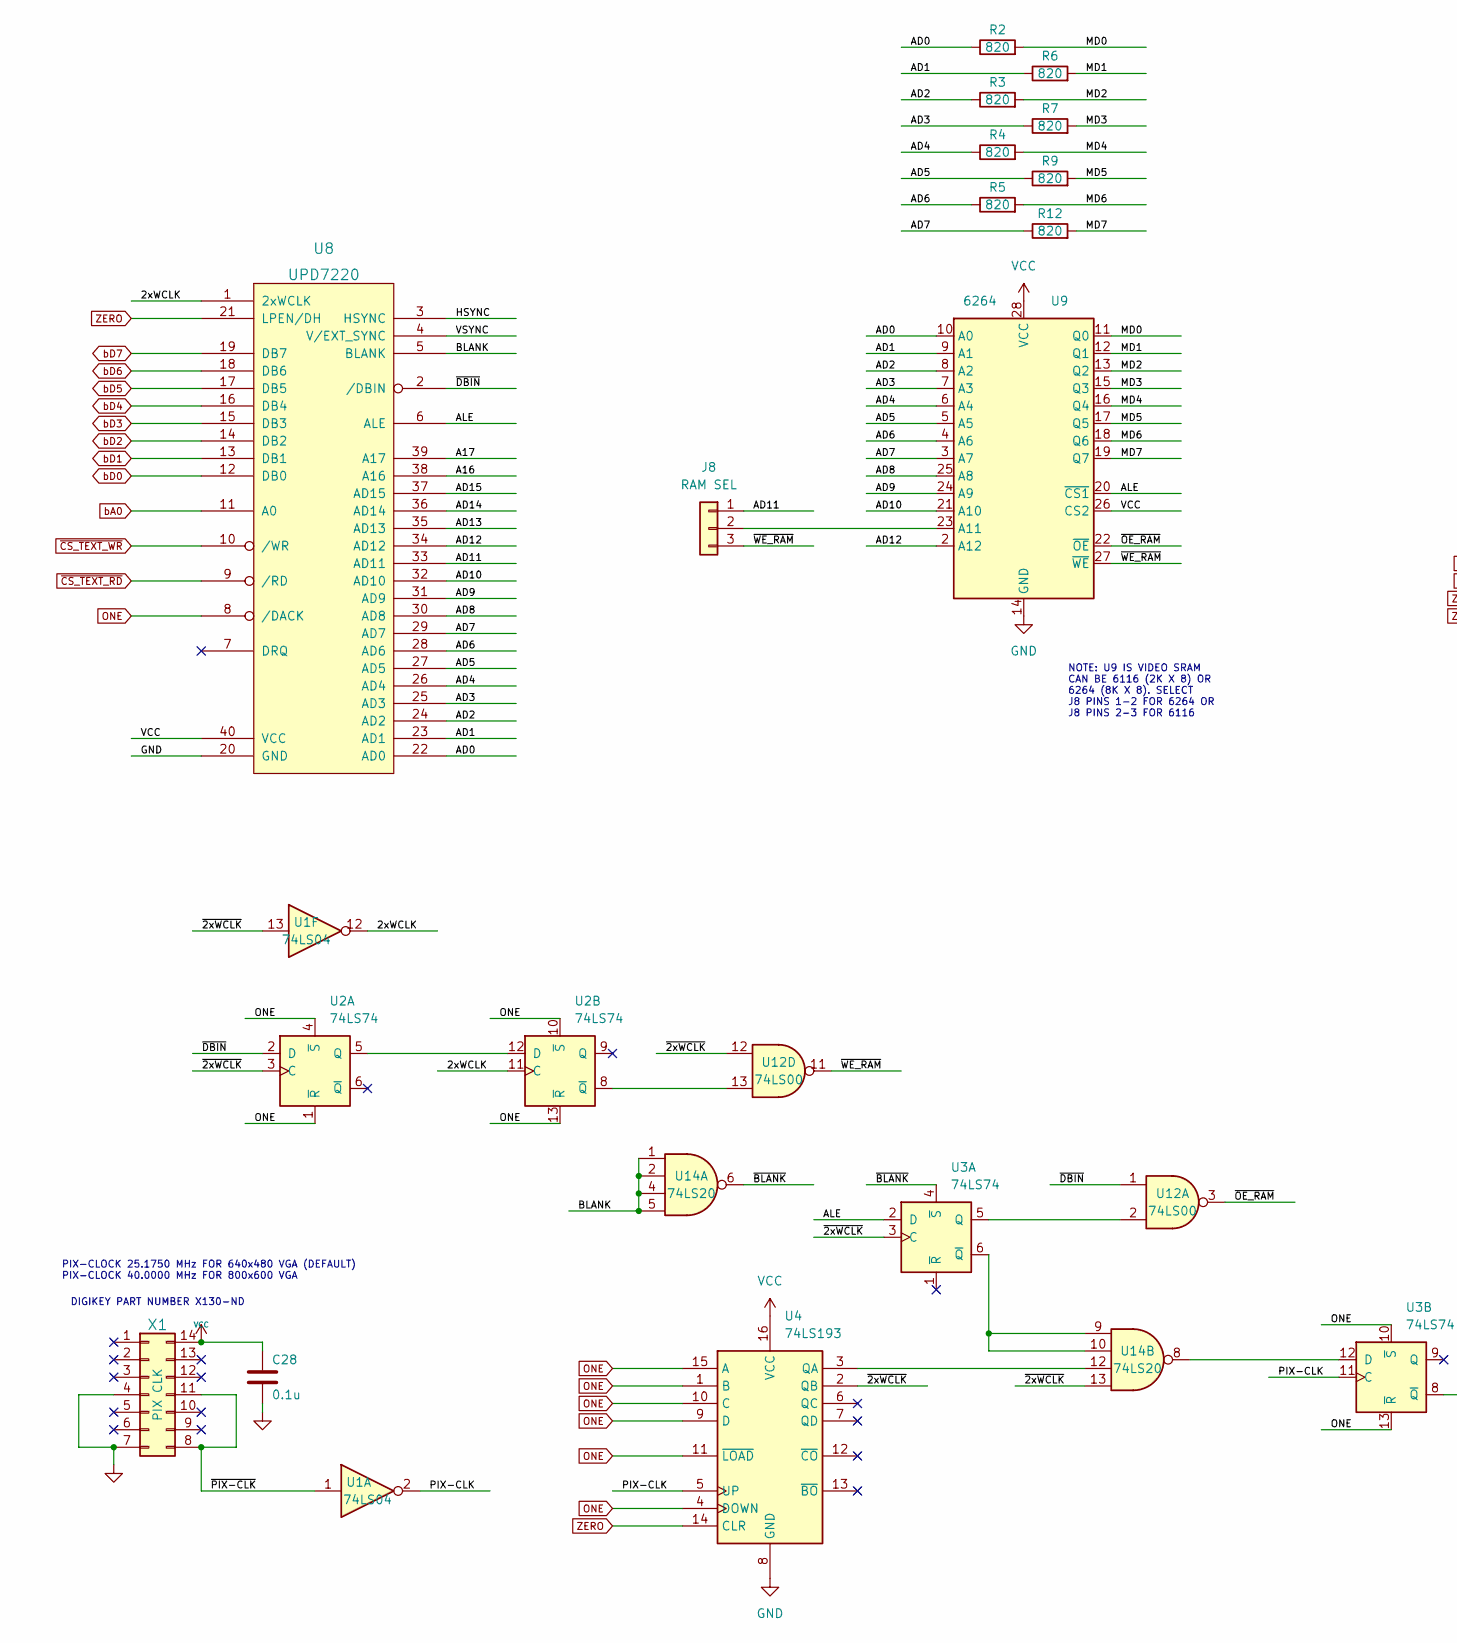
[picture p404: schematic GDC-Text.kicad_sch, part in row 1, column 1]

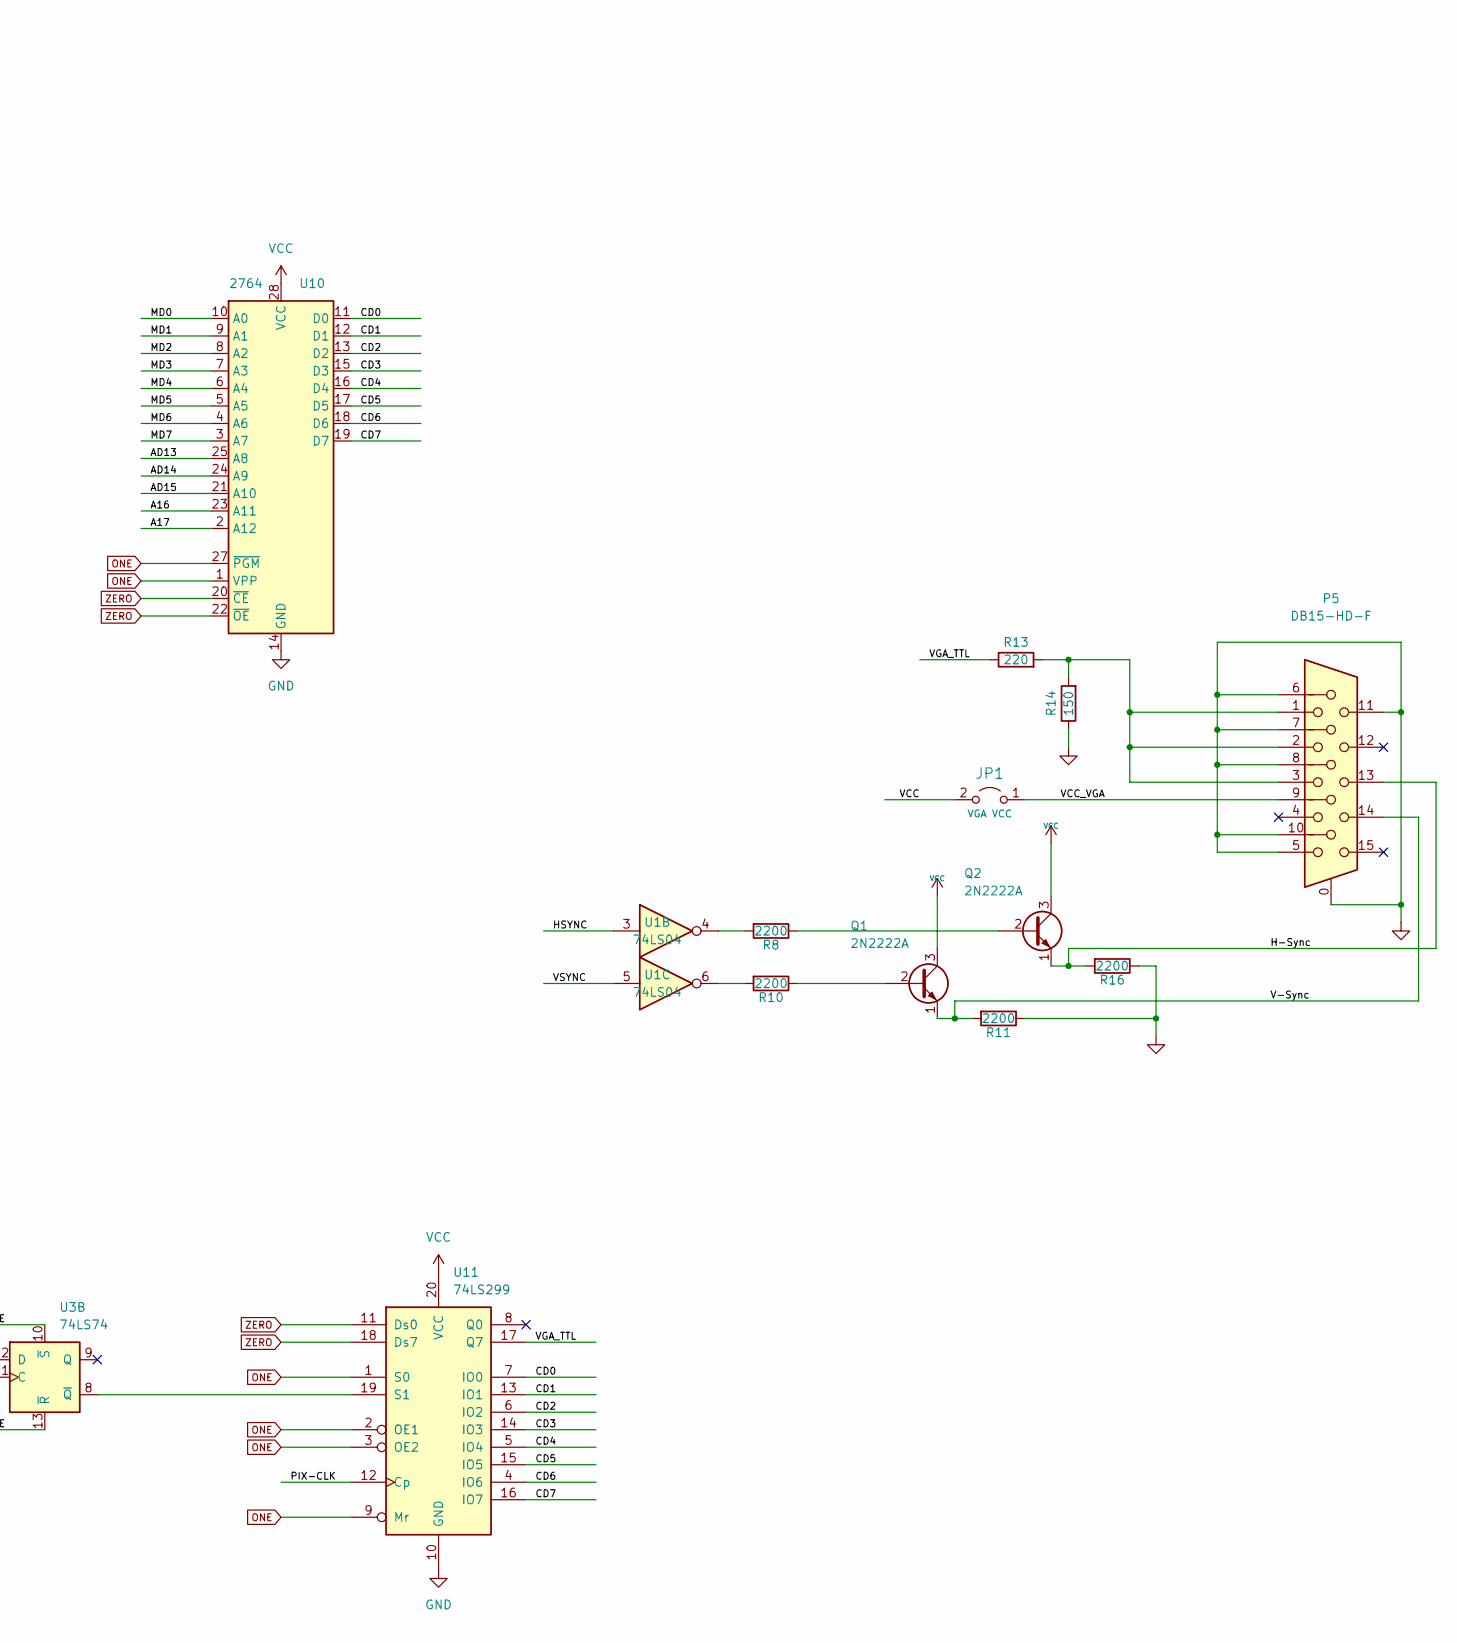
[picture p405: schematic GDC-Text.kicad_sch, part in row 1, column 2]

Parts:
C28: 0.1u; C_Disc_D5.0mm_W2.5mm_P5.00mm
J8: RAM SEL; PinHeader_1x03_P2.54mm_Vertical
JP1: VGA VCC; PinHeader_1x02_P2.54mm_Vertical
P5: DB15-HD-F; DSUB-15-HD_Female_Horizontal_P2.29x1.98mm_EdgePinOffset3.03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
Q1, Q2: 2N2222A; TO-92L_HandSolder
R2, R3, R4, R5, R6, R7, R9, R12: 820; R_Axial_DIN0207_L6.3mm_D2.5mm_P7.62mm_Horizontal
R8, R10, R11, R16: 2200; R_Axial_DIN0207_L6.3mm_D2.5mm_P7.62mm_Horizontal
R13: 220; R_Axial_DIN0207_L6.3mm_D2.5mm_P7.62mm_Horizontal
R14: 150; R_Axial_DIN0207_L6.3mm_D2.5mm_P7.62mm_Horizontal
U1: 74LS04; DIP-14_W7.62mm_Socket
U2, U3: 74LS74; DIP-14_W7.62mm_Socket
U4: 74LS193; DIP-16_W7.62mm_Socket
U8: UPD7220; DIP-40_W15.24mm_Socket
U9: 6264; DIP-28_W15.24mm_Socket
U10: 2764; DIP-28_W15.24mm_Socket
U11: 74LS299; DIP-20_W7.62mm_Socket
U12: 74LS00; DIP-14_W7.62mm_Socket
U14: 74LS20; DIP-14_W7.62mm_Socket
X1: PIX CLK; DIP-14_W7.62mm_Socket

Connections:
/GDC-Text/2xWCLK: U1.12, U2.11 (C), U8.1 (2xWCLK)
/GDC-Text/A16: U8.38 (A16), U10.23 (A11)
/GDC-Text/A17: U8.39 (A17), U10.2 (A12)
/GDC-Text/AD0: R2.1, U8.22 (AD0), U9.10 (A0)
/GDC-Text/AD1: R6.1, U8.23 (AD1), U9.9 (A1)
/GDC-Text/AD2: R3.1, U8.24 (AD2), U9.8 (A2)
/GDC-Text/AD3: R7.1, U8.25 (AD3), U9.7 (A3)
/GDC-Text/AD4: R4.1, U8.26 (AD4), U9.6 (A4)
/GDC-Text/AD5: R9.1, U8.27 (AD5), U9.5 (A5)
/GDC-Text/AD6: R5.1, U8.28 (AD6), U9.4 (A6)
/GDC-Text/AD7: R12.1, U8.29 (AD7), U9.3 (A7)
/GDC-Text/AD8: U8.30 (AD8), U9.25 (A8)
/GDC-Text/AD9: U8.31 (AD9), U9.24 (A9)
/GDC-Text/AD10: U8.32 (AD10), U9.21 (A10)
/GDC-Text/AD11: J8.1, U8.33 (AD11)
/GDC-Text/AD12: U8.34 (AD12), U9.2 (A12)
/GDC-Text/AD13: U8.35 (AD13), U10.25 (A8)
/GDC-Text/AD14: U8.36 (AD14), U10.24 (A9)
/GDC-Text/AD15: U8.37 (AD15), U10.21 (A10)
/GDC-Text/ALE: U3.2 (D), U8.6 (ALE), U9.20 (~CS1)
/GDC-Text/BLANK: U8.5 (BLANK), U14.1, U14.2, U14.4, U14.5
/GDC-Text/CD0: U10.11 (D0), U11.7 (IO0)
/GDC-Text/CD1: U10.12 (D1), U11.13 (IO1)
/GDC-Text/CD2: U10.13 (D2), U11.6 (IO2)
/GDC-Text/CD3: U10.15 (D3), U11.14 (IO3)
/GDC-Text/CD4: U10.16 (D4), U11.5 (IO4)
/GDC-Text/CD5: U10.17 (D5), U11.15 (IO5)
/GDC-Text/CD6: U10.18 (D6), U11.4 (IO6)
/GDC-Text/CD7: U10.19 (D7), U11.16 (IO7)
/GDC-Text/H-Sync: P5.13, Q2.1 (E), R16.2
/GDC-Text/HSYNC: U1.3, U8.3 (HSYNC)
/GDC-Text/MD0: R2.2, U9.11 (Q0), U10.10 (A0)
/GDC-Text/MD1: R6.2, U9.12 (Q1), U10.9 (A1)
/GDC-Text/MD2: R3.2, U9.13 (Q2), U10.8 (A2)
/GDC-Text/MD3: R7.2, U9.15 (Q3), U10.7 (A3)
/GDC-Text/MD4: R4.2, U9.16 (Q4), U10.6 (A4)
/GDC-Text/MD5: R9.2, U9.17 (Q5), U10.5 (A5)
/GDC-Text/MD6: R5.2, U9.18 (Q6), U10.4 (A6)
/GDC-Text/MD7: R12.2, U9.19 (Q7), U10.3 (A7)
/GDC-Text/PIX-CLK: U1.2, U3.11 (C), U4.5 (UP), U11.12 (Cp)
/GDC-Text/V-Sync: P5.14, Q1.1 (E), R11.2
/GDC-Text/VCC_VGA: JP1.1 (A), P5.9
/GDC-Text/VGA_TTL: R13.1, U11.17 (Q7)
/GDC-Text/VSYNC: U1.5, U8.4 (V/EXT_SYNC)
/GDC-Text/~2xWCLK: U1.13, U2.3 (C), U3.3 (C), U4.2 (QB), U12.12, U14.13
/GDC-Text/~BLANK: U3.4 (~S), U14.6
/GDC-Text/~DBIN: U2.2 (D), U8.2 (/DBIN), U12.1
/GDC-Text/~OE_RAM: U9.22 (~OE), U12.3
/GDC-Text/~PIX-CLK: U1.1, X1.8, X1.11
/GDC-Text/~WE_RAM: J8.3, U9.27 (~WE), U12.11
unnamed: J8.2, U9.23 (A11)
unnamed: P5.1, P5.2, P5.3, R13.2, R14.2
unnamed: Q1.2 (B), R10.1
unnamed: Q2.2 (B), R8.1
unnamed: R8.2, U1.4
unnamed: R10.2, U1.6
unnamed: U2.5 (Q), U2.12 (D)
unnamed: U3.8 (~Q), U11.19 (S1)
unnamed: U3.5 (Q), U12.2
unnamed: U2.8 (~Q), U12.13
unnamed: U3.12 (D), U14.8
unnamed: U3.6 (~Q), U14.9, U14.10
unnamed: U4.3 (QA), U14.12
ONE: U2.1 (~R), U2.4 (~S), U2.10 (~S), U2.13 (~R), U3.10 (~S), U3.13 (~R), U4.1 (B), U4.4 (DOWN), U4.9 (D), U4.10 (C), U4.11 (~LOAD), U4.15 (A), U8.8 (/DACK), U10.1 (VPP), U10.27 (~PGM), U11.1 (S0), U11.2 (OE1), U11.3 (OE2), U11.9 (Mr); also elsewhere on the board
VCC: C28.1, JP1.2 (B), Q1.3 (C), Q2.3 (C), U4.16 (VCC), U8.40 (VCC), U9.26 (CS2), U9.28 (VCC), U10.28 (VCC), U11.20 (VCC), X1.14; also elsewhere on the board
ZERO: U4.14 (CLR), U8.21 (LPEN/DH), U10.20 (~CE), U10.22 (~OE), U11.11 (Ds0), U11.18 (Ds7); also elsewhere on the board
bA0: U8.11 (A0); also elsewhere on the board
bD0: U8.12 (DB0); also elsewhere on the board
bD1: U8.13 (DB1); also elsewhere on the board
bD2: U8.14 (DB2); also elsewhere on the board
bD3: U8.15 (DB3); also elsewhere on the board
bD4: U8.16 (DB4); also elsewhere on the board
bD5: U8.17 (DB5); also elsewhere on the board
bD6: U8.18 (DB6); also elsewhere on the board
bD7: U8.19 (DB7); also elsewhere on the board
~CS_TEXT_RD: U8.9 (/RD); also elsewhere on the board
~CS_TEXT_WR: U8.10 (/WR); also elsewhere on the board

Notes on the sheet:
DIGIKEY PART NUMBER X130-ND
PIX-CLOCK 25.1750 MHz FOR 640x480 VGA (DEFAULT) PIX-CLOCK 40.0000 MHz FOR 800x600 VGA
NOTE: U9 IS VIDEO SRAM CAN BE 6116 (2K X 8) OR 6264 (8K X 8). SELECT J8 PINS 1-2 FOR 6264 OR J8 PINS 2-3 FOR 6116

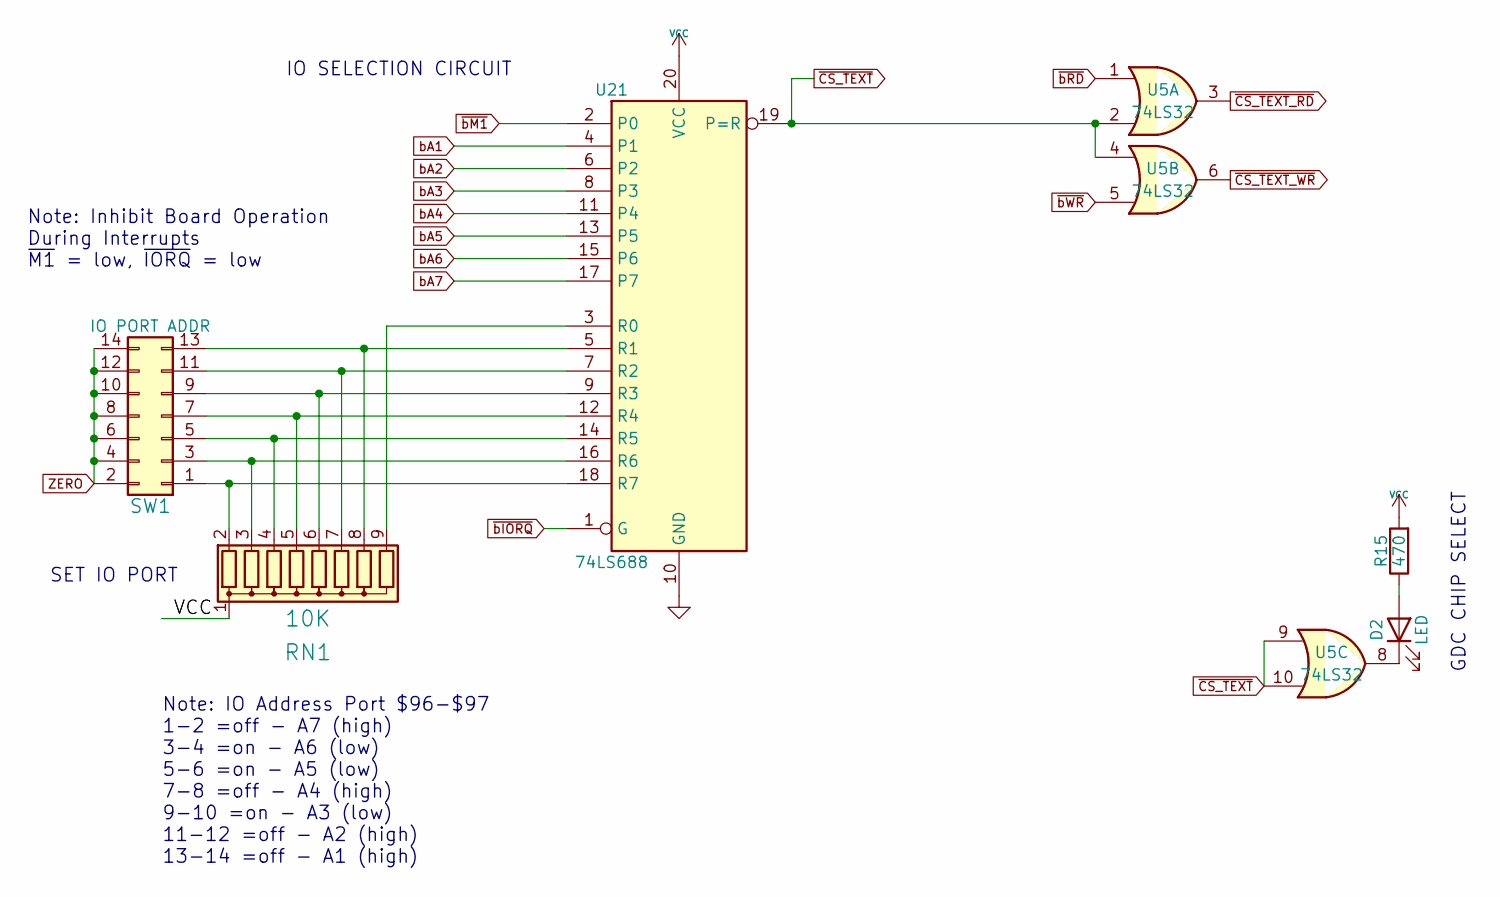
[picture p406: schematic IO.kicad_sch]

Parts:
D2: LED; LED_D3.0mm_Horizontal_O3.81mm_Z2.0mm
R15: 470; R_Axial_DIN0207_L6.3mm_D2.5mm_P7.62mm_Horizontal
RN1: 10K; R_Array_SIP9
SW1: IO PORT ADDR; PinHeader_2x07_P2.54mm_Vertical
U5: 74LS32; DIP-14_W7.62mm_Socket
U21: 74LS688; DIP-20_W7.62mm_Socket

Connections:
unnamed: D2.1 (K), U5.8
unnamed: D2.2 (A), R15.1
unnamed: RN1.2 (R1), SW1.1, U21.18 (R7)
unnamed: RN1.3 (R2), SW1.3, U21.16 (R6)
unnamed: RN1.4 (R3), SW1.5, U21.14 (R5)
unnamed: RN1.5 (R4), SW1.7, U21.12 (R4)
unnamed: RN1.6 (R5), SW1.9, U21.9 (R3)
unnamed: RN1.7 (R6), SW1.11, U21.7 (R2)
unnamed: RN1.8 (R7), SW1.13, U21.5 (R1)
unnamed: RN1.9 (R8), U21.3 (R0)
VCC: R15.2, RN1.1 (common), U21.20 (VCC); also elsewhere on the board
ZERO: SW1.2, SW1.4, SW1.6, SW1.8, SW1.10, SW1.12, SW1.14; also elsewhere on the board
bA1: U21.4 (P1); also elsewhere on the board
bA2: U21.6 (P2); also elsewhere on the board
bA3: U21.8 (P3); also elsewhere on the board
bA4: U21.11 (P4); also elsewhere on the board
bA5: U21.13 (P5); also elsewhere on the board
bA6: U21.15 (P6); also elsewhere on the board
bA7: U21.17 (P7); also elsewhere on the board
~CS_TEXT_RD: U5.3; also elsewhere on the board
~CS_TEXT_WR: U5.6; also elsewhere on the board
~CS_TEXT: U5.2, U5.4, U5.9, U5.10, U21.19 (P=R); also elsewhere on the board
~bIORQ: U21.1 (G); also elsewhere on the board
~bM1: U21.2 (P0); also elsewhere on the board
~bRD: U5.1; also elsewhere on the board
~bWR: U5.5; also elsewhere on the board

Notes on the sheet:
SET IO PORT
Note: IO Address Port $96-$97 1-2 =off - A7 (high) 3-4 =on - A6 (low) 5-6 =on - A5 (low) 7-8 =off - A4 (high) 9-10 =on - A3 (low) 11-12 =off - A2 (high) 13-14 =off - A1 (high)
IO SELECTION CIRCUIT
Note: Inhibit Board Operation During Interrupts ~{M1} = low, ~{IORQ} = low
GDC CHIP SELECT

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
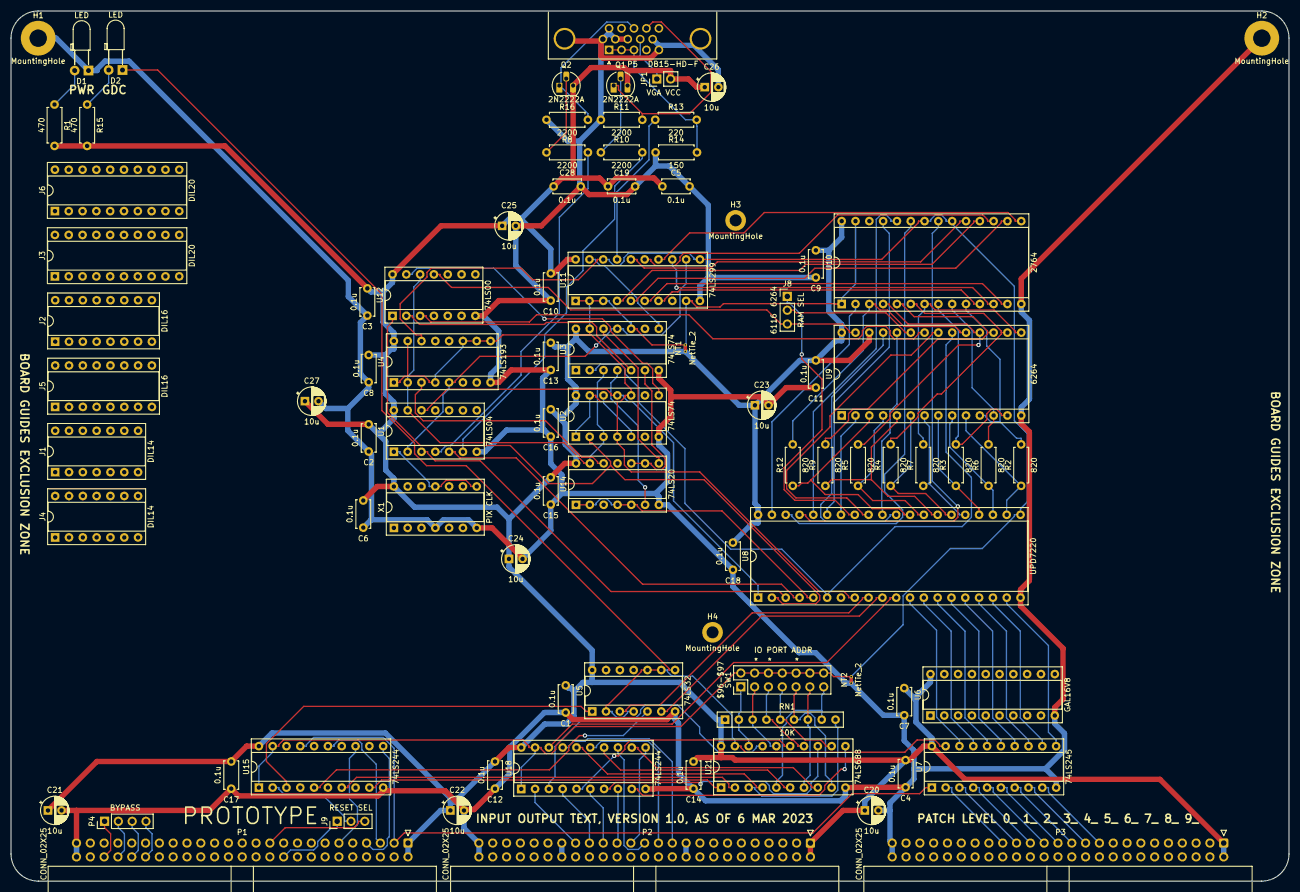
[picture p407: board input-output.Text.kicad_pcb from above]

Board: 2 copper layers, 235.0 x 160.0 mm, 87 parts (0 on the bottom side), 130 nets.
