lynchaj/duodyne/!Development/SAB80535-Dev-Board V1.1/SAB80535-Dev-Board.kicad_pcb

## KiCad design !Development/SAB80535-Dev-Board V1.1/SAB80535-Dev-Board.kicad_pcb (2024-01-15)

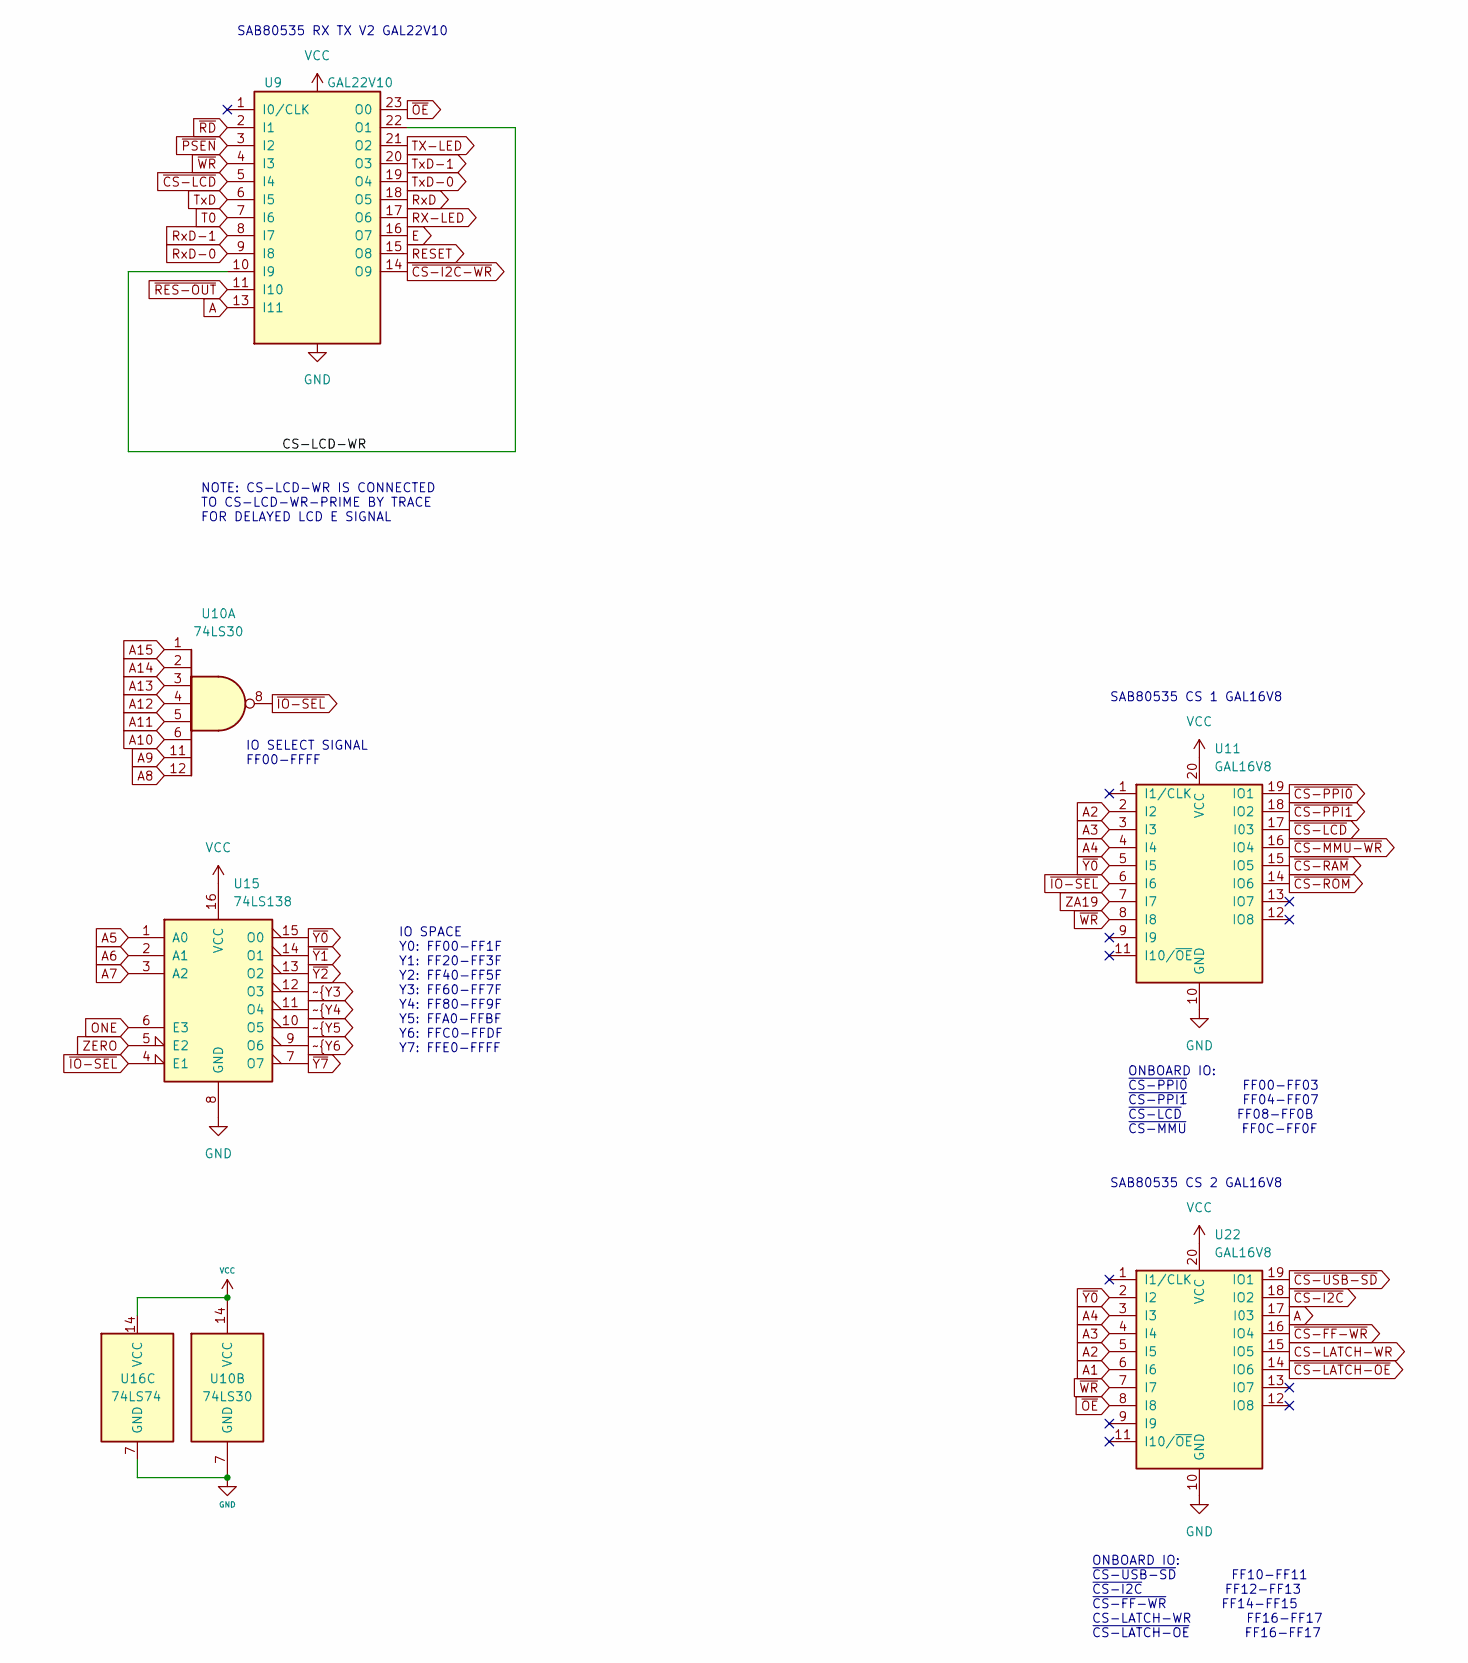
[picture p408: schematic GALs.kicad_sch]

Parts:
U9: GAL22V10; DIP-24_W7.62mm_Socket
U10: 74LS30; DIP-14_W7.62mm_Socket
U11, U22: GAL16V8; DIP-20_W7.62mm_Socket
U15: 74LS138; DIP-16_W7.62mm_Socket
U16: 74LS74; DIP-14_W7.62mm_Socket

Connections:
/GALs/CS-LCD-WR: U9.10 (I9), U9.22 (O1)
A: U9.13 (I11), U22.17 (I03)
A1: U22.6 (I6); also elsewhere on the board
A2: U11.2 (I2), U22.5 (I5); also elsewhere on the board
A3: U11.3 (I3), U22.4 (I4); also elsewhere on the board
A4: U11.4 (I4), U22.3 (I3); also elsewhere on the board
A5: U15.1 (A0); also elsewhere on the board
A6: U15.2 (A1); also elsewhere on the board
A7: U15.3 (A2); also elsewhere on the board
A8: U10.12; also elsewhere on the board
A9: U10.11; also elsewhere on the board
A10: U10.6; also elsewhere on the board
A11: U10.5; also elsewhere on the board
A12: U10.4; also elsewhere on the board
A13: U10.3; also elsewhere on the board
A14: U10.2; also elsewhere on the board
A15: U10.1; also elsewhere on the board
CS-LATCH-WR: U22.15 (IO5); also elsewhere on the board
E: U9.16 (O7); also elsewhere on the board
GND: U9.12 (GND), U10.7 (GND), U11.10 (GND), U15.8 (GND), U16.7 (GND), U22.10 (GND); also elsewhere on the board
ONE: U15.6 (E3); also elsewhere on the board
RESET: U9.15 (O8); also elsewhere on the board
RX-LED: U9.17 (O6); also elsewhere on the board
RxD: U9.18 (O5); also elsewhere on the board
RxD-0: U9.9 (I8); also elsewhere on the board
RxD-1: U9.8 (I7); also elsewhere on the board
T0: U9.7 (I6); also elsewhere on the board
TX-LED: U9.21 (O2); also elsewhere on the board
TxD: U9.6 (I5); also elsewhere on the board
TxD-0: U9.19 (O4); also elsewhere on the board
TxD-1: U9.20 (O3); also elsewhere on the board
VCC: U9.24 (VCC), U10.14 (VCC), U11.20 (VCC), U15.16 (VCC), U16.14 (VCC), U22.20 (VCC); also elsewhere on the board
ZA19: U11.7 (I7); also elsewhere on the board
ZERO: U15.5 (E2); also elsewhere on the board
~CS-FF-WR: U22.16 (IO4); also elsewhere on the board
~CS-I2C-WR: U9.14 (O9); also elsewhere on the board
~CS-I2C: U22.18 (IO2); also elsewhere on the board
~CS-LATCH-OE: U22.14 (IO6); also elsewhere on the board
~CS-LCD: U9.5 (I4), U11.17 (I03); also elsewhere on the board
~CS-MMU-WR: U11.16 (IO4); also elsewhere on the board
~CS-PPI0: U11.19 (IO1); also elsewhere on the board
~CS-PPI1: U11.18 (IO2); also elsewhere on the board
~CS-RAM: U11.15 (IO5); also elsewhere on the board
~CS-ROM: U11.14 (IO6); also elsewhere on the board
~CS-USB-SD: U22.19 (IO1); also elsewhere on the board
~IO-SEL: U10.8, U11.6 (I6), U15.4 (E1); also elsewhere on the board
~OE: U9.23 (O0), U22.8 (I8); also elsewhere on the board
~PSEN: U9.3 (I2); also elsewhere on the board
~RD: U9.2 (I1); also elsewhere on the board
~RES-OUT: U9.11 (I10); also elsewhere on the board
~WR: U9.4 (I3), U11.8 (I8), U22.7 (I7); also elsewhere on the board
~Y0: U11.5 (I5), U15.15 (O0), U22.2 (I2)
~Y1: U15.14 (O1); also elsewhere on the board
~Y2: U15.13 (O2); also elsewhere on the board
~Y7: U15.7 (O7); also elsewhere on the board

Notes on the sheet:
NOTE: CS-LCD-WR IS CONNECTED TO CS-LCD-WR-PRIME BY TRACE FOR DELAYED LCD E SIGNAL
SAB80535 RX TX V2 GAL22V10
IO SELECT SIGNAL FF00-FFFF
SAB80535 CS 2 GAL16V8
IO SPACE Y0: FF00-FF1F Y1: FF20-FF3F Y2: FF40-FF5F Y3: FF60-FF7F Y4: FF80-FF9F Y5: FFA0-FFBF Y6: FFC0-FFDF Y7: FFE0-FFFF
ONBOARD IO: ~{CS-USB-SD} FF10-FF11 ~{CS-I2C} FF12-FF13 ~{CS-FF-WR} FF14-FF15 CS-LATCH-WR FF16-FF17 ~{CS-LATCH-OE} FF16-FF17
SAB80535 CS 1 GAL16V8
ONBOARD IO: ~{CS-PPI0} FF00-FF03 ~{CS-PPI1} FF04-FF07 ~{CS-LCD} FF08-FF0B ~{CS-MMU} FF0C-FF0F

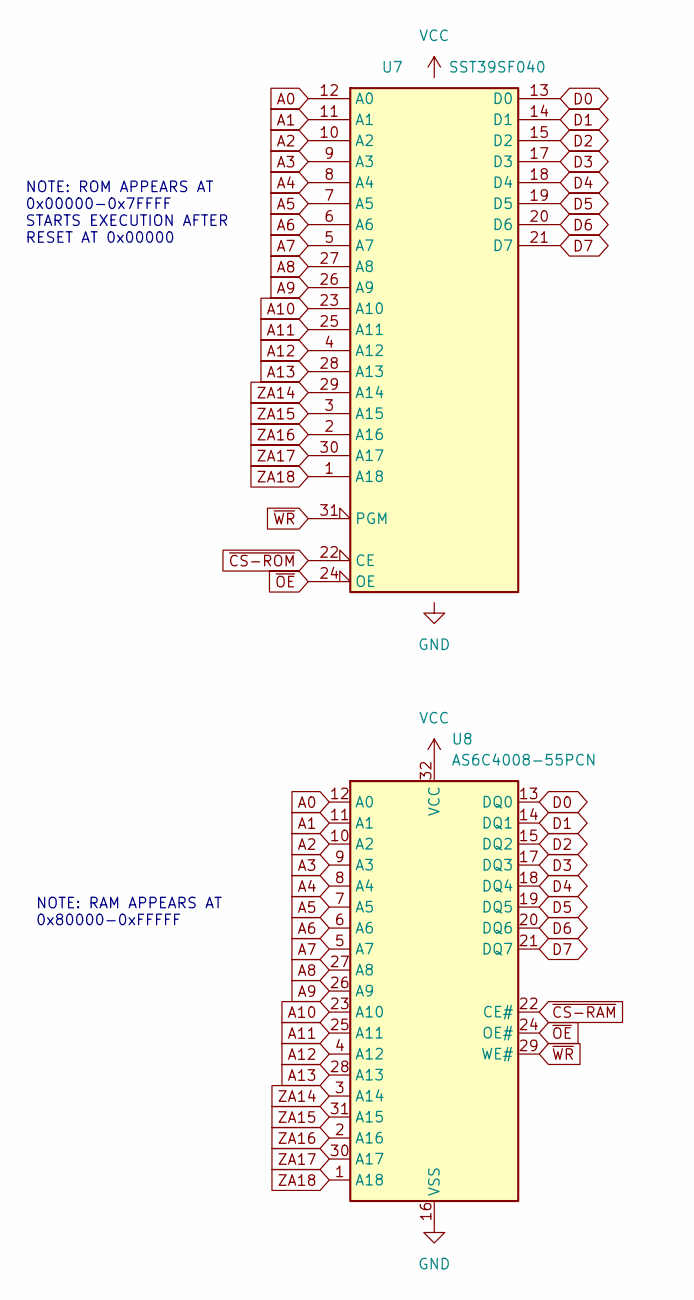
[picture p409: schematic ROM-RAM.kicad_sch]

Parts:
U7: SST39SF040; DIP_Socket-32_W11.9_W12.7_W15.24_W17.78_W18.5_3M_232-1285-0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
U8: AS6C4008-55PCN; DIP-32_W15.24mm_Socket

Connections:
A0: U7.12 (A0), U8.12 (A0); also elsewhere on the board
A1: U7.11 (A1), U8.11 (A1); also elsewhere on the board
A2: U7.10 (A2), U8.10 (A2); also elsewhere on the board
A3: U7.9 (A3), U8.9 (A3); also elsewhere on the board
A4: U7.8 (A4), U8.8 (A4); also elsewhere on the board
A5: U7.7 (A5), U8.7 (A5); also elsewhere on the board
A6: U7.6 (A6), U8.6 (A6); also elsewhere on the board
A7: U7.5 (A7), U8.5 (A7); also elsewhere on the board
A8: U7.27 (A8), U8.27 (A8); also elsewhere on the board
A9: U7.26 (A9), U8.26 (A9); also elsewhere on the board
A10: U7.23 (A10), U8.23 (A10); also elsewhere on the board
A11: U7.25 (A11), U8.25 (A11); also elsewhere on the board
A12: U7.4 (A12), U8.4 (A12); also elsewhere on the board
A13: U7.28 (A13), U8.28 (A13); also elsewhere on the board
D0: U7.13 (D0), U8.13 (DQ0); also elsewhere on the board
D1: U7.14 (D1), U8.14 (DQ1); also elsewhere on the board
D2: U7.15 (D2), U8.15 (DQ2); also elsewhere on the board
D3: U7.17 (D3), U8.17 (DQ3); also elsewhere on the board
D4: U7.18 (D4), U8.18 (DQ4); also elsewhere on the board
D5: U7.19 (D5), U8.19 (DQ5); also elsewhere on the board
D6: U7.20 (D6), U8.20 (DQ6); also elsewhere on the board
D7: U7.21 (D7), U8.21 (DQ7); also elsewhere on the board
GND: U7.16 (GND), U8.16 (VSS); also elsewhere on the board
VCC: U7.32 (VCC), U8.32 (VCC); also elsewhere on the board
ZA14: U7.29 (A14), U8.3 (A14); also elsewhere on the board
ZA15: U7.3 (A15), U8.31 (A15); also elsewhere on the board
ZA16: U7.2 (A16), U8.2 (A16); also elsewhere on the board
ZA17: U7.30 (A17), U8.30 (A17); also elsewhere on the board
ZA18: U7.1 (A18), U8.1 (A18); also elsewhere on the board
~CS-RAM: U8.22 (CE#); also elsewhere on the board
~CS-ROM: U7.22 (CE); also elsewhere on the board
~OE: U7.24 (OE), U8.24 (OE#); also elsewhere on the board
~WR: U7.31 (PGM), U8.29 (WE#); also elsewhere on the board

Notes on the sheet:
NOTE: ROM APPEARS AT 0x00000-0x7FFFF STARTS EXECUTION AFTER RESET AT 0x00000
NOTE: RAM APPEARS AT 0x80000-0xFFFFF

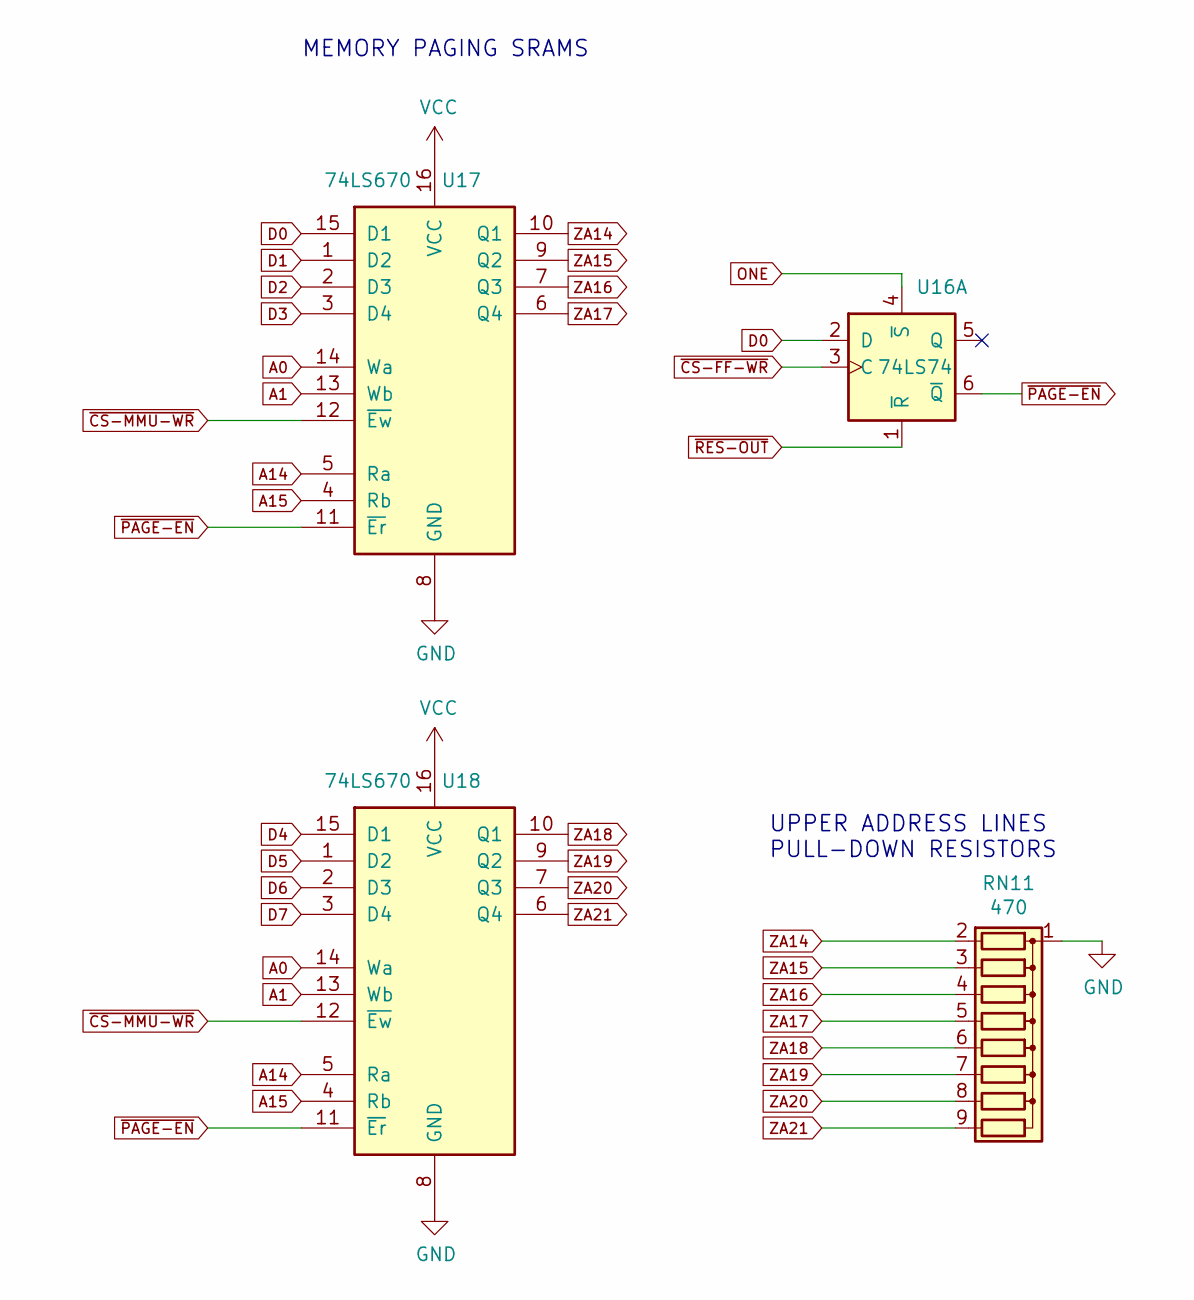
[picture p410: schematic Mapper.kicad_sch]

Parts:
RN11: 470; R_Array_SIP9
U16: 74LS74; DIP-14_W7.62mm_Socket
U17, U18: 74LS670; DIP-16_W7.62mm_Socket

Connections:
A0: U17.14 (Wa), U18.14 (Wa); also elsewhere on the board
A1: U17.13 (Wb), U18.13 (Wb); also elsewhere on the board
A14: U17.5 (Ra), U18.5 (Ra); also elsewhere on the board
A15: U17.4 (Rb), U18.4 (Rb); also elsewhere on the board
D0: U16.2 (D), U17.15 (D1); also elsewhere on the board
D1: U17.1 (D2); also elsewhere on the board
D2: U17.2 (D3); also elsewhere on the board
D3: U17.3 (D4); also elsewhere on the board
D4: U18.15 (D1); also elsewhere on the board
D5: U18.1 (D2); also elsewhere on the board
D6: U18.2 (D3); also elsewhere on the board
D7: U18.3 (D4); also elsewhere on the board
GND: RN11.1 (common), U17.8 (GND), U18.8 (GND); also elsewhere on the board
ONE: U16.4 (~S); also elsewhere on the board
VCC: U17.16 (VCC), U18.16 (VCC); also elsewhere on the board
ZA14: RN11.2 (R1), U17.10 (Q1); also elsewhere on the board
ZA15: RN11.3 (R2), U17.9 (Q2); also elsewhere on the board
ZA16: RN11.4 (R3), U17.7 (Q3); also elsewhere on the board
ZA17: RN11.5 (R4), U17.6 (Q4); also elsewhere on the board
ZA18: RN11.6 (R5), U18.10 (Q1); also elsewhere on the board
ZA19: RN11.7 (R6), U18.9 (Q2); also elsewhere on the board
ZA20: RN11.8 (R7), U18.7 (Q3); also elsewhere on the board
ZA21: RN11.9 (R8), U18.6 (Q4); also elsewhere on the board
~CS-FF-WR: U16.3 (C); also elsewhere on the board
~CS-MMU-WR: U17.12 (~Ew), U18.12 (~Ew); also elsewhere on the board
~PAGE-EN: U16.6 (~Q), U17.11 (~Er), U18.11 (~Er)
~RES-OUT: U16.1 (~R); also elsewhere on the board

Notes on the sheet:
UPPER ADDRESS LINES PULL-DOWN RESISTORS
MEMORY PAGING SRAMS

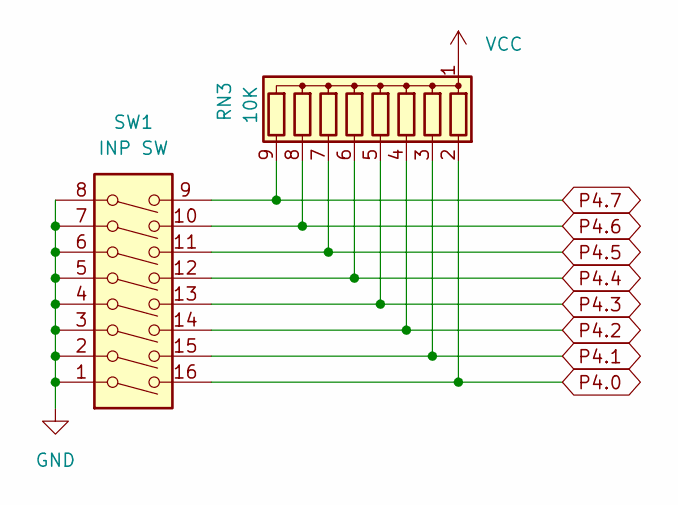
[picture p411: schematic Input Switches.kicad_sch]

Parts:
RN3: 10K; R_Array_SIP9
SW1: INP SW; SW_DIP_SPSTx08_Slide_9.78x22.5mm_W7.62mm_P2.54mm

Connections:
GND: SW1.1, SW1.2, SW1.3, SW1.4, SW1.5, SW1.6, SW1.7, SW1.8; also elsewhere on the board
P4.0: RN3.2 (R1), SW1.16; also elsewhere on the board
P4.1: RN3.3 (R2), SW1.15; also elsewhere on the board
P4.2: RN3.4 (R3), SW1.14; also elsewhere on the board
P4.3: RN3.5 (R4), SW1.13; also elsewhere on the board
P4.4: RN3.6 (R5), SW1.12; also elsewhere on the board
P4.5: RN3.7 (R6), SW1.11; also elsewhere on the board
P4.6: RN3.8 (R7), SW1.10; also elsewhere on the board
P4.7: RN3.9 (R8), SW1.9; also elsewhere on the board
VCC: RN3.1 (common); also elsewhere on the board

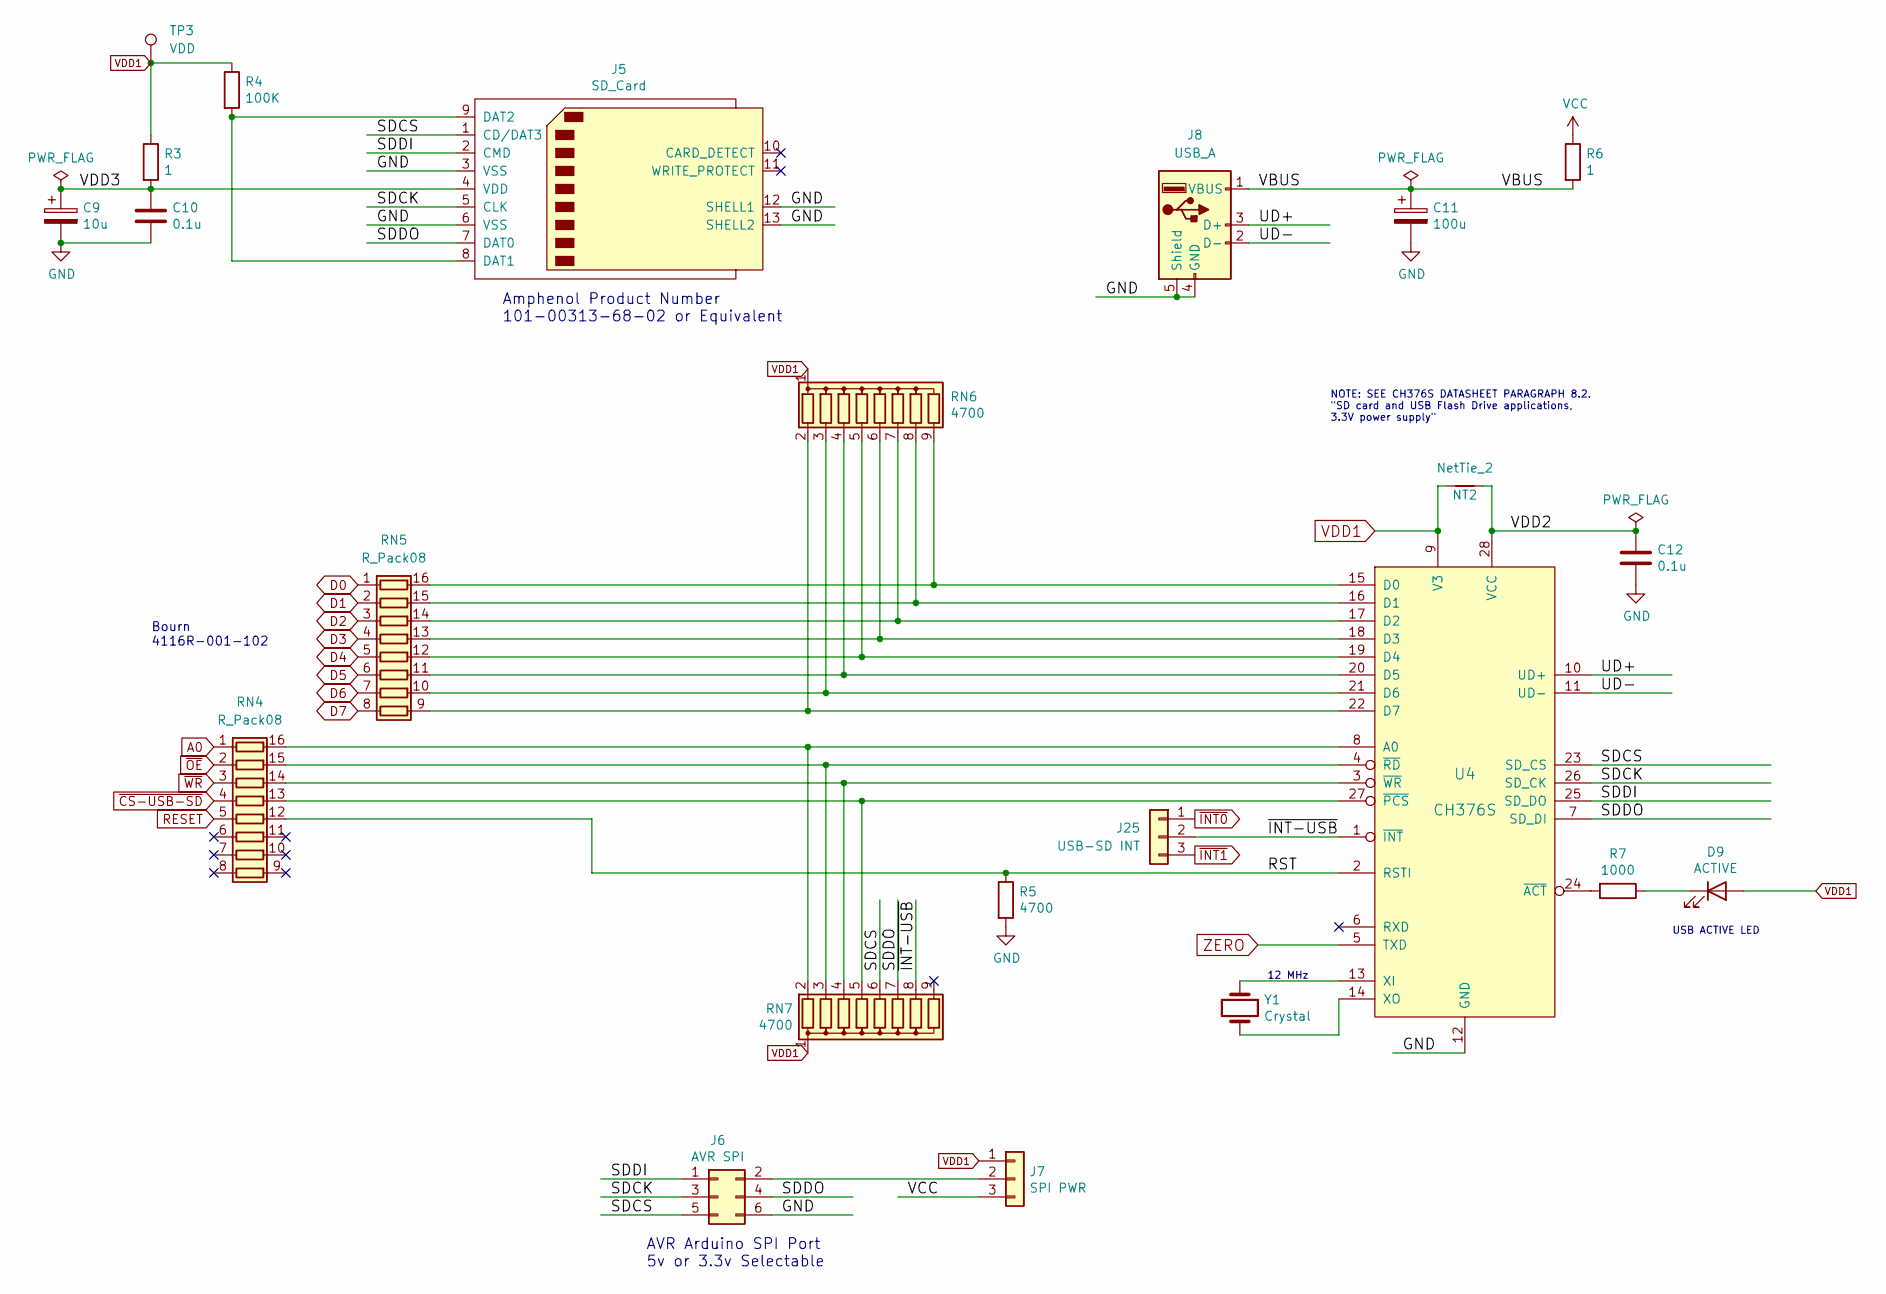
[picture p412: schematic USB-SD.kicad_sch]

Parts:
C9: 10u; CP_Radial_D5.0mm_P2.50mm
C10, C12: 0.1u; C_Disc_D5.0mm_W2.5mm_P5.00mm
C11: 100u; CP_Radial_D6.3mm_P2.50mm
D9: ACTIVE; LED_D3.0mm
J5: SD_Card; SD_Card_Receptacle
J6: AVR SPI; PinHeader_2x03_P2.54mm_Vertical
J7: SPI PWR; PinHeader_1x03_P2.54mm_Vertical
J8: USB_A; USB_A_Molex_67643_Horizontal
J25: USB-SD INT; PinHeader_1x03_P2.54mm_Vertical
NT2: NetTie_2; NetTie-2_THT_Pad0.3mm
R3, R6: 1; R_Axial_DIN0207_L6.3mm_D2.5mm_P7.62mm_Horizontal
R4: 100K; R_Axial_DIN0207_L6.3mm_D2.5mm_P7.62mm_Horizontal
R5: 4700; R_Axial_DIN0207_L6.3mm_D2.5mm_P7.62mm_Horizontal
R7: 1000; R_Axial_DIN0207_L6.3mm_D2.5mm_P7.62mm_Horizontal
RN4, RN5: R_Pack08; DIP-16_W7.62mm_Socket
RN6, RN7: 4700; R_Array_SIP9
TP3: VDD; PinHeader_1x01_P2.54mm_Vertical
U4: CH376S; DIP-28_W15.24mm_Socket
Y1: Crystal; Crystal_HC49-4H_Vertical

Connections:
/USB-SD/RST: R5.1, RN4.12 (R5.2), U4.2 (RSTI)
/USB-SD/SDCK: J5.5 (CLK), J6.3, U4.26 (SD_CK)
/USB-SD/SDCS: J5.1 (CD/DAT3), J6.5, RN7.6 (R5), U4.23 (SD_CS)
/USB-SD/SDDI: J5.2 (CMD), J6.1, U4.25 (SD_DO)
/USB-SD/SDDO: J5.7 (DAT0), J6.4, RN7.7 (R6), U4.7 (SD_DI)
/USB-SD/UD+: J8.3 (D+), U4.10 (UD+)
/USB-SD/UD-: J8.2 (D-), U4.11 (UD-)
/USB-SD/VBUS: C11.1, J8.1 (VBUS), R6.2
/USB-SD/VDD2: C12.1, NT2.1, U4.28 (VCC)
/USB-SD/VDD3: C9.1, C10.1, J5.4 (VDD), R3.2
/USB-SD/~INT-USB: J25.2, RN7.8 (R7), U4.1 (~INT)
A0: RN4.1 (R1.1); also elsewhere on the board
D0: RN5.1 (R1.1); also elsewhere on the board
D1: RN5.2 (R2.1); also elsewhere on the board
D2: RN5.3 (R3.1); also elsewhere on the board
D3: RN5.4 (R4.1); also elsewhere on the board
D4: RN5.5 (R5.1); also elsewhere on the board
D5: RN5.6 (R6.1); also elsewhere on the board
D6: RN5.7 (R7.1); also elsewhere on the board
D7: RN5.8 (R8.1); also elsewhere on the board
GND: C9.2, C10.2, C11.2, C12.2, J5.3 (VSS), J5.6 (VSS), J5.12 (SHELL1), J5.13 (SHELL2), J6.6, J8.4 (GND), J8.5 (Shield), R5.2, U4.12 (GND); also elsewhere on the board
unnamed: D9.1 (K), R7.1
unnamed: J5.8 (DAT1), J5.9 (DAT2), R4.2
unnamed: J6.2, J7.2
unnamed: R7.2, U4.24 (~ACT)
unnamed: RN4.13 (R4.2), RN7.5 (R4), U4.27 (~PCS)
unnamed: RN4.14 (R3.2), RN7.4 (R3), U4.3 (~WR)
unnamed: RN4.15 (R2.2), RN7.3 (R2), U4.4 (~RD)
unnamed: RN4.16 (R1.2), RN7.2 (R1), U4.8 (A0)
unnamed: RN5.9 (R8.2), RN6.2 (R1), U4.22 (D7)
unnamed: RN5.10 (R7.2), RN6.3 (R2), U4.21 (D6)
unnamed: RN5.11 (R6.2), RN6.4 (R3), U4.20 (D5)
unnamed: RN5.12 (R5.2), RN6.5 (R4), U4.19 (D4)
unnamed: RN5.13 (R4.2), RN6.6 (R5), U4.18 (D3)
unnamed: RN5.14 (R3.2), RN6.7 (R6), U4.17 (D2)
unnamed: RN5.15 (R2.2), RN6.8 (R7), U4.16 (D1)
unnamed: RN5.16 (R1.2), RN6.9 (R8), U4.15 (D0)
unnamed: U4.13 (XI), Y1.1
unnamed: U4.14 (XO), Y1.2
RESET: RN4.5 (R5.1); also elsewhere on the board
VCC: J7.3, R6.1; also elsewhere on the board
VDD1: D9.2 (A), J7.1, NT2.2, R3.1, R4.1, RN6.1 (common), RN7.1 (common), TP3.1, U4.9 (V3); also elsewhere on the board
ZERO: U4.5 (TXD); also elsewhere on the board
~CS-USB-SD: RN4.4 (R4.1); also elsewhere on the board
~INT0: J25.1; also elsewhere on the board
~INT1: J25.3; also elsewhere on the board
~OE: RN4.2 (R2.1); also elsewhere on the board
~WR: RN4.3 (R3.1); also elsewhere on the board

Notes on the sheet:
12 MHz
Amphenol Product Number 101-00313-68-02 or Equivalent
AVR Arduino SPI Port 5v or 3.3v Selectable
USB ACTIVE LED
Bourn 4116R-001-102
NOTE: SEE CH376S DATASHEET PARAGRAPH 8.2. "SD card and USB Flash Drive applications, 3.3V power supply"

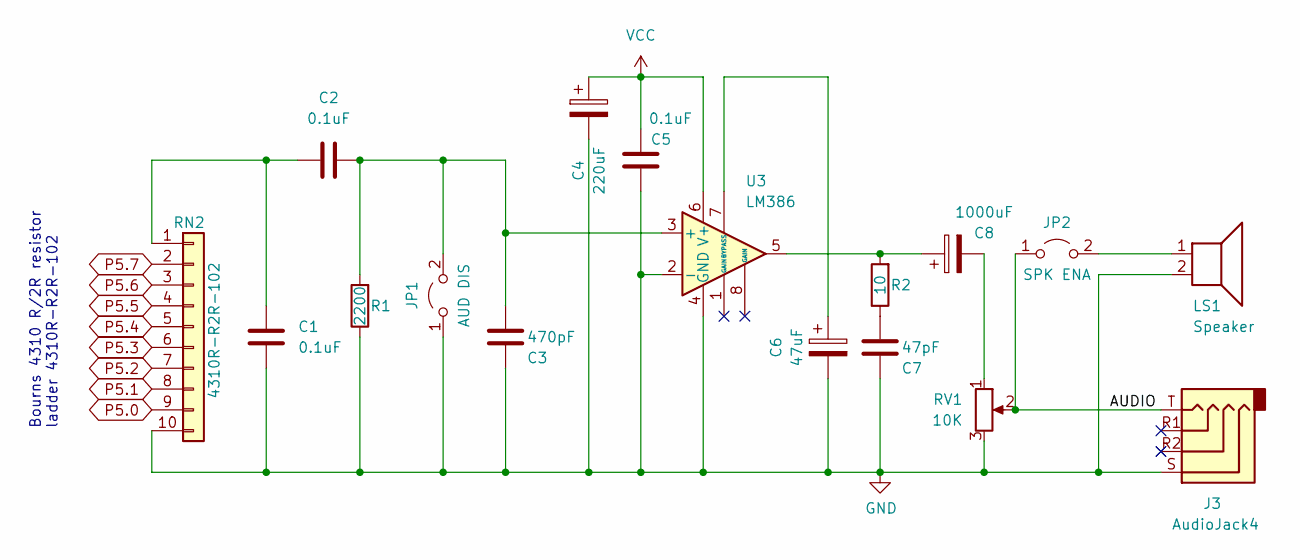
[picture p413: schematic Audio.kicad_sch]

Parts:
C1, C2, C5: 0.1uF; C_Disc_D5.0mm_W2.5mm_P5.00mm
C3: 470pF; C_Disc_D3.8mm_W2.6mm_P2.50mm
C4: 220uF; CP_Radial_D8.0mm_P2.50mm
C6: 47uF; CP_Radial_D5.0mm_P2.50mm
C7: 47pF; C_Disc_D3.8mm_W2.6mm_P2.50mm
C8: 1000uF; CP_Radial_D8.0mm_P2.50mm
J3: AudioJack4; Jack_3.5mm_PJ320E_Horizontal
JP1: AUD DIS; PinHeader_1x02_P2.54mm_Vertical
JP2: SPK ENA; PinHeader_1x02_P2.54mm_Vertical
LS1: Speaker; Jameco PCB Speaker 30mm 135722
R1: 2200; R_Axial_DIN0207_L6.3mm_D2.5mm_P7.62mm_Horizontal
R2: 10; R_Axial_DIN0207_L6.3mm_D2.5mm_P7.62mm_Horizontal
RN2: 4310R-R2R-102; R_Array_SIP10
RV1: 10K; Potentiometer_Bourns_3386P_Vertical
U3: LM386; DIP-8_W7.62mm_Socket

Connections:
/Audio/AUDIO: J3.T, JP2.1 (A), RV1.2
GND: C1.2, C3.2, C4.2, C5.1, C6.2, C7.2, J3.S, JP1.1 (A), LS1.2, R1.1, RN2.10, RV1.3, U3.2 (-), U3.4 (GND); also elsewhere on the board
unnamed: C1.1, C2.1, RN2.1
unnamed: C2.2, C3.1, JP1.2 (B), R1.2, U3.3 (+)
unnamed: C6.1, U3.7 (BYPASS)
unnamed: C7.1, R2.1
unnamed: C8.1, R2.2, U3.5
unnamed: C8.2, RV1.1
unnamed: JP2.2 (B), LS1.1
P5.0: RN2.9; also elsewhere on the board
P5.1: RN2.8; also elsewhere on the board
P5.2: RN2.7; also elsewhere on the board
P5.3: RN2.6; also elsewhere on the board
P5.4: RN2.5; also elsewhere on the board
P5.5: RN2.4; also elsewhere on the board
P5.6: RN2.3; also elsewhere on the board
P5.7: RN2.2; also elsewhere on the board
VCC: C4.1, C5.2, U3.6 (V+); also elsewhere on the board

Notes on the sheet:
Bourns 4310 R/2R resistor ladder 4310R-R2R-102

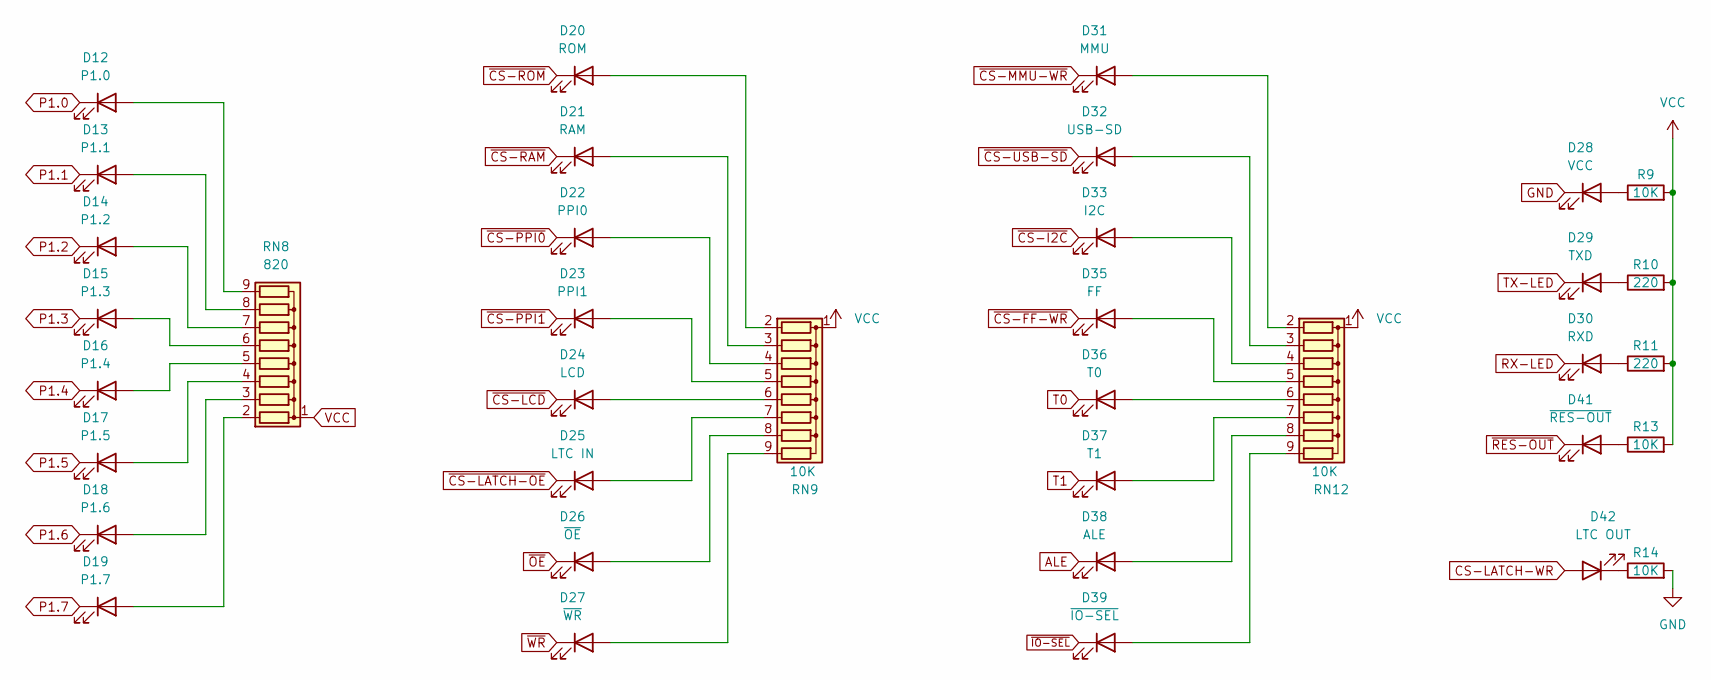
[picture p414: schematic Diagnostics.kicad_sch]

Parts:
D12: P1.0; LED_D3.0mm
D13: P1.1; LED_D3.0mm
D14: P1.2; LED_D3.0mm
D15: P1.3; LED_D3.0mm
D16: P1.4; LED_D3.0mm
D17: P1.5; LED_D3.0mm
D18: P1.6; LED_D3.0mm
D19: P1.7; LED_D3.0mm
D20: ROM; LED_D3.0mm
D21: RAM; LED_D3.0mm
D22: PPI0; LED_D3.0mm
D23: PPI1; LED_D3.0mm
D24: LCD; LED_D3.0mm
D25: LTC IN; LED_D3.0mm
D26: ~{OE}; LED_D3.0mm
D27: ~{WR}; LED_D3.0mm
D28: VCC; LED_D3.0mm
D29: TXD; LED_D3.0mm
D30: RXD; LED_D3.0mm
D31: MMU; LED_D3.0mm
D32: USB-SD; LED_D3.0mm
D33: I2C; LED_D3.0mm
D35: FF; LED_D3.0mm
D36: T0; LED_D3.0mm
D37: T1; LED_D3.0mm
D38: ALE; LED_D3.0mm
D39: ~{IO-SEL}; LED_D3.0mm
D41: ~{RES-OUT}; LED_D3.0mm
D42: LTC OUT; LED_D3.0mm
R9, R13, R14: 10K; R_Axial_DIN0207_L6.3mm_D2.5mm_P7.62mm_Horizontal
R10, R11: 220; R_Axial_DIN0207_L6.3mm_D2.5mm_P7.62mm_Horizontal
RN8: 820; R_Array_SIP9
RN9, RN12: 10K; R_Array_SIP9

Connections:
ALE: D38.1 (K); also elsewhere on the board
CS-LATCH-WR: D42.2 (A); also elsewhere on the board
GND: D28.1 (K), R14.2; also elsewhere on the board
unnamed: D12.2 (A), RN8.9 (R8)
unnamed: D13.2 (A), RN8.8 (R7)
unnamed: D14.2 (A), RN8.7 (R6)
unnamed: D15.2 (A), RN8.6 (R5)
unnamed: D16.2 (A), RN8.5 (R4)
unnamed: D17.2 (A), RN8.4 (R3)
unnamed: D18.2 (A), RN8.3 (R2)
unnamed: D19.2 (A), RN8.2 (R1)
unnamed: D20.2 (A), RN9.2 (R1)
unnamed: D21.2 (A), RN9.3 (R2)
unnamed: D22.2 (A), RN9.4 (R3)
unnamed: D23.2 (A), RN9.5 (R4)
unnamed: D24.2 (A), RN9.6 (R5)
unnamed: D25.2 (A), RN9.7 (R6)
unnamed: D26.2 (A), RN9.8 (R7)
unnamed: D27.2 (A), RN9.9 (R8)
unnamed: D28.2 (A), R9.1
unnamed: D29.2 (A), R10.1
unnamed: D30.2 (A), R11.1
unnamed: D31.2 (A), RN12.2 (R1)
unnamed: D32.2 (A), RN12.3 (R2)
unnamed: D33.2 (A), RN12.4 (R3)
unnamed: D35.2 (A), RN12.5 (R4)
unnamed: D36.2 (A), RN12.6 (R5)
unnamed: D37.2 (A), RN12.7 (R6)
unnamed: D38.2 (A), RN12.8 (R7)
unnamed: D39.2 (A), RN12.9 (R8)
unnamed: D41.2 (A), R13.1
unnamed: D42.1 (K), R14.1
P1.0: D12.1 (K); also elsewhere on the board
P1.1: D13.1 (K); also elsewhere on the board
P1.2: D14.1 (K); also elsewhere on the board
P1.3: D15.1 (K); also elsewhere on the board
P1.4: D16.1 (K); also elsewhere on the board
P1.5: D17.1 (K); also elsewhere on the board
P1.6: D18.1 (K); also elsewhere on the board
P1.7: D19.1 (K); also elsewhere on the board
RX-LED: D30.1 (K); also elsewhere on the board
T0: D36.1 (K); also elsewhere on the board
T1: D37.1 (K); also elsewhere on the board
TX-LED: D29.1 (K); also elsewhere on the board
VCC: R9.2, R10.2, R11.2, R13.2, RN8.1 (common), RN9.1 (common), RN12.1 (common); also elsewhere on the board
~CS-FF-WR: D35.1 (K); also elsewhere on the board
~CS-I2C: D33.1 (K); also elsewhere on the board
~CS-LATCH-OE: D25.1 (K); also elsewhere on the board
~CS-LCD: D24.1 (K); also elsewhere on the board
~CS-MMU-WR: D31.1 (K); also elsewhere on the board
~CS-PPI0: D22.1 (K); also elsewhere on the board
~CS-PPI1: D23.1 (K); also elsewhere on the board
~CS-RAM: D21.1 (K); also elsewhere on the board
~CS-ROM: D20.1 (K); also elsewhere on the board
~CS-USB-SD: D32.1 (K); also elsewhere on the board
~IO-SEL: D39.1 (K); also elsewhere on the board
~OE: D26.1 (K); also elsewhere on the board
~RES-OUT: D41.1 (K); also elsewhere on the board
~WR: D27.1 (K); also elsewhere on the board

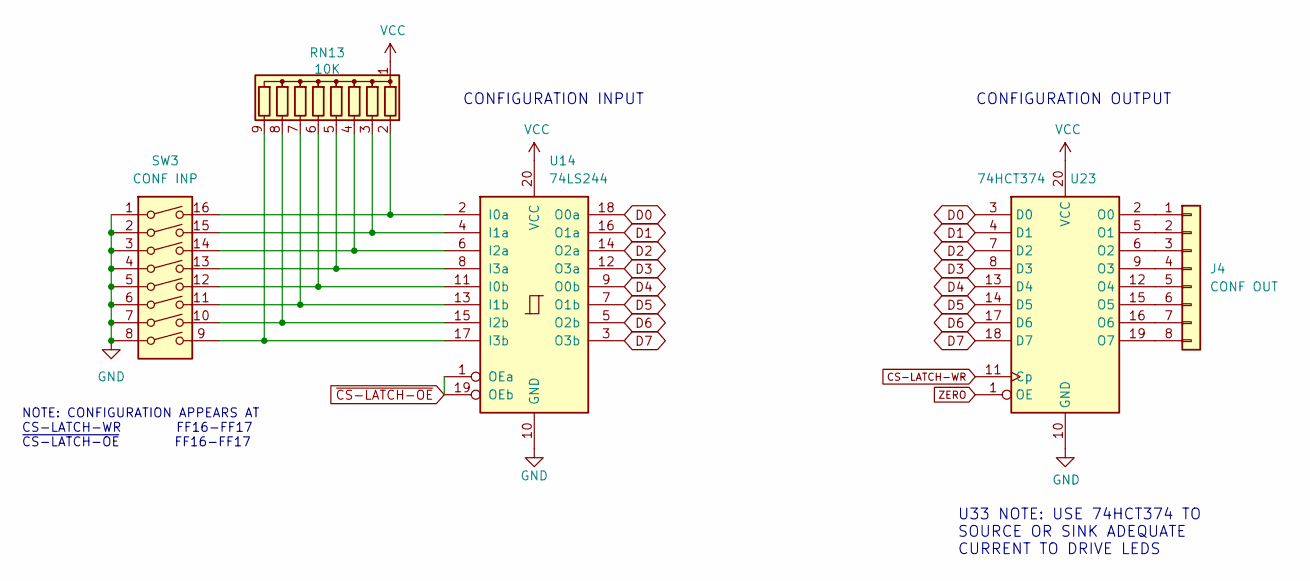
[picture p415: schematic Config Input.kicad_sch]

Parts:
J4: CONF OUT; PinHeader_1x08_P2.54mm_Vertical
RN13: 10K; R_Array_SIP9
SW3: CONF INP; SW_DIP_SPSTx08_Slide_9.78x22.5mm_W7.62mm_P2.54mm
U14: 74LS244; DIP-20_W7.62mm_Socket
U23: 74HCT374; DIP-20_W7.62mm_Socket

Connections:
CS-LATCH-WR: U23.11 (Cp); also elsewhere on the board
D0: U14.18 (O0a), U23.3 (D0); also elsewhere on the board
D1: U14.16 (O1a), U23.4 (D1); also elsewhere on the board
D2: U14.14 (O2a), U23.7 (D2); also elsewhere on the board
D3: U14.12 (O3a), U23.8 (D3); also elsewhere on the board
D4: U14.9 (O0b), U23.13 (D4); also elsewhere on the board
D5: U14.7 (O1b), U23.14 (D5); also elsewhere on the board
D6: U14.5 (O2b), U23.17 (D6); also elsewhere on the board
D7: U14.3 (O3b), U23.18 (D7); also elsewhere on the board
GND: SW3.1, SW3.2, SW3.3, SW3.4, SW3.5, SW3.6, SW3.7, SW3.8, U14.10 (GND), U23.10 (GND); also elsewhere on the board
unnamed: J4.1, U23.2 (O0)
unnamed: J4.2, U23.5 (O1)
unnamed: J4.3, U23.6 (O2)
unnamed: J4.4, U23.9 (O3)
unnamed: J4.5, U23.12 (O4)
unnamed: J4.6, U23.15 (O5)
unnamed: J4.7, U23.16 (O6)
unnamed: J4.8, U23.19 (O7)
unnamed: RN13.2 (R1), SW3.16, U14.2 (I0a)
unnamed: RN13.3 (R2), SW3.15, U14.4 (I1a)
unnamed: RN13.4 (R3), SW3.14, U14.6 (I2a)
unnamed: RN13.5 (R4), SW3.13, U14.8 (I3a)
unnamed: RN13.6 (R5), SW3.12, U14.11 (I0b)
unnamed: RN13.7 (R6), SW3.11, U14.13 (I1b)
unnamed: RN13.8 (R7), SW3.10, U14.15 (I2b)
unnamed: RN13.9 (R8), SW3.9, U14.17 (I3b)
VCC: RN13.1 (common), U14.20 (VCC), U23.20 (VCC); also elsewhere on the board
ZERO: U23.1 (OE); also elsewhere on the board
~CS-LATCH-OE: U14.1 (OEa), U14.19 (OEb); also elsewhere on the board

Notes on the sheet:
U33 NOTE: USE 74HCT374 TO SOURCE OR SINK ADEQUATE CURRENT TO DRIVE LEDS
CONFIGURATION INPUT
CONFIGURATION OUTPUT
NOTE: CONFIGURATION APPEARS AT CS-LATCH-WR FF16-FF17 ~{CS-LATCH-OE} FF16-FF17
