lynchaj/duodyne/!Development/SAB80535-Dev-Board V1.1/SAB80535-Dev-Board.kicad_pcb

## KiCad design !Development/SAB80535-Dev-Board V1.1/SAB80535-Dev-Board.kicad_pcb (continued)

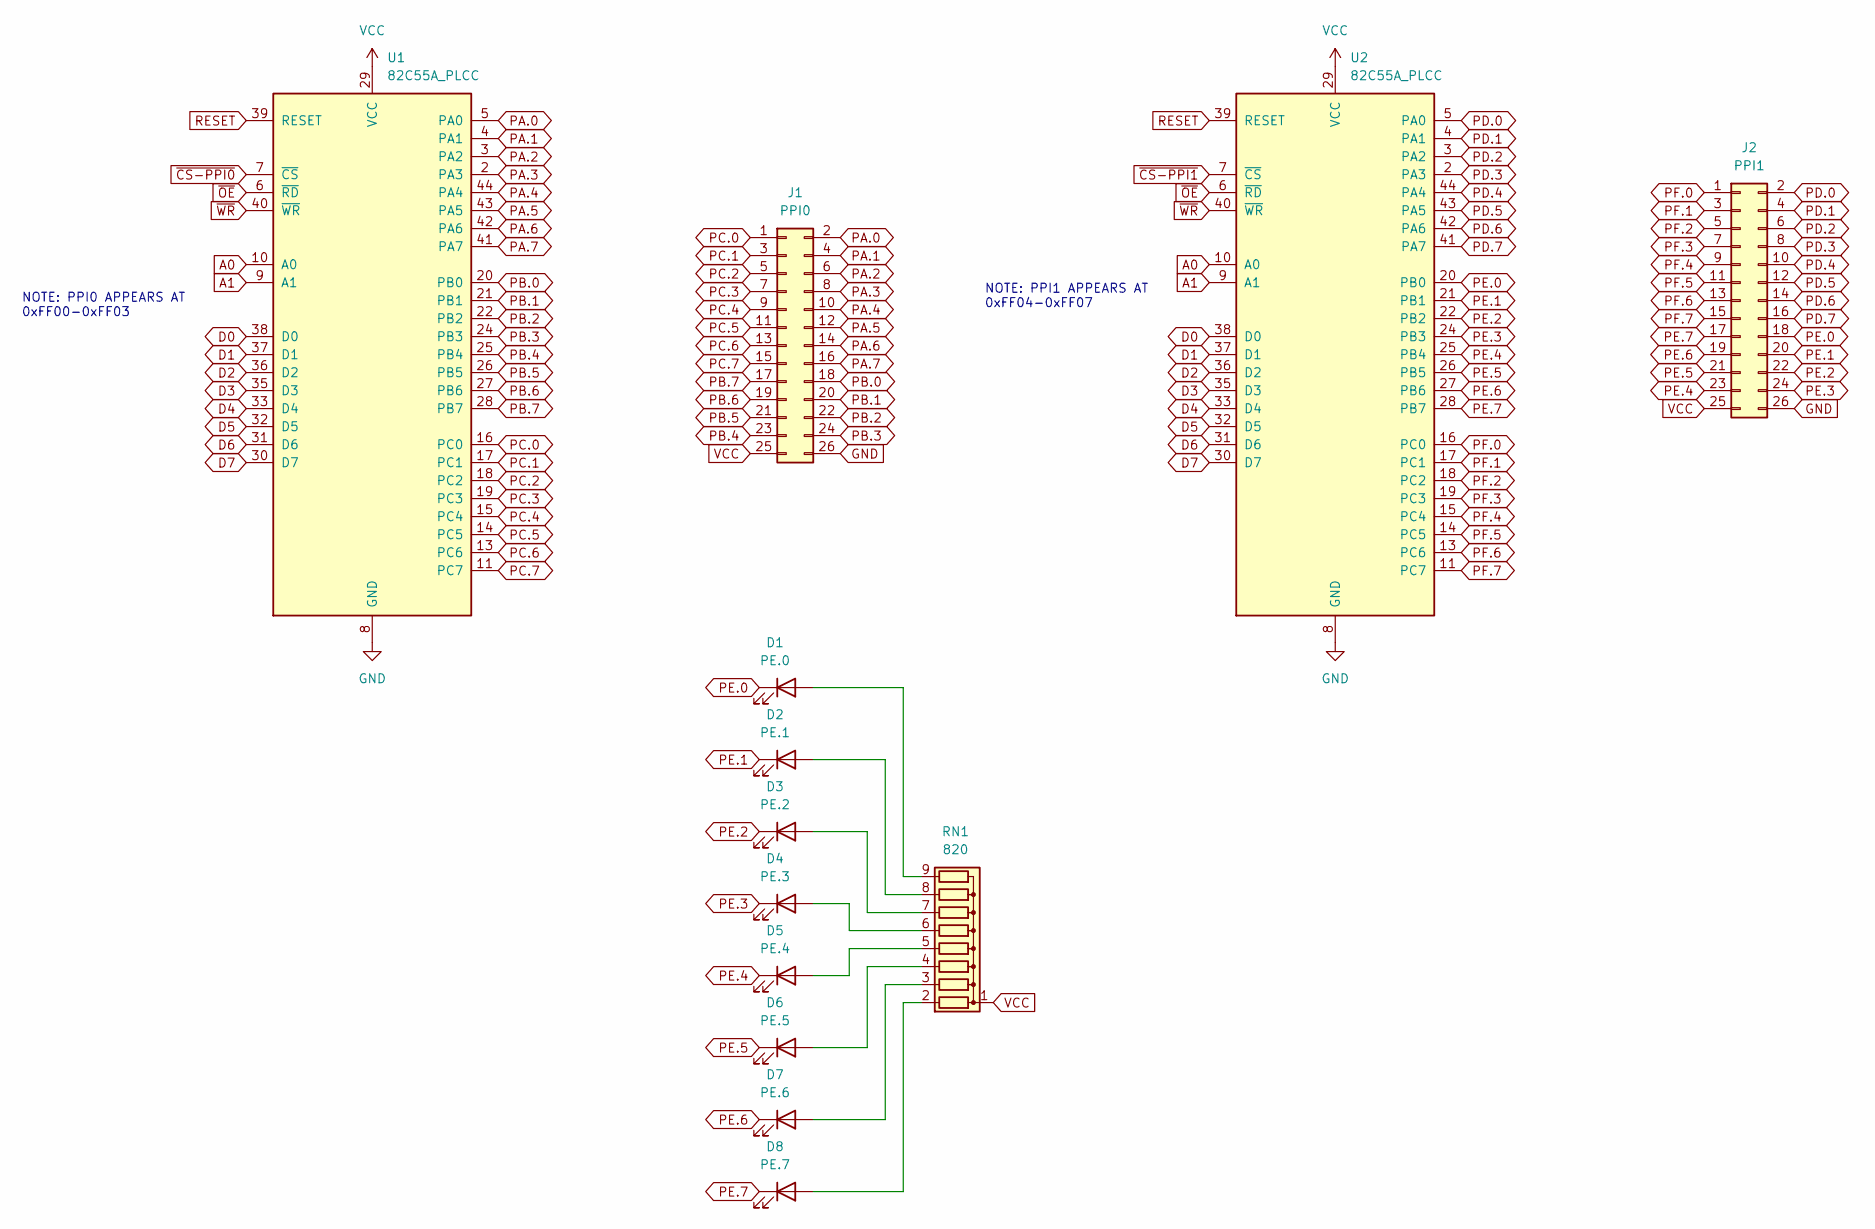
[picture p416: schematic PPIs.kicad_sch]

Parts:
D1: PE.0; LED_D3.0mm
D2: PE.1; LED_D3.0mm
D3: PE.2; LED_D3.0mm
D4: PE.3; LED_D3.0mm
D5: PE.4; LED_D3.0mm
D6: PE.5; LED_D3.0mm
D7: PE.6; LED_D3.0mm
D8: PE.7; LED_D3.0mm
J1: PPI0; IDC-Header_2x13_P2.54mm_Horizontal
J2: PPI1; IDC-Header_2x13_P2.54mm_Horizontal
RN1: 820; R_Array_SIP9
U1, U2: 82C55A_PLCC; PLCC-44_THT-Socket

Connections:
A0: U1.10 (A0), U2.10 (A0); also elsewhere on the board
A1: U1.9 (A1), U2.9 (A1); also elsewhere on the board
D0: U1.38 (D0), U2.38 (D0); also elsewhere on the board
D1: U1.37 (D1), U2.37 (D1); also elsewhere on the board
D2: U1.36 (D2), U2.36 (D2); also elsewhere on the board
D3: U1.35 (D3), U2.35 (D3); also elsewhere on the board
D4: U1.33 (D4), U2.33 (D4); also elsewhere on the board
D5: U1.32 (D5), U2.32 (D5); also elsewhere on the board
D6: U1.31 (D6), U2.31 (D6); also elsewhere on the board
D7: U1.30 (D7), U2.30 (D7); also elsewhere on the board
GND: J1.26, J2.26, U1.8 (GND), U2.8 (GND); also elsewhere on the board
unnamed: D1.2 (A), RN1.9 (R8)
unnamed: D2.2 (A), RN1.8 (R7)
unnamed: D3.2 (A), RN1.7 (R6)
unnamed: D4.2 (A), RN1.6 (R5)
unnamed: D5.2 (A), RN1.5 (R4)
unnamed: D6.2 (A), RN1.4 (R3)
unnamed: D7.2 (A), RN1.3 (R2)
unnamed: D8.2 (A), RN1.2 (R1)
PA.0: J1.2, U1.5 (PA0)
PA.1: J1.4, U1.4 (PA1)
PA.2: J1.6, U1.3 (PA2)
PA.3: J1.8, U1.2 (PA3)
PA.4: J1.10, U1.44 (PA4)
PA.5: J1.12, U1.43 (PA5)
PA.6: J1.14, U1.42 (PA6)
PA.7: J1.16, U1.41 (PA7)
PB.0: J1.18, U1.20 (PB0)
PB.1: J1.20, U1.21 (PB1)
PB.2: J1.22, U1.22 (PB2)
PB.3: J1.24, U1.24 (PB3)
PB.4: J1.23, U1.25 (PB4)
PB.5: J1.21, U1.26 (PB5)
PB.6: J1.19, U1.27 (PB6)
PB.7: J1.17, U1.28 (PB7)
PC.0: J1.1, U1.16 (PC0)
PC.1: J1.3, U1.17 (PC1)
PC.2: J1.5, U1.18 (PC2)
PC.3: J1.7, U1.19 (PC3)
PC.4: J1.9, U1.15 (PC4)
PC.5: J1.11, U1.14 (PC5)
PC.6: J1.13, U1.13 (PC6)
PC.7: J1.15, U1.11 (PC7)
PD.0: J2.2, U2.5 (PA0)
PD.1: J2.4, U2.4 (PA1)
PD.2: J2.6, U2.3 (PA2)
PD.3: J2.8, U2.2 (PA3)
PD.4: J2.10, U2.44 (PA4)
PD.5: J2.12, U2.43 (PA5)
PD.6: J2.14, U2.42 (PA6)
PD.7: J2.16, U2.41 (PA7)
PE.0: D1.1 (K), J2.18, U2.20 (PB0)
PE.1: D2.1 (K), J2.20, U2.21 (PB1)
PE.2: D3.1 (K), J2.22, U2.22 (PB2)
PE.3: D4.1 (K), J2.24, U2.24 (PB3)
PE.4: D5.1 (K), J2.23, U2.25 (PB4)
PE.5: D6.1 (K), J2.21, U2.26 (PB5)
PE.6: D7.1 (K), J2.19, U2.27 (PB6)
PE.7: D8.1 (K), J2.17, U2.28 (PB7)
PF.0: J2.1, U2.16 (PC0)
PF.1: J2.3, U2.17 (PC1)
PF.2: J2.5, U2.18 (PC2)
PF.3: J2.7, U2.19 (PC3)
PF.4: J2.9, U2.15 (PC4)
PF.5: J2.11, U2.14 (PC5)
PF.6: J2.13, U2.13 (PC6)
PF.7: J2.15, U2.11 (PC7)
RESET: U1.39 (RESET), U2.39 (RESET); also elsewhere on the board
VCC: J1.25, J2.25, RN1.1 (common), U1.29 (VCC), U2.29 (VCC); also elsewhere on the board
~CS-PPI0: U1.7 (~CS); also elsewhere on the board
~CS-PPI1: U2.7 (~CS); also elsewhere on the board
~OE: U1.6 (~RD), U2.6 (~RD); also elsewhere on the board
~WR: U1.40 (~WR), U2.40 (~WR); also elsewhere on the board

Notes on the sheet:
NOTE: PPI0 APPEARS AT 0xFF00-0xFF03
NOTE: PPI1 APPEARS AT 0xFF04-0xFF07

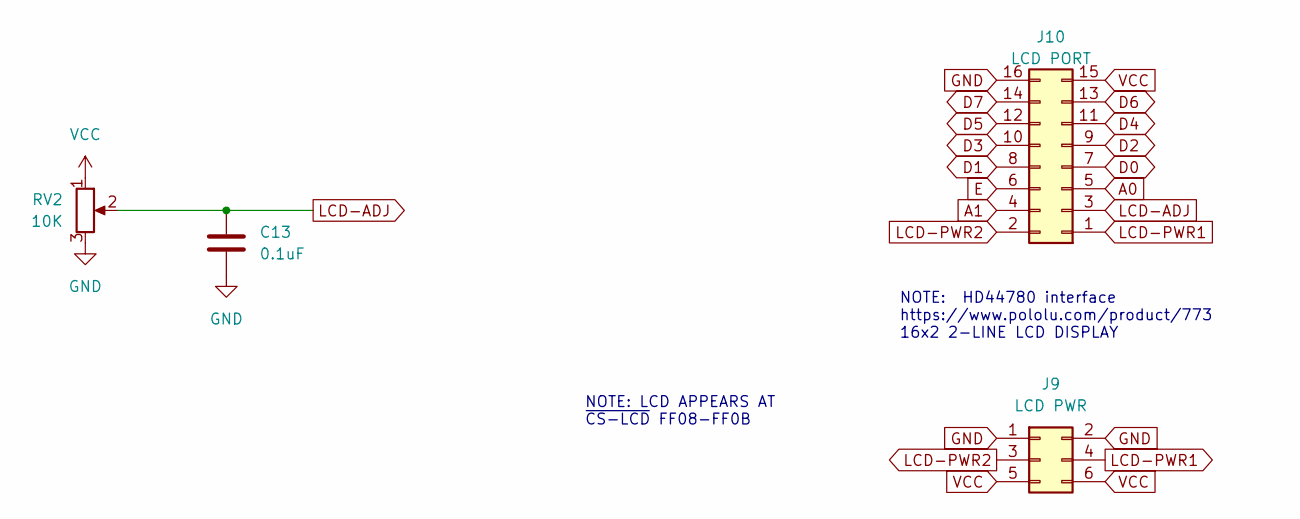
[picture p417: schematic 16x2-LCD.kicad_sch]

Parts:
C13: 0.1uF; C_Disc_D5.0mm_W2.5mm_P5.00mm
J9: LCD PWR; PinHeader_2x03_P2.54mm_Vertical
J10: LCD PORT; PinHeader_2x08_P2.54mm_Vertical
RV2: 10K; Potentiometer_Bourns_3386P_Vertical

Connections:
A0: J10.5; also elsewhere on the board
A1: J10.4; also elsewhere on the board
D0: J10.7; also elsewhere on the board
D1: J10.8; also elsewhere on the board
D2: J10.9; also elsewhere on the board
D3: J10.10; also elsewhere on the board
D4: J10.11; also elsewhere on the board
D5: J10.12; also elsewhere on the board
D6: J10.13; also elsewhere on the board
D7: J10.14; also elsewhere on the board
E: J10.6; also elsewhere on the board
GND: C13.2, J9.1, J9.2, J10.16, RV2.3; also elsewhere on the board
LCD-ADJ: C13.1, J10.3, RV2.2
LCD-PWR1: J9.4, J10.1
LCD-PWR2: J9.3, J10.2
VCC: J9.5, J9.6, J10.15, RV2.1; also elsewhere on the board

Notes on the sheet:
NOTE: LCD APPEARS AT ~{CS-LCD} FF08-FF0B
NOTE: HD44780 interface https://www.pololu.com/product/773 16x2 2-LINE LCD DISPLAY

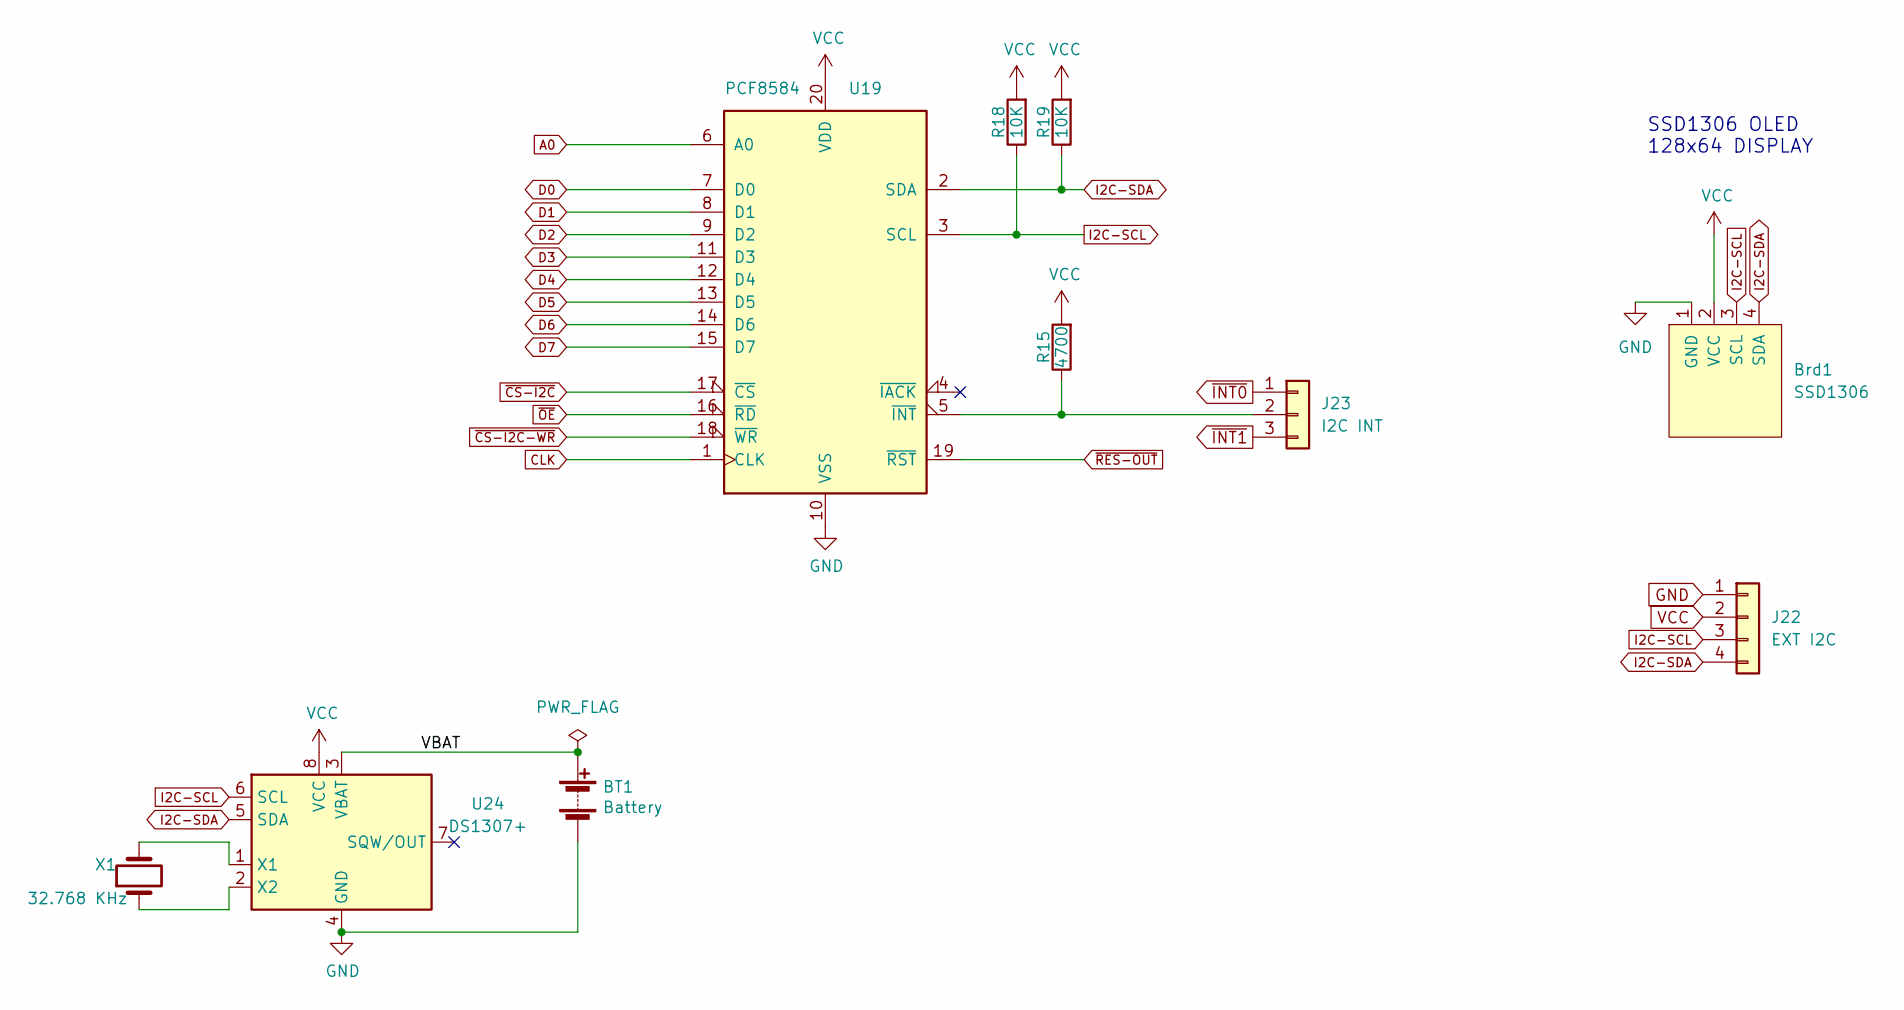
[picture p418: schematic I2C.kicad_sch]

Parts:
BT1: Battery; BatteryHolder_Keystone_103_1x20mm
Brd1: SSD1306; 128x64OLED
J22: EXT I2C; PinHeader_1x04_P2.54mm_Vertical
J23: I2C INT; PinHeader_1x03_P2.54mm_Vertical
R15: 4700; R_Axial_DIN0207_L6.3mm_D2.5mm_P7.62mm_Horizontal
R18, R19: 10K; R_Axial_DIN0207_L6.3mm_D2.5mm_P7.62mm_Horizontal
U19: PCF8584; DIP-20_W7.62mm_Socket
U24: DS1307+; DIP-8_W7.62mm_Socket
X1: 32.768 KHz; Crystal_AT310_D3.0mm_L10.0mm_Horizontal

Connections:
/I2C/VBAT: BT1.1 (+), U24.3 (VBAT)
A0: U19.6 (A0); also elsewhere on the board
CLK: U19.1 (CLK); also elsewhere on the board
D0: U19.7 (D0); also elsewhere on the board
D1: U19.8 (D1); also elsewhere on the board
D2: U19.9 (D2); also elsewhere on the board
D3: U19.11 (D3); also elsewhere on the board
D4: U19.12 (D4); also elsewhere on the board
D5: U19.13 (D5); also elsewhere on the board
D6: U19.14 (D6); also elsewhere on the board
D7: U19.15 (D7); also elsewhere on the board
GND: BT1.2 (-), Brd1.1 (GND), J22.1, U19.10 (VSS), U24.4 (GND); also elsewhere on the board
I2C-SCL: Brd1.3 (SCL), J22.3, R18.1, U19.3 (SCL), U24.6 (SCL); also elsewhere on the board
I2C-SDA: Brd1.4 (SDA), J22.4, R19.1, U19.2 (SDA), U24.5 (SDA); also elsewhere on the board
unnamed: J23.2, R15.1, U19.5 (~INT)
unnamed: U24.1 (X1), X1.2
unnamed: U24.2 (X2), X1.1
VCC: Brd1.2 (VCC), J22.2, R15.2, R18.2, R19.2, U19.20 (VDD), U24.8 (VCC); also elsewhere on the board
~CS-I2C-WR: U19.18 (~WR); also elsewhere on the board
~CS-I2C: U19.17 (~CS); also elsewhere on the board
~INT0: J23.1; also elsewhere on the board
~INT1: J23.3; also elsewhere on the board
~OE: U19.16 (~RD); also elsewhere on the board
~RES-OUT: U19.19 (~RST); also elsewhere on the board

Notes on the sheet:
SSD1306 OLED 128x64 DISPLAY

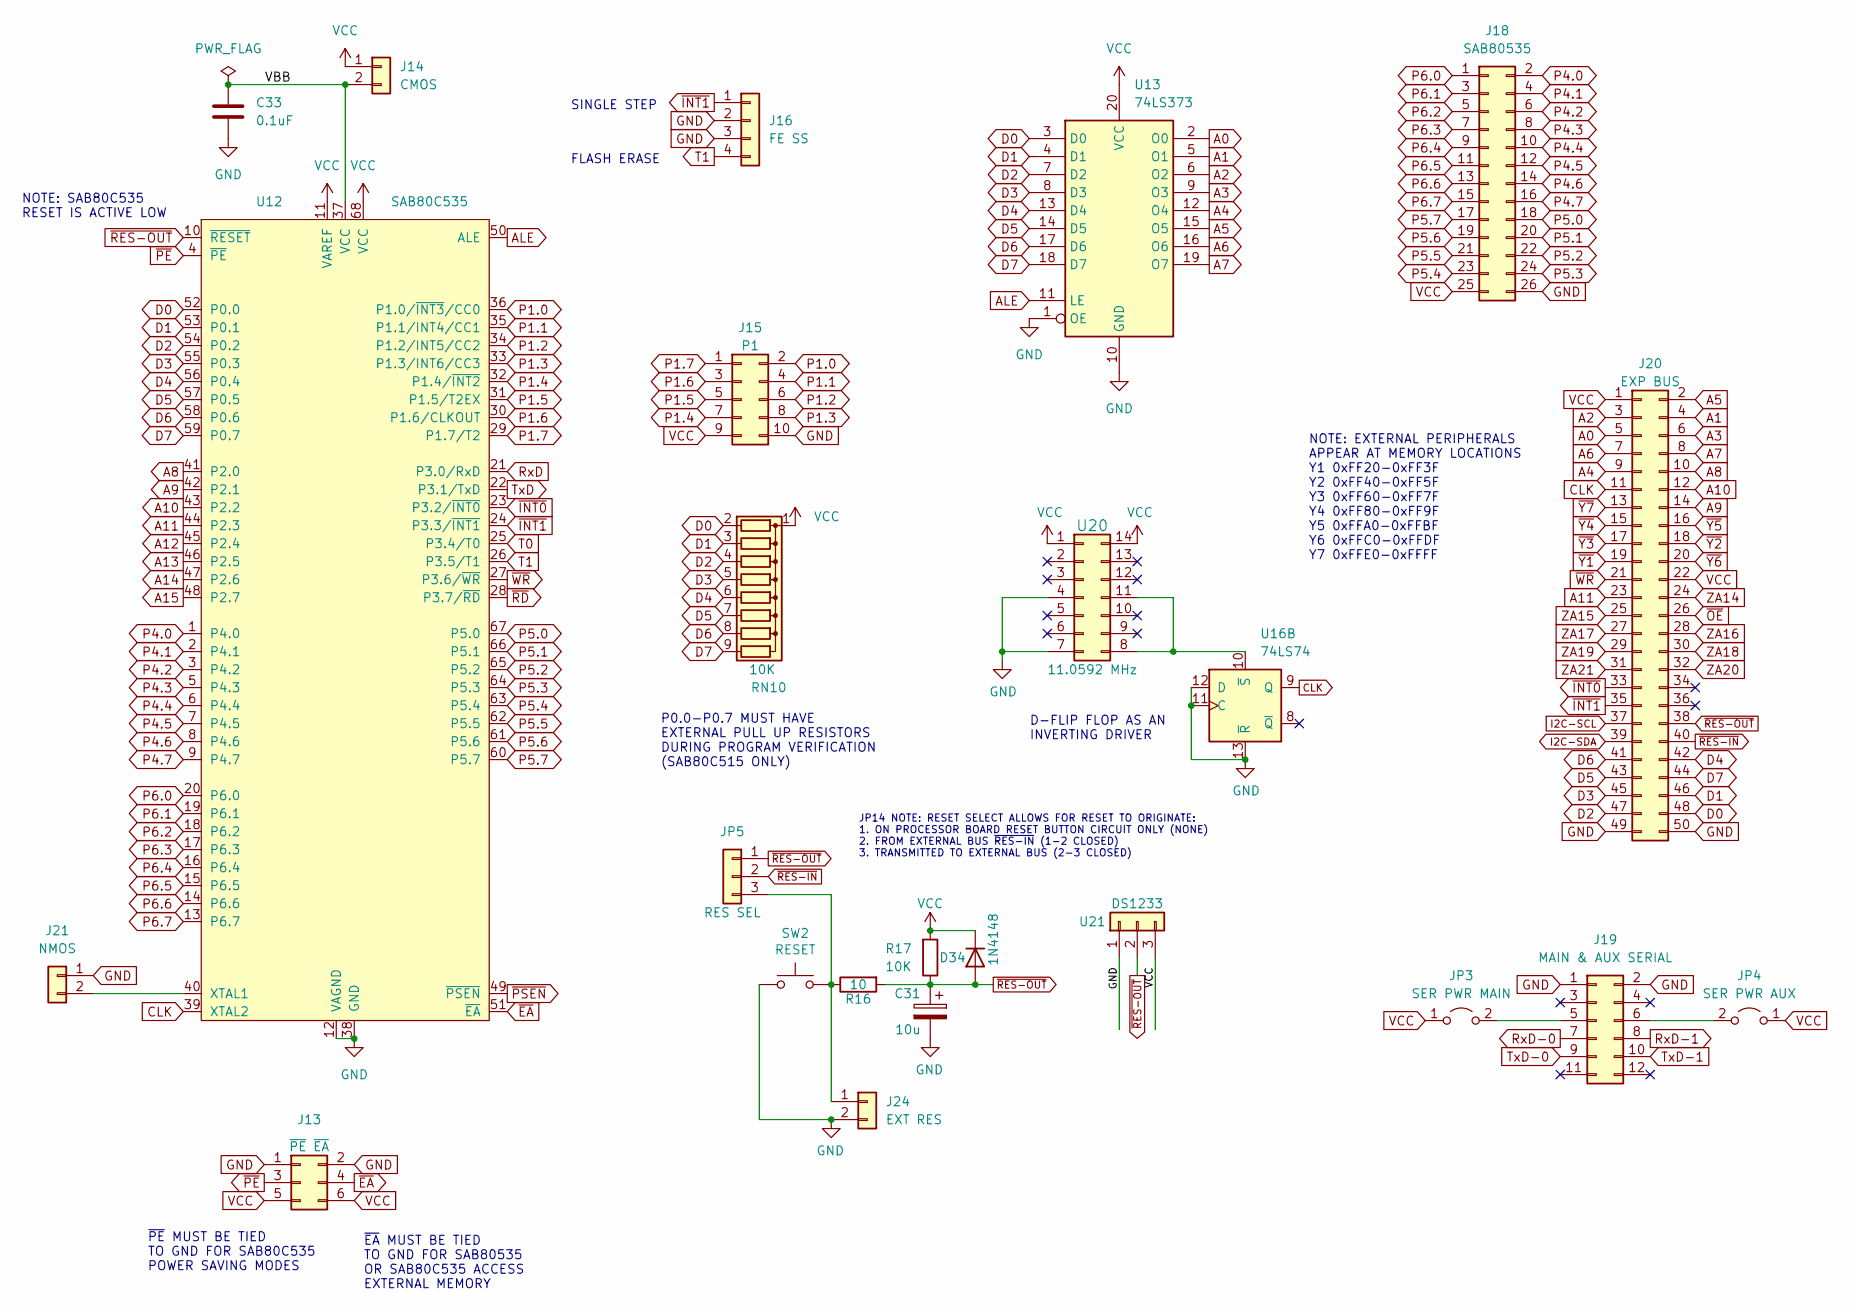
[picture p419: schematic SAB80535.kicad_sch]

Parts:
C31: 10u; CP_Radial_D5.0mm_P2.50mm
C33: 0.1uF; C_Disc_D5.0mm_W2.5mm_P5.00mm
D34: 1N4148; D_DO-35_SOD27_P7.62mm_Horizontal
J13: ~{PE} ~{EA}; PinHeader_2x03_P2.54mm_Vertical
J14: CMOS; PinHeader_1x02_P2.54mm_Vertical
J15: P1; IDC-Header_2x05_P2.54mm_Horizontal
J16: FE SS; PinHeader_1x04_P2.54mm_Vertical
J18: SAB80535; IDC-Header_2x13_P2.54mm_Horizontal
J19: MAIN & AUX SERIAL; IDC-Header_2x06_P2.54mm_Horizontal
J20: EXP BUS; IDC-Header_2x25_P2.54mm_Horizontal
J21: NMOS; PinHeader_1x02_P2.54mm_Vertical
J24: EXT RES; PinHeader_1x02_P2.54mm_Vertical
JP3: SER PWR MAIN; PinHeader_1x02_P2.54mm_Vertical
JP4: SER PWR AUX; PinHeader_1x02_P2.54mm_Vertical
JP5: RES SEL; PinHeader_1x03_P2.54mm_Vertical
R16: 10; R_Axial_DIN0207_L6.3mm_D2.5mm_P7.62mm_Horizontal
R17: 10K; R_Axial_DIN0207_L6.3mm_D2.5mm_P7.62mm_Horizontal
RN10: 10K; R_Array_SIP9
SW2: RESET; SW_PUSH_6mm
U12: SAB80C535; PLCC-68_THT-Socket
U13: 74LS373; DIP-20_W7.62mm_Socket
U16: 74LS74; DIP-14_W7.62mm_Socket
U20: 11.0592 MHz; DIP-14_W7.62mm_Socket
U21: DS1233; TO-92L_HandSolder

Connections:
/SAB80535/VBB: C33.1, J14.2, U12.37 (VCC)
A0: J20.5, U13.2 (O0); also elsewhere on the board
A1: J20.4, U13.5 (O1); also elsewhere on the board
A2: J20.3, U13.6 (O2); also elsewhere on the board
A3: J20.6, U13.9 (O3); also elsewhere on the board
A4: J20.9, U13.12 (O4); also elsewhere on the board
A5: J20.2, U13.15 (O5); also elsewhere on the board
A6: J20.7, U13.16 (O6); also elsewhere on the board
A7: J20.8, U13.19 (O7); also elsewhere on the board
A8: J20.10, U12.41 (P2.0); also elsewhere on the board
A9: J20.14, U12.42 (P2.1); also elsewhere on the board
A10: J20.12, U12.43 (P2.2); also elsewhere on the board
A11: J20.23, U12.44 (P2.3); also elsewhere on the board
A12: U12.45 (P2.4); also elsewhere on the board
A13: U12.46 (P2.5); also elsewhere on the board
A14: U12.47 (P2.6); also elsewhere on the board
A15: U12.48 (P2.7); also elsewhere on the board
ALE: U12.50 (ALE), U13.11 (LE); also elsewhere on the board
CLK: J20.11, U12.39 (XTAL2), U16.9 (Q); also elsewhere on the board
D0: J20.48, RN10.2 (R1), U12.52 (P0.0), U13.3 (D0); also elsewhere on the board
D1: J20.46, RN10.3 (R2), U12.53 (P0.1), U13.4 (D1); also elsewhere on the board
D2: J20.47, RN10.4 (R3), U12.54 (P0.2), U13.7 (D2); also elsewhere on the board
D3: J20.45, RN10.5 (R4), U12.55 (P0.3), U13.8 (D3); also elsewhere on the board
D4: J20.42, RN10.6 (R5), U12.56 (P0.4), U13.13 (D4); also elsewhere on the board
D5: J20.43, RN10.7 (R6), U12.57 (P0.5), U13.14 (D5); also elsewhere on the board
D6: J20.41, RN10.8 (R7), U12.58 (P0.6), U13.17 (D6); also elsewhere on the board
D7: J20.44, RN10.9 (R8), U12.59 (P0.7), U13.18 (D7); also elsewhere on the board
GND: C31.2, C33.2, J13.1, J13.2, J15.10, J16.2, J16.3, J18.26, J19.1, J19.2, J20.49, J20.50, J21.1, J24.2, SW2.2, U12.12 (VAGND), U12.38 (GND), U13.1 (OE), U13.10 (GND), U16.11 (C), U16.12 (D), U16.13 (~R), U20.4, U20.7, U21.1; also elsewhere on the board
I2C-SCL: J20.37; also elsewhere on the board
I2C-SDA: J20.39; also elsewhere on the board
unnamed: J19.5, JP3.2 (B)
unnamed: J19.6, JP4.2 (B)
unnamed: J21.2, U12.40 (XTAL1)
unnamed: J24.1, JP5.3, R16.1, SW2.1
unnamed: U16.10 (~S), U20.8, U20.11
P1.0: J15.2, U12.36 (P1.0/~INT3/CC0); also elsewhere on the board
P1.1: J15.4, U12.35 (P1.1/INT4/CC1); also elsewhere on the board
P1.2: J15.6, U12.34 (P1.2/INT5/CC2); also elsewhere on the board
P1.3: J15.8, U12.33 (P1.3/INT6/CC3); also elsewhere on the board
P1.4: J15.7, U12.32 (P1.4/~INT2); also elsewhere on the board
P1.5: J15.5, U12.31 (P1.5/T2EX); also elsewhere on the board
P1.6: J15.3, U12.30 (P1.6/CLKOUT); also elsewhere on the board
P1.7: J15.1, U12.29 (P1.7/T2); also elsewhere on the board
P4.0: J18.2, U12.1 (P4.0); also elsewhere on the board
P4.1: J18.4, U12.2 (P4.1); also elsewhere on the board
P4.2: J18.6, U12.3 (P4.2); also elsewhere on the board
P4.3: J18.8, U12.5 (P4.3); also elsewhere on the board
P4.4: J18.10, U12.6 (P4.4); also elsewhere on the board
P4.5: J18.12, U12.7 (P4.5); also elsewhere on the board
P4.6: J18.14, U12.8 (P4.6); also elsewhere on the board
P4.7: J18.16, U12.9 (P4.7); also elsewhere on the board
P5.0: J18.18, U12.67 (P5.0); also elsewhere on the board
P5.1: J18.20, U12.66 (P5.1); also elsewhere on the board
P5.2: J18.22, U12.65 (P5.2); also elsewhere on the board
P5.3: J18.24, U12.64 (P5.3); also elsewhere on the board
P5.4: J18.23, U12.63 (P5.4); also elsewhere on the board
P5.5: J18.21, U12.62 (P5.5); also elsewhere on the board
P5.6: J18.19, U12.61 (P5.6); also elsewhere on the board
P5.7: J18.17, U12.60 (P5.7); also elsewhere on the board
P6.0: J18.1, U12.20 (P6.0)
P6.1: J18.3, U12.19 (P6.1)
P6.2: J18.5, U12.18 (P6.2)
P6.3: J18.7, U12.17 (P6.3)
P6.4: J18.9, U12.16 (P6.4)
P6.5: J18.11, U12.15 (P6.5)
P6.6: J18.13, U12.14 (P6.6)
P6.7: J18.15, U12.13 (P6.7)
RxD: U12.21 (P3.0/RxD); also elsewhere on the board
RxD-0: J19.7; also elsewhere on the board
RxD-1: J19.8; also elsewhere on the board
T0: U12.25 (P3.4/T0); also elsewhere on the board
T1: J16.4, U12.26 (P3.5/T1); also elsewhere on the board
TxD: U12.22 (P3.1/TxD); also elsewhere on the board
TxD-0: J19.9; also elsewhere on the board
TxD-1: J19.10; also elsewhere on the board
VCC: D34.1 (K), J13.5, J13.6, J14.1, J15.9, J18.25, J20.1, J20.22, JP3.1 (A), JP4.1 (A), R17.2, RN10.1 (common), U12.11 (VAREF), U12.68 (VCC), U13.20 (VCC), U20.1, U20.14, U21.3; also elsewhere on the board
ZA14: J20.24; also elsewhere on the board
ZA15: J20.25; also elsewhere on the board
ZA16: J20.28; also elsewhere on the board
ZA17: J20.27; also elsewhere on the board
ZA18: J20.30; also elsewhere on the board
ZA19: J20.29; also elsewhere on the board
ZA20: J20.32; also elsewhere on the board
ZA21: J20.31; also elsewhere on the board
~EA: J13.4, U12.51 (~EA)
~INT0: J20.33, U12.23 (P3.2/~INT0); also elsewhere on the board
~INT1: J16.1, J20.35, U12.24 (P3.3/~INT1); also elsewhere on the board
~OE: J20.26; also elsewhere on the board
~PE: J13.3, U12.4 (~PE)
~PSEN: U12.49 (~PSEN); also elsewhere on the board
~RD: U12.28 (P3.7/~RD); also elsewhere on the board
~RES-IN: J20.40, JP5.2
~RES-OUT: C31.1, D34.2 (A), J20.38, JP5.1, R16.2, R17.1, U12.10 (~RESET), U21.2; also elsewhere on the board
~WR: J20.21, U12.27 (P3.6/~WR); also elsewhere on the board
~Y1: J20.19; also elsewhere on the board
~Y2: J20.18; also elsewhere on the board
~Y7: J20.13; also elsewhere on the board

Notes on the sheet:
NOTE: SAB80C535 RESET IS ACTIVE LOW
NOTE: EXTERNAL PERIPHERALS APPEAR AT MEMORY LOCATIONS Y1 0xFF20-0xFF3F Y2 0xFF40-0xFF5F Y3 0xFF60-0xFF7F Y4 0xFF80-0xFF9F Y5 0xFFA0-0xFFBF Y6 0xFFC0-0xFFDF Y7 0xFFE0-0xFFFF
D-FLIP FLOP AS AN INVERTING DRIVER
JP14 NOTE: RESET SELECT ALLOWS FOR RESET TO ORIGINATE: 1. ON PROCESSOR BOARD RESET BUTTON CIRCUIT ONLY (NONE) 2. FROM EXTERNAL BUS ~{RES-IN} (1-2 CLOSED) 3. TRANSMITTED TO EXTERNAL BUS (2-3 CLOSED)
SINGLE STEP
~{EA} MUST BE TIED TO GND FOR SAB80535 OR SAB80C535 ACCESS EXTERNAL MEMORY
FLASH ERASE
~{PE} MUST BE TIED TO GND FOR SAB80C535 POWER SAVING MODES
P0.0-P0.7 MUST HAVE EXTERNAL PULL UP RESISTORS DURING PROGRAM VERIFICATION (SAB80C515 ONLY)

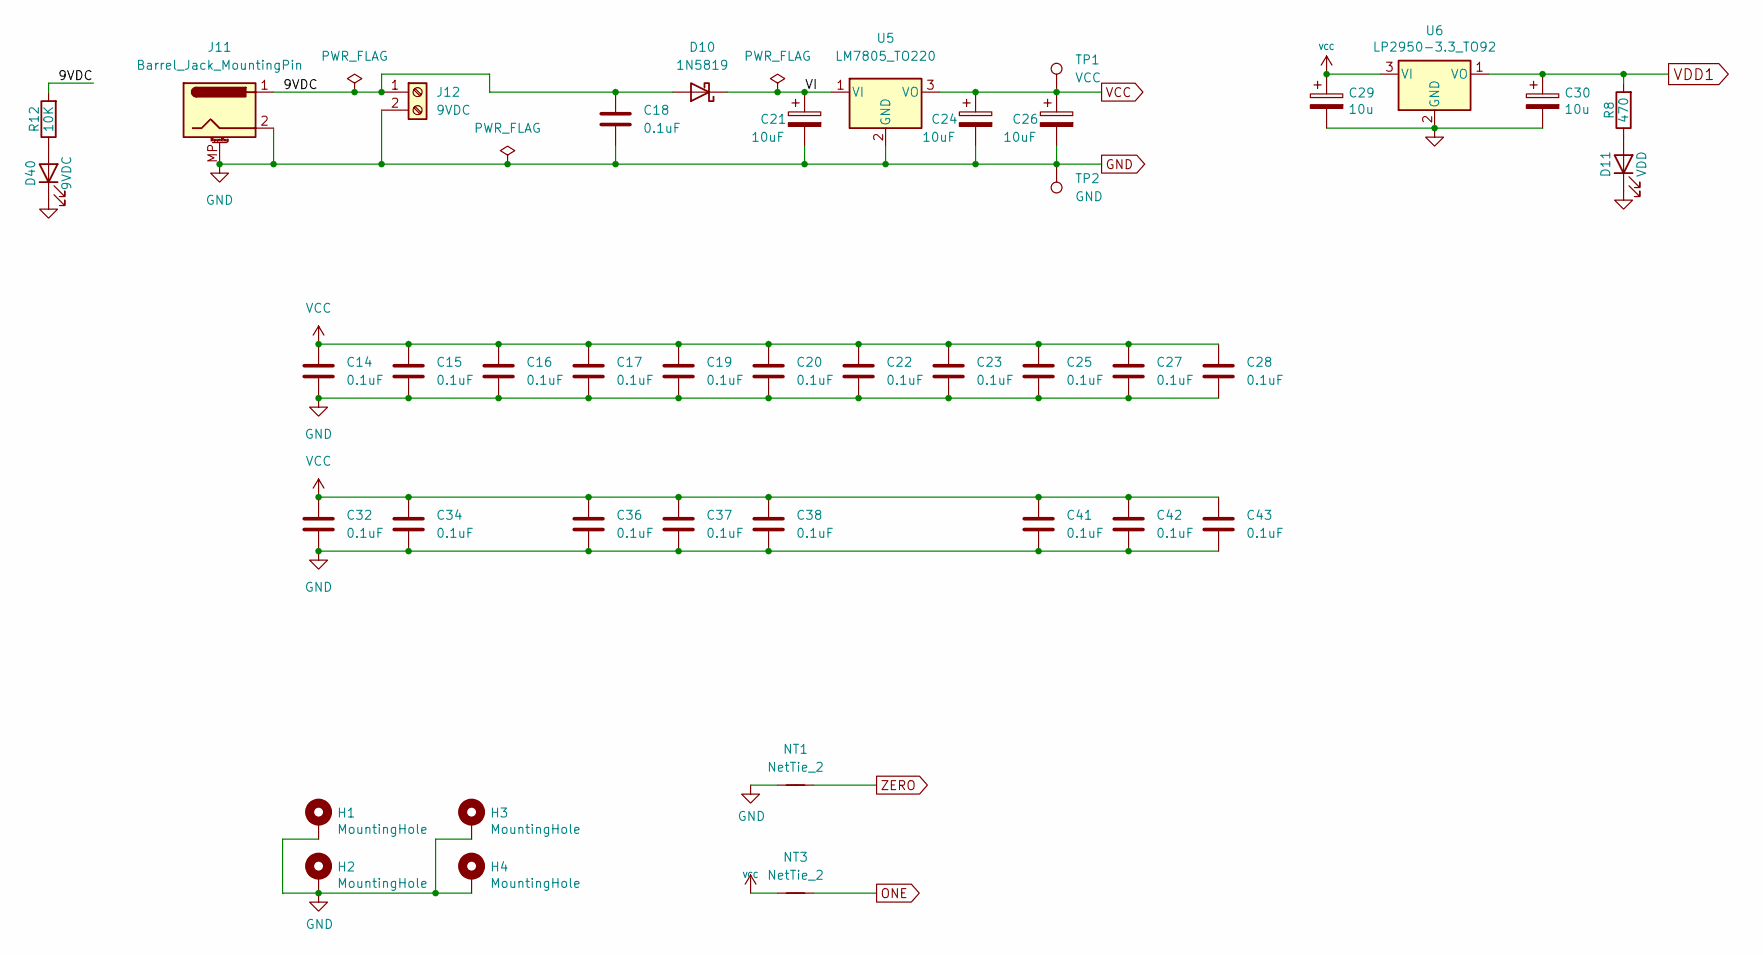
[picture p420: schematic Power.kicad_sch]

Parts:
C14, C15, C16, C17, C18, C19, C20, C22, C23, C25, C27, C28, C32, C34, C36, C37, C38, C41, C42, C43: 0.1uF; C_Disc_D5.0mm_W2.5mm_P5.00mm
C21, C24, C26: 10uF; CP_Radial_D5.0mm_P2.50mm
C29, C30: 10u; CP_Radial_D5.0mm_P2.50mm
D10: 1N5819; D_DO-41_SOD81_P10.16mm_Horizontal
D11: VDD; LED_D3.0mm
D40: 9VDC; LED_D3.0mm
H1, H2, H3, H4: MountingHole; MountingHole_3.2mm_M3_Pad
J11: Barrel_Jack_MountingPin; BarrelJack_Horizontal
J12: 9VDC; TerminalBlock_Phoenix_MKDS-1,5-2-5.08_1x02_P5.08mm_Horizont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
NT1, NT3: NetTie_2; NetTie-2_THT_Pad0.3mm
R8: 470; R_Axial_DIN0207_L6.3mm_D2.5mm_P7.62mm_Horizontal
R12: 10K; R_Axial_DIN0207_L6.3mm_D2.5mm_P7.62mm_Horizontal
TP1: VCC; PinHeader_1x01_P2.54mm_Vertical
TP2: GND; PinHeader_1x01_P2.54mm_Vertical
U5: LM7805_TO220; TO-220-3_Horizontal_TabDown
U6: LP2950-3.3_TO92; TO-92_HandSolder

Connections:
/Power/9VDC: C18.1, D10.2 (A), J11.1, J12.1, R12.2
/Power/VI: C21.1, D10.1 (K), U5.1 (VI)
GND: C14.2, C15.2, C16.2, C17.2, C18.2, C19.2, C20.2, C21.2, C22.2, C23.2, C24.2, C25.2, C26.2, C27.2, C28.2, C29.2, C30.2, C32.2, C34.2, C36.2, C37.2, C38.2, C41.2, C42.2, C43.2, D11.1 (K), D40.1 (K), H1.1, H2.1, H3.1, H4.1, J11.2, J11.MP (MountPin), J12.2, NT1.1, TP2.1, U5.2 (GND), U6.2 (GND); also elsewhere on the board
unnamed: D11.2 (A), R8.1
unnamed: D40.2 (A), R12.1
ONE: NT3.2; also elsewhere on the board
VCC: C14.1, C15.1, C16.1, C17.1, C19.1, C20.1, C22.1, C23.1, C24.1, C25.1, C26.1, C27.1, C28.1, C29.1, C32.1, C34.1, C36.1, C37.1, C38.1, C41.1, C42.1, C43.1, NT3.1, TP1.1, U5.3 (VO), U6.3 (VI); also elsewhere on the board
VDD1: C30.1, R8.2, U6.1 (VO); also elsewhere on the board
ZERO: NT1.2; also elsewhere on the board

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
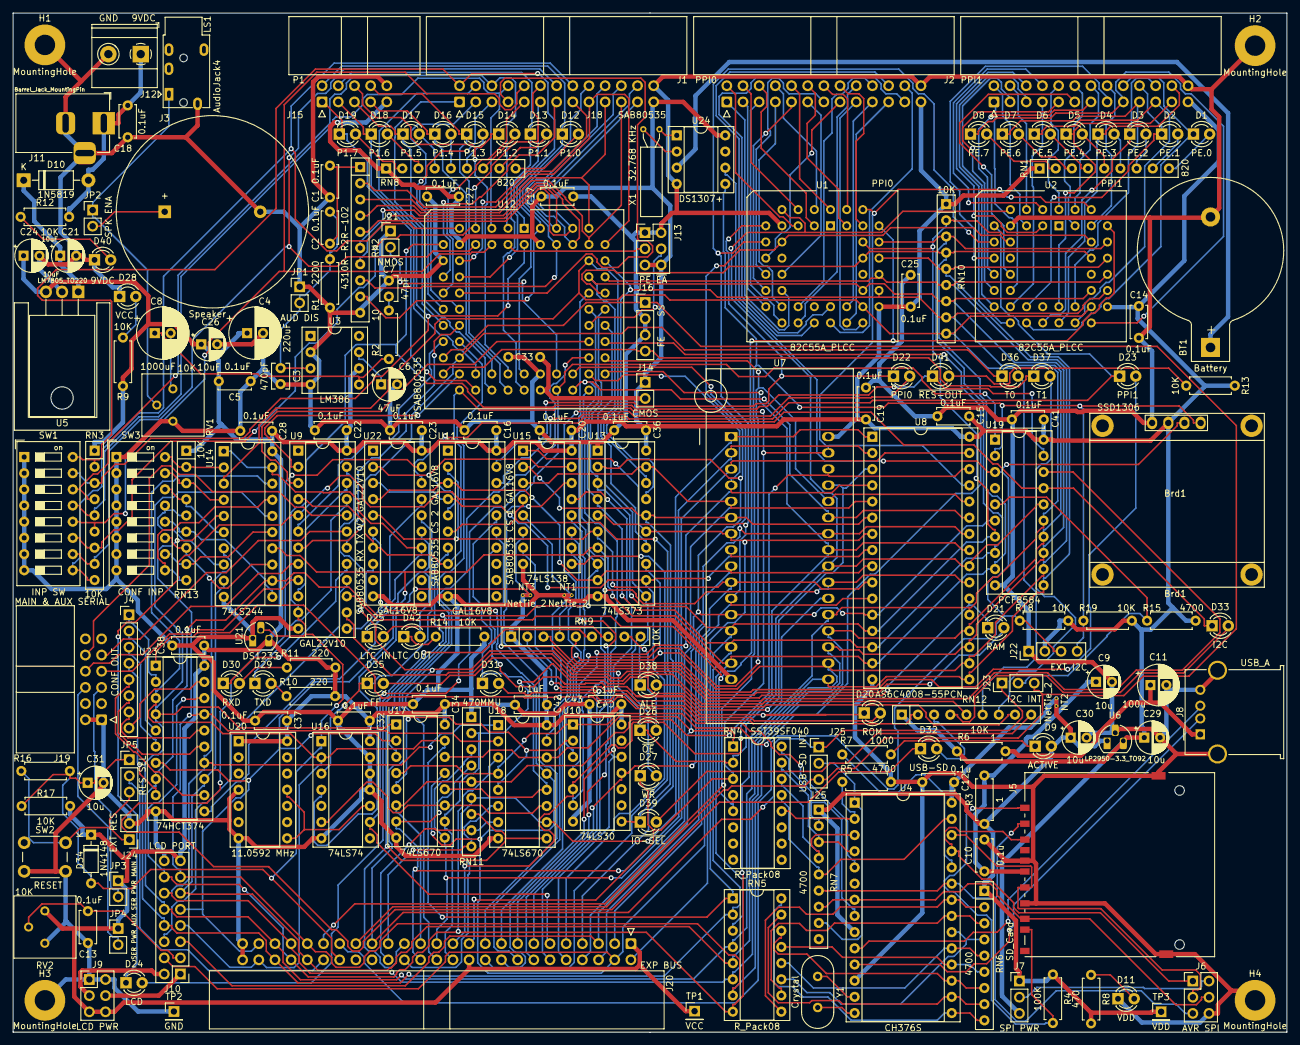
[picture p421: board SAB80535-Dev-Board.kicad_pcb from above]

Board: 2 copper layers, 200.0 x 160.0 mm, 187 parts (1 on the bottom side), 274 nets.
