lynchaj/duodyne/!Retired/04 memory.ROMRAM.8-bit, V1.0/memory.ROMRAM.kicad_pcb

## KiCad design !Retired/04 memory.ROMRAM.8-bit, V1.0/memory.ROMRAM.kicad_pcb (2023-05-28, an earlier design)

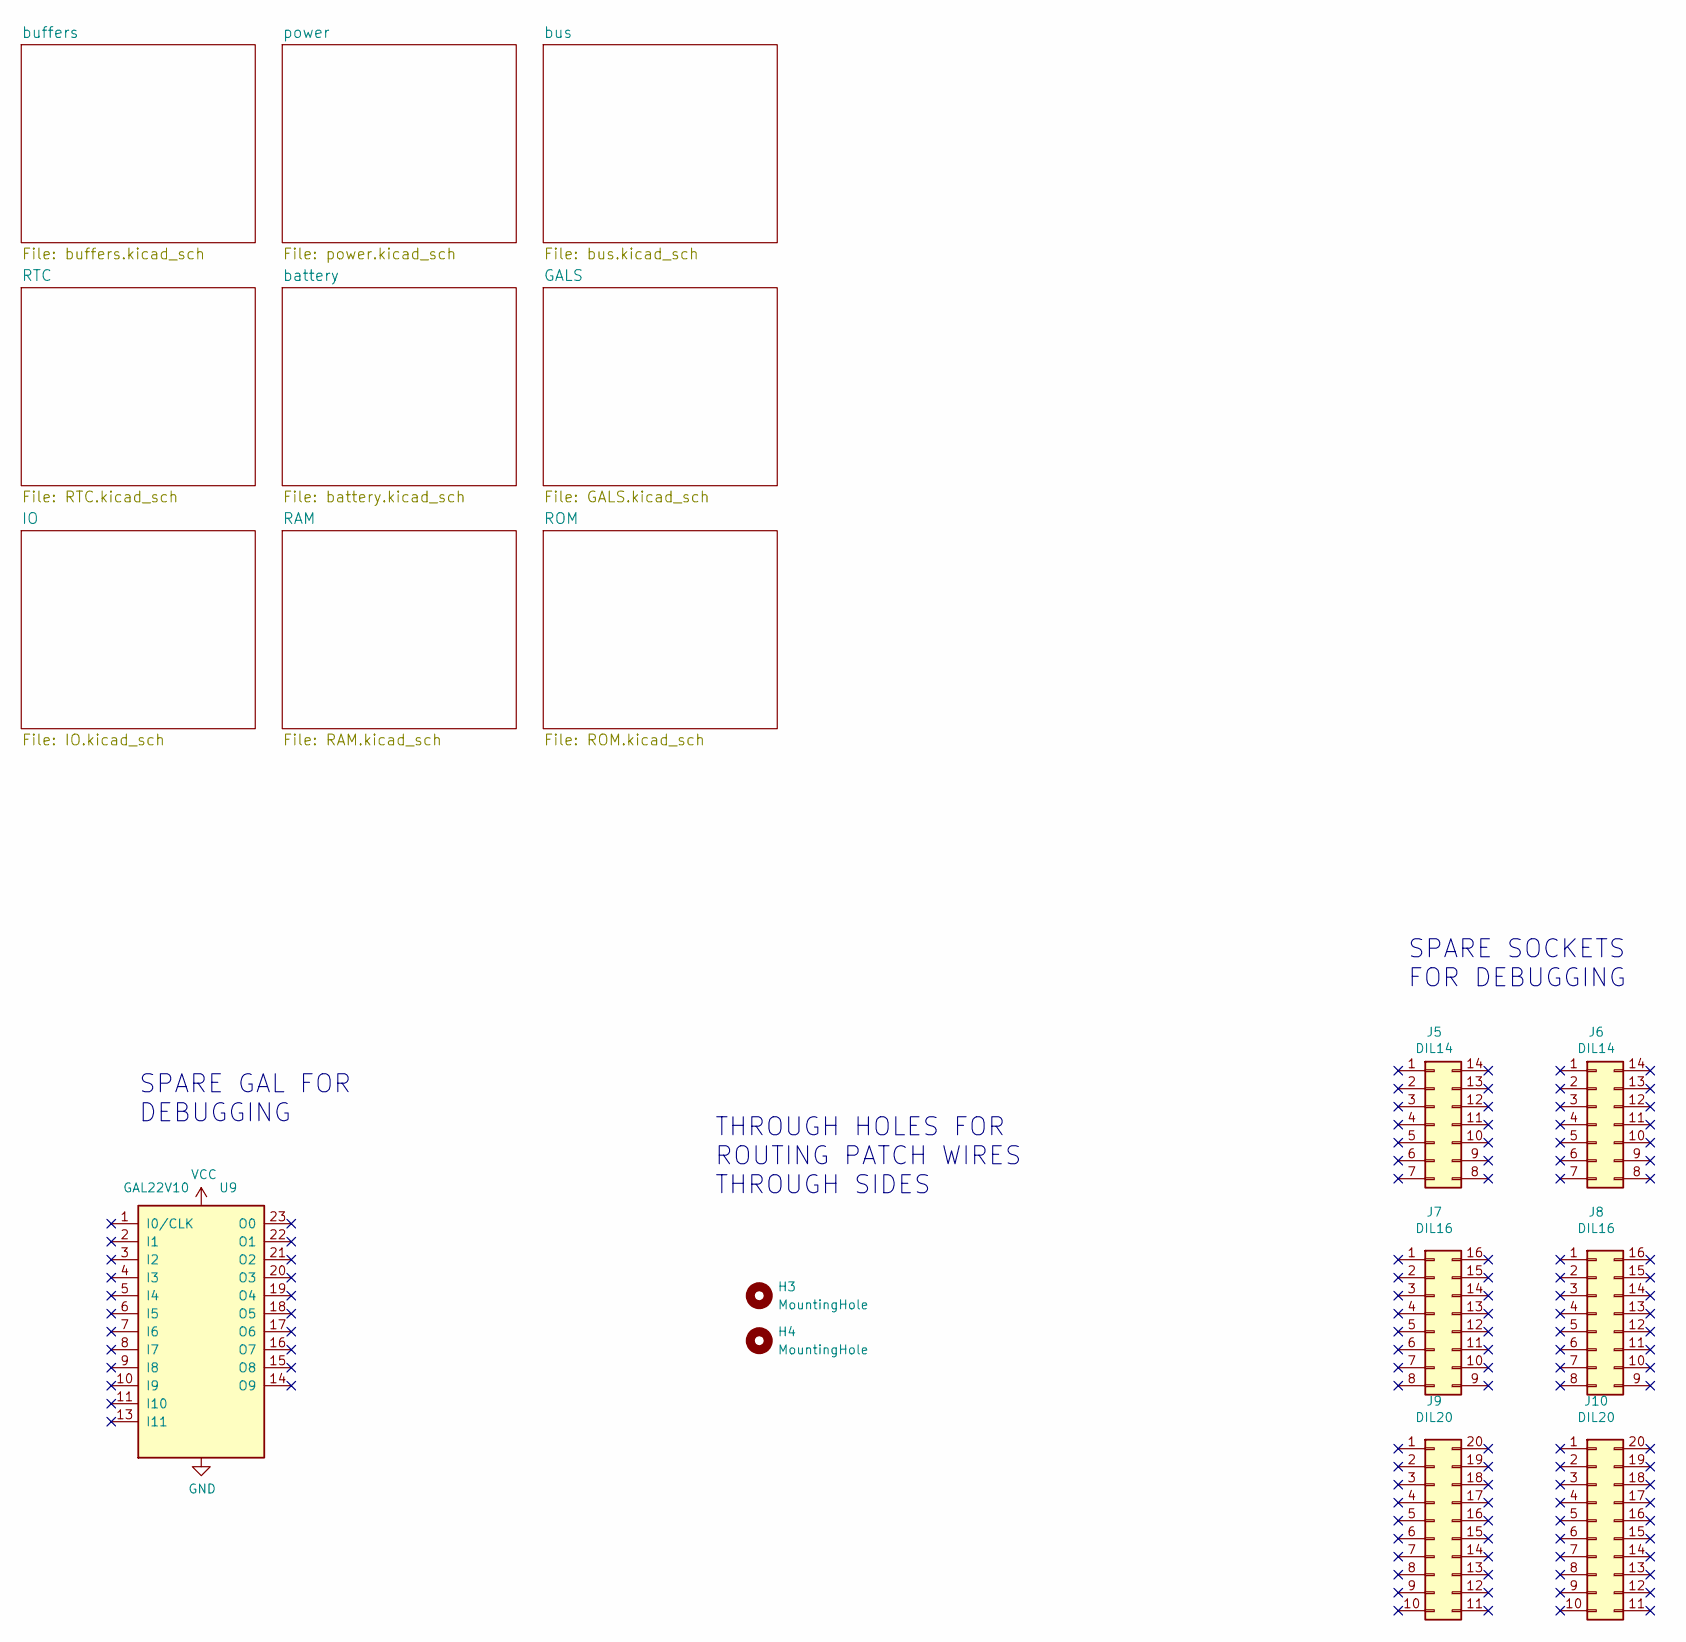
[picture p422: schematic memory.ROMRAM.kicad_sch]

Parts:
H3, H4: MountingHole; MountingHole_2.2mm_M2_DIN965_Pad
J5, J6: DIL14; DIP-14_W7.62mm
J7, J8: DIL16; DIP-16_W7.62mm
J9, J10: DIL20; DIP-20_W7.62mm
U9: GAL22V10; DIP-24_W7.62mm

Connections:
GND: U9.12 (GND); also elsewhere on the board
VCC: U9.24 (VCC); also elsewhere on the board

Notes on the sheet:
SPARE SOCKETS FOR DEBUGGING
SPARE GAL FOR DEBUGGING
THROUGH HOLES FOR ROUTING PATCH WIRES THROUGH SIDES
