lynchaj/duodyne/!Retired/04 memory.ROMRAM.8-bit, V1.0/memory.ROMRAM.kicad_pcb

## KiCad design !Retired/04 memory.ROMRAM.8-bit, V1.0/memory.ROMRAM.kicad_pcb (continued)

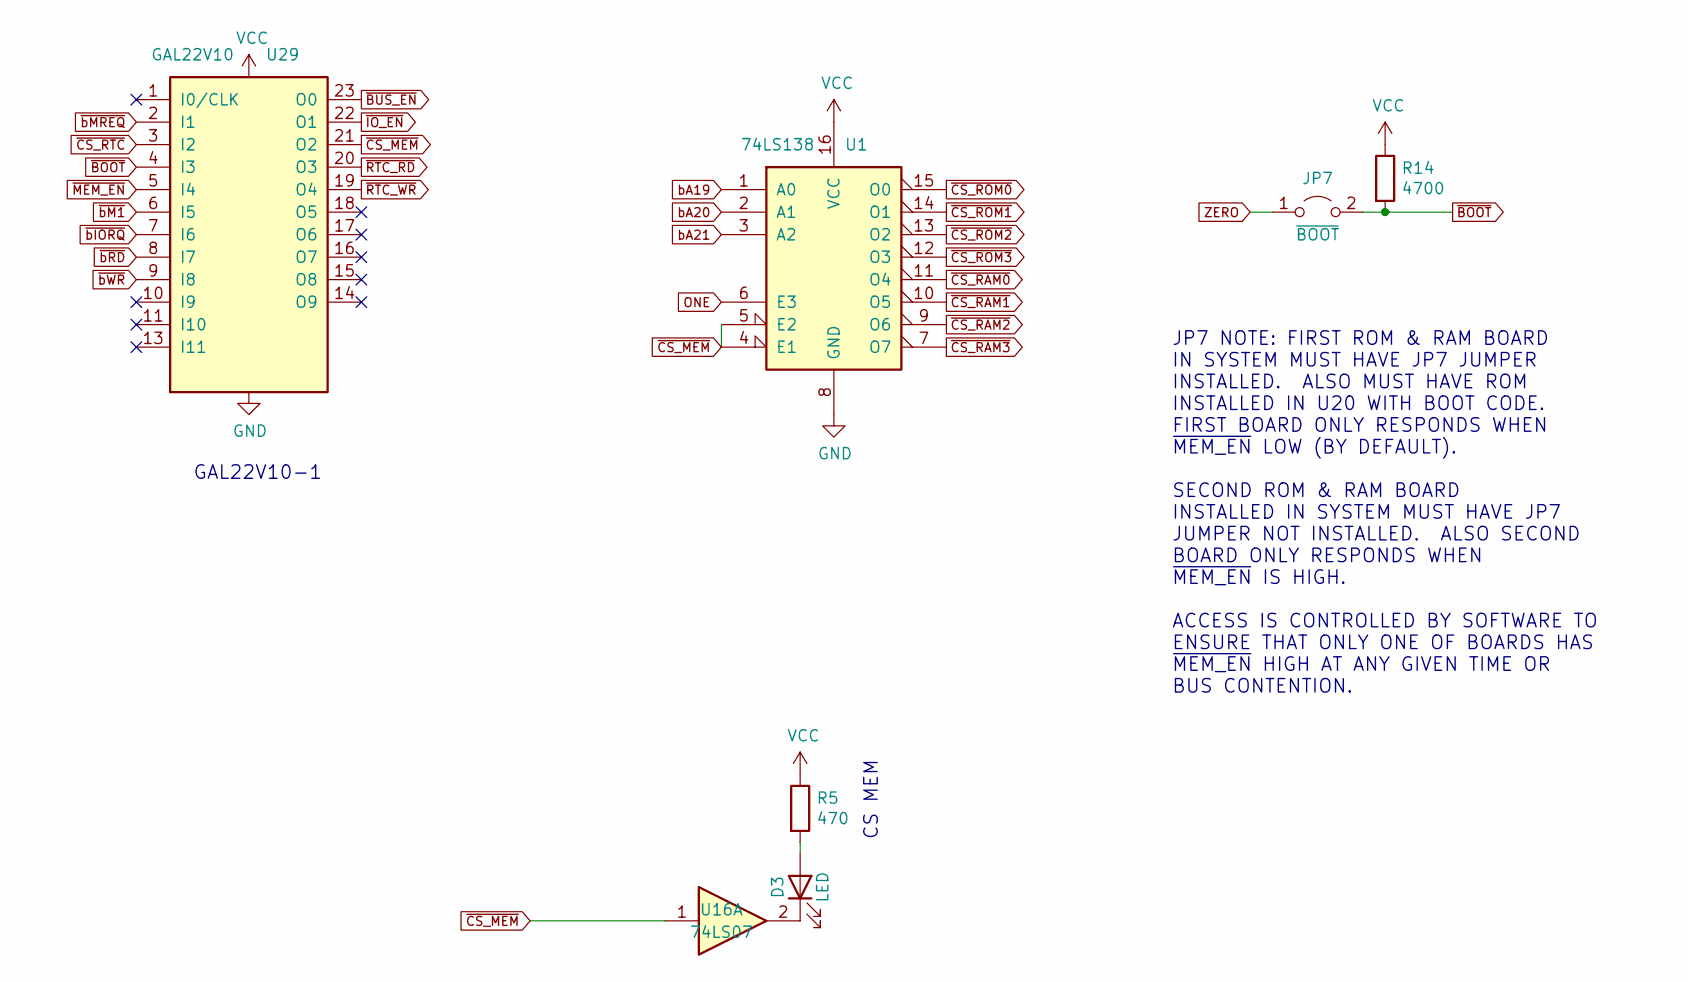
[picture p423: schematic GALS.kicad_sch]

Parts:
D3: LED; LED_D3.0mm_Horizontal_O3.81mm_Z2.0mm
JP7: ~{BOOT}; PinHeader_1x02_P2.54mm_Horizontal
R5: 470; R_Axial_DIN0207_L6.3mm_D2.5mm_P7.62mm_Horizontal
R14: 4700; R_Axial_DIN0207_L6.3mm_D2.5mm_P7.62mm_Horizontal
U1: 74LS138; DIP-16_W7.62mm
U16: 74LS07; DIP-14_W7.62mm
U29: GAL22V10; DIP-24_W7.62mm

Connections:
GND: U1.8 (GND), U29.12 (GND); also elsewhere on the board
unnamed: D3.1 (K), U16.2
unnamed: D3.2 (A), R5.2
ONE: U1.6 (E3); also elsewhere on the board
VCC: R5.1, R14.1, U1.16 (VCC), U29.24 (VCC); also elsewhere on the board
ZERO: JP7.1 (A); also elsewhere on the board
bA19: U1.1 (A0); also elsewhere on the board
bA20: U1.2 (A1); also elsewhere on the board
bA21: U1.3 (A2); also elsewhere on the board
~BOOT: JP7.2 (B), R14.2, U29.4 (I3)
~BUS_EN: U29.23 (O0); also elsewhere on the board
~CS_MEM: U1.4 (E1), U1.5 (E2), U16.1, U29.21 (O2)
~CS_RAM0: U1.11 (O4); also elsewhere on the board
~CS_RAM1: U1.10 (O5); also elsewhere on the board
~CS_RAM2: U1.9 (O6); also elsewhere on the board
~CS_RAM3: U1.7 (O7); also elsewhere on the board
~CS_ROM0: U1.15 (O0); also elsewhere on the board
~CS_ROM1: U1.14 (O1); also elsewhere on the board
~CS_ROM2: U1.13 (O2); also elsewhere on the board
~CS_ROM3: U1.12 (O3); also elsewhere on the board
~CS_RTC: U29.3 (I2); also elsewhere on the board
~IO_EN: U29.22 (O1); also elsewhere on the board
~MEM_EN: U29.5 (I4); also elsewhere on the board
~RTC_RD: U29.20 (O3); also elsewhere on the board
~RTC_WR: U29.19 (O4); also elsewhere on the board
~bIORQ: U29.7 (I6); also elsewhere on the board
~bM1: U29.6 (I5); also elsewhere on the board
~bMREQ: U29.2 (I1); also elsewhere on the board
~bRD: U29.8 (I7); also elsewhere on the board
~bWR: U29.9 (I8); also elsewhere on the board

Notes on the sheet:
GAL22V10-1
JP7 NOTE: FIRST ROM & RAM BOARD IN SYSTEM MUST HAVE JP7 JUMPER INSTALLED. ALSO MUST HAVE ROM INSTALLED IN U20 WITH BOOT CODE. FIRST BOARD ONLY RESPONDS WHEN ~{MEM_EN} LOW (BY DEFAULT). SECOND ROM & RAM BOARD INSTALLED IN SYSTEM MUST HAVE JP7 JUMPER NOT INSTALLED. ALSO SECOND BOARD ONLY RESPONDS WHE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
CS MEM

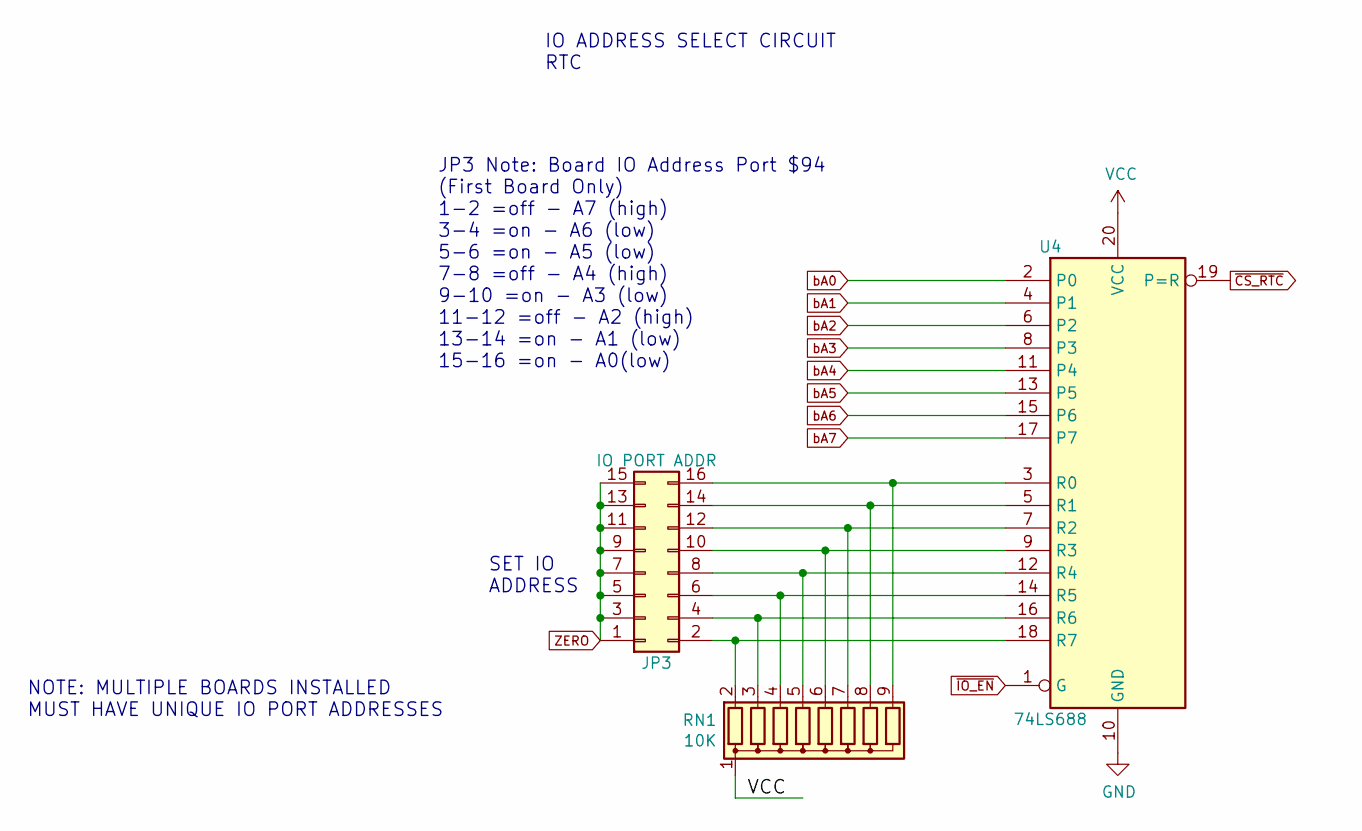
[picture p424: schematic IO.kicad_sch]

Parts:
JP3: IO PORT ADDR; PinHeader_2x08_P2.54mm_Vertical
RN1: 10K; R_Array_SIP9
U4: 74LS688; DIP-20_W7.62mm

Connections:
GND: U4.10 (GND); also elsewhere on the board
unnamed: JP3.2, RN1.2 (R1), U4.18 (R7)
unnamed: JP3.4, RN1.3 (R2), U4.16 (R6)
unnamed: JP3.6, RN1.4 (R3), U4.14 (R5)
unnamed: JP3.8, RN1.5 (R4), U4.12 (R4)
unnamed: JP3.10, RN1.6 (R5), U4.9 (R3)
unnamed: JP3.12, RN1.7 (R6), U4.7 (R2)
unnamed: JP3.14, RN1.8 (R7), U4.5 (R1)
unnamed: JP3.16, RN1.9 (R8), U4.3 (R0)
VCC: RN1.1 (common), U4.20 (VCC); also elsewhere on the board
ZERO: JP3.1, JP3.3, JP3.5, JP3.7, JP3.9, JP3.11, JP3.13, JP3.15; also elsewhere on the board
bA0: U4.2 (P0); also elsewhere on the board
bA1: U4.4 (P1); also elsewhere on the board
bA2: U4.6 (P2); also elsewhere on the board
bA3: U4.8 (P3); also elsewhere on the board
bA4: U4.11 (P4); also elsewhere on the board
bA5: U4.13 (P5); also elsewhere on the board
bA6: U4.15 (P6); also elsewhere on the board
bA7: U4.17 (P7); also elsewhere on the board
~CS_RTC: U4.19 (P=R); also elsewhere on the board
~IO_EN: U4.1 (G); also elsewhere on the board

Notes on the sheet:
JP3 Note: Board IO Address Port $94 (First Board Only) 1-2 =off - A7 (high) 3-4 =on - A6 (low) 5-6 =on - A5 (low) 7-8 =off - A4 (high) 9-10 =on - A3 (low) 11-12 =off - A2 (high) 13-14 =on - A1 (low) 15-16 =on - A0(low)
NOTE: MULTIPLE BOARDS INSTALLED MUST HAVE UNIQUE IO PORT ADDRESSES
IO ADDRESS SELECT CIRCUIT RTC
SET IO ADDRESS

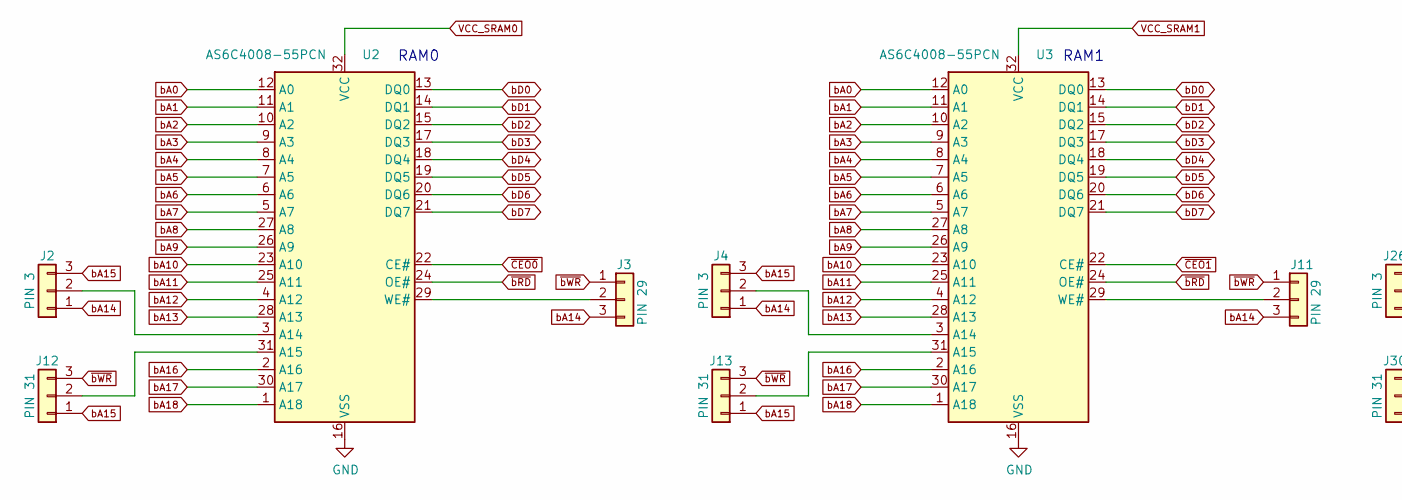
[picture p425: schematic RAM.kicad_sch, part in row 1, column 1]

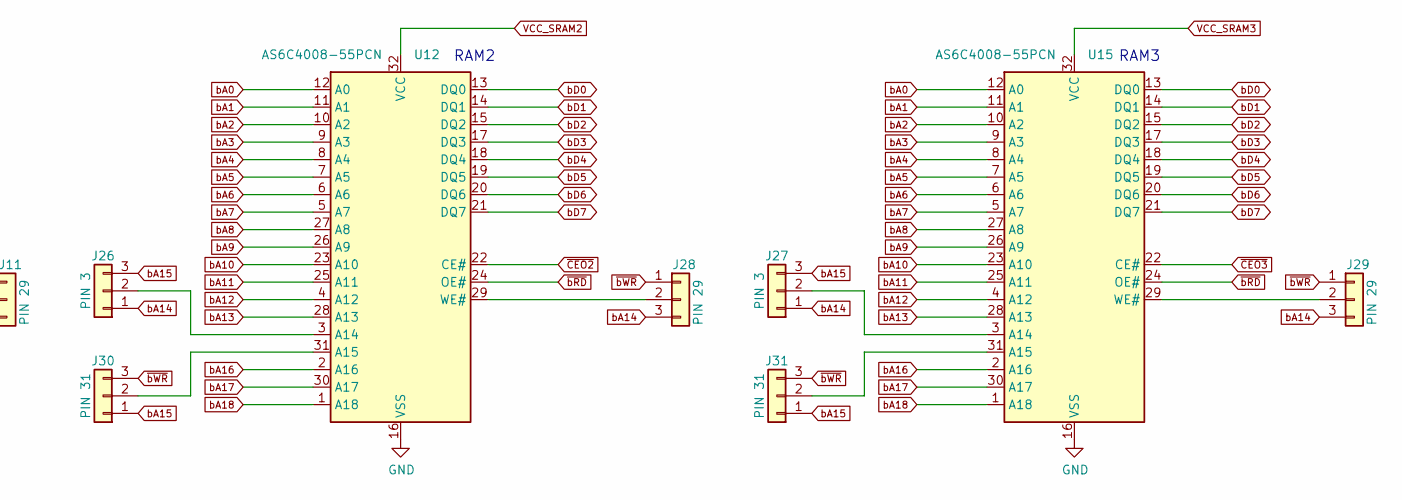
[picture p426: schematic RAM.kicad_sch, part in row 1, column 2]

Parts:
J2, J4, J26, J27: PIN 3; PinHeader_1x03_P2.54mm_Vertical
J3, J11, J28, J29: PIN 29; PinHeader_1x03_P2.54mm_Vertical
J12, J13, J30, J31: PIN 31; PinHeader_1x03_P2.54mm_Vertical
U2, U3, U12, U15: AS6C4008-55PCN; DIP-32_W15.24mm

Connections:
GND: U2.16 (VSS), U3.16 (VSS), U12.16 (VSS), U15.16 (VSS); also elsewhere on the board
unnamed: J2.2, U2.3 (A14)
unnamed: J3.2, U2.29 (WE#)
unnamed: J4.2, U3.3 (A14)
unnamed: J11.2, U3.29 (WE#)
unnamed: J12.2, U2.31 (A15)
unnamed: J13.2, U3.31 (A15)
unnamed: J26.2, U12.3 (A14)
unnamed: J27.2, U15.3 (A14)
unnamed: J28.2, U12.29 (WE#)
unnamed: J29.2, U15.29 (WE#)
unnamed: J30.2, U12.31 (A15)
unnamed: J31.2, U15.31 (A15)
VCC_SRAM0: U2.32 (VCC); also elsewhere on the board
VCC_SRAM1: U3.32 (VCC); also elsewhere on the board
VCC_SRAM2: U12.32 (VCC); also elsewhere on the board
VCC_SRAM3: U15.32 (VCC); also elsewhere on the board
bA0: U2.12 (A0), U3.12 (A0), U12.12 (A0), U15.12 (A0); also elsewhere on the board
bA1: U2.11 (A1), U3.11 (A1), U12.11 (A1), U15.11 (A1); also elsewhere on the board
bA2: U2.10 (A2), U3.10 (A2), U12.10 (A2), U15.10 (A2); also elsewhere on the board
bA3: U2.9 (A3), U3.9 (A3), U12.9 (A3), U15.9 (A3); also elsewhere on the board
bA4: U2.8 (A4), U3.8 (A4), U12.8 (A4), U15.8 (A4); also elsewhere on the board
bA5: U2.7 (A5), U3.7 (A5), U12.7 (A5), U15.7 (A5); also elsewhere on the board
bA6: U2.6 (A6), U3.6 (A6), U12.6 (A6), U15.6 (A6); also elsewhere on the board
bA7: U2.5 (A7), U3.5 (A7), U12.5 (A7), U15.5 (A7); also elsewhere on the board
bA8: U2.27 (A8), U3.27 (A8), U12.27 (A8), U15.27 (A8); also elsewhere on the board
bA9: U2.26 (A9), U3.26 (A9), U12.26 (A9), U15.26 (A9); also elsewhere on the board
bA10: U2.23 (A10), U3.23 (A10), U12.23 (A10), U15.23 (A10); also elsewhere on the board
bA11: U2.25 (A11), U3.25 (A11), U12.25 (A11), U15.25 (A11); also elsewhere on the board
bA12: U2.4 (A12), U3.4 (A12), U12.4 (A12), U15.4 (A12); also elsewhere on the board
bA13: U2.28 (A13), U3.28 (A13), U12.28 (A13), U15.28 (A13); also elsewhere on the board
bA14: J2.1, J3.3, J4.1, J11.3, J26.1, J27.1, J28.3, J29.3; also elsewhere on the board
bA15: J2.3, J4.3, J12.1, J13.1, J26.3, J27.3, J30.1, J31.1; also elsewhere on the board
bA16: U2.2 (A16), U3.2 (A16), U12.2 (A16), U15.2 (A16); also elsewhere on the board
bA17: U2.30 (A17), U3.30 (A17), U12.30 (A17), U15.30 (A17); also elsewhere on the board
bA18: U2.1 (A18), U3.1 (A18), U12.1 (A18), U15.1 (A18); also elsewhere on the board
bD0: U2.13 (DQ0), U3.13 (DQ0), U12.13 (DQ0), U15.13 (DQ0); also elsewhere on the board
bD1: U2.14 (DQ1), U3.14 (DQ1), U12.14 (DQ1), U15.14 (DQ1); also elsewhere on the board
bD2: U2.15 (DQ2), U3.15 (DQ2), U12.15 (DQ2), U15.15 (DQ2); also elsewhere on the board
bD3: U2.17 (DQ3), U3.17 (DQ3), U12.17 (DQ3), U15.17 (DQ3); also elsewhere on the board
bD4: U2.18 (DQ4), U3.18 (DQ4), U12.18 (DQ4), U15.18 (DQ4); also elsewhere on the board
bD5: U2.19 (DQ5), U3.19 (DQ5), U12.19 (DQ5), U15.19 (DQ5); also elsewhere on the board
bD6: U2.20 (DQ6), U3.20 (DQ6), U12.20 (DQ6), U15.20 (DQ6); also elsewhere on the board
bD7: U2.21 (DQ7), U3.21 (DQ7), U12.21 (DQ7), U15.21 (DQ7); also elsewhere on the board
~CEO0: U2.22 (CE#); also elsewhere on the board
~CEO1: U3.22 (CE#); also elsewhere on the board
~CEO2: U12.22 (CE#); also elsewhere on the board
~CEO3: U15.22 (CE#); also elsewhere on the board
~bRD: U2.24 (OE#), U3.24 (OE#), U12.24 (OE#), U15.24 (OE#); also elsewhere on the board
~bWR: J3.1, J11.1, J12.3, J13.3, J28.1, J29.1, J30.3, J31.3; also elsewhere on the board

Notes on the sheet:
RAM1
RAM2
RAM3
RAM0

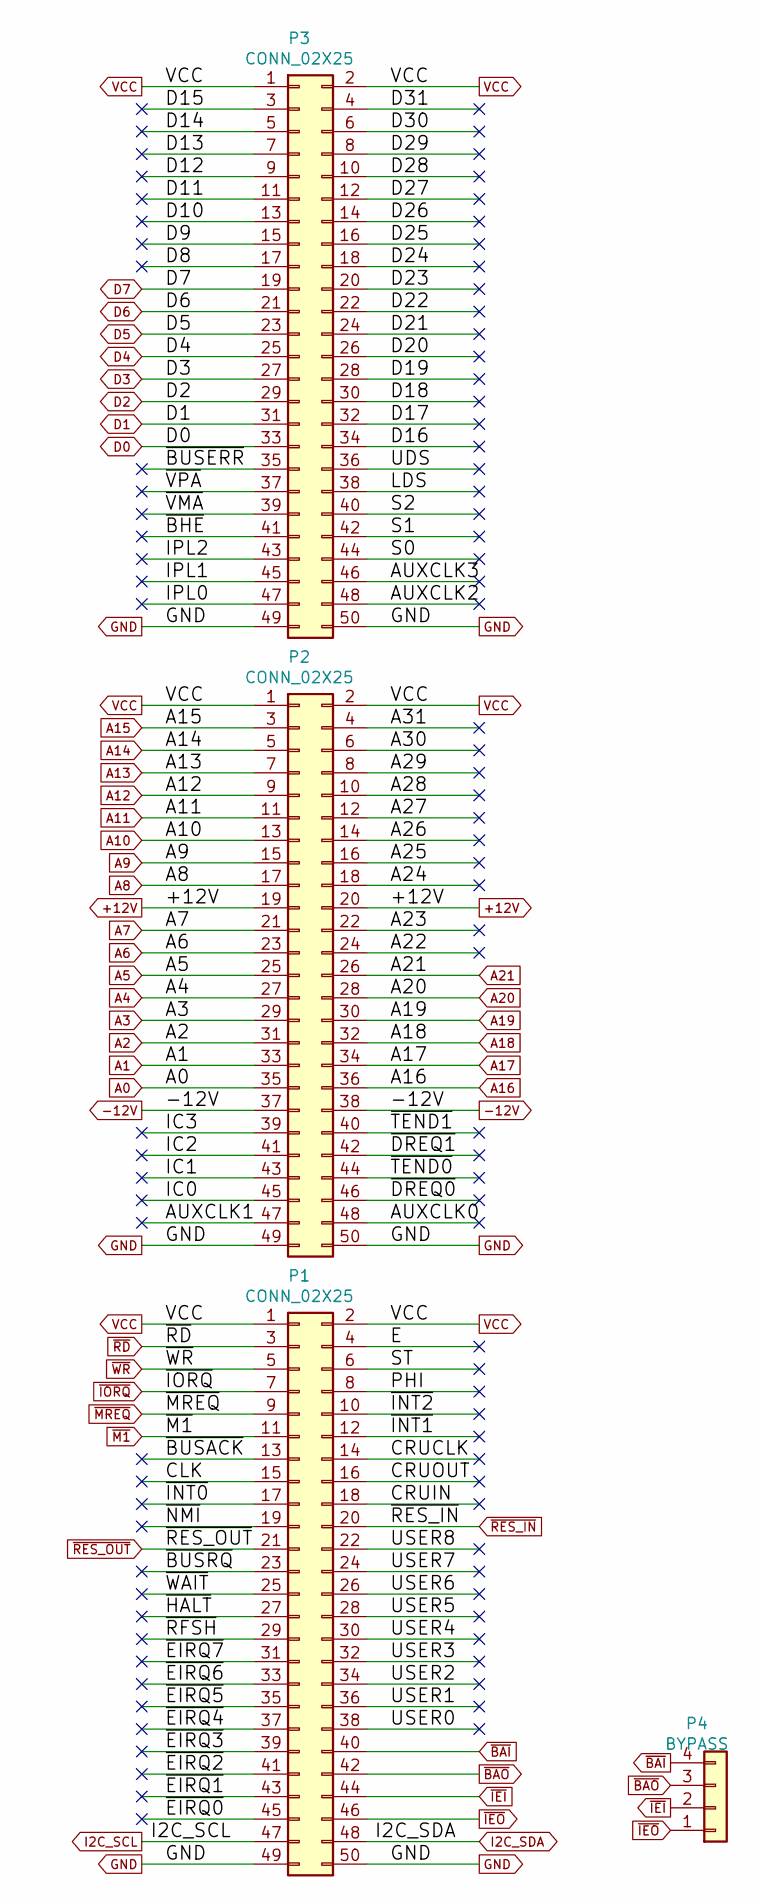
[picture p427: schematic bus.kicad_sch]

Parts:
P1, P2, P3: CONN_02X25; IDC-Header_2x25_P2.54mm_Horizontal
P4: BYPASS; PinHeader_1x04_P2.54mm_Vertical

Connections:
+12V: P2.19, P2.20
-12V: P2.37, P2.38
/bus/A22: P2.24
/bus/A23: P2.22
/bus/A24: P2.18
/bus/A25: P2.16
/bus/A26: P2.14
/bus/A27: P2.12
/bus/A28: P2.10
/bus/A29: P2.8
/bus/A30: P2.6
/bus/A31: P2.4
/bus/AUXCLK0: P2.48
/bus/AUXCLK1: P2.47
/bus/AUXCLK2: P3.48
/bus/AUXCLK3: P3.46
/bus/CLK: P1.15
/bus/CRUCLK: P1.14
/bus/CRUIN: P1.18
/bus/CRUOUT: P1.16
/bus/D8: P3.17
/bus/D9: P3.15
/bus/D10: P3.13
/bus/D11: P3.11
/bus/D12: P3.9
/bus/D13: P3.7
/bus/D14: P3.5
/bus/D15: P3.3
/bus/D16: P3.34
/bus/D17: P3.32
/bus/D18: P3.30
/bus/D19: P3.28
/bus/D20: P3.26
/bus/D21: P3.24
/bus/D22: P3.22
/bus/D23: P3.20
/bus/D24: P3.18
/bus/D25: P3.16
/bus/D26: P3.14
/bus/D27: P3.12
/bus/D28: P3.10
/bus/D29: P3.8
/bus/D30: P3.6
/bus/D31: P3.4
/bus/E: P1.4
/bus/IC0: P2.45
/bus/IC1: P2.43
/bus/IC2: P2.41
/bus/IC3: P2.39
/bus/IPL0: P3.47
/bus/IPL1: P3.45
/bus/IPL2: P3.43
/bus/LDS: P3.38
/bus/PHI: P1.8
/bus/S0: P3.44
/bus/S1: P3.42
/bus/S2: P3.40
/bus/ST: P1.6
/bus/UDS: P3.36
/bus/USER0: P1.38
/bus/USER1: P1.36
/bus/USER2: P1.34
/bus/USER3: P1.32
/bus/USER4: P1.30
/bus/USER5: P1.28
/bus/USER6: P1.26
/bus/USER7: P1.24
/bus/USER8: P1.22
/bus/~BHE: P3.41
/bus/~BUSACK: P1.13
/bus/~BUSERR: P3.35
/bus/~BUSRQ: P1.23
/bus/~DREQ0: P2.46
/bus/~DREQ1: P2.42
/bus/~EIRQ0: P1.45
/bus/~EIRQ1: P1.43
/bus/~EIRQ2: P1.41
/bus/~EIRQ3: P1.39
/bus/~EIRQ4: P1.37
/bus/~EIRQ5: P1.35
/bus/~EIRQ6: P1.33
/bus/~EIRQ7: P1.31
/bus/~HALT: P1.27
/bus/~INT0: P1.17
/bus/~INT1: P1.12
/bus/~INT2: P1.10
/bus/~NMI: P1.19
/bus/~RFSH: P1.29
/bus/~TEND0: P2.44
/bus/~TEND1: P2.40
/bus/~VMA: P3.39
/bus/~VPA: P3.37
/bus/~WAIT: P1.25
A0: P2.35; also elsewhere on the board
A1: P2.33; also elsewhere on the board
A2: P2.31; also elsewhere on the board
A3: P2.29; also elsewhere on the board
A4: P2.27; also elsewhere on the board
A5: P2.25; also elsewhere on the board
A6: P2.23; also elsewhere on the board
A7: P2.21; also elsewhere on the board
A8: P2.17; also elsewhere on the board
A9: P2.15; also elsewhere on the board
A10: P2.13; also elsewhere on the board
A11: P2.11; also elsewhere on the board
A12: P2.9; also elsewhere on the board
A13: P2.7; also elsewhere on the board
A14: P2.5; also elsewhere on the board
A15: P2.3; also elsewhere on the board
A16: P2.36; also elsewhere on the board
A17: P2.34; also elsewhere on the board
A18: P2.32; also elsewhere on the board
A19: P2.30; also elsewhere on the board
A20: P2.28; also elsewhere on the board
A21: P2.26; also elsewhere on the board
D0: P3.33; also elsewhere on the board
D1: P3.31; also elsewhere on the board
D2: P3.29; also elsewhere on the board
D3: P3.27; also elsewhere on the board
D4: P3.25; also elsewhere on the board
D5: P3.23; also elsewhere on the board
D6: P3.21; also elsewhere on the board
D7: P3.19; also elsewhere on the board
GND: P1.49, P1.50, P2.49, P2.50, P3.49, P3.50; also elsewhere on the board
I2C_SCL: P1.47; also elsewhere on the board
I2C_SDA: P1.48; also elsewhere on the board
VCC: P1.1, P1.2, P2.1, P2.2, P3.1, P3.2; also elsewhere on the board
~BAI: P1.40, P4.4
~BAO: P1.42, P4.3
~IEI: P1.44, P4.2
~IEO: P1.46, P4.1
~IORQ: P1.7; also elsewhere on the board
~M1: P1.11; also elsewhere on the board
~MREQ: P1.9; also elsewhere on the board
~RD: P1.3; also elsewhere on the board
~RES_IN: P1.20; also elsewhere on the board
~RES_OUT: P1.21; also elsewhere on the board
~WR: P1.5; also elsewhere on the board

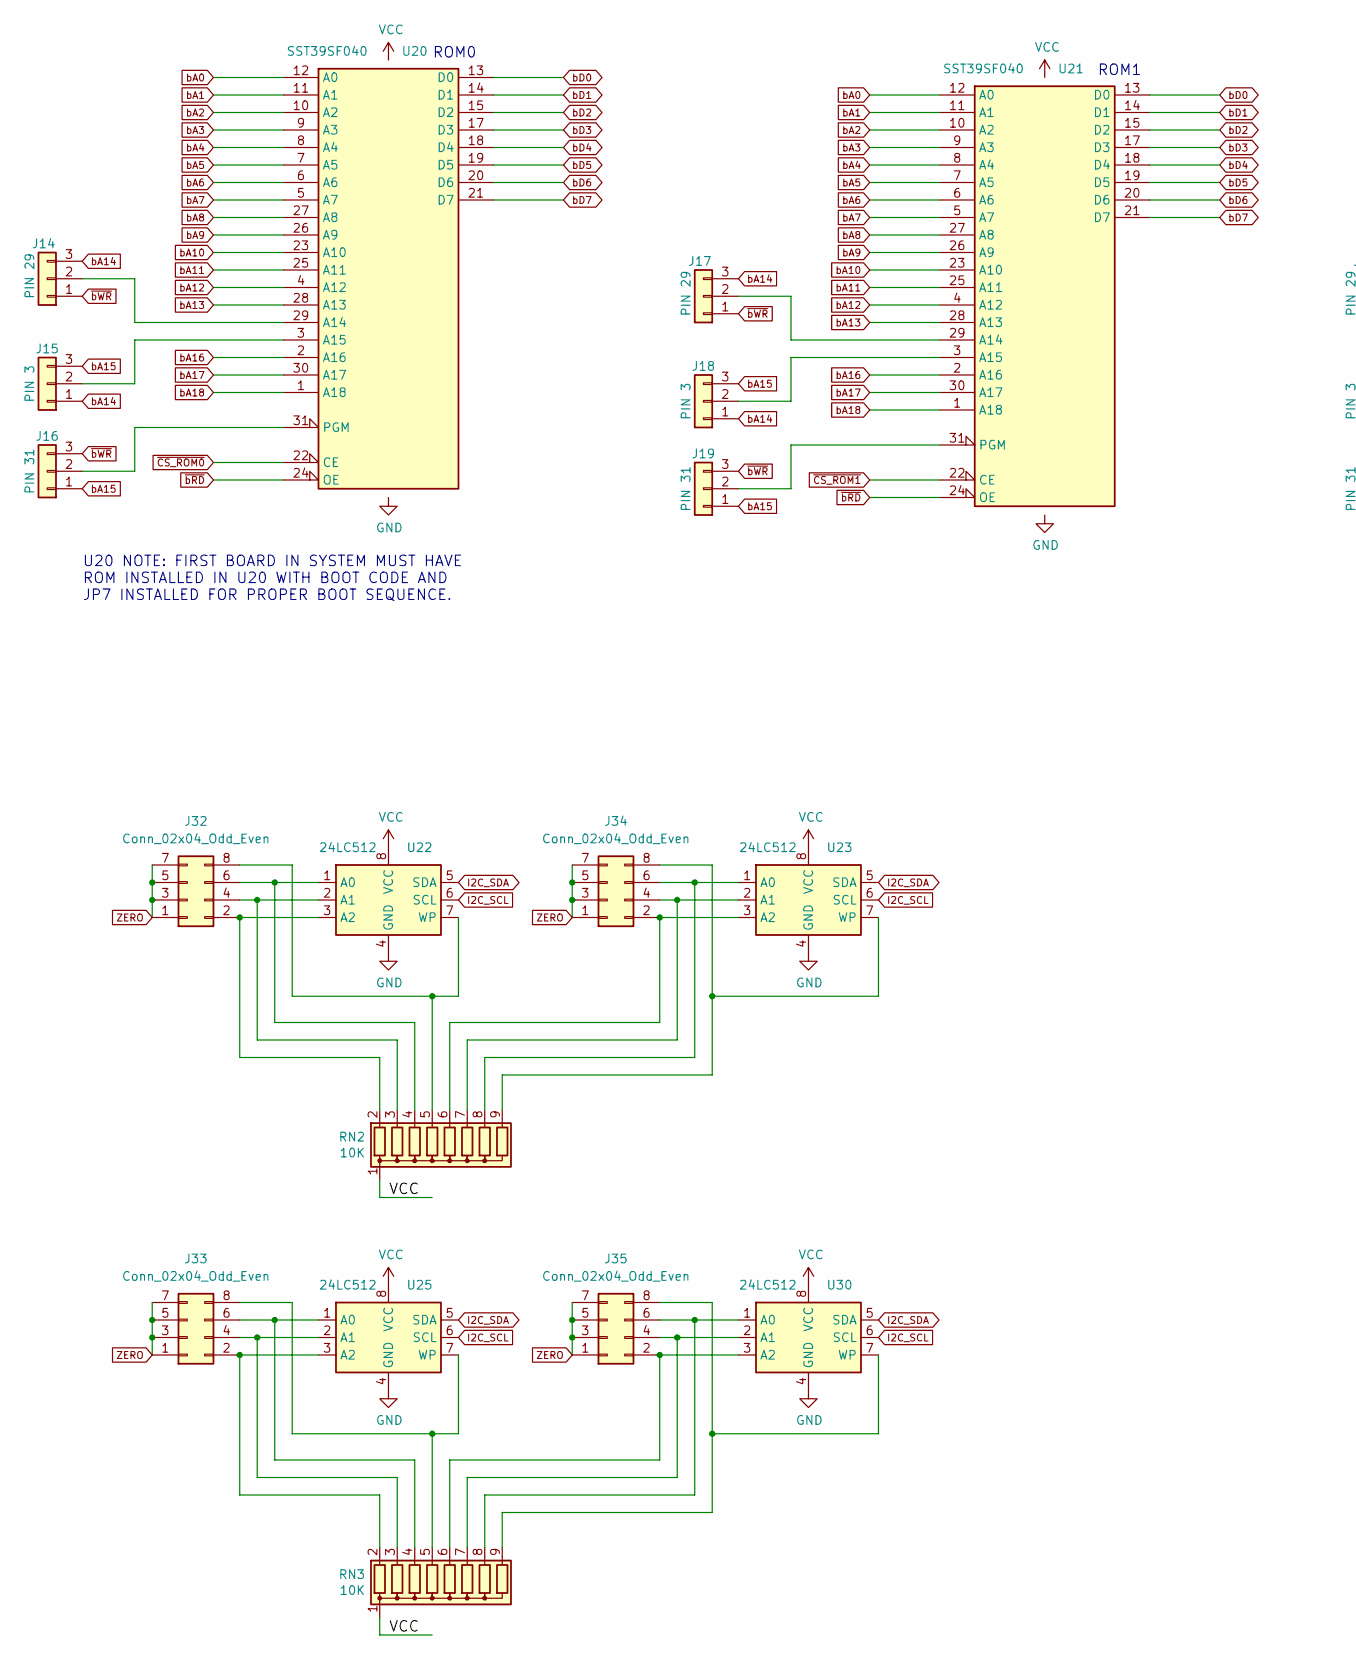
[picture p428: schematic ROM.kicad_sch, part in row 1, column 1]

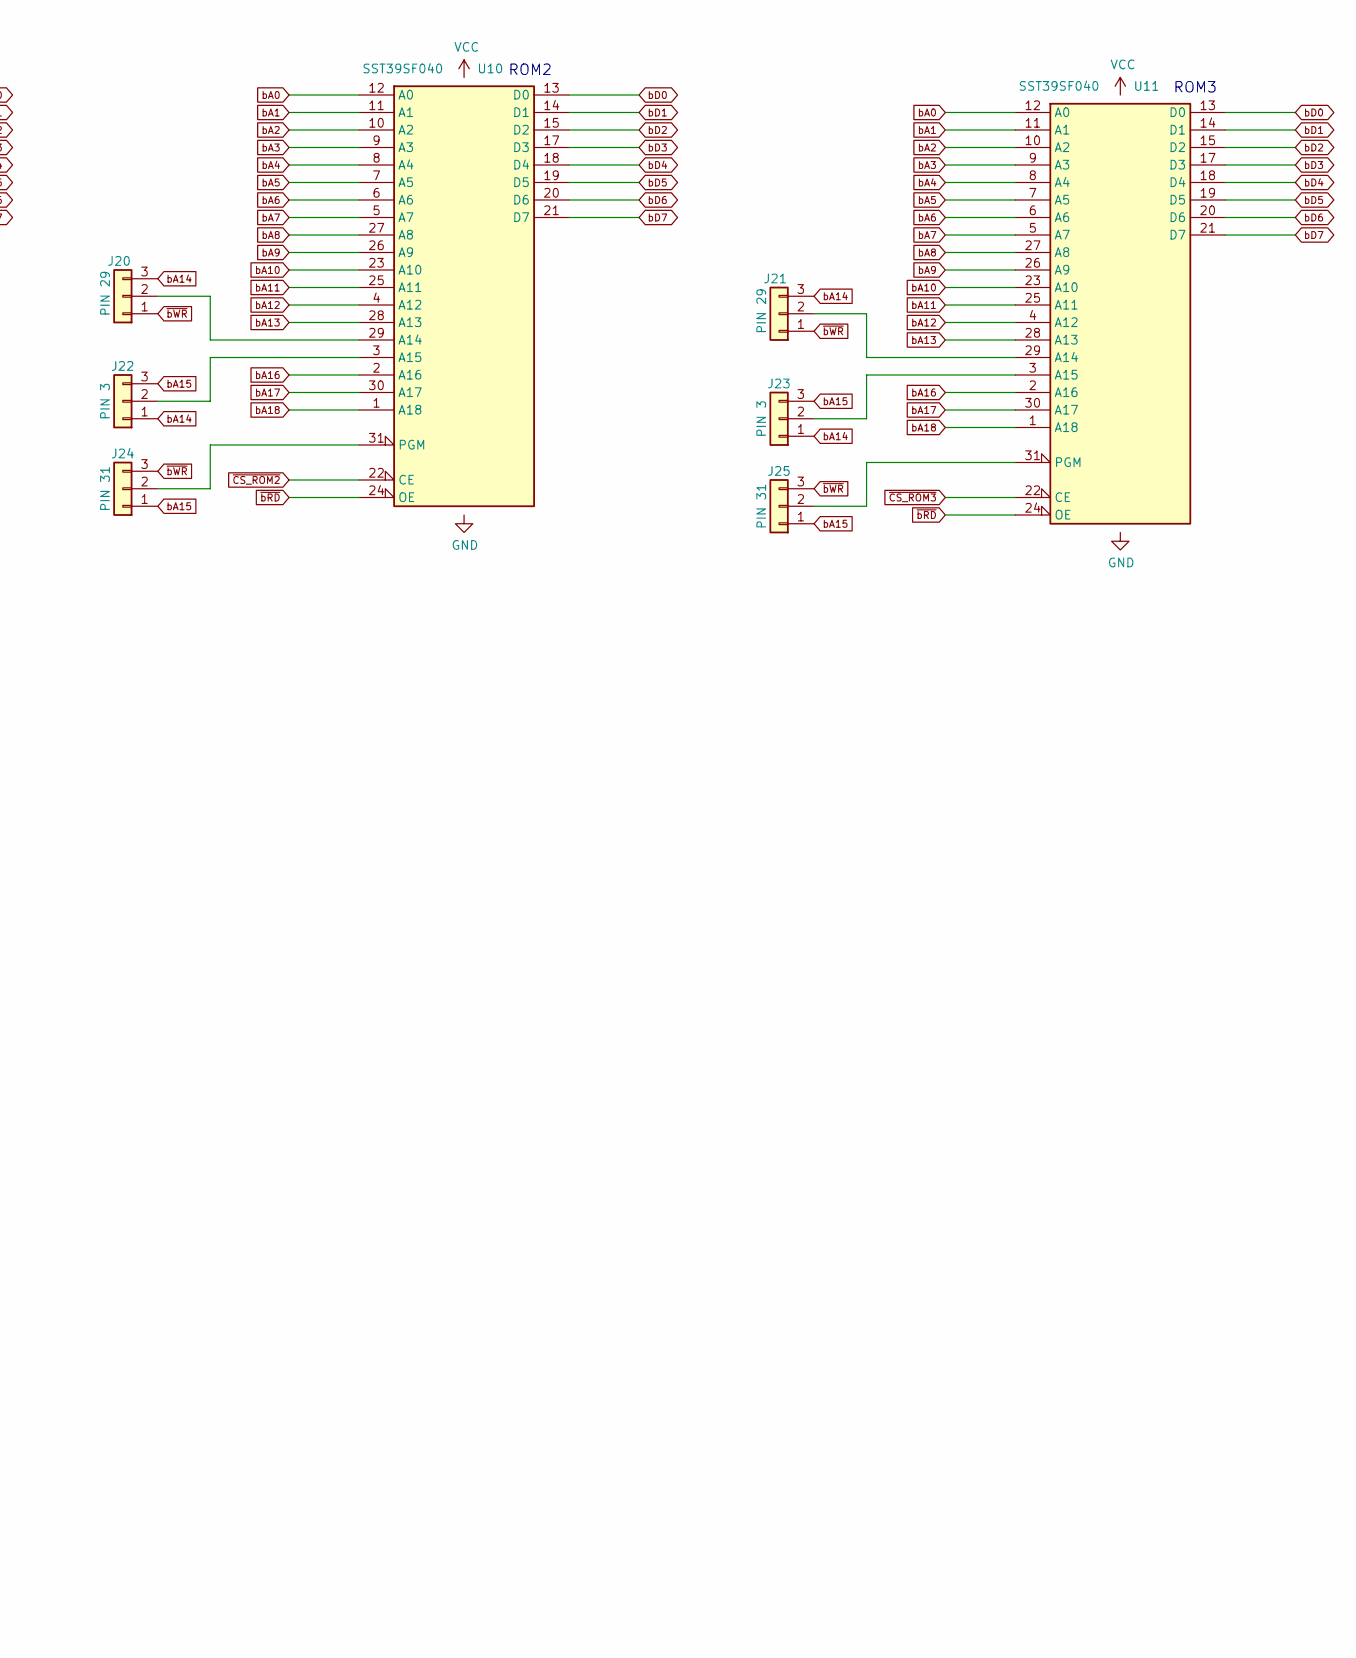
[picture p429: schematic ROM.kicad_sch, part in row 1, column 2]

Parts:
J14, J17, J20, J21: PIN 29; PinHeader_1x03_P2.54mm_Vertical
J15, J18, J22, J23: PIN 3; PinHeader_1x03_P2.54mm_Vertical
J16, J19, J24, J25: PIN 31; PinHeader_1x03_P2.54mm_Vertical
J32, J33, J34, J35: Conn_02x04_Odd_Even; PinHeader_2x04_P2.54mm_Vertical
RN2, RN3: 10K; R_Array_SIP9
U10, U11, U20, U21: SST39SF040; DIP-32_W15.24mm
U22, U23, U25, U30: 24LC512; DIP-8_W7.62mm

Connections:
GND: U10.16 (GND), U11.16 (GND), U20.16 (GND), U21.16 (GND), U22.4 (GND), U23.4 (GND), U25.4 (GND), U30.4 (GND); also elsewhere on the board
I2C_SCL: U22.6 (SCL), U23.6 (SCL), U25.6 (SCL), U30.6 (SCL); also elsewhere on the board
I2C_SDA: U22.5 (SDA), U23.5 (SDA), U25.5 (SDA), U30.5 (SDA); also elsewhere on the board
unnamed: J14.2, U20.29 (A14)
unnamed: J15.2, U20.3 (A15)
unnamed: J16.2, U20.31 (PGM)
unnamed: J17.2, U21.29 (A14)
unnamed: J18.2, U21.3 (A15)
unnamed: J19.2, U21.31 (PGM)
unnamed: J20.2, U10.29 (A14)
unnamed: J21.2, U11.29 (A14)
unnamed: J22.2, U10.3 (A15)
unnamed: J23.2, U11.3 (A15)
unnamed: J24.2, U10.31 (PGM)
unnamed: J25.2, U11.31 (PGM)
unnamed: J32.2, RN2.2 (R1), U22.3 (A2)
unnamed: J32.4, RN2.3 (R2), U22.2 (A1)
unnamed: J32.6, RN2.4 (R3), U22.1 (A0)
unnamed: J32.8, RN2.5 (R4), U22.7 (WP)
unnamed: J33.2, RN3.2 (R1), U25.3 (A2)
unnamed: J33.4, RN3.3 (R2), U25.2 (A1)
unnamed: J33.6, RN3.4 (R3), U25.1 (A0)
unnamed: J33.8, RN3.5 (R4), U25.7 (WP)
unnamed: J34.2, RN2.6 (R5), U23.3 (A2)
unnamed: J34.4, RN2.7 (R6), U23.2 (A1)
unnamed: J34.6, RN2.8 (R7), U23.1 (A0)
unnamed: J34.8, RN2.9 (R8), U23.7 (WP)
unnamed: J35.2, RN3.6 (R5), U30.3 (A2)
unnamed: J35.4, RN3.7 (R6), U30.2 (A1)
unnamed: J35.6, RN3.8 (R7), U30.1 (A0)
unnamed: J35.8, RN3.9 (R8), U30.7 (WP)
VCC: RN2.1 (common), RN3.1 (common), U10.32 (VCC), U11.32 (VCC), U20.32 (VCC), U21.32 (VCC), U22.8 (VCC), U23.8 (VCC), U25.8 (VCC), U30.8 (VCC); also elsewhere on the board
ZERO: J32.1, J32.3, J32.5, J32.7, J33.1, J33.3, J33.5, J33.7, J34.1, J34.3, J34.5, J34.7, J35.1, J35.3, J35.5, J35.7; also elsewhere on the board
bA0: U10.12 (A0), U11.12 (A0), U20.12 (A0), U21.12 (A0); also elsewhere on the board
bA1: U10.11 (A1), U11.11 (A1), U20.11 (A1), U21.11 (A1); also elsewhere on the board
bA2: U10.10 (A2), U11.10 (A2), U20.10 (A2), U21.10 (A2); also elsewhere on the board
bA3: U10.9 (A3), U11.9 (A3), U20.9 (A3), U21.9 (A3); also elsewhere on the board
bA4: U10.8 (A4), U11.8 (A4), U20.8 (A4), U21.8 (A4); also elsewhere on the board
bA5: U10.7 (A5), U11.7 (A5), U20.7 (A5), U21.7 (A5); also elsewhere on the board
bA6: U10.6 (A6), U11.6 (A6), U20.6 (A6), U21.6 (A6); also elsewhere on the board
bA7: U10.5 (A7), U11.5 (A7), U20.5 (A7), U21.5 (A7); also elsewhere on the board
bA8: U10.27 (A8), U11.27 (A8), U20.27 (A8), U21.27 (A8); also elsewhere on the board
bA9: U10.26 (A9), U11.26 (A9), U20.26 (A9), U21.26 (A9); also elsewhere on the board
bA10: U10.23 (A10), U11.23 (A10), U20.23 (A10), U21.23 (A10); also elsewhere on the board
bA11: U10.25 (A11), U11.25 (A11), U20.25 (A11), U21.25 (A11); also elsewhere on the board
bA12: U10.4 (A12), U11.4 (A12), U20.4 (A12), U21.4 (A12); also elsewhere on the board
bA13: U10.28 (A13), U11.28 (A13), U20.28 (A13), U21.28 (A13); also elsewhere on the board
bA14: J14.3, J15.1, J17.3, J18.1, J20.3, J21.3, J22.1, J23.1; also elsewhere on the board
bA15: J15.3, J16.1, J18.3, J19.1, J22.3, J23.3, J24.1, J25.1; also elsewhere on the board
bA16: U10.2 (A16), U11.2 (A16), U20.2 (A16), U21.2 (A16); also elsewhere on the board
bA17: U10.30 (A17), U11.30 (A17), U20.30 (A17), U21.30 (A17); also elsewhere on the board
bA18: U10.1 (A18), U11.1 (A18), U20.1 (A18), U21.1 (A18); also elsewhere on the board
bD0: U10.13 (D0), U11.13 (D0), U20.13 (D0), U21.13 (D0); also elsewhere on the board
bD1: U10.14 (D1), U11.14 (D1), U20.14 (D1), U21.14 (D1); also elsewhere on the board
bD2: U10.15 (D2), U11.15 (D2), U20.15 (D2), U21.15 (D2); also elsewhere on the board
bD3: U10.17 (D3), U11.17 (D3), U20.17 (D3), U21.17 (D3); also elsewhere on the board
bD4: U10.18 (D4), U11.18 (D4), U20.18 (D4), U21.18 (D4); also elsewhere on the board
bD5: U10.19 (D5), U11.19 (D5), U20.19 (D5), U21.19 (D5); also elsewhere on the board
bD6: U10.20 (D6), U11.20 (D6), U20.20 (D6), U21.20 (D6); also elsewhere on the board
bD7: U10.21 (D7), U11.21 (D7), U20.21 (D7), U21.21 (D7); also elsewhere on the board
~CS_ROM0: U20.22 (CE); also elsewhere on the board
~CS_ROM1: U21.22 (CE); also elsewhere on the board
~CS_ROM2: U10.22 (CE); also elsewhere on the board
~CS_ROM3: U11.22 (CE); also elsewhere on the board
~bRD: U10.24 (OE), U11.24 (OE), U20.24 (OE), U21.24 (OE); also elsewhere on the board
~bWR: J14.1, J16.3, J17.1, J19.3, J20.1, J21.1, J24.3, J25.3; also elsewhere on the board

Notes on the sheet:
ROM3
ROM1
ROM0
ROM2
U20 NOTE: FIRST BOARD IN SYSTEM MUST HAVE ROM INSTALLED IN U20 WITH BOOT CODE AND JP7 INSTALLED FOR PROPER BOOT SEQUENCE.

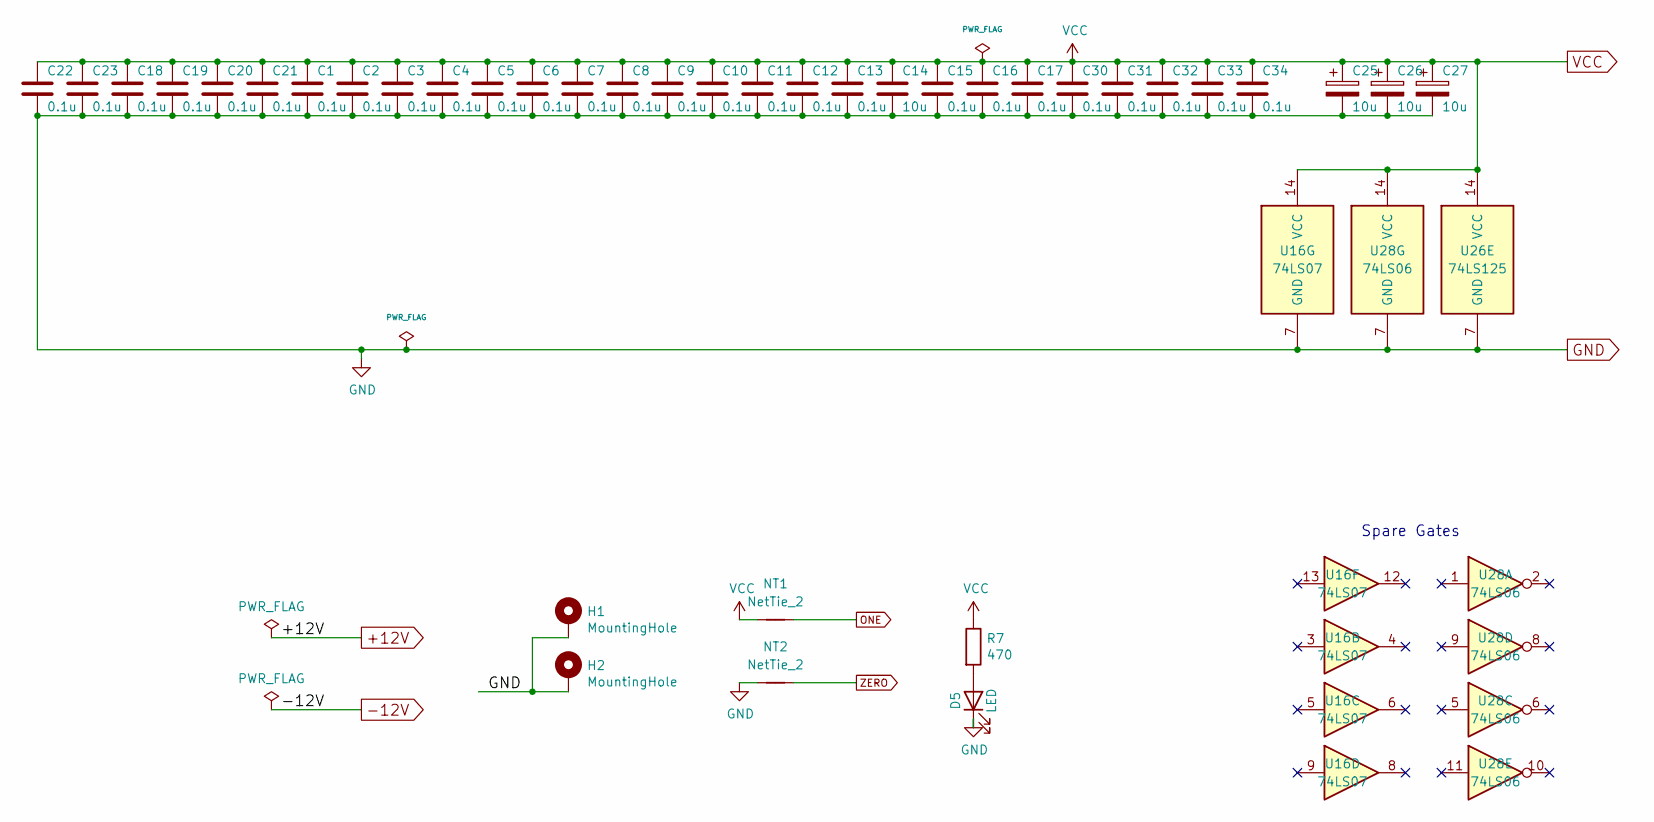
[picture p430: schematic power.kicad_sch]

Parts:
C1, C2, C3, C4, C5, C6, C7, C8, C9, C10, C11, C12, C13, C15, C16, C17, C18, C19, C20, C21, C22, C23, C30, C31, C32, C33, C34: 0.1u; C_Disc_D5.0mm_W2.5mm_P5.00mm
C14, C25, C26, C27: 10u; CP_Radial_D5.0mm_P2.50mm
D5: LED; LED_D3.0mm_Horizontal_O3.81mm_Z2.0mm
H1, H2: MountingHole; MountingHole_3.2mm_M3_Pad
NT1, NT2: NetTie_2; NetTie-2_THT_Pad0.3mm
R7: 470; R_Axial_DIN0207_L6.3mm_D2.5mm_P7.62mm_Horizontal
U16: 74LS07; DIP-14_W7.62mm
U26: 74LS125; DIP-14_W7.62mm
U28: 74LS06; DIP-14_W7.62mm

Connections:
GND: C1.2, C2.2, C3.2, C4.2, C5.2, C6.2, C7.2, C8.2, C9.2, C10.2, C11.2, C12.2, C13.2, C14.2, C15.2, C16.2, C17.2, C18.2, C19.2, C20.2, C21.2, C22.2, C23.2, C25.2, C26.2, C27.2, C30.2, C31.2, C32.2, C33.2, C34.2, D5.1 (K), H1.1, H2.1, NT2.1, U16.7 (GND), U26.7 (GND), U28.7 (GND); also elsewhere on the board
unnamed: D5.2 (A), R7.2
ONE: NT1.2; also elsewhere on the board
VCC: C1.1, C2.1, C3.1, C4.1, C5.1, C6.1, C7.1, C8.1, C9.1, C10.1, C11.1, C12.1, C13.1, C14.1, C15.1, C16.1, C17.1, C18.1, C19.1, C20.1, C21.1, C22.1, C23.1, C25.1, C26.1, C27.1, C30.1, C31.1, C32.1, C33.1, C34.1, NT1.1, R7.1, U16.14 (VCC), U26.14 (VCC), U28.14 (VCC); also elsewhere on the board
ZERO: NT2.2; also elsewhere on the board

Notes on the sheet:
Spare Gates
