lynchaj/duodyne/!Retired/04 memory.ROMRAM.8-bit, V1.0/memory.ROMRAM.kicad_pcb

## KiCad design !Retired/04 memory.ROMRAM.8-bit, V1.0/memory.ROMRAM.kicad_pcb (continued)

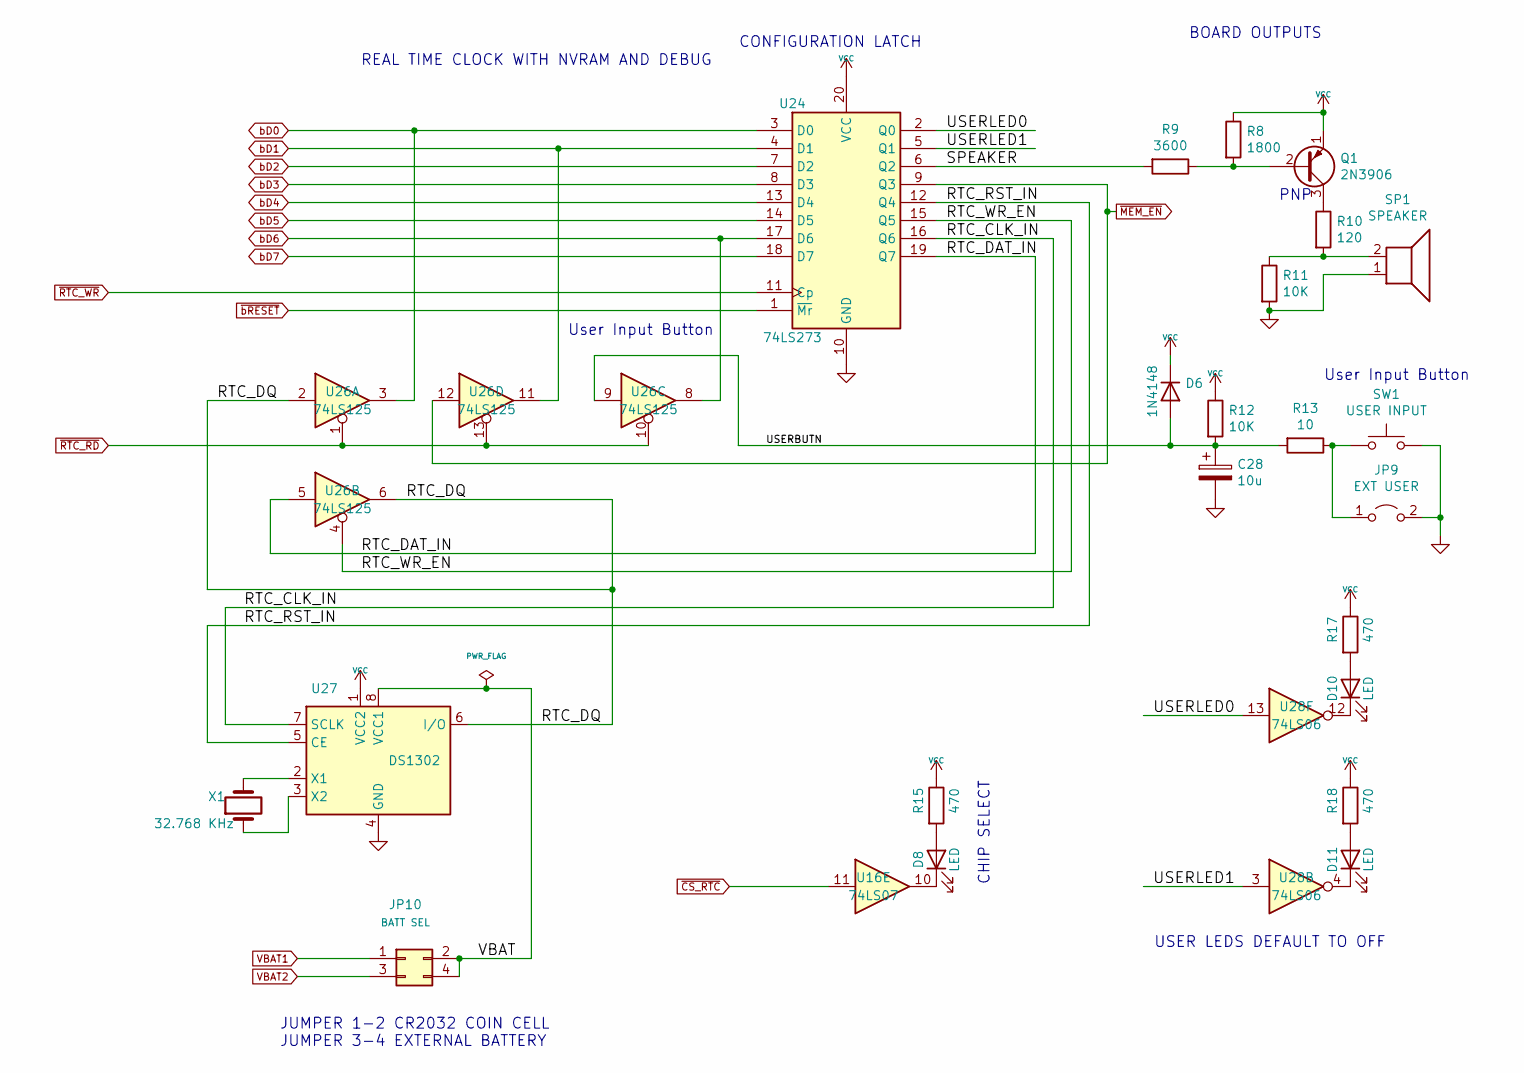
[picture p431: schematic RTC.kicad_sch]

Parts:
C28: 10u; CP_Radial_D5.0mm_P2.50mm
D6: 1N4148; D_DO-35_SOD27_P7.62mm_Horizontal
D8, D10, D11: LED; LED_D3.0mm_Horizontal_O3.81mm_Z2.0mm
JP9: EXT USER; PinHeader_1x02_P2.54mm_Horizontal
JP10: BATT SEL; PinHeader_2x02_P2.54mm_Vertical
Q1: 2N3906; TO-92_Inline
R8: 1800; R_Axial_DIN0207_L6.3mm_D2.5mm_P7.62mm_Horizontal
R9: 3600; R_Axial_DIN0207_L6.3mm_D2.5mm_P7.62mm_Horizontal
R10: 120; R_Axial_DIN0207_L6.3mm_D2.5mm_P7.62mm_Horizontal
R11, R12: 10K; R_Axial_DIN0207_L6.3mm_D2.5mm_P7.62mm_Horizontal
R13: 10; R_Axial_DIN0207_L6.3mm_D2.5mm_P7.62mm_Horizontal
R15, R17, R18: 470; R_Axial_DIN0207_L6.3mm_D2.5mm_P7.62mm_Horizontal
SP1: SPEAKER; MagneticBuzzer_StarMicronics_HMB-06_HMB-12
SW1: USER INPUT; SW_Tactile_SPST_Angled_PTS645Vx58-2LFS
U16: 74LS07; DIP-14_W7.62mm
U24: 74LS273; DIP-20_W7.62mm
U26: 74LS125; DIP-14_W7.62mm
U27: DS1302; DIP-8_W7.62mm
U28: 74LS06; DIP-14_W7.62mm
X1: 32.768 KHz; Crystal_AT310_D3.0mm_L10.0mm_Horizontal

Connections:
/RTC/RTC_CLK_IN: U24.16 (Q6), U27.7 (SCLK)
/RTC/RTC_DAT_IN: U24.19 (Q7), U26.5
/RTC/RTC_DQ: U26.2, U26.6, U27.6 (I/O)
/RTC/RTC_RST_IN: U24.12 (Q4), U27.5 (CE)
/RTC/RTC_WR_EN: U24.15 (Q5), U26.4
/RTC/SPEAKER: R9.2, U24.6 (Q2)
/RTC/USERBUTN: C28.1, D6.2 (A), R12.2, R13.2, U26.9
/RTC/USERLED0: U24.2 (Q0), U28.13
/RTC/USERLED1: U24.5 (Q1), U28.3
/RTC/VBAT: JP10.2, JP10.4, U27.8 (VCC1)
GND: C28.2, JP9.2 (B), R11.2, SP1.1, SW1.2, U24.10 (GND), U27.4 (GND); also elsewhere on the board
unnamed: D8.1 (K), U16.10
unnamed: D8.2 (A), R15.2
unnamed: D10.1 (K), U28.12
unnamed: D10.2 (A), R17.2
unnamed: D11.1 (K), U28.4
unnamed: D11.2 (A), R18.2
unnamed: JP9.1 (A), R13.1, SW1.1
unnamed: Q1.2 (B), R8.2, R9.1
unnamed: Q1.3 (C), R10.1
unnamed: R10.2, R11.1, SP1.2
unnamed: U27.2 (X1), X1.2
unnamed: U27.3 (X2), X1.1
VBAT1: JP10.1; also elsewhere on the board
VBAT2: JP10.3; also elsewhere on the board
VCC: D6.1 (K), Q1.1 (E), R8.1, R12.1, R15.1, R17.1, R18.1, U24.20 (VCC), U27.1 (VCC2); also elsewhere on the board
bD0: U24.3 (D0), U26.3; also elsewhere on the board
bD1: U24.4 (D1), U26.11; also elsewhere on the board
bD2: U24.7 (D2); also elsewhere on the board
bD3: U24.8 (D3); also elsewhere on the board
bD4: U24.13 (D4); also elsewhere on the board
bD5: U24.14 (D5); also elsewhere on the board
bD6: U24.17 (D6), U26.8; also elsewhere on the board
bD7: U24.18 (D7); also elsewhere on the board
~CS_RTC: U16.11; also elsewhere on the board
~MEM_EN: U24.9 (Q3), U26.12; also elsewhere on the board
~RTC_RD: U26.1, U26.10, U26.13; also elsewhere on the board
~RTC_WR: U24.11 (Cp); also elsewhere on the board
~bRESET: U24.1 (~Mr); also elsewhere on the board

Notes on the sheet:
PNP
User Input Button
BOARD OUTPUTS
CONFIGURATION LATCH
JUMPER 1-2 CR2032 COIN CELL JUMPER 3-4 EXTERNAL BATTERY
CHIP SELECT
USER LEDS DEFAULT TO OFF
REAL TIME CLOCK WITH NVRAM AND DEBUG

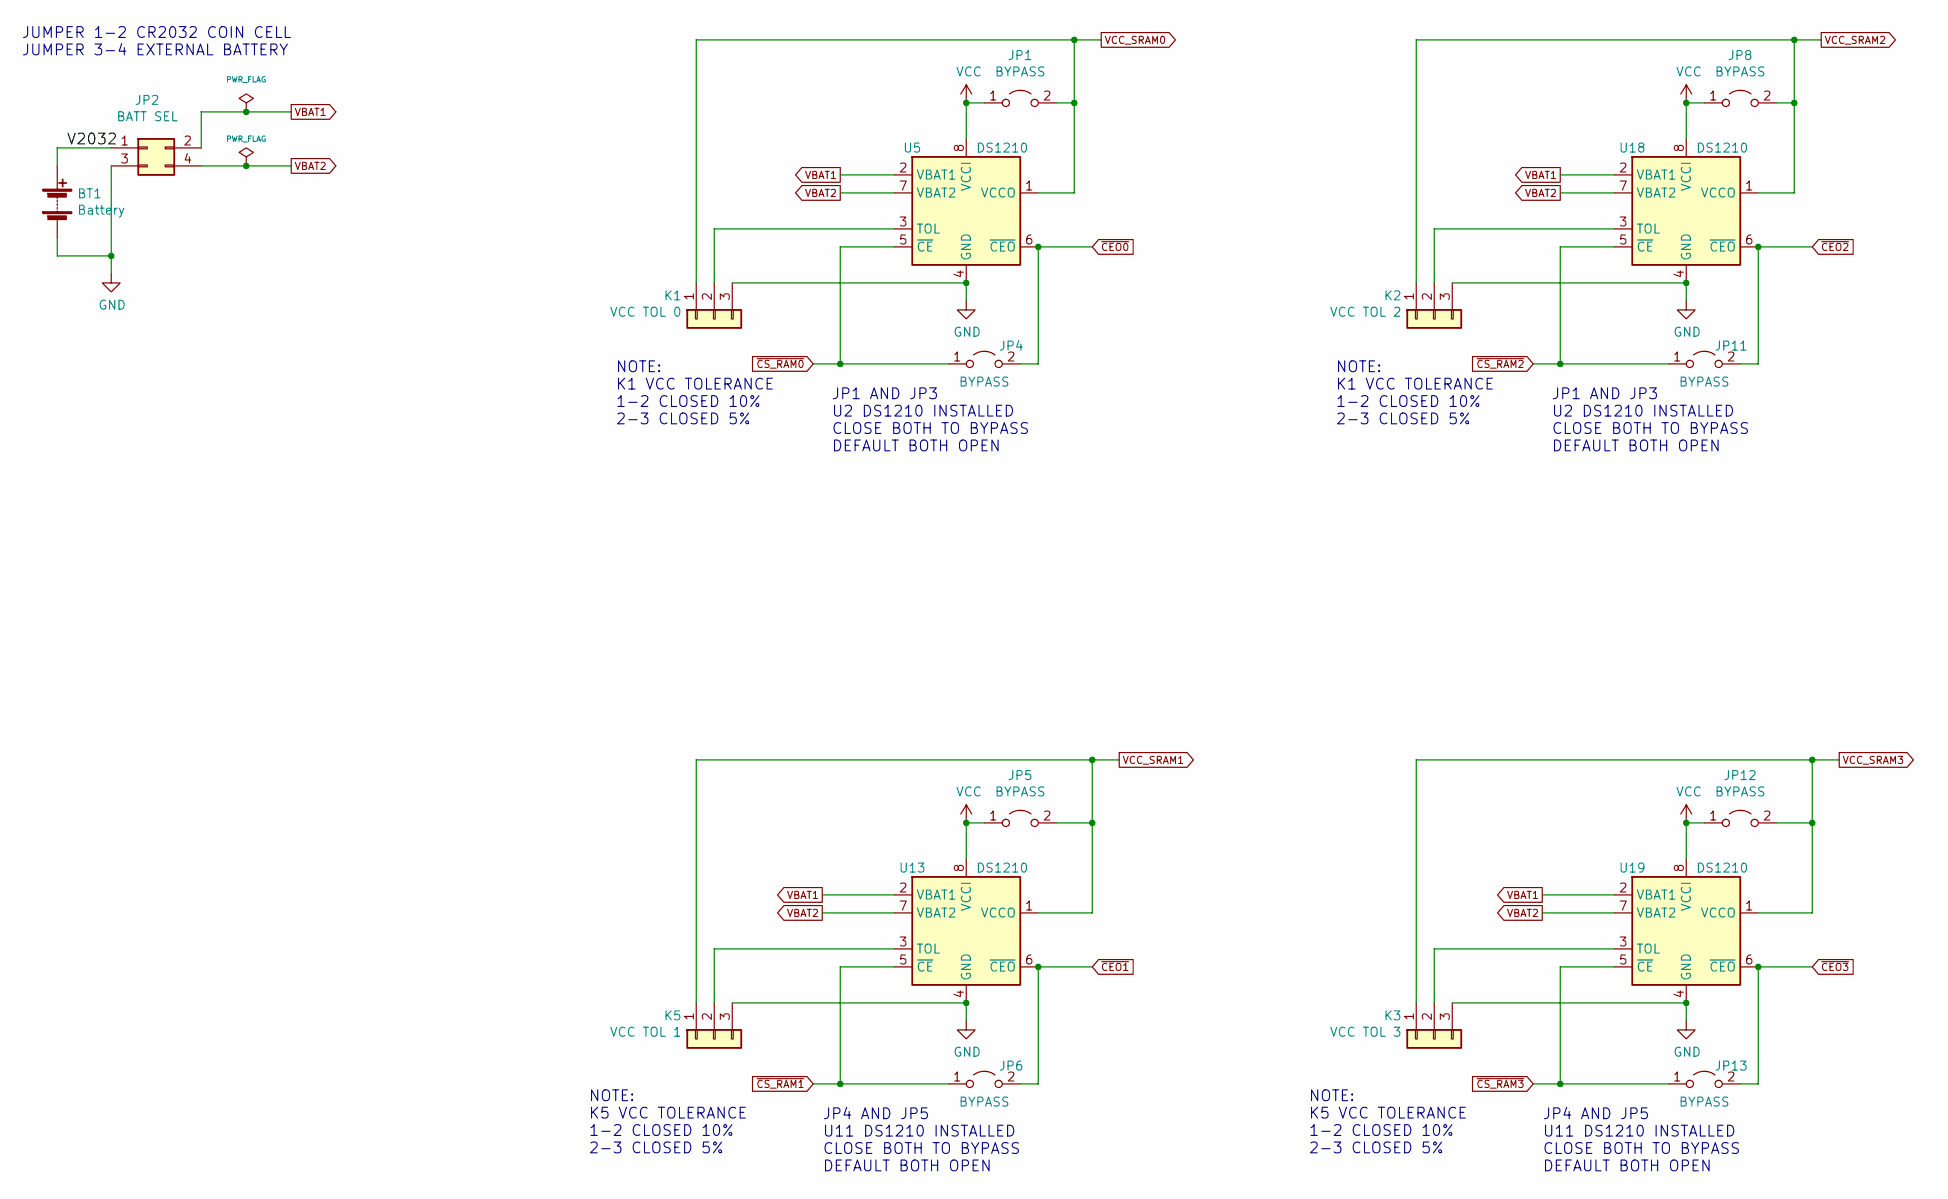
[picture p432: schematic battery.kicad_sch]

Parts:
BT1: Battery; BatteryHolder_Keystone_103_1x20mm
JP1, JP4, JP5, JP6, JP8, JP11, JP12, JP13: BYPASS; PinHeader_1x02_P2.54mm_Vertical
JP2: BATT SEL; PinHeader_2x02_P2.54mm_Vertical
K1: VCC TOL 0; PinHeader_1x03_P2.54mm_Vertical
K2: VCC TOL 2; PinHeader_1x03_P2.54mm_Vertical
K3: VCC TOL 3; PinHeader_1x03_P2.54mm_Vertical
K5: VCC TOL 1; PinHeader_1x03_P2.54mm_Vertical
U5, U13, U18, U19: DS1210; DIP-8_W7.62mm

Connections:
/battery/V2032: BT1.1 (+), JP2.1
GND: BT1.2 (-), JP2.3, K1.3, K2.3, K3.3, K5.3, U5.4 (GND), U13.4 (GND), U18.4 (GND), U19.4 (GND); also elsewhere on the board
unnamed: K1.2, U5.3 (TOL)
unnamed: K2.2, U18.3 (TOL)
unnamed: K3.2, U19.3 (TOL)
unnamed: K5.2, U13.3 (TOL)
VBAT1: JP2.2, U5.2 (VBAT1), U13.2 (VBAT1), U18.2 (VBAT1), U19.2 (VBAT1); also elsewhere on the board
VBAT2: JP2.4, U5.7 (VBAT2), U13.7 (VBAT2), U18.7 (VBAT2), U19.7 (VBAT2); also elsewhere on the board
VCC: JP1.1 (A), JP5.1 (A), JP8.1 (A), JP12.1 (A), U5.8 (VCCI), U13.8 (VCCI), U18.8 (VCCI), U19.8 (VCCI); also elsewhere on the board
VCC_SRAM0: JP1.2 (B), K1.1, U5.1 (VCCO); also elsewhere on the board
VCC_SRAM1: JP5.2 (B), K5.1, U13.1 (VCCO); also elsewhere on the board
VCC_SRAM2: JP8.2 (B), K2.1, U18.1 (VCCO); also elsewhere on the board
VCC_SRAM3: JP12.2 (B), K3.1, U19.1 (VCCO); also elsewhere on the board
~CEO0: JP4.2 (B), U5.6 (~CEO); also elsewhere on the board
~CEO1: JP6.2 (B), U13.6 (~CEO); also elsewhere on the board
~CEO2: JP11.2 (B), U18.6 (~CEO); also elsewhere on the board
~CEO3: JP13.2 (B), U19.6 (~CEO); also elsewhere on the board
~CS_RAM0: JP4.1 (A), U5.5 (~CE); also elsewhere on the board
~CS_RAM1: JP6.1 (A), U13.5 (~CE); also elsewhere on the board
~CS_RAM2: JP11.1 (A), U18.5 (~CE); also elsewhere on the board
~CS_RAM3: JP13.1 (A), U19.5 (~CE); also elsewhere on the board

Notes on the sheet:
NOTE: K1 VCC TOLERANCE 1-2 CLOSED 10% 2-3 CLOSED 5%
JP1 AND JP3 U2 DS1210 INSTALLED CLOSE BOTH TO BYPASS DEFAULT BOTH OPEN
NOTE: K5 VCC TOLERANCE 1-2 CLOSED 10% 2-3 CLOSED 5%
JUMPER 1-2 CR2032 COIN CELL JUMPER 3-4 EXTERNAL BATTERY
JP4 AND JP5 U11 DS1210 INSTALLED CLOSE BOTH TO BYPASS DEFAULT BOTH OPEN

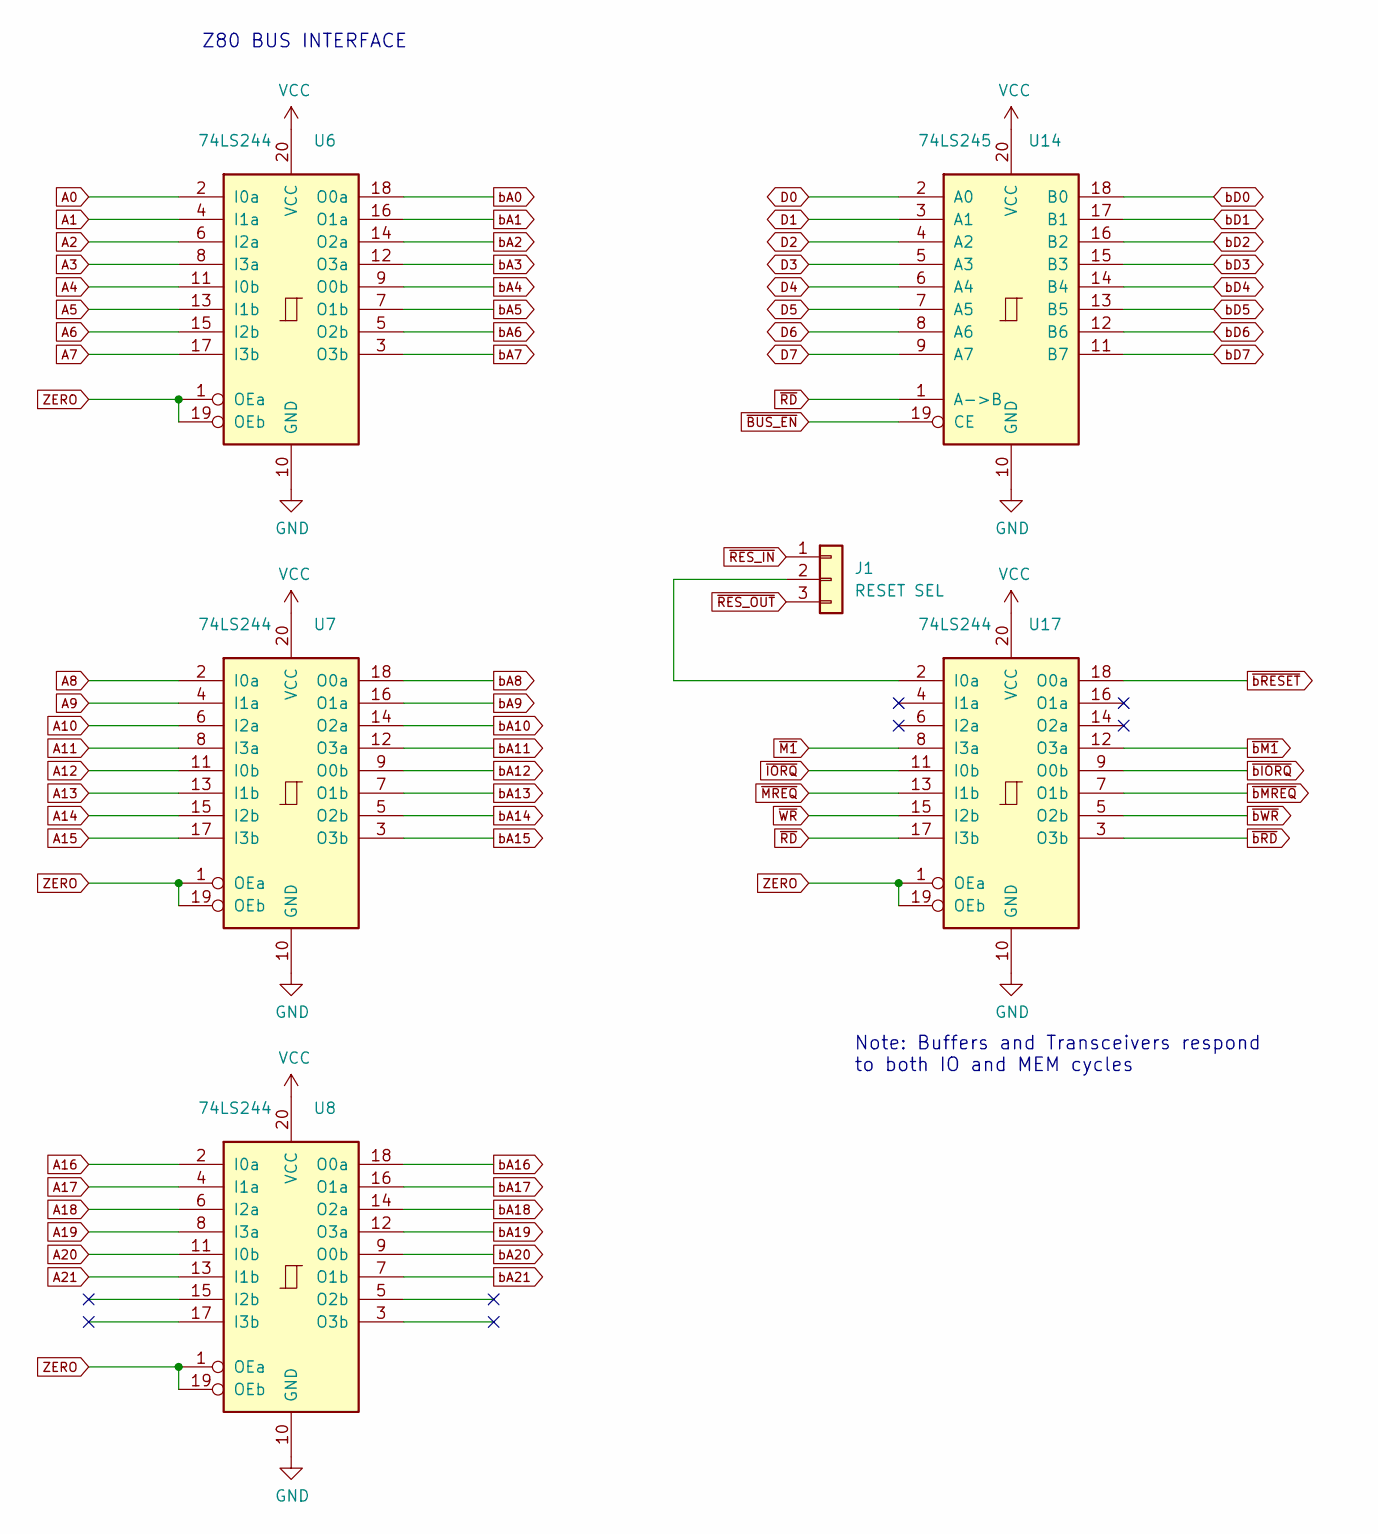
[picture p433: schematic buffers.kicad_sch]

Parts:
J1: RESET SEL; PinHeader_1x03_P2.54mm_Vertical
U6, U7, U8, U17: 74LS244; DIP-20_W7.62mm
U14: 74LS245; DIP-20_W7.62mm

Connections:
A0: U6.2 (I0a); also elsewhere on the board
A1: U6.4 (I1a); also elsewhere on the board
A2: U6.6 (I2a); also elsewhere on the board
A3: U6.8 (I3a); also elsewhere on the board
A4: U6.11 (I0b); also elsewhere on the board
A5: U6.13 (I1b); also elsewhere on the board
A6: U6.15 (I2b); also elsewhere on the board
A7: U6.17 (I3b); also elsewhere on the board
A8: U7.2 (I0a); also elsewhere on the board
A9: U7.4 (I1a); also elsewhere on the board
A10: U7.6 (I2a); also elsewhere on the board
A11: U7.8 (I3a); also elsewhere on the board
A12: U7.11 (I0b); also elsewhere on the board
A13: U7.13 (I1b); also elsewhere on the board
A14: U7.15 (I2b); also elsewhere on the board
A15: U7.17 (I3b); also elsewhere on the board
A16: U8.2 (I0a); also elsewhere on the board
A17: U8.4 (I1a); also elsewhere on the board
A18: U8.6 (I2a); also elsewhere on the board
A19: U8.8 (I3a); also elsewhere on the board
A20: U8.11 (I0b); also elsewhere on the board
A21: U8.13 (I1b); also elsewhere on the board
D0: U14.2 (A0); also elsewhere on the board
D1: U14.3 (A1); also elsewhere on the board
D2: U14.4 (A2); also elsewhere on the board
D3: U14.5 (A3); also elsewhere on the board
D4: U14.6 (A4); also elsewhere on the board
D5: U14.7 (A5); also elsewhere on the board
D6: U14.8 (A6); also elsewhere on the board
D7: U14.9 (A7); also elsewhere on the board
GND: U6.10 (GND), U7.10 (GND), U8.10 (GND), U14.10 (GND), U17.10 (GND); also elsewhere on the board
unnamed: J1.2, U17.2 (I0a)
VCC: U6.20 (VCC), U7.20 (VCC), U8.20 (VCC), U14.20 (VCC), U17.20 (VCC); also elsewhere on the board
ZERO: U6.1 (OEa), U6.19 (OEb), U7.1 (OEa), U7.19 (OEb), U8.1 (OEa), U8.19 (OEb), U17.1 (OEa), U17.19 (OEb); also elsewhere on the board
bA0: U6.18 (O0a); also elsewhere on the board
bA1: U6.16 (O1a); also elsewhere on the board
bA2: U6.14 (O2a); also elsewhere on the board
bA3: U6.12 (O3a); also elsewhere on the board
bA4: U6.9 (O0b); also elsewhere on the board
bA5: U6.7 (O1b); also elsewhere on the board
bA6: U6.5 (O2b); also elsewhere on the board
bA7: U6.3 (O3b); also elsewhere on the board
bA8: U7.18 (O0a); also elsewhere on the board
bA9: U7.16 (O1a); also elsewhere on the board
bA10: U7.14 (O2a); also elsewhere on the board
bA11: U7.12 (O3a); also elsewhere on the board
bA12: U7.9 (O0b); also elsewhere on the board
bA13: U7.7 (O1b); also elsewhere on the board
bA14: U7.5 (O2b); also elsewhere on the board
bA15: U7.3 (O3b); also elsewhere on the board
bA16: U8.18 (O0a); also elsewhere on the board
bA17: U8.16 (O1a); also elsewhere on the board
bA18: U8.14 (O2a); also elsewhere on the board
bA19: U8.12 (O3a); also elsewhere on the board
bA20: U8.9 (O0b); also elsewhere on the board
bA21: U8.7 (O1b); also elsewhere on the board
bD0: U14.18 (B0); also elsewhere on the board
bD1: U14.17 (B1); also elsewhere on the board
bD2: U14.16 (B2); also elsewhere on the board
bD3: U14.15 (B3); also elsewhere on the board
bD4: U14.14 (B4); also elsewhere on the board
bD5: U14.13 (B5); also elsewhere on the board
bD6: U14.12 (B6); also elsewhere on the board
bD7: U14.11 (B7); also elsewhere on the board
~BUS_EN: U14.19 (CE); also elsewhere on the board
~IORQ: U17.11 (I0b); also elsewhere on the board
~M1: U17.8 (I3a); also elsewhere on the board
~MREQ: U17.13 (I1b); also elsewhere on the board
~RD: U14.1 (A->B), U17.17 (I3b); also elsewhere on the board
~RES_IN: J1.1; also elsewhere on the board
~RES_OUT: J1.3; also elsewhere on the board
~WR: U17.15 (I2b); also elsewhere on the board
~bIORQ: U17.9 (O0b); also elsewhere on the board
~bM1: U17.12 (O3a); also elsewhere on the board
~bMREQ: U17.7 (O1b); also elsewhere on the board
~bRD: U17.3 (O3b); also elsewhere on the board
~bRESET: U17.18 (O0a); also elsewhere on the board
~bWR: U17.5 (O2b); also elsewhere on the board

Notes on the sheet:
Z80 BUS INTERFACE
Note: Buffers and Transceivers respond to both IO and MEM cycles

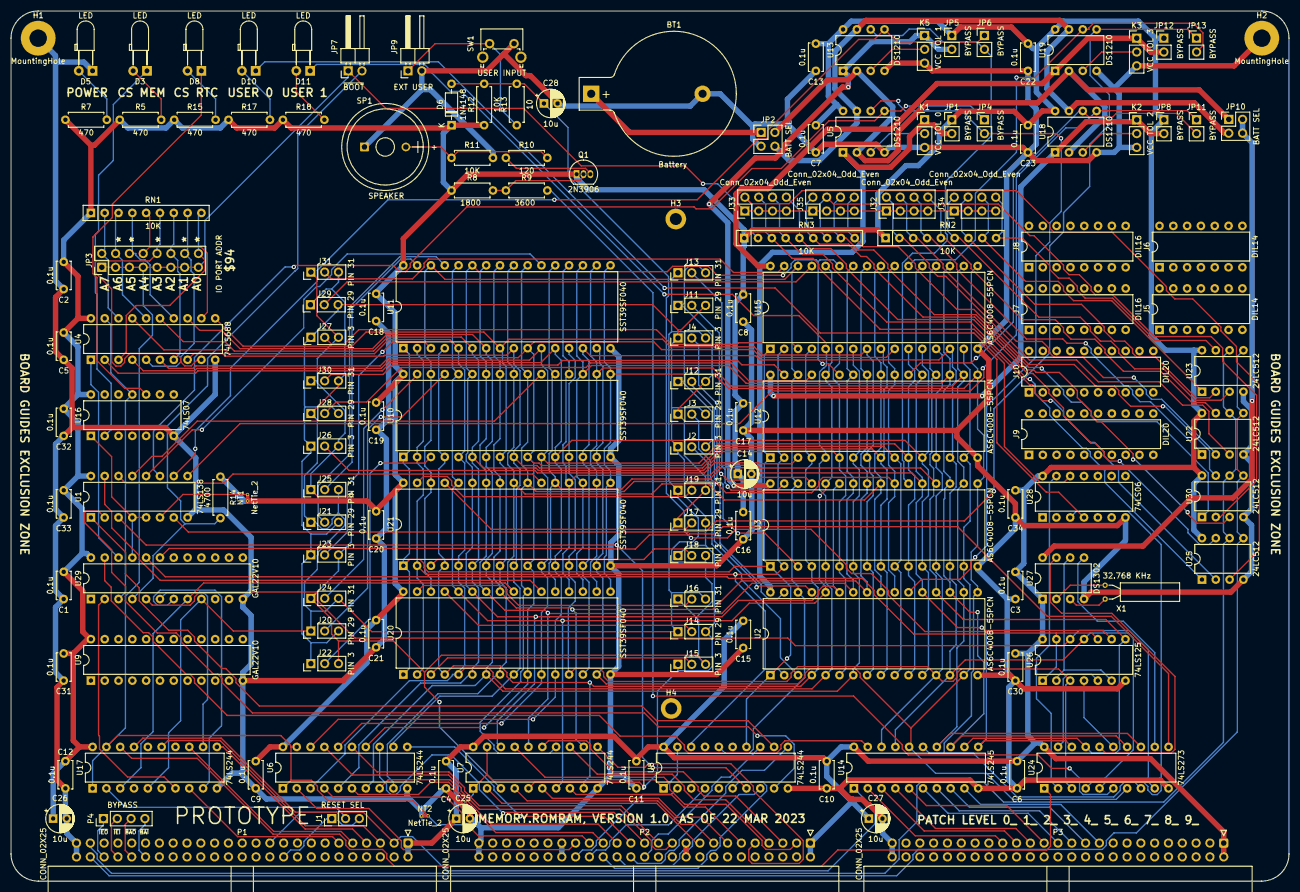
[picture p434: board memory.ROMRAM.kicad_pcb from above]

Board: 2 copper layers, 235.0 x 160.0 mm, 150 parts (0 on the bottom side), 190 nets.
