lynchaj/duodyne/!Development/16 input-output.VDCENET, V1.0/PQFP-100-Adapter/PQFP-100-Adapter.kicad_pcb

## KiCad design !Development/16 input-output.VDCENET, V1.0/PQFP-100-Adapter/PQFP-100-Adapter.kicad_pcb (2024-01-15)

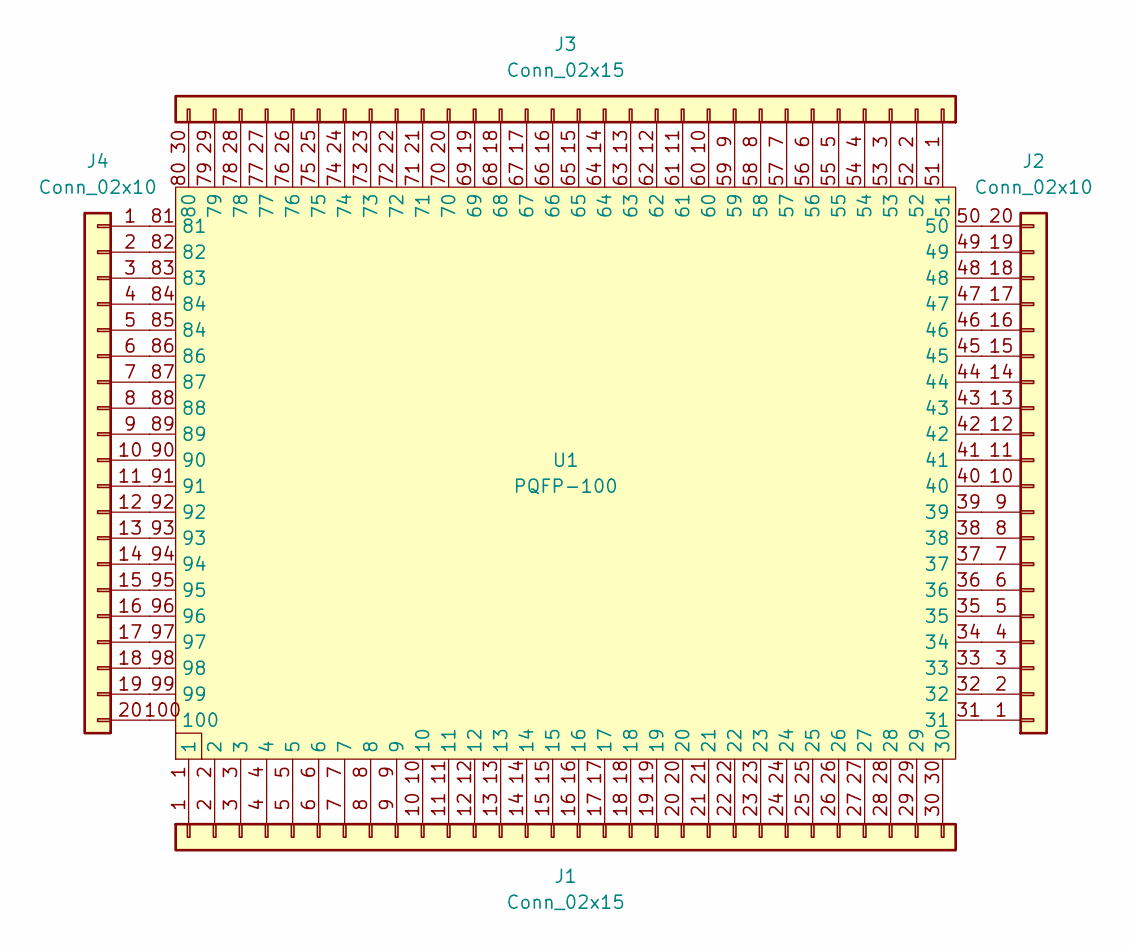
[picture p435: schematic PQFP-100-Adapter.kicad_sch]

Parts:
J1, J3: Conn_02x15; PinHeader_2x15_P2.54mm_Vertical
J2, J4: Conn_02x10; PinHeader_2x10_P2.54mm_Vertical
U1: PQFP-100; PQFP-100_14x20mm_P0.65mm

Connections:
unnamed: J1.1, U1.1
unnamed: J1.2, U1.2
unnamed: J1.3, U1.3
unnamed: J1.4, U1.4
unnamed: J1.5, U1.5
unnamed: J1.6, U1.6
unnamed: J1.7, U1.7
unnamed: J1.8, U1.8
unnamed: J1.9, U1.9
unnamed: J1.10, U1.10
unnamed: J1.11, U1.11
unnamed: J1.12, U1.12
unnamed: J1.13, U1.13
unnamed: J1.14, U1.14
unnamed: J1.15, U1.15
unnamed: J1.16, U1.16
unnamed: J1.17, U1.17
unnamed: J1.18, U1.18
unnamed: J1.19, U1.19
unnamed: J1.20, U1.20
unnamed: J1.21, U1.21
unnamed: J1.22, U1.22
unnamed: J1.23, U1.23
unnamed: J1.24, U1.24
unnamed: J1.25, U1.25
unnamed: J1.26, U1.26
unnamed: J1.27, U1.27
unnamed: J1.28, U1.28
unnamed: J1.29, U1.29
unnamed: J1.30, U1.30
unnamed: J2.1, U1.31
unnamed: J2.2, U1.32
unnamed: J2.3, U1.33
unnamed: J2.4, U1.34
unnamed: J2.5, U1.35
unnamed: J2.6, U1.36
unnamed: J2.7, U1.37
unnamed: J2.8, U1.38
unnamed: J2.9, U1.39
unnamed: J2.10, U1.40
unnamed: J2.11, U1.41
unnamed: J2.12, U1.42
unnamed: J2.13, U1.43
unnamed: J2.14, U1.44
unnamed: J2.15, U1.45
unnamed: J2.16, U1.46
unnamed: J2.17, U1.47
unnamed: J2.18, U1.48
unnamed: J2.19, U1.49
unnamed: J2.20, U1.50
unnamed: J3.1, U1.51
unnamed: J3.2, U1.52
unnamed: J3.3, U1.53
unnamed: J3.4, U1.54
unnamed: J3.5, U1.55
unnamed: J3.6, U1.56
unnamed: J3.7, U1.57
unnamed: J3.8, U1.58
unnamed: J3.9, U1.59
unnamed: J3.10, U1.60
unnamed: J3.11, U1.61
unnamed: J3.12, U1.62
unnamed: J3.13, U1.63
unnamed: J3.14, U1.64
unnamed: J3.15, U1.65
unnamed: J3.16, U1.66
unnamed: J3.17, U1.67
unnamed: J3.18, U1.68
unnamed: J3.19, U1.69
unnamed: J3.20, U1.70
unnamed: J3.21, U1.71
unnamed: J3.22, U1.72
unnamed: J3.23, U1.73
unnamed: J3.24, U1.74
unnamed: J3.25, U1.75
unnamed: J3.26, U1.76
unnamed: J3.27, U1.77
unnamed: J3.28, U1.78
unnamed: J3.29, U1.79
unnamed: J3.30, U1.80
unnamed: J4.1, U1.81
unnamed: J4.2, U1.82
unnamed: J4.3, U1.83
unnamed: J4.4, U1.84
unnamed: J4.5, U1.85 (84)
unnamed: J4.6, U1.86
unnamed: J4.7, U1.87
unnamed: J4.8, U1.88
unnamed: J4.9, U1.89
unnamed: J4.10, U1.90
unnamed: J4.11, U1.91
unnamed: J4.12, U1.92
unnamed: J4.13, U1.93
unnamed: J4.14, U1.94
unnamed: J4.15, U1.95
unnamed: J4.16, U1.96
unnamed: J4.17, U1.97
unnamed: J4.18, U1.98
unnamed: J4.19, U1.99
unnamed: J4.20, U1.100

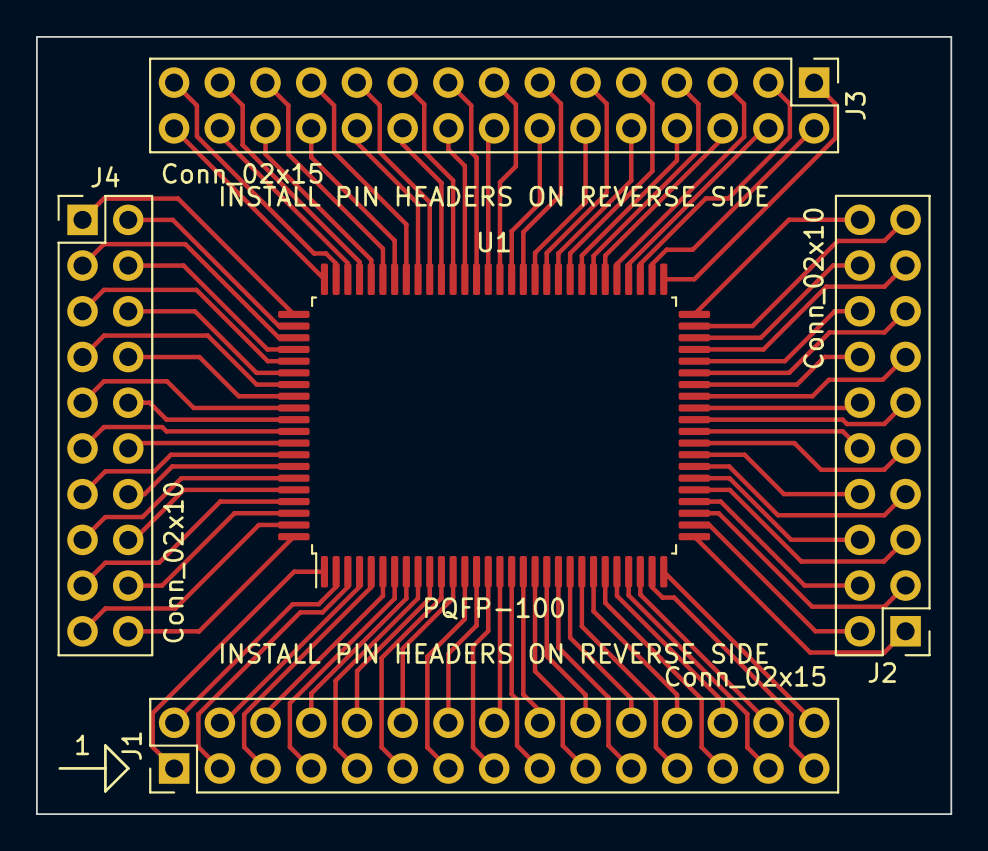
[picture p436: board PQFP-100-Adapter.kicad_pcb from above]

Board: 2 copper layers, 50.8 x 43.2 mm, 5 parts (0 on the bottom side), 100 nets.
