lynchaj/duodyne/!Retired/03 processor.Z80, V1.0/processor.Z80.kicad_pcb

## KiCad design !Retired/03 processor.Z80, V1.0/processor.Z80.kicad_pcb (2023-09-14, an earlier design)

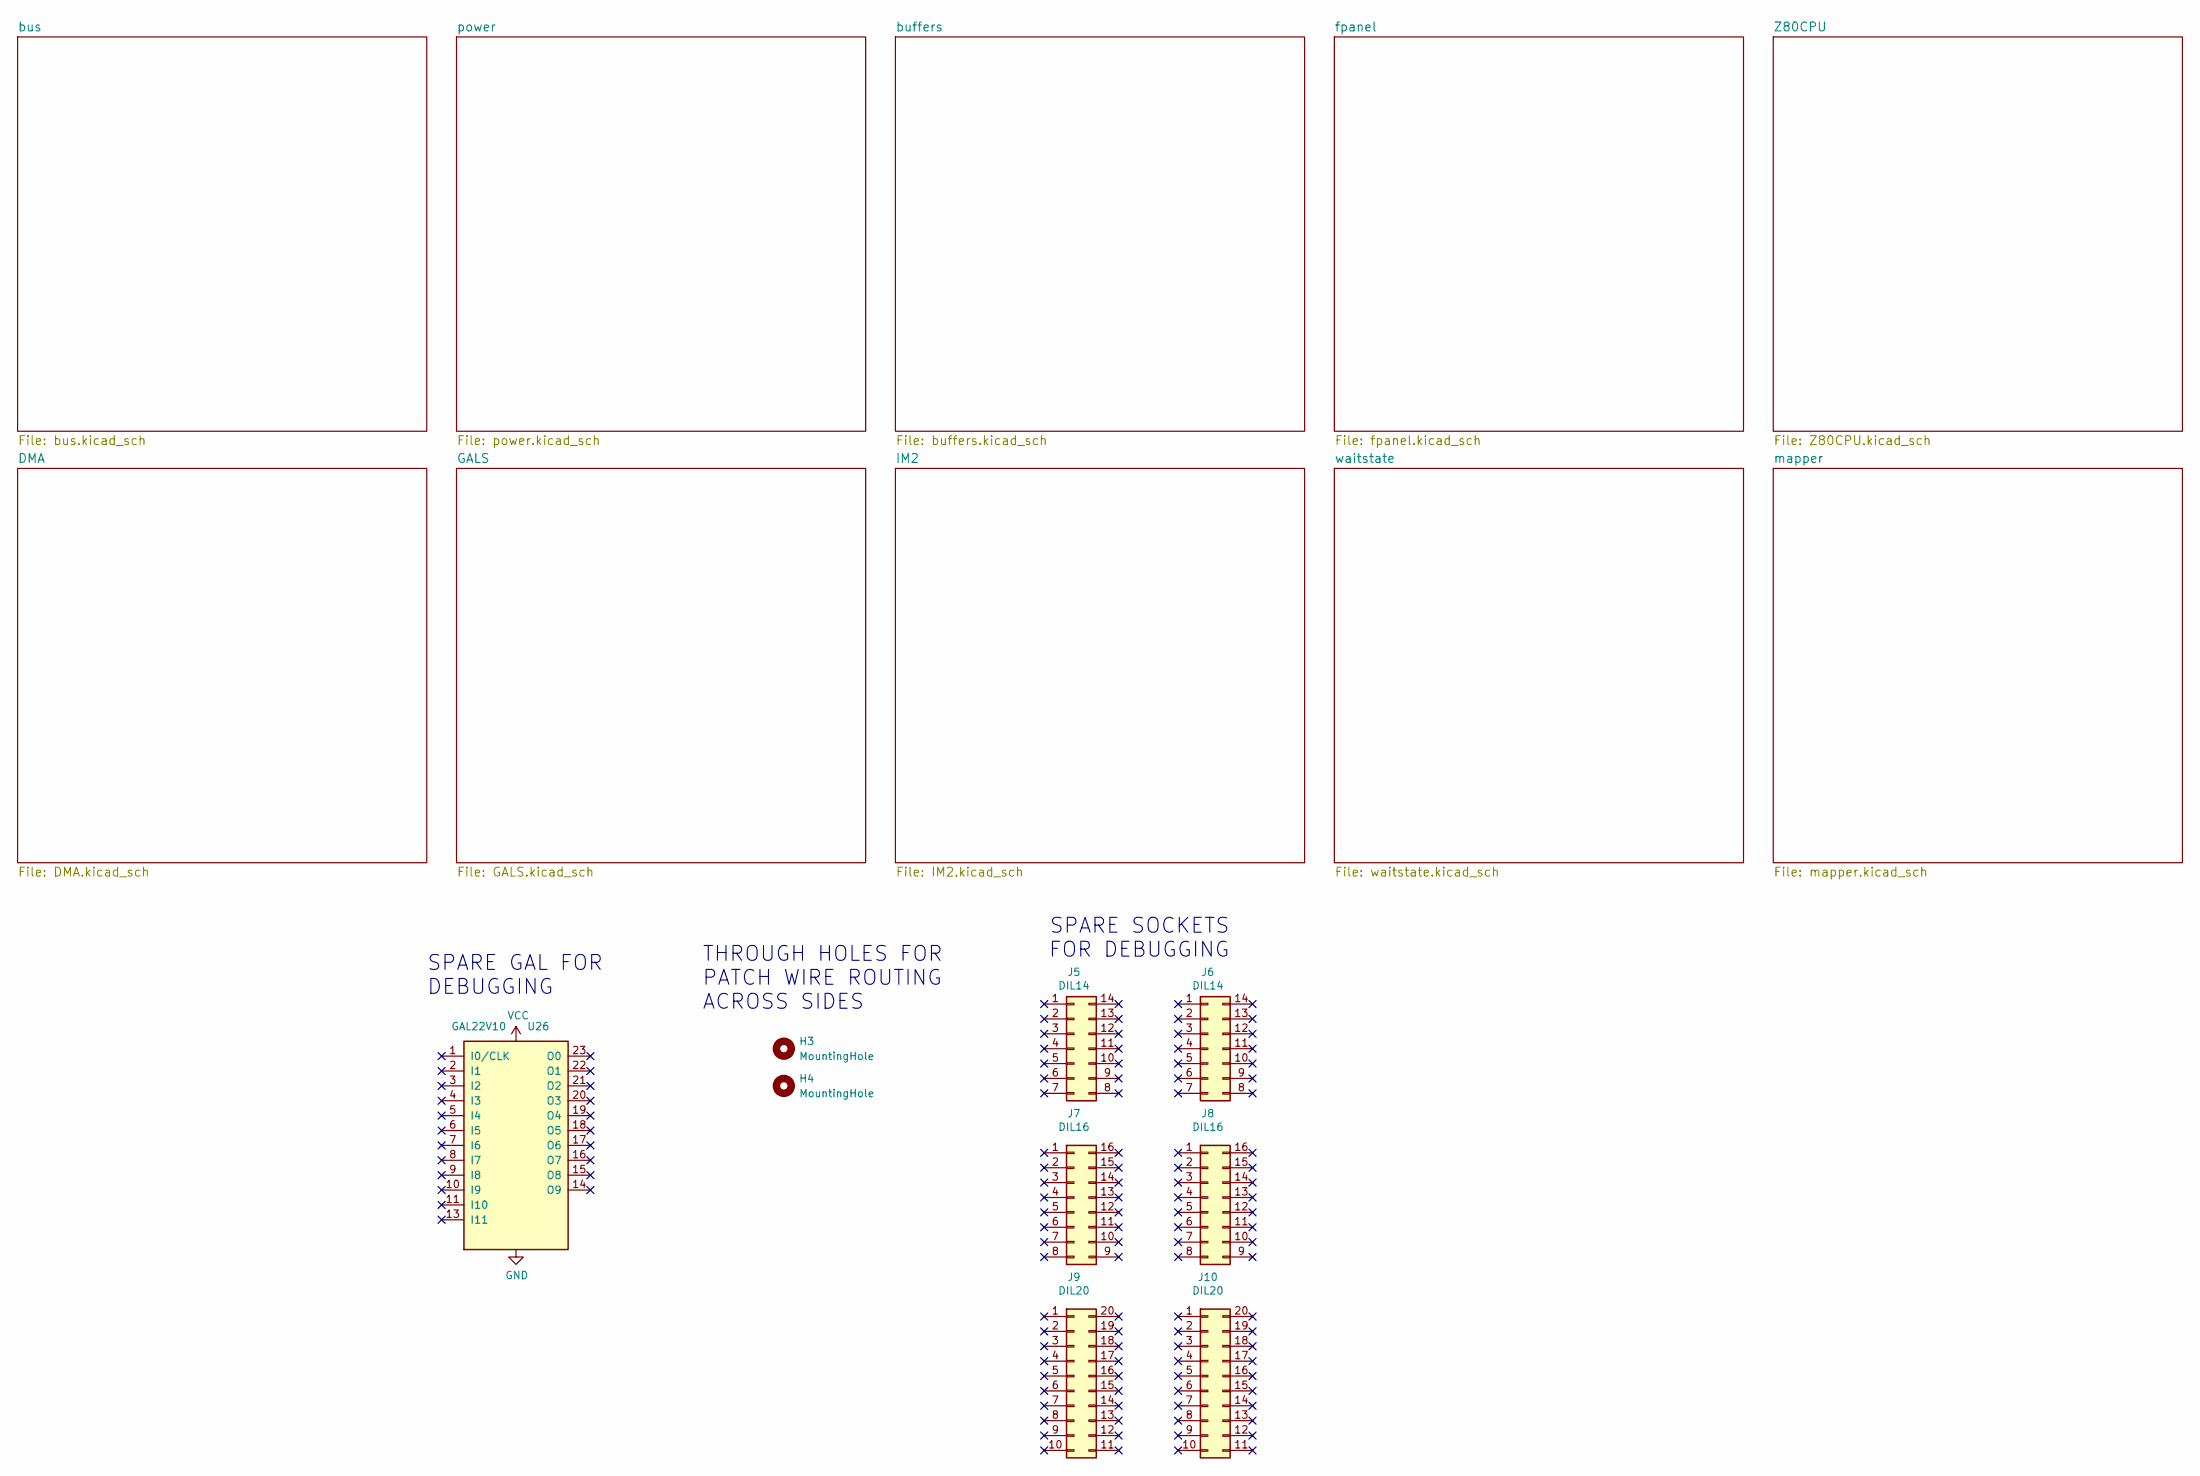
[picture p437: schematic processor.Z80.kicad_sch]

Parts:
H3, H4: MountingHole; MountingHole_2.2mm_M2_DIN965_Pad
J5, J6: DIL14; DIP-14_W7.62mm
J7, J8: DIL16; DIP-16_W7.62mm
J9, J10: DIL20; DIP-20_W7.62mm
U26: GAL22V10; DIP-24_W7.62mm

Connections:
GND: U26.12 (GND); also elsewhere on the board
VCC: U26.24 (VCC); also elsewhere on the board

Notes on the sheet:
THROUGH HOLES FOR PATCH WIRE ROUTING ACROSS SIDES
SPARE GAL FOR DEBUGGING
SPARE SOCKETS FOR DEBUGGING
