lynchaj/duodyne/!Retired/03 processor.Z80, V1.0/processor.Z80.kicad_pcb

## KiCad design !Retired/03 processor.Z80, V1.0/processor.Z80.kicad_pcb (continued)

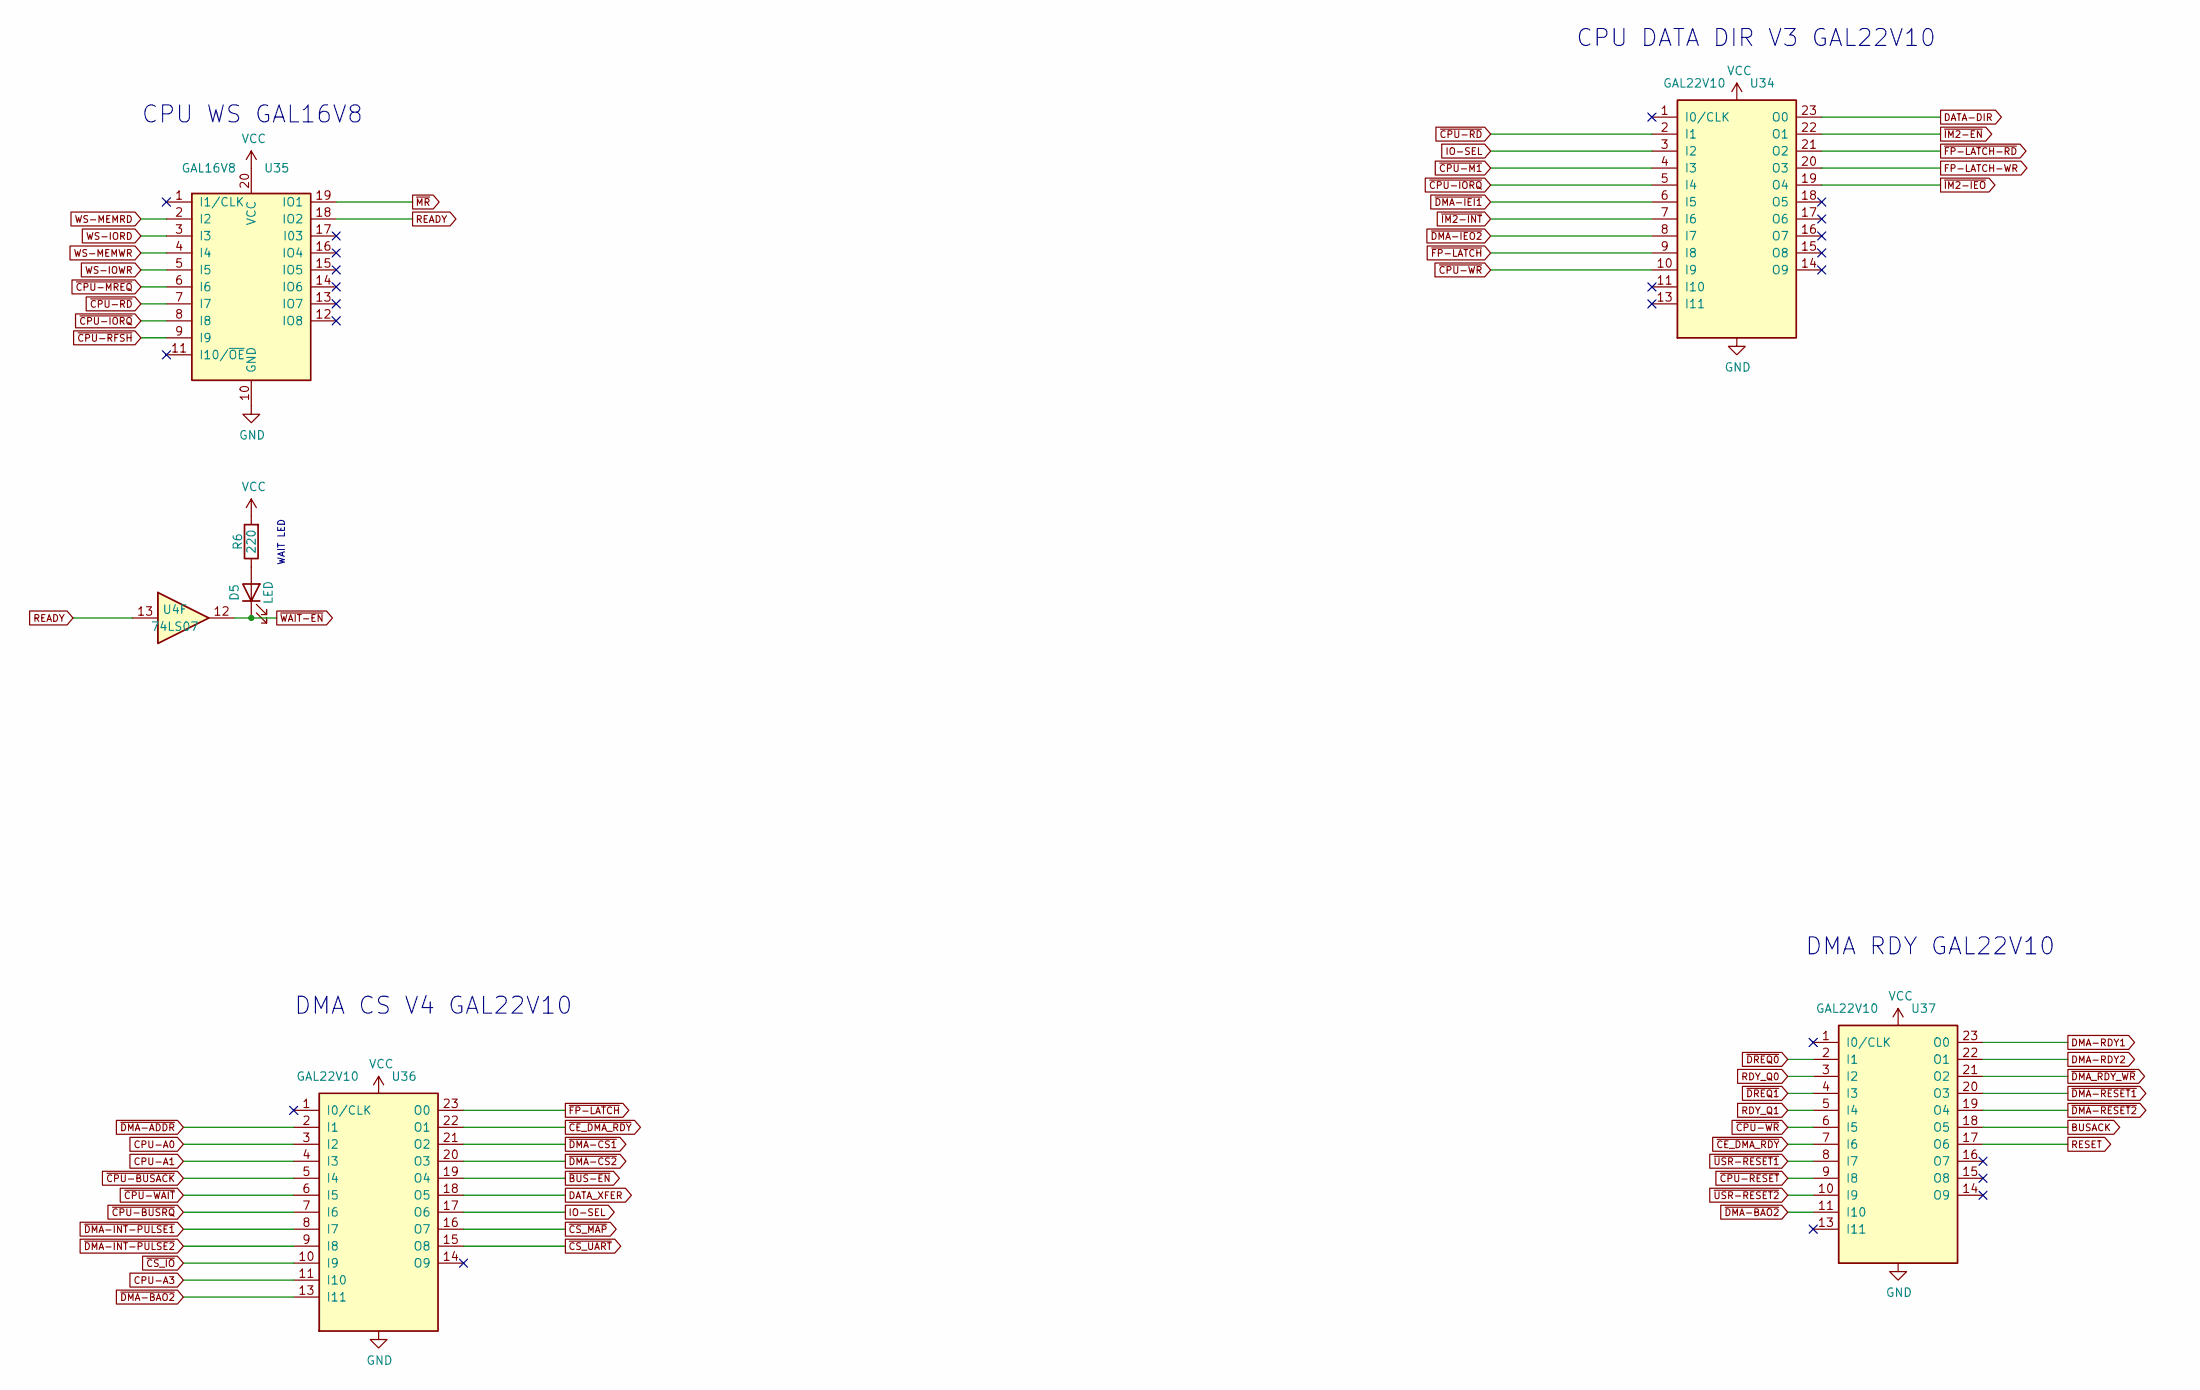
[picture p438: schematic GALS.kicad_sch]

Parts:
D5: LED; LED_D3.0mm_Horizontal_O3.81mm_Z2.0mm
R6: 220; R_Axial_DIN0207_L6.3mm_D2.5mm_P7.62mm_Horizontal
U4: 74LS07; DIP-14_W7.62mm
U34, U36, U37: GAL22V10; DIP-24_W7.62mm
U35: GAL16V8; DIP-20_W7.62mm

Connections:
BUSACK: U37.18 (O5); also elsewhere on the board
CPU-A0: U36.3 (I2); also elsewhere on the board
CPU-A1: U36.4 (I3); also elsewhere on the board
CPU-A3: U36.11 (I10); also elsewhere on the board
DATA-DIR: U34.23 (O0); also elsewhere on the board
DATA_XFER: U36.18 (O5); also elsewhere on the board
DMA-RDY1: U37.23 (O0); also elsewhere on the board
DMA-RDY2: U37.22 (O1); also elsewhere on the board
FP-LATCH-WR: U34.20 (O3); also elsewhere on the board
GND: U34.12 (GND), U35.10 (GND), U36.12 (GND), U37.12 (GND); also elsewhere on the board
IO-SEL: U34.3 (I2), U36.17 (O6)
unnamed: D5.2 (A), R6.1
RDY_Q0: U37.3 (I2); also elsewhere on the board
RDY_Q1: U37.5 (I4); also elsewhere on the board
READY: U4.13, U35.18 (IO2)
RESET: U37.17 (O6); also elsewhere on the board
VCC: R6.2, U34.24 (VCC), U35.20 (VCC), U36.24 (VCC), U37.24 (VCC); also elsewhere on the board
WS-IORD: U35.3 (I3); also elsewhere on the board
WS-IOWR: U35.5 (I5); also elsewhere on the board
WS-MEMRD: U35.2 (I2); also elsewhere on the board
WS-MEMWR: U35.4 (I4); also elsewhere on the board
~BUS-EN: U36.19 (O4); also elsewhere on the board
~CE_DMA_RDY: U36.22 (O1), U37.7 (I6)
~CPU-BUSACK: U36.5 (I4); also elsewhere on the board
~CPU-BUSRQ: U36.7 (I6); also elsewhere on the board
~CPU-IORQ: U34.5 (I4), U35.8 (I8); also elsewhere on the board
~CPU-M1: U34.4 (I3); also elsewhere on the board
~CPU-MREQ: U35.6 (I6); also elsewhere on the board
~CPU-RD: U34.2 (I1), U35.7 (I7); also elsewhere on the board
~CPU-RESET: U37.9 (I8); also elsewhere on the board
~CPU-RFSH: U35.9 (I9); also elsewhere on the board
~CPU-WAIT: U36.6 (I5); also elsewhere on the board
~CPU-WR: U34.10 (I9), U37.6 (I5); also elsewhere on the board
~CS_IO: U36.10 (I9); also elsewhere on the board
~CS_MAP: U36.16 (O7); also elsewhere on the board
~CS_UART: U36.15 (O8); also elsewhere on the board
~DMA-ADDR: U36.2 (I1); also elsewhere on the board
~DMA-BAO2: U36.13 (I11), U37.11 (I10); also elsewhere on the board
~DMA-CS1: U36.21 (O2); also elsewhere on the board
~DMA-CS2: U36.20 (O3); also elsewhere on the board
~DMA-IEI1: U34.6 (I5); also elsewhere on the board
~DMA-IEO2: U34.8 (I7); also elsewhere on the board
~DMA-INT-PULSE1: U36.8 (I7); also elsewhere on the board
~DMA-INT-PULSE2: U36.9 (I8); also elsewhere on the board
~DMA-RESET1: U37.20 (O3); also elsewhere on the board
~DMA-RESET2: U37.19 (O4); also elsewhere on the board
~DMA_RDY_WR: U37.21 (O2); also elsewhere on the board
~DREQ0: U37.2 (I1); also elsewhere on the board
~DREQ1: U37.4 (I3); also elsewhere on the board
~FP-LATCH-RD: U34.21 (O2); also elsewhere on the board
~FP-LATCH: U34.9 (I8), U36.23 (O0)
~IM2-EN: U34.22 (O1); also elsewhere on the board
~IM2-IEO: U34.19 (O4); also elsewhere on the board
~IM2-INT: U34.7 (I6); also elsewhere on the board
~MR: U35.19 (IO1); also elsewhere on the board
~USR-RESET1: U37.8 (I7); also elsewhere on the board
~USR-RESET2: U37.10 (I9); also elsewhere on the board
~WAIT-EN: D5.1 (K), U4.12; also elsewhere on the board

Notes on the sheet:
DMA CS V4 GAL22V10
DMA RDY GAL22V10
CPU WS GAL16V8
CPU DATA DIR V3 GAL22V10
WAIT LED

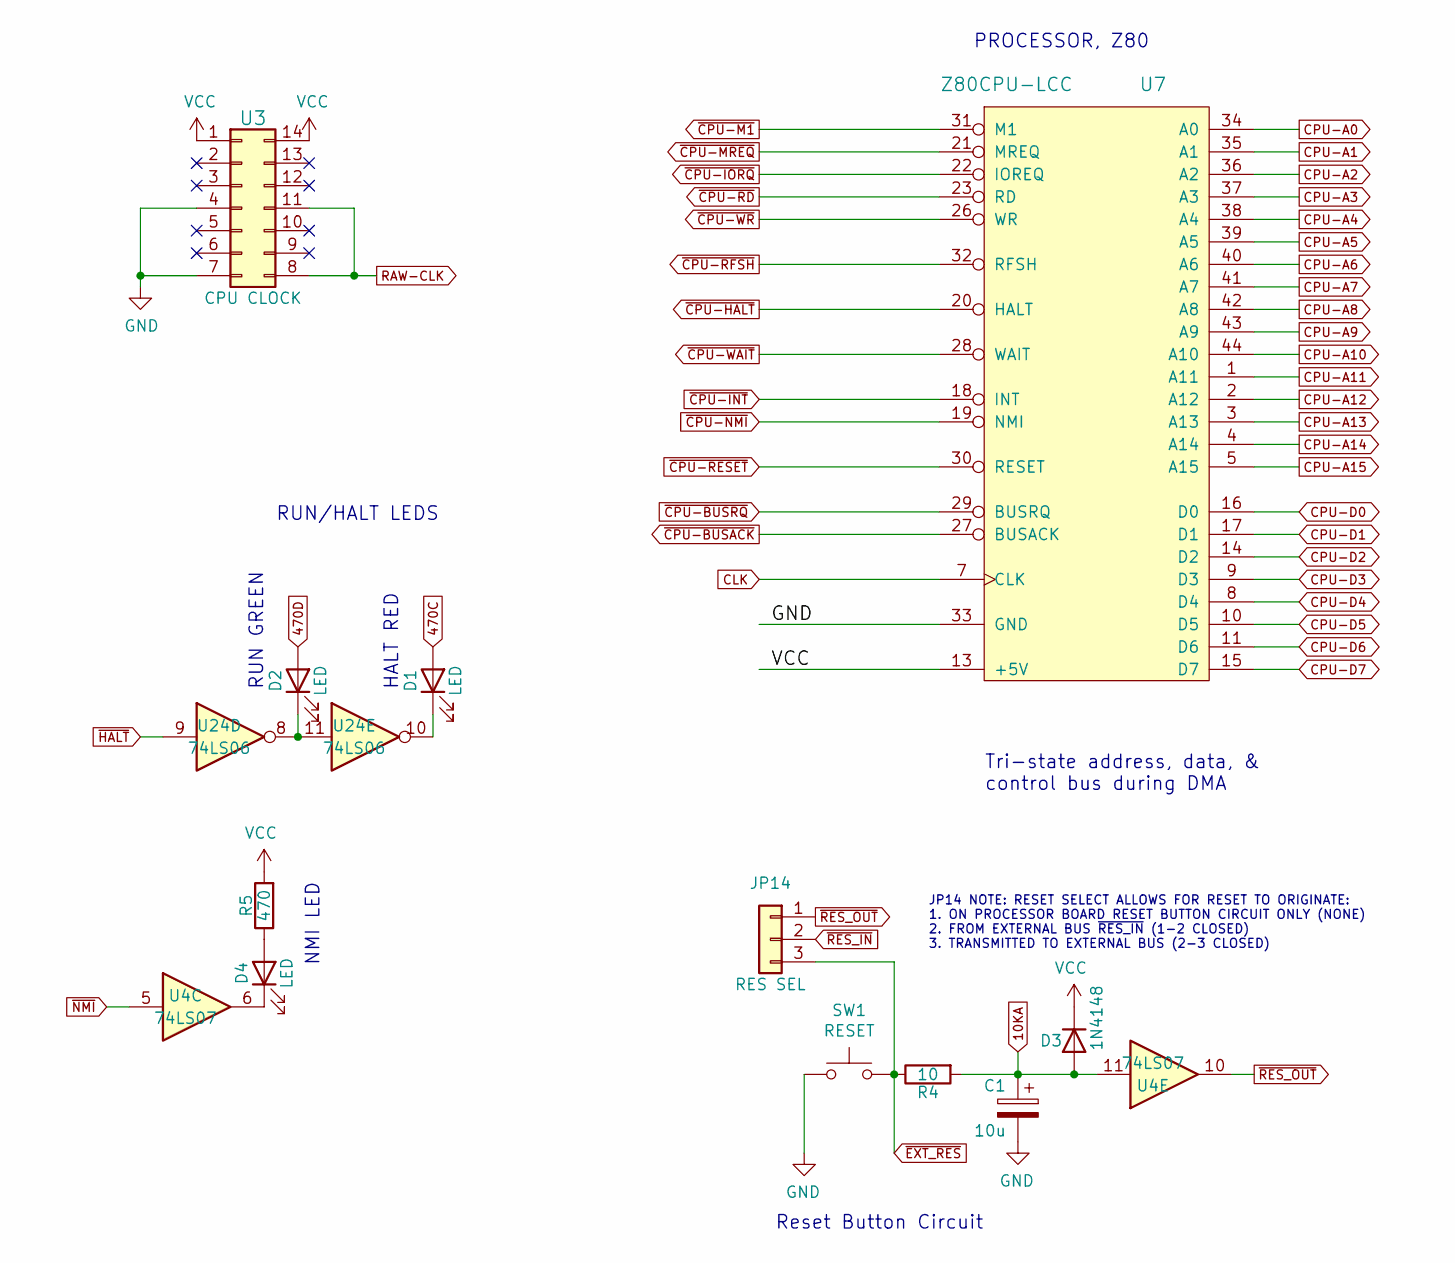
[picture p439: schematic Z80CPU.kicad_sch]

Parts:
C1: 10u; CP_Radial_D5.0mm_P2.50mm
D1, D2, D4: LED; LED_D3.0mm_Horizontal_O3.81mm_Z2.0mm
D3: 1N4148; D_DO-35_SOD27_P7.62mm_Horizontal
JP14: RES SEL; PinHeader_1x03_P2.54mm_Vertical
R4: 10; R_Axial_DIN0207_L6.3mm_D2.5mm_P7.62mm_Horizontal
R5: 470; R_Axial_DIN0207_L6.3mm_D2.5mm_P7.62mm_Horizontal
SW1: RESET; SW_Tactile_SPST_Angled_PTS645Vx58-2LFS
U3: CPU CLOCK; DIP-14_W7.62mm
U4: 74LS07; DIP-14_W7.62mm
U7: Z80CPU-LCC; PLCC-44_THT-Socket; Manufacturer_Part_Number Z84C00
U24: 74LS06

Connections:
10KA: C1.1, D3.2 (A), R4.2, U4.11; also elsewhere on the board
470C: D1.2 (A); also elsewhere on the board
470D: D2.2 (A); also elsewhere on the board
CLK: U7.7 (CLK); also elsewhere on the board
CPU-A0: U7.34 (A0); also elsewhere on the board
CPU-A1: U7.35 (A1); also elsewhere on the board
CPU-A2: U7.36 (A2); also elsewhere on the board
CPU-A3: U7.37 (A3); also elsewhere on the board
CPU-A4: U7.38 (A4); also elsewhere on the board
CPU-A5: U7.39 (A5); also elsewhere on the board
CPU-A6: U7.40 (A6); also elsewhere on the board
CPU-A7: U7.41 (A7); also elsewhere on the board
CPU-A8: U7.42 (A8); also elsewhere on the board
CPU-A9: U7.43 (A9); also elsewhere on the board
CPU-A10: U7.44 (A10); also elsewhere on the board
CPU-A11: U7.1 (A11); also elsewhere on the board
CPU-A12: U7.2 (A12); also elsewhere on the board
CPU-A13: U7.3 (A13); also elsewhere on the board
CPU-A14: U7.4 (A14); also elsewhere on the board
CPU-A15: U7.5 (A15); also elsewhere on the board
CPU-D0: U7.16 (D0); also elsewhere on the board
CPU-D1: U7.17 (D1); also elsewhere on the board
CPU-D2: U7.14 (D2); also elsewhere on the board
CPU-D3: U7.9 (D3); also elsewhere on the board
CPU-D4: U7.8 (D4); also elsewhere on the board
CPU-D5: U7.10 (D5); also elsewhere on the board
CPU-D6: U7.11 (D6); also elsewhere on the board
CPU-D7: U7.15 (D7); also elsewhere on the board
GND: C1.2, SW1.2, U3.4, U3.7, U7.33 (GND); also elsewhere on the board
unnamed: D1.1 (K), U24.10
unnamed: D2.1 (K), U24.8, U24.11
unnamed: D4.1 (K), U4.6
unnamed: D4.2 (A), R5.1
RAW-CLK: U3.8, U3.11; also elsewhere on the board
VCC: D3.1 (K), R5.2, U3.1, U3.14, U7.13 (+5V); also elsewhere on the board
~CPU-BUSACK: U7.27 (BUSACK); also elsewhere on the board
~CPU-BUSRQ: U7.29 (BUSRQ); also elsewhere on the board
~CPU-HALT: U7.20 (HALT); also elsewhere on the board
~CPU-INT: U7.18 (INT); also elsewhere on the board
~CPU-IORQ: U7.22 (IOREQ); also elsewhere on the board
~CPU-M1: U7.31 (M1); also elsewhere on the board
~CPU-MREQ: U7.21 (MREQ); also elsewhere on the board
~CPU-NMI: U7.19 (NMI); also elsewhere on the board
~CPU-RD: U7.23 (RD); also elsewhere on the board
~CPU-RESET: U7.30 (RESET); also elsewhere on the board
~CPU-RFSH: U7.32 (RFSH); also elsewhere on the board
~CPU-WAIT: U7.28 (WAIT); also elsewhere on the board
~CPU-WR: U7.26 (WR); also elsewhere on the board
~EXT_RES: JP14.3, R4.1, SW1.1; also elsewhere on the board
~HALT: U24.9; also elsewhere on the board
~NMI: U4.5; also elsewhere on the board
~RES_IN: JP14.2; also elsewhere on the board
~RES_OUT: JP14.1, U4.10; also elsewhere on the board

Notes on the sheet:
RUN GREEN
JP14 NOTE: RESET SELECT ALLOWS FOR RESET TO ORIGINATE: 1. ON PROCESSOR BOARD RESET BUTTON CIRCUIT ONLY (NONE) 2. FROM EXTERNAL BUS ~{RES_IN} (1-2 CLOSED) 3. TRANSMITTED TO EXTERNAL BUS (2-3 CLOSED)
HALT RED
Reset Button Circuit
NMI LED
PROCESSOR, Z80
Tri-state address, data, & control bus during DMA
RUN/HALT LEDS

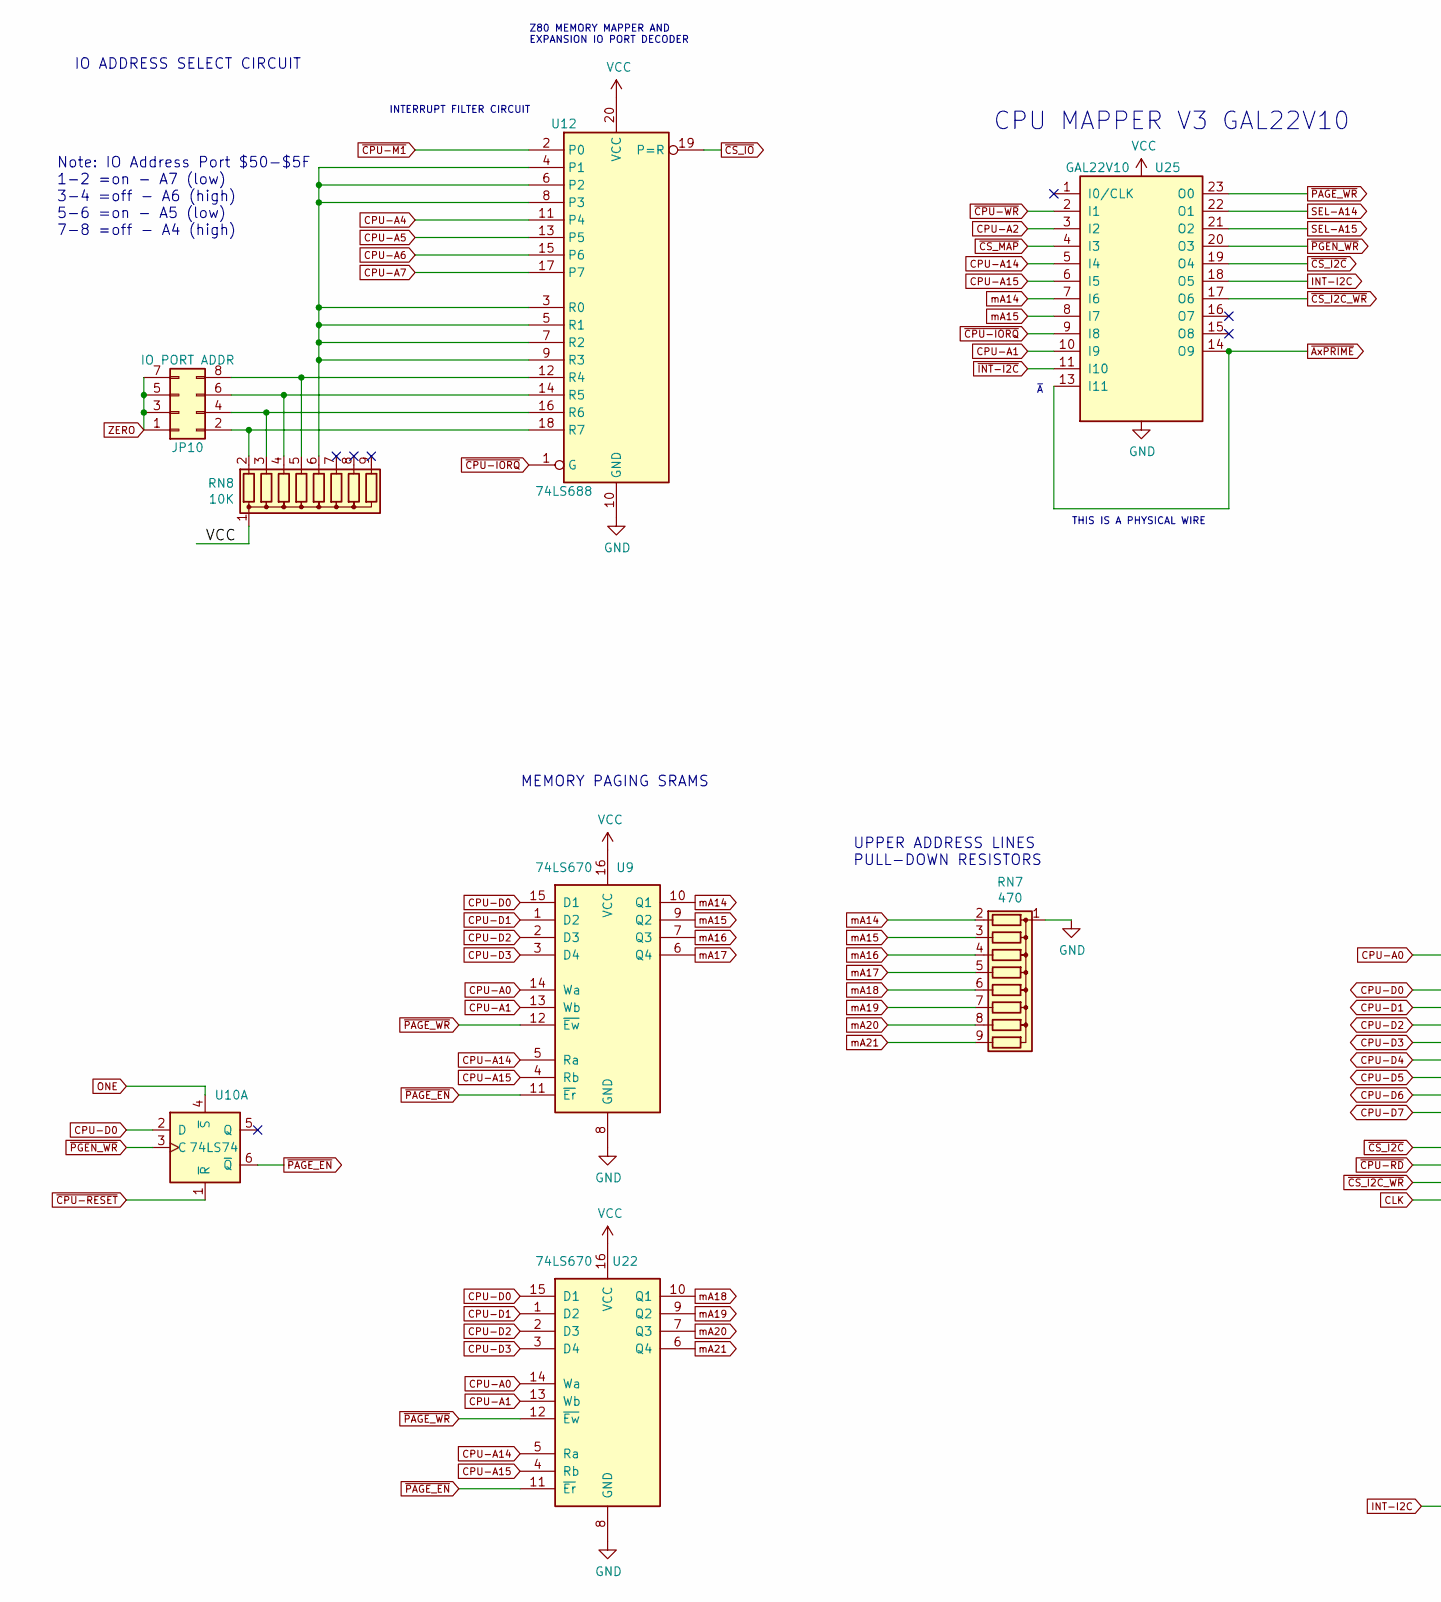
[picture p440: schematic mapper.kicad_sch, part in row 1, column 1]

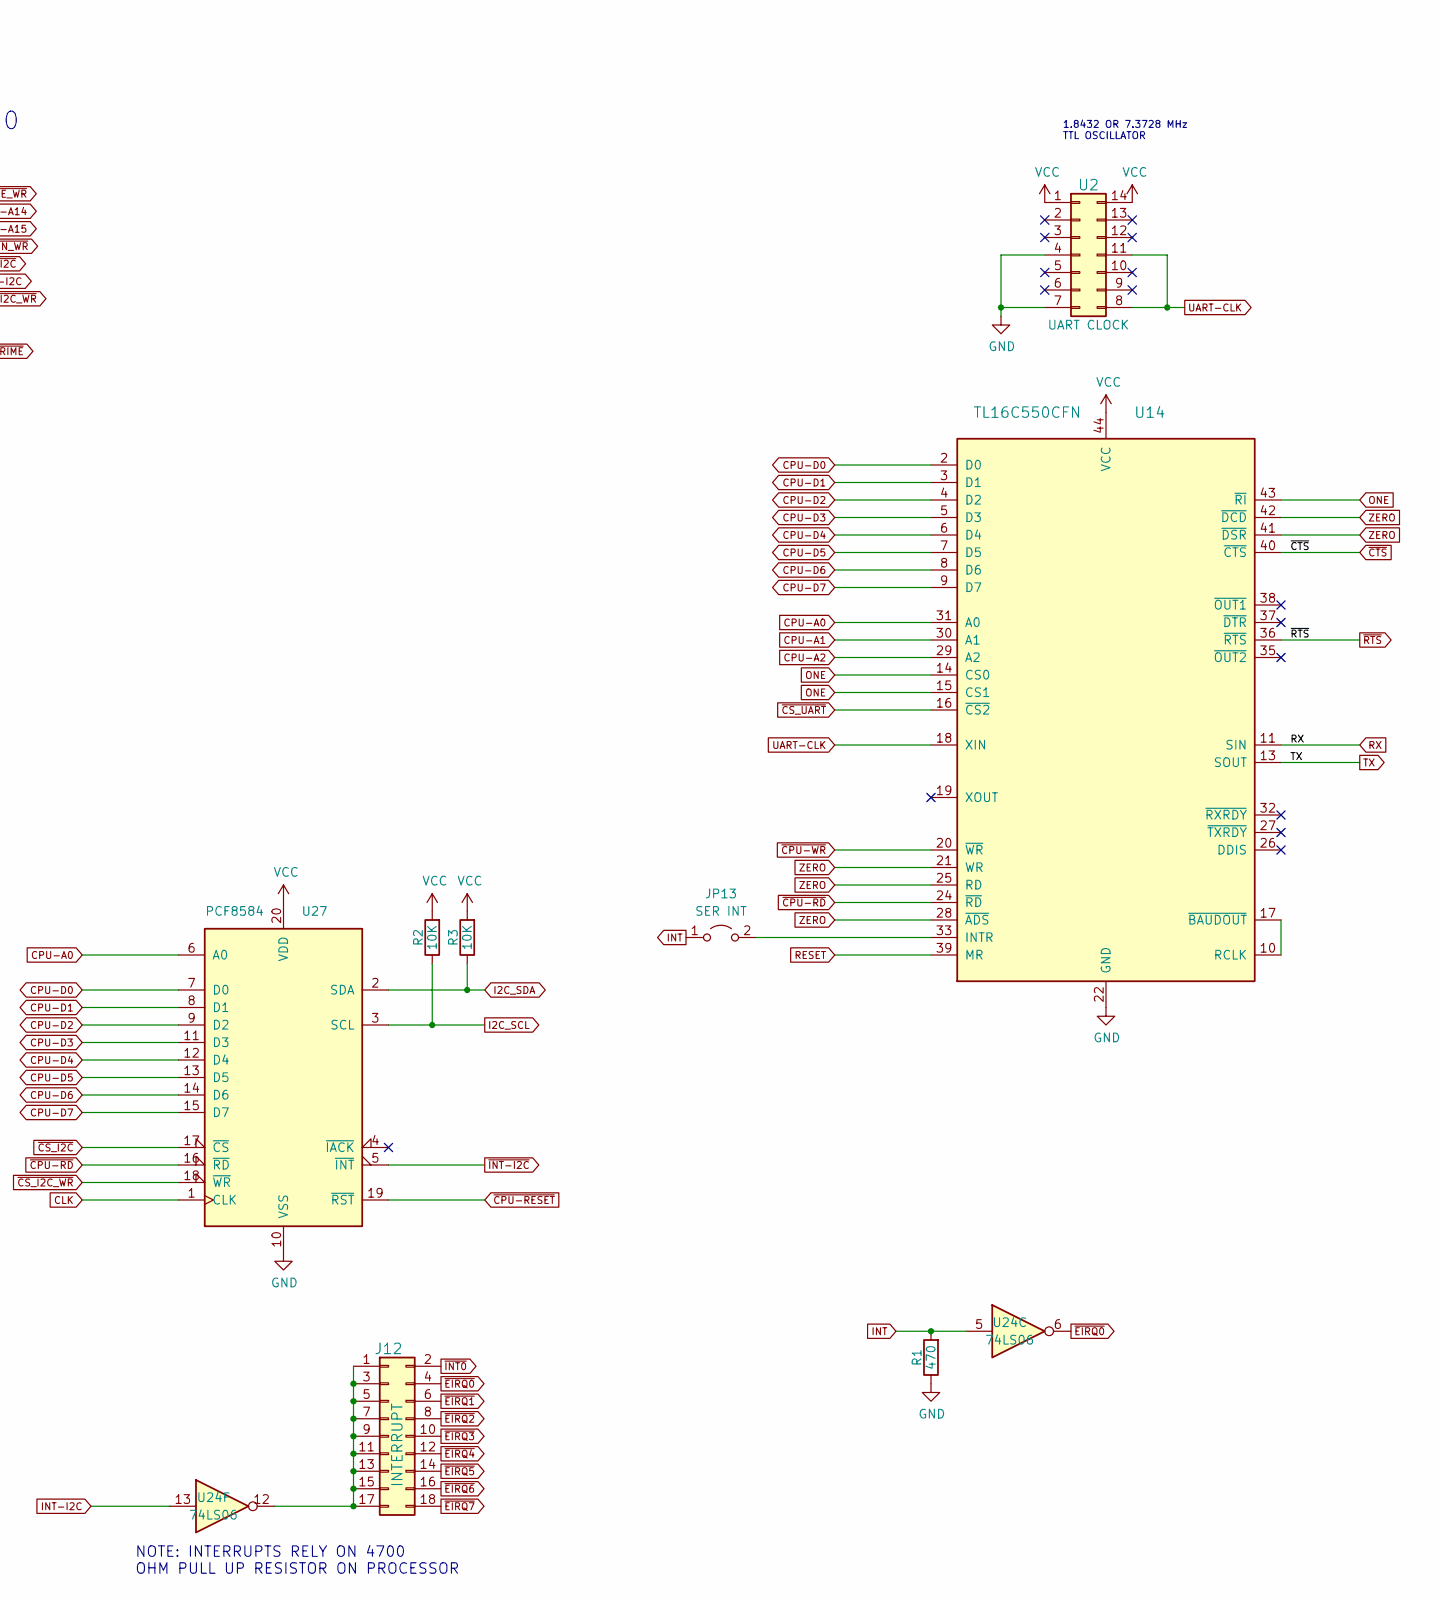
[picture p441: schematic mapper.kicad_sch, part in row 1, column 2]

Parts:
J12: INTERRUPT; PinHeader_2x09_P2.54mm_Vertical
JP10: IO PORT ADDR; PinHeader_2x04_P2.54mm_Vertical
JP13: SER INT; PinHeader_1x02_P2.54mm_Vertical
R1: 470; R_Axial_DIN0207_L6.3mm_D2.5mm_P7.62mm_Horizontal
R2, R3: 10K; R_Axial_DIN0207_L6.3mm_D2.5mm_P7.62mm_Horizontal
RN7: 470; R_Array_SIP9
RN8: 10K; R_Array_SIP9
U2: UART CLOCK; DIP-14_W7.62mm
U9, U22: 74LS670; DIP-16_W7.62mm
U10: 74LS74; DIP-14_W7.62mm
U12: 74LS688; DIP-20_W7.62mm
U14: TL16C550CFN; PLCC-44_THT-Socket
U24: 74LS06
U25: GAL22V10; DIP-24_W7.62mm
U27: PCF8584; DIP-20_W7.62mm

Connections:
CLK: U27.1 (CLK); also elsewhere on the board
CPU-A0: U9.14 (Wa), U14.31 (A0), U22.14 (Wa), U27.6 (A0); also elsewhere on the board
CPU-A1: U9.13 (Wb), U14.30 (A1), U22.13 (Wb), U25.10 (I9); also elsewhere on the board
CPU-A2: U14.29 (A2), U25.3 (I2); also elsewhere on the board
CPU-A4: U12.11 (P4); also elsewhere on the board
CPU-A5: U12.13 (P5); also elsewhere on the board
CPU-A6: U12.15 (P6); also elsewhere on the board
CPU-A7: U12.17 (P7); also elsewhere on the board
CPU-A14: U9.5 (Ra), U22.5 (Ra), U25.5 (I4); also elsewhere on the board
CPU-A15: U9.4 (Rb), U22.4 (Rb), U25.6 (I5); also elsewhere on the board
CPU-D0: U9.15 (D1), U10.2 (D), U14.2 (D0), U22.15 (D1), U27.7 (D0); also elsewhere on the board
CPU-D1: U9.1 (D2), U14.3 (D1), U22.1 (D2), U27.8 (D1); also elsewhere on the board
CPU-D2: U9.2 (D3), U14.4 (D2), U22.2 (D3), U27.9 (D2); also elsewhere on the board
CPU-D3: U9.3 (D4), U14.5 (D3), U22.3 (D4), U27.11 (D3); also elsewhere on the board
CPU-D4: U14.6 (D4), U27.12 (D4); also elsewhere on the board
CPU-D5: U14.7 (D5), U27.13 (D5); also elsewhere on the board
CPU-D6: U14.8 (D6), U27.14 (D6); also elsewhere on the board
CPU-D7: U14.9 (D7), U27.15 (D7); also elsewhere on the board
GND: R1.1, RN7.1 (common), U2.4, U2.7, U9.8 (GND), U12.10 (GND), U14.22 (GND), U22.8 (GND), U25.12 (GND), U27.10 (VSS); also elsewhere on the board
I2C_SCL: R2.1, U27.3 (SCL); also elsewhere on the board
I2C_SDA: R3.1, U27.2 (SDA); also elsewhere on the board
INT: JP13.1 (A), R1.2, U24.5
INT-I2C: U24.13, U25.18 (O5)
unnamed: J12.1, J12.3, J12.5, J12.7, J12.9, J12.11, J12.13, J12.15, J12.17, U24.12
unnamed: JP10.2, RN8.2 (R1), U12.18 (R7)
unnamed: JP10.4, RN8.3 (R2), U12.16 (R6)
unnamed: JP10.6, RN8.4 (R3), U12.14 (R5)
unnamed: JP10.8, RN8.5 (R4), U12.12 (R4)
unnamed: JP13.2 (B), U14.33 (INTR)
unnamed: RN8.6 (R5), U12.3 (R0), U12.4 (P1), U12.5 (R1), U12.6 (P2), U12.7 (R2), U12.8 (P3), U12.9 (R3)
unnamed: U14.10 (RCLK), U14.17 (~BAUDOUT)
ONE: U10.4 (~S), U14.14 (CS0), U14.15 (CS1), U14.43 (~RI); also elsewhere on the board
RESET: U14.39 (MR); also elsewhere on the board
RX: U14.11 (SIN); also elsewhere on the board
SEL-A14: U25.22 (O1); also elsewhere on the board
SEL-A15: U25.21 (O2); also elsewhere on the board
TX: U14.13 (SOUT); also elsewhere on the board
UART-CLK: U2.8, U2.11, U14.18 (XIN)
VCC: R2.2, R3.2, RN8.1 (common), U2.1, U2.14, U9.16 (VCC), U12.20 (VCC), U14.44 (VCC), U22.16 (VCC), U25.24 (VCC), U27.20 (VDD); also elsewhere on the board
ZERO: JP10.1, JP10.3, JP10.5, JP10.7, U14.21 (WR), U14.25 (RD), U14.28 (~ADS), U14.41 (~DSR), U14.42 (~DCD); also elsewhere on the board
mA14: RN7.2 (R1), U9.10 (Q1), U25.7 (I6)
mA15: RN7.3 (R2), U9.9 (Q2), U25.8 (I7)
mA16: RN7.4 (R3), U9.7 (Q3); also elsewhere on the board
mA17: RN7.5 (R4), U9.6 (Q4); also elsewhere on the board
mA18: RN7.6 (R5), U22.10 (Q1); also elsewhere on the board
mA19: RN7.7 (R6), U22.9 (Q2); also elsewhere on the board
mA20: RN7.8 (R7), U22.7 (Q3); also elsewhere on the board
mA21: RN7.9 (R8), U22.6 (Q4); also elsewhere on the board
~AxPRIME: U25.13 (I11), U25.14 (O9)
~CPU-IORQ: U12.1 (G), U25.9 (I8); also elsewhere on the board
~CPU-M1: U12.2 (P0); also elsewhere on the board
~CPU-RD: U14.24 (~RD), U27.16 (~RD); also elsewhere on the board
~CPU-RESET: U10.1 (~R), U27.19 (~RST); also elsewhere on the board
~CPU-WR: U14.20 (~WR), U25.2 (I1); also elsewhere on the board
~CS_I2C_WR: U25.17 (O6), U27.18 (~WR)
~CS_I2C: U25.19 (O4), U27.17 (~CS)
~CS_IO: U12.19 (P=R); also elsewhere on the board
~CS_MAP: U25.4 (I3); also elsewhere on the board
~CS_UART: U14.16 (~CS2); also elsewhere on the board
~CTS: U14.40 (~CTS); also elsewhere on the board
~EIRQ0: J12.4, U24.6; also elsewhere on the board
~EIRQ1: J12.6; also elsewhere on the board
~EIRQ2: J12.8; also elsewhere on the board
~EIRQ3: J12.10; also elsewhere on the board
~EIRQ4: J12.12; also elsewhere on the board
~EIRQ5: J12.14; also elsewhere on the board
~EIRQ6: J12.16; also elsewhere on the board
~EIRQ7: J12.18; also elsewhere on the board
~INT0: J12.2; also elsewhere on the board
~INT-I2C: U25.11 (I10), U27.5 (~INT); also elsewhere on the board
~PAGE_EN: U9.11 (~Er), U10.6 (~Q), U22.11 (~Er)
~PAGE_WR: U9.12 (~Ew), U22.12 (~Ew), U25.23 (O0)
~PGEN_WR: U10.3 (C), U25.20 (O3)
~RTS: U14.36 (~RTS); also elsewhere on the board

Notes on the sheet:
CPU MAPPER V3 GAL22V10
Z80 MEMORY MAPPER AND EXPANSION IO PORT DECODER
UPPER ADDRESS LINES PULL-DOWN RESISTORS
~{A}
MEMORY PAGING SRAMS
THIS IS A PHYSICAL WIRE
IO ADDRESS SELECT CIRCUIT
INTERRUPT FILTER CIRCUIT
1.8432 OR 7.3728 MHz TTL OSCILLATOR
NOTE: INTERRUPTS RELY ON 4700 OHM PULL UP RESISTOR ON PROCESSOR
Note: IO Address Port $50-$5F 1-2 =on - A7 (low) 3-4 =off - A6 (high) 5-6 =on - A5 (low) 7-8 =off - A4 (high)

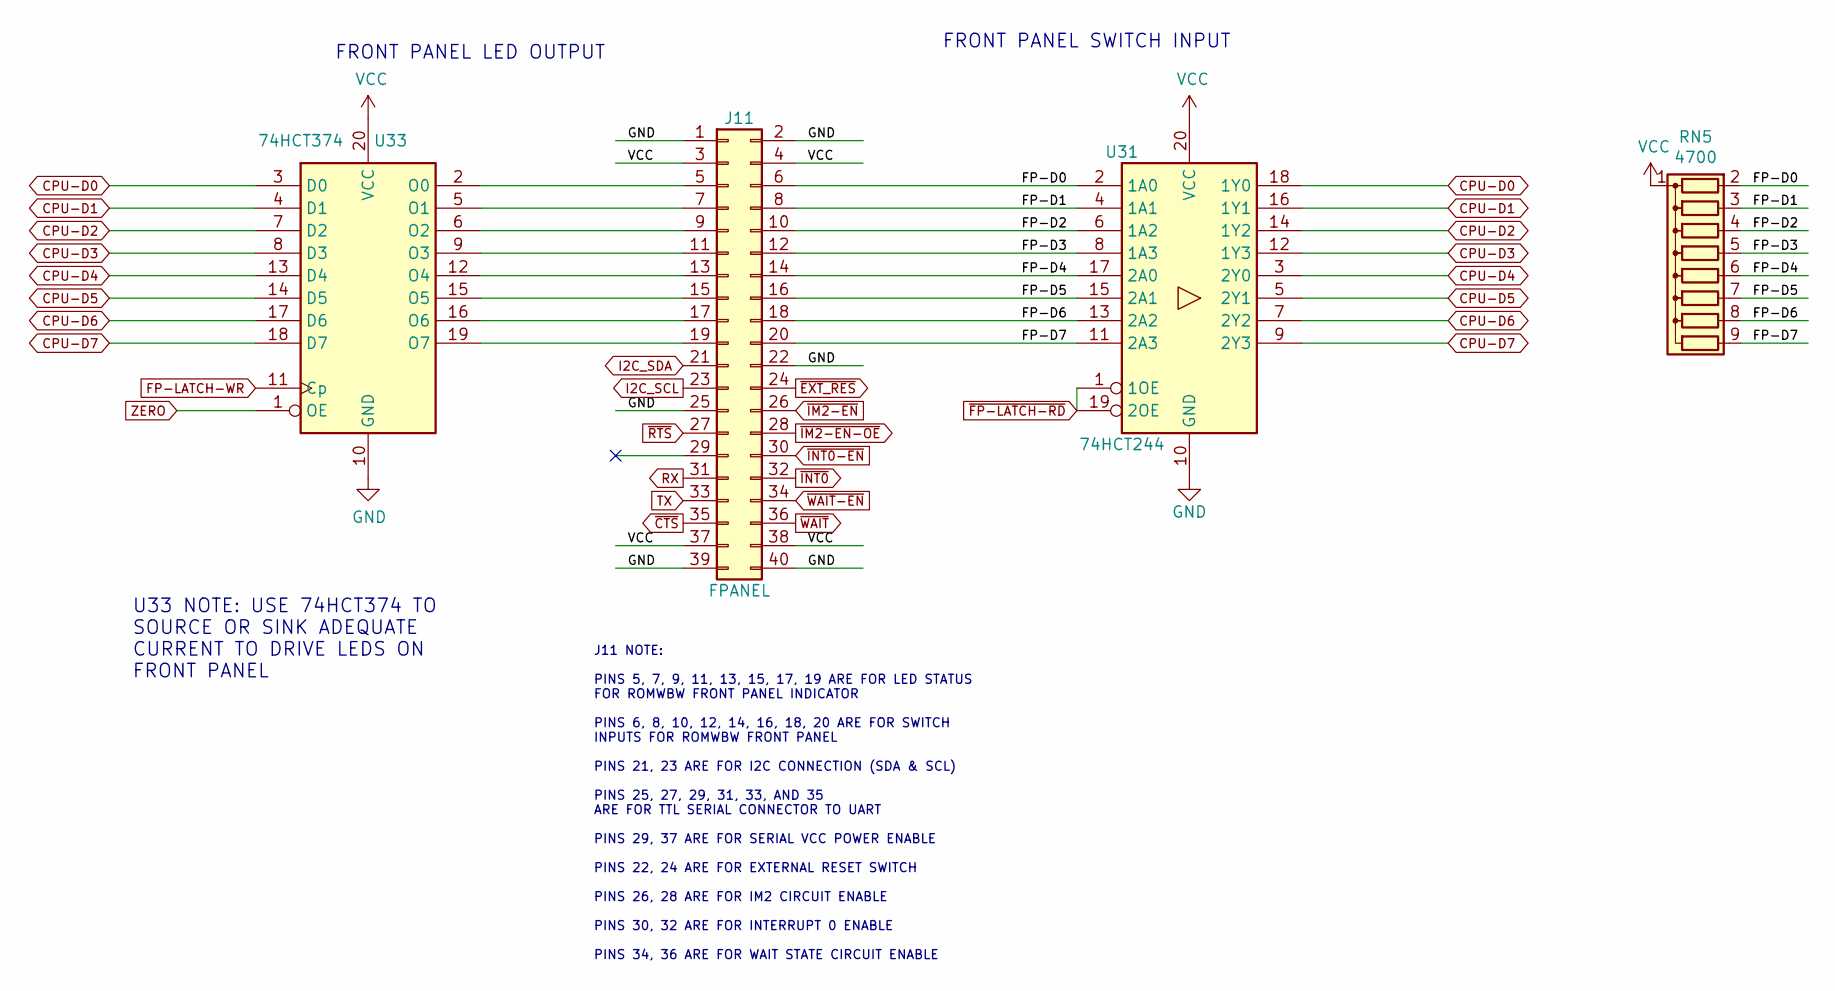
[picture p442: schematic fpanel.kicad_sch]

Parts:
J11: FPANEL; IDC-Header_2x20_P2.54mm_Horizontal
RN5: 4700; R_Array_SIP9
U31: 74HCT244; DIP-20_W7.62mm
U33: 74HCT374; DIP-20_W7.62mm

Connections:
/fpanel/FP-D0: J11.6, RN5.2 (R1), U31.2 (1A0)
/fpanel/FP-D1: J11.8, RN5.3 (R2), U31.4 (1A1)
/fpanel/FP-D2: J11.10, RN5.4 (R3), U31.6 (1A2)
/fpanel/FP-D3: J11.12, RN5.5 (R4), U31.8 (1A3)
/fpanel/FP-D4: J11.14, RN5.6 (R5), U31.17 (2A0)
/fpanel/FP-D5: J11.16, RN5.7 (R6), U31.15 (2A1)
/fpanel/FP-D6: J11.18, RN5.8 (R7), U31.13 (2A2)
/fpanel/FP-D7: J11.20, RN5.9 (R8), U31.11 (2A3)
CPU-D0: U31.18 (1Y0), U33.3 (D0); also elsewhere on the board
CPU-D1: U31.16 (1Y1), U33.4 (D1); also elsewhere on the board
CPU-D2: U31.14 (1Y2), U33.7 (D2); also elsewhere on the board
CPU-D3: U31.12 (1Y3), U33.8 (D3); also elsewhere on the board
CPU-D4: U31.3 (2Y0), U33.13 (D4); also elsewhere on the board
CPU-D5: U31.5 (2Y1), U33.14 (D5); also elsewhere on the board
CPU-D6: U31.7 (2Y2), U33.17 (D6); also elsewhere on the board
CPU-D7: U31.9 (2Y3), U33.18 (D7); also elsewhere on the board
FP-LATCH-WR: U33.11 (Cp); also elsewhere on the board
GND: J11.1, J11.2, J11.22, J11.25, J11.39, J11.40, U31.10 (GND), U33.10 (GND); also elsewhere on the board
I2C_SCL: J11.23; also elsewhere on the board
I2C_SDA: J11.21; also elsewhere on the board
unnamed: J11.5, U33.2 (O0)
unnamed: J11.7, U33.5 (O1)
unnamed: J11.9, U33.6 (O2)
unnamed: J11.11, U33.9 (O3)
unnamed: J11.13, U33.12 (O4)
unnamed: J11.15, U33.15 (O5)
unnamed: J11.17, U33.16 (O6)
unnamed: J11.19, U33.19 (O7)
RX: J11.31; also elsewhere on the board
TX: J11.33; also elsewhere on the board
VCC: J11.3, J11.4, J11.37, J11.38, RN5.1 (common), U31.20 (VCC), U33.20 (VCC); also elsewhere on the board
ZERO: U33.1 (OE); also elsewhere on the board
~CTS: J11.35; also elsewhere on the board
~EXT_RES: J11.24; also elsewhere on the board
~FP-LATCH-RD: U31.1 (1OE), U31.19 (2OE); also elsewhere on the board
~IM2-EN-OE: J11.28; also elsewhere on the board
~IM2-EN: J11.26; also elsewhere on the board
~INT0-EN: J11.30; also elsewhere on the board
~INT0: J11.32; also elsewhere on the board
~RTS: J11.27; also elsewhere on the board
~WAIT-EN: J11.34; also elsewhere on the board
~WAIT: J11.36; also elsewhere on the board

Notes on the sheet:
J11 NOTE: PINS 5, 7, 9, 11, 13, 15, 17, 19 ARE FOR LED STATUS FOR ROMWBW FRONT PANEL INDICATOR PINS 6, 8, 10, 12, 14, 16, 18, 20 ARE FOR SWITCH INPUTS FOR ROMWBW FRONT PANEL PINS 21, 23 ARE FOR I2C CONNECTION (SDA & SCL) PINS 25, 27, 29, 31, 33, AND 35 ARE FOR TTL SERIAL CONNECTOR TO UART PINS 29, 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
U33 NOTE: USE 74HCT374 TO SOURCE OR SINK ADEQUATE CURRENT TO DRIVE LEDS ON FRONT PANEL
FRONT PANEL SWITCH INPUT
FRONT PANEL LED OUTPUT
