lynchaj/duodyne/!Retired/03 processor.Z80, V1.0/processor.Z80.kicad_pcb

## KiCad design !Retired/03 processor.Z80, V1.0/processor.Z80.kicad_pcb (continued)

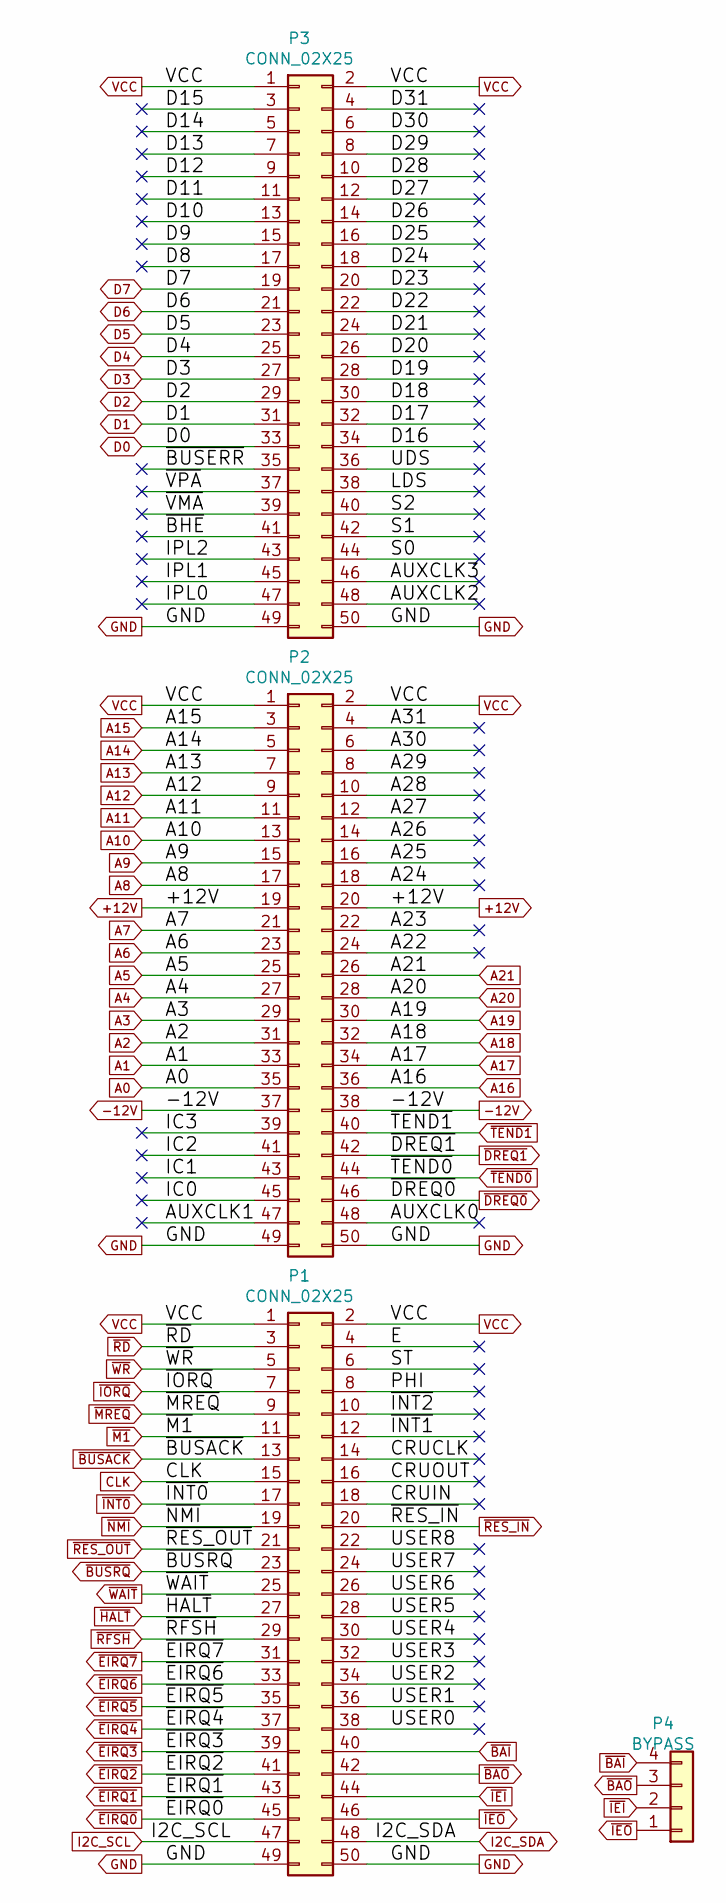
[picture p443: schematic bus.kicad_sch]

Parts:
P1, P2, P3: CONN_02X25; IDC-Header_2x25_P2.54mm_Horizontal
P4: BYPASS; PinHeader_1x04_P2.54mm_Vertical

Connections:
+12V: P2.19, P2.20
-12V: P2.37, P2.38
/bus/A22: P2.24
/bus/A23: P2.22
/bus/A24: P2.18
/bus/A25: P2.16
/bus/A26: P2.14
/bus/A27: P2.12
/bus/A28: P2.10
/bus/A29: P2.8
/bus/A30: P2.6
/bus/A31: P2.4
/bus/AUXCLK0: P2.48
/bus/AUXCLK1: P2.47
/bus/AUXCLK2: P3.48
/bus/AUXCLK3: P3.46
/bus/CRUCLK: P1.14
/bus/CRUIN: P1.18
/bus/CRUOUT: P1.16
/bus/D8: P3.17
/bus/D9: P3.15
/bus/D10: P3.13
/bus/D11: P3.11
/bus/D12: P3.9
/bus/D13: P3.7
/bus/D14: P3.5
/bus/D15: P3.3
/bus/D16: P3.34
/bus/D17: P3.32
/bus/D18: P3.30
/bus/D19: P3.28
/bus/D20: P3.26
/bus/D21: P3.24
/bus/D22: P3.22
/bus/D23: P3.20
/bus/D24: P3.18
/bus/D25: P3.16
/bus/D26: P3.14
/bus/D27: P3.12
/bus/D28: P3.10
/bus/D29: P3.8
/bus/D30: P3.6
/bus/D31: P3.4
/bus/E: P1.4
/bus/IC0: P2.45
/bus/IC1: P2.43
/bus/IC2: P2.41
/bus/IC3: P2.39
/bus/IPL0: P3.47
/bus/IPL1: P3.45
/bus/IPL2: P3.43
/bus/LDS: P3.38
/bus/PHI: P1.8
/bus/S0: P3.44
/bus/S1: P3.42
/bus/S2: P3.40
/bus/ST: P1.6
/bus/UDS: P3.36
/bus/USER0: P1.38
/bus/USER1: P1.36
/bus/USER2: P1.34
/bus/USER3: P1.32
/bus/USER4: P1.30
/bus/USER5: P1.28
/bus/USER6: P1.26
/bus/USER7: P1.24
/bus/USER8: P1.22
/bus/~BHE: P3.41
/bus/~BUSERR: P3.35
/bus/~INT1: P1.12
/bus/~INT2: P1.10
/bus/~VMA: P3.39
/bus/~VPA: P3.37
A0: P2.35; also elsewhere on the board
A1: P2.33; also elsewhere on the board
A2: P2.31; also elsewhere on the board
A3: P2.29; also elsewhere on the board
A4: P2.27; also elsewhere on the board
A5: P2.25; also elsewhere on the board
A6: P2.23; also elsewhere on the board
A7: P2.21; also elsewhere on the board
A8: P2.17; also elsewhere on the board
A9: P2.15; also elsewhere on the board
A10: P2.13; also elsewhere on the board
A11: P2.11; also elsewhere on the board
A12: P2.9; also elsewhere on the board
A13: P2.7; also elsewhere on the board
A14: P2.5; also elsewhere on the board
A15: P2.3; also elsewhere on the board
A16: P2.36; also elsewhere on the board
A17: P2.34; also elsewhere on the board
A18: P2.32; also elsewhere on the board
A19: P2.30; also elsewhere on the board
A20: P2.28; also elsewhere on the board
A21: P2.26; also elsewhere on the board
CLK: P1.15; also elsewhere on the board
D0: P3.33; also elsewhere on the board
D1: P3.31; also elsewhere on the board
D2: P3.29; also elsewhere on the board
D3: P3.27; also elsewhere on the board
D4: P3.25; also elsewhere on the board
D5: P3.23; also elsewhere on the board
D6: P3.21; also elsewhere on the board
D7: P3.19; also elsewhere on the board
GND: P1.49, P1.50, P2.49, P2.50, P3.49, P3.50; also elsewhere on the board
I2C_SCL: P1.47; also elsewhere on the board
I2C_SDA: P1.48; also elsewhere on the board
VCC: P1.1, P1.2, P2.1, P2.2, P3.1, P3.2; also elsewhere on the board
~BAI: P1.40, P4.4
~BAO: P1.42, P4.3; also elsewhere on the board
~BUSACK: P1.13; also elsewhere on the board
~BUSRQ: P1.23; also elsewhere on the board
~DREQ0: P2.46; also elsewhere on the board
~DREQ1: P2.42; also elsewhere on the board
~EIRQ0: P1.45; also elsewhere on the board
~EIRQ1: P1.43; also elsewhere on the board
~EIRQ2: P1.41; also elsewhere on the board
~EIRQ3: P1.39; also elsewhere on the board
~EIRQ4: P1.37; also elsewhere on the board
~EIRQ5: P1.35; also elsewhere on the board
~EIRQ6: P1.33; also elsewhere on the board
~EIRQ7: P1.31; also elsewhere on the board
~HALT: P1.27; also elsewhere on the board
~IEI: P1.44, P4.2; also elsewhere on the board
~IEO: P1.46, P4.1; also elsewhere on the board
~INT0: P1.17; also elsewhere on the board
~IORQ: P1.7; also elsewhere on the board
~M1: P1.11; also elsewhere on the board
~MREQ: P1.9; also elsewhere on the board
~NMI: P1.19; also elsewhere on the board
~RD: P1.3; also elsewhere on the board
~RES_IN: P1.20; also elsewhere on the board
~RES_OUT: P1.21; also elsewhere on the board
~RFSH: P1.29; also elsewhere on the board
~TEND0: P2.44; also elsewhere on the board
~TEND1: P2.40; also elsewhere on the board
~WAIT: P1.25; also elsewhere on the board
~WR: P1.5; also elsewhere on the board

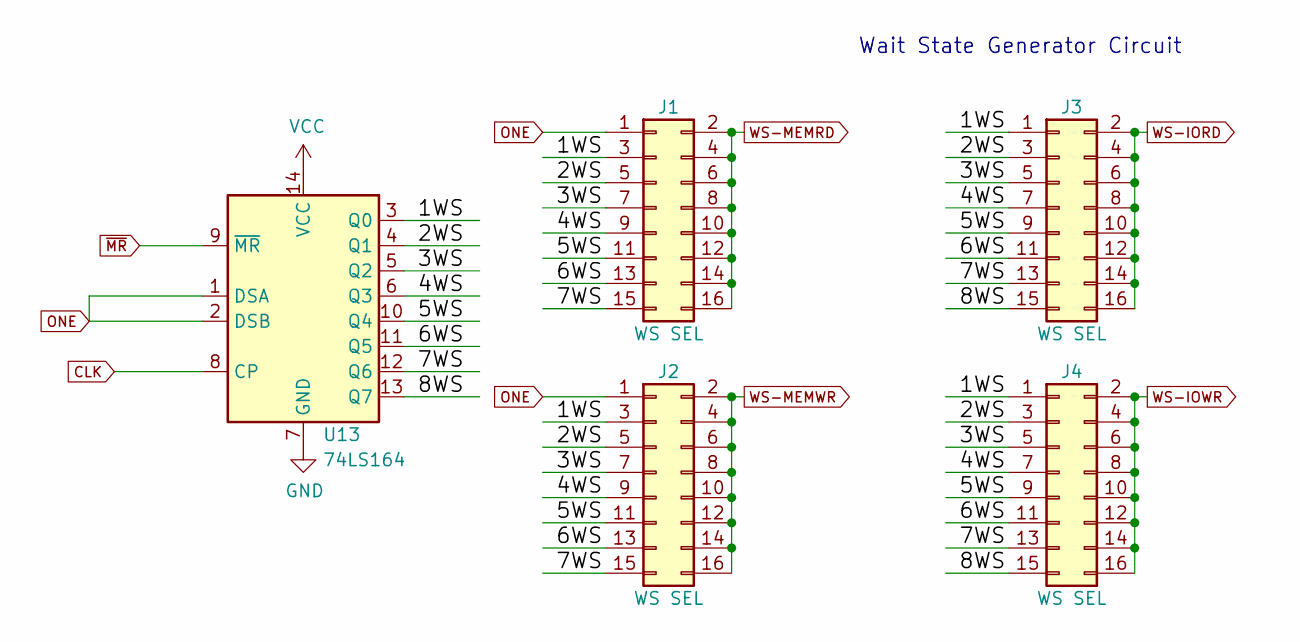
[picture p444: schematic waitstate.kicad_sch]

Parts:
J1, J2, J3, J4: WS SEL; PinHeader_2x08_P2.54mm_Vertical
U13: 74LS164; DIP-14_W7.62mm

Connections:
/waitstate/1WS: J1.3, J2.3, J3.1, J4.1, U13.3 (Q0)
/waitstate/2WS: J1.5, J2.5, J3.3, J4.3, U13.4 (Q1)
/waitstate/3WS: J1.7, J2.7, J3.5, J4.5, U13.5 (Q2)
/waitstate/4WS: J1.9, J2.9, J3.7, J4.7, U13.6 (Q3)
/waitstate/5WS: J1.11, J2.11, J3.9, J4.9, U13.10 (Q4)
/waitstate/6WS: J1.13, J2.13, J3.11, J4.11, U13.11 (Q5)
/waitstate/7WS: J1.15, J2.15, J3.13, J4.13, U13.12 (Q6)
/waitstate/8WS: J3.15, J4.15, U13.13 (Q7)
CLK: U13.8 (CP); also elsewhere on the board
GND: U13.7 (GND); also elsewhere on the board
ONE: J1.1, J2.1, U13.1 (DSA), U13.2 (DSB); also elsewhere on the board
VCC: U13.14 (VCC); also elsewhere on the board
WS-IORD: J3.2, J3.4, J3.6, J3.8, J3.10, J3.12, J3.14, J3.16; also elsewhere on the board
WS-IOWR: J4.2, J4.4, J4.6, J4.8, J4.10, J4.12, J4.14, J4.16; also elsewhere on the board
WS-MEMRD: J1.2, J1.4, J1.6, J1.8, J1.10, J1.12, J1.14, J1.16; also elsewhere on the board
WS-MEMWR: J2.2, J2.4, J2.6, J2.8, J2.10, J2.12, J2.14, J2.16; also elsewhere on the board
~MR: U13.9 (~MR); also elsewhere on the board

Notes on the sheet:
Wait State Generator Circuit

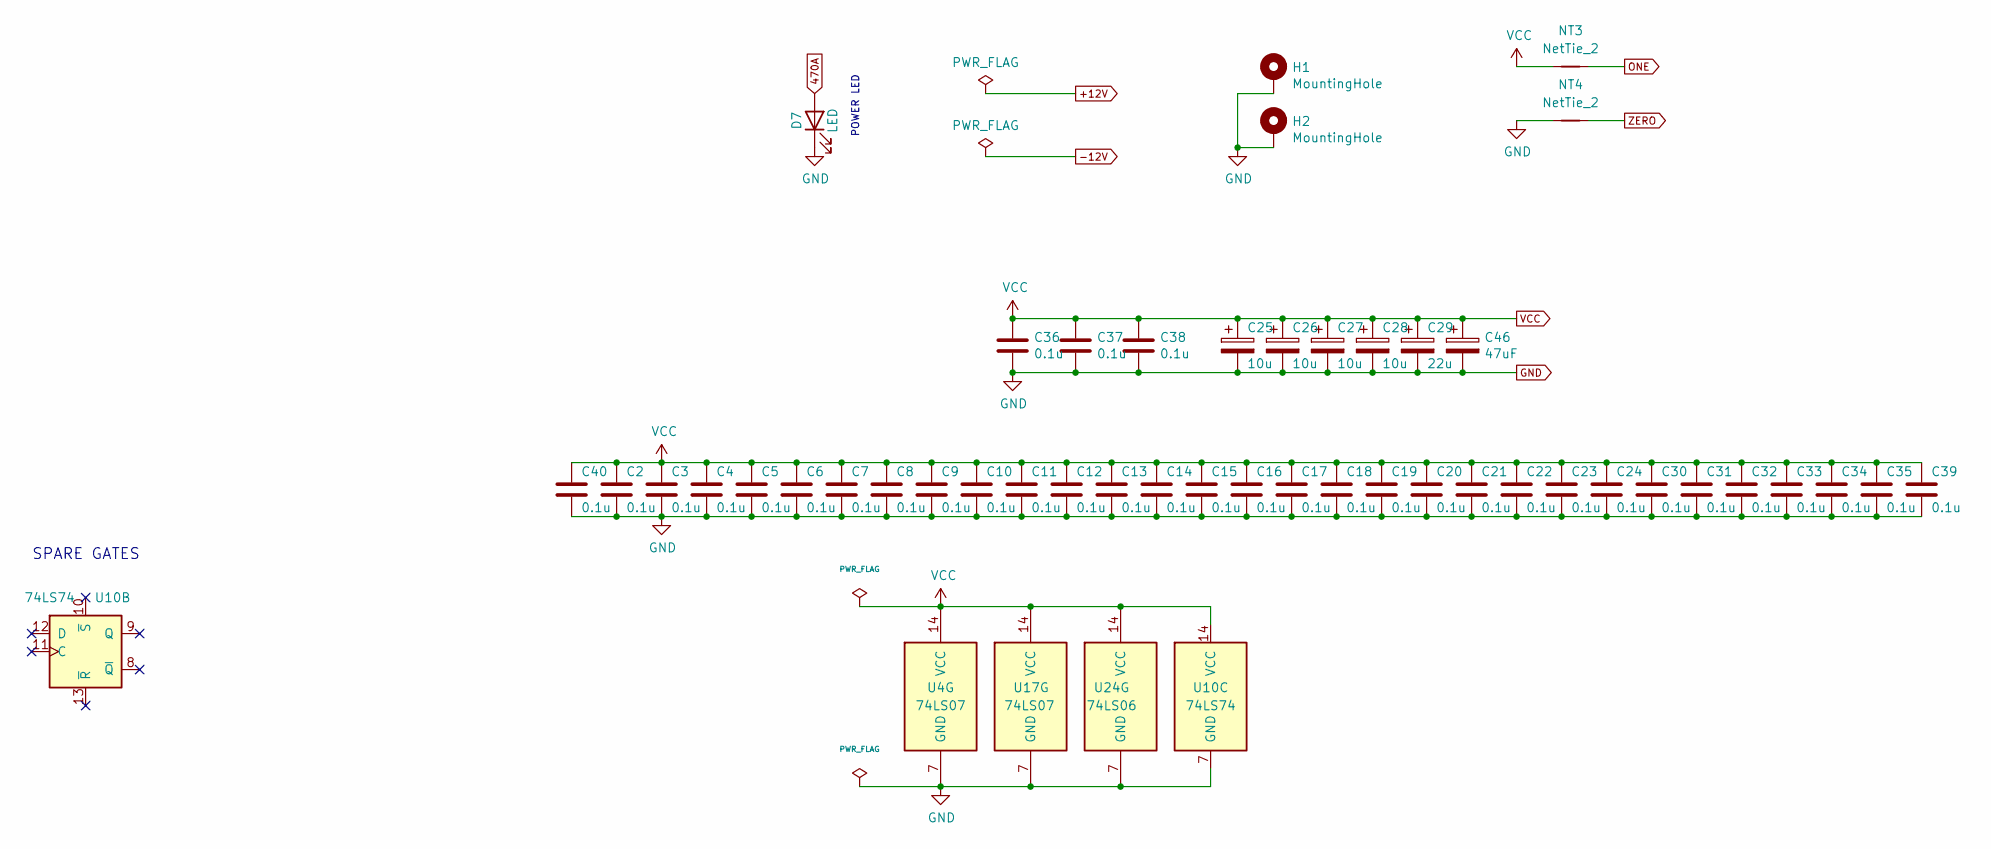
[picture p445: schematic power.kicad_sch]

Parts:
C2, C3, C4, C5, C6, C7, C8, C9, C10, C11, C12, C13, C14, C15, C16, C17, C18, C19, C20, C21, C22, C23, C24, C30, C31, C32, C33, C34, C35, C36, C37, C38, C39, C40: 0.1u; C_Disc_D5.0mm_W2.5mm_P5.00mm
C25, C26, C27, C28: 10u; CP_Radial_D5.0mm_P2.50mm
C29: 22u; CP_Radial_D5.0mm_P2.50mm
C46: 47uF; CP_Radial_D5.0mm_P2.50mm
D7: LED; LED_D3.0mm_Horizontal_O3.81mm_Z2.0mm
H1, H2: MountingHole; MountingHole_3.2mm_M3_Pad
NT3, NT4: NetTie_2; NetTie-2_THT_Pad0.3mm
U4, U17: 74LS07; DIP-14_W7.62mm
U10: 74LS74; DIP-14_W7.62mm
U24: 74LS06; DIP-14_W7.62mm

Connections:
470A: D7.2 (A); also elsewhere on the board
GND: C2.2, C3.2, C4.2, C5.2, C6.2, C7.2, C8.2, C9.2, C10.2, C11.2, C12.2, C13.2, C14.2, C15.2, C16.2, C17.2, C18.2, C19.2, C20.2, C21.2, C22.2, C23.2, C24.2, C25.2, C26.2, C27.2, C28.2, C29.2, C30.2, C31.2, C32.2, C33.2, C34.2, C35.2, C36.2, C37.2, C38.2, C39.2, C40.2, C46.2, D7.1 (K), H1.1, H2.1, NT4.1, U4.7 (GND), U10.7 (GND), U17.7 (GND), U24.7 (GND); also elsewhere on the board
ONE: NT3.2; also elsewhere on the board
VCC: C2.1, C3.1, C4.1, C5.1, C6.1, C7.1, C8.1, C9.1, C10.1, C11.1, C12.1, C13.1, C14.1, C15.1, C16.1, C17.1, C18.1, C19.1, C20.1, C21.1, C22.1, C23.1, C24.1, C25.1, C26.1, C27.1, C28.1, C29.1, C30.1, C31.1, C32.1, C33.1, C34.1, C35.1, C36.1, C37.1, C38.1, C39.1, C40.1, C46.1, NT3.1, U4.14 (VCC), U10.14 (VCC), U17.14 (VCC), U24.14 (VCC); also elsewhere on the board
ZERO: NT4.2; also elsewhere on the board

Notes on the sheet:
POWER LED
SPARE GATES

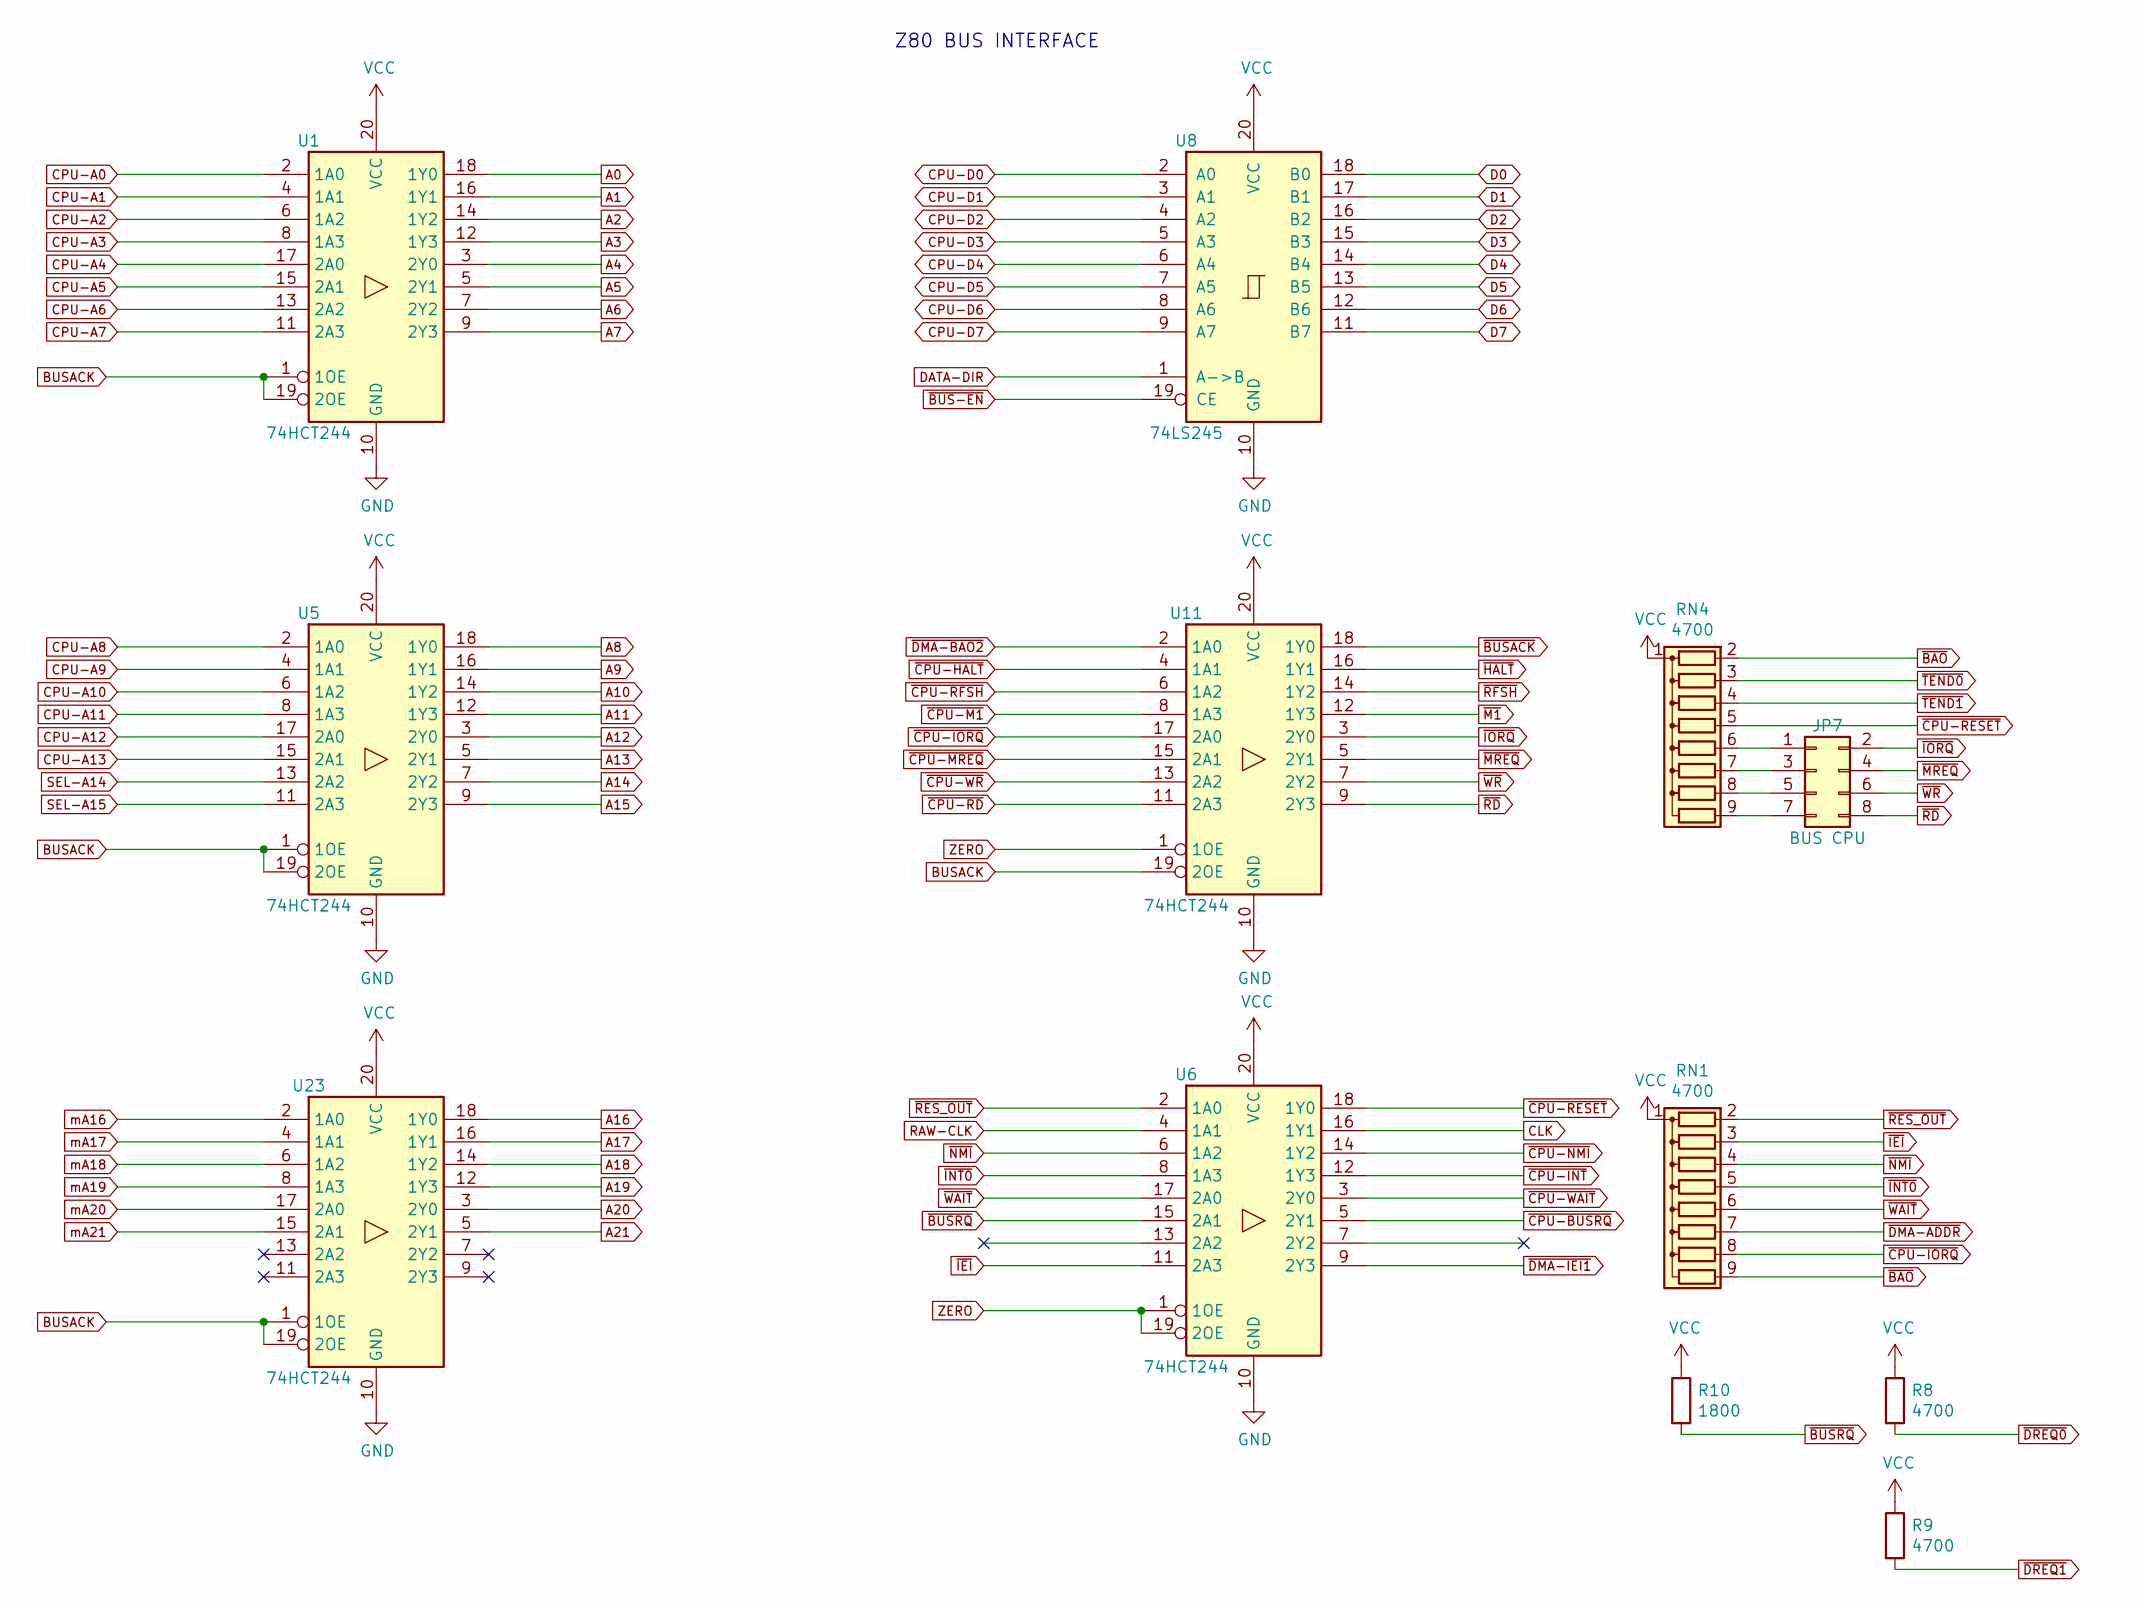
[picture p446: schematic buffers.kicad_sch]

Parts:
JP7: BUS CPU; PinHeader_2x04_P2.54mm_Vertical
R8, R9: 4700; R_Axial_DIN0207_L6.3mm_D2.5mm_P7.62mm_Horizontal
R10: 1800; R_Axial_DIN0207_L6.3mm_D2.5mm_P7.62mm_Horizontal
RN1, RN4: 4700; R_Array_SIP9
U1, U5, U6, U11, U23: 74HCT244; DIP-20_W7.62mm
U8: 74LS245; DIP-20_W7.62mm

Connections:
A0: U1.18 (1Y0); also elsewhere on the board
A1: U1.16 (1Y1); also elsewhere on the board
A2: U1.14 (1Y2); also elsewhere on the board
A3: U1.12 (1Y3); also elsewhere on the board
A4: U1.3 (2Y0); also elsewhere on the board
A5: U1.5 (2Y1); also elsewhere on the board
A6: U1.7 (2Y2); also elsewhere on the board
A7: U1.9 (2Y3); also elsewhere on the board
A8: U5.18 (1Y0); also elsewhere on the board
A9: U5.16 (1Y1); also elsewhere on the board
A10: U5.14 (1Y2); also elsewhere on the board
A11: U5.12 (1Y3); also elsewhere on the board
A12: U5.3 (2Y0); also elsewhere on the board
A13: U5.5 (2Y1); also elsewhere on the board
A14: U5.7 (2Y2); also elsewhere on the board
A15: U5.9 (2Y3); also elsewhere on the board
A16: U23.18 (1Y0); also elsewhere on the board
A17: U23.16 (1Y1); also elsewhere on the board
A18: U23.14 (1Y2); also elsewhere on the board
A19: U23.12 (1Y3); also elsewhere on the board
A20: U23.3 (2Y0); also elsewhere on the board
A21: U23.5 (2Y1); also elsewhere on the board
BUSACK: U1.1 (1OE), U1.19 (2OE), U5.1 (1OE), U5.19 (2OE), U11.19 (2OE), U23.1 (1OE), U23.19 (2OE); also elsewhere on the board
CLK: U6.16 (1Y1); also elsewhere on the board
CPU-A0: U1.2 (1A0); also elsewhere on the board
CPU-A1: U1.4 (1A1); also elsewhere on the board
CPU-A2: U1.6 (1A2); also elsewhere on the board
CPU-A3: U1.8 (1A3); also elsewhere on the board
CPU-A4: U1.17 (2A0); also elsewhere on the board
CPU-A5: U1.15 (2A1); also elsewhere on the board
CPU-A6: U1.13 (2A2); also elsewhere on the board
CPU-A7: U1.11 (2A3); also elsewhere on the board
CPU-A8: U5.2 (1A0); also elsewhere on the board
CPU-A9: U5.4 (1A1); also elsewhere on the board
CPU-A10: U5.6 (1A2); also elsewhere on the board
CPU-A11: U5.8 (1A3); also elsewhere on the board
CPU-A12: U5.17 (2A0); also elsewhere on the board
CPU-A13: U5.15 (2A1); also elsewhere on the board
CPU-D0: U8.2 (A0); also elsewhere on the board
CPU-D1: U8.3 (A1); also elsewhere on the board
CPU-D2: U8.4 (A2); also elsewhere on the board
CPU-D3: U8.5 (A3); also elsewhere on the board
CPU-D4: U8.6 (A4); also elsewhere on the board
CPU-D5: U8.7 (A5); also elsewhere on the board
CPU-D6: U8.8 (A6); also elsewhere on the board
CPU-D7: U8.9 (A7); also elsewhere on the board
D0: U8.18 (B0); also elsewhere on the board
D1: U8.17 (B1); also elsewhere on the board
D2: U8.16 (B2); also elsewhere on the board
D3: U8.15 (B3); also elsewhere on the board
D4: U8.14 (B4); also elsewhere on the board
D5: U8.13 (B5); also elsewhere on the board
D6: U8.12 (B6); also elsewhere on the board
D7: U8.11 (B7); also elsewhere on the board
DATA-DIR: U8.1 (A->B); also elsewhere on the board
GND: U1.10 (GND), U5.10 (GND), U6.10 (GND), U8.10 (GND), U11.10 (GND), U23.10 (GND); also elsewhere on the board
unnamed: JP7.1, RN4.6 (R5)
unnamed: JP7.3, RN4.7 (R6)
unnamed: JP7.5, RN4.8 (R7)
unnamed: JP7.7, RN4.9 (R8)
RAW-CLK: U6.4 (1A1); also elsewhere on the board
SEL-A14: U5.13 (2A2); also elsewhere on the board
SEL-A15: U5.11 (2A3); also elsewhere on the board
VCC: R8.1, R9.1, R10.1, RN1.1 (common), RN4.1 (common), U1.20 (VCC), U5.20 (VCC), U6.20 (VCC), U8.20 (VCC), U11.20 (VCC), U23.20 (VCC); also elsewhere on the board
ZERO: U6.1 (1OE), U6.19 (2OE), U11.1 (1OE); also elsewhere on the board
mA16: U23.2 (1A0); also elsewhere on the board
mA17: U23.4 (1A1); also elsewhere on the board
mA18: U23.6 (1A2); also elsewhere on the board
mA19: U23.8 (1A3); also elsewhere on the board
mA20: U23.17 (2A0); also elsewhere on the board
mA21: U23.15 (2A1); also elsewhere on the board
~BAO: RN1.9 (R8), RN4.2 (R1); also elsewhere on the board
~BUS-EN: U8.19 (CE); also elsewhere on the board
~BUSACK: U11.18 (1Y0); also elsewhere on the board
~BUSRQ: R10.2, U6.15 (2A1); also elsewhere on the board
~CPU-BUSRQ: U6.5 (2Y1); also elsewhere on the board
~CPU-HALT: U11.4 (1A1); also elsewhere on the board
~CPU-INT: U6.12 (1Y3); also elsewhere on the board
~CPU-IORQ: RN1.8 (R7), U11.17 (2A0); also elsewhere on the board
~CPU-M1: U11.8 (1A3); also elsewhere on the board
~CPU-MREQ: U11.15 (2A1); also elsewhere on the board
~CPU-NMI: U6.14 (1Y2); also elsewhere on the board
~CPU-RD: U11.11 (2A3); also elsewhere on the board
~CPU-RESET: RN4.5 (R4), U6.18 (1Y0); also elsewhere on the board
~CPU-RFSH: U11.6 (1A2); also elsewhere on the board
~CPU-WAIT: U6.3 (2Y0); also elsewhere on the board
~CPU-WR: U11.13 (2A2); also elsewhere on the board
~DMA-ADDR: RN1.7 (R6); also elsewhere on the board
~DMA-BAO2: U11.2 (1A0); also elsewhere on the board
~DMA-IEI1: U6.9 (2Y3); also elsewhere on the board
~DREQ0: R8.2; also elsewhere on the board
~DREQ1: R9.2; also elsewhere on the board
~HALT: U11.16 (1Y1); also elsewhere on the board
~IEI: RN1.3 (R2), U6.11 (2A3); also elsewhere on the board
~INT0: RN1.5 (R4), U6.8 (1A3); also elsewhere on the board
~IORQ: JP7.2, U11.3 (2Y0); also elsewhere on the board
~M1: U11.12 (1Y3); also elsewhere on the board
~MREQ: JP7.4, U11.5 (2Y1); also elsewhere on the board
~NMI: RN1.4 (R3), U6.6 (1A2); also elsewhere on the board
~RD: JP7.8, U11.9 (2Y3); also elsewhere on the board
~RES_OUT: RN1.2 (R1), U6.2 (1A0); also elsewhere on the board
~RFSH: U11.14 (1Y2); also elsewhere on the board
~TEND0: RN4.3 (R2); also elsewhere on the board
~TEND1: RN4.4 (R3); also elsewhere on the board
~WAIT: RN1.6 (R5), U6.17 (2A0); also elsewhere on the board
~WR: JP7.6, U11.7 (2Y2); also elsewhere on the board

Notes on the sheet:
Z80 BUS INTERFACE
