lynchaj/duodyne/!Retired/03 processor.Z80, V1.0/processor.Z80.kicad_pcb

## KiCad design !Retired/03 processor.Z80, V1.0/processor.Z80.kicad_pcb (continued)

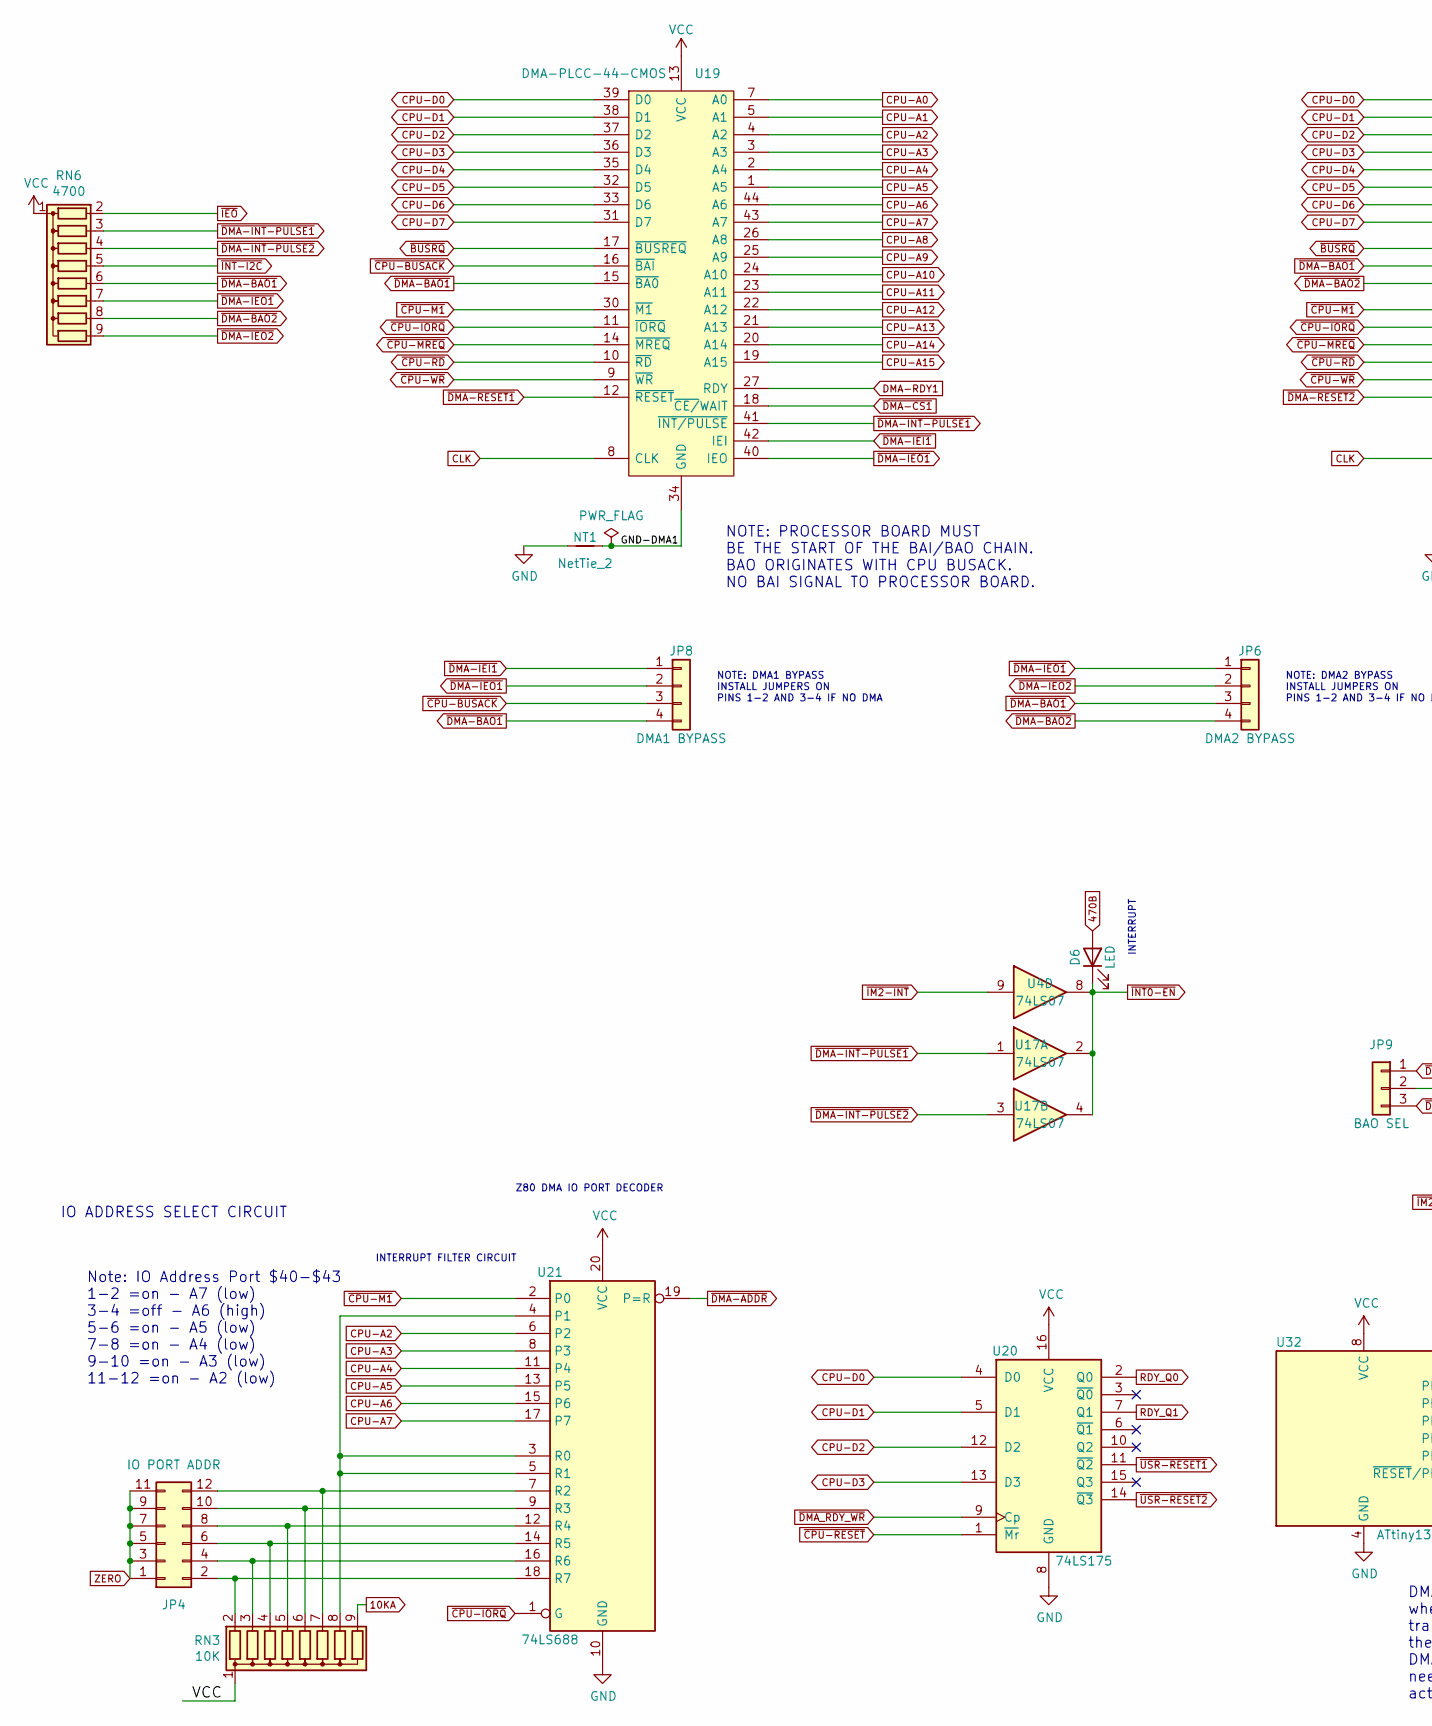
[picture p447: schematic DMA.kicad_sch, part in row 1, column 1]

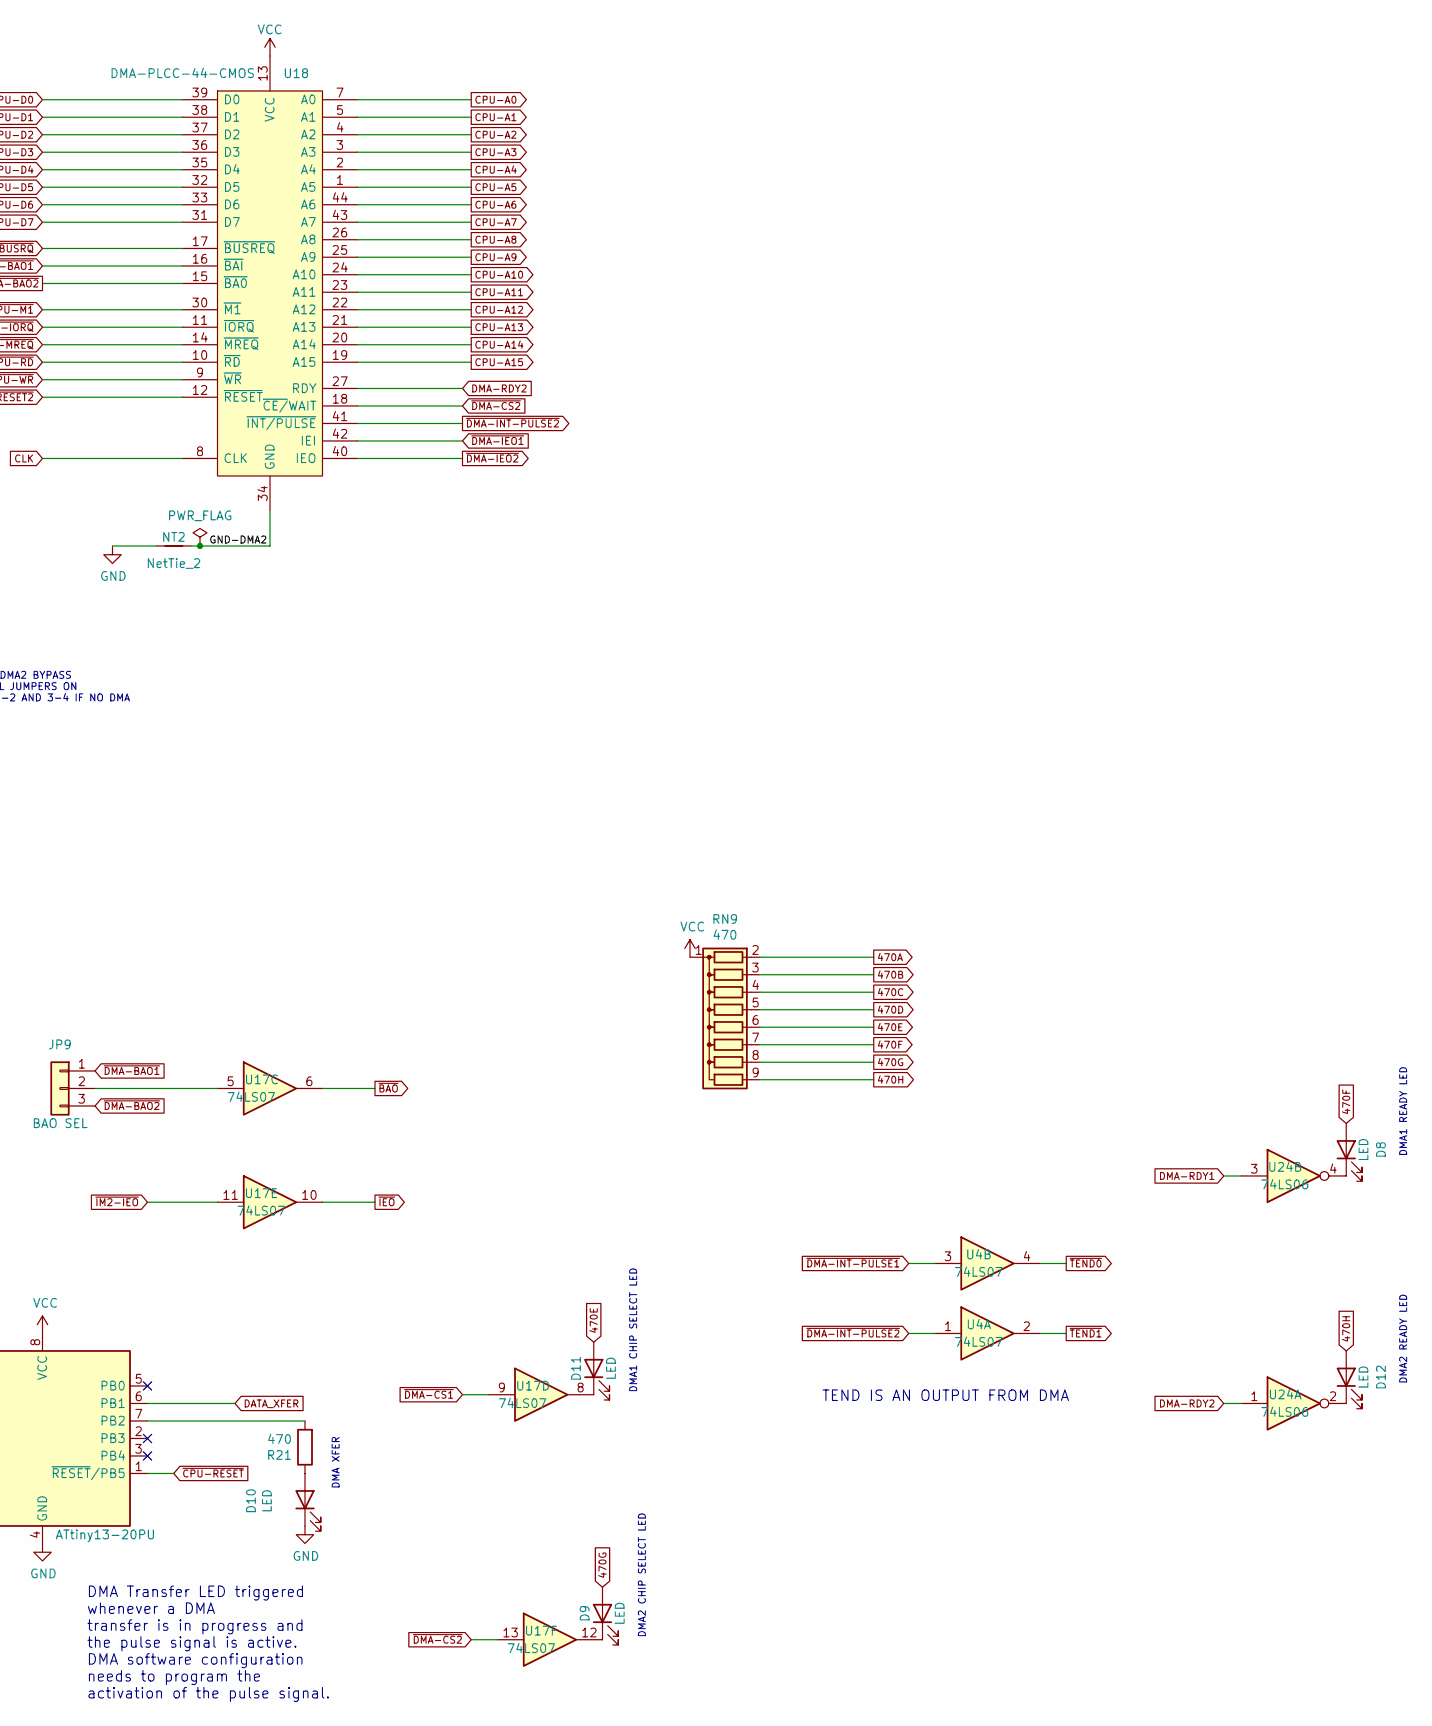
[picture p448: schematic DMA.kicad_sch, part in row 1, column 2]

Parts:
D6, D8, D9, D10, D11, D12: LED; LED_D3.0mm_Horizontal_O3.81mm_Z2.0mm
JP4: IO PORT ADDR; PinHeader_2x06_P2.54mm_Vertical
JP6: DMA2 BYPASS; PinHeader_1x04_P2.54mm_Vertical
JP8: DMA1 BYPASS; PinHeader_1x04_P2.54mm_Vertical
JP9: BAO SEL; PinHeader_1x03_P2.54mm_Vertical
NT1, NT2: NetTie_2; NetTie-2_THT_Pad0.3mm
R21: 470; R_Axial_DIN0207_L6.3mm_D2.5mm_P7.62mm_Horizontal
RN3: 10K; R_Array_SIP9
RN6: 4700; R_Array_SIP9
RN9: 470; R_Array_SIP9
U4, U17: 74LS07; DIP-14_W7.62mm
U18, U19: DMA-PLCC-44-CMOS; PLCC-44_THT-Socket; Manufacturer_Part_Number Z84C4206PEG; Mouser Part Number 692-Z84C4206PEG
U20: 74LS175; DIP-16_W7.62mm
U21: 74LS688; DIP-20_W7.62mm
U24: 74LS06
U32: ATtiny13-20PU; DIP-8_W7.62mm

Connections:
10KA: RN3.9 (R8); also elsewhere on the board
470A: RN9.2 (R1); also elsewhere on the board
470B: D6.2 (A), RN9.3 (R2)
470C: RN9.4 (R3); also elsewhere on the board
470D: RN9.5 (R4); also elsewhere on the board
470E: D11.2 (A), RN9.6 (R5)
470F: D8.2 (A), RN9.7 (R6)
470G: D9.2 (A), RN9.8 (R7)
470H: D12.2 (A), RN9.9 (R8)
/DMA/GND-DMA1: NT1.2, U19.34 (GND)
/DMA/GND-DMA2: NT2.2, U18.34 (GND)
CLK: U18.8 (CLK), U19.8 (CLK); also elsewhere on the board
CPU-A0: U18.7 (A0), U19.7 (A0); also elsewhere on the board
CPU-A1: U18.5 (A1), U19.5 (A1); also elsewhere on the board
CPU-A2: U18.4 (A2), U19.4 (A2), U21.6 (P2); also elsewhere on the board
CPU-A3: U18.3 (A3), U19.3 (A3), U21.8 (P3); also elsewhere on the board
CPU-A4: U18.2 (A4), U19.2 (A4), U21.11 (P4); also elsewhere on the board
CPU-A5: U18.1 (A5), U19.1 (A5), U21.13 (P5); also elsewhere on the board
CPU-A6: U18.44 (A6), U19.44 (A6), U21.15 (P6); also elsewhere on the board
CPU-A7: U18.43 (A7), U19.43 (A7), U21.17 (P7); also elsewhere on the board
CPU-A8: U18.26 (A8), U19.26 (A8); also elsewhere on the board
CPU-A9: U18.25 (A9), U19.25 (A9); also elsewhere on the board
CPU-A10: U18.24 (A10), U19.24 (A10); also elsewhere on the board
CPU-A11: U18.23 (A11), U19.23 (A11); also elsewhere on the board
CPU-A12: U18.22 (A12), U19.22 (A12); also elsewhere on the board
CPU-A13: U18.21 (A13), U19.21 (A13); also elsewhere on the board
CPU-A14: U18.20 (A14), U19.20 (A14); also elsewhere on the board
CPU-A15: U18.19 (A15), U19.19 (A15); also elsewhere on the board
CPU-D0: U18.39 (D0), U19.39 (D0), U20.4 (D0); also elsewhere on the board
CPU-D1: U18.38 (D1), U19.38 (D1), U20.5 (D1); also elsewhere on the board
CPU-D2: U18.37 (D2), U19.37 (D2), U20.12 (D2); also elsewhere on the board
CPU-D3: U18.36 (D3), U19.36 (D3), U20.13 (D3); also elsewhere on the board
CPU-D4: U18.35 (D4), U19.35 (D4); also elsewhere on the board
CPU-D5: U18.32 (D5), U19.32 (D5); also elsewhere on the board
CPU-D6: U18.33 (D6), U19.33 (D6); also elsewhere on the board
CPU-D7: U18.31 (D7), U19.31 (D7); also elsewhere on the board
DATA_XFER: U32.6 (PB1); also elsewhere on the board
DMA-RDY1: U19.27 (RDY), U24.3; also elsewhere on the board
DMA-RDY2: U18.27 (RDY), U24.1; also elsewhere on the board
GND: D10.1 (K), NT1.1, NT2.1, U20.8 (GND), U21.10 (GND), U32.4 (GND); also elsewhere on the board
unnamed: D8.1 (K), U24.4
unnamed: D9.1 (K), U17.12
unnamed: D10.2 (A), R21.1
unnamed: D11.1 (K), U17.8
unnamed: D12.1 (K), U24.2
unnamed: JP4.2, RN3.2 (R1), U21.18 (R7)
unnamed: JP4.4, RN3.3 (R2), U21.16 (R6)
unnamed: JP4.6, RN3.4 (R3), U21.14 (R5)
unnamed: JP4.8, RN3.5 (R4), U21.12 (R4)
unnamed: JP4.10, RN3.6 (R5), U21.9 (R3)
unnamed: JP4.12, RN3.7 (R6), U21.7 (R2)
unnamed: JP9.2, U17.5
unnamed: R21.2, U32.7 (PB2)
unnamed: RN3.8 (R7), U21.3 (R0), U21.4 (P1), U21.5 (R1)
RDY_Q0: U20.2 (Q0); also elsewhere on the board
RDY_Q1: U20.7 (Q1); also elsewhere on the board
VCC: RN3.1 (common), RN6.1 (common), RN9.1 (common), U18.13 (VCC), U19.13 (VCC), U20.16 (VCC), U21.20 (VCC), U32.8 (VCC); also elsewhere on the board
ZERO: JP4.1, JP4.3, JP4.5, JP4.7, JP4.9, JP4.11; also elsewhere on the board
~BAO: U17.6; also elsewhere on the board
~BUSRQ: U18.17 (~BUSREQ), U19.17 (~BUSREQ); also elsewhere on the board
~CPU-BUSACK: JP8.3, U19.16 (~BAI); also elsewhere on the board
~CPU-IORQ: U18.11 (~IORQ), U19.11 (~IORQ), U21.1 (G); also elsewhere on the board
~CPU-M1: U18.30 (~M1), U19.30 (~M1), U21.2 (P0); also elsewhere on the board
~CPU-MREQ: U18.14 (~MREQ), U19.14 (~MREQ); also elsewhere on the board
~CPU-RD: U18.10 (~RD), U19.10 (~RD); also elsewhere on the board
~CPU-RESET: U20.1 (~Mr), U32.1 (~RESET/PB5); also elsewhere on the board
~CPU-WR: U18.9 (~WR), U19.9 (~WR); also elsewhere on the board
~DMA-ADDR: U21.19 (P=R); also elsewhere on the board
~DMA-BAO1: JP6.3, JP8.4, JP9.1, RN6.6 (R5), U18.16 (~BAI), U19.15 (~BA0)
~DMA-BAO2: JP6.4, JP9.3, RN6.8 (R7), U18.15 (~BA0); also elsewhere on the board
~DMA-CS1: U17.9, U19.18 (~CE/WAIT); also elsewhere on the board
~DMA-CS2: U17.13, U18.18 (~CE/WAIT); also elsewhere on the board
~DMA-IEI1: JP8.1, U19.42 (IEI); also elsewhere on the board
~DMA-IEO1: JP6.1, JP8.2, RN6.7 (R6), U18.42 (IEI), U19.40 (IEO)
~DMA-IEO2: JP6.2, RN6.9 (R8), U18.40 (IEO); also elsewhere on the board
~DMA-INT-PULSE1: RN6.3 (R2), U4.3, U17.1, U19.41 (~INT/PULSE); also elsewhere on the board
~DMA-INT-PULSE2: RN6.4 (R3), U4.1, U17.3, U18.41 (~INT/PULSE); also elsewhere on the board
~DMA-RESET1: U19.12 (~RESET); also elsewhere on the board
~DMA-RESET2: U18.12 (~RESET); also elsewhere on the board
~DMA_RDY_WR: U20.9 (Cp); also elsewhere on the board
~IEO: RN6.2 (R1), U17.10; also elsewhere on the board
~IM2-IEO: U17.11; also elsewhere on the board
~IM2-INT: U4.9; also elsewhere on the board
~INT0-EN: D6.1 (K), U4.8, U17.2, U17.4; also elsewhere on the board
~INT-I2C: RN6.5 (R4); also elsewhere on the board
~TEND0: U4.4; also elsewhere on the board
~TEND1: U4.2; also elsewhere on the board
~USR-RESET1: U20.11 (~Q2); also elsewhere on the board
~USR-RESET2: U20.14 (~Q3); also elsewhere on the board

Notes on the sheet:
INTERRUPT
DMA1 READY LED
NOTE: DMA2 BYPASS INSTALL JUMPERS ON PINS 1-2 AND 3-4 IF NO DMA
NOTE: DMA1 BYPASS INSTALL JUMPERS ON PINS 1-2 AND 3-4 IF NO DMA
IO ADDRESS SELECT CIRCUIT
DMA Transfer LED triggered whenever a DMA transfer is in progress and the pulse signal is active. DMA software configuration needs to program the activation of the pulse signal.
DMA1 CHIP SELECT LED
DMA XFER
INTERRUPT FILTER CIRCUIT
DMA2 READY LED
DMA2 CHIP SELECT LED
TEND IS AN OUTPUT FROM DMA
NOTE: PROCESSOR BOARD MUST BE THE START OF THE BAI/BAO CHAIN. BAO ORIGINATES WITH CPU BUSACK. NO BAI SIGNAL TO PROCESSOR BOARD.
Z80 DMA IO PORT DECODER
Note: IO Address Port $40-$43 1-2 =on - A7 (low) 3-4 =off - A6 (high) 5-6 =on - A5 (low) 7-8 =on - A4 (low) 9-10 =on - A3 (low) 11-12 =on - A2 (low)

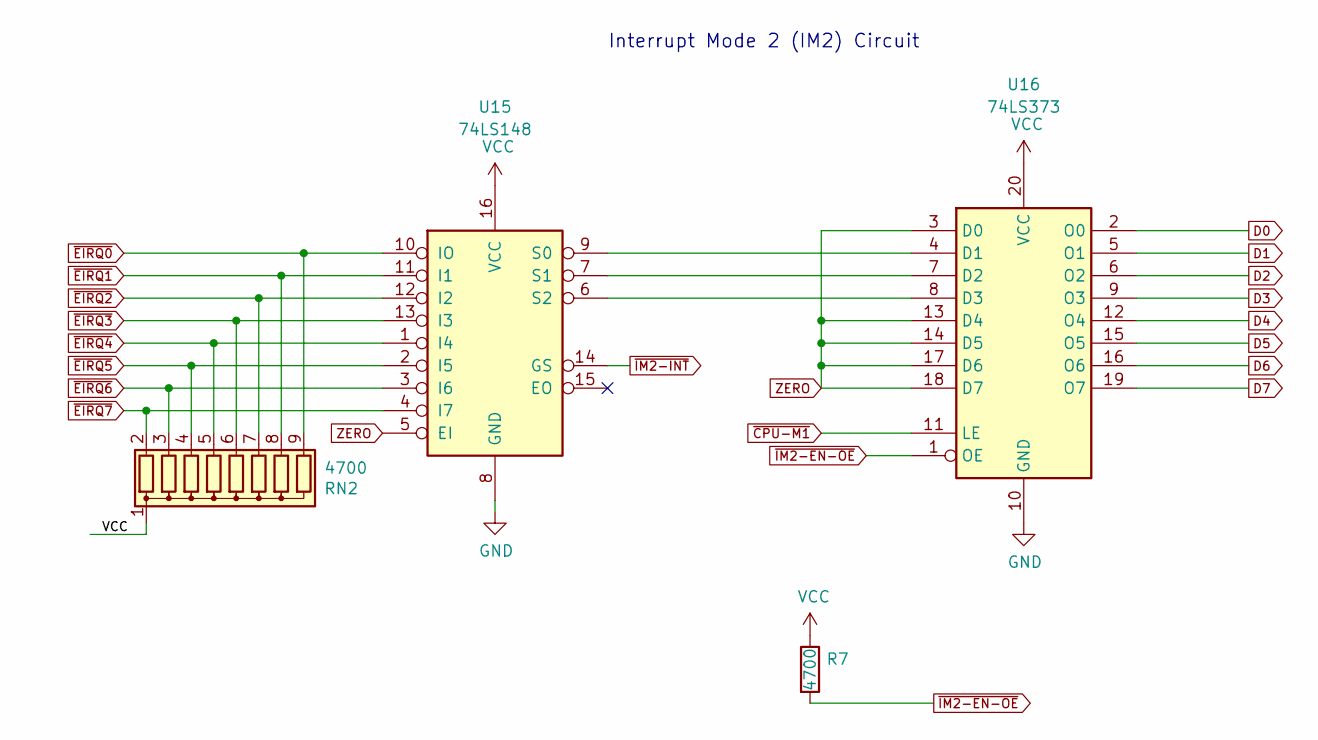
[picture p449: schematic IM2.kicad_sch]

Parts:
R7: 4700; R_Axial_DIN0207_L6.3mm_D2.5mm_P7.62mm_Horizontal
RN2: 4700; R_Array_SIP9
U15: 74LS148; DIP-16_W7.62mm
U16: 74LS373; DIP-20_W7.62mm

Connections:
D0: U16.2 (O0); also elsewhere on the board
D1: U16.5 (O1); also elsewhere on the board
D2: U16.6 (O2); also elsewhere on the board
D3: U16.9 (O3); also elsewhere on the board
D4: U16.12 (O4); also elsewhere on the board
D5: U16.15 (O5); also elsewhere on the board
D6: U16.16 (O6); also elsewhere on the board
D7: U16.19 (O7); also elsewhere on the board
GND: U15.8 (GND), U16.10 (GND); also elsewhere on the board
unnamed: U15.6 (S2), U16.8 (D3)
unnamed: U15.7 (S1), U16.7 (D2)
unnamed: U15.9 (S0), U16.4 (D1)
VCC: R7.1, RN2.1 (common), U15.16 (VCC), U16.20 (VCC); also elsewhere on the board
ZERO: U15.5 (EI), U16.3 (D0), U16.13 (D4), U16.14 (D5), U16.17 (D6), U16.18 (D7); also elsewhere on the board
~CPU-M1: U16.11 (LE); also elsewhere on the board
~EIRQ0: RN2.9 (R8), U15.10 (IO); also elsewhere on the board
~EIRQ1: RN2.8 (R7), U15.11 (I1); also elsewhere on the board
~EIRQ2: RN2.7 (R6), U15.12 (I2); also elsewhere on the board
~EIRQ3: RN2.6 (R5), U15.13 (I3); also elsewhere on the board
~EIRQ4: RN2.5 (R4), U15.1 (I4); also elsewhere on the board
~EIRQ5: RN2.4 (R3), U15.2 (I5); also elsewhere on the board
~EIRQ6: RN2.3 (R2), U15.3 (I6); also elsewhere on the board
~EIRQ7: RN2.2 (R1), U15.4 (I7); also elsewhere on the board
~IM2-EN-OE: R7.2, U16.1 (OE); also elsewhere on the board
~IM2-INT: U15.14 (GS); also elsewhere on the board

Notes on the sheet:
Interrupt Mode 2 (IM2) Circuit

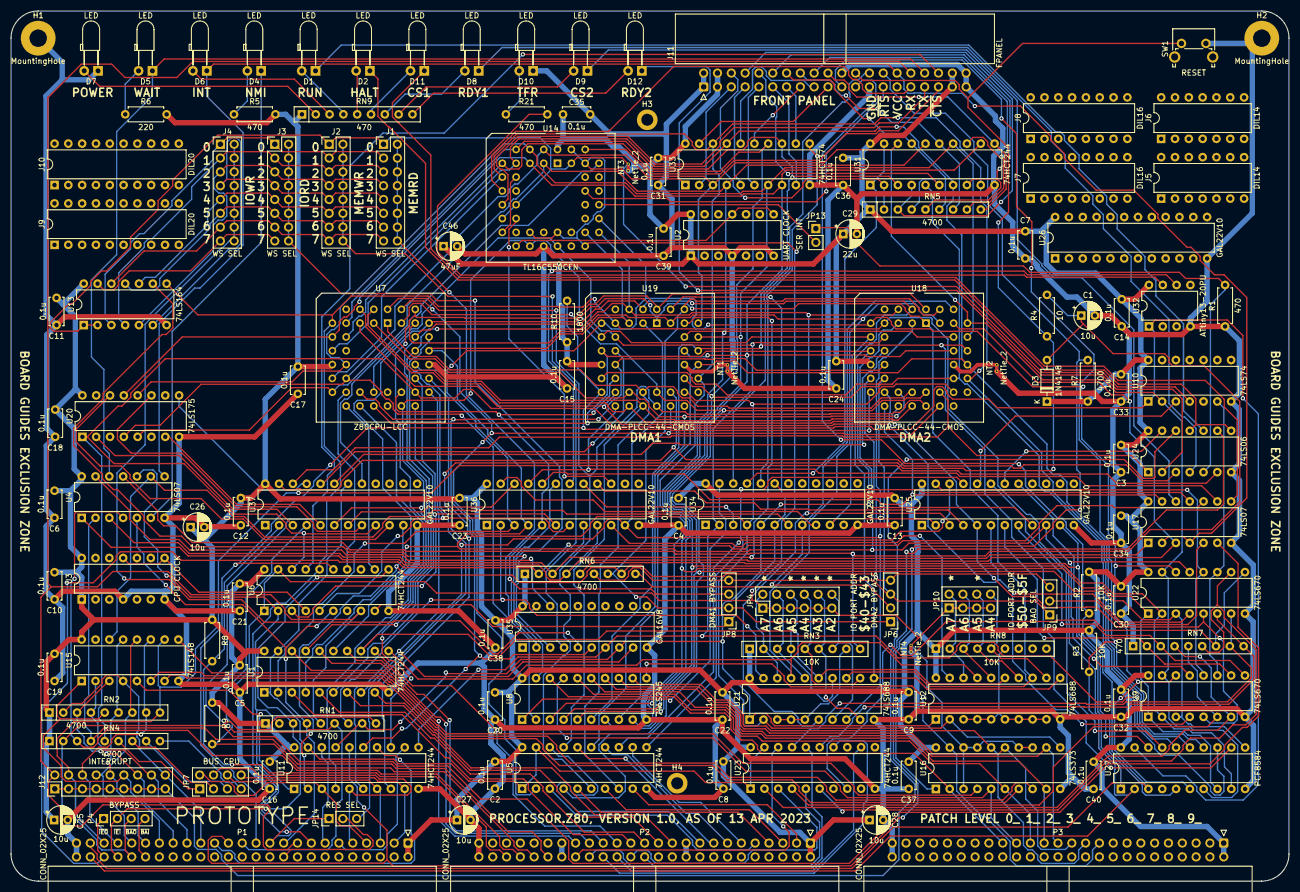
[picture p450: board processor.Z80.kicad_pcb from above]

Board: 2 copper layers, 235.0 x 160.0 mm, 140 parts (0 on the bottom side), 245 nets.
