lynchaj/duodyne/!Development/Slick/temp/CPLDs.kicad_pcb

## KiCad design !Development/Slick/temp/CPLDs.kicad_pcb (2023-09-04)

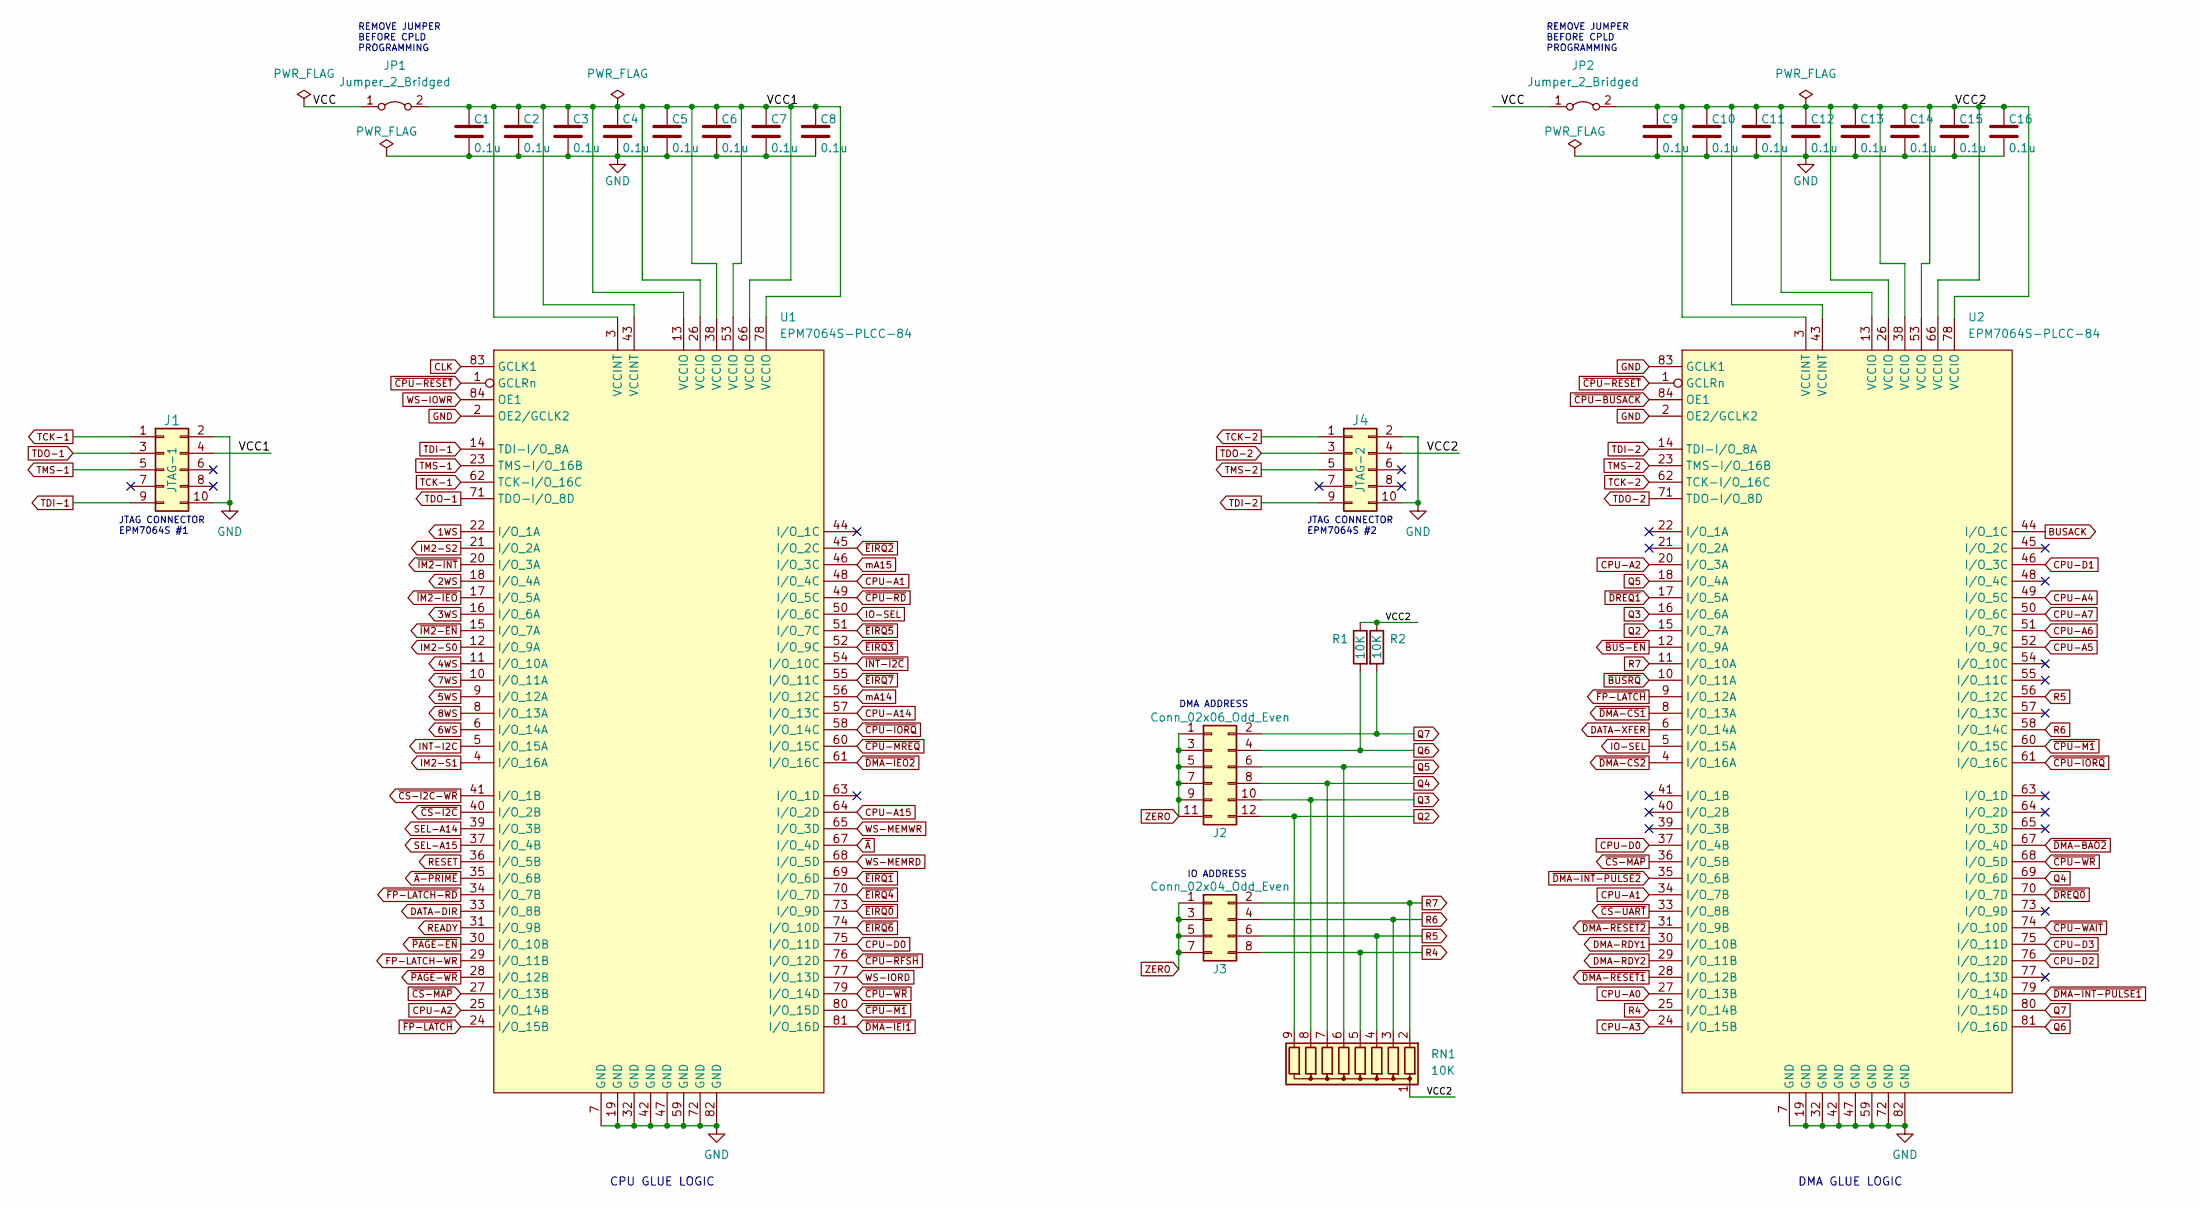
[picture p451: schematic CPLDs.kicad_sch]

Parts:
C1, C2, C3, C4, C5, C6, C7, C8, C9, C10, C11, C12, C13, C14, C15, C16: 0.1u; C_Disc_D5.0mm_W2.5mm_P5.00mm
J1: JTAG-1; IDC-Header_2x05_P2.54mm_Vertical
J2: Conn_02x06_Odd_Even; PinHeader_2x06_P2.54mm_Vertical
J3: Conn_02x04_Odd_Even; PinHeader_2x04_P2.54mm_Vertical
J4: JTAG-2; IDC-Header_2x05_P2.54mm_Vertical
JP1, JP2: Jumper_2_Bridged; PinHeader_2x01_P2.54mm_Vertical
R1, R2: 10K; R_Axial_DIN0207_L6.3mm_D2.5mm_P7.62mm_Horizontal
RN1: 10K; R_Array_SIP9
U1, U2: EPM7064S-PLCC-84; PLCC-84_THT-Socket

Connections:
1WS: U1.22 (I/O_1A)
2WS: U1.18 (I/O_4A)
3WS: U1.16 (I/O_6A)
4WS: U1.11 (I/O_10A)
5WS: U1.9 (I/O_12A)
6WS: U1.6 (I/O_14A)
7WS: U1.10 (I/O_11A)
8WS: U1.8 (I/O_13A)
/VCC: JP1.1 (A), JP2.1 (A)
/VCC1: C1.1, C2.1, C3.1, C4.1, C5.1, C6.1, C7.1, C8.1, J1.4, JP1.2 (B), U1.3 (VCCINT), U1.13 (VCCIO), U1.26 (VCCIO), U1.38 (VCCIO), U1.43 (VCCINT), U1.53 (VCCIO), U1.66 (VCCIO), U1.78 (VCCIO)
/VCC2: C9.1, C10.1, C11.1, C12.1, C13.1, C14.1, C15.1, C16.1, J4.4, JP2.2 (B), R1.1, R2.1, RN1.1 (common), U2.3 (VCCINT), U2.13 (VCCIO), U2.26 (VCCIO), U2.38 (VCCIO), U2.43 (VCCINT), U2.53 (VCCIO), U2.66 (VCCIO), U2.78 (VCCIO)
BUSACK: U2.44 (I/O_1C)
CLK: U1.83 (GCLK1)
CPU-A0: U2.27 (I/O_13B)
CPU-A1: U1.48 (I/O_4C), U2.34 (I/O_7B)
CPU-A2: U1.25 (I/O_14B), U2.20 (I/O_3A)
CPU-A3: U2.24 (I/O_15B)
CPU-A4: U2.49 (I/O_5C)
CPU-A5: U2.52 (I/O_9C)
CPU-A6: U2.51 (I/O_7C)
CPU-A7: U2.50 (I/O_6C)
CPU-A14: U1.57 (I/O_13C)
CPU-A15: U1.64 (I/O_2D)
CPU-D2: U2.76 (I/O_12D)
CPU-D3: U2.75 (I/O_11D)
DATA-DIR: U1.33 (I/O_8B)
DATA-XFER: U2.6 (I/O_14A)
DMA-RDY1: U2.30 (I/O_10B)
DMA-RDY2: U2.29 (I/O_11B)
FP-LATCH-WR: U1.29 (I/O_11B)
GND: C1.2, C2.2, C3.2, C4.2, C5.2, C6.2, C7.2, C8.2, C9.2, C10.2, C11.2, C12.2, C13.2, C14.2, C15.2, C16.2, J1.2, J1.10, J4.2, J4.10, U1.2 (OE2/GCLK2), U1.7 (GND), U1.19 (GND), U1.32 (GND), U1.42 (GND), U1.47 (GND), U1.59 (GND), U1.72 (GND), U1.82 (GND), U2.2 (OE2/GCLK2), U2.7 (GND), U2.19 (GND), U2.32 (GND), U2.42 (GND), U2.47 (GND), U2.59 (GND), U2.72 (GND), U2.82 (GND), U2.83 (GCLK1)
INT-I2C: U1.5 (I/O_15A)
IO-SEL: U1.50 (I/O_6C), U2.5 (I/O_15A)
Q2: J2.12, RN1.9 (R8), U2.15 (I/O_7A)
Q3: J2.10, RN1.8 (R7), U2.16 (I/O_6A)
Q4: J2.8, RN1.7 (R6), U2.69 (I/O_6D)
Q5: J2.6, RN1.6 (R5), U2.18 (I/O_4A)
Q6: J2.4, R1.2, U2.81 (I/O_16D)
Q7: J2.2, R2.2, U2.80 (I/O_15D)
R4: J3.8, RN1.5 (R4), U2.25 (I/O_14B)
R5: J3.6, RN1.4 (R3), U2.56 (I/O_12C)
R6: J3.4, RN1.3 (R2), U2.58 (I/O_14C)
R7: J3.2, RN1.2 (R1), U2.11 (I/O_10A)
READY: U1.31 (I/O_9B)
RESET: U1.36 (I/O_5B)
SEL-A14: U1.39 (I/O_3B)
SEL-A15: U1.37 (I/O_4B)
TCK-1: J1.1, U1.62 (TCK-I/O_16C)
TCK-2: J4.1, U2.62 (TCK-I/O_16C)
TDI-1: J1.9, U1.14 (TDI-I/O_8A)
TDI-2: J4.9, U2.14 (TDI-I/O_8A)
TDO-1: J1.3, U1.71 (TDO-I/O_8D)
TDO-2: J4.3, U2.71 (TDO-I/O_8D)
TMS-1: J1.5, U1.23 (TMS-I/O_16B)
TMS-2: J4.5, U2.23 (TMS-I/O_16B)
WS-IORD: U1.77 (I/O_13D)
WS-IOWR: U1.84 (OE1)
WS-MEMRD: U1.68 (I/O_5D)
WS-MEMWR: U1.65 (I/O_3D)
ZERO: J2.1, J2.3, J2.5, J2.7, J2.9, J2.11, J3.1, J3.3, J3.5, J3.7
mA14: U1.56 (I/O_12C)
mA15: U1.46 (I/O_3C)
~A-PRIME: U1.35 (I/O_6B)
~A: U1.67 (I/O_4D)
~BUS-EN: U2.12 (I/O_9A)
~BUSRQ: U2.10 (I/O_11A)
~CPU-BUSACK: U2.84 (OE1)
~CPU-IORQ: U1.58 (I/O_14C), U2.61 (I/O_16C)
~CPU-M1: U1.80 (I/O_15D), U2.60 (I/O_15C)
~CPU-MREQ: U1.60 (I/O_15C)
~CPU-RD: U1.49 (I/O_5C)
~CPU-RESET: U1.1 (GCLRn), U2.1 (GCLRn)
~CPU-RFSH: U1.76 (I/O_12D)
~CPU-WAIT: U2.74 (I/O_10D)
~CPU-WR: U1.79 (I/O_14D), U2.68 (I/O_5D)
~CS-I2C-WR: U1.41 (I/O_1B)
~CS-I2C: U1.40 (I/O_2B)
~CS-MAP: U1.27 (I/O_13B), U2.36 (I/O_5B)
~CS-UART: U2.33 (I/O_8B)
~DMA-BAO2: U2.67 (I/O_4D)
~DMA-CS1: U2.8 (I/O_13A)
~DMA-CS2: U2.4 (I/O_16A)
~DMA-IEI1: U1.81 (I/O_16D)
~DMA-IEO2: U1.61 (I/O_16C)
~DMA-INT-PULSE1: U2.79 (I/O_14D)
~DMA-INT-PULSE2: U2.35 (I/O_6B)
~DMA-RESET1: U2.28 (I/O_12B)
~DMA-RESET2: U2.31 (I/O_9B)
~DREQ0: U2.70 (I/O_7D)
~DREQ1: U2.17 (I/O_5A)
~EIRQ0: U1.73 (I/O_9D)
~EIRQ1: U1.69 (I/O_6D)
~EIRQ2: U1.45 (I/O_2C)
~EIRQ3: U1.52 (I/O_9C)
~EIRQ4: U1.70 (I/O_7D)
~EIRQ5: U1.51 (I/O_7C)
~EIRQ6: U1.74 (I/O_10D)
~EIRQ7: U1.55 (I/O_11C)
~FP-LATCH-RD: U1.34 (I/O_7B)
~FP-LATCH: U1.24 (I/O_15B), U2.9 (I/O_12A)
~IM2-EN: U1.15 (I/O_7A)
~IM2-IEO: U1.17 (I/O_5A)
~IM2-INT: U1.20 (I/O_3A)
~IM2-S0: U1.12 (I/O_9A)
~IM2-S1: U1.4 (I/O_16A)
~IM2-S2: U1.21 (I/O_2A)
~INT-I2C: U1.54 (I/O_10C)
~PAGE-EN: U1.30 (I/O_10B)
~PAGE-WR: U1.28 (I/O_12B)

Notes on the sheet:
REMOVE JUMPER BEFORE CPLD PROGRAMMING
DMA ADDRESS
CPU GLUE LOGIC
JTAG CONNECTOR EPM7064S #1
JTAG CONNECTOR EPM7064S #2
DMA GLUE LOGIC
IO ADDRESS

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
Board: 2 copper layers, 27 parts (0 on the bottom side), 33 nets, no tracks yet.
