lynchaj/duodyne/03 processor.Z80, V1.1/GALS.kicad_sch

## KiCad design 03 processor.Z80, V1.1/GALS.kicad_sch (2023-09-15)

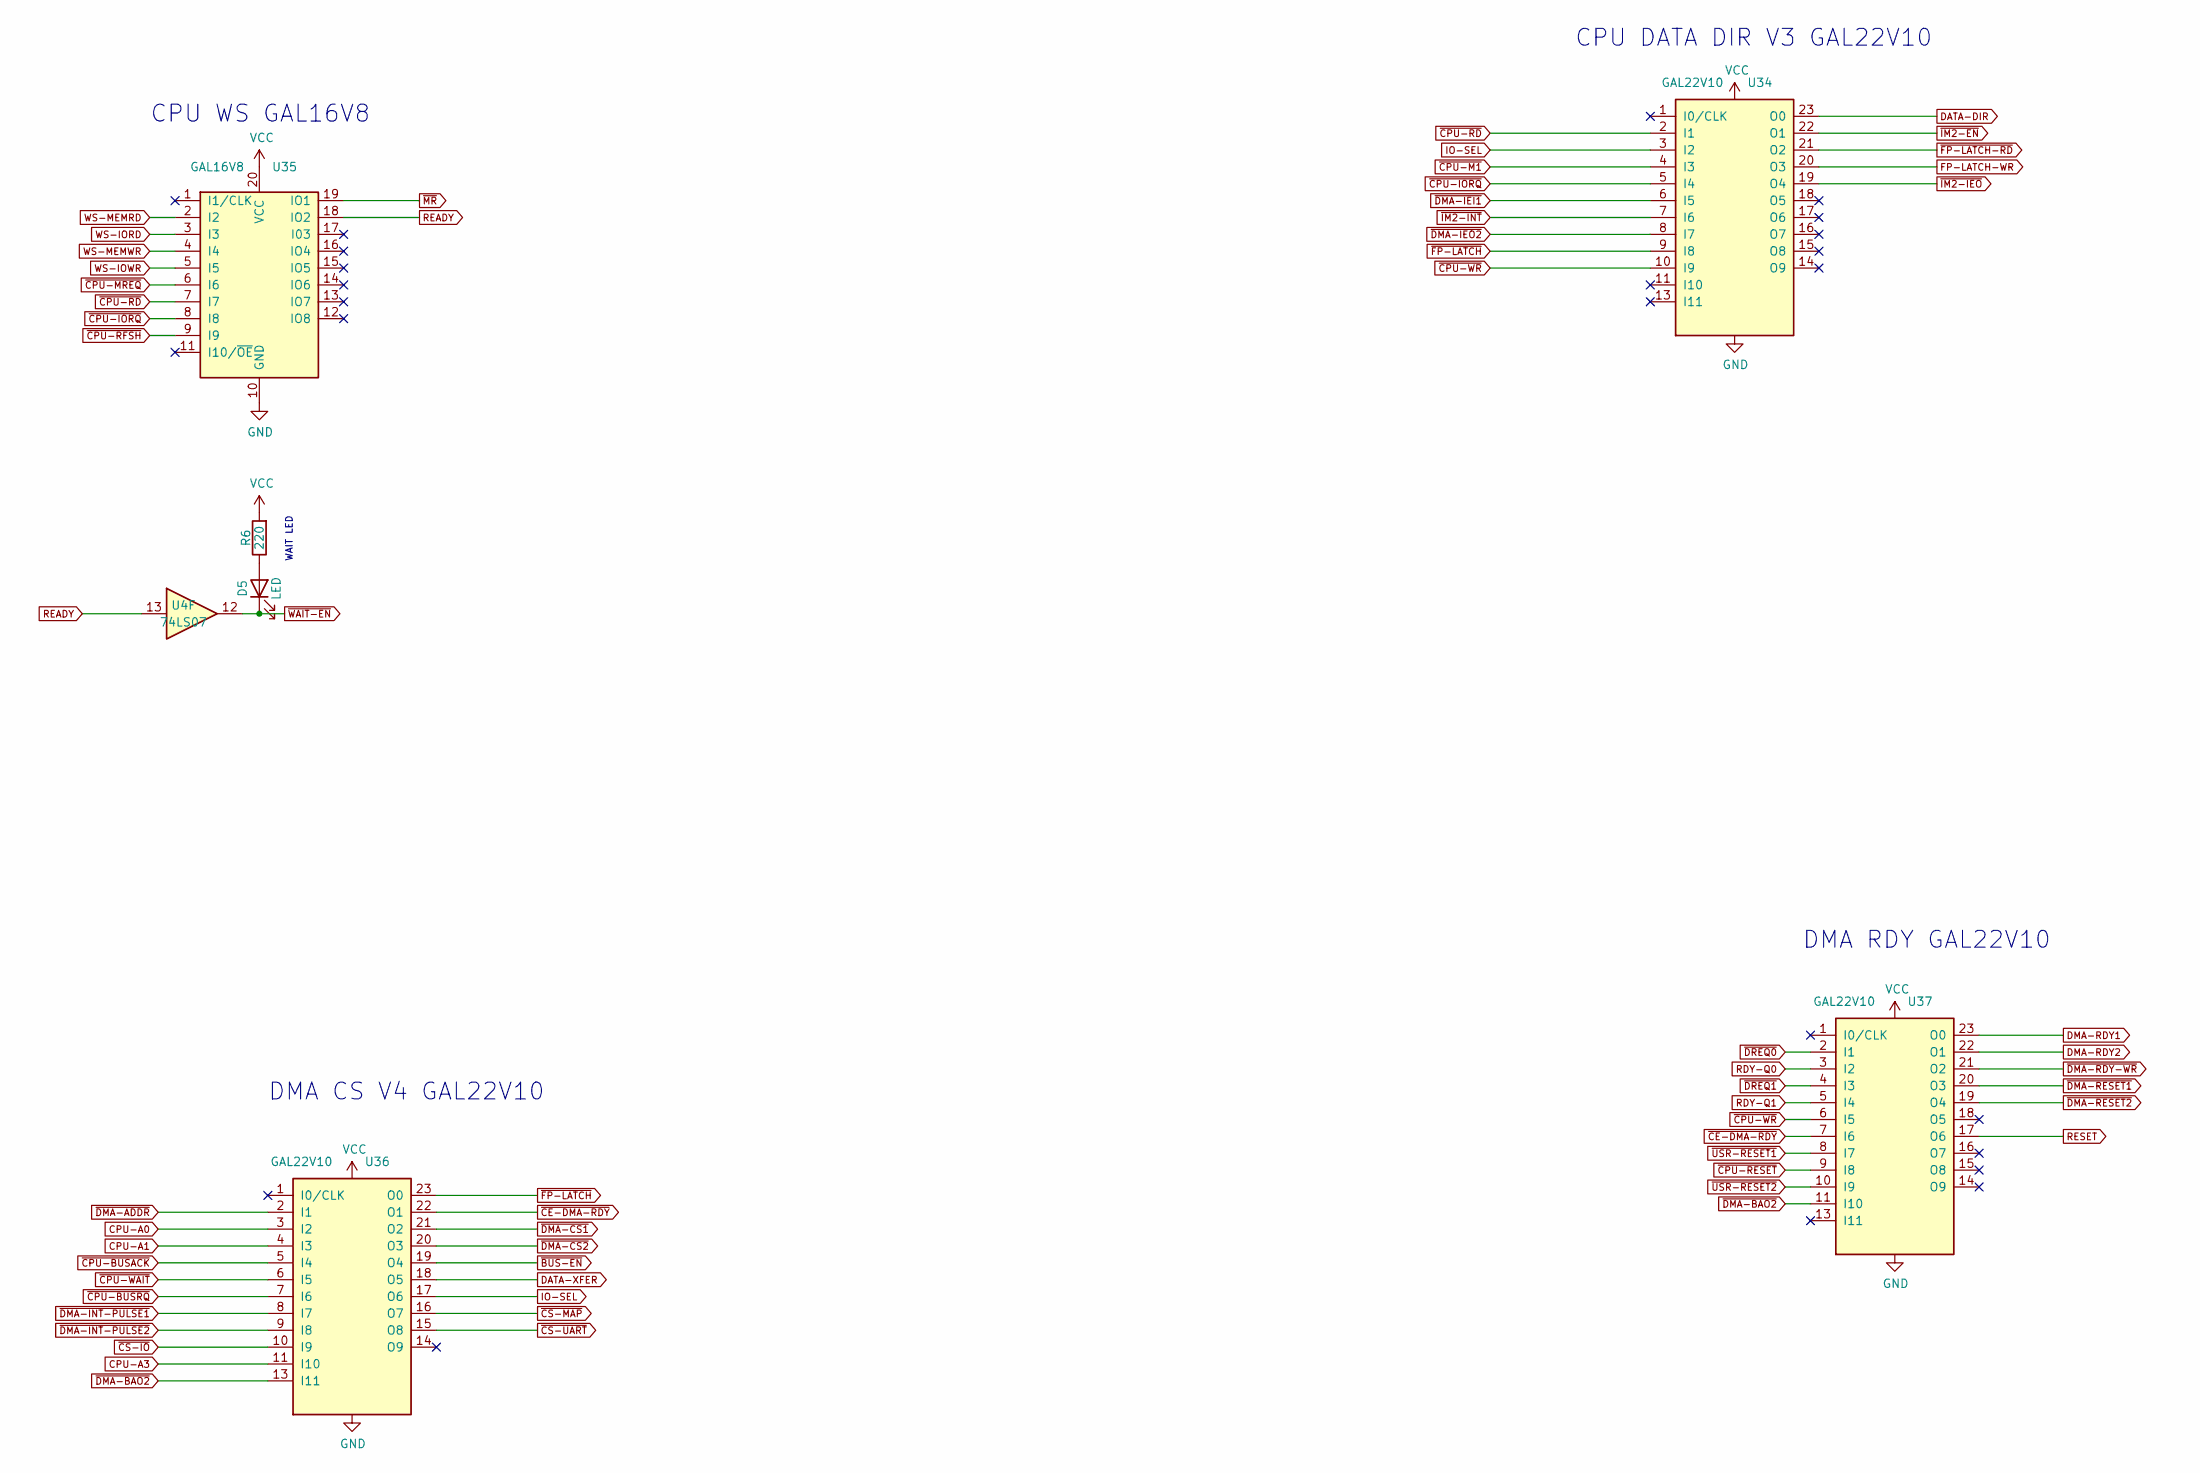
[picture p452: schematic GALS.kicad_sch]

Parts:
D5: LED; LED_D3.0mm_Horizontal_O3.81mm_Z2.0mm
R6: 220; R_Axial_DIN0207_L6.3mm_D2.5mm_P7.62mm_Horizontal
U4: 74LS07; DIP-14_W7.62mm
U34, U36, U37: GAL22V10; DIP-24_W7.62mm
U35: GAL16V8; DIP-20_W7.62mm

Connections:
CPU-A0: U36.3 (I2)
CPU-A1: U36.4 (I3)
CPU-A3: U36.11 (I10)
DATA-DIR: U34.23 (O0)
DATA-XFER: U36.18 (O5)
DMA-RDY1: U37.23 (O0)
DMA-RDY2: U37.22 (O1)
FP-LATCH-WR: U34.20 (O3)
GND: U34.12 (GND), U35.10 (GND), U36.12 (GND), U37.12 (GND)
IO-SEL: U34.3 (I2), U36.17 (O6)
unnamed: D5.2 (A), R6.1
RDY-Q0: U37.3 (I2)
RDY-Q1: U37.5 (I4)
READY: U4.13, U35.18 (IO2)
RESET: U37.17 (O6)
VCC: R6.2, U34.24 (VCC), U35.20 (VCC), U36.24 (VCC), U37.24 (VCC)
WS-IORD: U35.3 (I3)
WS-IOWR: U35.5 (I5)
WS-MEMRD: U35.2 (I2)
WS-MEMWR: U35.4 (I4)
~BUS-EN: U36.19 (O4)
~CE-DMA-RDY: U36.22 (O1), U37.7 (I6)
~CPU-BUSACK: U36.5 (I4)
~CPU-BUSRQ: U36.7 (I6)
~CPU-IORQ: U34.5 (I4), U35.8 (I8)
~CPU-M1: U34.4 (I3)
~CPU-MREQ: U35.6 (I6)
~CPU-RD: U34.2 (I1), U35.7 (I7)
~CPU-RESET: U37.9 (I8)
~CPU-RFSH: U35.9 (I9)
~CPU-WAIT: U36.6 (I5)
~CPU-WR: U34.10 (I9), U37.6 (I5)
~CS-IO: U36.10 (I9)
~CS-MAP: U36.16 (O7)
~CS-UART: U36.15 (O8)
~DMA-ADDR: U36.2 (I1)
~DMA-BAO2: U36.13 (I11), U37.11 (I10)
~DMA-CS1: U36.21 (O2)
~DMA-CS2: U36.20 (O3)
~DMA-IEI1: U34.6 (I5)
~DMA-IEO2: U34.8 (I7)
~DMA-INT-PULSE1: U36.8 (I7)
~DMA-INT-PULSE2: U36.9 (I8)
~DMA-RDY-WR: U37.21 (O2)
~DMA-RESET1: U37.20 (O3)
~DMA-RESET2: U37.19 (O4)
~DREQ0: U37.2 (I1)
~DREQ1: U37.4 (I3)
~FP-LATCH-RD: U34.21 (O2)
~FP-LATCH: U34.9 (I8), U36.23 (O0)
~IM2-EN: U34.22 (O1)
~IM2-IEO: U34.19 (O4)
~IM2-INT: U34.7 (I6)
~MR: U35.19 (IO1)
~USR-RESET1: U37.8 (I7)
~USR-RESET2: U37.10 (I9)
~WAIT-EN: D5.1 (K), U4.12

Notes on the sheet:
DMA CS V4 GAL22V10
DMA RDY GAL22V10
CPU WS GAL16V8
CPU DATA DIR V3 GAL22V10
WAIT LED
