lynchaj/duodyne/03 processor.Z80, V1.1/mapper.kicad_sch

## KiCad design 03 processor.Z80, V1.1/mapper.kicad_sch (2024-01-07)

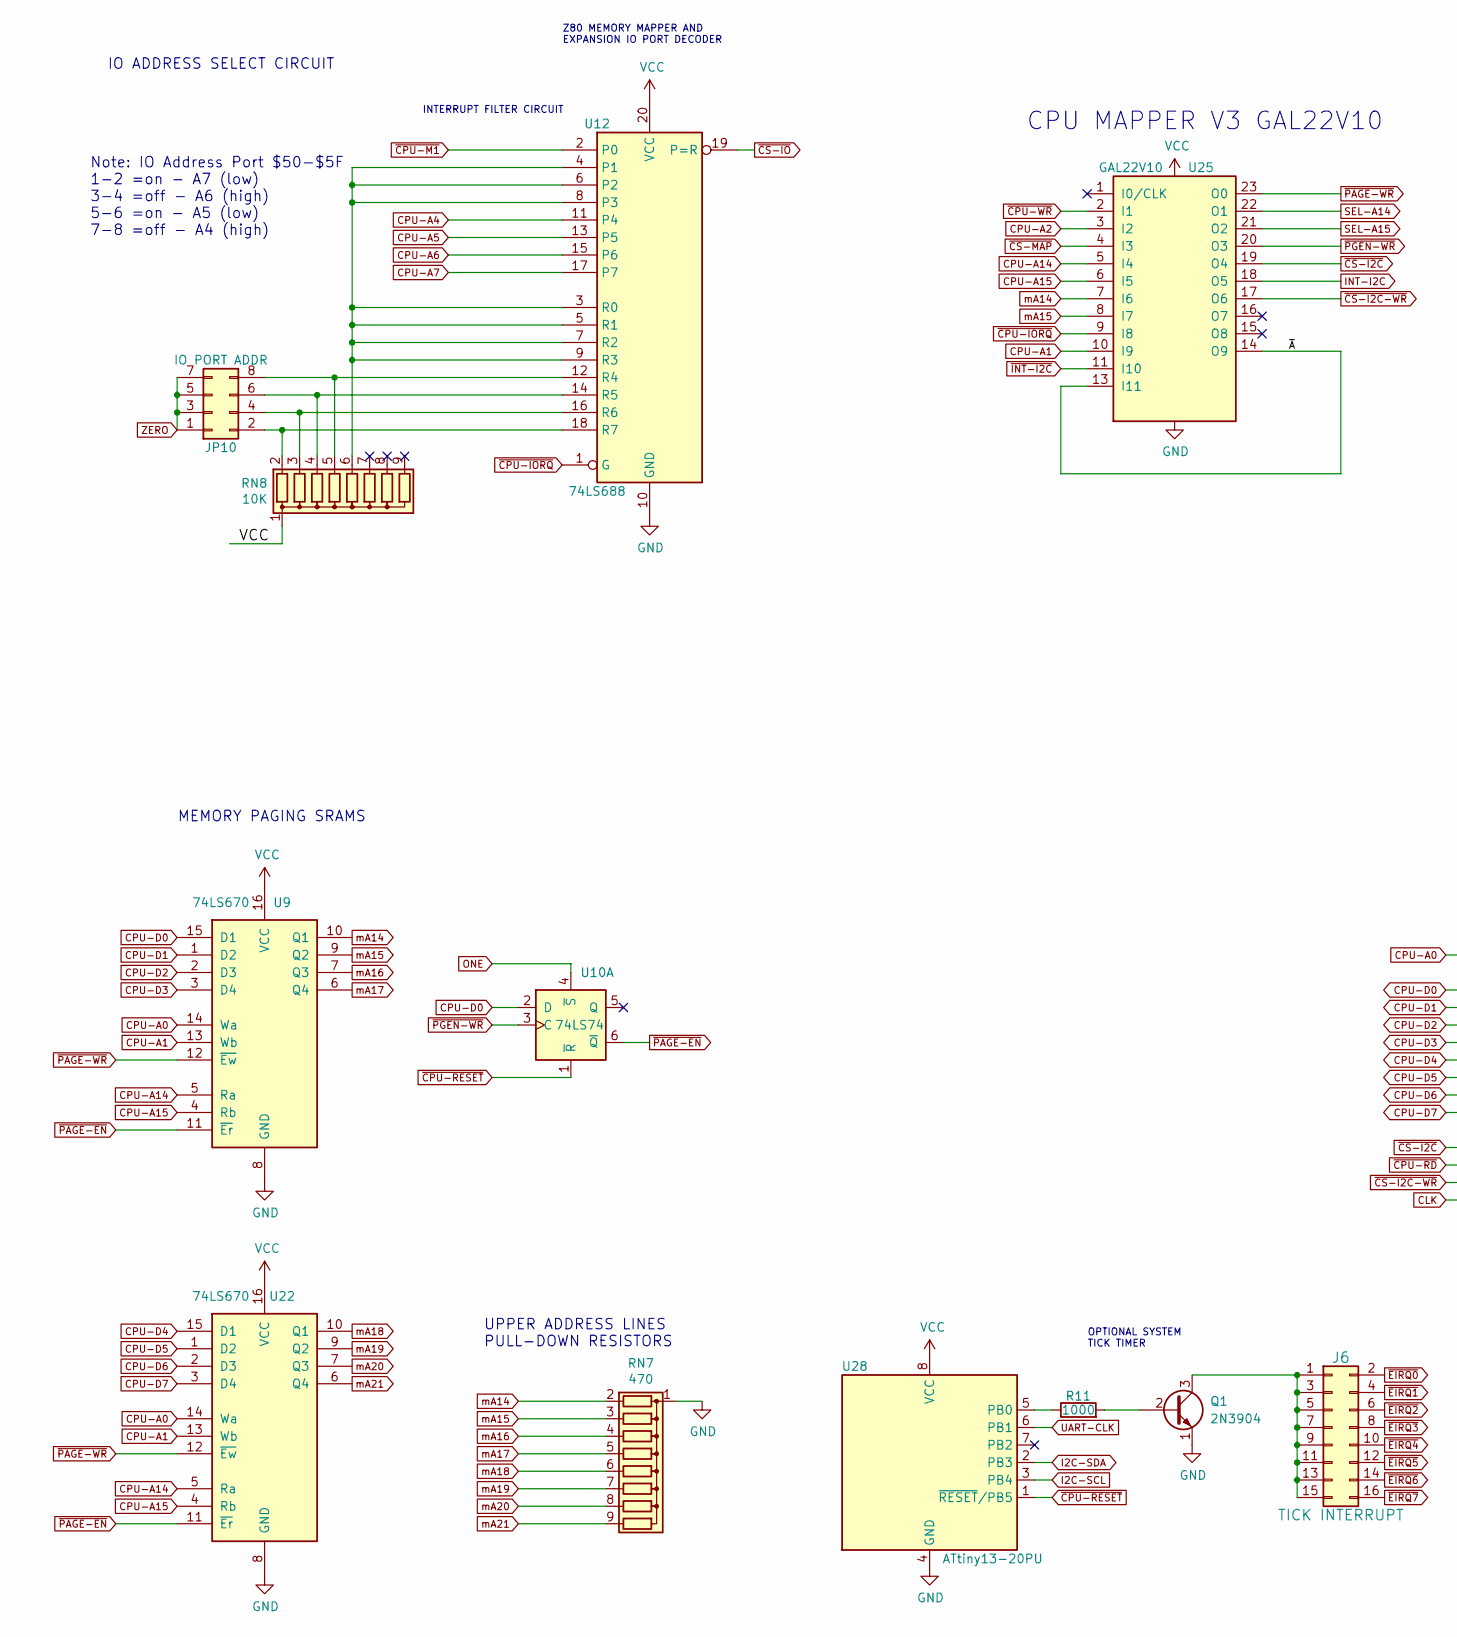
[picture p453: schematic mapper.kicad_sch, part in row 1, column 1]

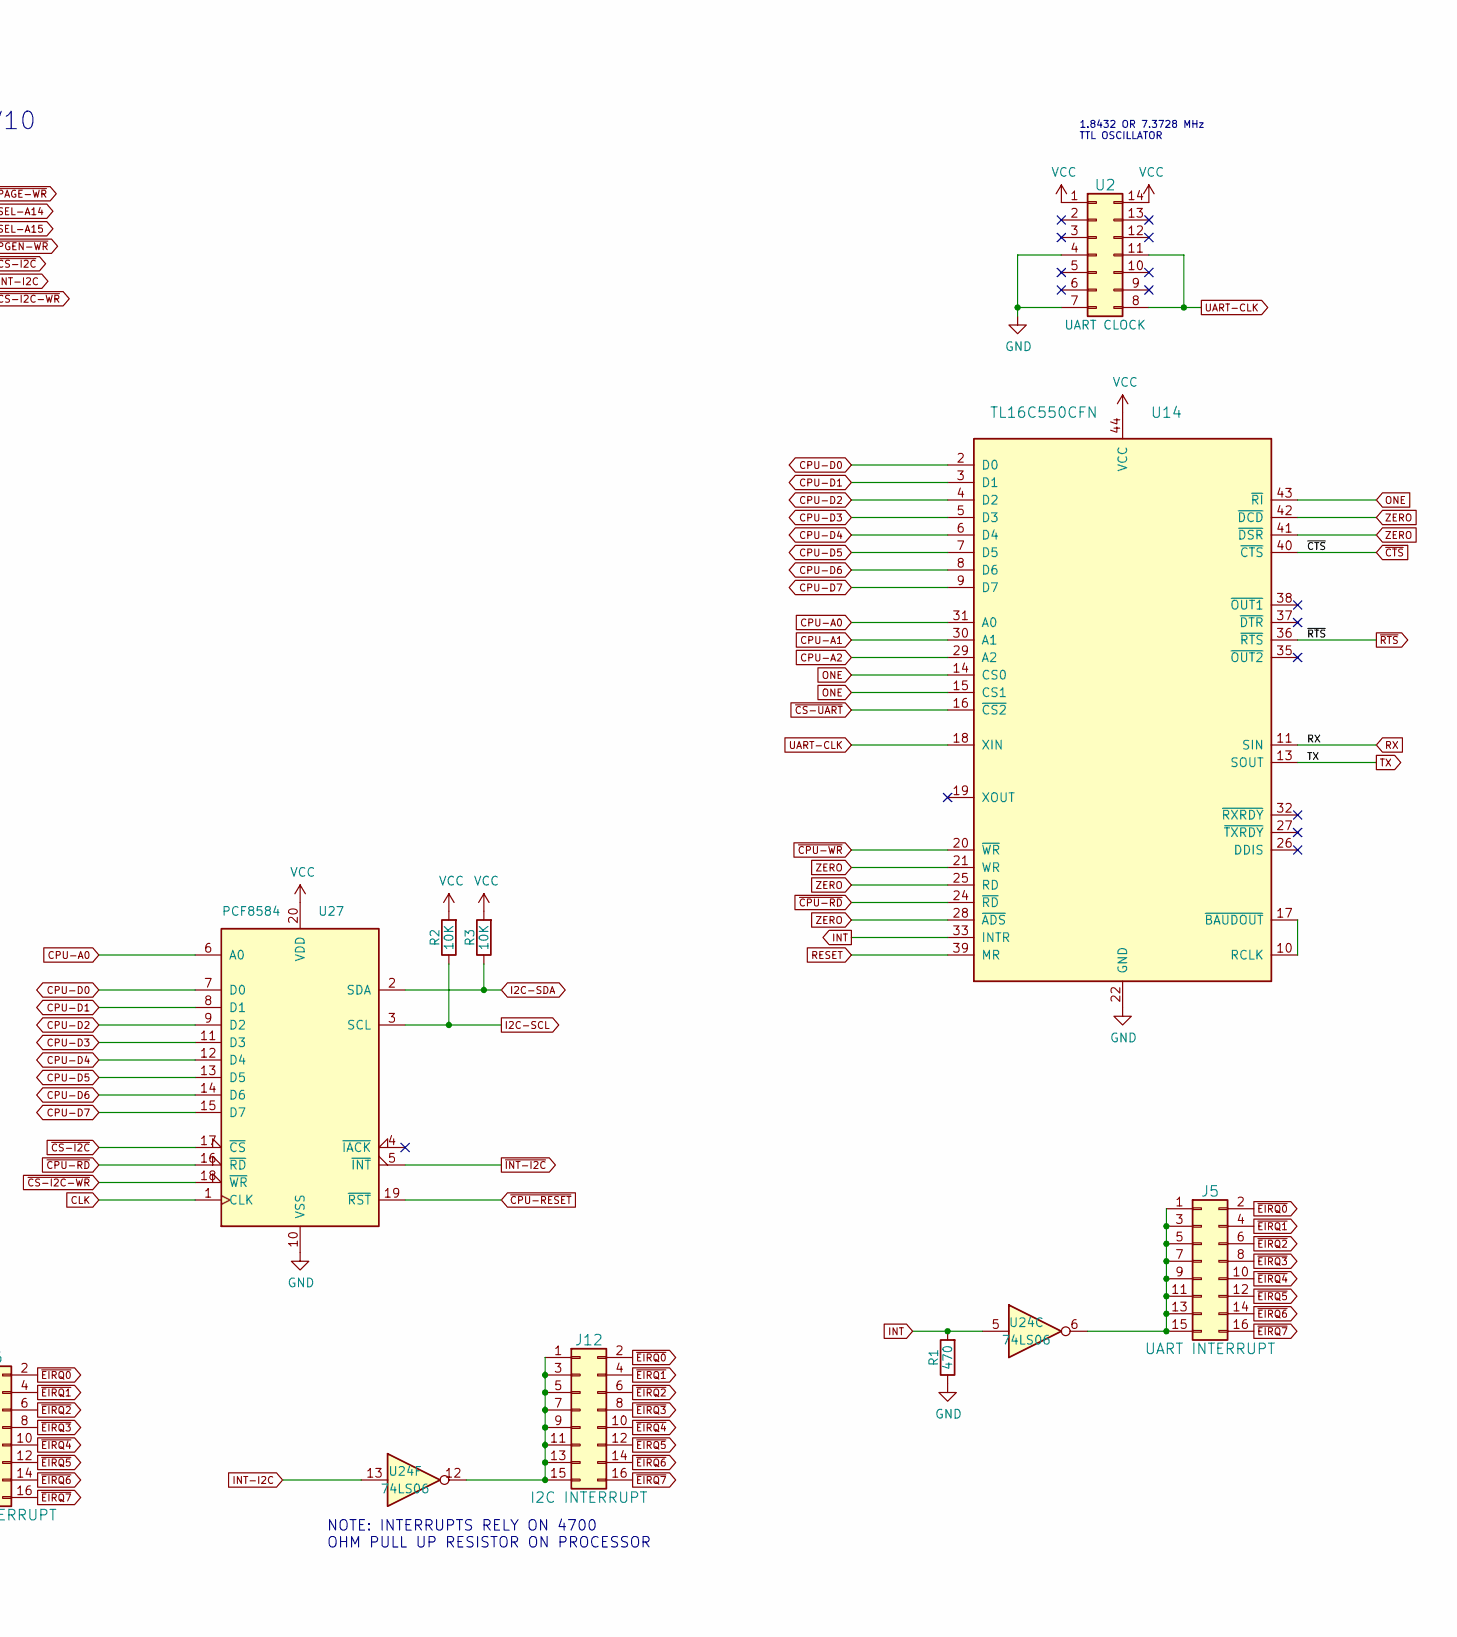
[picture p454: schematic mapper.kicad_sch, part in row 1, column 2]

Parts:
J5: UART INTERRUPT; PinHeader_2x08_P2.54mm_Vertical
J6: TICK INTERRUPT; PinHeader_2x08_P2.54mm_Vertical
J12: I2C INTERRUPT; PinHeader_2x08_P2.54mm_Vertical
JP10: IO PORT ADDR; PinHeader_2x04_P2.54mm_Vertical
Q1: 2N3904; TO-92_HandSolder
R1: 470; R_Axial_DIN0207_L6.3mm_D2.5mm_P7.62mm_Horizontal
R2, R3: 10K; R_Axial_DIN0207_L6.3mm_D2.5mm_P7.62mm_Horizontal
R11: 1000; R_Axial_DIN0207_L6.3mm_D2.5mm_P7.62mm_Horizontal
RN7: 470; R_Array_SIP9
RN8: 10K; R_Array_SIP9
U2: UART CLOCK; DIP-14_W7.62mm
U9, U22: 74LS670; DIP-16_W7.62mm
U10: 74LS74; DIP-14_W7.62mm
U12: 74LS688; DIP-20_W7.62mm
U14: TL16C550CFN; PLCC-44_THT-Socket
U24: 74LS06
U25: GAL22V10; DIP-24_W7.62mm
U27: PCF8584; DIP-20_W7.62mm
U28: ATtiny13-20PU; DIP-8_W7.62mm

Connections:
CLK: U27.1 (CLK)
CPU-A0: U9.14 (Wa), U14.31 (A0), U22.14 (Wa), U27.6 (A0)
CPU-A1: U9.13 (Wb), U14.30 (A1), U22.13 (Wb), U25.10 (I9)
CPU-A2: U14.29 (A2), U25.3 (I2)
CPU-A4: U12.11 (P4)
CPU-A5: U12.13 (P5)
CPU-A6: U12.15 (P6)
CPU-A7: U12.17 (P7)
CPU-A14: U9.5 (Ra), U22.5 (Ra), U25.5 (I4)
CPU-A15: U9.4 (Rb), U22.4 (Rb), U25.6 (I5)
CPU-D0: U9.15 (D1), U10.2 (D), U14.2 (D0), U27.7 (D0)
CPU-D1: U9.1 (D2), U14.3 (D1), U27.8 (D1)
CPU-D2: U9.2 (D3), U14.4 (D2), U27.9 (D2)
CPU-D3: U9.3 (D4), U14.5 (D3), U27.11 (D3)
CPU-D4: U14.6 (D4), U22.15 (D1), U27.12 (D4)
CPU-D5: U14.7 (D5), U22.1 (D2), U27.13 (D5)
CPU-D6: U14.8 (D6), U22.2 (D3), U27.14 (D6)
CPU-D7: U14.9 (D7), U22.3 (D4), U27.15 (D7)
GND: Q1.1 (E), R1.1, RN7.1 (common), U2.4, U2.7, U9.8 (GND), U12.10 (GND), U14.22 (GND), U22.8 (GND), U25.12 (GND), U27.10 (VSS), U28.4 (GND)
I2C-SCL: R2.1, U27.3 (SCL), U28.3 (PB4)
I2C-SDA: R3.1, U27.2 (SDA), U28.2 (PB3)
INT: R1.2, U14.33 (INTR), U24.5
INT-I2C: U24.13, U25.18 (O5)
unnamed: J5.1, J5.3, J5.5, J5.7, J5.9, J5.11, J5.13, J5.15, U24.6
unnamed: J6.1, J6.3, J6.5, J6.7, J6.9, J6.11, J6.13, J6.15, Q1.3 (C)
unnamed: J12.1, J12.3, J12.5, J12.7, J12.9, J12.11, J12.13, J12.15, U24.12
unnamed: JP10.2, RN8.2 (R1), U12.18 (R7)
unnamed: JP10.4, RN8.3 (R2), U12.16 (R6)
unnamed: JP10.6, RN8.4 (R3), U12.14 (R5)
unnamed: JP10.8, RN8.5 (R4), U12.12 (R4)
unnamed: Q1.2 (B), R11.2
unnamed: R11.1, U28.5 (PB0)
unnamed: RN8.6 (R5), U12.3 (R0), U12.4 (P1), U12.5 (R1), U12.6 (P2), U12.7 (R2), U12.8 (P3), U12.9 (R3)
unnamed: U14.10 (RCLK), U14.17 (~BAUDOUT)
ONE: U10.4 (~S), U14.14 (CS0), U14.15 (CS1), U14.43 (~RI)
RESET: U14.39 (MR)
RX: U14.11 (SIN)
SEL-A14: U25.22 (O1)
SEL-A15: U25.21 (O2)
TX: U14.13 (SOUT)
UART-CLK: U2.8, U2.11, U14.18 (XIN), U28.6 (PB1)
VCC: R2.2, R3.2, RN8.1 (common), U2.1, U2.14, U9.16 (VCC), U12.20 (VCC), U14.44 (VCC), U22.16 (VCC), U25.24 (VCC), U27.20 (VDD), U28.8 (VCC)
ZERO: JP10.1, JP10.3, JP10.5, JP10.7, U14.21 (WR), U14.25 (RD), U14.28 (~ADS), U14.41 (~DSR), U14.42 (~DCD)
mA14: RN7.2 (R1), U9.10 (Q1), U25.7 (I6)
mA15: RN7.3 (R2), U9.9 (Q2), U25.8 (I7)
mA16: RN7.4 (R3), U9.7 (Q3)
mA17: RN7.5 (R4), U9.6 (Q4)
mA18: RN7.6 (R5), U22.10 (Q1)
mA19: RN7.7 (R6), U22.9 (Q2)
mA20: RN7.8 (R7), U22.7 (Q3)
mA21: RN7.9 (R8), U22.6 (Q4)
~A: U25.13 (I11), U25.14 (O9)
~CPU-IORQ: U12.1 (G), U25.9 (I8)
~CPU-M1: U12.2 (P0)
~CPU-RD: U14.24 (~RD), U27.16 (~RD)
~CPU-RESET: U10.1 (~R), U27.19 (~RST), U28.1 (~RESET/PB5)
~CPU-WR: U14.20 (~WR), U25.2 (I1)
~CS-I2C-WR: U25.17 (O6), U27.18 (~WR)
~CS-I2C: U25.19 (O4), U27.17 (~CS)
~CS-IO: U12.19 (P=R)
~CS-MAP: U25.4 (I3)
~CS-UART: U14.16 (~CS2)
~CTS: U14.40 (~CTS)
~EIRQ0: J5.2, J6.2, J12.2
~EIRQ1: J5.4, J6.4, J12.4
~EIRQ2: J5.6, J6.6, J12.6
~EIRQ3: J5.8, J6.8, J12.8
~EIRQ4: J5.10, J6.10, J12.10
~EIRQ5: J5.12, J6.12, J12.12
~EIRQ6: J5.14, J6.14, J12.14
~EIRQ7: J5.16, J6.16, J12.16
~INT-I2C: U25.11 (I10), U27.5 (~INT)
~PAGE-EN: U9.11 (~Er), U10.6 (~Q), U22.11 (~Er)
~PAGE-WR: U9.12 (~Ew), U22.12 (~Ew), U25.23 (O0)
~PGEN-WR: U10.3 (C), U25.20 (O3)
~RTS: U14.36 (~RTS)

Notes on the sheet:
CPU MAPPER V3 GAL22V10
Z80 MEMORY MAPPER AND EXPANSION IO PORT DECODER
UPPER ADDRESS LINES PULL-DOWN RESISTORS
MEMORY PAGING SRAMS
OPTIONAL SYSTEM TICK TIMER
IO ADDRESS SELECT CIRCUIT
INTERRUPT FILTER CIRCUIT
1.8432 OR 7.3728 MHz TTL OSCILLATOR
NOTE: INTERRUPTS RELY ON 4700 OHM PULL UP RESISTOR ON PROCESSOR
Note: IO Address Port $50-$5F 1-2 =on - A7 (low) 3-4 =off - A6 (high) 5-6 =on - A5 (low) 7-8 =off - A4 (high)
