lynchaj/duodyne/24 backplane.20-slot, V1.0/backplane.20-slot.kicad_sch

## KiCad design 24 backplane.20-slot, V1.0/backplane.20-slot.kicad_sch (2024-10-28)

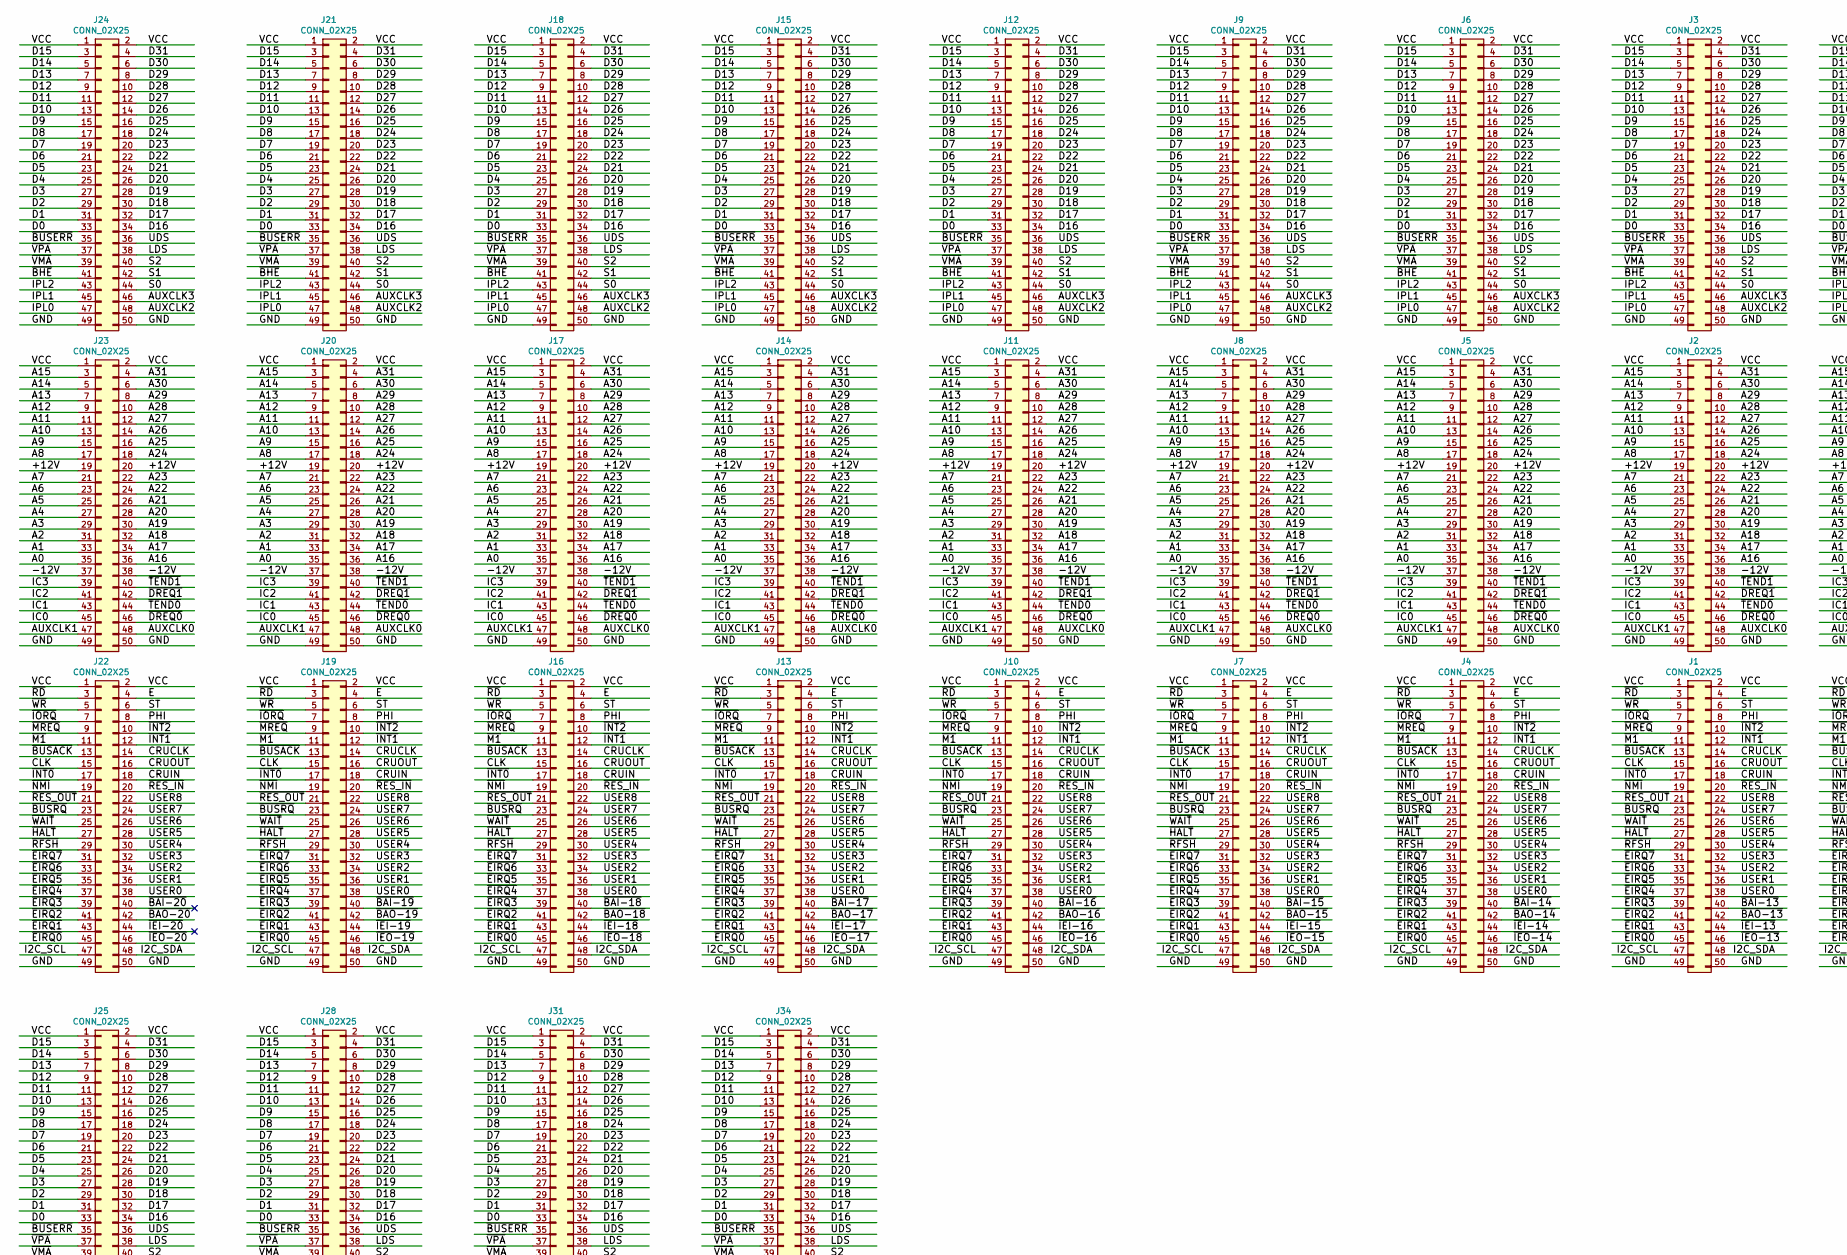
[picture p455: schematic backplane.20-slot.kicad_sch, part in row 1, column 1]

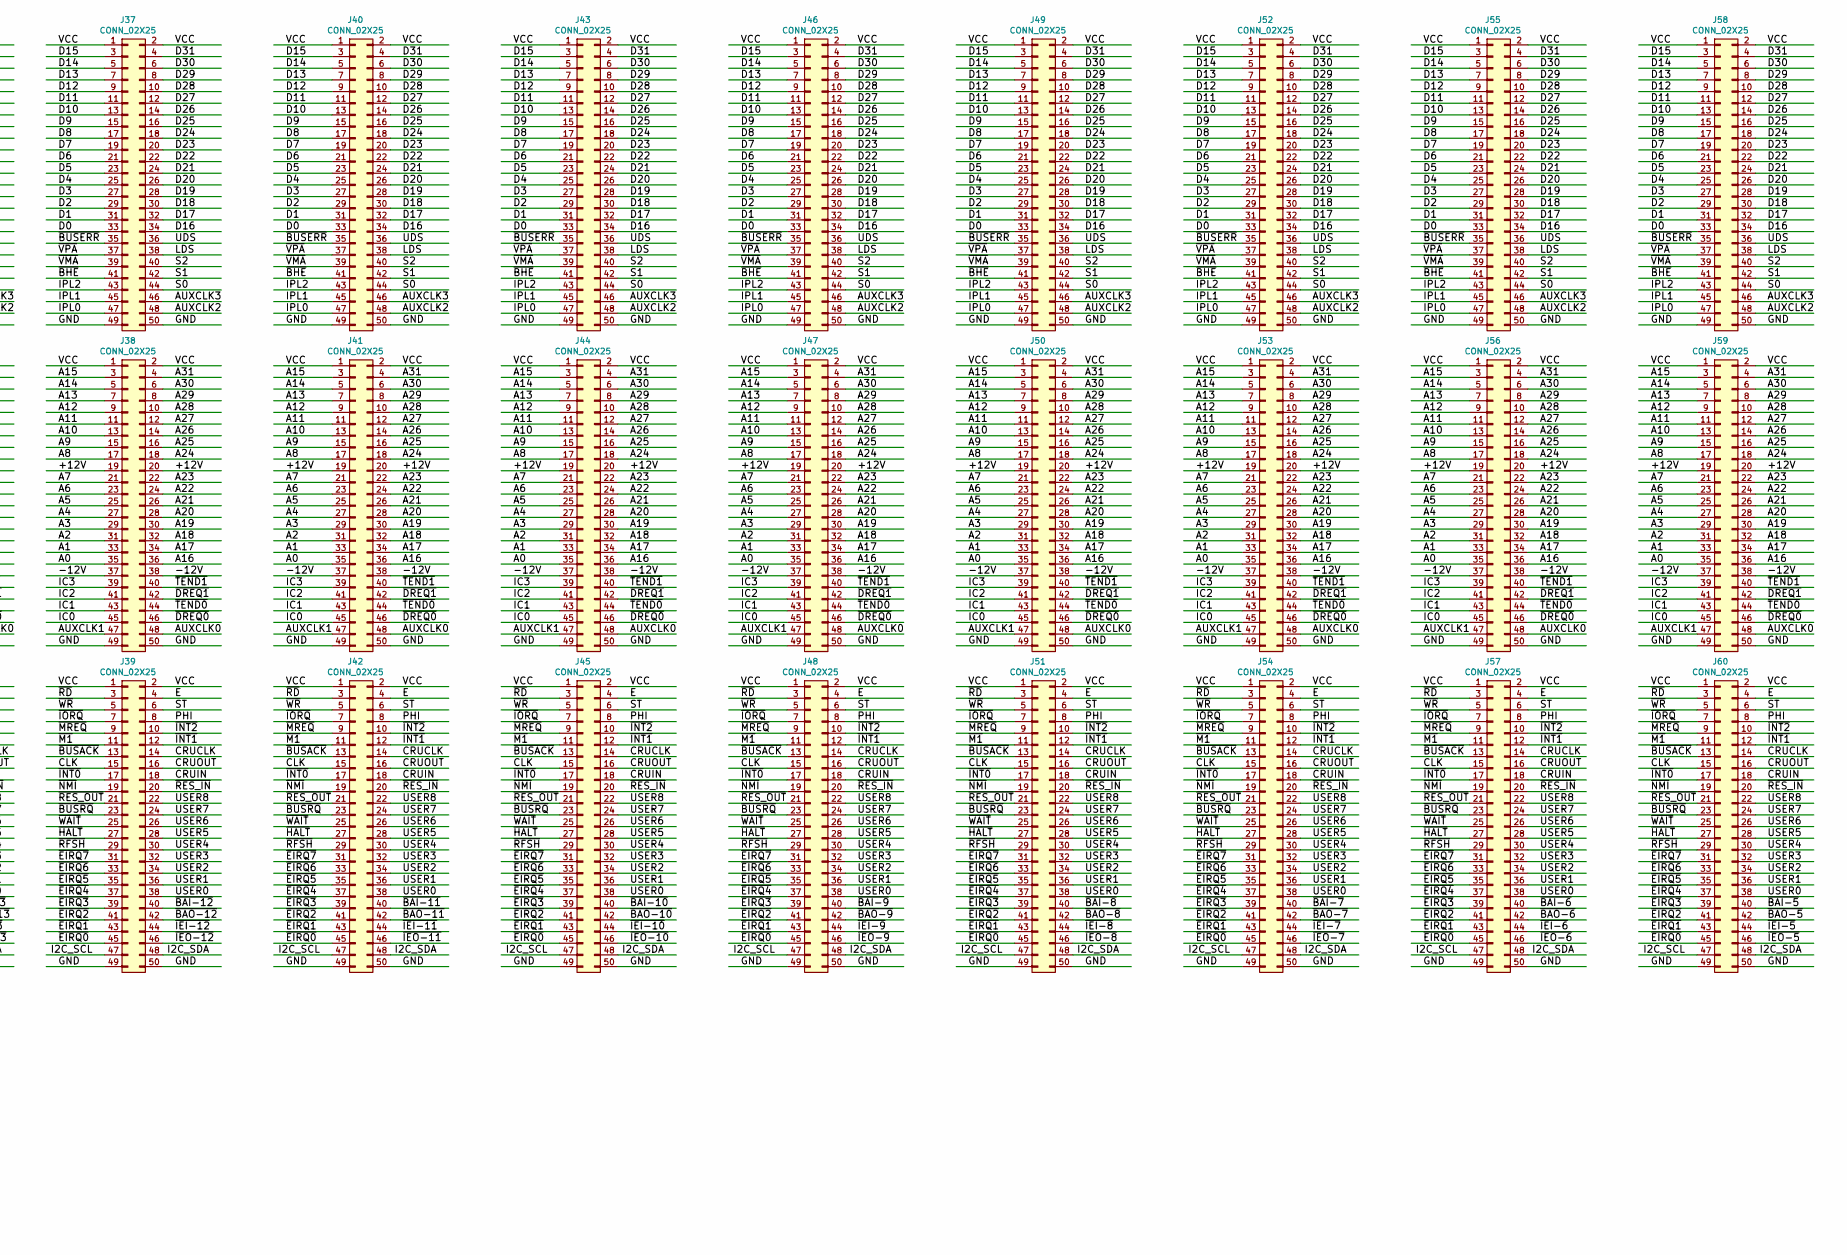
[picture p456: schematic backplane.20-slot.kicad_sch, part in row 1, column 2]

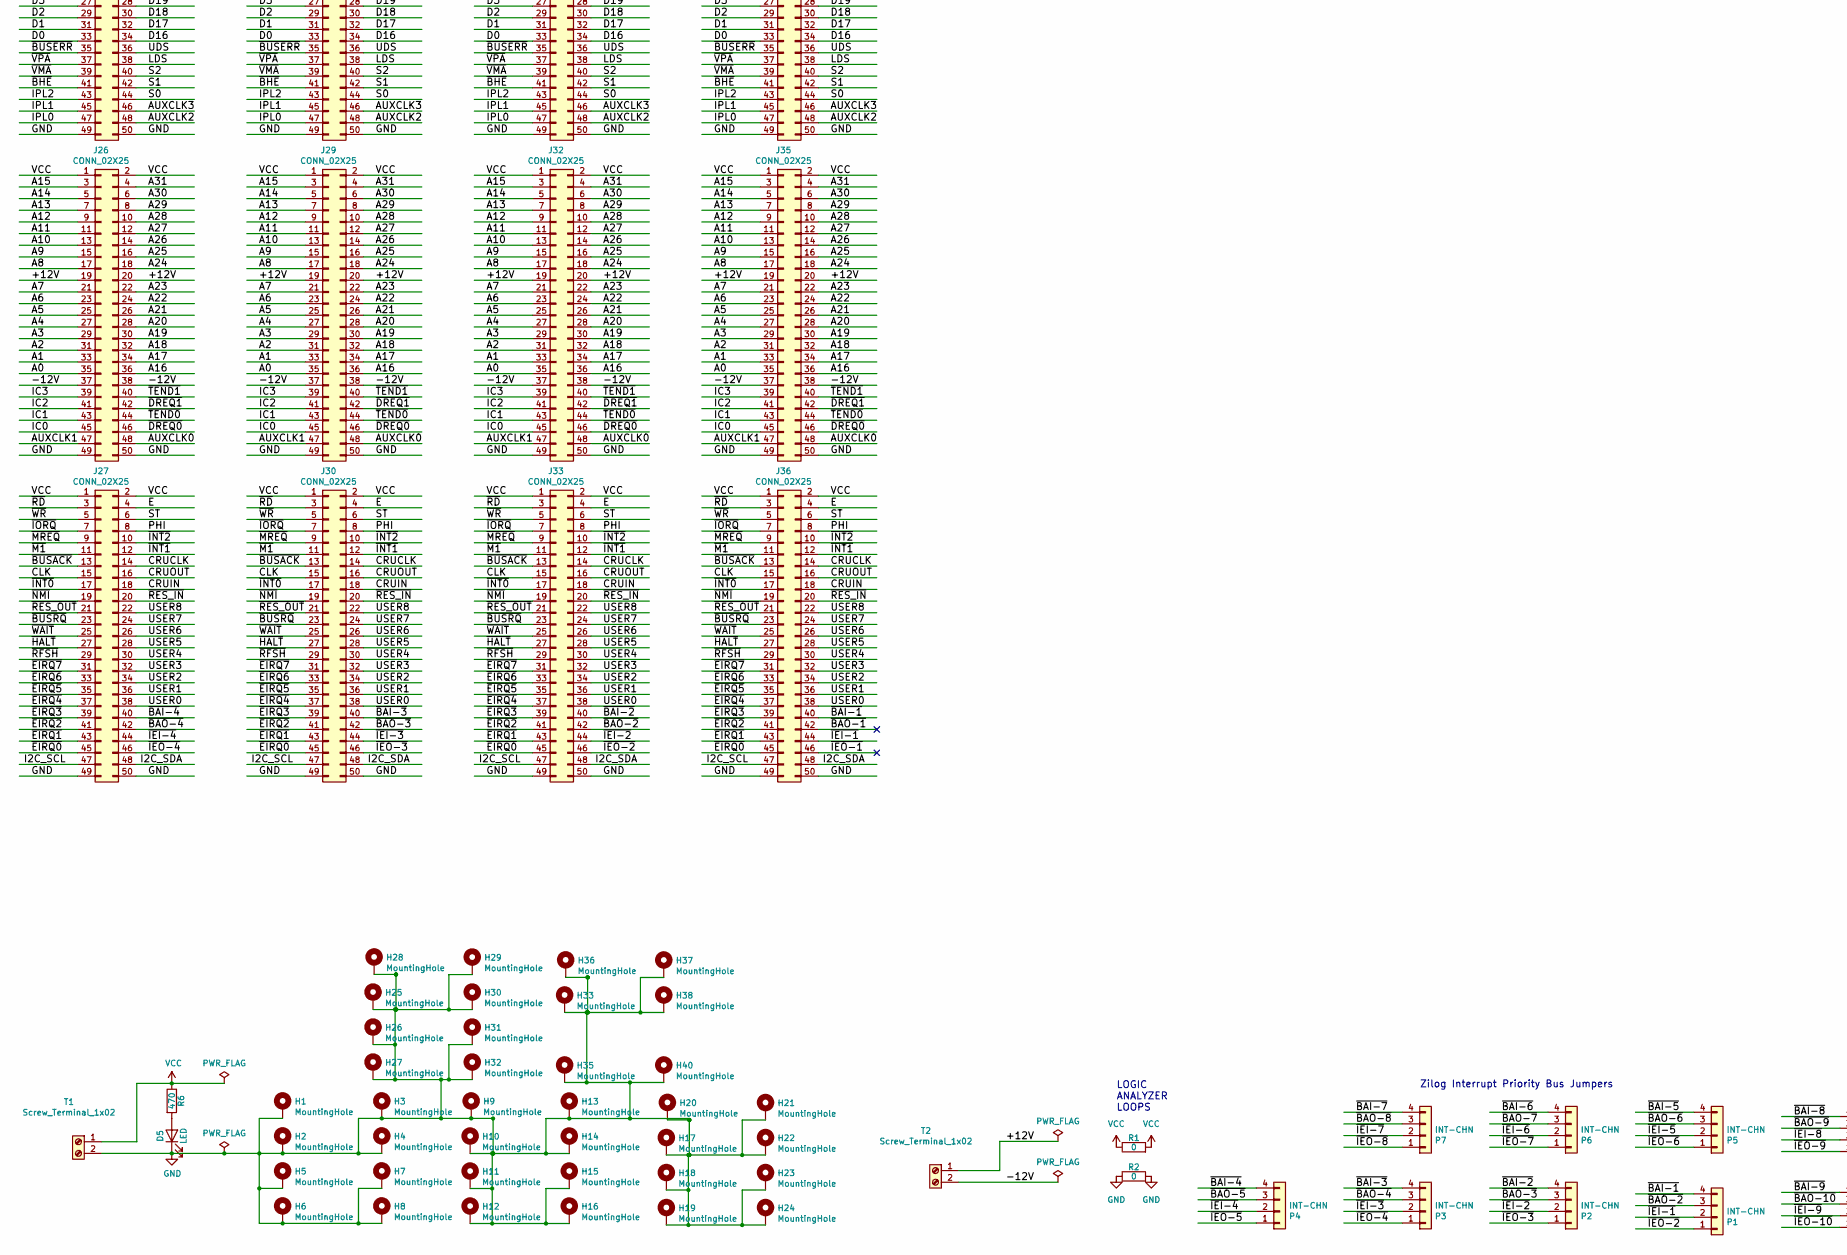
[picture p457: schematic backplane.20-slot.kicad_sch, part in row 2, column 1]

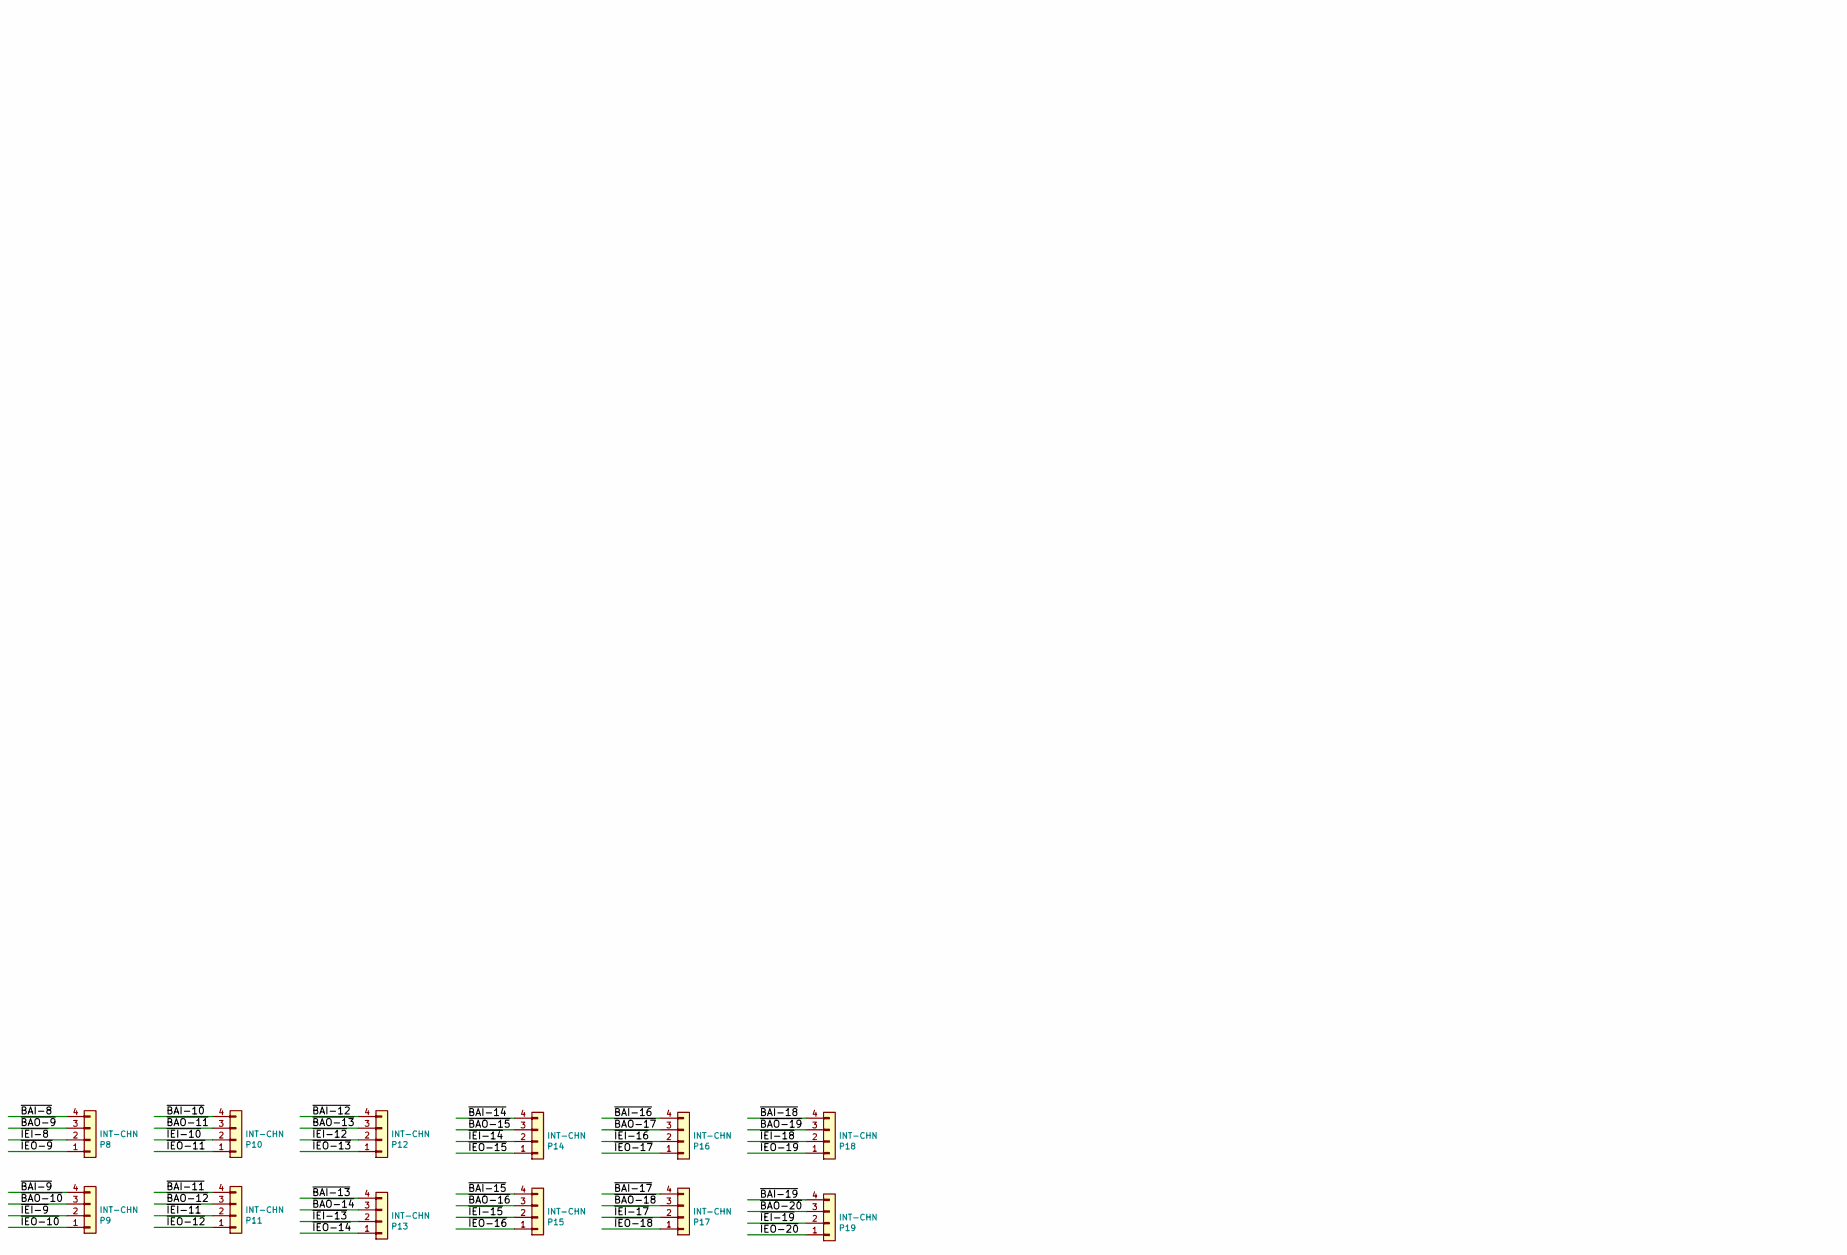
[picture p458: schematic backplane.20-slot.kicad_sch, part in row 2, column 2]

Parts:
D5: LED; LED_D3.0mm
H1, H2, H3, H4, H5, H6, H7, H8, H9, H10, H11, H12, H13, H14, H15, H16, H17, H18, H19, H20, H21, H22, H23, H24, H25, H26, H27, H28, H29, H30, H31, H32, H33, H35, H36, H37, H38, H40: MountingHole; MountingHole_3.2mm_M3_Pad
J1, J2, J3, J4, J5, J6, J7, J8, J9, J10, J11, J12, J13, J14, J15, J16, J17, J18, J19, J20, J21, J22, J23, J24, J25, J26, J27, J28, J29, J30, J31, J32, J33, J34, J35, J36, J37, J38, J39, J40, J41, J42, J43, J44, J45, J46, J47, J48, J49, J50, J51, J52, J53, J54, J55, J56, J57, J58, J59, J60: CONN_02X25; PinSocket_2x25_P2.54mm_Vertical
P1, P2, P3, P4, P5, P6, P7, P8, P9, P10, P11, P12, P13, P14, P15, P16, P17, P18, P19: INT-CHN; PinHeader_1x04_P2.54mm_Vertical
R1, R2: 0; R_Axial_DIN0207_L6.3mm_D2.5mm_P7.62mm_Horizontal
R6: 470; R_Axial_DIN0207_L6.3mm_D2.5mm_P7.62mm_Horizontal
T1, T2: Screw_Terminal_1x02; TerminalBlock_Phoenix_MKDS-1,5-2-5.08_1x02_P5.08mm_Horizont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

Connections:
+12V: J2.19, J2.20, J5.19, J5.20, J8.19, J8.20, J11.19, J11.20, J14.19, J14.20, J17.19, J17.20, J20.19, J20.20, J23.19, J23.20, J26.19, J26.20, J29.19, J29.20, J32.19, J32.20, J35.19, J35.20, J38.19, J38.20, J41.19, J41.20, J44.19, J44.20, J47.19, J47.20, J50.19, J50.20, J53.19, J53.20, J56.19, J56.20, J59.19, J59.20, T2.1
-12V: J2.37, J2.38, J5.37, J5.38, J8.37, J8.38, J11.37, J11.38, J14.37, J14.38, J17.37, J17.38, J20.37, J20.38, J23.37, J23.38, J26.37, J26.38, J29.37, J29.38, J32.37, J32.38, J35.37, J35.38, J38.37, J38.38, J41.37, J41.38, J44.37, J44.38, J47.37, J47.38, J50.37, J50.38, J53.37, J53.38, J56.37, J56.38, J59.37, J59.38, T2.2
A0: J2.35, J5.35, J8.35, J11.35, J14.35, J17.35, J20.35, J23.35, J26.35, J29.35, J32.35, J35.35, J38.35, J41.35, J44.35, J47.35, J50.35, J53.35, J56.35, J59.35
A1: J2.33, J5.33, J8.33, J11.33, J14.33, J17.33, J20.33, J23.33, J26.33, J29.33, J32.33, J35.33, J38.33, J41.33, J44.33, J47.33, J50.33, J53.33, J56.33, J59.33
A2: J2.31, J5.31, J8.31, J11.31, J14.31, J17.31, J20.31, J23.31, J26.31, J29.31, J32.31, J35.31, J38.31, J41.31, J44.31, J47.31, J50.31, J53.31, J56.31, J59.31
A3: J2.29, J5.29, J8.29, J11.29, J14.29, J17.29, J20.29, J23.29, J26.29, J29.29, J32.29, J35.29, J38.29, J41.29, J44.29, J47.29, J50.29, J53.29, J56.29, J59.29
A4: J2.27, J5.27, J8.27, J11.27, J14.27, J17.27, J20.27, J23.27, J26.27, J29.27, J32.27, J35.27, J38.27, J41.27, J44.27, J47.27, J50.27, J53.27, J56.27, J59.27
A5: J2.25, J5.25, J8.25, J11.25, J14.25, J17.25, J20.25, J23.25, J26.25, J29.25, J32.25, J35.25, J38.25, J41.25, J44.25, J47.25, J50.25, J53.25, J56.25, J59.25
A6: J2.23, J5.23, J8.23, J11.23, J14.23, J17.23, J20.23, J23.23, J26.23, J29.23, J32.23, J35.23, J38.23, J41.23, J44.23, J47.23, J50.23, J53.23, J56.23, J59.23
A7: J2.21, J5.21, J8.21, J11.21, J14.21, J17.21, J20.21, J23.21, J26.21, J29.21, J32.21, J35.21, J38.21, J41.21, J44.21, J47.21, J50.21, J53.21, J56.21, J59.21
A8: J2.17, J5.17, J8.17, J11.17, J14.17, J17.17, J20.17, J23.17, J26.17, J29.17, J32.17, J35.17, J38.17, J41.17, J44.17, J47.17, J50.17, J53.17, J56.17, J59.17
A9: J2.15, J5.15, J8.15, J11.15, J14.15, J17.15, J20.15, J23.15, J26.15, J29.15, J32.15, J35.15, J38.15, J41.15, J44.15, J47.15, J50.15, J53.15, J56.15, J59.15
A10: J2.13, J5.13, J8.13, J11.13, J14.13, J17.13, J20.13, J23.13, J26.13, J29.13, J32.13, J35.13, J38.13, J41.13, J44.13, J47.13, J50.13, J53.13, J56.13, J59.13
A11: J2.11, J5.11, J8.11, J11.11, J14.11, J17.11, J20.11, J23.11, J26.11, J29.11, J32.11, J35.11, J38.11, J41.11, J44.11, J47.11, J50.11, J53.11, J56.11, J59.11
A12: J2.9, J5.9, J8.9, J11.9, J14.9, J17.9, J20.9, J23.9, J26.9, J29.9, J32.9, J35.9, J38.9, J41.9, J44.9, J47.9, J50.9, J53.9, J56.9, J59.9
A13: J2.7, J5.7, J8.7, J11.7, J14.7, J17.7, J20.7, J23.7, J26.7, J29.7, J32.7, J35.7, J38.7, J41.7, J44.7, J47.7, J50.7, J53.7, J56.7, J59.7
A14: J2.5, J5.5, J8.5, J11.5, J14.5, J17.5, J20.5, J23.5, J26.5, J29.5, J32.5, J35.5, J38.5, J41.5, J44.5, J47.5, J50.5, J53.5, J56.5, J59.5
A15: J2.3, J5.3, J8.3, J11.3, J14.3, J17.3, J20.3, J23.3, J26.3, J29.3, J32.3, J35.3, J38.3, J41.3, J44.3, J47.3, J50.3, J53.3, J56.3, J59.3
A16: J2.36, J5.36, J8.36, J11.36, J14.36, J17.36, J20.36, J23.36, J26.36, J29.36, J32.36, J35.36, J38.36, J41.36, J44.36, J47.36, J50.36, J53.36, J56.36, J59.36
A17: J2.34, J5.34, J8.34, J11.34, J14.34, J17.34, J20.34, J23.34, J26.34, J29.34, J32.34, J35.34, J38.34, J41.34, J44.34, J47.34, J50.34, J53.34, J56.34, J59.34
A18: J2.32, J5.32, J8.32, J11.32, J14.32, J17.32, J20.32, J23.32, J26.32, J29.32, J32.32, J35.32, J38.32, J41.32, J44.32, J47.32, J50.32, J53.32, J56.32, J59.32
A19: J2.30, J5.30, J8.30, J11.30, J14.30, J17.30, J20.30, J23.30, J26.30, J29.30, J32.30, J35.30, J38.30, J41.30, J44.30, J47.30, J50.30, J53.30, J56.30, J59.30
A20: J2.28, J5.28, J8.28, J11.28, J14.28, J17.28, J20.28, J23.28, J26.28, J29.28, J32.28, J35.28, J38.28, J41.28, J44.28, J47.28, J50.28, J53.28, J56.28, J59.28
A21: J2.26, J5.26, J8.26, J11.26, J14.26, J17.26, J20.26, J23.26, J26.26, J29.26, J32.26, J35.26, J38.26, J41.26, J44.26, J47.26, J50.26, J53.26, J56.26, J59.26
A22: J2.24, J5.24, J8.24, J11.24, J14.24, J17.24, J20.24, J23.24, J26.24, J29.24, J32.24, J35.24, J38.24, J41.24, J44.24, J47.24, J50.24, J53.24, J56.24, J59.24
A23: J2.22, J5.22, J8.22, J11.22, J14.22, J17.22, J20.22, J23.22, J26.22, J29.22, J32.22, J35.22, J38.22, J41.22, J44.22, J47.22, J50.22, J53.22, J56.22, J59.22
A24: J2.18, J5.18, J8.18, J11.18, J14.18, J17.18, J20.18, J23.18, J26.18, J29.18, J32.18, J35.18, J38.18, J41.18, J44.18, J47.18, J50.18, J53.18, J56.18, J59.18
A25: J2.16, J5.16, J8.16, J11.16, J14.16, J17.16, J20.16, J23.16, J26.16, J29.16, J32.16, J35.16, J38.16, J41.16, J44.16, J47.16, J50.16, J53.16, J56.16, J59.16
A26: J2.14, J5.14, J8.14, J11.14, J14.14, J17.14, J20.14, J23.14, J26.14, J29.14, J32.14, J35.14, J38.14, J41.14, J44.14, J47.14, J50.14, J53.14, J56.14, J59.14
A27: J2.12, J5.12, J8.12, J11.12, J14.12, J17.12, J20.12, J23.12, J26.12, J29.12, J32.12, J35.12, J38.12, J41.12, J44.12, J47.12, J50.12, J53.12, J56.12, J59.12
A28: J2.10, J5.10, J8.10, J11.10, J14.10, J17.10, J20.10, J23.10, J26.10, J29.10, J32.10, J35.10, J38.10, J41.10, J44.10, J47.10, J50.10, J53.10, J56.10, J59.10
A29: J2.8, J5.8, J8.8, J11.8, J14.8, J17.8, J20.8, J23.8, J26.8, J29.8, J32.8, J35.8, J38.8, J41.8, J44.8, J47.8, J50.8, J53.8, J56.8, J59.8
A30: J2.6, J5.6, J8.6, J11.6, J14.6, J17.6, J20.6, J23.6, J26.6, J29.6, J32.6, J35.6, J38.6, J41.6, J44.6, J47.6, J50.6, J53.6, J56.6, J59.6
A31: J2.4, J5.4, J8.4, J11.4, J14.4, J17.4, J20.4, J23.4, J26.4, J29.4, J32.4, J35.4, J38.4, J41.4, J44.4, J47.4, J50.4, J53.4, J56.4, J59.4
AUXCLK0: J2.48, J5.48, J8.48, J11.48, J14.48, J17.48, J20.48, J23.48, J26.48, J29.48, J32.48, J35.48, J38.48, J41.48, J44.48, J47.48, J50.48, J53.48, J56.48, J59.48
AUXCLK1: J2.47, J5.47, J8.47, J11.47, J14.47, J17.47, J20.47, J23.47, J26.47, J29.47, J32.47, J35.47, J38.47, J41.47, J44.47, J47.47, J50.47, J53.47, J56.47, J59.47
AUXCLK2: J3.48, J6.48, J9.48, J12.48, J15.48, J18.48, J21.48, J24.48, J25.48, J28.48, J31.48, J34.48, J37.48, J40.48, J43.48, J46.48, J49.48, J52.48, J55.48, J58.48
AUXCLK3: J3.46, J6.46, J9.46, J12.46, J15.46, J18.46, J21.46, J24.46, J25.46, J28.46, J31.46, J34.46, J37.46, J40.46, J43.46, J46.46, J49.46, J52.46, J55.46, J58.46
CLK: J1.15, J4.15, J7.15, J10.15, J13.15, J16.15, J19.15, J22.15, J27.15, J30.15, J33.15, J36.15, J39.15, J42.15, J45.15, J48.15, J51.15, J54.15, J57.15, J60.15
CRUCLK: J1.14, J4.14, J7.14, J10.14, J13.14, J16.14, J19.14, J22.14, J27.14, J30.14, J33.14, J36.14, J39.14, J42.14, J45.14, J48.14, J51.14, J54.14, J57.14, J60.14
CRUIN: J1.18, J4.18, J7.18, J10.18, J13.18, J16.18, J19.18, J22.18, J27.18, J30.18, J33.18, J36.18, J39.18, J42.18, J45.18, J48.18, J51.18, J54.18, J57.18, J60.18
CRUOUT: J1.16, J4.16, J7.16, J10.16, J13.16, J16.16, J19.16, J22.16, J27.16, J30.16, J33.16, J36.16, J39.16, J42.16, J45.16, J48.16, J51.16, J54.16, J57.16, J60.16
D0: J3.33, J6.33, J9.33, J12.33, J15.33, J18.33, J21.33, J24.33, J25.33, J28.33, J31.33, J34.33, J37.33, J40.33, J43.33, J46.33, J49.33, J52.33, J55.33, J58.33
D1: J3.31, J6.31, J9.31, J12.31, J15.31, J18.31, J21.31, J24.31, J25.31, J28.31, J31.31, J34.31, J37.31, J40.31, J43.31, J46.31, J49.31, J52.31, J55.31, J58.31
D2: J3.29, J6.29, J9.29, J12.29, J15.29, J18.29, J21.29, J24.29, J25.29, J28.29, J31.29, J34.29, J37.29, J40.29, J43.29, J46.29, J49.29, J52.29, J55.29, J58.29
D3: J3.27, J6.27, J9.27, J12.27, J15.27, J18.27, J21.27, J24.27, J25.27, J28.27, J31.27, J34.27, J37.27, J40.27, J43.27, J46.27, J49.27, J52.27, J55.27, J58.27
D4: J3.25, J6.25, J9.25, J12.25, J15.25, J18.25, J21.25, J24.25, J25.25, J28.25, J31.25, J34.25, J37.25, J40.25, J43.25, J46.25, J49.25, J52.25, J55.25, J58.25
D5: J3.23, J6.23, J9.23, J12.23, J15.23, J18.23, J21.23, J24.23, J25.23, J28.23, J31.23, J34.23, J37.23, J40.23, J43.23, J46.23, J49.23, J52.23, J55.23, J58.23
D6: J3.21, J6.21, J9.21, J12.21, J15.21, J18.21, J21.21, J24.21, J25.21, J28.21, J31.21, J34.21, J37.21, J40.21, J43.21, J46.21, J49.21, J52.21, J55.21, J58.21
D7: J3.19, J6.19, J9.19, J12.19, J15.19, J18.19, J21.19, J24.19, J25.19, J28.19, J31.19, J34.19, J37.19, J40.19, J43.19, J46.19, J49.19, J52.19, J55.19, J58.19
D8: J3.17, J6.17, J9.17, J12.17, J15.17, J18.17, J21.17, J24.17, J25.17, J28.17, J31.17, J34.17, J37.17, J40.17, J43.17, J46.17, J49.17, J52.17, J55.17, J58.17
D9: J3.15, J6.15, J9.15, J12.15, J15.15, J18.15, J21.15, J24.15, J25.15, J28.15, J31.15, J34.15, J37.15, J40.15, J43.15, J46.15, J49.15, J52.15, J55.15, J58.15
D10: J3.13, J6.13, J9.13, J12.13, J15.13, J18.13, J21.13, J24.13, J25.13, J28.13, J31.13, J34.13, J37.13, J40.13, J43.13, J46.13, J49.13, J52.13, J55.13, J58.13
D11: J3.11, J6.11, J9.11, J12.11, J15.11, J18.11, J21.11, J24.11, J25.11, J28.11, J31.11, J34.11, J37.11, J40.11, J43.11, J46.11, J49.11, J52.11, J55.11, J58.11
D12: J3.9, J6.9, J9.9, J12.9, J15.9, J18.9, J21.9, J24.9, J25.9, J28.9, J31.9, J34.9, J37.9, J40.9, J43.9, J46.9, J49.9, J52.9, J55.9, J58.9
D13: J3.7, J6.7, J9.7, J12.7, J15.7, J18.7, J21.7, J24.7, J25.7, J28.7, J31.7, J34.7, J37.7, J40.7, J43.7, J46.7, J49.7, J52.7, J55.7, J58.7
D14: J3.5, J6.5, J9.5, J12.5, J15.5, J18.5, J21.5, J24.5, J25.5, J28.5, J31.5, J34.5, J37.5, J40.5, J43.5, J46.5, J49.5, J52.5, J55.5, J58.5
D15: J3.3, J6.3, J9.3, J12.3, J15.3, J18.3, J21.3, J24.3, J25.3, J28.3, J31.3, J34.3, J37.3, J40.3, J43.3, J46.3, J49.3, J52.3, J55.3, J58.3
D16: J3.34, J6.34, J9.34, J12.34, J15.34, J18.34, J21.34, J24.34, J25.34, J28.34, J31.34, J34.34, J37.34, J40.34, J43.34, J46.34, J49.34, J52.34, J55.34, J58.34
D17: J3.32, J6.32, J9.32, J12.32, J15.32, J18.32, J21.32, J24.32, J25.32, J28.32, J31.32, J34.32, J37.32, J40.32, J43.32, J46.32, J49.32, J52.32, J55.32, J58.32
D18: J3.30, J6.30, J9.30, J12.30, J15.30, J18.30, J21.30, J24.30, J25.30, J28.30, J31.30, J34.30, J37.30, J40.30, J43.30, J46.30, J49.30, J52.30, J55.30, J58.30
D19: J3.28, J6.28, J9.28, J12.28, J15.28, J18.28, J21.28, J24.28, J25.28, J28.28, J31.28, J34.28, J37.28, J40.28, J43.28, J46.28, J49.28, J52.28, J55.28, J58.28
D20: J3.26, J6.26, J9.26, J12.26, J15.26, J18.26, J21.26, J24.26, J25.26, J28.26, J31.26, J34.26, J37.26, J40.26, J43.26, J46.26, J49.26, J52.26, J55.26, J58.26
D21: J3.24, J6.24, J9.24, J12.24, J15.24, J18.24, J21.24, J24.24, J25.24, J28.24, J31.24, J34.24, J37.24, J40.24, J43.24, J46.24, J49.24, J52.24, J55.24, J58.24
D22: J3.22, J6.22, J9.22, J12.22, J15.22, J18.22, J21.22, J24.22, J25.22, J28.22, J31.22, J34.22, J37.22, J40.22, J43.22, J46.22, J49.22, J52.22, J55.22, J58.22
D23: J3.20, J6.20, J9.20, J12.20, J15.20, J18.20, J21.20, J24.20, J25.20, J28.20, J31.20, J34.20, J37.20, J40.20, J43.20, J46.20, J49.20, J52.20, J55.20, J58.20
D24: J3.18, J6.18, J9.18, J12.18, J15.18, J18.18, J21.18, J24.18, J25.18, J28.18, J31.18, J34.18, J37.18, J40.18, J43.18, J46.18, J49.18, J52.18, J55.18, J58.18
D25: J3.16, J6.16, J9.16, J12.16, J15.16, J18.16, J21.16, J24.16, J25.16, J28.16, J31.16, J34.16, J37.16, J40.16, J43.16, J46.16, J49.16, J52.16, J55.16, J58.16
D26: J3.14, J6.14, J9.14, J12.14, J15.14, J18.14, J21.14, J24.14, J25.14, J28.14, J31.14, J34.14, J37.14, J40.14, J43.14, J46.14, J49.14, J52.14, J55.14, J58.14
D27: J3.12, J6.12, J9.12, J12.12, J15.12, J18.12, J21.12, J24.12, J25.12, J28.12, J31.12, J34.12, J37.12, J40.12, J43.12, J46.12, J49.12, J52.12, J55.12, J58.12
D28: J3.10, J6.10, J9.10, J12.10, J15.10, J18.10, J21.10, J24.10, J25.10, J28.10, J31.10, J34.10, J37.10, J40.10, J43.10, J46.10, J49.10, J52.10, J55.10, J58.10
D29: J3.8, J6.8, J9.8, J12.8, J15.8, J18.8, J21.8, J24.8, J25.8, J28.8, J31.8, J34.8, J37.8, J40.8, J43.8, J46.8, J49.8, J52.8, J55.8, J58.8
D30: J3.6, J6.6, J9.6, J12.6, J15.6, J18.6, J21.6, J24.6, J25.6, J28.6, J31.6, J34.6, J37.6, J40.6, J43.6, J46.6, J49.6, J52.6, J55.6, J58.6
D31: J3.4, J6.4, J9.4, J12.4, J15.4, J18.4, J21.4, J24.4, J25.4, J28.4, J31.4, J34.4, J37.4, J40.4, J43.4, J46.4, J49.4, J52.4, J55.4, J58.4
E: J1.4, J4.4, J7.4, J10.4, J13.4, J16.4, J19.4, J22.4, J27.4, J30.4, J33.4, J36.4, J39.4, J42.4, J45.4, J48.4, J51.4, J54.4, J57.4, J60.4
GND: D5.1 (K), H1.1, H2.1, H3.1, H4.1, H5.1, H6.1, H7.1, H8.1, H9.1, H10.1, H11.1, H12.1, H13.1, H14.1, H15.1, H16.1, H17.1, H18.1, H19.1, H20.1, H21.1, H22.1, H23.1, H24.1, H25.1, H26.1, H27.1, H28.1, H29.1, H30.1, H31.1, H32.1, H33.1, H35.1, H36.1, H37.1, H38.1, H40.1, J1.49, J1.50, J2.49, J2.50, J3.49, J3.50, J4.49, J4.50, J5.49, J5.50, J6.49, J6.50, J7.49, J7.50, J8.49, J8.50, J9.49, J9.50, J10.49, J10.50, J11.49, J11.50, J12.49, J12.50, J13.49, J13.50, J14.49, J14.50, J15.49, J15.50, J16.49, J16.50, J17.49, J17.50, J18.49, J18.50, J19.49, J19.50, J20.49, J20.50, J21.49, J21.50, J22.49, J22.50, J23.49, J23.50, J24.49, J24.50, J25.49, J25.50, J26.49, J26.50, J27.49, J27.50, J28.49, J28.50, J29.49, J29.50, J30.49, J30.50, J31.49, J31.50, J32.49, J32.50, J33.49, J33.50, J34.49, J34.50, J35.49, J35.50, J36.49, J36.50, J37.49, J37.50, J38.49, J38.50, J39.49, J39.50, J40.49, J40.50, J41.49, J41.50, J42.49, J42.50, J43.49, J43.50, J44.49, J44.50, J45.49, J45.50, J46.49, J46.50, J47.49, J47.50, J48.49, J48.50, J49.49, J49.50, J50.49, J50.50, J51.49, J51.50, J52.49, J52.50, J53.49, J53.50, J54.49, J54.50, J55.49, J55.50, J56.49, J56.50, J57.49, J57.50, J58.49, J58.50, J59.49, J59.50, J60.49, J60.50, R2.1, R2.2, T1.2
I2C_SCL: J1.47, J4.47, J7.47, J10.47, J13.47, J16.47, J19.47, J22.47, J27.47, J30.47, J33.47, J36.47, J39.47, J42.47, J45.47, J48.47, J51.47, J54.47, J57.47, J60.47
I2C_SDA: J1.48, J4.48, J7.48, J10.48, J13.48, J16.48, J19.48, J22.48, J27.48, J30.48, J33.48, J36.48, J39.48, J42.48, J45.48, J48.48, J51.48, J54.48, J57.48, J60.48
IC0: J2.45, J5.45, J8.45, J11.45, J14.45, J17.45, J20.45, J23.45, J26.45, J29.45, J32.45, J35.45, J38.45, J41.45, J44.45, J47.45, J50.45, J53.45, J56.45, J59.45
IC1: J2.43, J5.43, J8.43, J11.43, J14.43, J17.43, J20.43, J23.43, J26.43, J29.43, J32.43, J35.43, J38.43, J41.43, J44.43, J47.43, J50.43, J53.43, J56.43, J59.43
IC2: J2.41, J5.41, J8.41, J11.41, J14.41, J17.41, J20.41, J23.41, J26.41, J29.41, J32.41, J35.41, J38.41, J41.41, J44.41, J47.41, J50.41, J53.41, J56.41, J59.41
IC3: J2.39, J5.39, J8.39, J11.39, J14.39, J17.39, J20.39, J23.39, J26.39, J29.39, J32.39, J35.39, J38.39, J41.39, J44.39, J47.39, J50.39, J53.39, J56.39, J59.39
IPL0: J3.47, J6.47, J9.47, J12.47, J15.47, J18.47, J21.47, J24.47, J25.47, J28.47, J31.47, J34.47, J37.47, J40.47, J43.47, J46.47, J49.47, J52.47, J55.47, J58.47
IPL1: J3.45, J6.45, J9.45, J12.45, J15.45, J18.45, J21.45, J24.45, J25.45, J28.45, J31.45, J34.45, J37.45, J40.45, J43.45, J46.45, J49.45, J52.45, J55.45, J58.45
IPL2: J3.43, J6.43, J9.43, J12.43, J15.43, J18.43, J21.43, J24.43, J25.43, J28.43, J31.43, J34.43, J37.43, J40.43, J43.43, J46.43, J49.43, J52.43, J55.43, J58.43
LDS: J3.38, J6.38, J9.38, J12.38, J15.38, J18.38, J21.38, J24.38, J25.38, J28.38, J31.38, J34.38, J37.38, J40.38, J43.38, J46.38, J49.38, J52.38, J55.38, J58.38
unnamed: D5.2 (A), R6.2
PHI: J1.8, J4.8, J7.8, J10.8, J13.8, J16.8, J19.8, J22.8, J27.8, J30.8, J33.8, J36.8, J39.8, J42.8, J45.8, J48.8, J51.8, J54.8, J57.8, J60.8
S0: J3.44, J6.44, J9.44, J12.44, J15.44, J18.44, J21.44, J24.44, J25.44, J28.44, J31.44, J34.44, J37.44, J40.44, J43.44, J46.44, J49.44, J52.44, J55.44, J58.44
S1: J3.42, J6.42, J9.42, J12.42, J15.42, J18.42, J21.42, J24.42, J25.42, J28.42, J31.42, J34.42, J37.42, J40.42, J43.42, J46.42, J49.42, J52.42, J55.42, J58.42
S2: J3.40, J6.40, J9.40, J12.40, J15.40, J18.40, J21.40, J24.40, J25.40, J28.40, J31.40, J34.40, J37.40, J40.40, J43.40, J46.40, J49.40, J52.40, J55.40, J58.40
ST: J1.6, J4.6, J7.6, J10.6, J13.6, J16.6, J19.6, J22.6, J27.6, J30.6, J33.6, J36.6, J39.6, J42.6, J45.6, J48.6, J51.6, J54.6, J57.6, J60.6
UDS: J3.36, J6.36, J9.36, J12.36, J15.36, J18.36, J21.36, J24.36, J25.36, J28.36, J31.36, J34.36, J37.36, J40.36, J43.36, J46.36, J49.36, J52.36, J55.36, J58.36
USER0: J1.38, J4.38, J7.38, J10.38, J13.38, J16.38, J19.38, J22.38, J27.38, J30.38, J33.38, J36.38, J39.38, J42.38, J45.38, J48.38, J51.38, J54.38, J57.38, J60.38
USER1: J1.36, J4.36, J7.36, J10.36, J13.36, J16.36, J19.36, J22.36, J27.36, J30.36, J33.36, J36.36, J39.36, J42.36, J45.36, J48.36, J51.36, J54.36, J57.36, J60.36
USER2: J1.34, J4.34, J7.34, J10.34, J13.34, J16.34, J19.34, J22.34, J27.34, J30.34, J33.34, J36.34, J39.34, J42.34, J45.34, J48.34, J51.34, J54.34, J57.34, J60.34
USER3: J1.32, J4.32, J7.32, J10.32, J13.32, J16.32, J19.32, J22.32, J27.32, J30.32, J33.32, J36.32, J39.32, J42.32, J45.32, J48.32, J51.32, J54.32, J57.32, J60.32
USER4: J1.30, J4.30, J7.30, J10.30, J13.30, J16.30, J19.30, J22.30, J27.30, J30.30, J33.30, J36.30, J39.30, J42.30, J45.30, J48.30, J51.30, J54.30, J57.30, J60.30
USER5: J1.28, J4.28, J7.28, J10.28, J13.28, J16.28, J19.28, J22.28, J27.28, J30.28, J33.28, J36.28, J39.28, J42.28, J45.28, J48.28, J51.28, J54.28, J57.28, J60.28
USER6: J1.26, J4.26, J7.26, J10.26, J13.26, J16.26, J19.26, J22.26, J27.26, J30.26, J33.26, J36.26, J39.26, J42.26, J45.26, J48.26, J51.26, J54.26, J57.26, J60.26
USER7: J1.24, J4.24, J7.24, J10.24, J13.24, J16.24, J19.24, J22.24, J27.24, J30.24, J33.24, J36.24, J39.24, J42.24, J45.24, J48.24, J51.24, J54.24, J57.24, J60.24
USER8: J1.22, J4.22, J7.22, J10.22, J13.22, J16.22, J19.22, J22.22, J27.22, J30.22, J33.22, J36.22, J39.22, J42.22, J45.22, J48.22, J51.22, J54.22, J57.22, J60.22
VCC: J1.1, J1.2, J2.1, J2.2, J3.1, J3.2, J4.1, J4.2, J5.1, J5.2, J6.1, J6.2, J7.1, J7.2, J8.1, J8.2, J9.1, J9.2, J10.1, J10.2, J11.1, J11.2, J12.1, J12.2, J13.1, J13.2, J14.1, J14.2, J15.1, J15.2, J16.1, J16.2, J17.1, J17.2, J18.1, J18.2, J19.1, J19.2, J20.1, J20.2, J21.1, J21.2, J22.1, J22.2, J23.1, J23.2, J24.1, J24.2, J25.1, J25.2, J26.1, J26.2, J27.1, J27.2, J28.1, J28.2, J29.1, J29.2, J30.1, J30.2, J31.1, J31.2, J32.1, J32.2, J33.1, J33.2, J34.1, J34.2, J35.1, J35.2, J36.1, J36.2, J37.1, J37.2, J38.1, J38.2, J39.1, J39.2, J40.1, J40.2, J41.1, J41.2, J42.1, J42.2, J43.1, J43.2, J44.1, J44.2, J45.1, J45.2, J46.1, J46.2, J47.1, J47.2, J48.1, J48.2, J49.1, J49.2, J50.1, J50.2, J51.1, J51.2, J52.1, J52.2, J53.1, J53.2, J54.1, J54.2, J55.1, J55.2, J56.1, J56.2, J57.1, J57.2, J58.1, J58.2, J59.1, J59.2, J60.1, J60.2, R1.1, R1.2, R6.1, T1.1
~BAI-1: J36.40, P1.4
~BAI-2: J33.40, P2.4
~BAI-3: J30.40, P3.4
~BAI-4: J27.40, P4.4
~BAI-5: J60.40, P5.4
~BAI-6: J57.40, P6.4
~BAI-7: J54.40, P7.4
~BAI-8: J51.40, P8.4
~BAI-9: J48.40, P9.4
~BAI-10: J45.40, P10.4
~BAI-11: J42.40, P11.4
~BAI-12: J39.40, P12.4
~BAI-13: J1.40, P13.4
~BAI-14: J4.40, P14.4
~BAI-15: J7.40, P15.4
~BAI-16: J10.40, P16.4
~BAI-17: J13.40, P17.4
~BAI-18: J16.40, P18.4
~BAI-19: J19.40, P19.4
~BAI-20: J22.40
~BAO-1: J36.42
~BAO-2: J33.42, P1.3
~BAO-3: J30.42, P2.3
~BAO-4: J27.42, P3.3
~BAO-5: J60.42, P4.3
~BAO-6: J57.42, P5.3
~BAO-7: J54.42, P6.3
~BAO-8: J51.42, P7.3
~BAO-9: J48.42, P8.3
~BAO-10: J45.42, P9.3
~BAO-11: J42.42, P10.3
~BAO-12: J39.42, P11.3
~BAO-13: J1.42, P12.3
~BAO-14: J4.42, P13.3
~BAO-15: J7.42, P14.3
~BAO-16: J10.42, P15.3
~BAO-17: J13.42, P16.3
~BAO-18: J16.42, P17.3
~BAO-19: J19.42, P18.3
~BAO-20: J22.42, P19.3
~BHE: J3.41, J6.41, J9.41, J12.41, J15.41, J18.41, J21.41, J24.41, J25.41, J28.41, J31.41, J34.41, J37.41, J40.41, J43.41, J46.41, J49.41, J52.41, J55.41, J58.41
~BUSACK: J1.13, J4.13, J7.13, J10.13, J13.13, J16.13, J19.13, J22.13, J27.13, J30.13, J33.13, J36.13, J39.13, J42.13, J45.13, J48.13, J51.13, J54.13, J57.13, J60.13
~BUSERR: J3.35, J6.35, J9.35, J12.35, J15.35, J18.35, J21.35, J24.35, J25.35, J28.35, J31.35, J34.35, J37.35, J40.35, J43.35, J46.35, J49.35, J52.35, J55.35, J58.35
~BUSRQ: J1.23, J4.23, J7.23, J10.23, J13.23, J16.23, J19.23, J22.23, J27.23, J30.23, J33.23, J36.23, J39.23, J42.23, J45.23, J48.23, J51.23, J54.23, J57.23, J60.23
~DREQ0: J2.46, J5.46, J8.46, J11.46, J14.46, J17.46, J20.46, J23.46, J26.46, J29.46, J32.46, J35.46, J38.46, J41.46, J44.46, J47.46, J50.46, J53.46, J56.46, J59.46
~DREQ1: J2.42, J5.42, J8.42, J11.42, J14.42, J17.42, J20.42, J23.42, J26.42, J29.42, J32.42, J35.42, J38.42, J41.42, J44.42, J47.42, J50.42, J53.42, J56.42, J59.42
~EIRQ0: J1.45, J4.45, J7.45, J10.45, J13.45, J16.45, J19.45, J22.45, J27.45, J30.45, J33.45, J36.45, J39.45, J42.45, J45.45, J48.45, J51.45, J54.45, J57.45, J60.45
~EIRQ1: J1.43, J4.43, J7.43, J10.43, J13.43, J16.43, J19.43, J22.43, J27.43, J30.43, J33.43, J36.43, J39.43, J42.43, J45.43, J48.43, J51.43, J54.43, J57.43, J60.43
~EIRQ2: J1.41, J4.41, J7.41, J10.41, J13.41, J16.41, J19.41, J22.41, J27.41, J30.41, J33.41, J36.41, J39.41, J42.41, J45.41, J48.41, J51.41, J54.41, J57.41, J60.41
~EIRQ3: J1.39, J4.39, J7.39, J10.39, J13.39, J16.39, J19.39, J22.39, J27.39, J30.39, J33.39, J36.39, J39.39, J42.39, J45.39, J48.39, J51.39, J54.39, J57.39, J60.39
~EIRQ4: J1.37, J4.37, J7.37, J10.37, J13.37, J16.37, J19.37, J22.37, J27.37, J30.37, J33.37, J36.37, J39.37, J42.37, J45.37, J48.37, J51.37, J54.37, J57.37, J60.37
~EIRQ5: J1.35, J4.35, J7.35, J10.35, J13.35, J16.35, J19.35, J22.35, J27.35, J30.35, J33.35, J36.35, J39.35, J42.35, J45.35, J48.35, J51.35, J54.35, J57.35, J60.35
~EIRQ6: J1.33, J4.33, J7.33, J10.33, J13.33, J16.33, J19.33, J22.33, J27.33, J30.33, J33.33, J36.33, J39.33, J42.33, J45.33, J48.33, J51.33, J54.33, J57.33, J60.33
~EIRQ7: J1.31, J4.31, J7.31, J10.31, J13.31, J16.31, J19.31, J22.31, J27.31, J30.31, J33.31, J36.31, J39.31, J42.31, J45.31, J48.31, J51.31, J54.31, J57.31, J60.31
~HALT: J1.27, J4.27, J7.27, J10.27, J13.27, J16.27, J19.27, J22.27, J27.27, J30.27, J33.27, J36.27, J39.27, J42.27, J45.27, J48.27, J51.27, J54.27, J57.27, J60.27
~IEI-1: J36.44, P1.2
~IEI-2: J33.44, P2.2
~IEI-3: J30.44, P3.2
~IEI-4: J27.44, P4.2
~IEI-5: J60.44, P5.2
~IEI-6: J57.44, P6.2
~IEI-7: J54.44, P7.2
~IEI-8: J51.44, P8.2
~IEI-9: J48.44, P9.2
~IEI-10: J45.44, P10.2
~IEI-11: J42.44, P11.2
~IEI-12: J39.44, P12.2
~IEI-13: J1.44, P13.2
~IEI-14: J4.44, P14.2
~IEI-15: J7.44, P15.2
~IEI-16: J10.44, P16.2
~IEI-17: J13.44, P17.2
~IEI-18: J16.44, P18.2
~IEI-19: J19.44, P19.2
~IEI-20: J22.44
~IEO-1: J36.46
~IEO-2: J33.46, P1.1
~IEO-3: J30.46, P2.1
~IEO-4: J27.46, P3.1
~IEO-5: J60.46, P4.1
~IEO-6: J57.46, P5.1
~IEO-7: J54.46, P6.1
~IEO-8: J51.46, P7.1
~IEO-9: J48.46, P8.1
~IEO-10: J45.46, P9.1
~IEO-11: J42.46, P10.1
~IEO-12: J39.46, P11.1
~IEO-13: J1.46, P12.1
~IEO-14: J4.46, P13.1
~IEO-15: J7.46, P14.1
~IEO-16: J10.46, P15.1
~IEO-17: J13.46, P16.1
~IEO-18: J16.46, P17.1
~IEO-19: J19.46, P18.1
~IEO-20: J22.46, P19.1
~INT0: J1.17, J4.17, J7.17, J10.17, J13.17, J16.17, J19.17, J22.17, J27.17, J30.17, J33.17, J36.17, J39.17, J42.17, J45.17, J48.17, J51.17, J54.17, J57.17, J60.17
~INT1: J1.12, J4.12, J7.12, J10.12, J13.12, J16.12, J19.12, J22.12, J27.12, J30.12, J33.12, J36.12, J39.12, J42.12, J45.12, J48.12, J51.12, J54.12, J57.12, J60.12
~INT2: J1.10, J4.10, J7.10, J10.10, J13.10, J16.10, J19.10, J22.10, J27.10, J30.10, J33.10, J36.10, J39.10, J42.10, J45.10, J48.10, J51.10, J54.10, J57.10, J60.10
~IORQ: J1.7, J4.7, J7.7, J10.7, J13.7, J16.7, J19.7, J22.7, J27.7, J30.7, J33.7, J36.7, J39.7, J42.7, J45.7, J48.7, J51.7, J54.7, J57.7, J60.7
~M1: J1.11, J4.11, J7.11, J10.11, J13.11, J16.11, J19.11, J22.11, J27.11, J30.11, J33.11, J36.11, J39.11, J42.11, J45.11, J48.11, J51.11, J54.11, J57.11, J60.11
~MREQ: J1.9, J4.9, J7.9, J10.9, J13.9, J16.9, J19.9, J22.9, J27.9, J30.9, J33.9, J36.9, J39.9, J42.9, J45.9, J48.9, J51.9, J54.9, J57.9, J60.9
~NMI: J1.19, J4.19, J7.19, J10.19, J13.19, J16.19, J19.19, J22.19, J27.19, J30.19, J33.19, J36.19, J39.19, J42.19, J45.19, J48.19, J51.19, J54.19, J57.19, J60.19
~RD: J1.3, J4.3, J7.3, J10.3, J13.3, J16.3, J19.3, J22.3, J27.3, J30.3, J33.3, J36.3, J39.3, J42.3, J45.3, J48.3, J51.3, J54.3, J57.3, J60.3
~RES_IN: J1.20, J4.20, J7.20, J10.20, J13.20, J16.20, J19.20, J22.20, J27.20, J30.20, J33.20, J36.20, J39.20, J42.20, J45.20, J48.20, J51.20, J54.20, J57.20, J60.20
~RES_OUT: J1.21, J4.21, J7.21, J10.21, J13.21, J16.21, J19.21, J22.21, J27.21, J30.21, J33.21, J36.21, J39.21, J42.21, J45.21, J48.21, J51.21, J54.21, J57.21, J60.21
~RFSH: J1.29, J4.29, J7.29, J10.29, J13.29, J16.29, J19.29, J22.29, J27.29, J30.29, J33.29, J36.29, J39.29, J42.29, J45.29, J48.29, J51.29, J54.29, J57.29, J60.29
~TEND0: J2.44, J5.44, J8.44, J11.44, J14.44, J17.44, J20.44, J23.44, J26.44, J29.44, J32.44, J35.44, J38.44, J41.44, J44.44, J47.44, J50.44, J53.44, J56.44, J59.44
~TEND1: J2.40, J5.40, J8.40, J11.40, J14.40, J17.40, J20.40, J23.40, J26.40, J29.40, J32.40, J35.40, J38.40, J41.40, J44.40, J47.40, J50.40, J53.40, J56.40, J59.40
~VMA: J3.39, J6.39, J9.39, J12.39, J15.39, J18.39, J21.39, J24.39, J25.39, J28.39, J31.39, J34.39, J37.39, J40.39, J43.39, J46.39, J49.39, J52.39, J55.39, J58.39
~VPA: J3.37, J6.37, J9.37, J12.37, J15.37, J18.37, J21.37, J24.37, J25.37, J28.37, J31.37, J34.37, J37.37, J40.37, J43.37, J46.37, J49.37, J52.37, J55.37, J58.37
~WAIT: J1.25, J4.25, J7.25, J10.25, J13.25, J16.25, J19.25, J22.25, J27.25, J30.25, J33.25, J36.25, J39.25, J42.25, J45.25, J48.25, J51.25, J54.25, J57.25, J60.25
~WR: J1.5, J4.5, J7.5, J10.5, J13.5, J16.5, J19.5, J22.5, J27.5, J30.5, J33.5, J36.5, J39.5, J42.5, J45.5, J48.5, J51.5, J54.5, J57.5, J60.5

Notes on the sheet:
Zilog Interrupt Priority Bus Jumpers
LOGIC ANALYZER LOOPS
