lynchaj/duodyne/01 template.prototyping, V1.0/temp/power.sch

## KiCad design 01 template.prototyping, V1.0/temp/power.sch (2023-03-30)

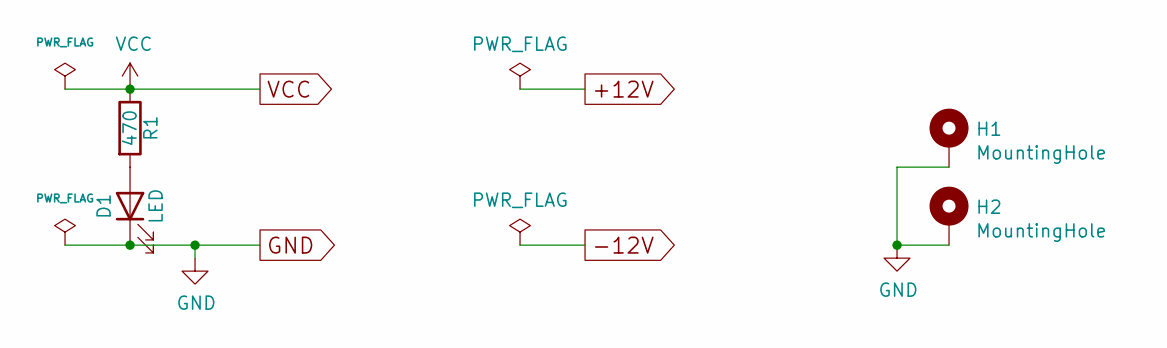
[picture p460: schematic power.sch]

Parts:
D1: LED; LED_D3.0mm_Horizontal_O3.81mm_Z2.0mm
H1, H2: MountingHole; MountingHole_3.2mm_M3_Pad
R1: 470; R_Axial_DIN0207_L6.3mm_D2.5mm_P7.62mm_Horizontal

Connections:
GND: D1.1 (K), H1.1, H2.1
unnamed: D1.2 (A), R1.2
VCC: R1.1
