lynchaj/duodyne/05 input-output.Zilog, V1.1/temp/CTC-INT.sch

## KiCad design 05 input-output.Zilog, V1.1/temp/CTC-INT.sch (2023-03-30)

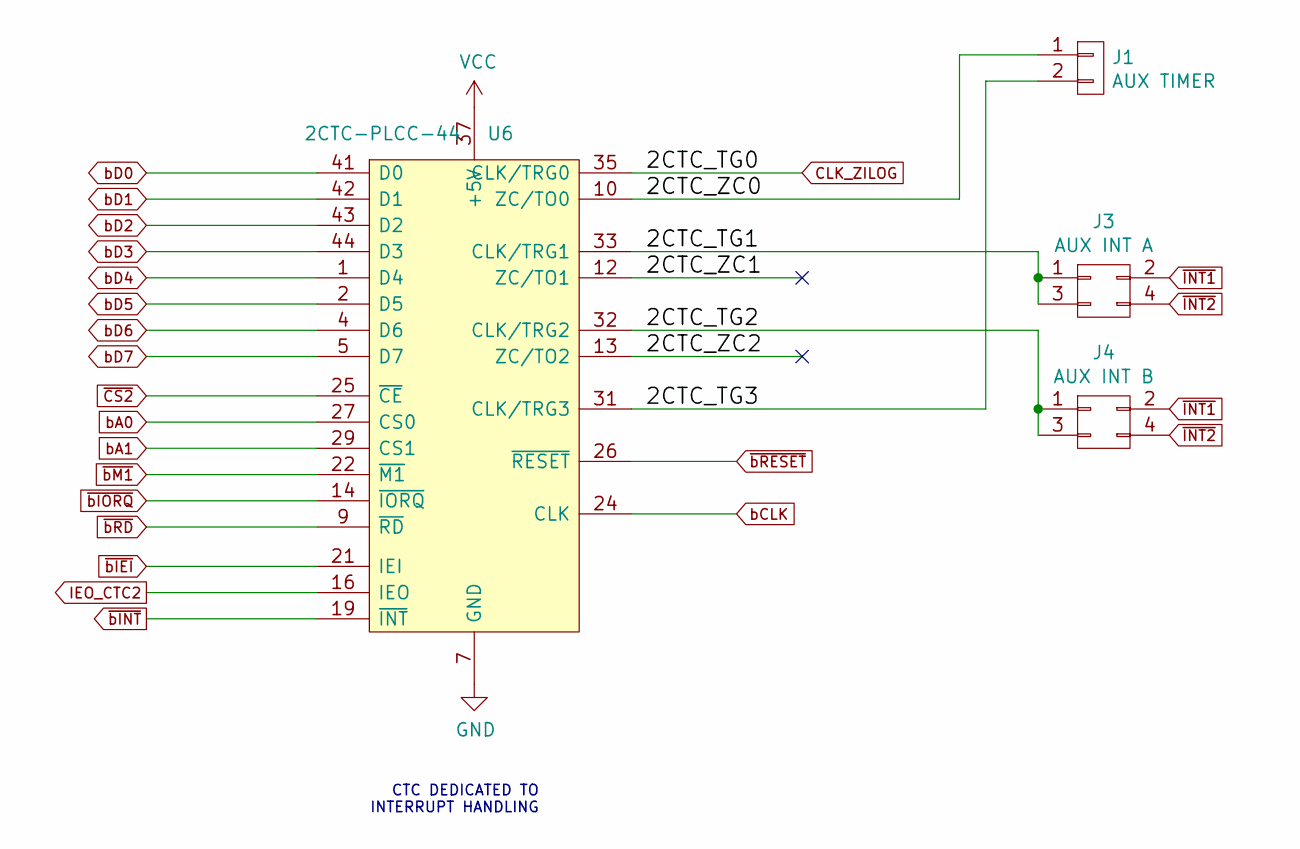
[picture p462: schematic CTC-INT.sch]

Parts:
J1: AUX TIMER; PinHeader_1x02_P2.54mm_Vertical
J3: AUX INT A; PinHeader_2x02_P2.54mm_Vertical
J4: AUX INT B; PinHeader_2x02_P2.54mm_Vertical
U6: 2CTC-PLCC-44; PLCC-44_THT-Socket; Manufacturer_Part_Number Z84C3010PEG; Mouser Part Number 692-Z84C3010PEG

Connections:
2CTC_TG1: J3.1, J3.3, U6.33 (CLK/TRG1)
2CTC_TG2: J4.1, J4.3, U6.32 (CLK/TRG2)
2CTC_TG3: J1.2, U6.31 (CLK/TRG3)
2CTC_ZC0: J1.1, U6.10 (ZC/TO0)
2CTC_ZC1: U6.12 (ZC/TO1)
2CTC_ZC2: U6.13 (ZC/TO2)
CLK_ZILOG: U6.35 (CLK/TRG0)
GND: U6.7 (GND)
IEO_CTC2: U6.16 (IEO)
VCC: U6.37 (+5V)
bA0: U6.27 (CS0)
bA1: U6.29 (CS1)
bCLK: U6.24 (CLK)
bD0: U6.41 (D0)
bD1: U6.42 (D1)
bD2: U6.43 (D2)
bD3: U6.44 (D3)
bD4: U6.1 (D4)
bD5: U6.2 (D5)
bD6: U6.4 (D6)
bD7: U6.5 (D7)
~CS2: U6.25 (~CE)
~INT1: J3.2, J4.2
~INT2: J3.4, J4.4
~bIEI: U6.21 (IEI)
~bINT: U6.19 (~INT)
~bIORQ: U6.14 (~IORQ)
~bM1: U6.22 (~M1)
~bRD: U6.9 (~RD)
~bRESET: U6.26 (~RESET)

Notes on the sheet:
CTC DEDICATED TO INTERRUPT HANDLING
