lynchaj/duodyne/05 input-output.Zilog, V1.1/temp/CTC-SIO.sch

## KiCad design 05 input-output.Zilog, V1.1/temp/CTC-SIO.sch (2023-03-30)

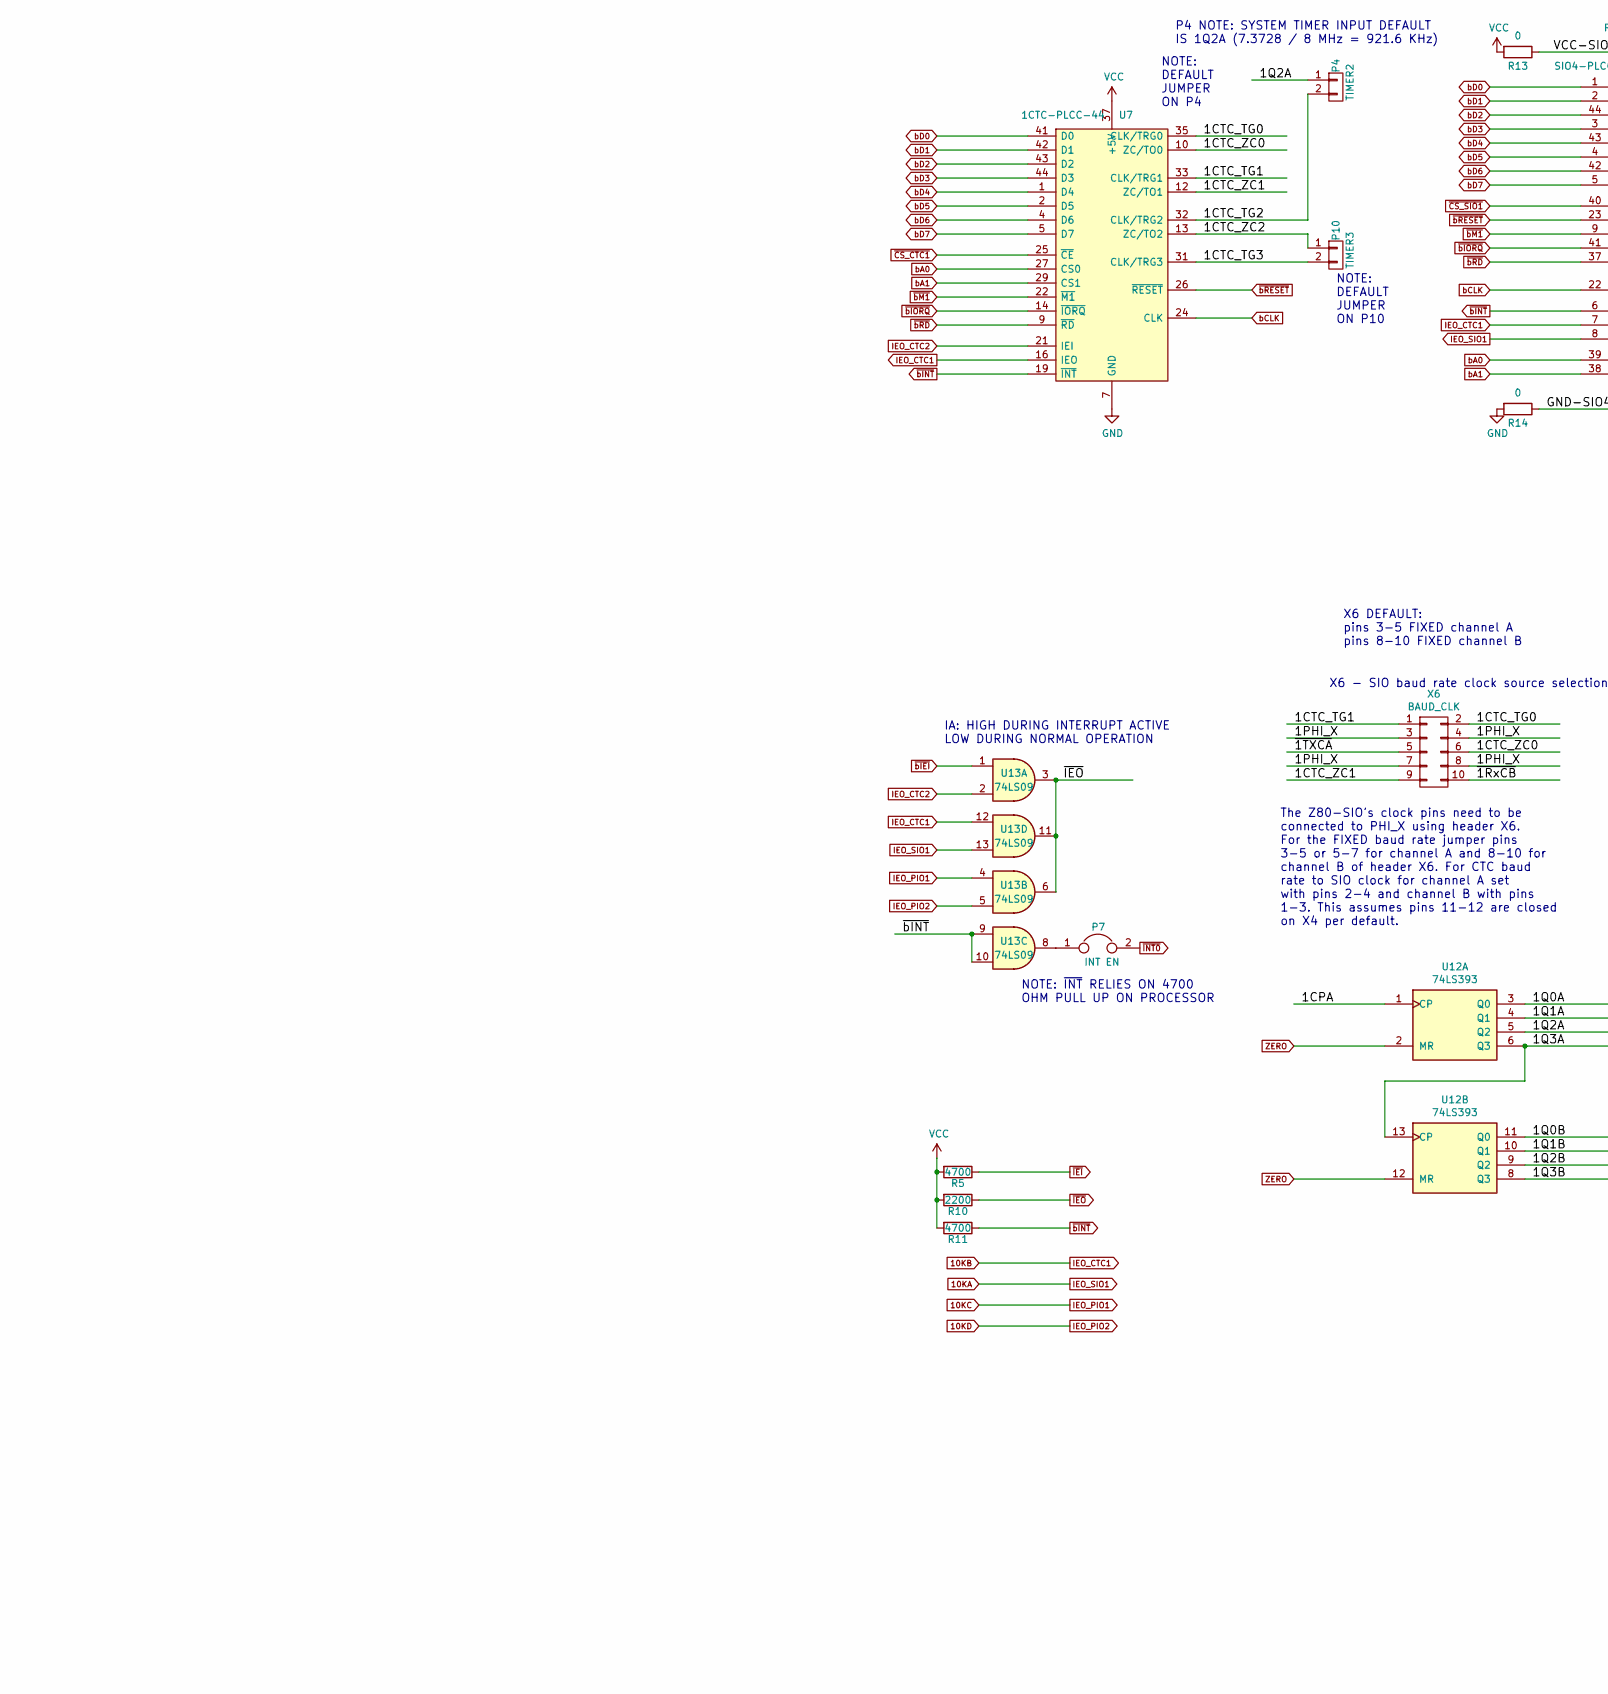
[picture p463: schematic CTC-SIO.sch, part in row 1, column 1]

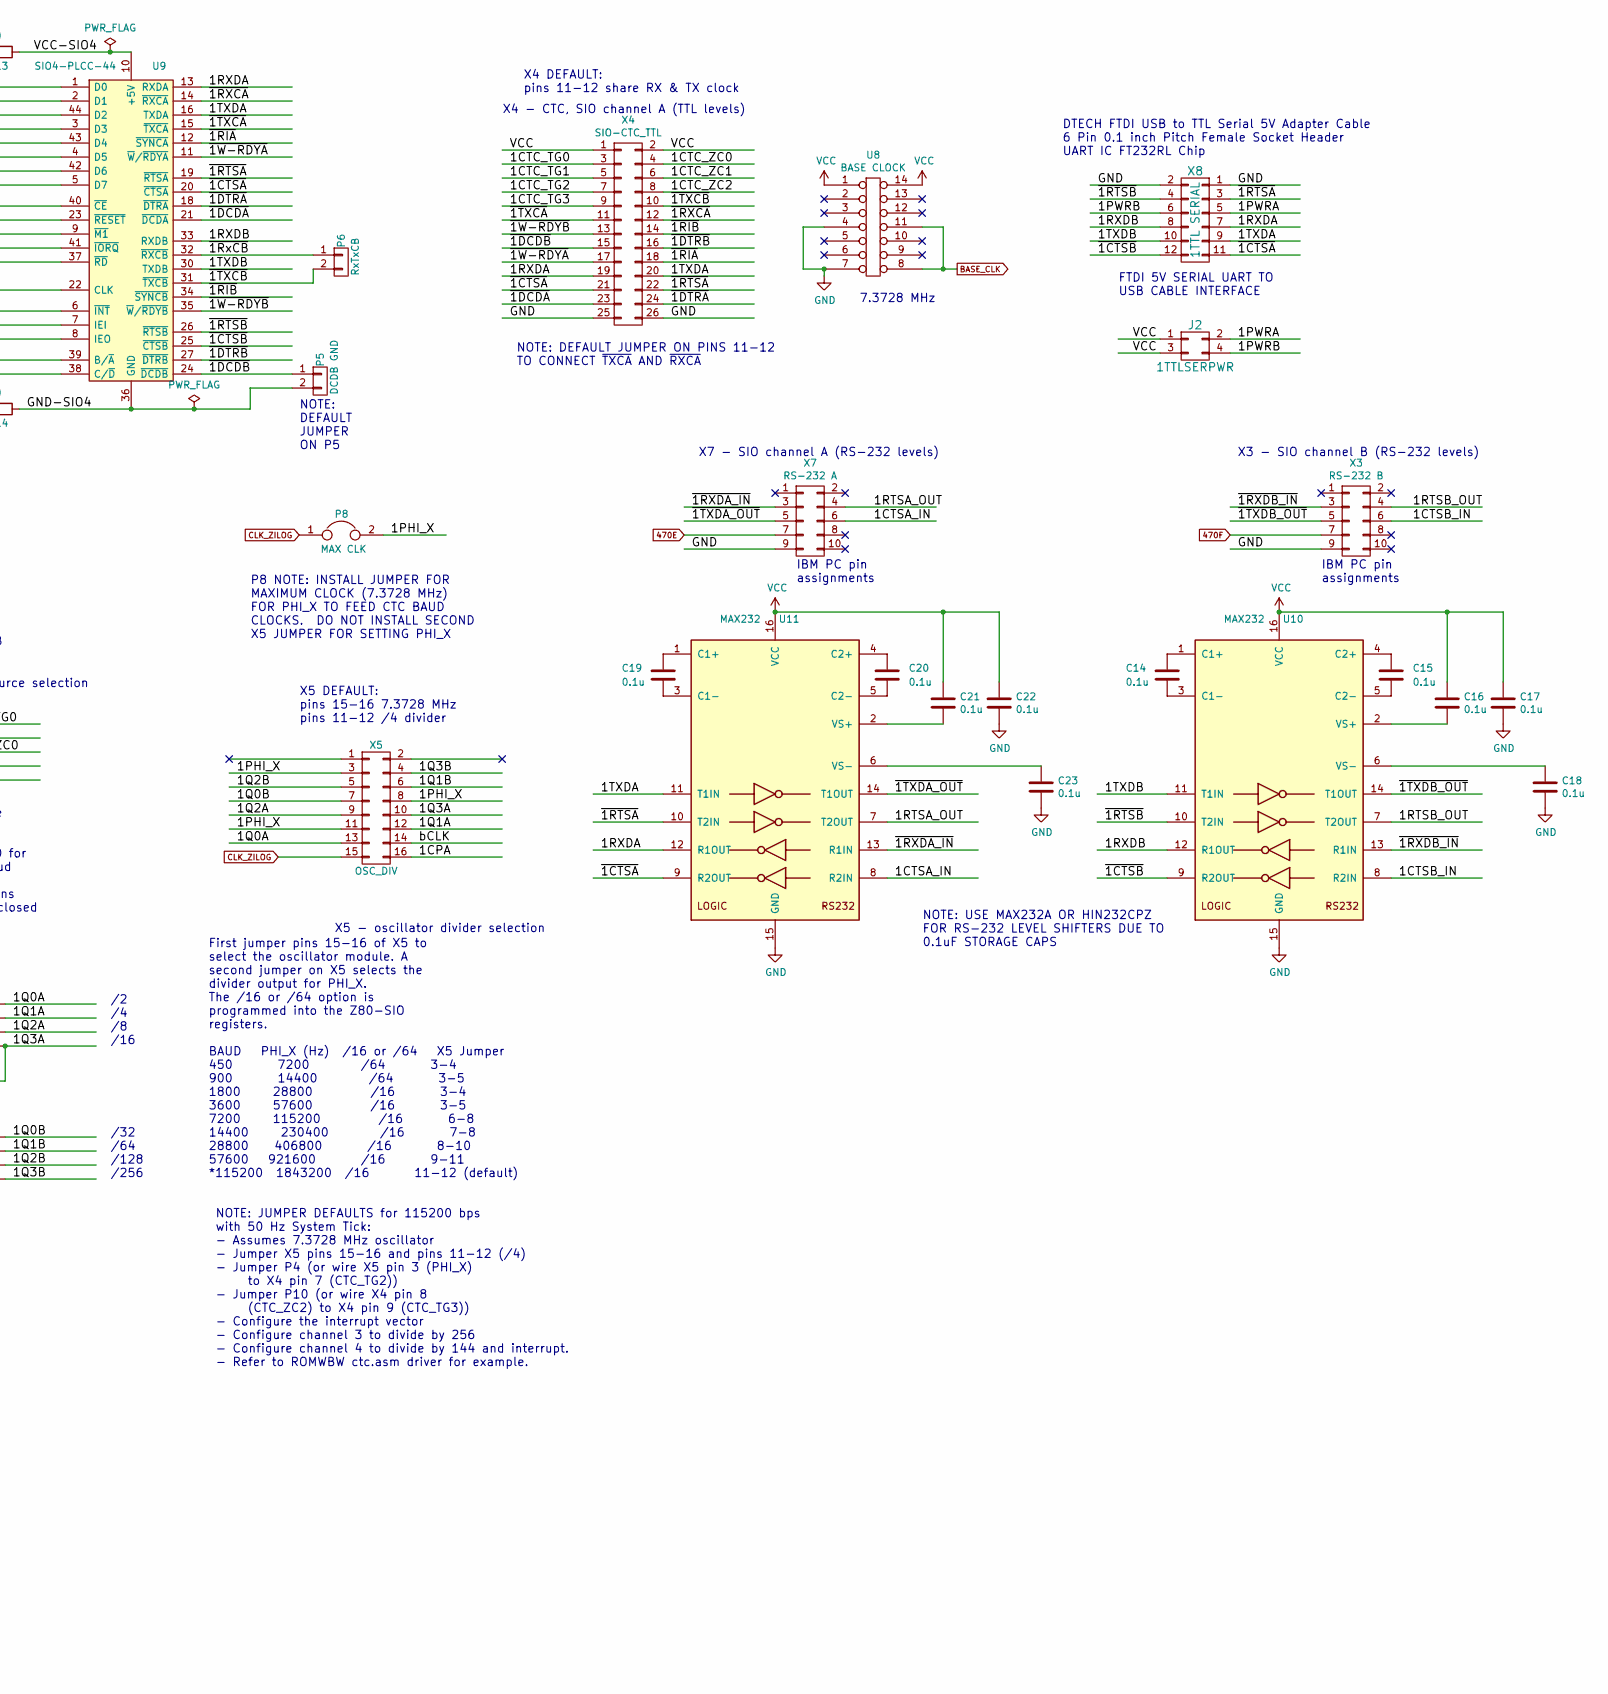
[picture p464: schematic CTC-SIO.sch, part in row 1, column 2]

Parts:
C14, C15, C16, C17, C18, C19, C20, C21, C22, C23: 0.1u; C_Disc_D5.0mm_W2.5mm_P5.00mm
J2: 1TTLSERPWR; PinHeader_2x02_P2.54mm_Vertical
P4: TIMER2; PinHeader_1x02_P2.54mm_Vertical
P5: DCDB GND; PinHeader_1x02_P2.54mm_Vertical
P6: RxTxCB; PinHeader_1x02_P2.54mm_Vertical
P7: INT EN; PinHeader_1x02_P2.54mm_Vertical
P8: MAX CLK; PinHeader_1x02_P2.54mm_Vertical
P10: TIMER3; PinHeader_1x02_P2.54mm_Vertical
R5, R11: 4700; R_Axial_DIN0207_L6.3mm_D2.5mm_P7.62mm_Horizontal
R10: 2200; R_Axial_DIN0207_L6.3mm_D2.5mm_P7.62mm_Horizontal
R13, R14: 0; R_Axial_DIN0207_L6.3mm_D2.5mm_P7.62mm_Horizontal
U7: 1CTC-PLCC-44; PLCC-44_THT-Socket; Manufacturer_Part_Number Z84C3010PEG; Mouser Part Number 692-Z84C3010PEG
U8: BASE CLOCK; DIP-14_W7.62mm
U9: SIO4-PLCC-44; PLCC-44_THT-Socket; Manufacturer_Part_Number Z84C4206PEG; Mouser Part Number 692-Z84C4206PEG
U10, U11: MAX232; DIP-16_W7.62mm
U12: 74LS393; DIP-14_W7.62mm
U13: 74LS09; DIP-14_W7.62mm
X3: RS-232 B; IDC-Header_2x05_P2.54mm_Horizontal
X4: SIO-CTC_TTL; PinHeader_2x13_P2.54mm_Vertical
X5: OSC_DIV; PinHeader_2x08_P2.54mm_Vertical
X6: BAUD_CLK; PinHeader_2x05_P2.54mm_Vertical
X7: RS-232 A; IDC-Header_2x05_P2.54mm_Horizontal
X8: 1TTL SERIAL; IDC-Header_2x06_P2.54mm_Horizontal

Connections:
1CPA: U12.1 (CP), X5.16
1CTC_TG0: U7.35 (CLK/TRG0), X4.3, X6.2
1CTC_TG1: U7.33 (CLK/TRG1), X4.5, X6.1
1CTC_TG2: P4.2, U7.32 (CLK/TRG2), X4.7
1CTC_TG3: P10.2, U7.31 (CLK/TRG3), X4.9
1CTC_ZC0: U7.10 (ZC/TO0), X4.4, X6.6
1CTC_ZC1: U7.12 (ZC/TO1), X4.6, X6.9
1CTC_ZC2: P10.1, U7.13 (ZC/TO2), X4.8
1CTSA_IN: U11.8 (R2IN), X7.6
1CTSB_IN: U10.8 (R2IN), X3.6
1PHI_X: P8.2, X5.3, X5.8, X5.11, X6.3, X6.4, X6.7, X6.8
1PWRA: J2.2, X8.5
1PWRB: J2.4, X8.6
1Q0A: U12.3 (Q0), X5.13
1Q0B: U12.11 (Q0), X5.7
1Q1A: U12.4 (Q1), X5.12
1Q1B: U12.10 (Q1), X5.6
1Q2A: P4.1, U12.5 (Q2), X5.9
1Q2B: U12.9 (Q2), X5.5
1Q3A: U12.6 (Q3), U12.13 (CP), X5.10
1Q3B: U12.8 (Q3), X5.4
1RTSA_OUT: U11.7 (T2OUT), X7.4
1RTSB_OUT: U10.7 (T2OUT), X3.4
1RXDA: U9.13 (RXDA), U11.12 (R1OUT), X4.19, X8.7
1RXDB: U9.33 (RXDB), U10.12 (R1OUT), X8.8
1TXDA: U9.16 (TXDA), U11.11 (T1IN), X4.20, X8.9
1TXDB: U9.30 (TXDB), U10.11 (T1IN), X8.10
10KA: U9.8 (IEO), U13.13
10KB: U7.16 (IEO), U9.7 (IEI), U13.12
10KC: U13.4
10KD: U13.5
470E: X7.7
470F: X3.7
BASE_CLK: U8.8, U8.11
CLK_ZILOG: P8.1, X5.15
GND: C17.2, C18.2, C22.2, C23.2, R14.2, U7.7 (GND), U8.4, U8.7, U10.15 (GND), U11.15 (GND), X3.9, X4.25, X4.26, X7.9, X8.1, X8.2
GND-SIO4: P5.2, R14.1, U9.36 (GND)
IEO_CTC2: U7.21 (IEI), U13.2
unnamed: C14.1, U10.1 (C1+)
unnamed: C14.2, U10.3 (C1-)
unnamed: C15.1, U10.4 (C2+)
unnamed: C15.2, U10.5 (C2-)
unnamed: C16.2, U10.2 (VS+)
unnamed: C18.1, U10.6 (VS-)
unnamed: C19.1, U11.1 (C1+)
unnamed: C19.2, U11.3 (C1-)
unnamed: C20.1, U11.4 (C2+)
unnamed: C20.2, U11.5 (C2-)
unnamed: C21.2, U11.2 (VS+)
unnamed: C23.1, U11.6 (VS-)
unnamed: P7.1, U13.8
VCC: C16.1, C17.1, C21.1, C22.1, J2.1, J2.3, R5.2, R10.2, R11.2, R13.2, U7.37 (+5V), U8.1, U8.14, U10.16 (VCC), U11.16 (VCC), X4.1, X4.2
VCC-SIO4: R13.1, U9.10 (+5V)
ZERO: U12.2 (MR), U12.12 (MR)
bA0: U7.27 (CS0), U9.39 (B/~A)
bA1: U7.29 (CS1), U9.38 (C/~D)
bCLK: U7.24 (CLK), U9.22 (CLK), X5.14
bD0: U7.41 (D0), U9.1 (D0)
bD1: U7.42 (D1), U9.2 (D1)
bD2: U7.43 (D2), U9.44 (D2)
bD3: U7.44 (D3), U9.3 (D3)
bD4: U7.1 (D4), U9.43 (D4)
bD5: U7.2 (D5), U9.4 (D5)
bD6: U7.4 (D6), U9.42 (D6)
bD7: U7.5 (D7), U9.5 (D7)
~1CTSA: U9.20 (~CTSA), U11.9 (R2OUT), X4.21, X8.11
~1CTSB: U9.25 (~CTSB), U10.9 (R2OUT), X8.12
~1DCDA: U9.21 (~DCDA), X4.23
~1DCDB: P5.1, U9.24 (~DCDB), X4.15
~1DTRA: U9.18 (~DTRA), X4.24
~1DTRB: U9.27 (~DTRB), X4.16
~1RIA: U9.12 (~SYNCA), X4.18
~1RIB: U9.34 (~SYNCB), X4.14
~1RTSA: U9.19 (~RTSA), U11.10 (T2IN), X4.22, X8.3
~1RTSB: U9.26 (~RTSB), U10.10 (T2IN), X8.4
~1RXCA: U9.14 (~RXCA), X4.12
~1RXDA_IN: U11.13 (R1IN), X7.3
~1RXDB_IN: U10.13 (R1IN), X3.3
~1RxCB: P6.1, U9.32 (~RXCB), X6.10
~1TXCA: U9.15 (~TXCA), X4.11, X6.5
~1TXCB: P6.2, U9.31 (~TXCB), X4.10
~1TXDA_OUT: U11.14 (T1OUT), X7.5
~1TXDB_OUT: U10.14 (T1OUT), X3.5
~1W-RDYA: U9.11 (~W~/~RDYA), X4.17
~1W-RDYB: U9.35 (~W~/~RDYB), X4.13
~CS_CTC1: U7.25 (~CE)
~CS_SIO1: U9.40 (~CE)
~IEI: R5.1
~IEO: R10.1, U13.3, U13.6, U13.11
~INT0: P7.2
~bIEI: U13.1
~bINT: R11.1, U7.19 (~INT), U9.6 (~INT), U13.9, U13.10
~bIORQ: U7.14 (~IORQ), U9.41 (~IORQ)
~bM1: U7.22 (~M1), U9.9 (~M1)
~bRD: U7.9 (~RD), U9.37 (~RD)
~bRESET: U7.26 (~RESET), U9.23 (~RESET)

Notes on the sheet:
IBM PC pin assignments
IA: HIGH DURING INTERRUPT ACTIVE LOW DURING NORMAL OPERATION
X6 - SIO baud rate clock source selection
X3 - SIO channel B (RS-232 levels)
X4 - CTC, SIO channel A (TTL levels)
X5 - oscillator divider selection
X7 - SIO channel A (RS-232 levels)
NOTE: ~INT~ RELIES ON 4700 OHM PULL UP ON PROCESSOR
FTDI 5V SERIAL UART TO USB CABLE INTERFACE
DTECH FTDI USB to TTL Serial 5V Adapter Cable 6 Pin 0.1 inch Pitch Female Socket Header UART IC FT232RL Chip
NOTE: DEFAULT JUMPER ON PINS 11-12 TO CONNECT ~TXCA~ AND ~RXCA~
NOTE: JUMPER DEFAULTS for 115200 bps with 50 Hz System Tick: - Assumes 7.3728 MHz oscillator - Jumper X5 pins 15-16 and pins 11-12 (/4) - Jumper P4 (or wire X5 pin 3 (PHI_X) to X4 pin 7 (CTC_TG2)) - Jumper P10 (or wire X4 pin 8 (CTC_ZC2) to X4 pin 9 (CTC_TG3)) - Configure the interrupt vector - Con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
First jumper pins 15-16 of X5 to select the oscillator module. A second jumper on X5 selects the divider output for PHI_X. The /16 or /64 option is programmed into the Z80-SIO registers. BAUD PHI_X (Hz) /16 or /64 X5 Jumper 450 7200 /64 3-4 900 14400 /64 3-5 1800 28800 /16 3-4 3600 57600 /16 3-5 72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
The Z80-SIO's clock pins need to be connected to PHI_X using header X6. For the FIXED baud rate jumper pins 3-5 or 5-7 for channel A and 8-10 for channel B of header X6. For CTC baud rate to SIO clock for channel A set with pins 2-4 and channel B with pins 1-3. This assumes pins 11-12 are closed on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
X6 DEFAULT: pins 3-5 FIXED channel A pins 8-10 FIXED channel B
X5 DEFAULT: pins 15-16 7.3728 MHz pins 11-12 /4 divider
X4 DEFAULT: pins 11-12 share RX & TX clock
/32 /64 /128 /256
/2 /4 /8 /16
NOTE: USE MAX232A OR HIN232CPZ FOR RS-232 LEVEL SHIFTERS DUE TO 0.1uF STORAGE CAPS
NOTE: DEFAULT JUMPER ON P4
NOTE: DEFAULT JUMPER ON P10
NOTE: DEFAULT JUMPER ON P5
P4 NOTE: SYSTEM TIMER INPUT DEFAULT IS 1Q2A (7.3728 / 8 MHz = 921.6 KHz)
7.3728 MHz
P8 NOTE: INSTALL JUMPER FOR MAXIMUM CLOCK (7.3728 MHz) FOR PHI_X TO FEED CTC BAUD CLOCKS. DO NOT INSTALL SECOND X5 JUMPER FOR SETTING PHI_X
