lynchaj/duodyne/05 input-output.Zilog, V1.1/temp/GAL.sch

## KiCad design 05 input-output.Zilog, V1.1/temp/GAL.sch (2023-03-30)

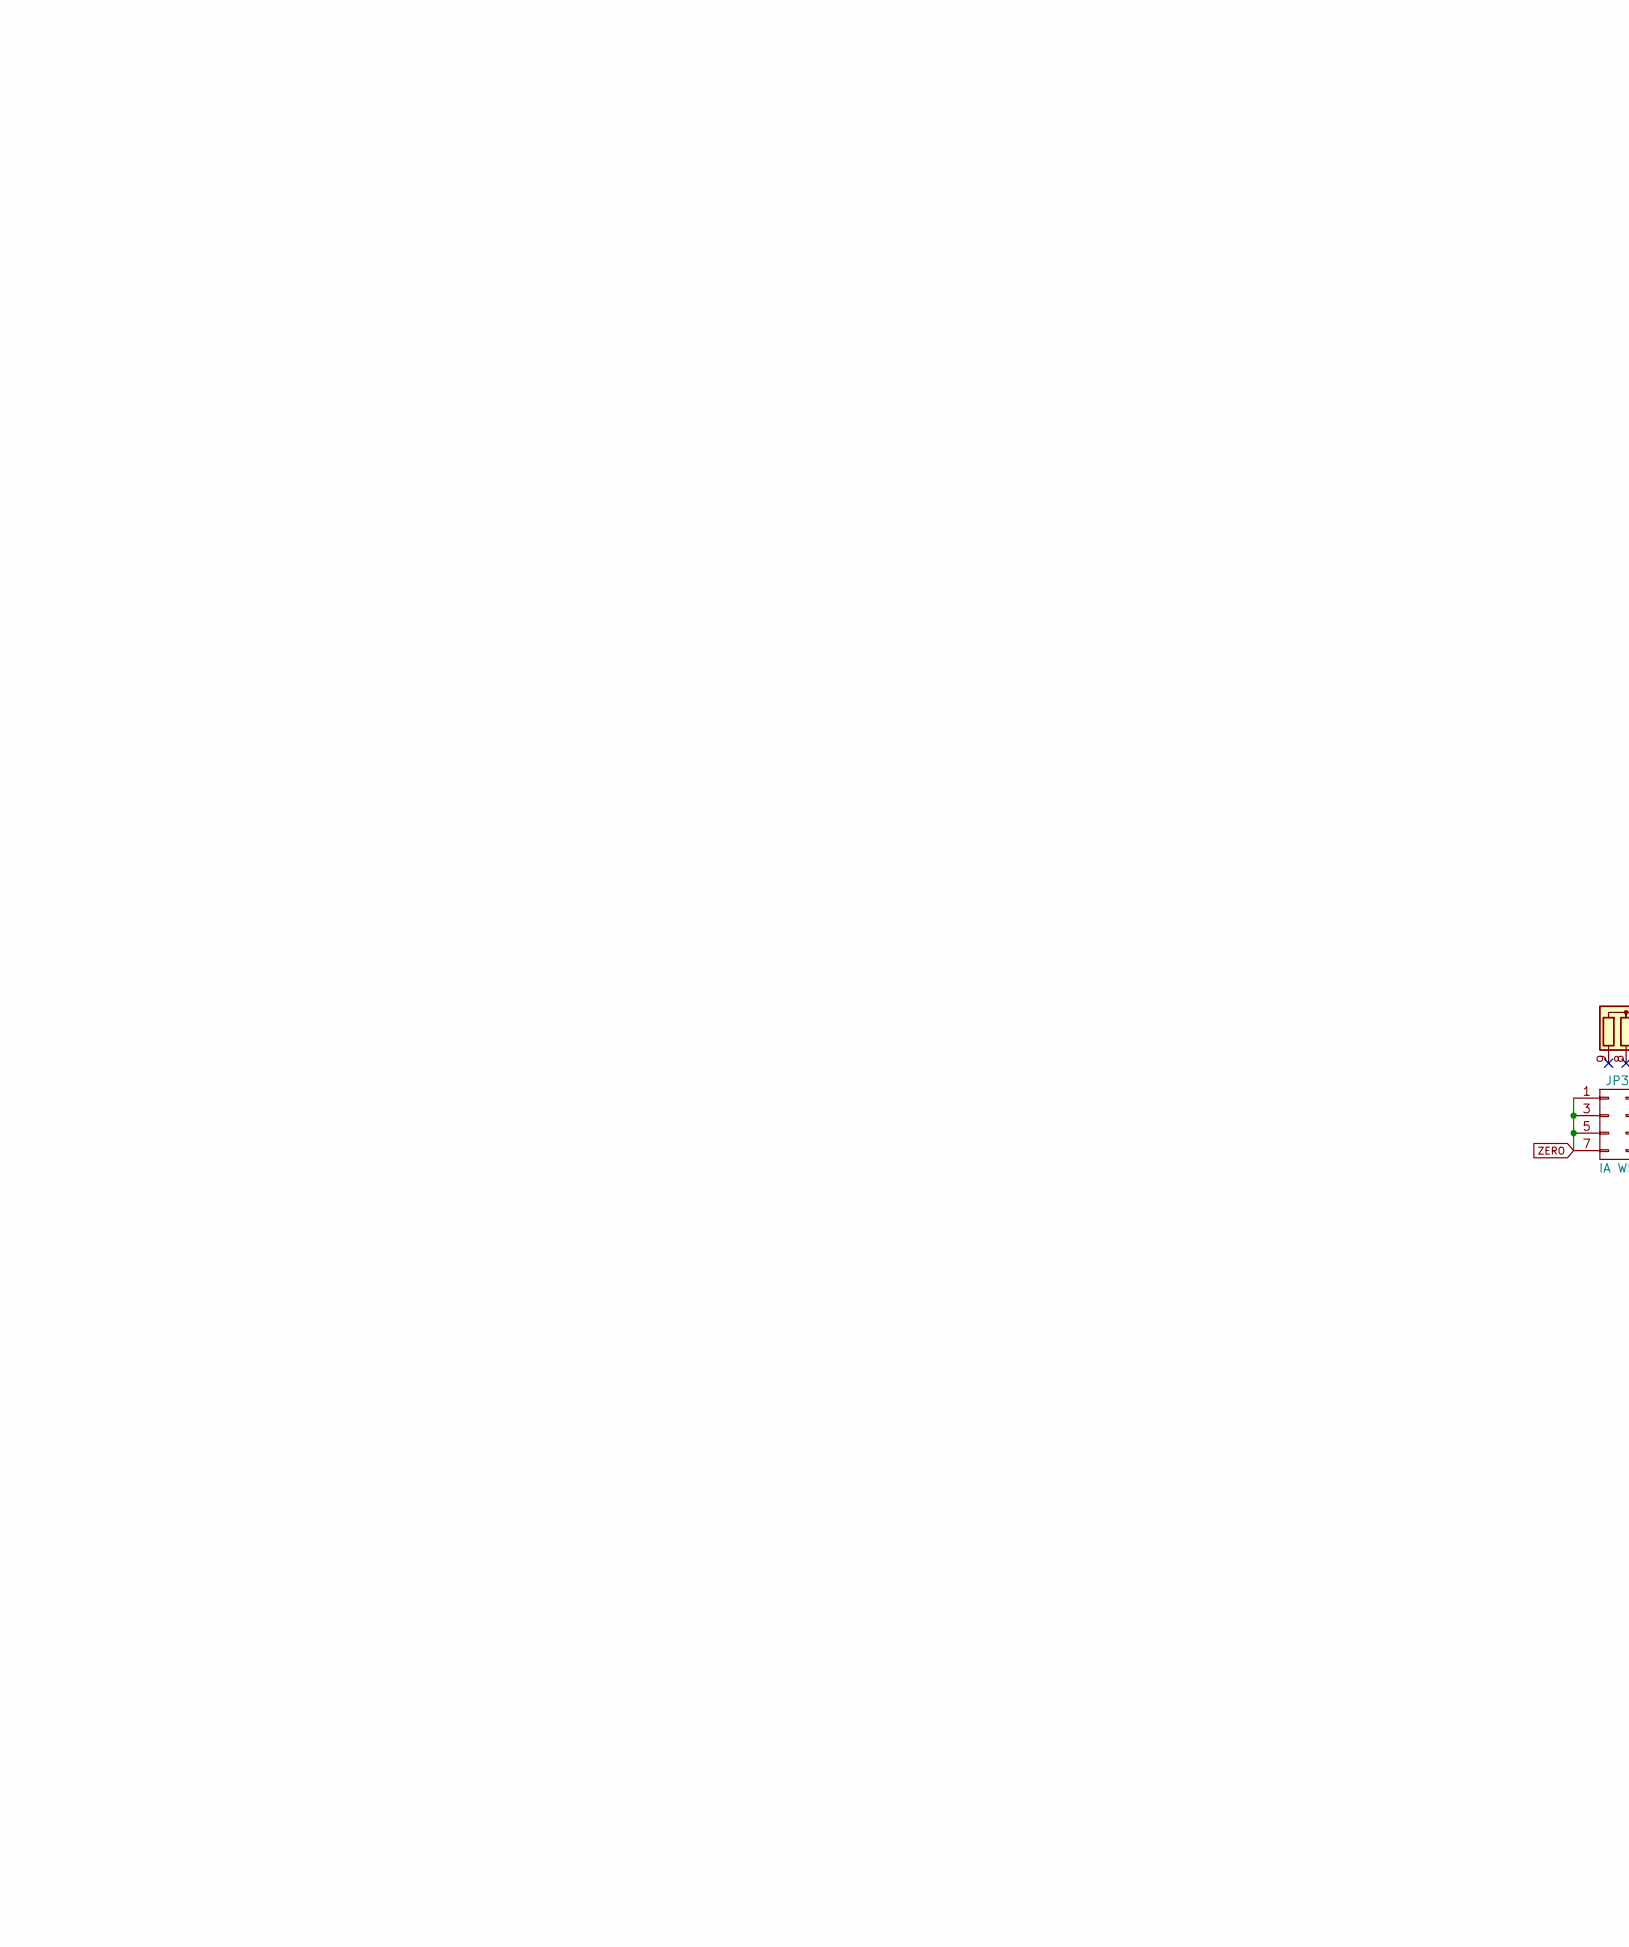
[picture p465: schematic GAL.sch, part in row 1, column 1]

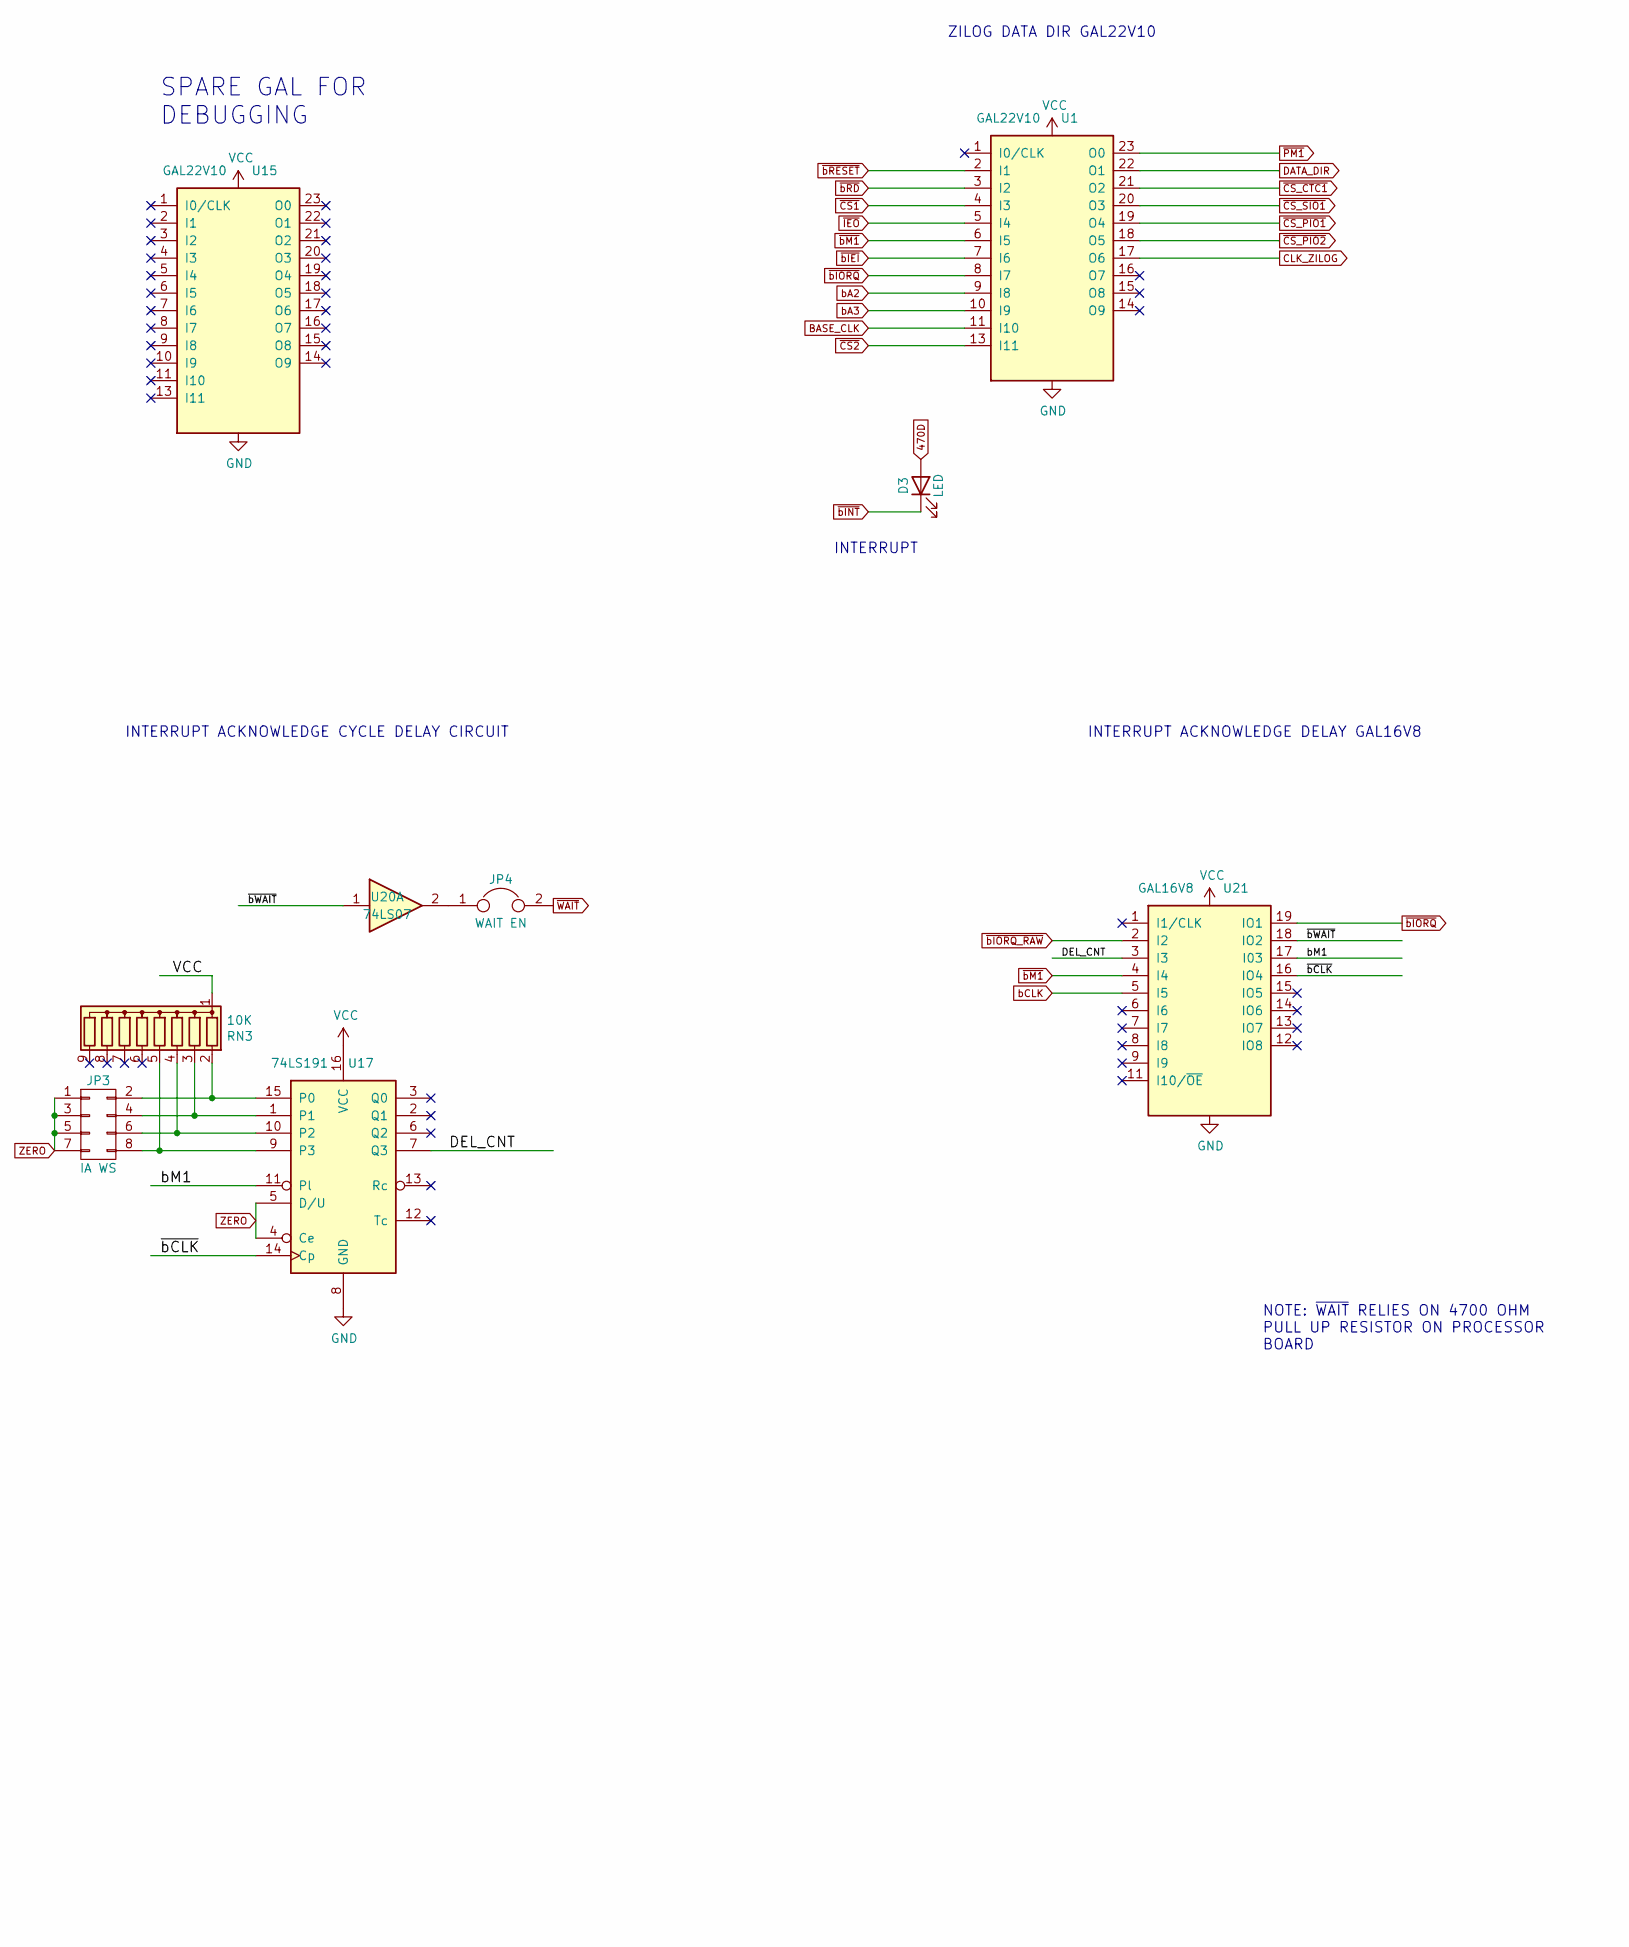
[picture p466: schematic GAL.sch, part in row 1, column 2]

Parts:
D3: LED; LED_D3.0mm_Horizontal_O3.81mm_Z2.0mm
JP3: IA WS; PinHeader_2x04_P2.54mm_Vertical
JP4: WAIT EN; PinHeader_1x02_P2.54mm_Vertical
RN3: 10K; R_Array_SIP9
U1, U15: GAL22V10; DIP-24_W7.62mm
U17: 74LS191; DIP-16_W7.62mm
U20: 74LS07
U21: GAL16V8; DIP-20_W7.62mm

Connections:
470D: D3.2 (A)
BASE_CLK: U1.11 (I10)
CLK_ZILOG: U1.17 (O6)
DATA_DIR: U1.22 (O1)
DEL_CNT: U17.7 (Q3), U21.3 (I3)
GND: U1.12 (GND), U15.12 (GND), U17.8 (GND), U21.10 (GND)
unnamed: JP3.2, RN3.2 (R1), U17.15 (P0)
unnamed: JP3.4, RN3.3 (R2), U17.1
unnamed: JP3.6, RN3.4 (R3), U17.10 (P2)
unnamed: JP3.8, RN3.5 (R4), U17.9 (P3)
unnamed: JP4.1, U20.2
VCC: RN3.1 (common), U1.24 (VCC), U15.24 (VCC), U17.16 (VCC), U21.20 (VCC)
ZERO: JP3.1, JP3.3, JP3.5, JP3.7, U17.4 (Ce), U17.5 (D/U)
bA2: U1.9 (I8)
bA3: U1.10 (I9)
bCLK: U21.5 (I5)
bM1: U17.11 (Pl), U21.17 (I03)
~CS1: U1.4 (I3)
~CS2: U1.13 (I11)
~CS_CTC1: U1.21 (O2)
~CS_PIO1: U1.19 (O4)
~CS_PIO2: U1.18 (O5)
~CS_SIO1: U1.20 (O3)
~IEO: U1.5 (I4)
~PM1: U1.23 (O0)
~WAIT: JP4.2
~bCLK: U17.14 (Cp), U21.16 (IO4)
~bIEI: U1.7 (I6)
~bINT: D3.1 (K)
~bIORQ: U1.8 (I7), U21.19 (IO1)
~bIORQ_RAW: U21.2 (I2)
~bM1: U1.6 (I5), U21.4 (I4)
~bRD: U1.3 (I2)
~bRESET: U1.2 (I1)
~bWAIT: U20.1, U21.18 (IO2)

Notes on the sheet:
INTERRUPT
NOTE: ~WAIT~ RELIES ON 4700 OHM PULL UP RESISTOR ON PROCESSOR BOARD
INTERRUPT ACKNOWLEDGE CYCLE DELAY CIRCUIT
INTERRUPT ACKNOWLEDGE DELAY GAL16V8
SPARE GAL FOR DEBUGGING
ZILOG DATA DIR GAL22V10
