lynchaj/duodyne/05 input-output.Zilog, V1.1/temp/IO.sch

## KiCad design 05 input-output.Zilog, V1.1/temp/IO.sch (2023-03-30)

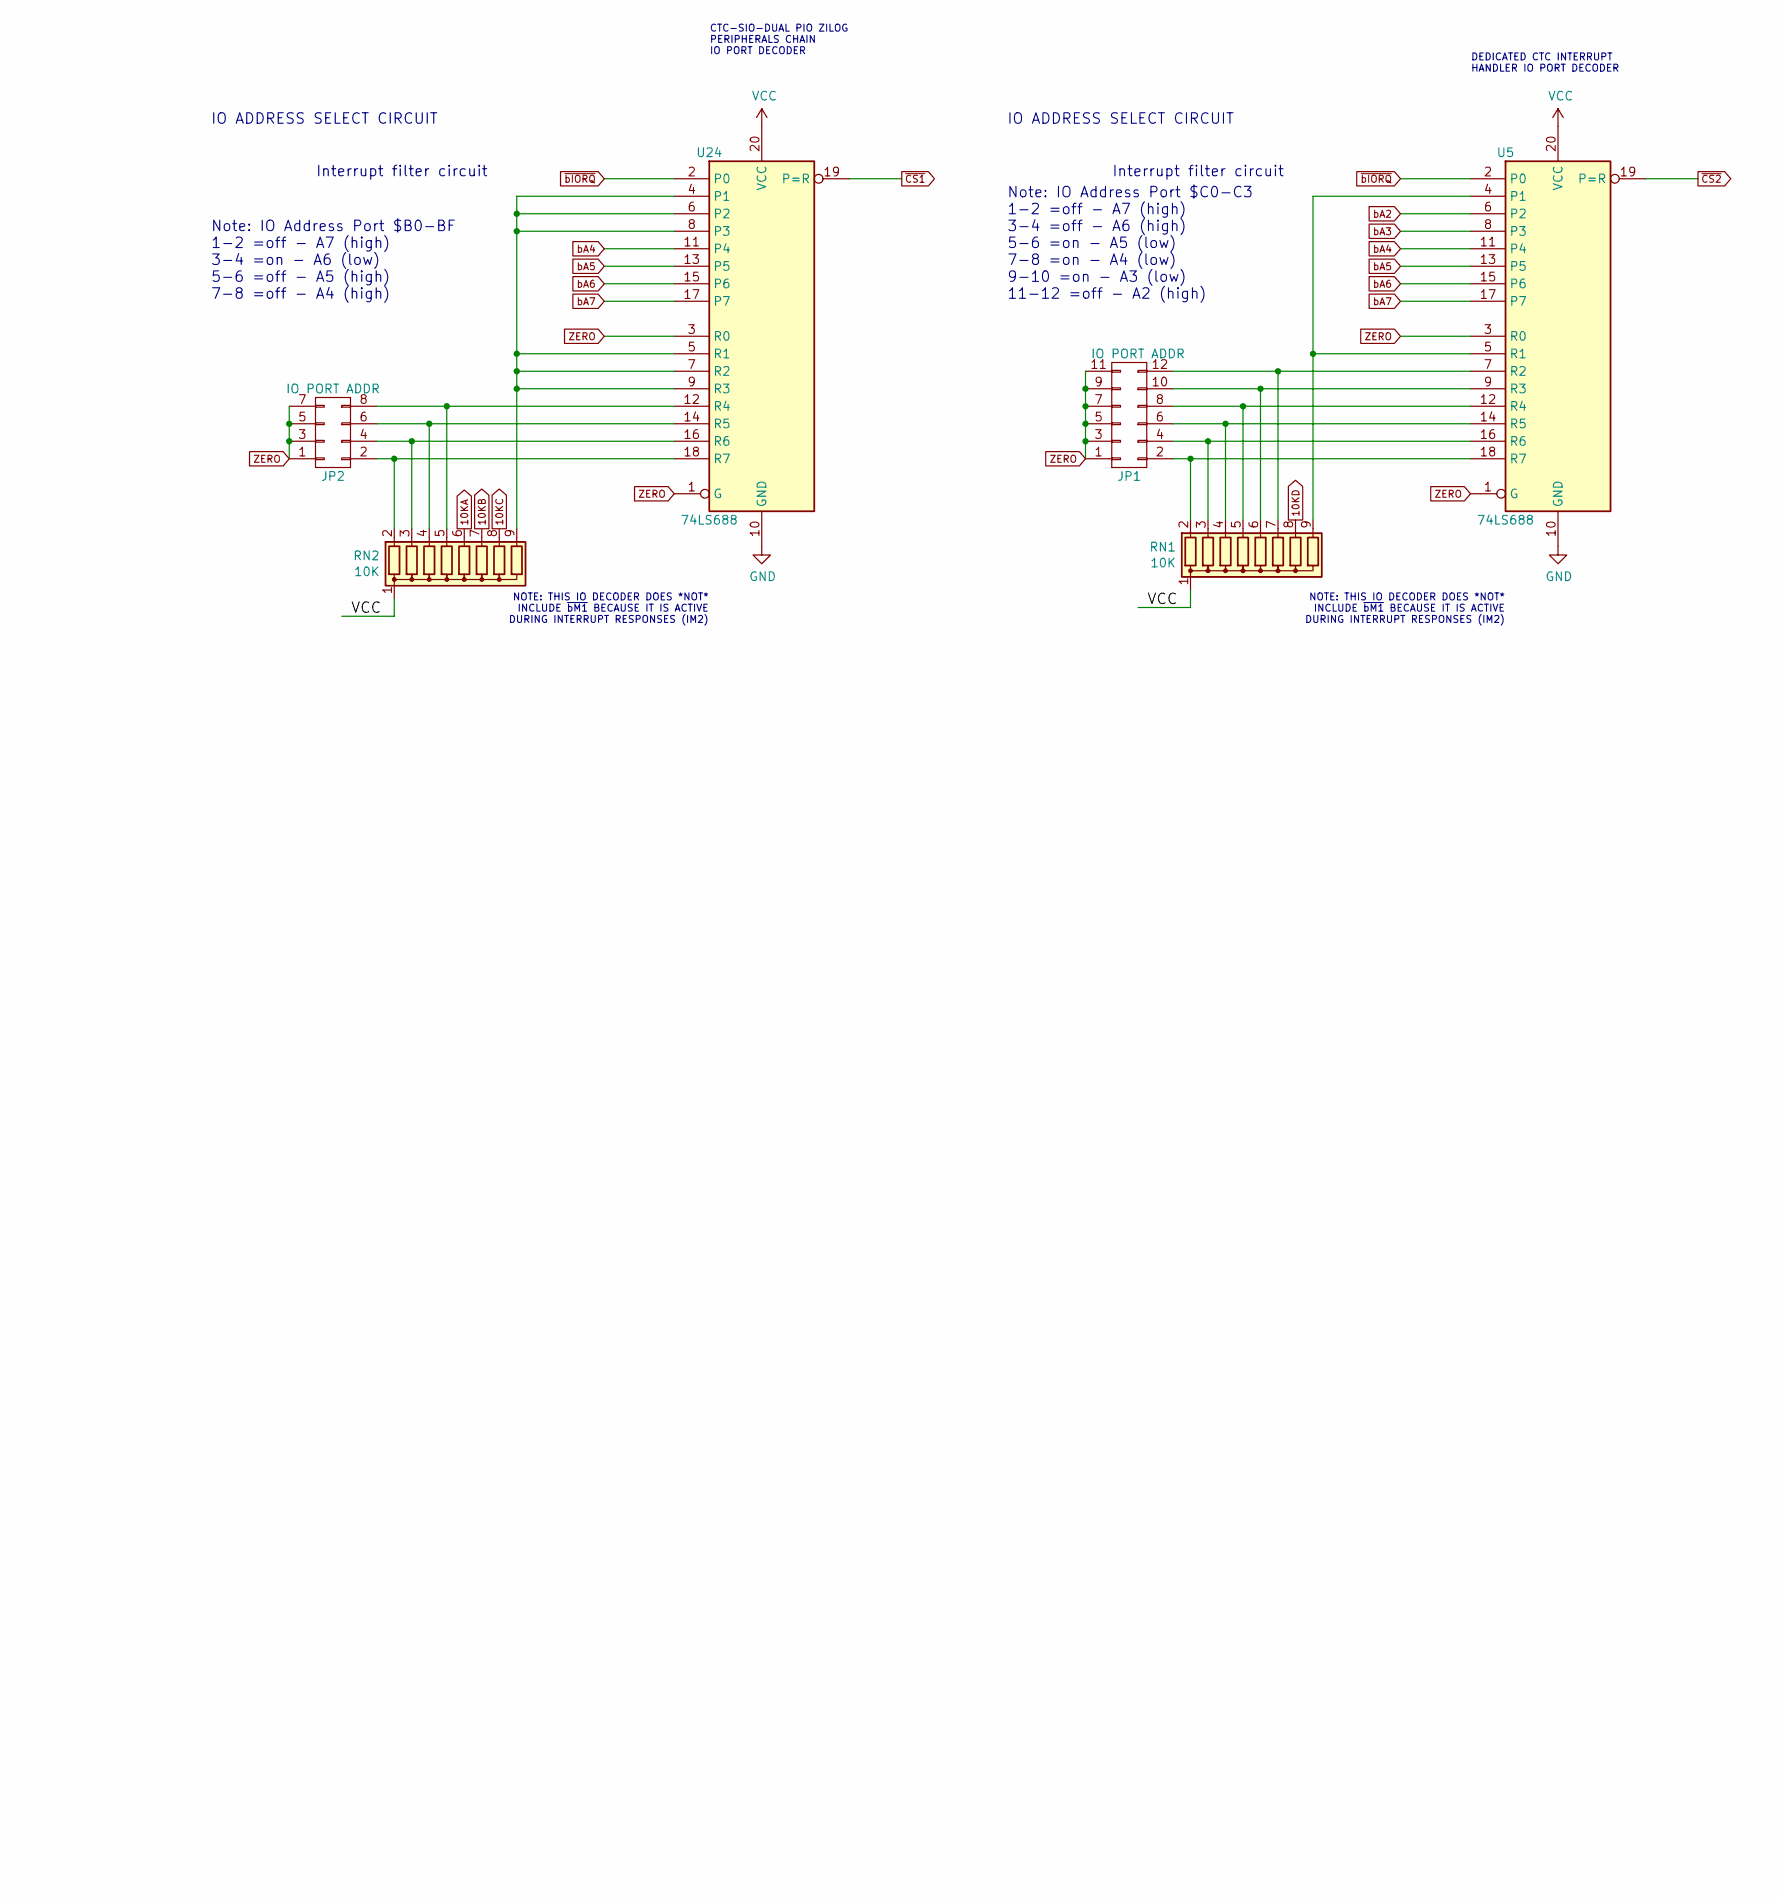
[picture p467: schematic IO.sch, part in row 1, column 2]

Parts:
JP1: IO PORT ADDR; PinHeader_2x06_P2.54mm_Vertical
JP2: IO PORT ADDR; PinHeader_2x04_P2.54mm_Vertical
RN1, RN2: 10K; R_Array_SIP9
U5, U24: 74LS688; DIP-20_W7.62mm

Connections:
10KA: RN2.6 (R5)
10KB: RN2.7 (R6)
10KC: RN2.8 (R7)
10KD: RN1.8 (R7)
GND: U5.10 (GND), U24.10 (GND)
unnamed: JP1.2, RN1.2 (R1), U5.18 (R7)
unnamed: JP1.4, RN1.3 (R2), U5.16 (R6)
unnamed: JP1.6, RN1.4 (R3), U5.14 (R5)
unnamed: JP1.8, RN1.5 (R4), U5.12 (R4)
unnamed: JP1.10, RN1.6 (R5), U5.9 (R3)
unnamed: JP1.12, RN1.7 (R6), U5.7 (R2)
unnamed: JP2.2, RN2.2 (R1), U24.18 (R7)
unnamed: JP2.4, RN2.3 (R2), U24.16 (R6)
unnamed: JP2.6, RN2.4 (R3), U24.14 (R5)
unnamed: JP2.8, RN2.5 (R4), U24.12 (R4)
unnamed: RN1.9 (R8), U5.4 (P1), U5.5 (R1)
unnamed: RN2.9 (R8), U24.4 (P1), U24.5 (R1), U24.6 (P2), U24.7 (R2), U24.8 (P3), U24.9 (R3)
VCC: RN1.1 (common), RN2.1 (common), U5.20 (VCC), U24.20 (VCC)
ZERO: JP1.1, JP1.3, JP1.5, JP1.7, JP1.9, JP1.11, JP2.1, JP2.3, JP2.5, JP2.7, U5.1 (G), U5.3 (R0), U24.1 (G), U24.3 (R0)
bA2: U5.6 (P2)
bA3: U5.8 (P3)
bA4: U5.11 (P4), U24.11 (P4)
bA5: U5.13 (P5), U24.13 (P5)
bA6: U5.15 (P6), U24.15 (P6)
bA7: U5.17 (P7), U24.17 (P7)
~CS1: U24.19 (P=R)
~CS2: U5.19 (P=R)
~bIORQ: U5.2 (P0), U24.2 (P0)

Notes on the sheet:
Note: IO Address Port $B0-BF 1-2 =off - A7 (high) 3-4 =on - A6 (low) 5-6 =off - A5 (high) 7-8 =off - A4 (high)
IO ADDRESS SELECT CIRCUIT
Interrupt filter circuit
NOTE: THIS IO DECODER DOES *NOT* INCLUDE ~bM1~ BECAUSE IT IS ACTIVE DURING INTERRUPT RESPONSES (IM2)
Note: IO Address Port $C0-C3 1-2 =off - A7 (high) 3-4 =off - A6 (high) 5-6 =on - A5 (low) 7-8 =on - A4 (low) 9-10 =on - A3 (low) 11-12 =off - A2 (high)
CTC-SIO-DUAL PIO ZILOG PERIPHERALS CHAIN IO PORT DECODER
DEDICATED CTC INTERRUPT HANDLER IO PORT DECODER
