lynchaj/duodyne/05 input-output.Zilog, V1.1/temp/buffers.sch

## KiCad design 05 input-output.Zilog, V1.1/temp/buffers.sch (2023-03-30)

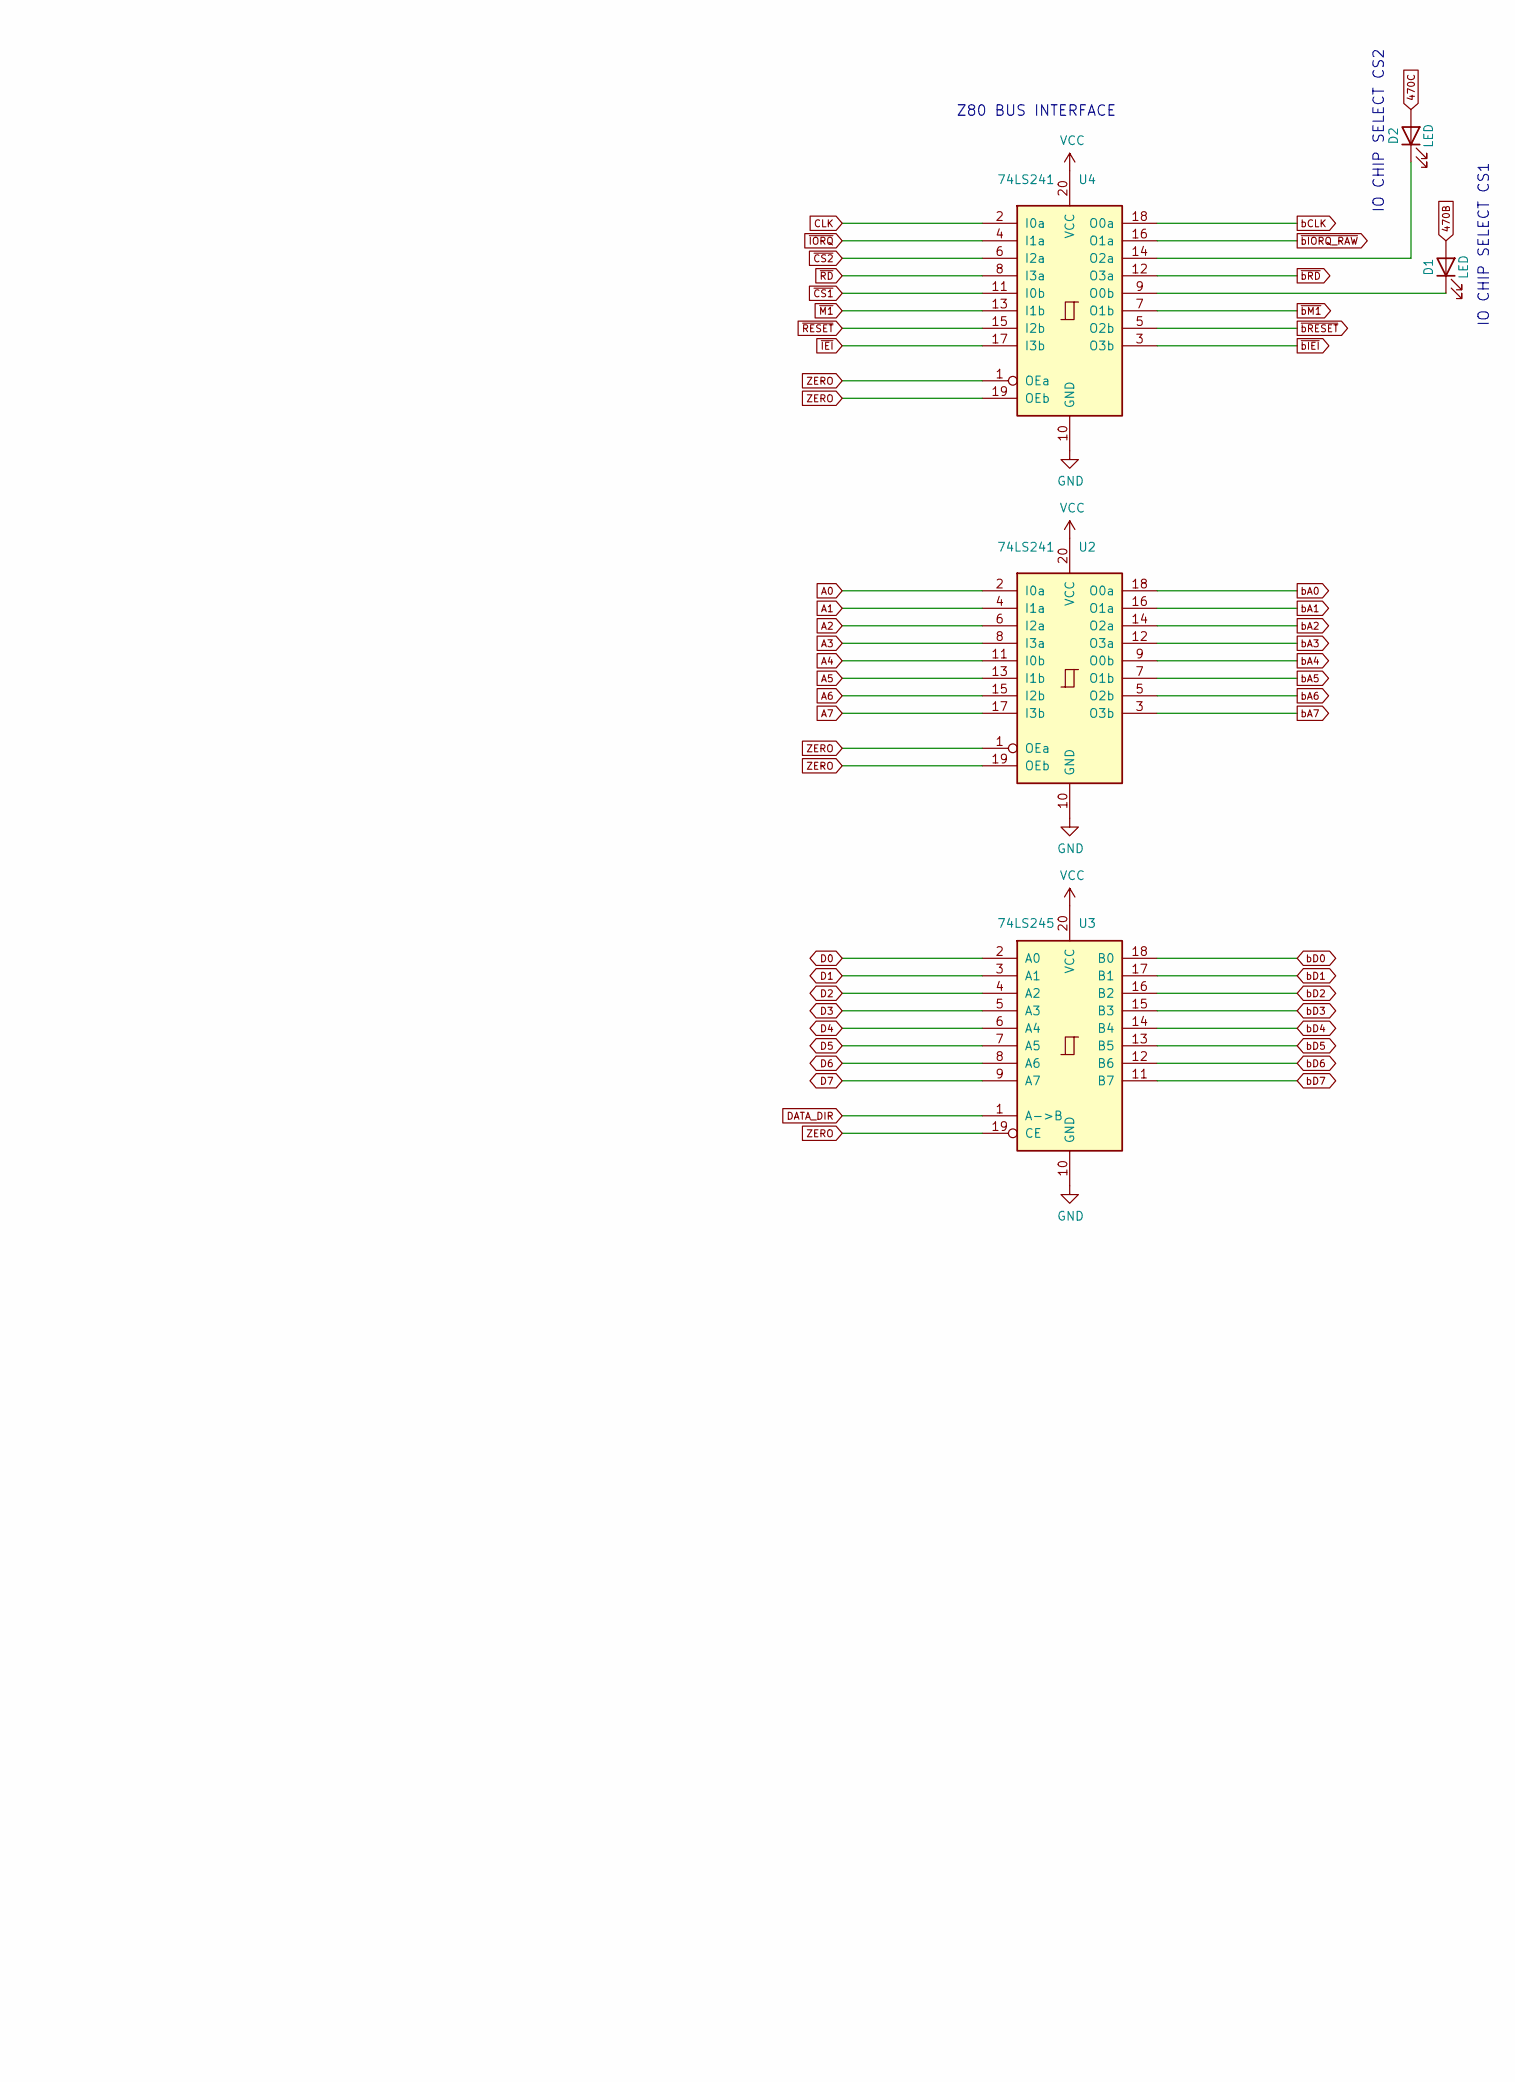
[picture p468: schematic buffers.sch, part in row 1, column 2]

Parts:
D1, D2: LED; LED_D3.0mm_Horizontal_O3.81mm_Z2.0mm
U2, U4: 74LS241; DIP-20_W7.62mm
U3: 74LS245; DIP-20_W7.62mm

Connections:
470B: D1.2 (A)
470C: D2.2 (A)
A0: U2.2 (I0a)
A1: U2.4 (I1a)
A2: U2.6 (I2a)
A3: U2.8 (I3a)
A4: U2.11 (I0b)
A5: U2.13 (I1b)
A6: U2.15 (I2b)
A7: U2.17 (I3b)
CLK: U4.2 (I0a)
D0: U3.2 (A0)
D1: U3.3 (A1)
D2: U3.4 (A2)
D3: U3.5 (A3)
D4: U3.6 (A4)
D5: U3.7 (A5)
D6: U3.8 (A6)
D7: U3.9 (A7)
DATA_DIR: U3.1 (A->B)
GND: U2.10 (GND), U3.10 (GND), U4.10 (GND)
unnamed: D1.1 (K), U4.9 (O0b)
unnamed: D2.1 (K), U4.14 (O2a)
VCC: U2.20 (VCC), U3.20 (VCC), U4.20 (VCC)
ZERO: U2.1 (OEa), U2.19 (OEb), U3.19 (CE), U4.1 (OEa), U4.19 (OEb)
bA0: U2.18 (O0a)
bA1: U2.16 (O1a)
bA2: U2.14 (O2a)
bA3: U2.12 (O3a)
bA4: U2.9 (O0b)
bA5: U2.7 (O1b)
bA6: U2.5 (O2b)
bA7: U2.3 (O3b)
bCLK: U4.18 (O0a)
bD0: U3.18 (B0)
bD1: U3.17 (B1)
bD2: U3.16 (B2)
bD3: U3.15 (B3)
bD4: U3.14 (B4)
bD5: U3.13 (B5)
bD6: U3.12 (B6)
bD7: U3.11 (B7)
~CS1: U4.11 (I0b)
~CS2: U4.6 (I2a)
~IEI: U4.17 (I3b)
~IORQ: U4.4 (I1a)
~M1: U4.13 (I1b)
~RD: U4.8 (I3a)
~RESET: U4.15 (I2b)
~bIEI: U4.3 (O3b)
~bIORQ_RAW: U4.16 (O1a)
~bM1: U4.7 (O1b)
~bRD: U4.12 (O3a)
~bRESET: U4.5 (O2b)

Notes on the sheet:
Z80 BUS INTERFACE
IO CHIP SELECT CS1
IO CHIP SELECT CS2
