lynchaj/duodyne/05 input-output.Zilog, V1.1/temp/bus.sch

## KiCad design 05 input-output.Zilog, V1.1/temp/bus.sch (2023-03-30)

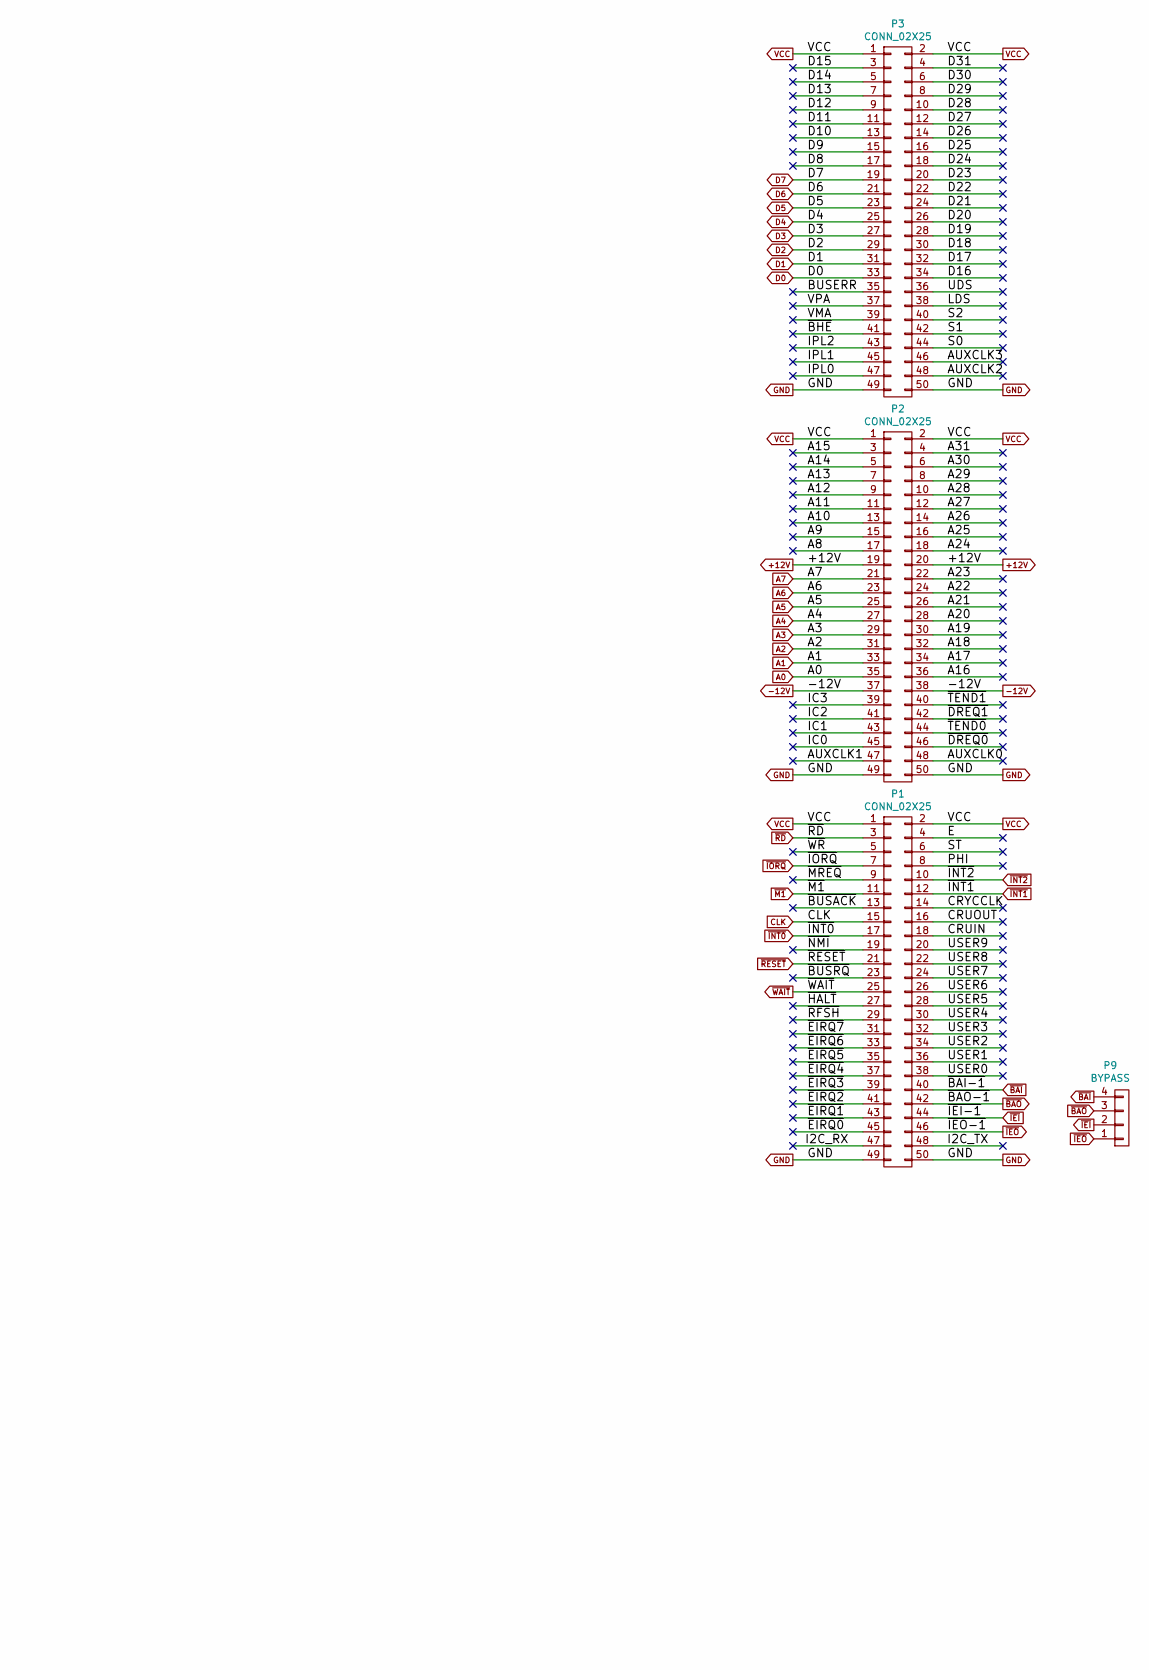
[picture p469: schematic bus.sch, part in row 1, column 2]

Parts:
P1, P2, P3: CONN_02X25; IDC-Header_2x25_P2.54mm_Horizontal
P9: BYPASS; PinHeader_1x04_P2.54mm_Vertical

Connections:
+12V: P2.19, P2.20
-12V: P2.37, P2.38
A0: P2.35
A1: P2.33
A2: P2.31
A3: P2.29
A4: P2.27
A5: P2.25
A6: P2.23
A7: P2.21
A8: P2.17
A9: P2.15
A10: P2.13
A11: P2.11
A12: P2.9
A13: P2.7
A14: P2.5
A15: P2.3
A16: P2.36
A17: P2.34
A18: P2.32
A19: P2.30
A20: P2.28
A21: P2.26
A22: P2.24
A23: P2.22
A24: P2.18
A25: P2.16
A26: P2.14
A27: P2.12
A28: P2.10
A29: P2.8
A30: P2.6
A31: P2.4
AUXCLK0: P2.48
AUXCLK1: P2.47
AUXCLK2: P3.48
AUXCLK3: P3.46
BUSERR: P3.35
CLK: P1.15
CRUIN: P1.18
CRUOUT: P1.16
CRYCCLK: P1.14
D0: P3.33
D1: P3.31
D2: P3.29
D3: P3.27
D4: P3.25
D5: P3.23
D6: P3.21
D7: P3.19
D8: P3.17
D9: P3.15
D10: P3.13
D11: P3.11
D12: P3.9
D13: P3.7
D14: P3.5
D15: P3.3
D16: P3.34
D17: P3.32
D18: P3.30
D19: P3.28
D20: P3.26
D21: P3.24
D22: P3.22
D23: P3.20
D24: P3.18
D25: P3.16
D26: P3.14
D27: P3.12
D28: P3.10
D29: P3.8
D30: P3.6
D31: P3.4
E: P1.4
GND: P1.49, P1.50, P2.49, P2.50, P3.49, P3.50
I2C_RX: P1.47
I2C_TX: P1.48
IC0: P2.45
IC1: P2.43
IC2: P2.41
IC3: P2.39
IPL0: P3.47
IPL1: P3.45
IPL2: P3.43
LDS: P3.38
PHI: P1.8
S0: P3.44
S1: P3.42
S2: P3.40
ST: P1.6
UDS: P3.36
USER0: P1.38
USER1: P1.36
USER2: P1.34
USER3: P1.32
USER4: P1.30
USER5: P1.28
USER6: P1.26
USER7: P1.24
USER8: P1.22
USER9: P1.20
VCC: P1.1, P1.2, P2.1, P2.2, P3.1, P3.2
VMA: P3.39
VPA: P3.37
~BAI: P1.40, P9.4
~BAO: P1.42, P9.3
~BHE: P3.41
~BUSACK: P1.13
~BUSRQ: P1.23
~DREQ0: P2.46
~DREQ1: P2.42
~EIRQ0: P1.45
~EIRQ1: P1.43
~EIRQ2: P1.41
~EIRQ3: P1.39
~EIRQ4: P1.37
~EIRQ5: P1.35
~EIRQ6: P1.33
~EIRQ7: P1.31
~HALT: P1.27
~IEI: P1.44, P9.2
~IEO: P1.46, P9.1
~INT0: P1.17
~INT1: P1.12
~INT2: P1.10
~IORQ: P1.7
~M1: P1.11
~MREQ: P1.9
~NMI: P1.19
~RD: P1.3
~RESET: P1.21
~RFSH: P1.29
~TEND0: P2.44
~TEND1: P2.40
~WAIT: P1.25
~WR: P1.5
