lynchaj/duodyne/05 input-output.Zilog, V1.1/temp/dualPIO.sch

## KiCad design 05 input-output.Zilog, V1.1/temp/dualPIO.sch (2023-03-30)

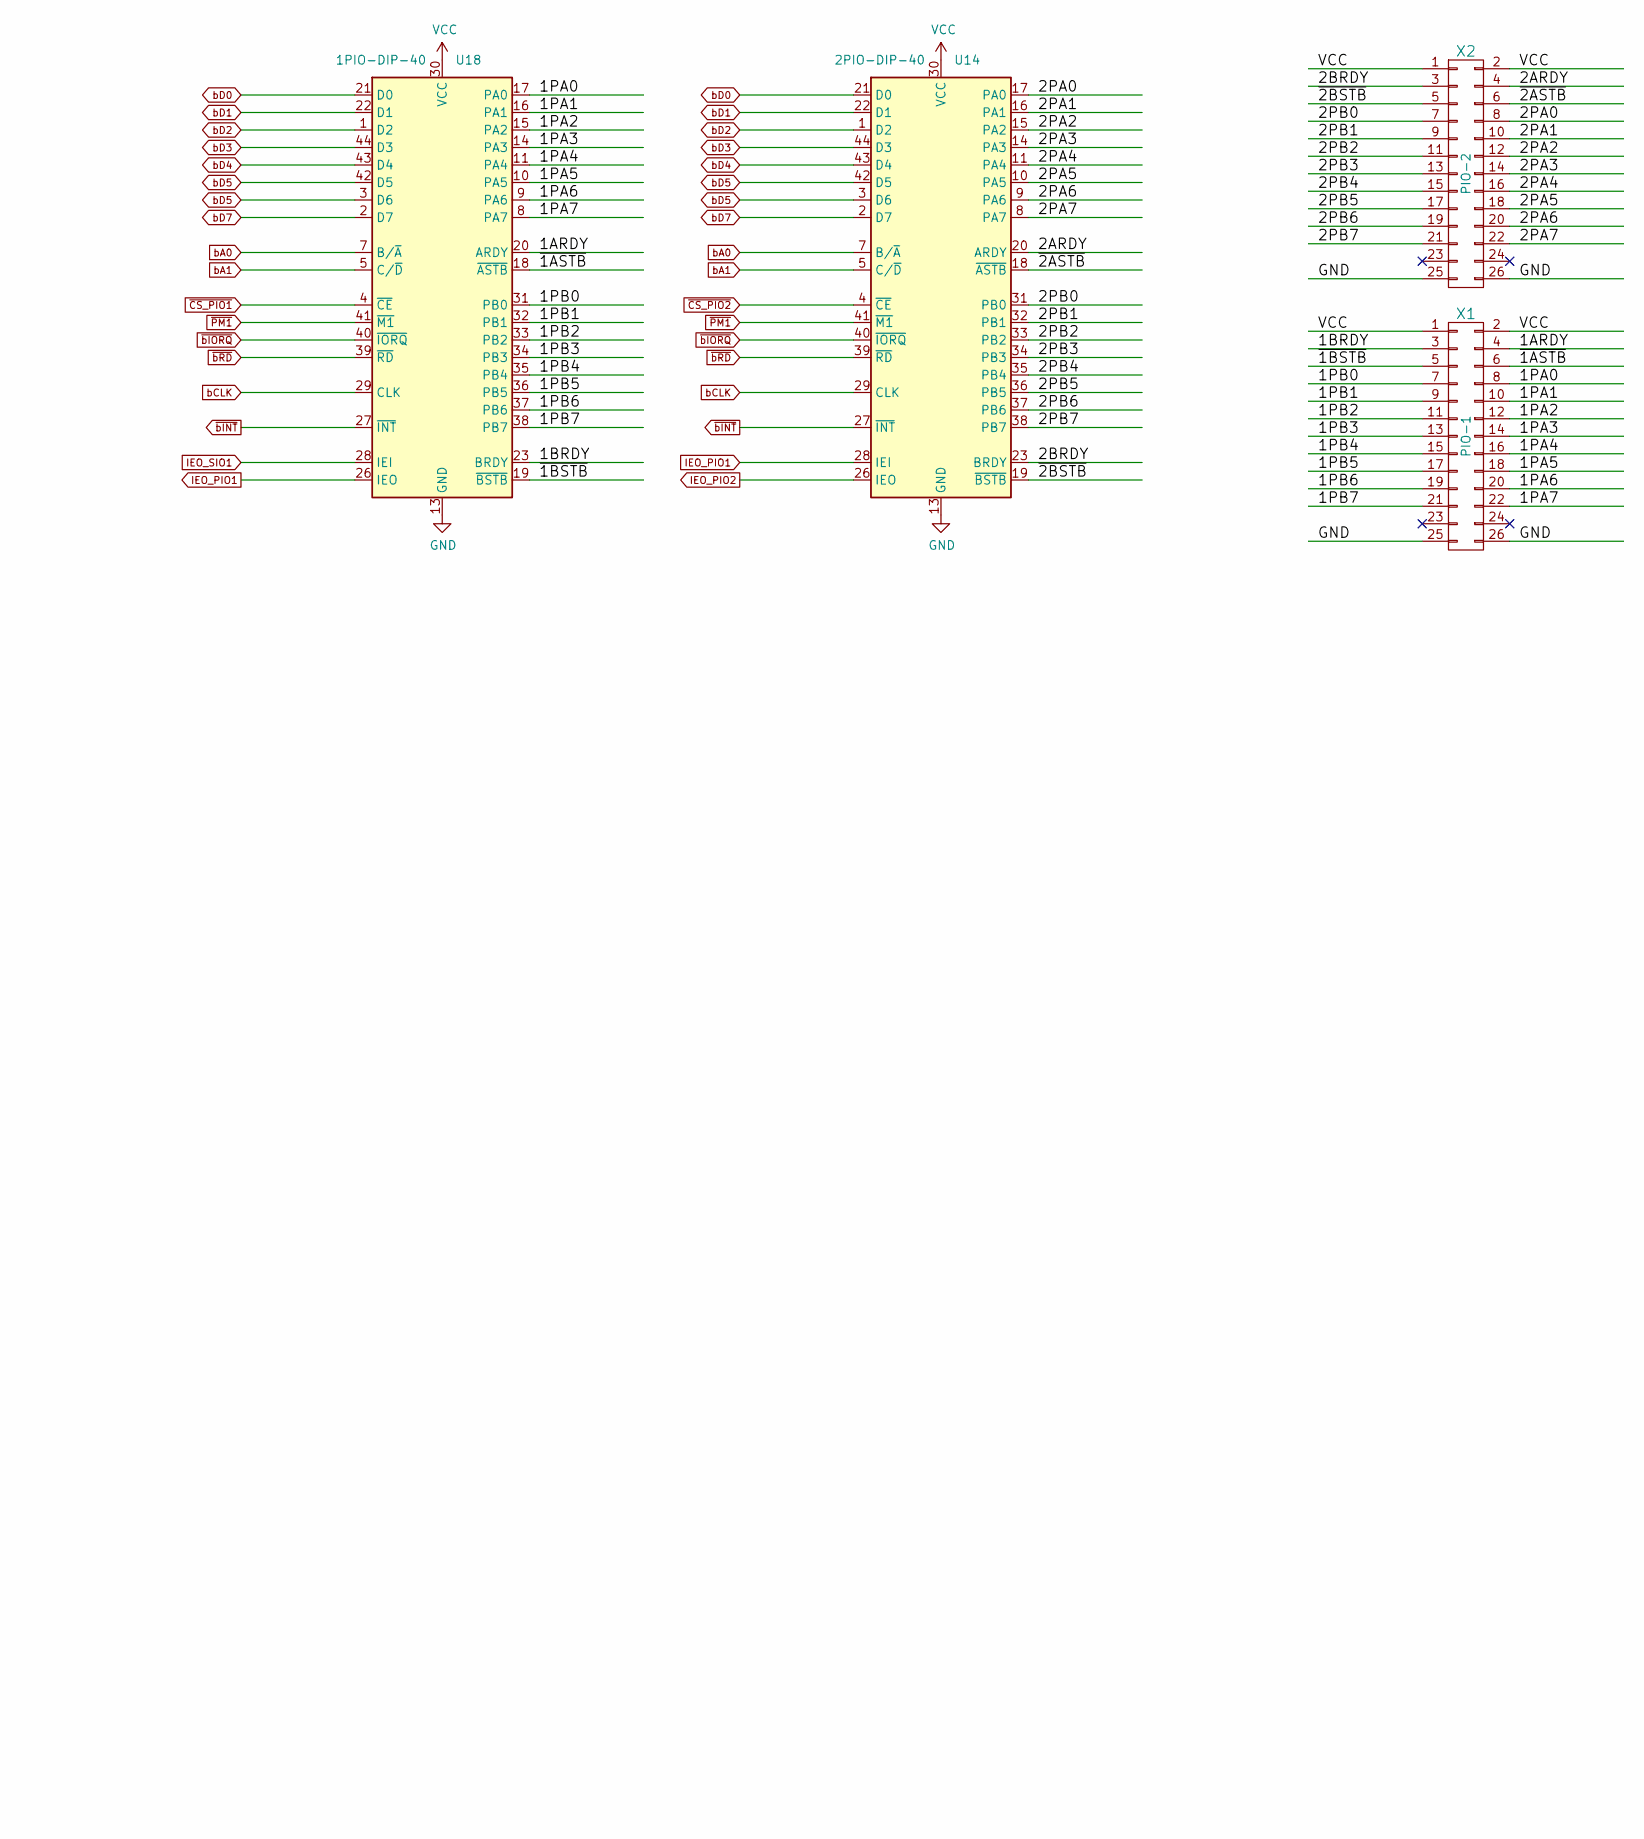
[picture p470: schematic dualPIO.sch, part in row 1, column 2]

Parts:
U14: 2PIO-DIP-40; PLCC-44_THT-Socket
U18: 1PIO-DIP-40; PLCC-44_THT-Socket
X1: PIO-1; IDC-Header_2x13_P2.54mm_Horizontal
X2: PIO-2; IDC-Header_2x13_P2.54mm_Horizontal

Connections:
1ARDY: U18.20 (ARDY), X1.4
1BRDY: U18.23 (BRDY), X1.3
1PA0: U18.17 (PA0), X1.8
1PA1: U18.16 (PA1), X1.10
1PA2: U18.15 (PA2), X1.12
1PA3: U18.14 (PA3), X1.14
1PA4: U18.11 (PA4), X1.16
1PA5: U18.10 (PA5), X1.18
1PA6: U18.9 (PA6), X1.20
1PA7: U18.8 (PA7), X1.22
1PB0: U18.31 (PB0), X1.7
1PB1: U18.32 (PB1), X1.9
1PB2: U18.33 (PB2), X1.11
1PB3: U18.34 (PB3), X1.13
1PB4: U18.35 (PB4), X1.15
1PB5: U18.36 (PB5), X1.17
1PB6: U18.37 (PB6), X1.19
1PB7: U18.38 (PB7), X1.21
2ARDY: U14.20 (ARDY), X2.4
2BRDY: U14.23 (BRDY), X2.3
2PA0: U14.17 (PA0), X2.8
2PA1: U14.16 (PA1), X2.10
2PA2: U14.15 (PA2), X2.12
2PA3: U14.14 (PA3), X2.14
2PA4: U14.11 (PA4), X2.16
2PA5: U14.10 (PA5), X2.18
2PA6: U14.9 (PA6), X2.20
2PA7: U14.8 (PA7), X2.22
2PB0: U14.31 (PB0), X2.7
2PB1: U14.32 (PB1), X2.9
2PB2: U14.33 (PB2), X2.11
2PB3: U14.34 (PB3), X2.13
2PB4: U14.35 (PB4), X2.15
2PB5: U14.36 (PB5), X2.17
2PB6: U14.37 (PB6), X2.19
2PB7: U14.38 (PB7), X2.21
GND: U14.13 (GND), U18.13 (GND), X1.25, X1.26, X2.25, X2.26
IEO_PIO1: U14.28 (IEI), U18.26 (IEO)
IEO_PIO2: U14.26 (IEO)
IEO_SIO1: U18.28 (IEI)
VCC: U14.30 (VCC), U18.30 (VCC), X1.1, X1.2, X2.1, X2.2
bA0: U14.7 (B/~A~), U18.7 (B/~A~)
bA1: U14.5 (C/~D~), U18.5 (C/~D~)
bCLK: U14.29 (CLK), U18.29 (CLK)
bD0: U14.21 (D0), U18.21 (D0)
bD1: U14.22 (D1), U18.22 (D1)
bD2: U14.1 (D2), U18.1 (D2)
bD3: U14.44 (D3), U18.44 (D3)
bD4: U14.43 (D4), U18.43 (D4)
bD5: U14.3 (D6), U14.42 (D5), U18.3 (D6), U18.42 (D5)
bD7: U14.2 (D7), U18.2 (D7)
~1ASTB: U18.18 (~ASTB~), X1.6
~1BSTB: U18.19 (~BSTB~), X1.5
~2ASTB: U14.18 (~ASTB~), X2.6
~2BSTB: U14.19 (~BSTB~), X2.5
~CS_PIO1: U18.4 (~CE~)
~CS_PIO2: U14.4 (~CE~)
~PM1: U14.41 (~M1~), U18.41 (~M1~)
~bINT: U14.27 (~INT~), U18.27 (~INT~)
~bIORQ: U14.40 (~IORQ~), U18.40 (~IORQ~)
~bRD: U14.39 (~RD~), U18.39 (~RD~)
