lynchaj/duodyne/05 input-output.Zilog, V1.1/temp/input-output.Zilog.sch

## KiCad design 05 input-output.Zilog, V1.1/temp/input-output.Zilog.sch (2023-03-30)

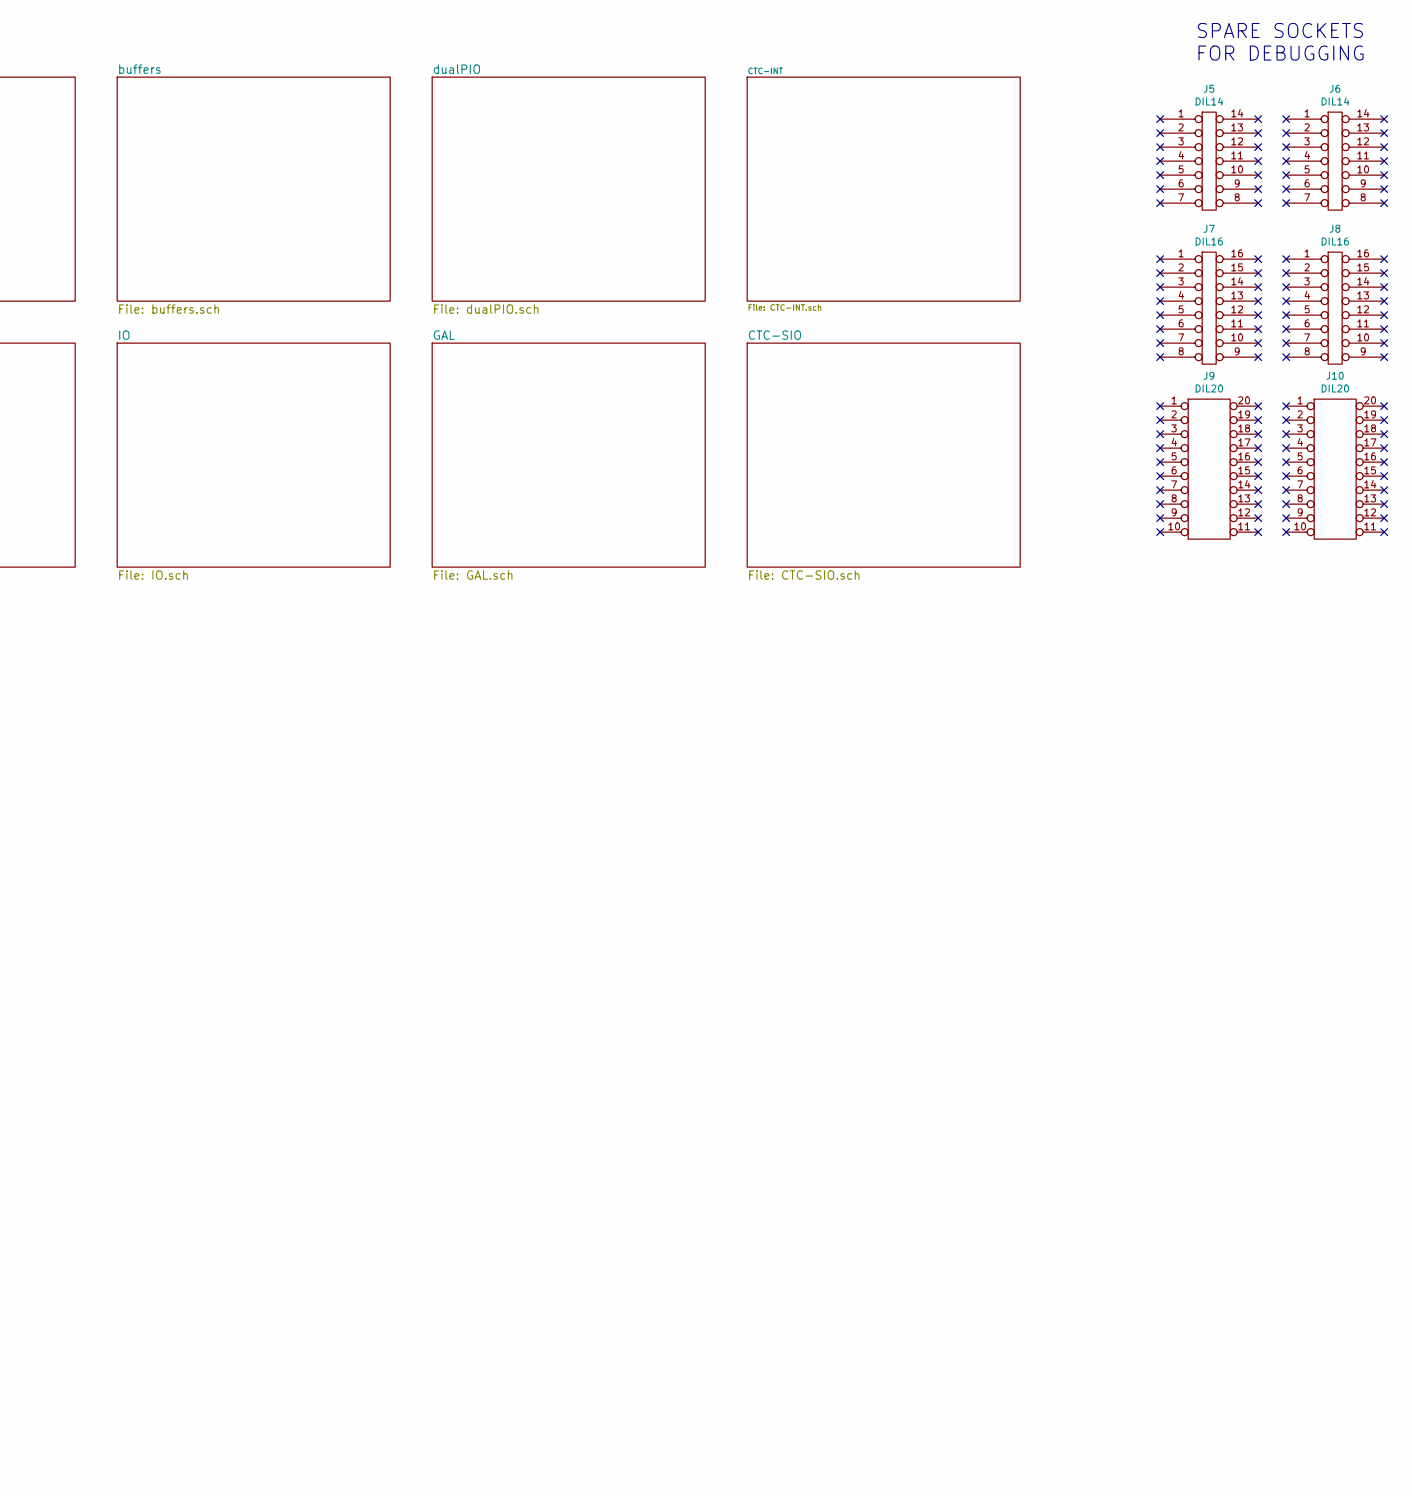
[picture p471: schematic input-output.Zilog.sch, part in row 1, column 2]

Parts:
J5, J6: DIL14; DIP-14_W7.62mm
J7, J8: DIL16; DIP-16_W7.62mm
J9, J10: DIL20; DIP-20_W7.62mm

Notes on the sheet:
SPARE SOCKETS FOR DEBUGGING
