lynchaj/duodyne/05 input-output.Zilog, V1.1/temp/input-output_zilog.discrete.logic.backup.sch

## KiCad design 05 input-output.Zilog, V1.1/temp/input-output_zilog.discrete.logic.backup.sch (2023-03-30)

Schematic: input-output_zilog.discrete.logic.backup.sch

Parts:
C1, C2, C3, C4, C5, C6, C7, C8, C9, C12, C13, C14, C15, C16, C17, C18, C19, C20, C21, C22, C23, C24, C25, C26, C28, C29: 0.1u; C_Disc_D5.0mm_W2.5mm_P5.00mm
C10, C11, C27: 10u; CP_Radial_D5.0mm_P2.50mm
D1, D3, D5: LED; LED_D3.0mm_Horizontal_O3.81mm_Z2.0mm
H1, H2: MountingHole; MountingHole_3.2mm_M3_Pad
J1: INT SEL; PinHeader_1x03_P2.54mm_Vertical
J2: 1TTLSERPWR; PinHeader_2x02_P2.54mm_Vertical
JP2: IO PORT ADDR; PinHeader_2x04_P2.54mm_Vertical
JX5: OSC_DIV; PinHeader_2x08_P2.54mm_Vertical
P1, P2, P3: CONN_02X25; IDC-Header_2x25_P2.54mm_Horizontal
P4: TIMER2; PinHeader_1x02_P2.54mm_Vertical
P5: DCDB GND; PinHeader_1x02_P2.54mm_Vertical
P10: TIMER3; PinHeader_1x02_P2.54mm_Vertical
R1, R2, R3, R4, R8: 470; R_Axial_DIN0207_L6.3mm_D2.5mm_P7.62mm_Horizontal
R5, R11: 4700; R_Axial_DIN0207_L6.3mm_D2.5mm_P7.62mm_Horizontal
R6, R7, R9, R12: 10K; R_Axial_DIN0207_L6.3mm_D2.5mm_P7.62mm_Horizontal
R10: 2200; R_Axial_DIN0207_L6.3mm_D2.5mm_P7.62mm_Horizontal
RN2: 10K; R_Array_SIP9
U1: 74LS20; DIP-14_W7.62mm
U2, U4: 74LS241; DIP-20_W7.62mm
U3: 74LS245; DIP-20_W7.62mm
U6: 74LS08; DIP-14_W7.62mm
U7: CTC-DIP-28; DIP-28_W15.24mm; Manufacturer_Part_Number Z84C3010PEG; Mouser Part Number 692-Z84C3010PEG
U8: 4.9152 MHz; DIP-14_W7.62mm
U9: SIO-DIP-40; DIP-40_W15.24mm; Manufacturer_Part_Number Z84C4206PEG; Mouser Part Number 692-Z84C4206PEG
U10, U11: MAX232; DIP-16_W7.62mm
U12: 74LS393; DIP-14_W7.62mm
U13, U20: 74LS09; DIP-14_W7.62mm
U14, U18: PIO-DIP-40; DIP-40_W15.24mm
U15: 74LS04; DIP-14_W7.62mm
U22: 74LS138; DIP-16_W7.62mm
U24: 74LS688; DIP-20_W7.62mm
X1: PIO-1; IDC-Header_2x13_P2.54mm_Horizontal
X2: PIO-2; IDC-Header_2x13_P2.54mm_Horizontal
X3: RS-232 B; IDC-Header_2x05_P2.54mm_Horizontal
X4: SIO-CTC_TTL; PinHeader_2x13_P2.54mm_Vertical
X6: BAUD_CLK; PinHeader_2x05_P2.54mm_Vertical
X7: RS-232 A; IDC-Header_2x05_P2.54mm_Horizontal
X8: 1TTL SERIAL; IDC-Header_2x06_P2.54mm_Horizontal

Notes on the sheet:
Spare Components
Z80 BUS INTERFACE
IBM PC pin assignments
IA: HIGH DURING INTERRUPT ACTIVE LOW DURING NORMAL OPERATION
X6 - SIO baud rate clock source selection
X3 - SIO channel B (RS-232 levels)
X4 - CTC, SIO channel A (TTL levels)
X5 - oscillator divider selection
X7 - SIO channel A (RS-232 levels)
NOTE: INT# AND NMI# RELY ON 4700 OHM PULL UP ON PROCESSOR
FTDI 5V SERIAL UART TO USB CABLE INTERFACE
DTECH FTDI USB to TTL Serial 5V Adapter Cable 6 Pin 0.1 inch Pitch Female Socket Header UART IC FT232RL Chip
NOTE: DEFAULT JUMPER ON PINS 11-12 TO CONNECT TXCA# AND RXCA#
NOTE: JUMPER DEFAULTS for 38400 bps with 50 Hz System Tick: - Assumes 4.9152 MHz oscillator - Jumper X5 pins 15-16 and pins 9-11 (/8) - Jumper P4 (or wire X5 pin 3 (PHI_X) to X4 pin 7 (CTC_TG2)) - Jumper P10 (or wire X4 pin 8 (CTC_ZC2) to X4 pin 9 (CTC_TG3)) - Configure the interrupt vector - Confi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
First jumper pins 15-16 of X5 to select the oscillator module. A second jumper on X5 selects the divider output for PHI_X. The /16 or /64 option is programmed into the Z80-SIO registers. BAUD PHI_X (Hz) /16 or /64 X5 Jumper 300 19200 /64 3-4 600 38400 /64 3-5 1200 19200 /16 3-4 2400 38400 /16 3-5 4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
The Z80-SIO's clock pins need to be connected to PHI_X using header X6. For the FIXED baud rate jumper pins 3-5 or 5-7 for channel A and 8-10 for channel B of header X6. For CTC baud rate to SIO clock for channel A set with pins 2-4 and channel B with pins 1-3. This assumes pins 11-12 are closed on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
X6 DEFAULT: pins 3-5 FIXED channel A pins 8-10 FIXED channel B
X5 DEFAULT: pins 15-16 4.9152 MHz pins 9-11 /8 divider
X4 DEFAULT: pins 11-12 share RX & TX clock
/32 /64 /128 /256
/2 /4 /8 /16
NOTE: USE MAX232A OR HIN232CPZ FOR RS-232 LEVEL SHIFTERS DUE TO 0.1uF STORAGE CAPS
INTERRUPT
BYPASS CAPACITORS
NOTE: DEFAULT JUMPER ON P4
NOTE: DEFAULT JUMPER ON P10
VCC PIN 24
GND PIN 5
VCC PIN 9
GND PIN 31
NOTE: DEFAULT JUMPER ON P5
VCC PIN 26
GND PIN 11
Note: IO Address Port $B0-BF 1-2 =off - A7 (high) 3-4 =on - A6 (low) 5-6 =off - A5 (high) 7-8 =off - A4 (high)
IO ADDRESS SELECT CIRCUIT
SET IO ADDRESS
Interrupt filter circuit
IO CHIP SELECT CS1
