lynchaj/duodyne/05 input-output.Zilog, V1.1/temp/power.sch

## KiCad design 05 input-output.Zilog, V1.1/temp/power.sch (2023-03-30)

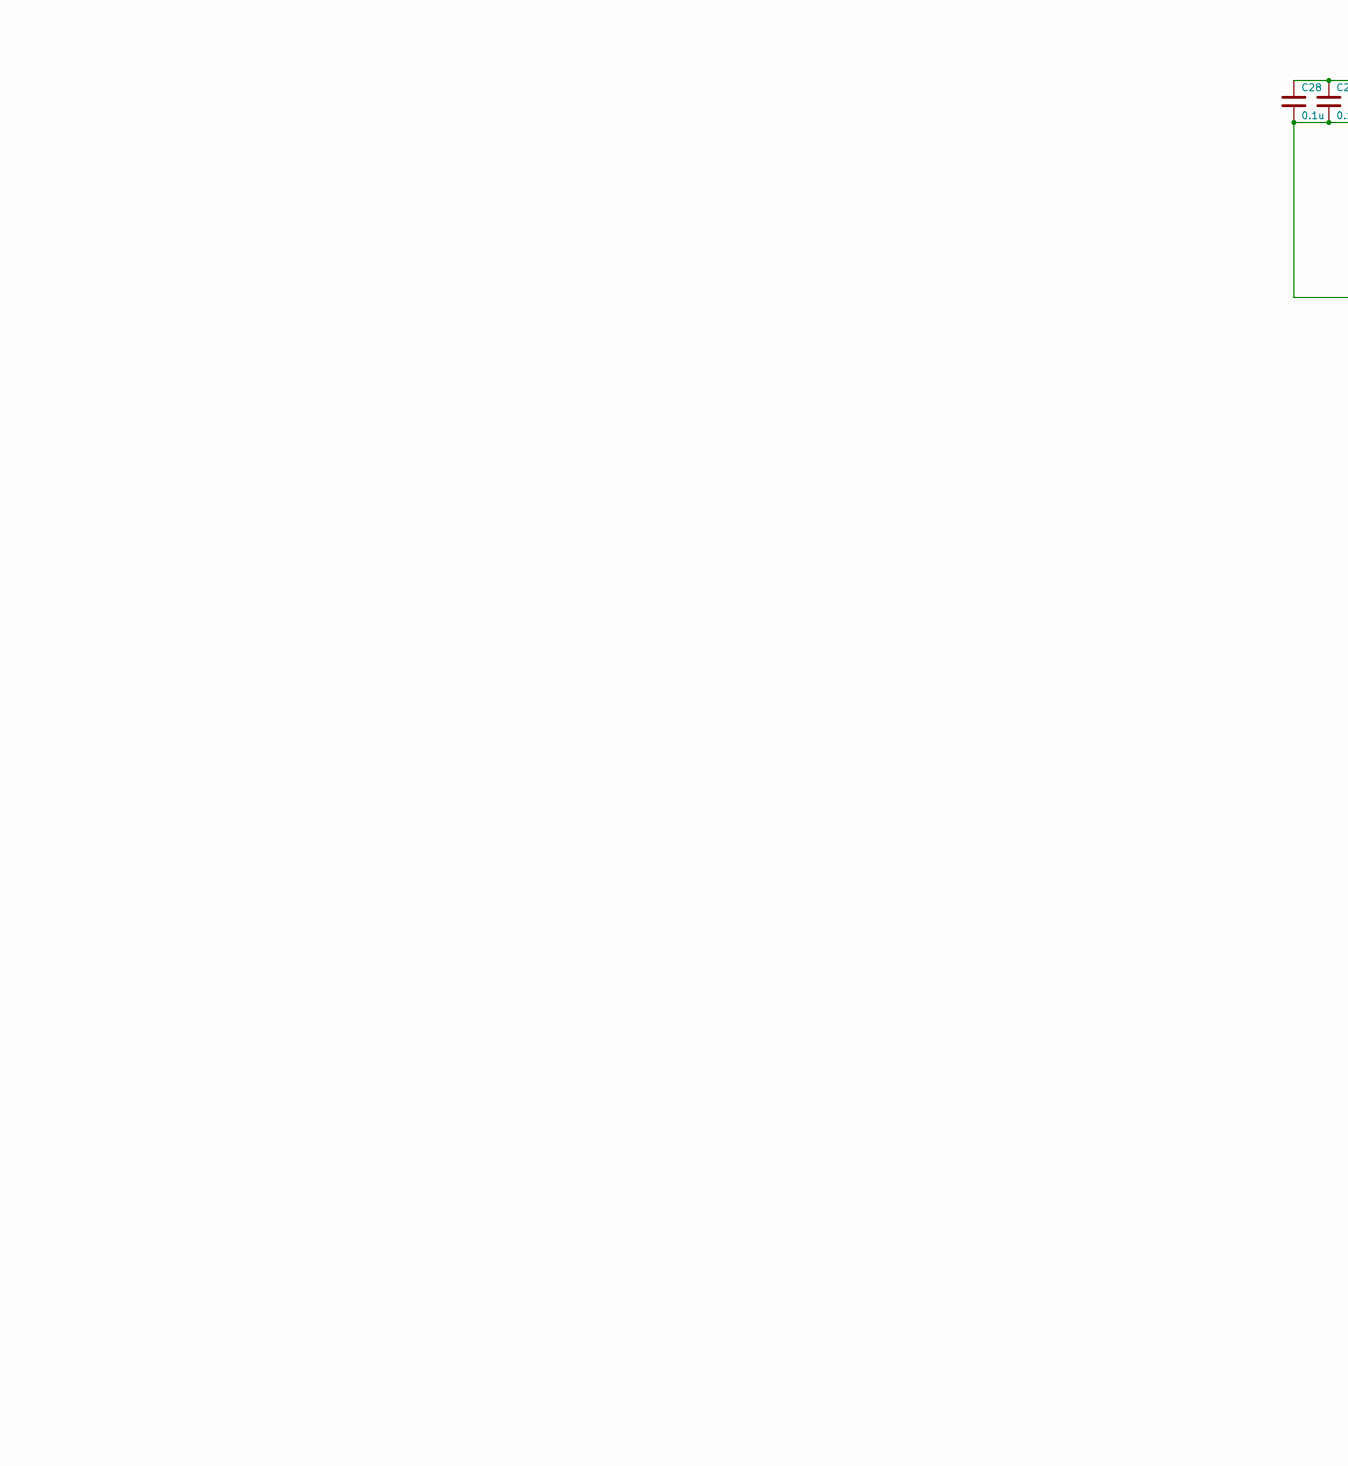
[picture p472: schematic power.sch, part in row 1, column 1]

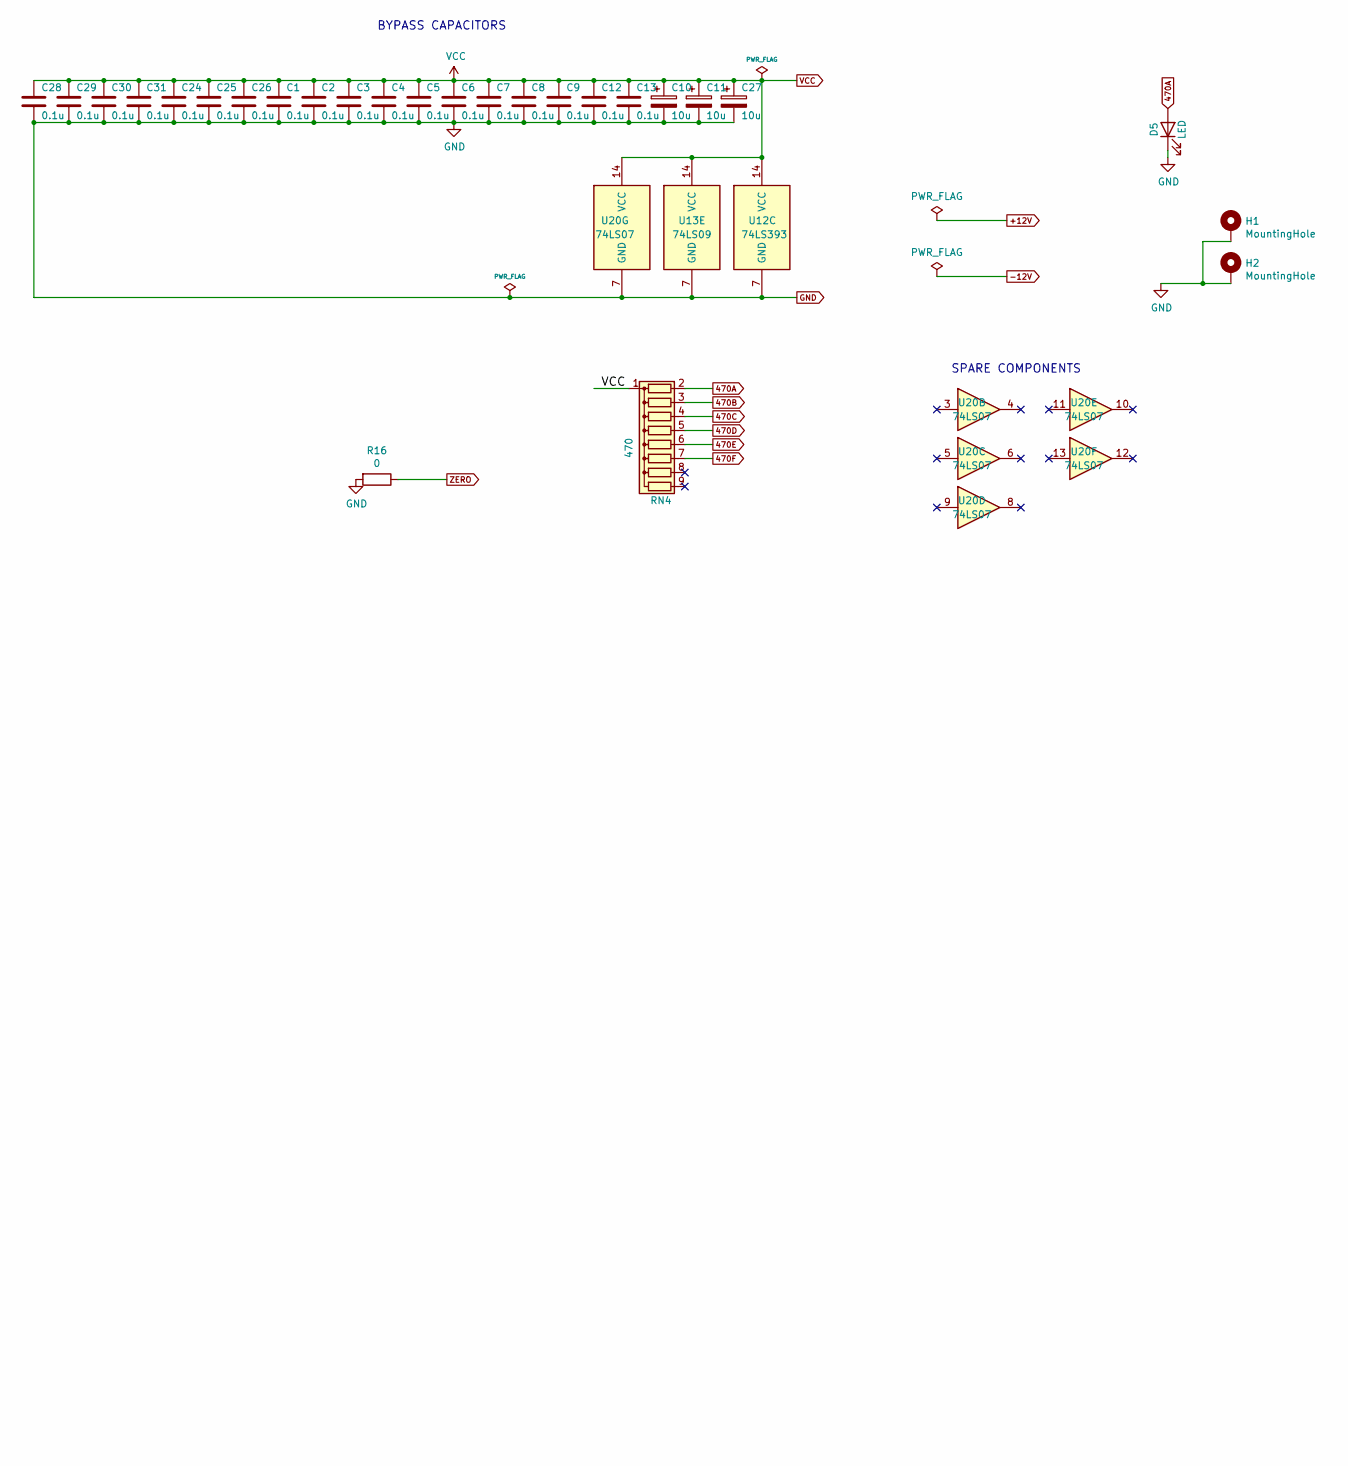
[picture p473: schematic power.sch, part in row 1, column 2]

Parts:
C1, C2, C3, C4, C5, C6, C7, C8, C9, C12, C13, C24, C25, C26, C28, C29, C30, C31: 0.1u; C_Disc_D5.0mm_W2.5mm_P5.00mm
C10, C11, C27: 10u; CP_Radial_D5.0mm_P2.50mm
D5: LED; LED_D3.0mm_Horizontal_O3.81mm_Z2.0mm
H1, H2: MountingHole; MountingHole_3.2mm_M3_Pad
R16: 0; R_Axial_DIN0207_L6.3mm_D2.5mm_P7.62mm_Horizontal
RN4: 470; R_Array_SIP9
U12: 74LS393; DIP-14_W7.62mm
U13: 74LS09; DIP-14_W7.62mm
U20: 74LS07; DIP-14_W7.62mm

Connections:
470A: D5.2 (A), RN4.2 (R1)
470B: RN4.3 (R2)
470C: RN4.4 (R3)
470D: RN4.5 (R4)
470E: RN4.6 (R5)
470F: RN4.7 (R6)
GND: C1.2, C2.2, C3.2, C4.2, C5.2, C6.2, C7.2, C8.2, C9.2, C10.2, C11.2, C12.2, C13.2, C24.2, C25.2, C26.2, C27.2, C28.2, C29.2, C30.2, C31.2, D5.1 (K), H1.1, H2.1, R16.2, U12.7 (GND), U13.7 (GND), U20.7 (GND)
VCC: C1.1, C2.1, C3.1, C4.1, C5.1, C6.1, C7.1, C8.1, C9.1, C10.1, C11.1, C12.1, C13.1, C24.1, C25.1, C26.1, C27.1, C28.1, C29.1, C30.1, C31.1, RN4.1 (common), U12.14 (VCC), U13.14 (VCC), U20.14 (VCC)
ZERO: R16.1

Notes on the sheet:
BYPASS CAPACITORS
SPARE COMPONENTS
