lynchaj/duodyne/08 input-output.Disk, V1.0/temp/DUART.sch

## KiCad design 08 input-output.Disk, V1.0/temp/DUART.sch (2023-03-30)

Schematic: DUART.sch

Parts:
C1: 10u; CP_Radial_D5.0mm_P2.50mm
C2, C3, C4, C5, C6, C7, C8, C9, C10, C11: 0.1u; C_Disc_D5.0mm_W2.5mm_P5.00mm
D1: 1N4148; D_DO-35_SOD27_P7.62mm_Horizontal
D3, D4, D5: LED; LED_D3.0mm
J1, J13: INTERRUPT; PinHeader_2x09_P2.54mm_Vertical
J3: TTL PWRB; PinHeader_1x02_P2.54mm_Vertical
J4: TTL PWRA; PinHeader_1x02_P2.54mm_Vertical
J6: TTL SERIAL; IDC-Header_2x06_P2.54mm_Horizontal
JP1: EXT RECOVERY; PinHeader_1x02_P2.54mm_Vertical
P4: RS-232 A; IDC-Header_2x05_P2.54mm_Horizontal
P5: RS-232 B; IDC-Header_2x05_P2.54mm_Horizontal
R1: 10K; R_Axial_DIN0207_L6.3mm_D2.5mm_P7.62mm_Horizontal
R2: 10; R_Axial_DIN0207_L6.3mm_D2.5mm_P7.62mm_Horizontal
R5, R8, R13, R14, R15: 470; R_Axial_DIN0207_L6.3mm_D2.5mm_P7.62mm_Horizontal
R6: 0; R_Axial_DIN0207_L6.3mm_D2.5mm_P7.62mm_Horizontal
R9, R12: 1000; R_Axial_DIN0207_L6.3mm_D2.5mm_P7.62mm_Horizontal
RN5: 10K; R_Array_SIP9
SW1: RECOVERY; SW_Tactile_SPST_Angled_PTS645Vx58-2LFS
SW2: IO PORT ADDR; PinHeader_2x04_P2.54mm_Vertical
U1: 74LS06; DIP-14_W7.62mm
U2: 74LS688; DIP-20_W7.62mm
U4: TL16C2552FN; PLCC-44_THT-Socket
U6: DUART CLK; DIP-14_W7.62mm
U8, U9: MAX232; DIP-16_W7.62mm
U10: 74LS08; DIP-14_W7.62mm
U16: 74LS04; DIP-14_W7.62mm

Notes on the sheet:
SW2 Note: IO Address Port $80-$8F 1-2 =off - A7 (high) 3-4 =on - A6 (low) 5-6 =on - A5 (low) 7-8 =on - A4 (low)
Note: Inhibit Board Operation During Interrupts ~M1~ = low, ~IORQ~ = low
IO SELECTION CIRCUIT
SET IO PORT
FTDI 5V SERIAL UART TO USB CABLE INTERFACE
7.3728 MHz Crystal Oscillator
DTECH FTDI USB to TTL Serial 5V Adapter Cable 6 Pin 0.1 inch Pitch Female Socket Header UART IC FT232RL Chip
StarTech.com 16in 9 Pin Serial Male to 10 Pin Motherboard Header Panel Mount Cable - motherboard to RS232 (PNL9M16),Gray
NOTE: INSTALL ONLY ONE 9 PIN SERIAL OR TTL SERIAL USB CABLE
NOTE: ~INT~ RELIES ON 4700 OHM PULL UP RESISTOR ON PROCESSOR
TRANSMIT LED
RECEIVE LED
INTERRUPT LED
IBM PC pin assignments
X3 - SIO channel B (RS-232 levels)
X7 - SIO channel A (RS-232 levels)
NOTE: USE MAX232A OR HIN232CPZ FOR RS-232 LEVEL SHIFTERS DUE TO 0.1uF STORAGE CAPS
