lynchaj/duodyne/08 input-output.Disk, V1.0/temp/FDC.sch

## KiCad design 08 input-output.Disk, V1.0/temp/FDC.sch (2023-03-30)

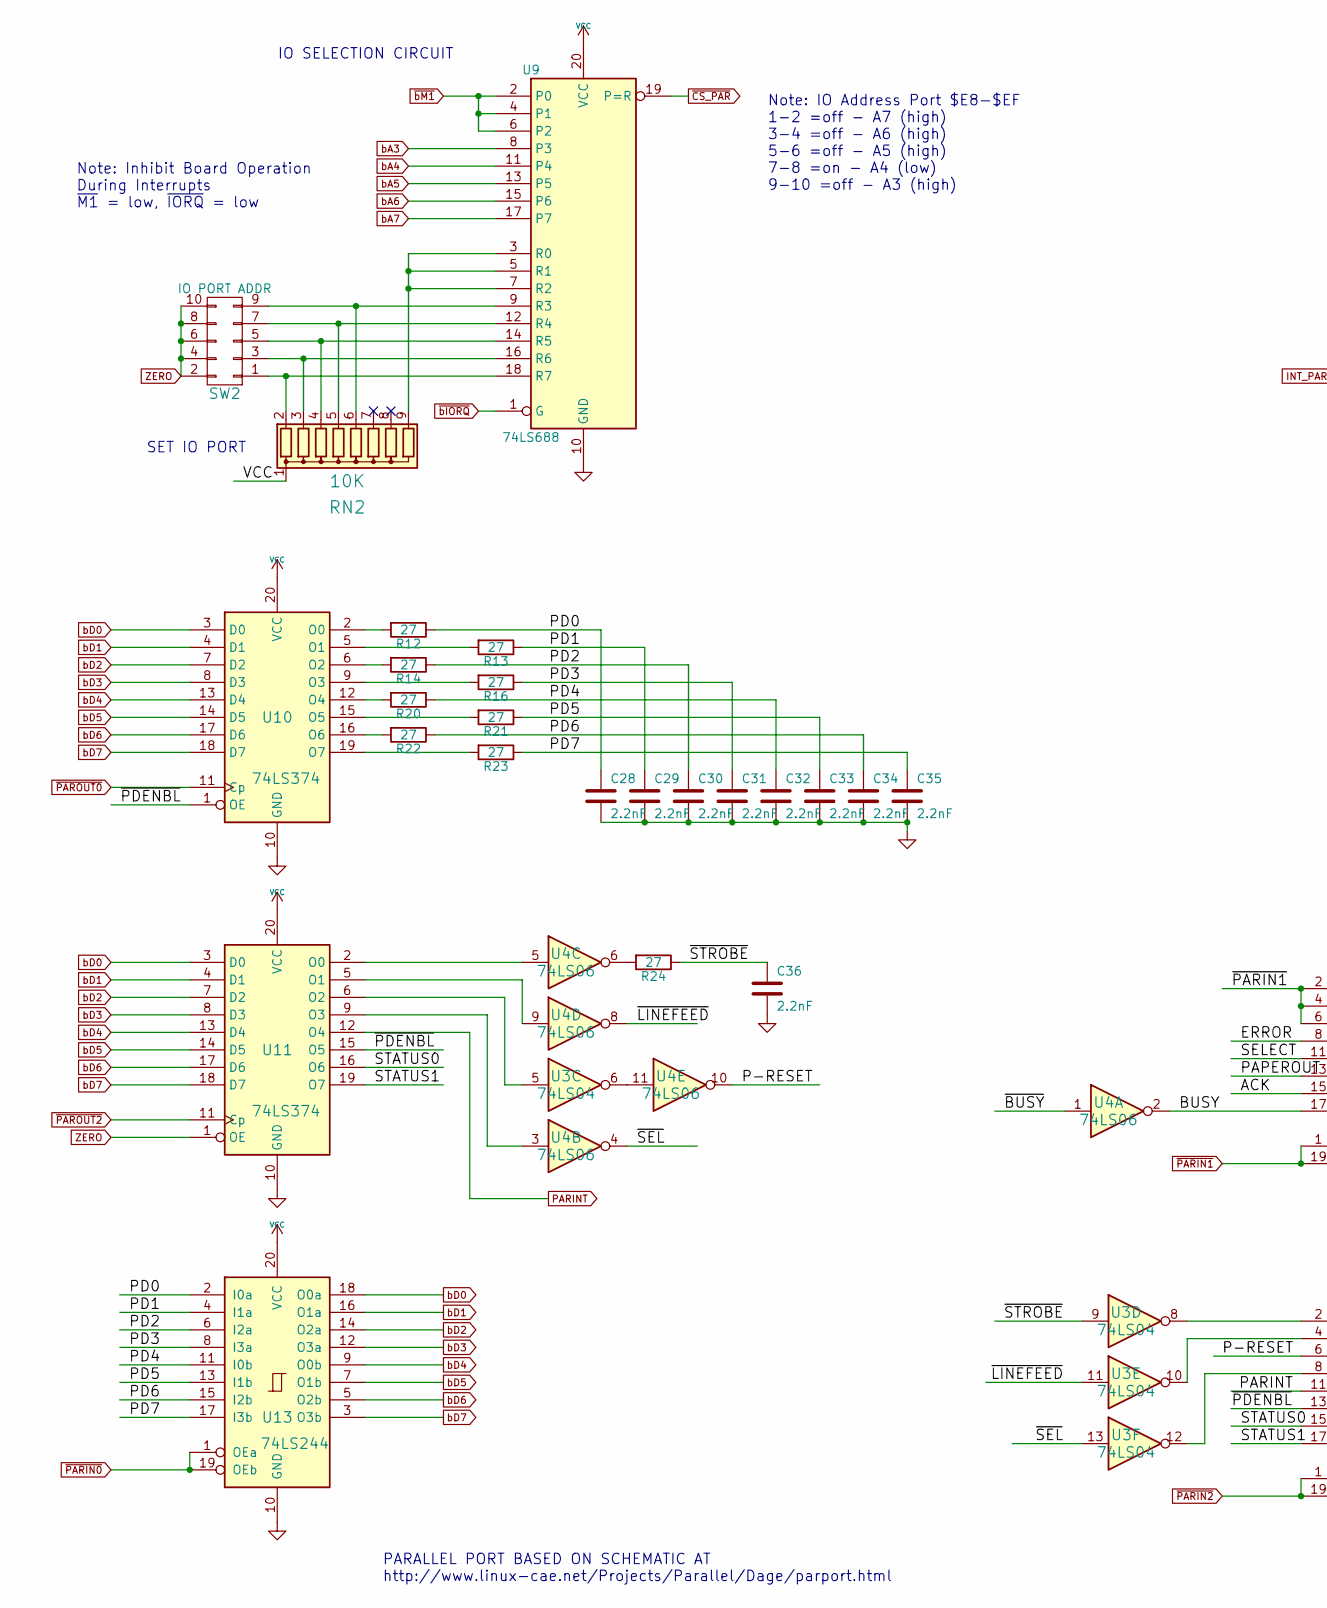
[picture p474: schematic FDC.sch, part in row 1, column 1]

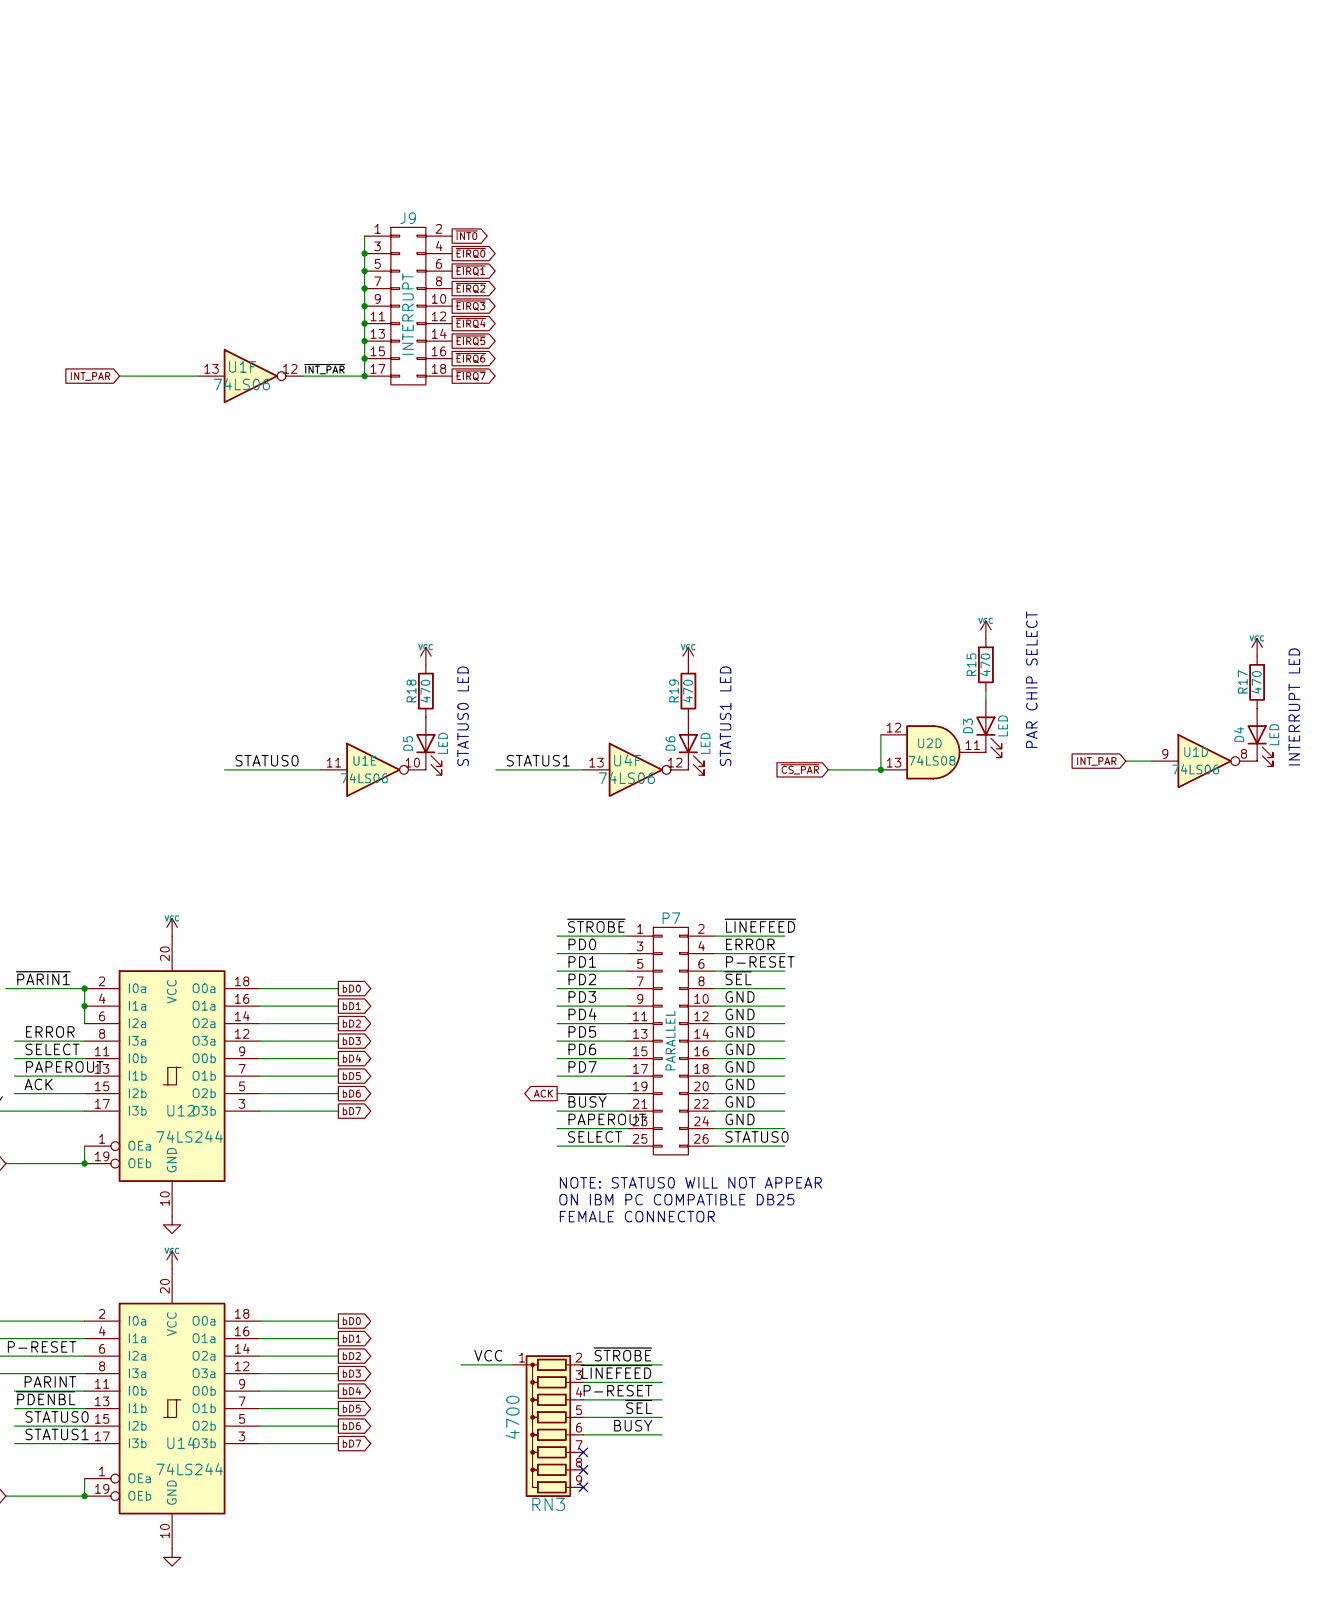
[picture p475: schematic FDC.sch, part in row 1, column 2]

Parts:
C28, C29, C30, C31, C32, C33, C34, C35, C36: 2.2nF; C_Disc_D5.0mm_W2.5mm_P5.00mm
D3: LED; LED_D3.0mm_Horizontal_O3.81mm_Z2.0mm
D4, D5, D6: LED; LED_D3.0mm
J9: INTERRUPT; PinHeader_2x09_P2.54mm_Vertical
P7: PARALLEL; IDC-Header_2x13_P2.54mm_Horizontal
R12, R13, R14, R16, R20, R21, R22, R23, R24: 27; R_Axial_DIN0207_L6.3mm_D2.5mm_P7.62mm_Horizontal
R15, R17, R18, R19: 470; R_Axial_DIN0207_L6.3mm_D2.5mm_P7.62mm_Horizontal
RN2: 10K; R_Array_SIP9
RN3: 4700; R_Array_SIP9
SW2: IO PORT ADDR; PinHeader_2x05_P2.54mm_Vertical
U1, U4: 74LS06; DIP-14_W7.62mm
U2: 74LS08; DIP-14_W7.62mm
U3: 74LS04; DIP-14_W7.62mm
U9: 74LS688; DIP-20_W7.62mm
U10, U11: 74LS374; DIP-20_W7.62mm
U12, U13, U14: 74LS244; DIP-20_W7.62mm

Connections:
ACK: P7.19, U12.15 (I2b)
BUSY: RN3.6 (R5), U4.2, U12.17 (I3b)
ERROR: P7.4, U12.8 (I3a)
GND: C28.2, C29.2, C30.2, C31.2, C32.2, C33.2, C34.2, C35.2, C36.2, P7.10, P7.12, P7.14, P7.16, P7.18, P7.20, P7.22, P7.24, U9.10 (GND), U10.10 (GND), U11.10 (GND), U12.10 (GND), U13.10 (GND), U14.10 (GND)
INT_PAR: U1.9, U1.13
unnamed: D3.1 (K), U2.11
unnamed: D3.2 (A), R15.1
unnamed: D4.1 (K), U1.8
unnamed: D4.2 (A), R17.1
unnamed: D5.1 (K), U1.10
unnamed: D5.2 (A), R18.1
unnamed: D6.1 (K), U4.12
unnamed: D6.2 (A), R19.1
unnamed: R12.2, U10.2 (O0)
unnamed: R13.2, U10.5 (O1)
unnamed: R14.2, U10.6 (O2)
unnamed: R16.2, U10.9 (O3)
unnamed: R20.2, U10.12 (O4)
unnamed: R21.2, U10.15 (O5)
unnamed: R22.2, U10.16 (O6)
unnamed: R23.2, U10.19 (O7)
unnamed: R24.2, U4.6
unnamed: RN2.2 (R1), SW2.1, U9.18 (R7)
unnamed: RN2.3 (R2), SW2.3, U9.16 (R6)
unnamed: RN2.4 (R3), SW2.5, U9.14 (R5)
unnamed: RN2.5 (R4), SW2.7, U9.12 (R4)
unnamed: RN2.6 (R5), SW2.9, U9.9 (R3)
unnamed: RN2.9 (R8), U9.3 (R0), U9.5 (R1), U9.7 (R2)
unnamed: U3.6, U4.11
unnamed: U4.5, U11.2 (O0)
unnamed: U4.9, U11.5 (O1)
unnamed: U3.5, U11.6 (O2)
unnamed: U4.3, U11.9 (O3)
unnamed: U3.8, U14.2 (I0a)
unnamed: U3.10, U14.4 (I1a)
unnamed: U3.12, U14.8 (I3a)
P-RESET: P7.6, RN3.4 (R3), U4.10, U14.6 (I2a)
PAPEROUT: P7.23, U12.13 (I1b)
PARINT: U11.12 (O4), U14.11 (I0b)
PD0: C28.1, P7.3, R12.1, U13.2 (I0a)
PD1: C29.1, P7.5, R13.1, U13.4 (I1a)
PD2: C30.1, P7.7, R14.1, U13.6 (I2a)
PD3: C31.1, P7.9, R16.1, U13.8 (I3a)
PD4: C32.1, P7.11, R20.1, U13.11 (I0b)
PD5: C33.1, P7.13, R21.1, U13.13 (I1b)
PD6: C34.1, P7.15, R22.1, U13.15 (I2b)
PD7: C35.1, P7.17, R23.1, U13.17 (I3b)
SELECT: P7.25, U12.11 (I0b)
STATUS0: P7.26, U1.11, U11.16 (O6), U14.15 (I2b)
STATUS1: U4.13, U11.19 (O7), U14.17 (I3b)
VCC: R15.2, R17.2, R18.2, R19.2, RN2.1 (common), RN3.1 (common), U9.20 (VCC), U10.20 (VCC), U11.20 (VCC), U12.20 (VCC), U13.20 (VCC), U14.20 (VCC)
ZERO: SW2.2, SW2.4, SW2.6, SW2.8, SW2.10, U11.1 (OE)
bA3: U9.8 (P3)
bA4: U9.11 (P4)
bA5: U9.13 (P5)
bA6: U9.15 (P6)
bA7: U9.17 (P7)
bD0: U10.3 (D0), U11.3 (D0), U12.18 (O0a), U13.18 (O0a), U14.18 (O0a)
bD1: U10.4 (D1), U11.4 (D1), U12.16 (O1a), U13.16 (O1a), U14.16 (O1a)
bD2: U10.7 (D2), U11.7 (D2), U12.14 (O2a), U13.14 (O2a), U14.14 (O2a)
bD3: U10.8 (D3), U11.8 (D3), U12.12 (O3a), U13.12 (O3a), U14.12 (O3a)
bD4: U10.13 (D4), U11.13 (D4), U12.9 (O0b), U13.9 (O0b), U14.9 (O0b)
bD5: U10.14 (D5), U11.14 (D5), U12.7 (O1b), U13.7 (O1b), U14.7 (O1b)
bD6: U10.17 (D6), U11.17 (D6), U12.5 (O2b), U13.5 (O2b), U14.5 (O2b)
bD7: U10.18 (D7), U11.18 (D7), U12.3 (O3b), U13.3 (O3b), U14.3 (O3b)
~BUSY: P7.21, U4.1
~CS_PAR: U2.12, U2.13, U9.19 (P=R)
~EIRQ0: J9.4
~EIRQ1: J9.6
~EIRQ2: J9.8
~EIRQ3: J9.10
~EIRQ4: J9.12
~EIRQ5: J9.14
~EIRQ6: J9.16
~EIRQ7: J9.18
~INT0: J9.2
~INT_PAR: J9.1, J9.3, J9.5, J9.7, J9.9, J9.11, J9.13, J9.15, J9.17, U1.12
~LINEFEED: P7.2, RN3.3 (R2), U3.11, U4.8
~PARIN0: U13.1 (OEa), U13.19 (OEb)
~PARIN1: U12.1 (OEa), U12.2 (I0a), U12.4 (I1a), U12.6 (I2a), U12.19 (OEb)
~PARIN2: U14.1 (OEa), U14.19 (OEb)
~PAROUT0: U10.11 (Cp)
~PAROUT2: U11.11 (Cp)
~PDENBL: U10.1 (OE), U11.15 (O5), U14.13 (I1b)
~SEL: P7.8, RN3.5 (R4), U3.13, U4.4
~STROBE: C36.1, P7.1, R24.1, RN3.2 (R1), U3.9
~bIORQ: U9.1 (G)
~bM1: U9.2 (P0), U9.4 (P1), U9.6 (P2)

Notes on the sheet:
IO SELECTION CIRCUIT
SET IO PORT
PAR CHIP SELECT
Note: Inhibit Board Operation During Interrupts ~M1~ = low, ~IORQ~ = low
Note: IO Address Port $E8-$EF 1-2 =off - A7 (high) 3-4 =off - A6 (high) 5-6 =off - A5 (high) 7-8 =on - A4 (low) 9-10 =off - A3 (high)
PARALLEL PORT BASED ON SCHEMATIC AT http://www.linux-cae.net/Projects/Parallel/Dage/parport.html
INTERRUPT LED
STATUS0 LED
STATUS1 LED
NOTE: STATUS0 WILL NOT APPEAR ON IBM PC COMPATIBLE DB25 FEMALE CONNECTOR
