lynchaj/duodyne/08 input-output.Disk, V1.0/temp/GAL.sch

## KiCad design 08 input-output.Disk, V1.0/temp/GAL.sch (2023-03-30)

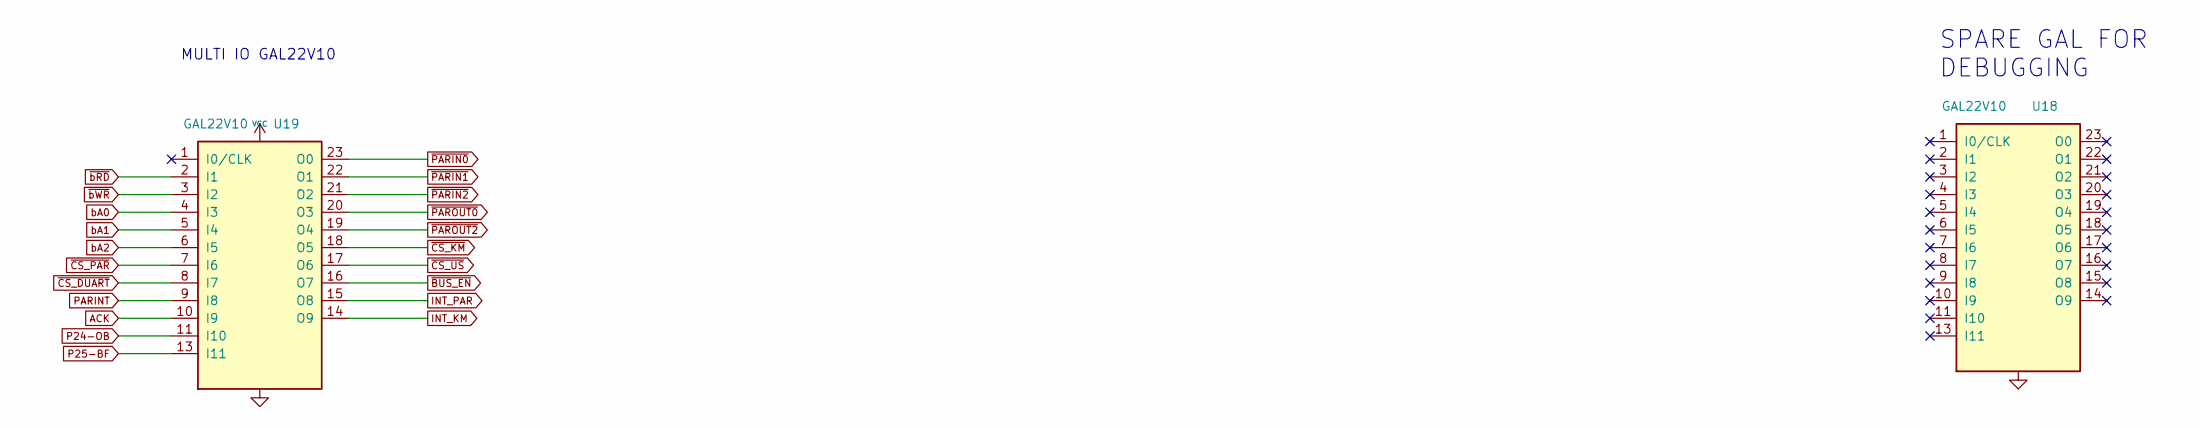
[picture p476: schematic GAL.sch]

Parts:
U18, U19: GAL22V10; DIP-24_W7.62mm

Connections:
ACK: U19.10 (I9)
GND: U18.12 (GND), U19.12 (GND)
INT_KM: U19.14 (O9)
INT_PAR: U19.15 (O8)
P24-OB: U19.11 (I10)
P25-BF: U19.13 (I11)
PARINT: U19.9 (I8)
VCC: U19.24 (VCC)
bA0: U19.4 (I3)
bA1: U19.5 (I4)
bA2: U19.6 (I5)
~BUS_EN: U19.16 (O7)
~CS_DUART: U19.8 (I7)
~CS_KM: U19.18 (O5)
~CS_PAR: U19.7 (I6)
~CS_US: U19.17 (O6)
~PARIN0: U19.23 (O0)
~PARIN1: U19.22 (O1)
~PARIN2: U19.21 (O2)
~PAROUT0: U19.20 (O3)
~PAROUT2: U19.19 (O4)
~bRD: U19.2 (I1)
~bWR: U19.3 (I2)

Notes on the sheet:
SPARE GAL FOR DEBUGGING
MULTI IO GAL22V10
