lynchaj/duodyne/08 input-output.Disk, V1.0/temp/PPIDE.sch

## KiCad design 08 input-output.Disk, V1.0/temp/PPIDE.sch (2023-03-30)

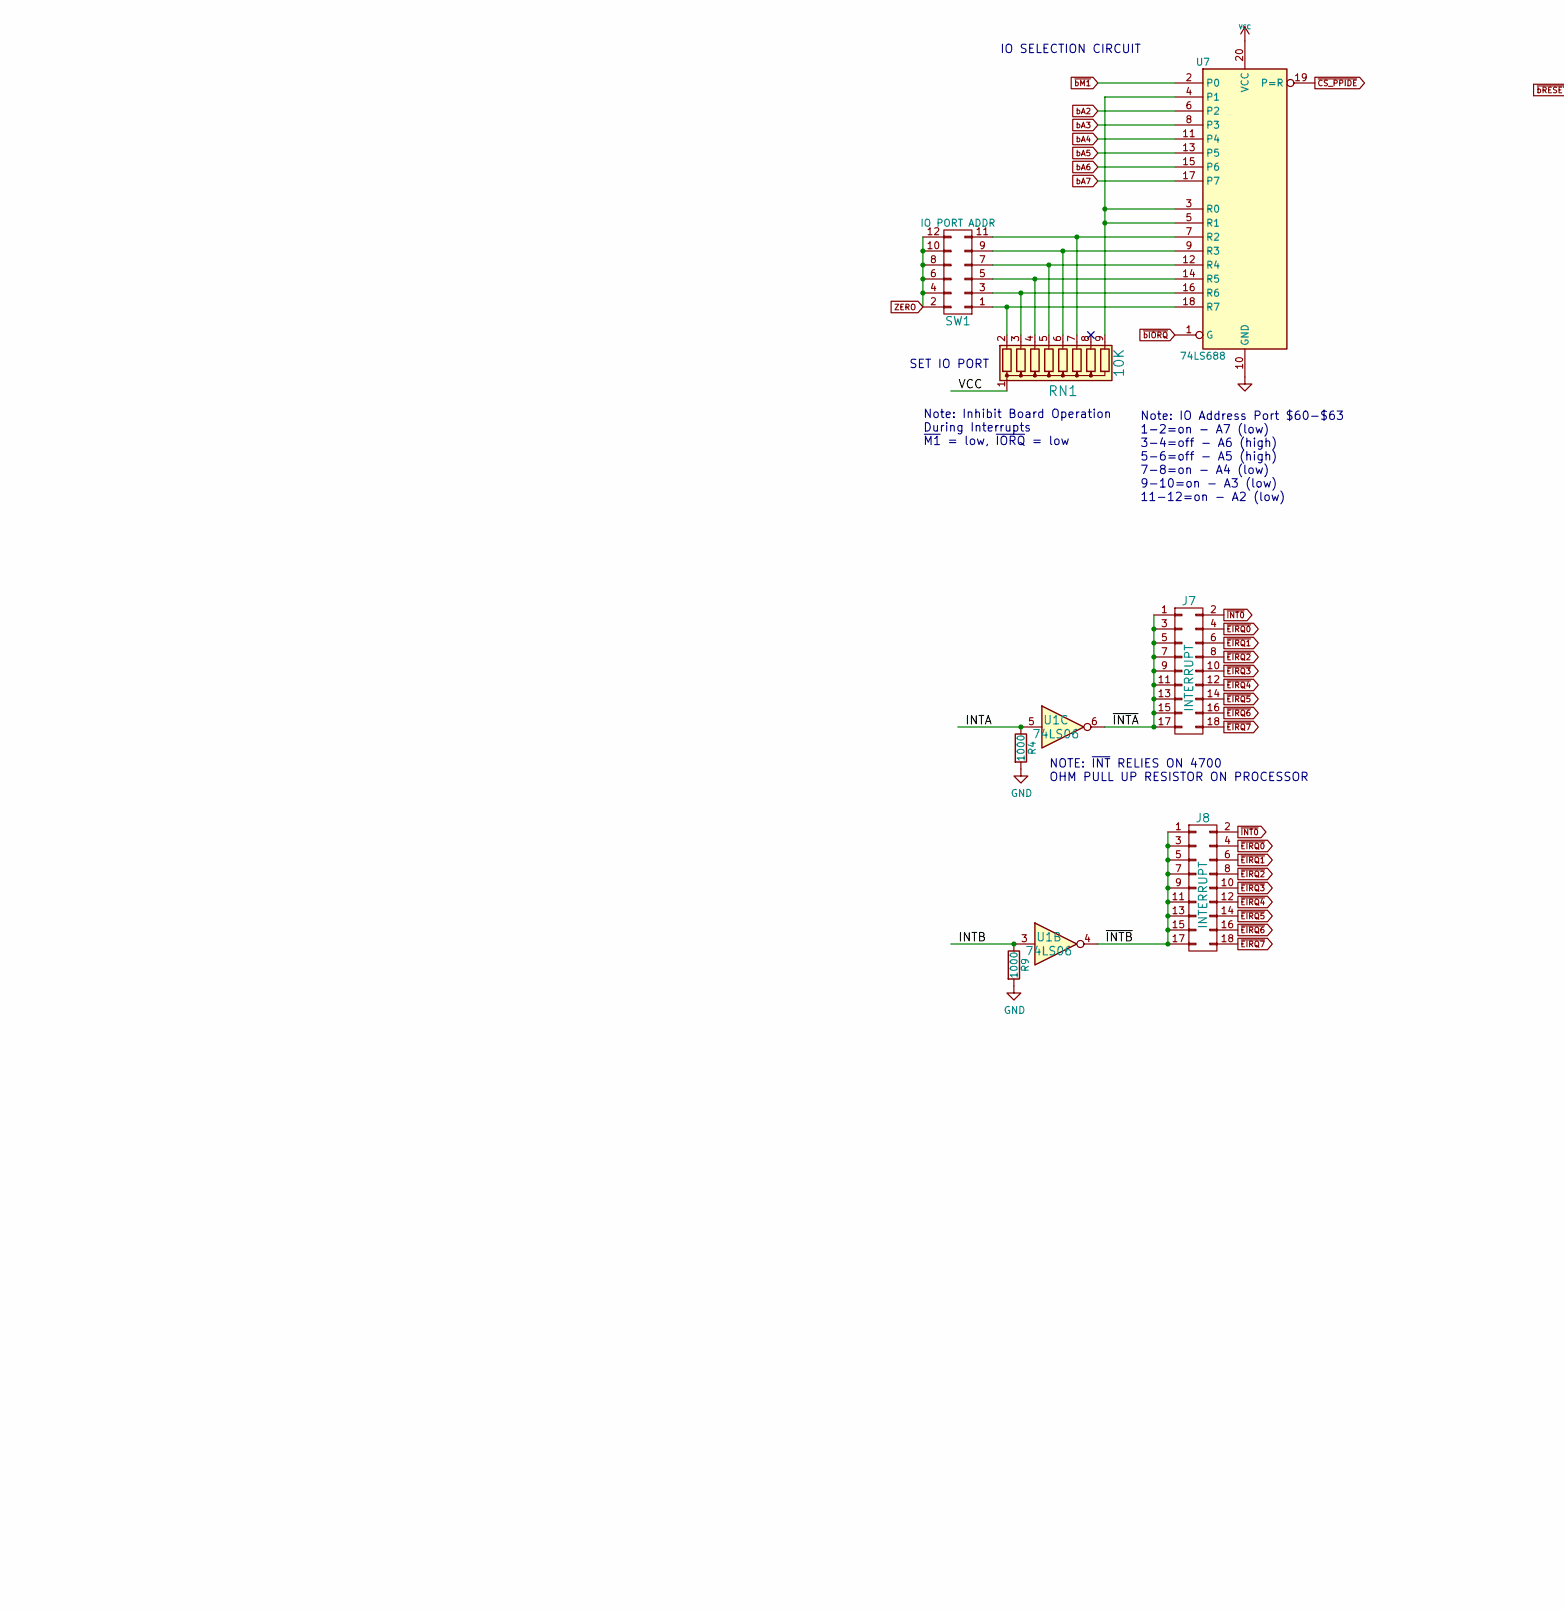
[picture p477: schematic PPIDE.sch, part in row 1, column 1]

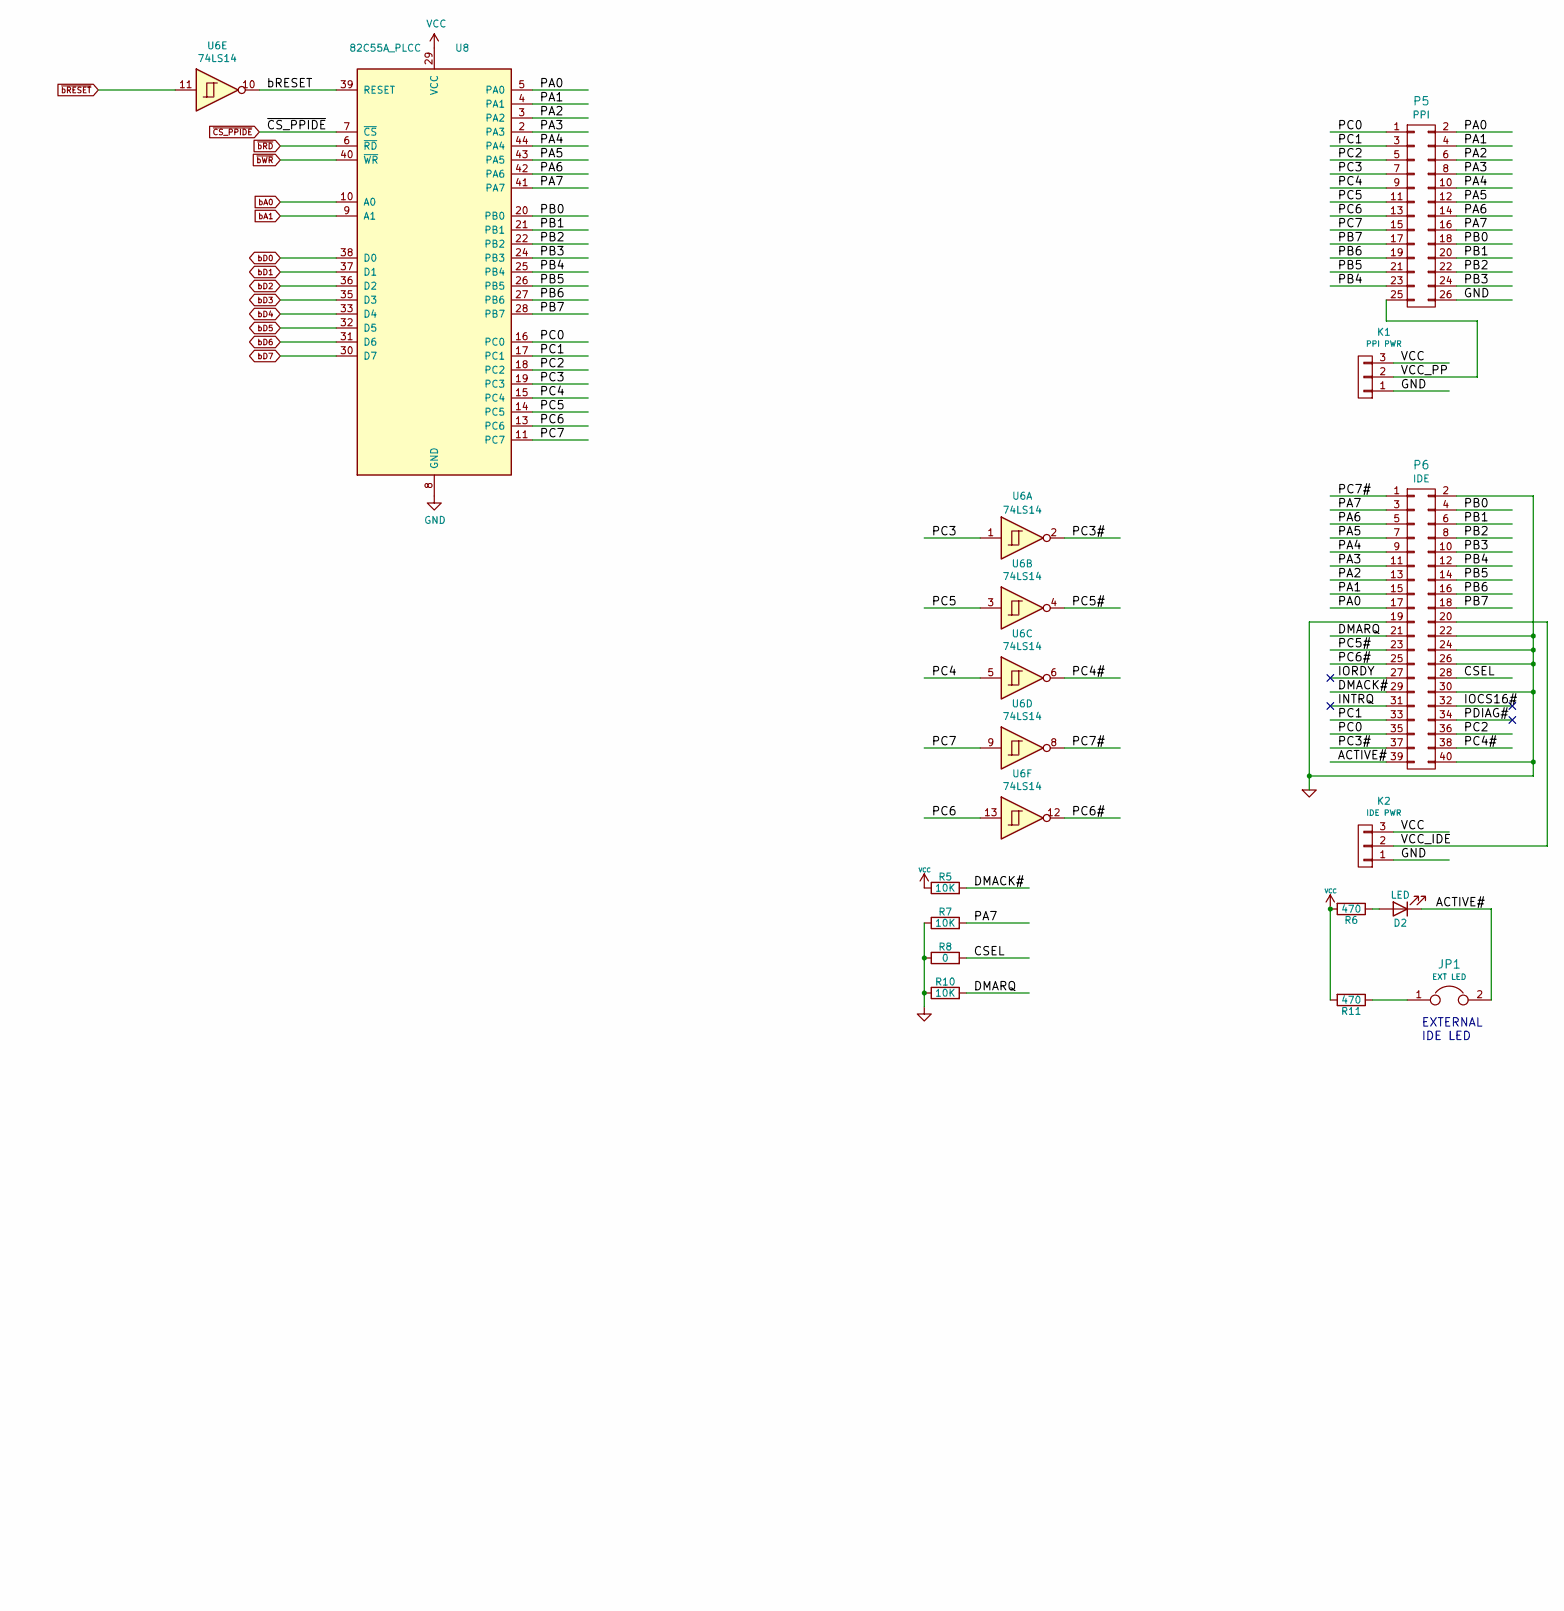
[picture p478: schematic PPIDE.sch, part in row 1, column 2]

Parts:
D2: LED; LED_D3.0mm
J7, J8: INTERRUPT; PinHeader_2x09_P2.54mm_Vertical
JP1: EXT LED; PinHeader_1x02_P2.54mm_Horizontal
K1: PPI PWR; PinHeader_1x03_P2.54mm_Vertical
K2: IDE PWR; PinHeader_1x03_P2.54mm_Vertical
P5: PPI; PinHeader_2x13_P2.54mm_Horizontal
P6: IDE; PinHeader_2x20_P2.54mm_Horizontal
R4, R9: 1000; R_Axial_DIN0207_L6.3mm_D2.5mm_P7.62mm_Horizontal
R5, R7, R10: 10K; R_Axial_DIN0207_L6.3mm_D2.5mm_P7.62mm_Horizontal
R6, R11: 470; R_Axial_DIN0207_L6.3mm_D2.5mm_P7.62mm_Horizontal
R8: 0; R_Axial_DIN0207_L6.3mm_D2.5mm_P7.62mm_Horizontal
RN1: 10K; R_Array_SIP9
SW1: IO PORT ADDR; PinHeader_2x06_P2.54mm_Vertical
U1: 74LS06; DIP-14_W7.62mm
U6: 74LS14; DIP-14_W7.62mm
U7: 74LS688; DIP-20_W7.62mm
U8: 82C55A_PLCC; PLCC-44_THT-Socket

Connections:
ACTIVE#: D2.1 (K), JP1.2, P6.39
CSEL: P6.28, R8.2
DMACK#: P6.29, R5.2
DMARQ: P6.21, R10.2
GND: K1.1, K2.1, P5.26, P6.2, P6.19, P6.22, P6.24, P6.26, P6.30, P6.40, R4.2, R7.1, R8.1, R9.2, R10.1, U7.10 (GND), U8.8 (GND)
INTA: R4.1, U1.5
INTB: R9.1, U1.3
INTRQ: P6.31
IOCS16#: P6.32
IORDY: P6.27
unnamed: D2.2 (A), R6.1
unnamed: JP1.1, R11.1
unnamed: RN1.2 (R1), SW1.1, U7.18 (R7)
unnamed: RN1.3 (R2), SW1.3, U7.16 (R6)
unnamed: RN1.4 (R3), SW1.5, U7.14 (R5)
unnamed: RN1.5 (R4), SW1.7, U7.12 (R4)
unnamed: RN1.6 (R5), SW1.9, U7.9 (R3)
unnamed: RN1.7 (R6), SW1.11, U7.7 (R2)
unnamed: RN1.9 (R8), U7.3 (R0), U7.4 (P1), U7.5 (R1)
PA0: P5.2, P6.17, U8.5 (PA0)
PA1: P5.4, P6.15, U8.4 (PA1)
PA2: P5.6, P6.13, U8.3 (PA2)
PA3: P5.8, P6.11, U8.2 (PA3)
PA4: P5.10, P6.9, U8.44 (PA4)
PA5: P5.12, P6.7, U8.43 (PA5)
PA6: P5.14, P6.5, U8.42 (PA6)
PA7: P5.16, P6.3, R7.2, U8.41 (PA7)
PB0: P5.18, P6.4, U8.20 (PB0)
PB1: P5.20, P6.6, U8.21 (PB1)
PB2: P5.22, P6.8, U8.22 (PB2)
PB3: P5.24, P6.10, U8.24 (PB3)
PB4: P5.23, P6.12, U8.25 (PB4)
PB5: P5.21, P6.14, U8.26 (PB5)
PB6: P5.19, P6.16, U8.27 (PB6)
PB7: P5.17, P6.18, U8.28 (PB7)
PC0: P5.1, P6.35, U8.16 (PC0)
PC1: P5.3, P6.33, U8.17 (PC1)
PC2: P5.5, P6.36, U8.18 (PC2)
PC3: P5.7, U6.1, U8.19 (PC3)
PC3#: P6.37, U6.2
PC4: P5.9, U6.5, U8.15 (PC4)
PC4#: P6.38, U6.6
PC5: P5.11, U6.3, U8.14 (PC5)
PC5#: P6.23, U6.4
PC6: P5.13, U6.13, U8.13 (PC6)
PC6#: P6.25, U6.12
PC7: P5.15, U6.9, U8.11 (PC7)
PC7#: P6.1, U6.8
PDIAG#: P6.34
VCC: K1.3, K2.3, R5.1, R6.2, R11.2, RN1.1 (common), U7.20 (VCC), U8.29 (VCC)
VCC_IDE: K2.2, P6.20
VCC_PP: K1.2, P5.25
ZERO: SW1.2, SW1.4, SW1.6, SW1.8, SW1.10, SW1.12
bA0: U8.10 (A0)
bA1: U8.9 (A1)
bA2: U7.6 (P2)
bA3: U7.8 (P3)
bA4: U7.11 (P4)
bA5: U7.13 (P5)
bA6: U7.15 (P6)
bA7: U7.17 (P7)
bD0: U8.38 (D0)
bD1: U8.37 (D1)
bD2: U8.36 (D2)
bD3: U8.35 (D3)
bD4: U8.33 (D4)
bD5: U8.32 (D5)
bD6: U8.31 (D6)
bD7: U8.30 (D7)
bRESET: U6.10, U8.39 (RESET)
~CS_PPIDE: U7.19 (P=R), U8.7 (~CS~)
~EIRQ0: J7.4, J8.4
~EIRQ1: J7.6, J8.6
~EIRQ2: J7.8, J8.8
~EIRQ3: J7.10, J8.10
~EIRQ4: J7.12, J8.12
~EIRQ5: J7.14, J8.14
~EIRQ6: J7.16, J8.16
~EIRQ7: J7.18, J8.18
~INT0: J7.2, J8.2
~INTA: J7.1, J7.3, J7.5, J7.7, J7.9, J7.11, J7.13, J7.15, J7.17, U1.6
~INTB: J8.1, J8.3, J8.5, J8.7, J8.9, J8.11, J8.13, J8.15, J8.17, U1.4
~bIORQ: U7.1 (G)
~bM1: U7.2 (P0)
~bRD: U8.6 (~RD~)
~bRESET: U6.11
~bWR: U8.40 (~WR~)

Notes on the sheet:
Note: Inhibit Board Operation During Interrupts ~M1~ = low, ~IORQ~ = low
IO SELECTION CIRCUIT
SET IO PORT
NOTE: ~INT~ RELIES ON 4700 OHM PULL UP RESISTOR ON PROCESSOR
Note: IO Address Port $60-$63 1-2=on - A7 (low) 3-4=off - A6 (high) 5-6=off - A5 (high) 7-8=on - A4 (low) 9-10=on - A3 (low) 11-12=on - A2 (low)
EXTERNAL IDE LED
