lynchaj/duodyne/08 input-output.Disk, V1.0/temp/buffers.sch

## KiCad design 08 input-output.Disk, V1.0/temp/buffers.sch (2023-03-30)

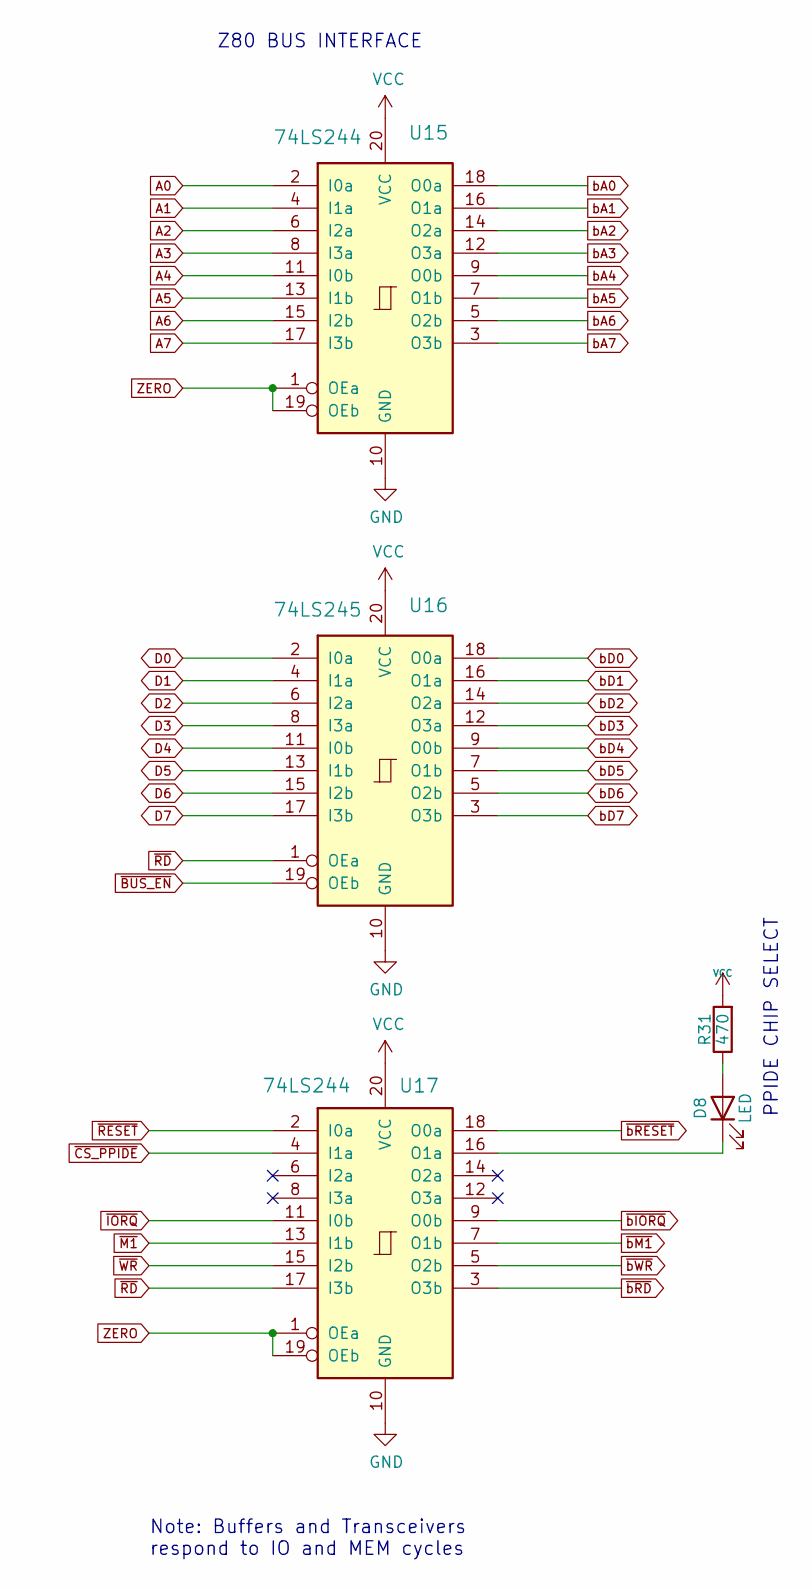
[picture p479: schematic buffers.sch]

Parts:
D8: LED; LED_D3.0mm_Horizontal_O3.81mm_Z2.0mm
R31: 470; R_Axial_DIN0207_L6.3mm_D2.5mm_P7.62mm_Horizontal
U15, U17: 74LS244; DIP-20_W7.62mm
U16: 74LS245; DIP-20_W7.62mm

Connections:
A0: U15.2 (I0a)
A1: U15.4 (I1a)
A2: U15.6 (I2a)
A3: U15.8 (I3a)
A4: U15.11 (I0b)
A5: U15.13 (I1b)
A6: U15.15 (I2b)
A7: U15.17 (I3b)
D0: U16.2 (I0a)
D1: U16.4 (I1a)
D2: U16.6 (I2a)
D3: U16.8 (I3a)
D4: U16.11 (I0b)
D5: U16.13 (I1b)
D6: U16.15 (I2b)
D7: U16.17 (I3b)
GND: U15.10 (GND), U16.10 (GND), U17.10 (GND)
unnamed: D8.1 (K), U17.16 (O1a)
unnamed: D8.2 (A), R31.1
VCC: R31.2, U15.20 (VCC), U16.20 (VCC), U17.20 (VCC)
ZERO: U15.1 (OEa), U15.19 (OEb), U17.1 (OEa), U17.19 (OEb)
bA0: U15.18 (O0a)
bA1: U15.16 (O1a)
bA2: U15.14 (O2a)
bA3: U15.12 (O3a)
bA4: U15.9 (O0b)
bA5: U15.7 (O1b)
bA6: U15.5 (O2b)
bA7: U15.3 (O3b)
bD0: U16.18 (O0a)
bD1: U16.16 (O1a)
bD2: U16.14 (O2a)
bD3: U16.12 (O3a)
bD4: U16.9 (O0b)
bD5: U16.7 (O1b)
bD6: U16.5 (O2b)
bD7: U16.3 (O3b)
~BUS_EN: U16.19 (OEb)
~CS_PPIDE: U17.4 (I1a)
~IORQ: U17.11 (I0b)
~M1: U17.13 (I1b)
~RD: U16.1 (OEa), U17.17 (I3b)
~RESET: U17.2 (I0a)
~WR: U17.15 (I2b)
~bIORQ: U17.9 (O0b)
~bM1: U17.7 (O1b)
~bRD: U17.3 (O3b)
~bRESET: U17.18 (O0a)
~bWR: U17.5 (O2b)

Notes on the sheet:
Note: Buffers and Transceivers respond to IO and MEM cycles
Z80 BUS INTERFACE
PPIDE CHIP SELECT
