lynchaj/duodyne/08 input-output.Disk, V1.0/temp/input-output.Disk.sch

## KiCad design 08 input-output.Disk, V1.0/temp/input-output.Disk.sch (2023-03-30)

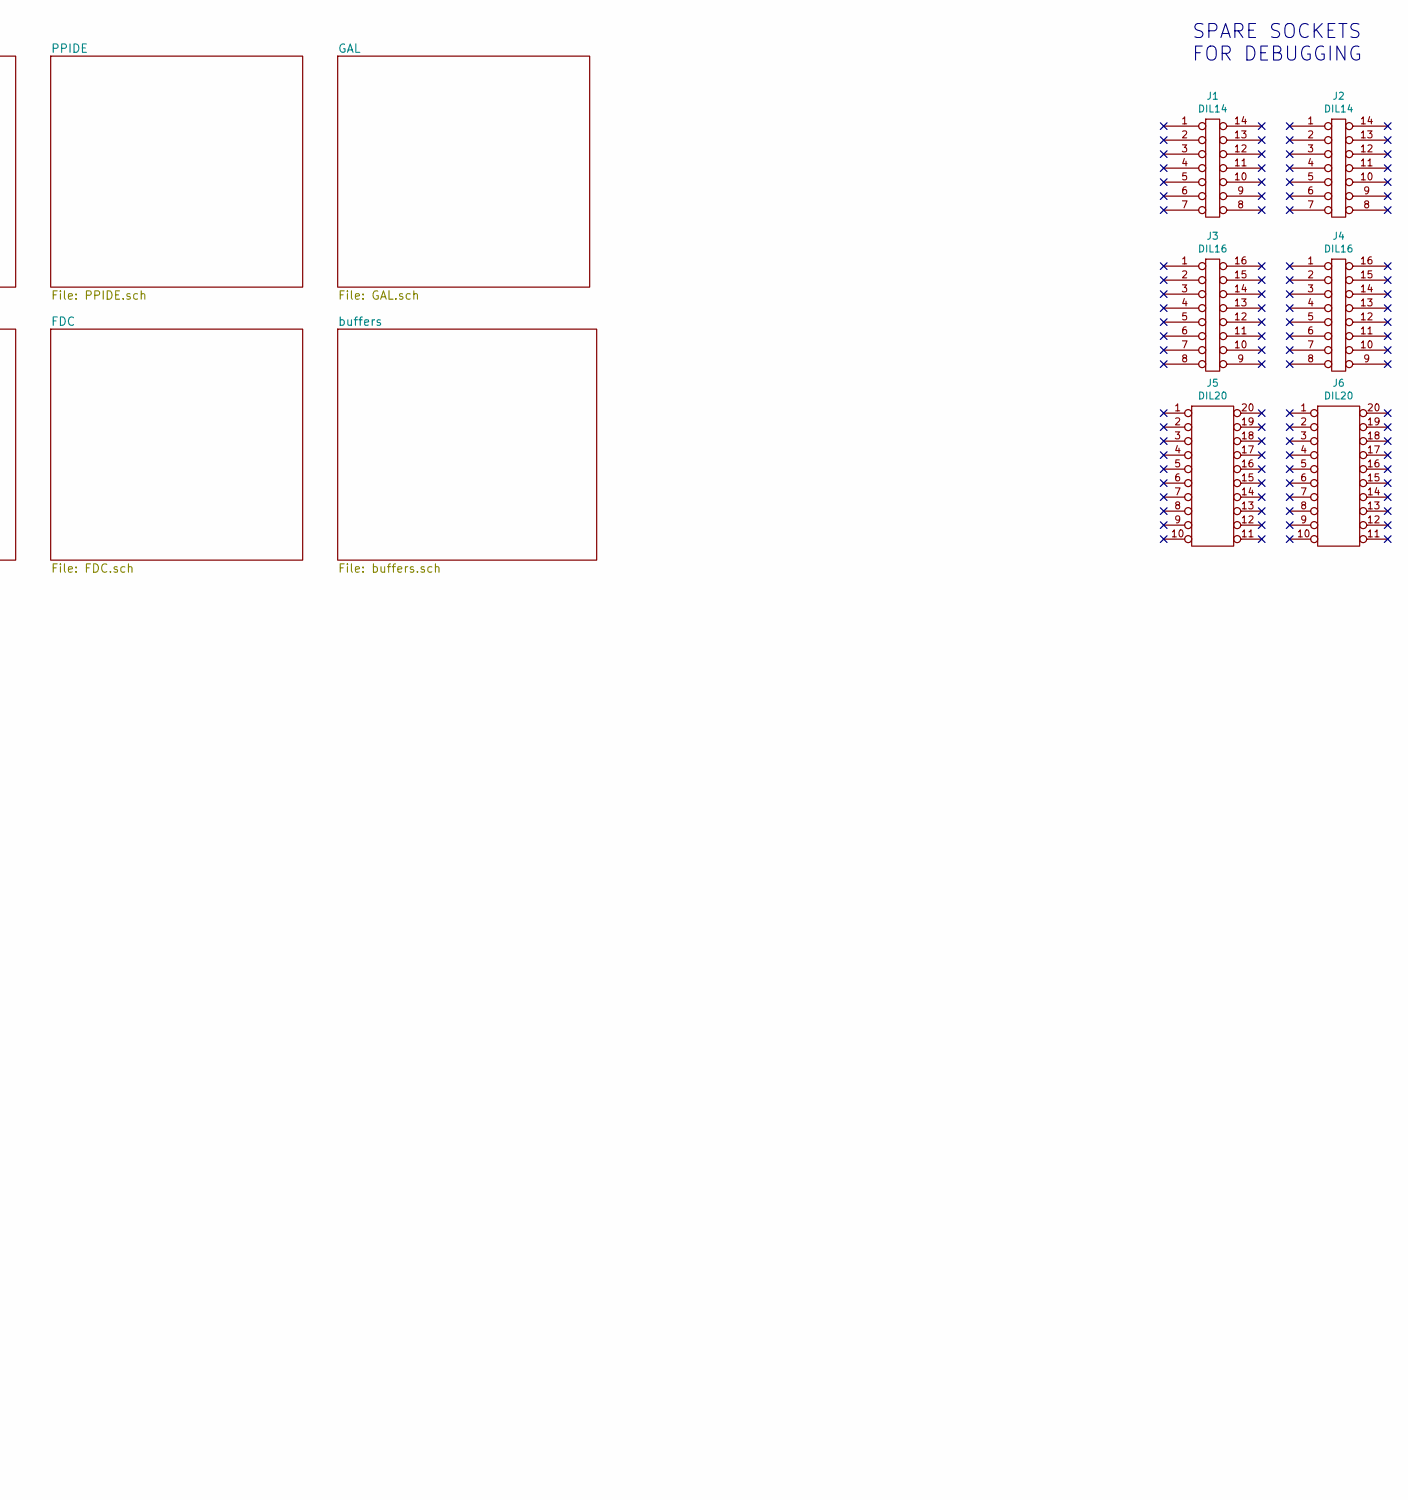
[picture p480: schematic input-output.Disk.sch, part in row 1, column 2]

Parts:
J1, J2: DIL14; DIP-14_W7.62mm
J3, J4: DIL16; DIP-16_W7.62mm
J5, J6: DIL20; DIP-20_W7.62mm

Notes on the sheet:
SPARE SOCKETS FOR DEBUGGING
