lynchaj/duodyne/08 input-output.Disk, V1.0/temp/parallel.sch

## KiCad design 08 input-output.Disk, V1.0/temp/parallel.sch (2023-03-30)

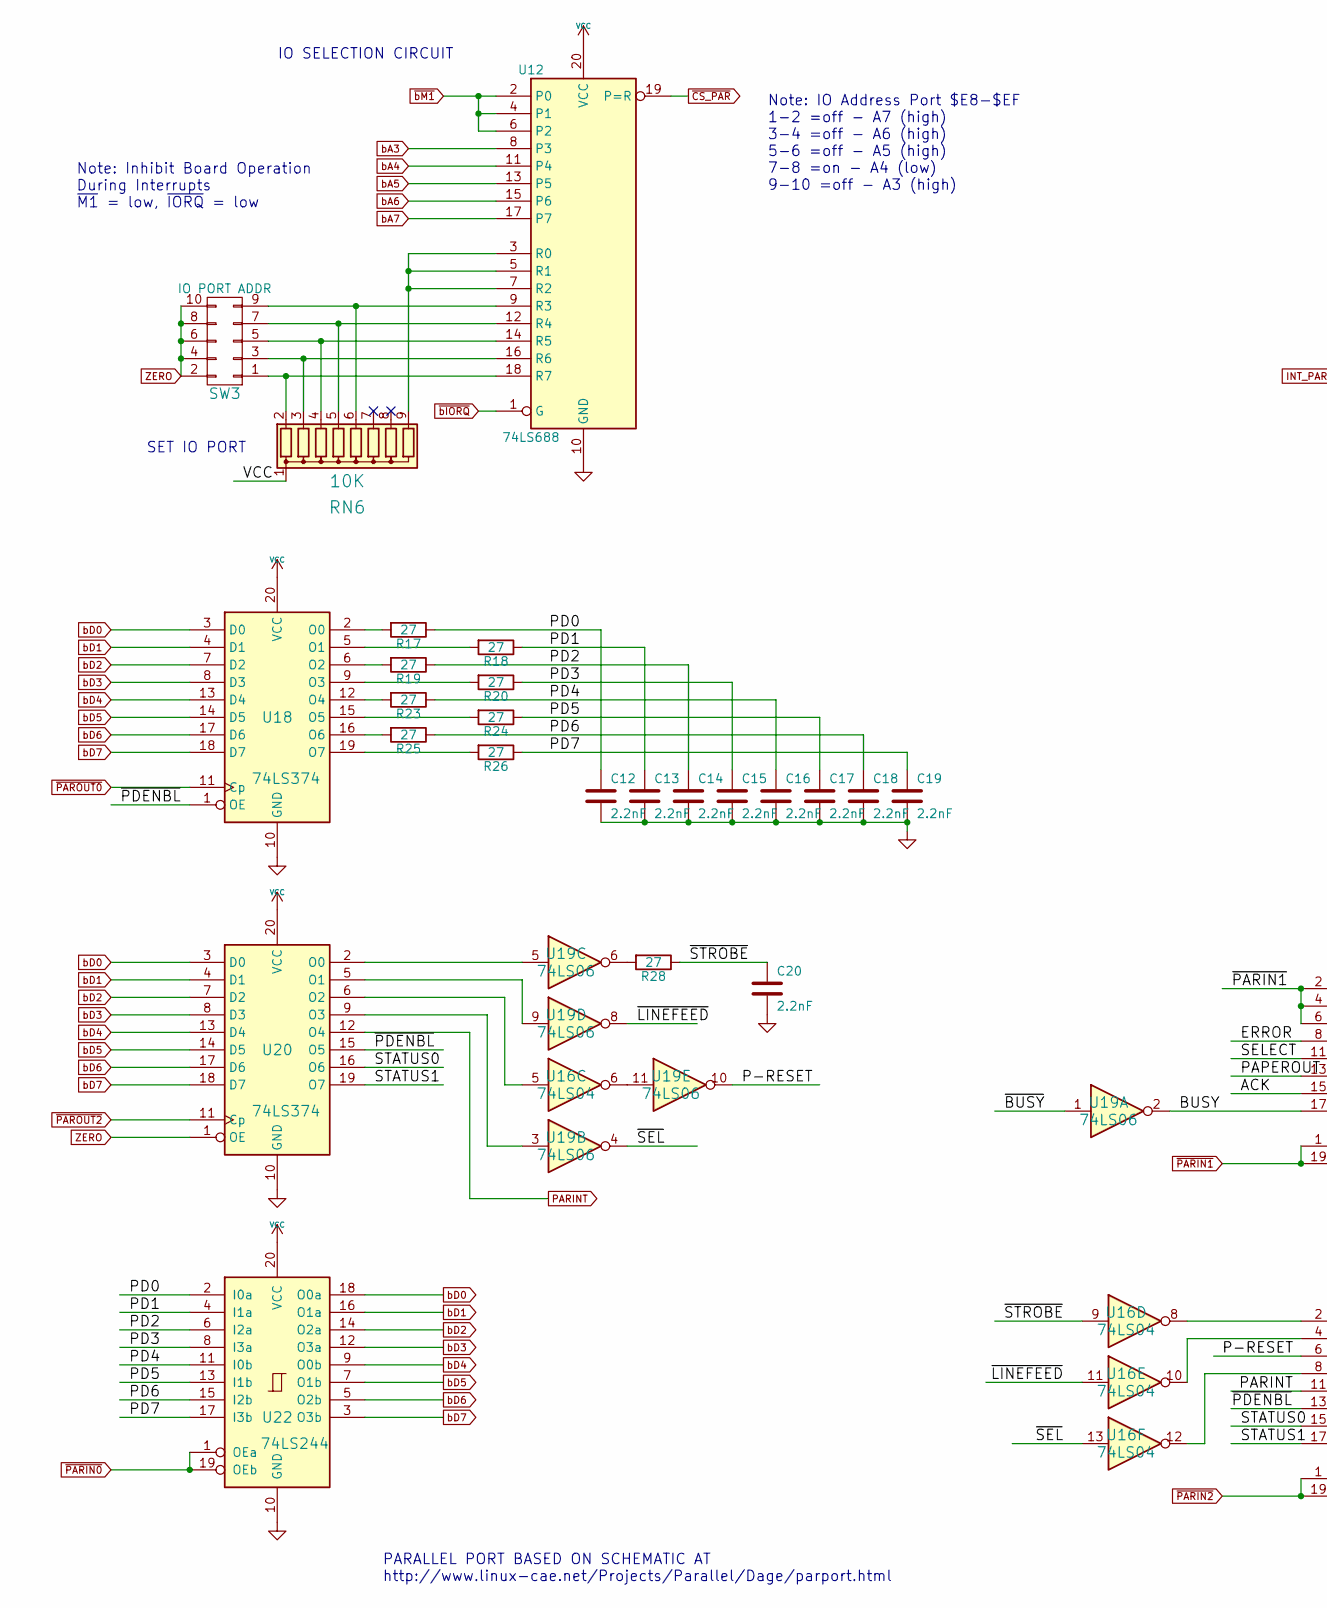
[picture p481: schematic parallel.sch, part in row 1, column 1]

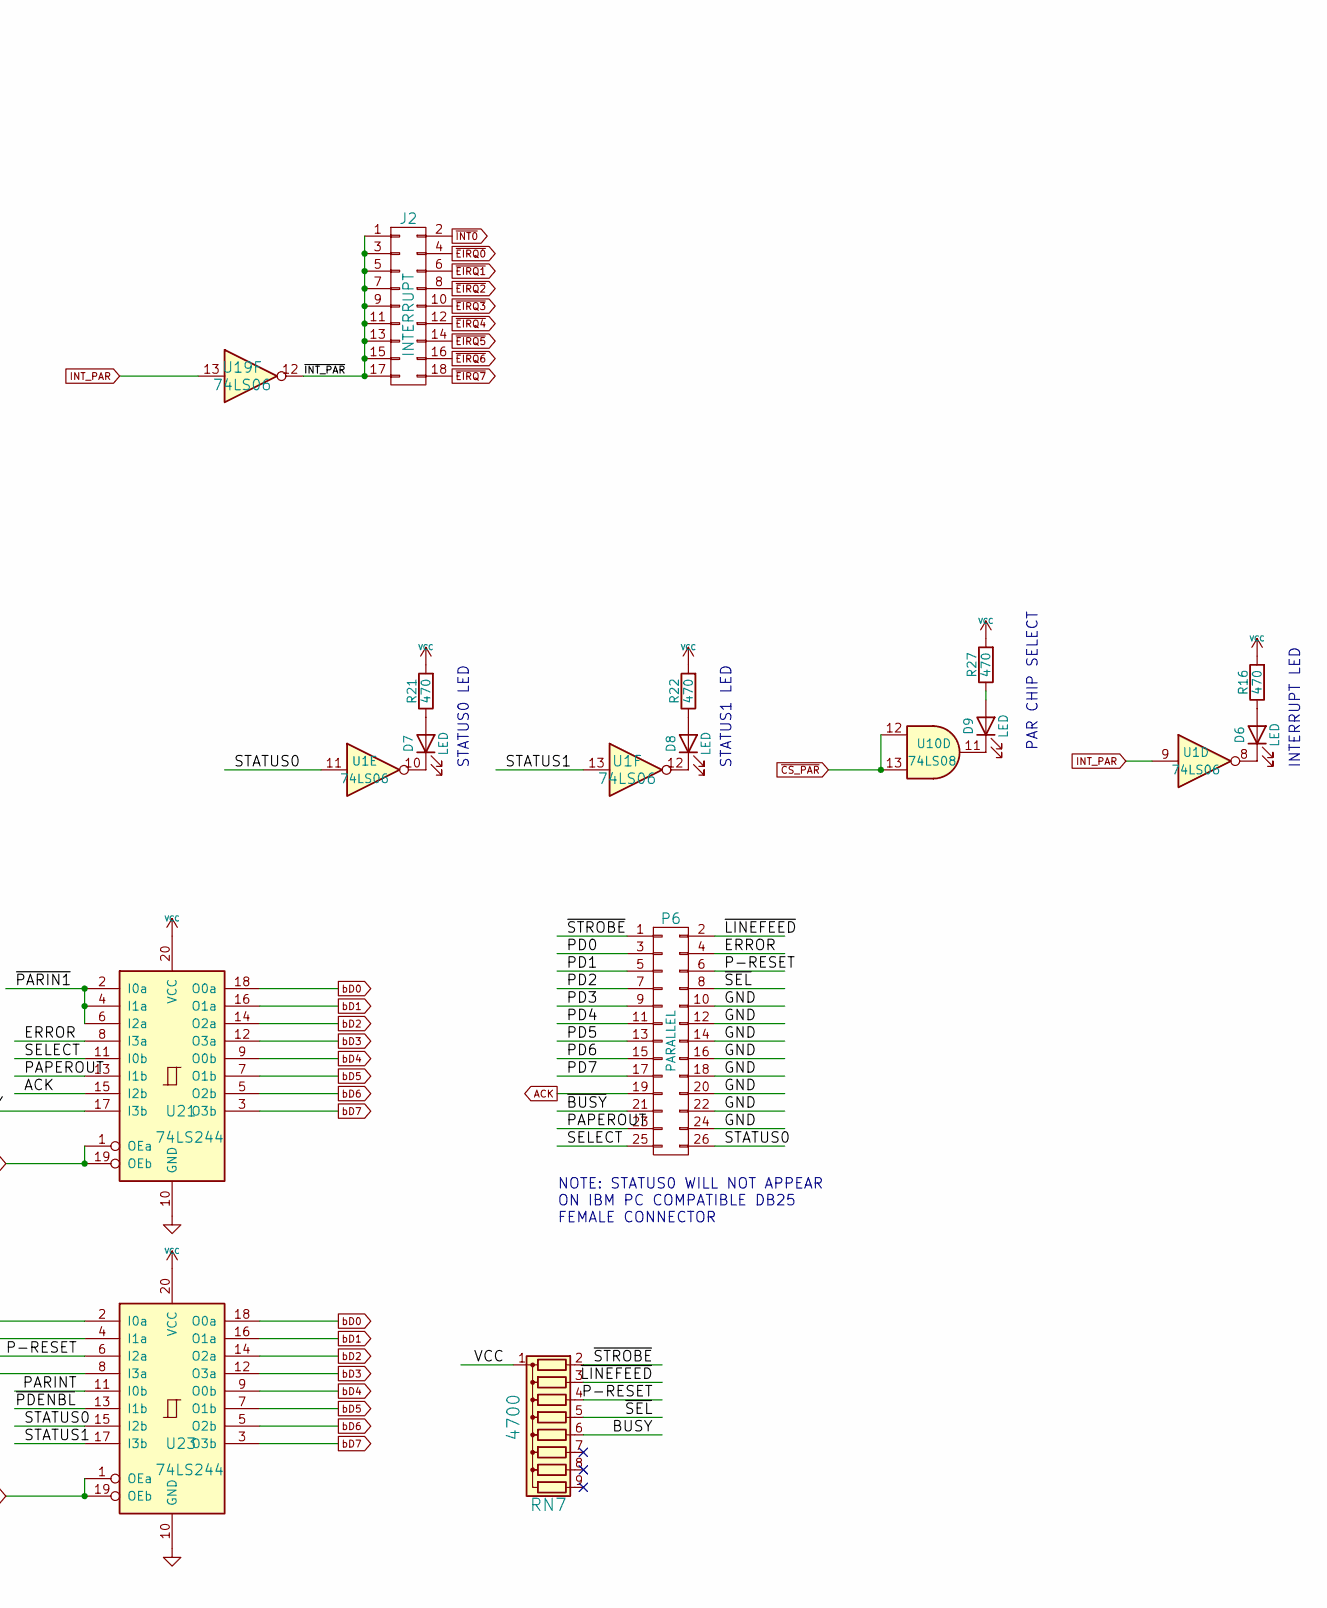
[picture p482: schematic parallel.sch, part in row 1, column 2]

Parts:
C12, C13, C14, C15, C16, C17, C18, C19, C20: 2.2nF; C_Disc_D5.0mm_W2.5mm_P5.00mm
D6, D7, D8: LED; LED_D3.0mm
D9: LED; LED_D3.0mm_Horizontal_O3.81mm_Z2.0mm
J2: INTERRUPT; PinHeader_2x09_P2.54mm_Vertical
P6: PARALLEL; IDC-Header_2x13_P2.54mm_Horizontal
R16, R21, R22, R27: 470; R_Axial_DIN0207_L6.3mm_D2.5mm_P7.62mm_Horizontal
R17, R18, R19, R20, R23, R24, R25, R26, R28: 27; R_Axial_DIN0207_L6.3mm_D2.5mm_P7.62mm_Horizontal
RN6: 10K; R_Array_SIP9
RN7: 4700; R_Array_SIP9
SW3: IO PORT ADDR; PinHeader_2x05_P2.54mm_Vertical
U1, U19: 74LS06; DIP-14_W7.62mm
U10: 74LS08; DIP-14_W7.62mm
U12: 74LS688; DIP-20_W7.62mm
U16: 74LS04; DIP-14_W7.62mm
U18, U20: 74LS374; DIP-20_W7.62mm
U21, U22, U23: 74LS244; DIP-20_W7.62mm

Connections:
ACK: P6.19, U21.15 (I2b)
BUSY: RN7.6 (R5), U19.2, U21.17 (I3b)
ERROR: P6.4, U21.8 (I3a)
GND: C12.2, C13.2, C14.2, C15.2, C16.2, C17.2, C18.2, C19.2, C20.2, P6.10, P6.12, P6.14, P6.16, P6.18, P6.20, P6.22, P6.24, U12.10 (GND), U18.10 (GND), U20.10 (GND), U21.10 (GND), U22.10 (GND), U23.10 (GND)
INT_PAR: U1.9, U19.13
unnamed: D6.1 (K), U1.8
unnamed: D6.2 (A), R16.1
unnamed: D7.1 (K), U1.10
unnamed: D7.2 (A), R21.1
unnamed: D8.1 (K), U1.12
unnamed: D8.2 (A), R22.1
unnamed: D9.1 (K), U10.11
unnamed: D9.2 (A), R27.1
unnamed: R17.2, U18.2 (O0)
unnamed: R18.2, U18.5 (O1)
unnamed: R19.2, U18.6 (O2)
unnamed: R20.2, U18.9 (O3)
unnamed: R23.2, U18.12 (O4)
unnamed: R24.2, U18.15 (O5)
unnamed: R25.2, U18.16 (O6)
unnamed: R26.2, U18.19 (O7)
unnamed: R28.2, U19.6
unnamed: RN6.2 (R1), SW3.1, U12.18 (R7)
unnamed: RN6.3 (R2), SW3.3, U12.16 (R6)
unnamed: RN6.4 (R3), SW3.5, U12.14 (R5)
unnamed: RN6.5 (R4), SW3.7, U12.12 (R4)
unnamed: RN6.6 (R5), SW3.9, U12.9 (R3)
unnamed: RN6.9 (R8), U12.3 (R0), U12.5 (R1), U12.7 (R2)
unnamed: U16.5, U20.6 (O2)
unnamed: U16.6, U19.11
unnamed: U16.8, U23.2 (I0a)
unnamed: U16.10, U23.4 (I1a)
unnamed: U16.12, U23.8 (I3a)
unnamed: U19.3, U20.9 (O3)
unnamed: U19.5, U20.2 (O0)
unnamed: U19.9, U20.5 (O1)
P-RESET: P6.6, RN7.4 (R3), U19.10, U23.6 (I2a)
PAPEROUT: P6.23, U21.13 (I1b)
PARINT: U20.12 (O4), U23.11 (I0b)
PD0: C12.1, P6.3, R17.1, U22.2 (I0a)
PD1: C13.1, P6.5, R18.1, U22.4 (I1a)
PD2: C14.1, P6.7, R19.1, U22.6 (I2a)
PD3: C15.1, P6.9, R20.1, U22.8 (I3a)
PD4: C16.1, P6.11, R23.1, U22.11 (I0b)
PD5: C17.1, P6.13, R24.1, U22.13 (I1b)
PD6: C18.1, P6.15, R25.1, U22.15 (I2b)
PD7: C19.1, P6.17, R26.1, U22.17 (I3b)
SELECT: P6.25, U21.11 (I0b)
STATUS0: P6.26, U1.11, U20.16 (O6), U23.15 (I2b)
STATUS1: U1.13, U20.19 (O7), U23.17 (I3b)
VCC: R16.2, R21.2, R22.2, R27.2, RN6.1 (common), RN7.1 (common), U12.20 (VCC), U18.20 (VCC), U20.20 (VCC), U21.20 (VCC), U22.20 (VCC), U23.20 (VCC)
ZERO: SW3.2, SW3.4, SW3.6, SW3.8, SW3.10, U20.1 (OE)
bA3: U12.8 (P3)
bA4: U12.11 (P4)
bA5: U12.13 (P5)
bA6: U12.15 (P6)
bA7: U12.17 (P7)
bD0: U18.3 (D0), U20.3 (D0), U21.18 (O0a), U22.18 (O0a), U23.18 (O0a)
bD1: U18.4 (D1), U20.4 (D1), U21.16 (O1a), U22.16 (O1a), U23.16 (O1a)
bD2: U18.7 (D2), U20.7 (D2), U21.14 (O2a), U22.14 (O2a), U23.14 (O2a)
bD3: U18.8 (D3), U20.8 (D3), U21.12 (O3a), U22.12 (O3a), U23.12 (O3a)
bD4: U18.13 (D4), U20.13 (D4), U21.9 (O0b), U22.9 (O0b), U23.9 (O0b)
bD5: U18.14 (D5), U20.14 (D5), U21.7 (O1b), U22.7 (O1b), U23.7 (O1b)
bD6: U18.17 (D6), U20.17 (D6), U21.5 (O2b), U22.5 (O2b), U23.5 (O2b)
bD7: U18.18 (D7), U20.18 (D7), U21.3 (O3b), U22.3 (O3b), U23.3 (O3b)
~BUSY: P6.21, U19.1
~CS_PAR: U10.12, U10.13, U12.19 (P=R)
~EIRQ0: J2.4
~EIRQ1: J2.6
~EIRQ2: J2.8
~EIRQ3: J2.10
~EIRQ4: J2.12
~EIRQ5: J2.14
~EIRQ6: J2.16
~EIRQ7: J2.18
~INT0: J2.2
~INT_PAR: J2.1, J2.3, J2.5, J2.7, J2.9, J2.11, J2.13, J2.15, J2.17, U19.12
~LINEFEED: P6.2, RN7.3 (R2), U16.11, U19.8
~PARIN0: U22.1 (OEa), U22.19 (OEb)
~PARIN1: U21.1 (OEa), U21.2 (I0a), U21.4 (I1a), U21.6 (I2a), U21.19 (OEb)
~PARIN2: U23.1 (OEa), U23.19 (OEb)
~PAROUT0: U18.11 (Cp)
~PAROUT2: U20.11 (Cp)
~PDENBL: U18.1 (OE), U20.15 (O5), U23.13 (I1b)
~SEL: P6.8, RN7.5 (R4), U16.13, U19.4
~STROBE: C20.1, P6.1, R28.1, RN7.2 (R1), U16.9
~bIORQ: U12.1 (G)
~bM1: U12.2 (P0), U12.4 (P1), U12.6 (P2)

Notes on the sheet:
IO SELECTION CIRCUIT
SET IO PORT
PAR CHIP SELECT
Note: Inhibit Board Operation During Interrupts ~M1~ = low, ~IORQ~ = low
Note: IO Address Port $E8-$EF 1-2 =off - A7 (high) 3-4 =off - A6 (high) 5-6 =off - A5 (high) 7-8 =on - A4 (low) 9-10 =off - A3 (high)
PARALLEL PORT BASED ON SCHEMATIC AT http://www.linux-cae.net/Projects/Parallel/Dage/parport.html
INTERRUPT LED
STATUS0 LED
STATUS1 LED
NOTE: STATUS0 WILL NOT APPEAR ON IBM PC COMPATIBLE DB25 FEMALE CONNECTOR
