lynchaj/duodyne/08 input-output.Disk, V1.0/temp/power.sch

## KiCad design 08 input-output.Disk, V1.0/temp/power.sch (2023-03-30)

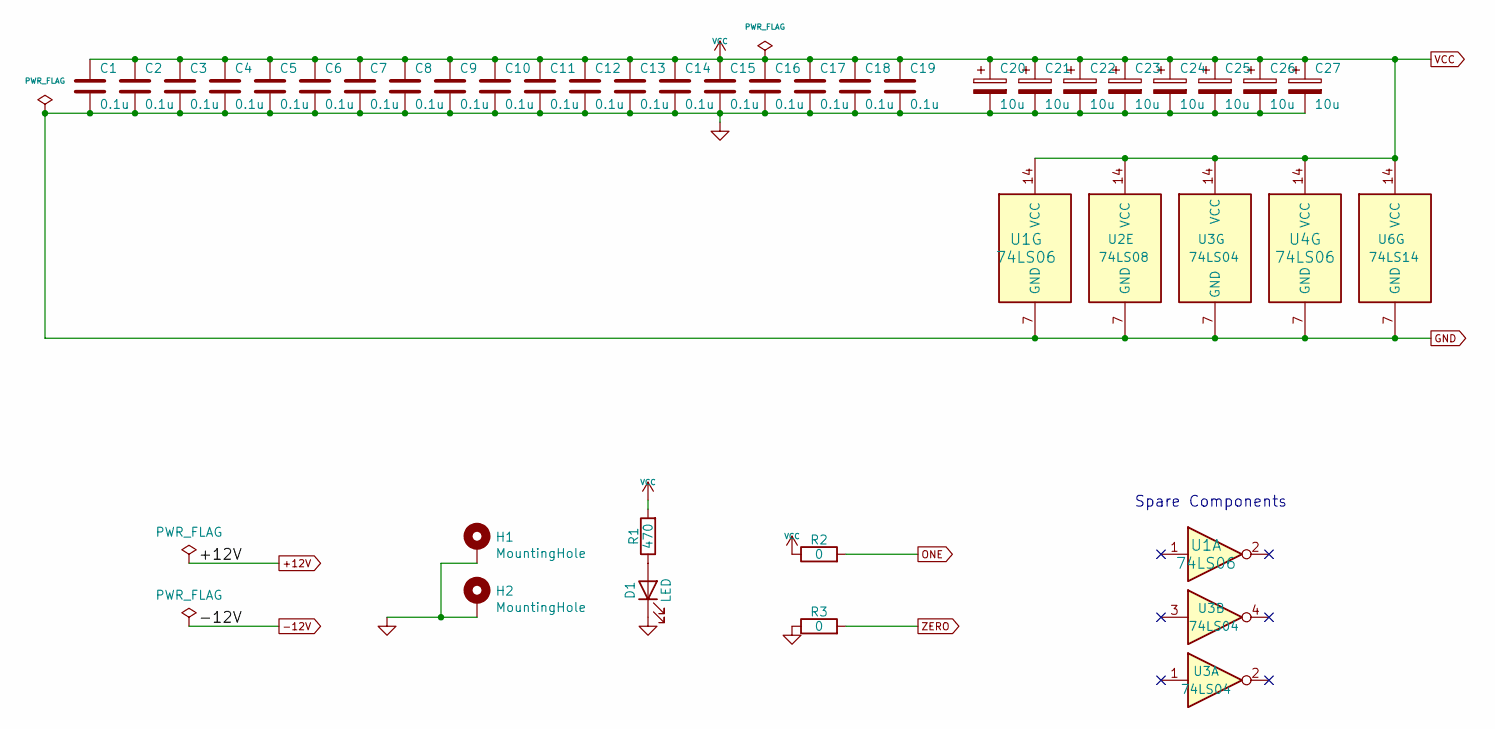
[picture p483: schematic power.sch]

Parts:
C1, C2, C3, C4, C5, C6, C7, C8, C9, C10, C11, C12, C13, C14, C15, C16, C17, C18, C19: 0.1u; C_Disc_D5.0mm_W2.5mm_P5.00mm
C20, C21, C22, C23, C24, C25, C26, C27: 10u; CP_Radial_D5.0mm_P2.50mm
D1: LED; LED_D3.0mm_Horizontal_O3.81mm_Z2.0mm
H1, H2: MountingHole; MountingHole_3.2mm_M3_Pad
R1: 470; R_Axial_DIN0207_L6.3mm_D2.5mm_P7.62mm_Horizontal
R2, R3: 0; R_Axial_DIN0207_L6.3mm_D2.5mm_P7.62mm_Horizontal
U1, U4: 74LS06; DIP-14_W7.62mm
U2: 74LS08; DIP-14_W7.62mm
U3: 74LS04; DIP-14_W7.62mm
U6: 74LS14; DIP-14_W7.62mm

Connections:
GND: C1.2, C2.2, C3.2, C4.2, C5.2, C6.2, C7.2, C8.2, C9.2, C10.2, C11.2, C12.2, C13.2, C14.2, C15.2, C16.2, C17.2, C18.2, C19.2, C20.2, C21.2, C22.2, C23.2, C24.2, C25.2, C26.2, C27.2, D1.1 (K), H1.1, H2.1, R3.1, U1.7 (GND), U2.7 (GND), U3.7 (GND), U4.7 (GND), U6.7 (GND)
unnamed: D1.2 (A), R1.1
ONE: R2.2
VCC: C1.1, C2.1, C3.1, C4.1, C5.1, C6.1, C7.1, C8.1, C9.1, C10.1, C11.1, C12.1, C13.1, C14.1, C15.1, C16.1, C17.1, C18.1, C19.1, C20.1, C21.1, C22.1, C23.1, C24.1, C25.1, C26.1, C27.1, R1.2, R2.1, U1.14 (VCC), U2.14 (VCC), U3.14 (VCC), U4.14 (VCC), U6.14 (VCC)
ZERO: R3.2

Notes on the sheet:
Spare Components
