lynchaj/duodyne/12 front-panel.processor, V1.0/temp/backplane.4-slot.sch

## KiCad design 12 front-panel.processor, V1.0/temp/backplane.4-slot.sch (2023-03-30)

Schematic: backplane.4-slot.sch

Parts:
D5: LED; LED_D3.0mm
H1, H2, H3, H4: MountingHole; MountingHole_3.2mm_M3_Pad
J1, J2, J3, J4, J5, J6, J7, J8, J9, J10, J11, J12: CONN_02X25; PinSocket_2x25_P2.54mm_Vertical
P1, P2, P3: INT-CHN; PinHeader_1x04_P2.54mm_Vertical
R6: 470; R_Axial_DIN0207_L6.3mm_D2.5mm_P7.62mm_Horizontal
T1, T2: Screw_Terminal_1x02; TerminalBlock_Phoenix_MKDS-1,5-2-5.08_1x02_P5.08mm_Horizont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

Notes on the sheet:
Zilog Interrupt Priority Bus Jumpers
