lynchaj/duodyne/24 backplane.20-slot, V1.0/temp/backplane.8-slot.sch

## KiCad design 24 backplane.20-slot, V1.0/temp/backplane.8-slot.sch (2023-03-30)

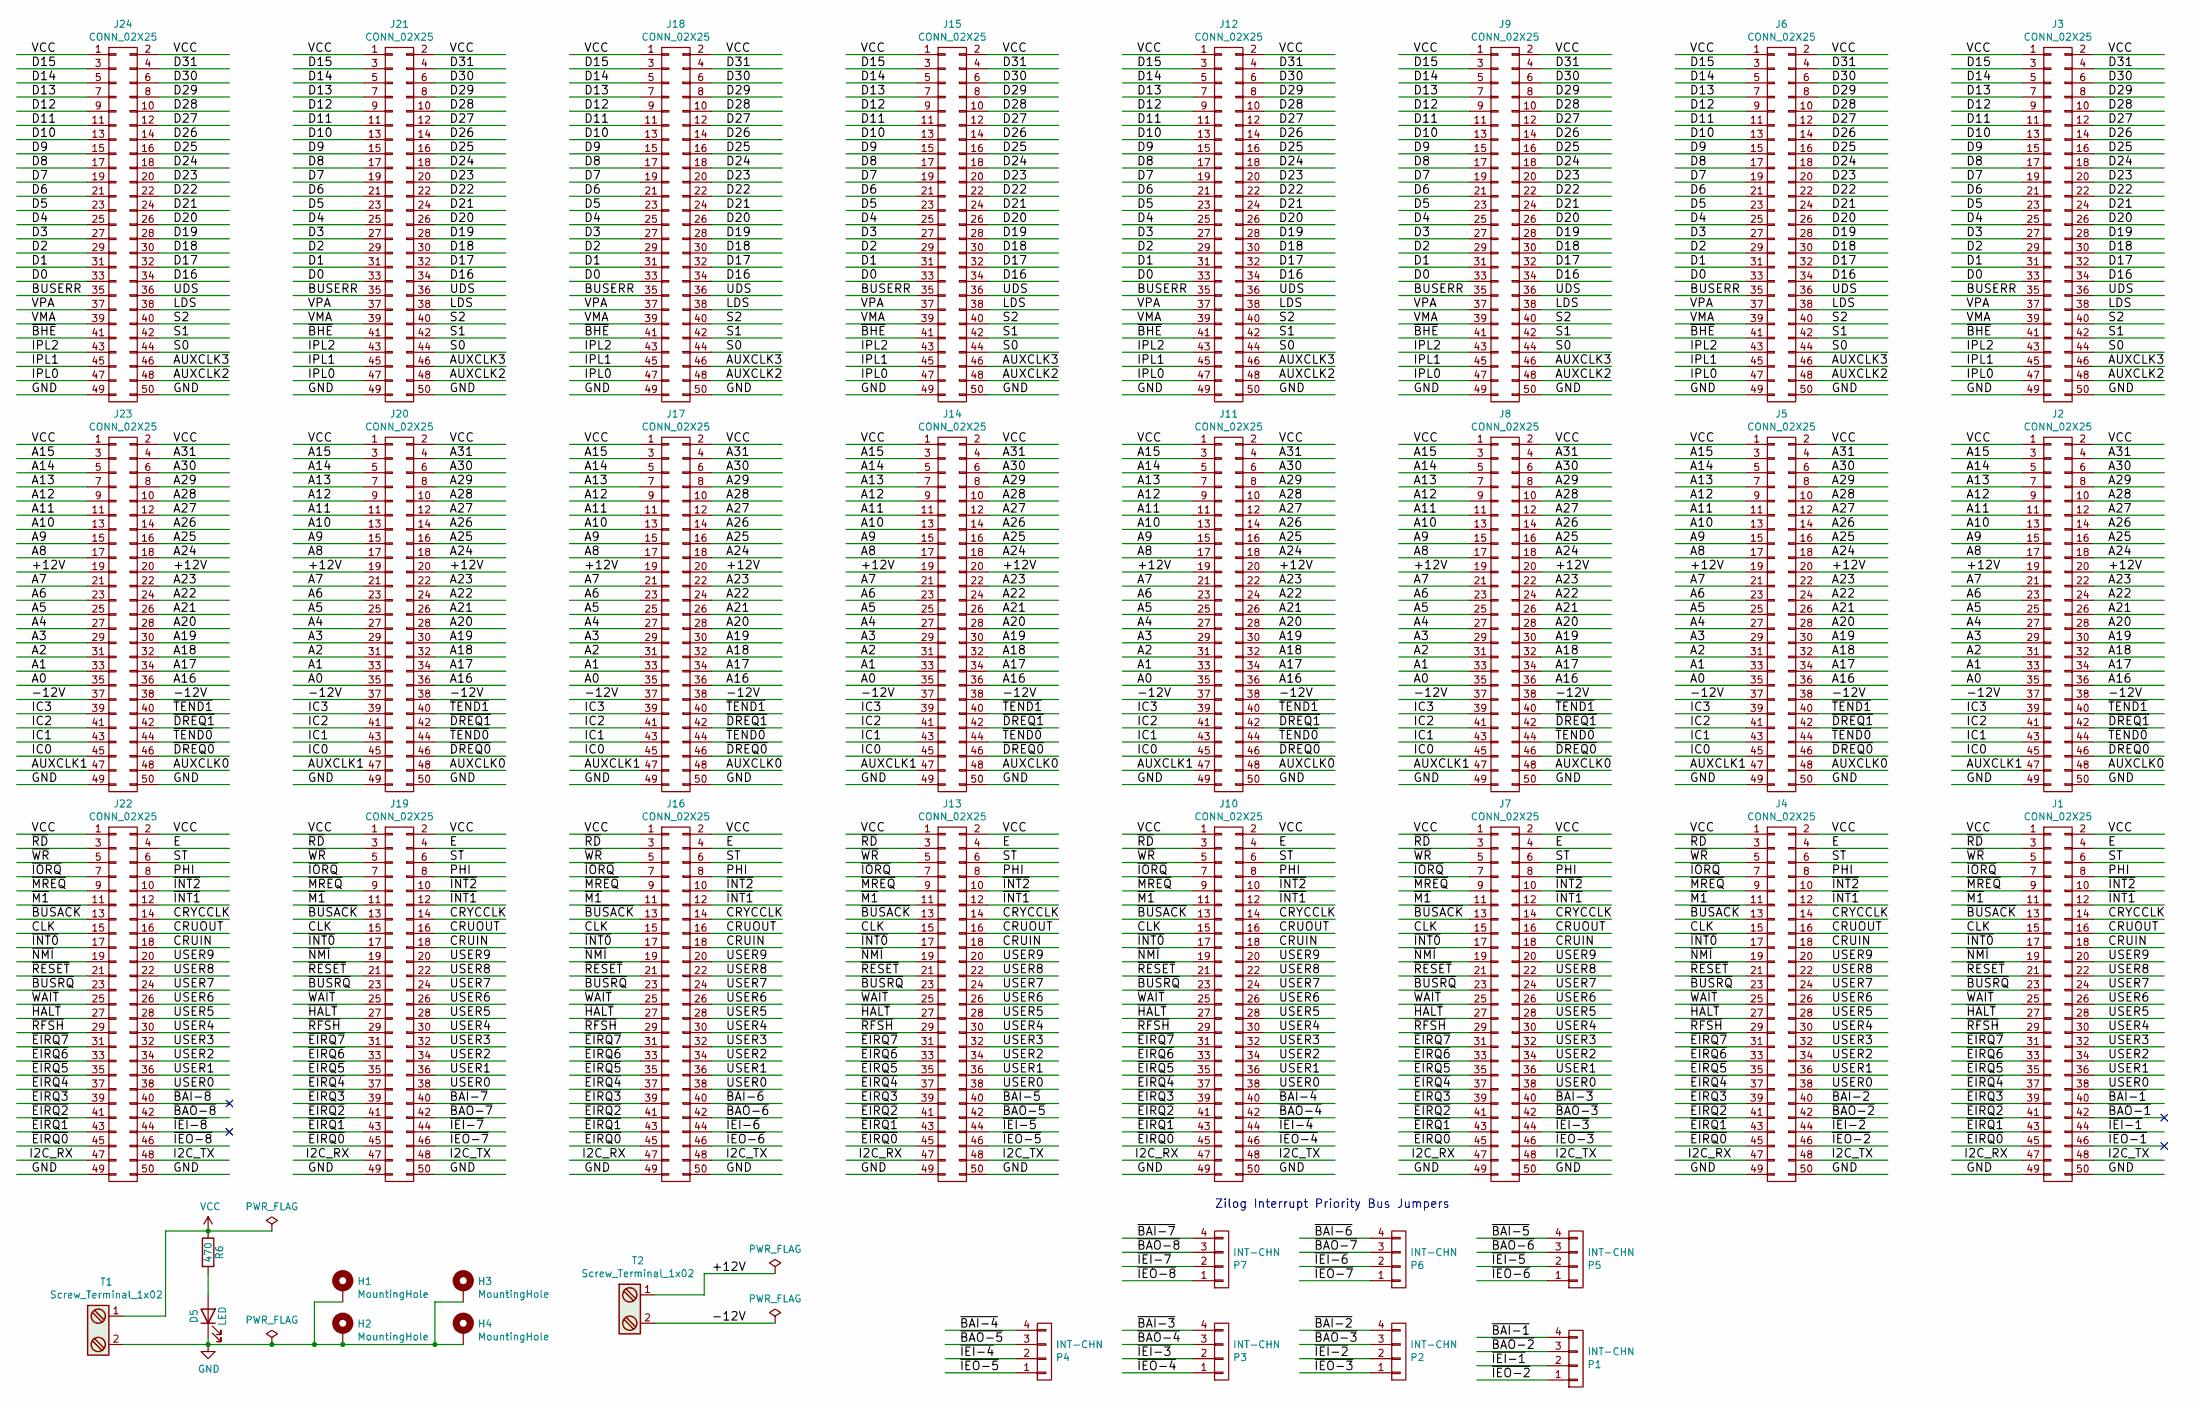
[picture p484: schematic backplane.8-slot.sch]

Parts:
D5: LED; LED_D3.0mm
H1, H2, H3, H4: MountingHole; MountingHole_3.2mm_M3_Pad
J1, J2, J3, J4, J5, J6, J7, J8, J9, J10, J11, J12, J13, J14, J15, J16, J17, J18, J19, J20, J21, J22, J23, J24: CONN_02X25; PinSocket_2x25_P2.54mm_Vertical
P1, P2, P3, P4, P5, P6, P7: INT-CHN; PinHeader_1x04_P2.54mm_Vertical
R6: 470; R_Axial_DIN0207_L6.3mm_D2.5mm_P7.62mm_Horizontal
T1, T2: Screw_Terminal_1x02; TerminalBlock_Phoenix_MKDS-1,5-2-5.08_1x02_P5.08mm_Horizont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

Connections:
+12V: J2.19, J2.20, J5.19, J5.20, J8.19, J8.20, J11.19, J11.20, J14.19, J14.20, J17.19, J17.20, J20.19, J20.20, J23.19, J23.20, T2.1
-12V: J2.37, J2.38, J5.37, J5.38, J8.37, J8.38, J11.37, J11.38, J14.37, J14.38, J17.37, J17.38, J20.37, J20.38, J23.37, J23.38, T2.2
A0: J2.35, J5.35, J8.35, J11.35, J14.35, J17.35, J20.35, J23.35
A1: J2.33, J5.33, J8.33, J11.33, J14.33, J17.33, J20.33, J23.33
A2: J2.31, J5.31, J8.31, J11.31, J14.31, J17.31, J20.31, J23.31
A3: J2.29, J5.29, J8.29, J11.29, J14.29, J17.29, J20.29, J23.29
A4: J2.27, J5.27, J8.27, J11.27, J14.27, J17.27, J20.27, J23.27
A5: J2.25, J5.25, J8.25, J11.25, J14.25, J17.25, J20.25, J23.25
A6: J2.23, J5.23, J8.23, J11.23, J14.23, J17.23, J20.23, J23.23
A7: J2.21, J5.21, J8.21, J11.21, J14.21, J17.21, J20.21, J23.21
A8: J2.17, J5.17, J8.17, J11.17, J14.17, J17.17, J20.17, J23.17
A9: J2.15, J5.15, J8.15, J11.15, J14.15, J17.15, J20.15, J23.15
A10: J2.13, J5.13, J8.13, J11.13, J14.13, J17.13, J20.13, J23.13
A11: J2.11, J5.11, J8.11, J11.11, J14.11, J17.11, J20.11, J23.11
A12: J2.9, J5.9, J8.9, J11.9, J14.9, J17.9, J20.9, J23.9
A13: J2.7, J5.7, J8.7, J11.7, J14.7, J17.7, J20.7, J23.7
A14: J2.5, J5.5, J8.5, J11.5, J14.5, J17.5, J20.5, J23.5
A15: J2.3, J5.3, J8.3, J11.3, J14.3, J17.3, J20.3, J23.3
A16: J2.36, J5.36, J8.36, J11.36, J14.36, J17.36, J20.36, J23.36
A17: J2.34, J5.34, J8.34, J11.34, J14.34, J17.34, J20.34, J23.34
A18: J2.32, J5.32, J8.32, J11.32, J14.32, J17.32, J20.32, J23.32
A19: J2.30, J5.30, J8.30, J11.30, J14.30, J17.30, J20.30, J23.30
A20: J2.28, J5.28, J8.28, J11.28, J14.28, J17.28, J20.28, J23.28
A21: J2.26, J5.26, J8.26, J11.26, J14.26, J17.26, J20.26, J23.26
A22: J2.24, J5.24, J8.24, J11.24, J14.24, J17.24, J20.24, J23.24
A23: J2.22, J5.22, J8.22, J11.22, J14.22, J17.22, J20.22, J23.22
A24: J2.18, J5.18, J8.18, J11.18, J14.18, J17.18, J20.18, J23.18
A25: J2.16, J5.16, J8.16, J11.16, J14.16, J17.16, J20.16, J23.16
A26: J2.14, J5.14, J8.14, J11.14, J14.14, J17.14, J20.14, J23.14
A27: J2.12, J5.12, J8.12, J11.12, J14.12, J17.12, J20.12, J23.12
A28: J2.10, J5.10, J8.10, J11.10, J14.10, J17.10, J20.10, J23.10
A29: J2.8, J5.8, J8.8, J11.8, J14.8, J17.8, J20.8, J23.8
A30: J2.6, J5.6, J8.6, J11.6, J14.6, J17.6, J20.6, J23.6
A31: J2.4, J5.4, J8.4, J11.4, J14.4, J17.4, J20.4, J23.4
AUXCLK0: J2.48, J5.48, J8.48, J11.48, J14.48, J17.48, J20.48, J23.48
AUXCLK1: J2.47, J5.47, J8.47, J11.47, J14.47, J17.47, J20.47, J23.47
AUXCLK2: J3.48, J6.48, J9.48, J12.48, J15.48, J18.48, J21.48, J24.48
AUXCLK3: J3.46, J6.46, J9.46, J12.46, J15.46, J18.46, J21.46, J24.46
BUSERR: J3.35, J6.35, J9.35, J12.35, J15.35, J18.35, J21.35, J24.35
CLK: J1.15, J4.15, J7.15, J10.15, J13.15, J16.15, J19.15, J22.15
CRUIN: J1.18, J4.18, J7.18, J10.18, J13.18, J16.18, J19.18, J22.18
CRUOUT: J1.16, J4.16, J7.16, J10.16, J13.16, J16.16, J19.16, J22.16
CRYCCLK: J1.14, J4.14, J7.14, J10.14, J13.14, J16.14, J19.14, J22.14
D0: J3.33, J6.33, J9.33, J12.33, J15.33, J18.33, J21.33, J24.33
D1: J3.31, J6.31, J9.31, J12.31, J15.31, J18.31, J21.31, J24.31
D2: J3.29, J6.29, J9.29, J12.29, J15.29, J18.29, J21.29, J24.29
D3: J3.27, J6.27, J9.27, J12.27, J15.27, J18.27, J21.27, J24.27
D4: J3.25, J6.25, J9.25, J12.25, J15.25, J18.25, J21.25, J24.25
D5: J3.23, J6.23, J9.23, J12.23, J15.23, J18.23, J21.23, J24.23
D6: J3.21, J6.21, J9.21, J12.21, J15.21, J18.21, J21.21, J24.21
D7: J3.19, J6.19, J9.19, J12.19, J15.19, J18.19, J21.19, J24.19
D8: J3.17, J6.17, J9.17, J12.17, J15.17, J18.17, J21.17, J24.17
D9: J3.15, J6.15, J9.15, J12.15, J15.15, J18.15, J21.15, J24.15
D10: J3.13, J6.13, J9.13, J12.13, J15.13, J18.13, J21.13, J24.13
D11: J3.11, J6.11, J9.11, J12.11, J15.11, J18.11, J21.11, J24.11
D12: J3.9, J6.9, J9.9, J12.9, J15.9, J18.9, J21.9, J24.9
D13: J3.7, J6.7, J9.7, J12.7, J15.7, J18.7, J21.7, J24.7
D14: J3.5, J6.5, J9.5, J12.5, J15.5, J18.5, J21.5, J24.5
D15: J3.3, J6.3, J9.3, J12.3, J15.3, J18.3, J21.3, J24.3
D16: J3.34, J6.34, J9.34, J12.34, J15.34, J18.34, J21.34, J24.34
D17: J3.32, J6.32, J9.32, J12.32, J15.32, J18.32, J21.32, J24.32
D18: J3.30, J6.30, J9.30, J12.30, J15.30, J18.30, J21.30, J24.30
D19: J3.28, J6.28, J9.28, J12.28, J15.28, J18.28, J21.28, J24.28
D20: J3.26, J6.26, J9.26, J12.26, J15.26, J18.26, J21.26, J24.26
D21: J3.24, J6.24, J9.24, J12.24, J15.24, J18.24, J21.24, J24.24
D22: J3.22, J6.22, J9.22, J12.22, J15.22, J18.22, J21.22, J24.22
D23: J3.20, J6.20, J9.20, J12.20, J15.20, J18.20, J21.20, J24.20
D24: J3.18, J6.18, J9.18, J12.18, J15.18, J18.18, J21.18, J24.18
D25: J3.16, J6.16, J9.16, J12.16, J15.16, J18.16, J21.16, J24.16
D26: J3.14, J6.14, J9.14, J12.14, J15.14, J18.14, J21.14, J24.14
D27: J3.12, J6.12, J9.12, J12.12, J15.12, J18.12, J21.12, J24.12
D28: J3.10, J6.10, J9.10, J12.10, J15.10, J18.10, J21.10, J24.10
D29: J3.8, J6.8, J9.8, J12.8, J15.8, J18.8, J21.8, J24.8
D30: J3.6, J6.6, J9.6, J12.6, J15.6, J18.6, J21.6, J24.6
D31: J3.4, J6.4, J9.4, J12.4, J15.4, J18.4, J21.4, J24.4
E: J1.4, J4.4, J7.4, J10.4, J13.4, J16.4, J19.4, J22.4
GND: D5.1 (K), H1.1, H2.1, H3.1, H4.1, J1.49, J1.50, J2.49, J2.50, J3.49, J3.50, J4.49, J4.50, J5.49, J5.50, J6.49, J6.50, J7.49, J7.50, J8.49, J8.50, J9.49, J9.50, J10.49, J10.50, J11.49, J11.50, J12.49, J12.50, J13.49, J13.50, J14.49, J14.50, J15.49, J15.50, J16.49, J16.50, J17.49, J17.50, J18.49, J18.50, J19.49, J19.50, J20.49, J20.50, J21.49, J21.50, J22.49, J22.50, J23.49, J23.50, J24.49, J24.50, T1.2
I2C_RX: J1.47, J4.47, J7.47, J10.47, J13.47, J16.47, J19.47, J22.47
I2C_TX: J1.48, J4.48, J7.48, J10.48, J13.48, J16.48, J19.48, J22.48
IC0: J2.45, J5.45, J8.45, J11.45, J14.45, J17.45, J20.45, J23.45
IC1: J2.43, J5.43, J8.43, J11.43, J14.43, J17.43, J20.43, J23.43
IC2: J2.41, J5.41, J8.41, J11.41, J14.41, J17.41, J20.41, J23.41
IC3: J2.39, J5.39, J8.39, J11.39, J14.39, J17.39, J20.39, J23.39
IPL0: J3.47, J6.47, J9.47, J12.47, J15.47, J18.47, J21.47, J24.47
IPL1: J3.45, J6.45, J9.45, J12.45, J15.45, J18.45, J21.45, J24.45
IPL2: J3.43, J6.43, J9.43, J12.43, J15.43, J18.43, J21.43, J24.43
LDS: J3.38, J6.38, J9.38, J12.38, J15.38, J18.38, J21.38, J24.38
unnamed: D5.2 (A), R6.2
PHI: J1.8, J4.8, J7.8, J10.8, J13.8, J16.8, J19.8, J22.8
S0: J3.44, J6.44, J9.44, J12.44, J15.44, J18.44, J21.44, J24.44
S1: J3.42, J6.42, J9.42, J12.42, J15.42, J18.42, J21.42, J24.42
S2: J3.40, J6.40, J9.40, J12.40, J15.40, J18.40, J21.40, J24.40
ST: J1.6, J4.6, J7.6, J10.6, J13.6, J16.6, J19.6, J22.6
UDS: J3.36, J6.36, J9.36, J12.36, J15.36, J18.36, J21.36, J24.36
USER0: J1.38, J4.38, J7.38, J10.38, J13.38, J16.38, J19.38, J22.38
USER1: J1.36, J4.36, J7.36, J10.36, J13.36, J16.36, J19.36, J22.36
USER2: J1.34, J4.34, J7.34, J10.34, J13.34, J16.34, J19.34, J22.34
USER3: J1.32, J4.32, J7.32, J10.32, J13.32, J16.32, J19.32, J22.32
USER4: J1.30, J4.30, J7.30, J10.30, J13.30, J16.30, J19.30, J22.30
USER5: J1.28, J4.28, J7.28, J10.28, J13.28, J16.28, J19.28, J22.28
USER6: J1.26, J4.26, J7.26, J10.26, J13.26, J16.26, J19.26, J22.26
USER7: J1.24, J4.24, J7.24, J10.24, J13.24, J16.24, J19.24, J22.24
USER8: J1.22, J4.22, J7.22, J10.22, J13.22, J16.22, J19.22, J22.22
USER9: J1.20, J4.20, J7.20, J10.20, J13.20, J16.20, J19.20, J22.20
VCC: J1.1, J1.2, J2.1, J2.2, J3.1, J3.2, J4.1, J4.2, J5.1, J5.2, J6.1, J6.2, J7.1, J7.2, J8.1, J8.2, J9.1, J9.2, J10.1, J10.2, J11.1, J11.2, J12.1, J12.2, J13.1, J13.2, J14.1, J14.2, J15.1, J15.2, J16.1, J16.2, J17.1, J17.2, J18.1, J18.2, J19.1, J19.2, J20.1, J20.2, J21.1, J21.2, J22.1, J22.2, J23.1, J23.2, J24.1, J24.2, R6.1, T1.1
VMA: J3.39, J6.39, J9.39, J12.39, J15.39, J18.39, J21.39, J24.39
VPA: J3.37, J6.37, J9.37, J12.37, J15.37, J18.37, J21.37, J24.37
~BAI-1: J1.40, P1.4
~BAI-2: J4.40, P2.4
~BAI-3: J7.40, P3.4
~BAI-4: J10.40, P4.4
~BAI-5: J13.40, P5.4
~BAI-6: J16.40, P6.4
~BAI-7: J19.40, P7.4
~BAI-8: J22.40
~BAO-1: J1.42
~BAO-2: J4.42, P1.3
~BAO-3: J7.42, P2.3
~BAO-4: J10.42, P3.3
~BAO-5: J13.42, P4.3
~BAO-6: J16.42, P5.3
~BAO-7: J19.42, P6.3
~BAO-8: J22.42, P7.3
~BHE: J3.41, J6.41, J9.41, J12.41, J15.41, J18.41, J21.41, J24.41
~BUSACK: J1.13, J4.13, J7.13, J10.13, J13.13, J16.13, J19.13, J22.13
~BUSRQ: J1.23, J4.23, J7.23, J10.23, J13.23, J16.23, J19.23, J22.23
~DREQ0: J2.46, J5.46, J8.46, J11.46, J14.46, J17.46, J20.46, J23.46
~DREQ1: J2.42, J5.42, J8.42, J11.42, J14.42, J17.42, J20.42, J23.42
~EIRQ0: J1.45, J4.45, J7.45, J10.45, J13.45, J16.45, J19.45, J22.45
~EIRQ1: J1.43, J4.43, J7.43, J10.43, J13.43, J16.43, J19.43, J22.43
~EIRQ2: J1.41, J4.41, J7.41, J10.41, J13.41, J16.41, J19.41, J22.41
~EIRQ3: J1.39, J4.39, J7.39, J10.39, J13.39, J16.39, J19.39, J22.39
~EIRQ4: J1.37, J4.37, J7.37, J10.37, J13.37, J16.37, J19.37, J22.37
~EIRQ5: J1.35, J4.35, J7.35, J10.35, J13.35, J16.35, J19.35, J22.35
~EIRQ6: J1.33, J4.33, J7.33, J10.33, J13.33, J16.33, J19.33, J22.33
~EIRQ7: J1.31, J4.31, J7.31, J10.31, J13.31, J16.31, J19.31, J22.31
~HALT: J1.27, J4.27, J7.27, J10.27, J13.27, J16.27, J19.27, J22.27
~IEI-1: J1.44, P1.2
~IEI-2: J4.44, P2.2
~IEI-3: J7.44, P3.2
~IEI-4: J10.44, P4.2
~IEI-5: J13.44, P5.2
~IEI-6: J16.44, P6.2
~IEI-7: J19.44, P7.2
~IEI-8: J22.44
~IEO-1: J1.46
~IEO-2: J4.46, P1.1
~IEO-3: J7.46, P2.1
~IEO-4: J10.46, P3.1
~IEO-5: J13.46, P4.1
~IEO-6: J16.46, P5.1
~IEO-7: J19.46, P6.1
~IEO-8: J22.46, P7.1
~INT0: J1.17, J4.17, J7.17, J10.17, J13.17, J16.17, J19.17, J22.17
~INT1: J1.12, J4.12, J7.12, J10.12, J13.12, J16.12, J19.12, J22.12
~INT2: J1.10, J4.10, J7.10, J10.10, J13.10, J16.10, J19.10, J22.10
~IORQ: J1.7, J4.7, J7.7, J10.7, J13.7, J16.7, J19.7, J22.7
~M1: J1.11, J4.11, J7.11, J10.11, J13.11, J16.11, J19.11, J22.11
~MREQ: J1.9, J4.9, J7.9, J10.9, J13.9, J16.9, J19.9, J22.9
~NMI: J1.19, J4.19, J7.19, J10.19, J13.19, J16.19, J19.19, J22.19
~RD: J1.3, J4.3, J7.3, J10.3, J13.3, J16.3, J19.3, J22.3
~RESET: J1.21, J4.21, J7.21, J10.21, J13.21, J16.21, J19.21, J22.21
~RFSH: J1.29, J4.29, J7.29, J10.29, J13.29, J16.29, J19.29, J22.29
~TEND0: J2.44, J5.44, J8.44, J11.44, J14.44, J17.44, J20.44, J23.44
~TEND1: J2.40, J5.40, J8.40, J11.40, J14.40, J17.40, J20.40, J23.40
~WAIT: J1.25, J4.25, J7.25, J10.25, J13.25, J16.25, J19.25, J22.25
~WR: J1.5, J4.5, J7.5, J10.5, J13.5, J16.5, J19.5, J22.5

Notes on the sheet:
Zilog Interrupt Priority Bus Jumpers
