lynchaj/duodyne/10 input-output.Voice, V1.0/temp/Z180GDCV2-SND/SND.kicad_sch

## KiCad design 10 input-output.Voice, V1.0/temp/Z180GDCV2-SND/SND.kicad_sch (2023-04-09)

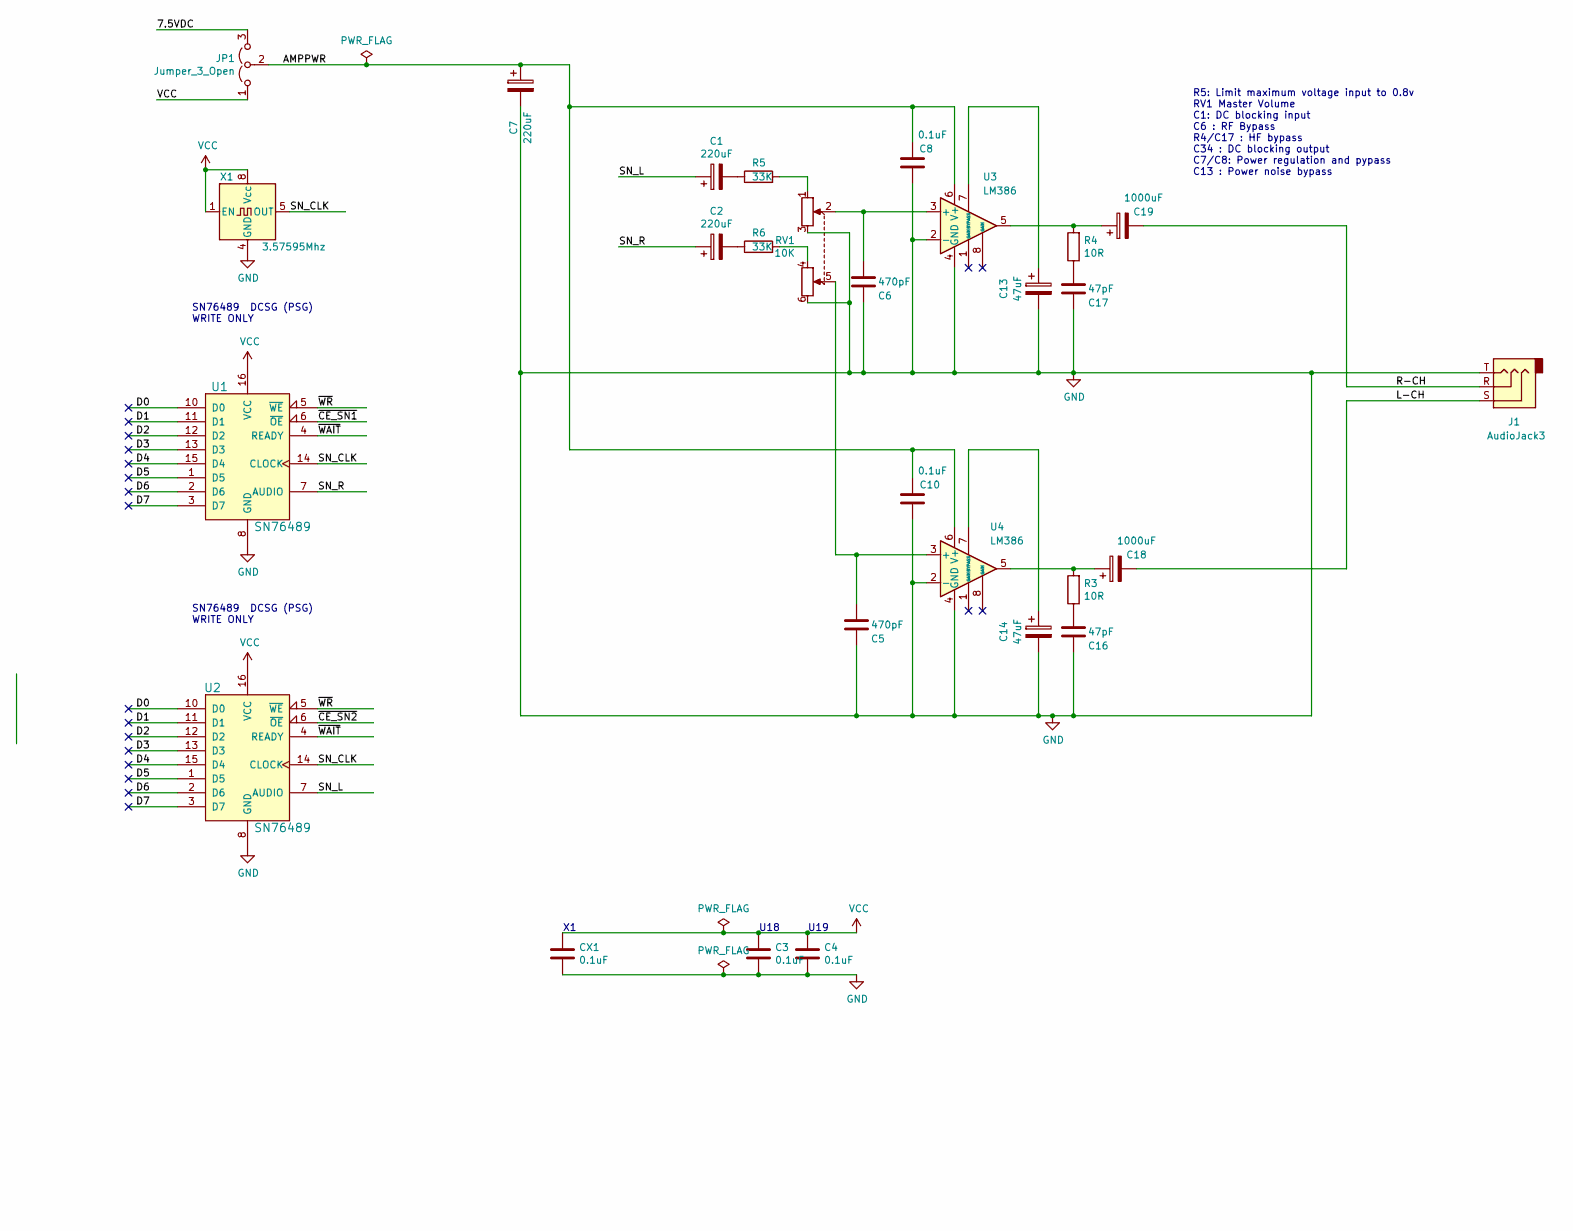
[picture p485: schematic SND.kicad_sch, part in row 1, column 1]

Parts:
C1, C2, C7: 220uF; CP_Radial_D8.0mm_P2.50mm
C3, C4, C8, C10: 0.1uF; C_Disc_D7.0mm_W2.5mm_P5.00mm
C5, C6: 470pF; C_Disc_D3.8mm_W2.6mm_P2.50mm
C13, C14: 47uF; CP_Radial_D5.0mm_P2.50mm
C16, C17: 47pF; C_Disc_D3.8mm_W2.6mm_P2.50mm
C18, C19: 1000uF; CP_Radial_D8.0mm_P2.50mm
CX1: 0.1uF; C_Disc_D7.0mm_W2.5mm_P5.00mm
J1: AudioJack3; StereoJack_3.5mm_Switch_Ledino_KB3SPRS_Horizontal
JP1: Jumper_3_Open; PinHeader_1x03_P2.54mm_Vertical
R3, R4: 10R; R_Axial_DIN0207_L6.3mm_D2.5mm_P10.16mm_Horizontal
R5, R6: 33K; R_Axial_DIN0207_L6.3mm_D2.5mm_P10.16mm_Horizontal
RV1: 10K; Potentiometer_Alps_RK097_Dual_Horizontal
U1, U2: SN76489; DIP-16_W7.62mm
U3, U4: LM386; DIP-8_W7.62mm
X1: 3.57595Mhz; Oscillator_DIP-8

Connections:
7.5VDC: JP1.3 (B)
AMPPWR: C7.1, C8.2, C10.2, JP1.2 (C), U3.6 (V+), U4.6 (V+)
D0: U1.10 (D0), U2.10 (D0)
D1: U1.11 (D1), U2.11 (D1)
D2: U1.12 (D2), U2.12 (D2)
D3: U1.13 (D3), U2.13 (D3)
D4: U1.15 (D4), U2.15 (D4)
D5: U1.1 (D5), U2.1 (D5)
D6: U1.2 (D6), U2.2 (D6)
D7: U1.3 (D7), U2.3 (D7)
GND: C3.2, C4.2, C5.2, C6.2, C7.2, C8.1, C10.1, C13.2, C14.2, C16.2, C17.2, CX1.2, J1.T, RV1.3, RV1.6, U1.8 (GND), U2.8 (GND), U3.2 (-), U3.4 (GND), U4.2 (-), U4.4 (GND), X1.4 (GND)
L-CH: C18.2, J1.S
unnamed: C1.2, R5.1
unnamed: C2.2, R6.1
unnamed: C5.1, RV1.5, U4.3 (+)
unnamed: C6.1, RV1.2, U3.3 (+)
unnamed: C13.1, U3.7 (BYPASS)
unnamed: C14.1, U4.7 (BYPASS)
unnamed: C16.1, R3.1
unnamed: C17.1, R4.1
unnamed: C18.1, R3.2, U4.5
unnamed: C19.1, R4.2, U3.5
unnamed: R5.2, RV1.1
unnamed: R6.2, RV1.4
R-CH: C19.2, J1.R
SN_CLK: U1.14 (CLOCK), U2.14 (CLOCK), X1.5 (OUT)
SN_L: C1.1, U2.7 (AUDIO)
SN_R: C2.1, U1.7 (AUDIO)
VCC: C3.1, C4.1, CX1.1, JP1.1 (A), U1.16 (VCC), U2.16 (VCC), X1.1 (EN), X1.8 (Vcc)
~CE_SN1: U1.6 (~OE)
~CE_SN2: U2.6 (~OE)
~WAIT: U1.4 (READY), U2.4 (READY)
~WR: U1.5 (~WE), U2.5 (~WE)

Notes on the sheet:
U19
SN76489 DCSG (PSG) WRITE ONLY
R5: Limit maximum voltage input to 0.8v RV1 Master Volume C1: DC blocking input C6 : RF Bypass R4/C17 : HF bypass C34 : DC blocking output C7/C8: Power regulation and pypass C13 : Power noise bypass
U18
