lynchaj/duodyne/!Development/19 input-output.SelfHost, V1.1/temp/GAL.kicad_sch

## KiCad design !Development/19 input-output.SelfHost, V1.1/temp/GAL.kicad_sch (2023-04-30)

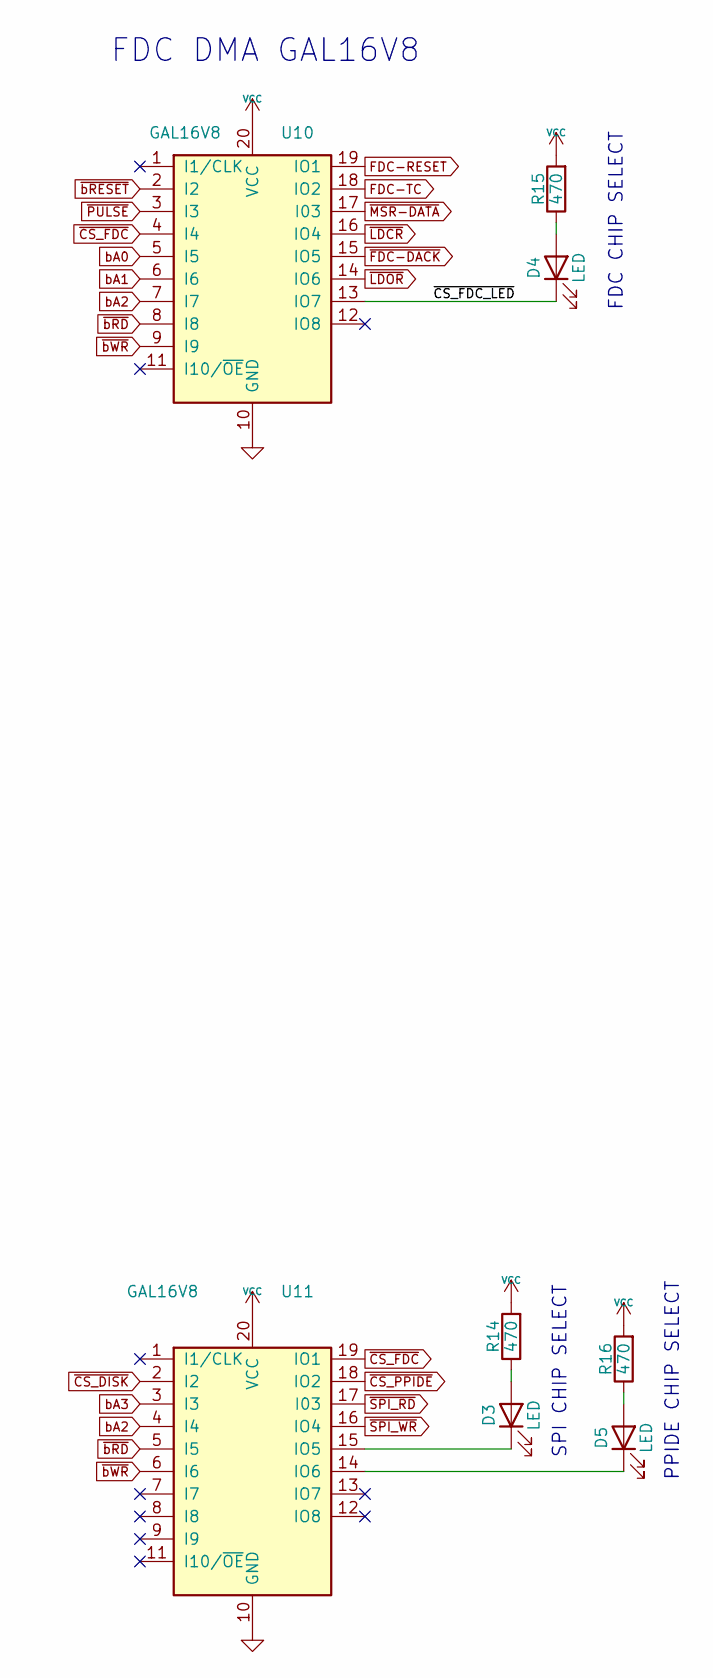
[picture p486: schematic GAL.kicad_sch]

Parts:
D3, D4, D5: LED; LED_D3.0mm_Horizontal_O3.81mm_Z2.0mm
R14, R15, R16: 470; R_Axial_DIN0207_L6.3mm_D2.5mm_P7.62mm_Horizontal
U10, U11: GAL16V8; DIP-20_W7.62mm

Connections:
FDC-RESET: U10.19 (IO1)
FDC-TC: U10.18 (IO2)
GND: U10.10 (GND), U11.10 (GND)
unnamed: D3.1 (K), U11.15 (IO5)
unnamed: D3.2 (A), R14.1
unnamed: D4.2 (A), R15.1
unnamed: D5.1 (K), U11.14 (IO6)
unnamed: D5.2 (A), R16.1
VCC: R14.2, R15.2, R16.2, U10.20 (VCC), U11.20 (VCC)
bA0: U10.5 (I5)
bA1: U10.6 (I6)
bA2: U10.7 (I7), U11.4 (I4)
bA3: U11.3 (I3)
~CS_DISK: U11.2 (I2)
~CS_FDC_LED: D4.1 (K), U10.13 (IO7)
~CS_FDC: U10.4 (I4), U11.19 (IO1)
~CS_PPIDE: U11.18 (IO2)
~FDC-DACK: U10.15 (IO5)
~LDCR: U10.16 (IO4)
~LDOR: U10.14 (IO6)
~MSR-DATA: U10.17 (I03)
~PULSE: U10.3 (I3)
~SPI_RD: U11.17 (I03)
~SPI_WR: U11.16 (IO4)
~bRD: U10.8 (I8), U11.5 (I5)
~bRESET: U10.2 (I2)
~bWR: U10.9 (I9), U11.6 (I6)

Notes on the sheet:
PPIDE CHIP SELECT
FDC DMA GAL16V8
SPI CHIP SELECT
FDC CHIP SELECT
