lynchaj/duodyne/!Development/19 input-output.SelfHost, V1.1/temp/Project1.kicad_sch

## KiCad design !Development/19 input-output.SelfHost, V1.1/temp/Project1.kicad_sch (2023-09-23)

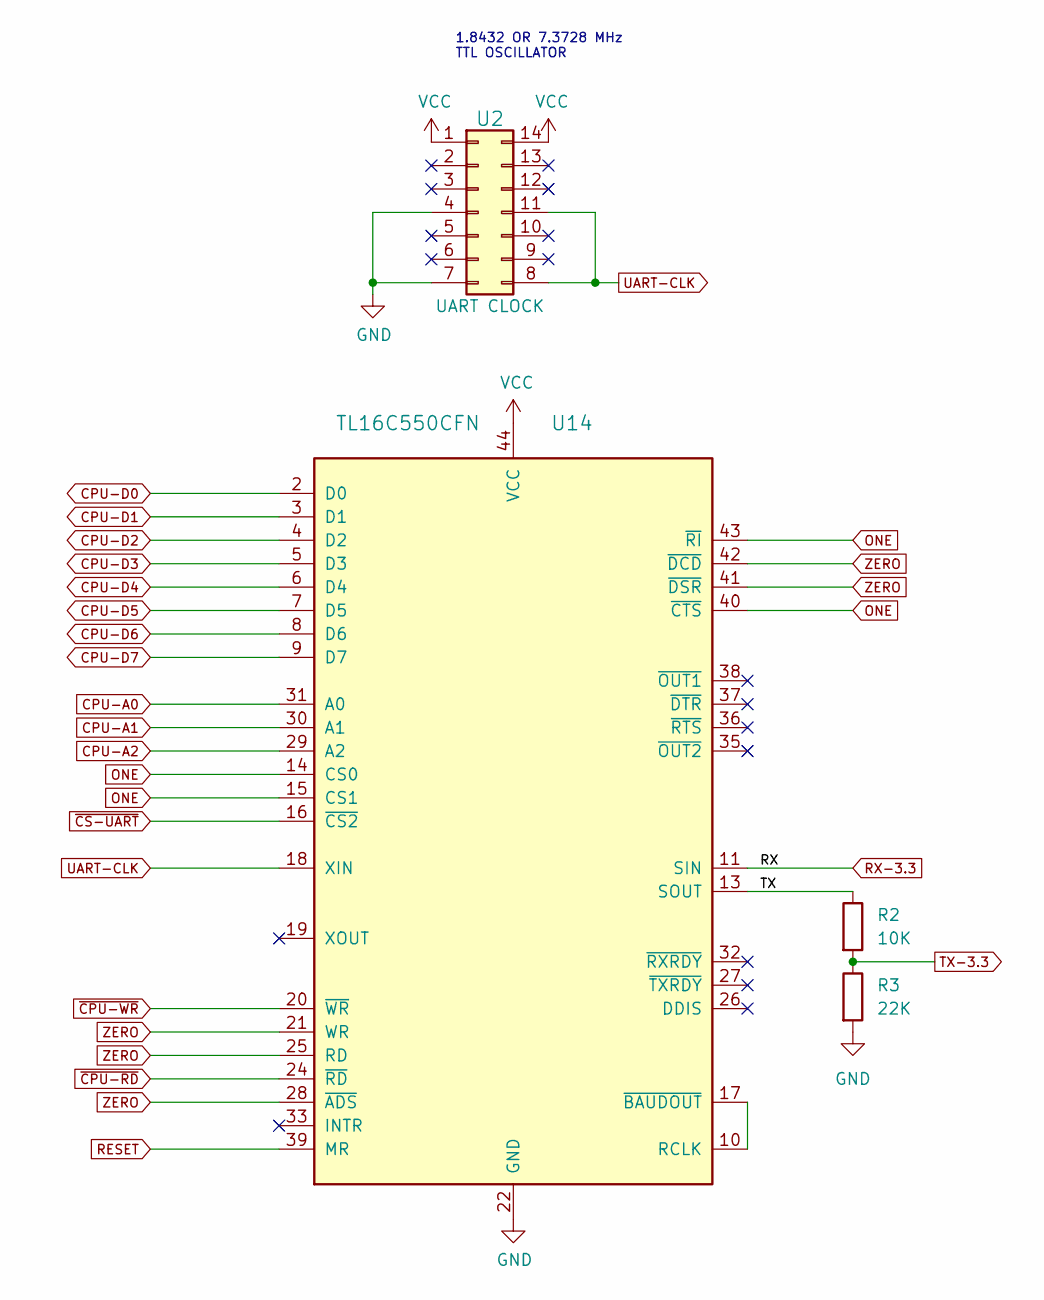
[picture p487: schematic Project1.kicad_sch]

Parts:
R2: 10K
R3: 22K
U2: UART CLOCK; DIP-14_W7.62mm
U14: TL16C550CFN; PLCC-44_THT-Socket

Connections:
CPU-A0: U14.31 (A0)
CPU-A1: U14.30 (A1)
CPU-A2: U14.29 (A2)
CPU-D0: U14.2 (D0)
CPU-D1: U14.3 (D1)
CPU-D2: U14.4 (D2)
CPU-D3: U14.5 (D3)
CPU-D4: U14.6 (D4)
CPU-D5: U14.7 (D5)
CPU-D6: U14.8 (D6)
CPU-D7: U14.9 (D7)
GND: R3.2, U2.4, U2.7, U14.22 (GND)
unnamed: U14.10 (RCLK), U14.17 (~BAUDOUT)
ONE: U14.14 (CS0), U14.15 (CS1), U14.40 (~CTS), U14.43 (~RI)
RESET: U14.39 (MR)
RX-3.3: U14.11 (SIN)
TX: R2.1, U14.13 (SOUT)
TX-3.3: R2.2, R3.1
UART-CLK: U2.8, U2.11, U14.18 (XIN)
VCC: U2.1, U2.14, U14.44 (VCC)
ZERO: U14.21 (WR), U14.25 (RD), U14.28 (~ADS), U14.41 (~DSR), U14.42 (~DCD)
~CPU-RD: U14.24 (~RD)
~CPU-WR: U14.20 (~WR)
~CS-UART: U14.16 (~CS2)

Notes on the sheet:
1.8432 OR 7.3728 MHz TTL OSCILLATOR
