lynchaj/duodyne/!Development/24 DAISY256, V1.0/temp/Talker.sch

## KiCad design !Development/24 DAISY256, V1.0/temp/Talker.sch (2024-04-22)

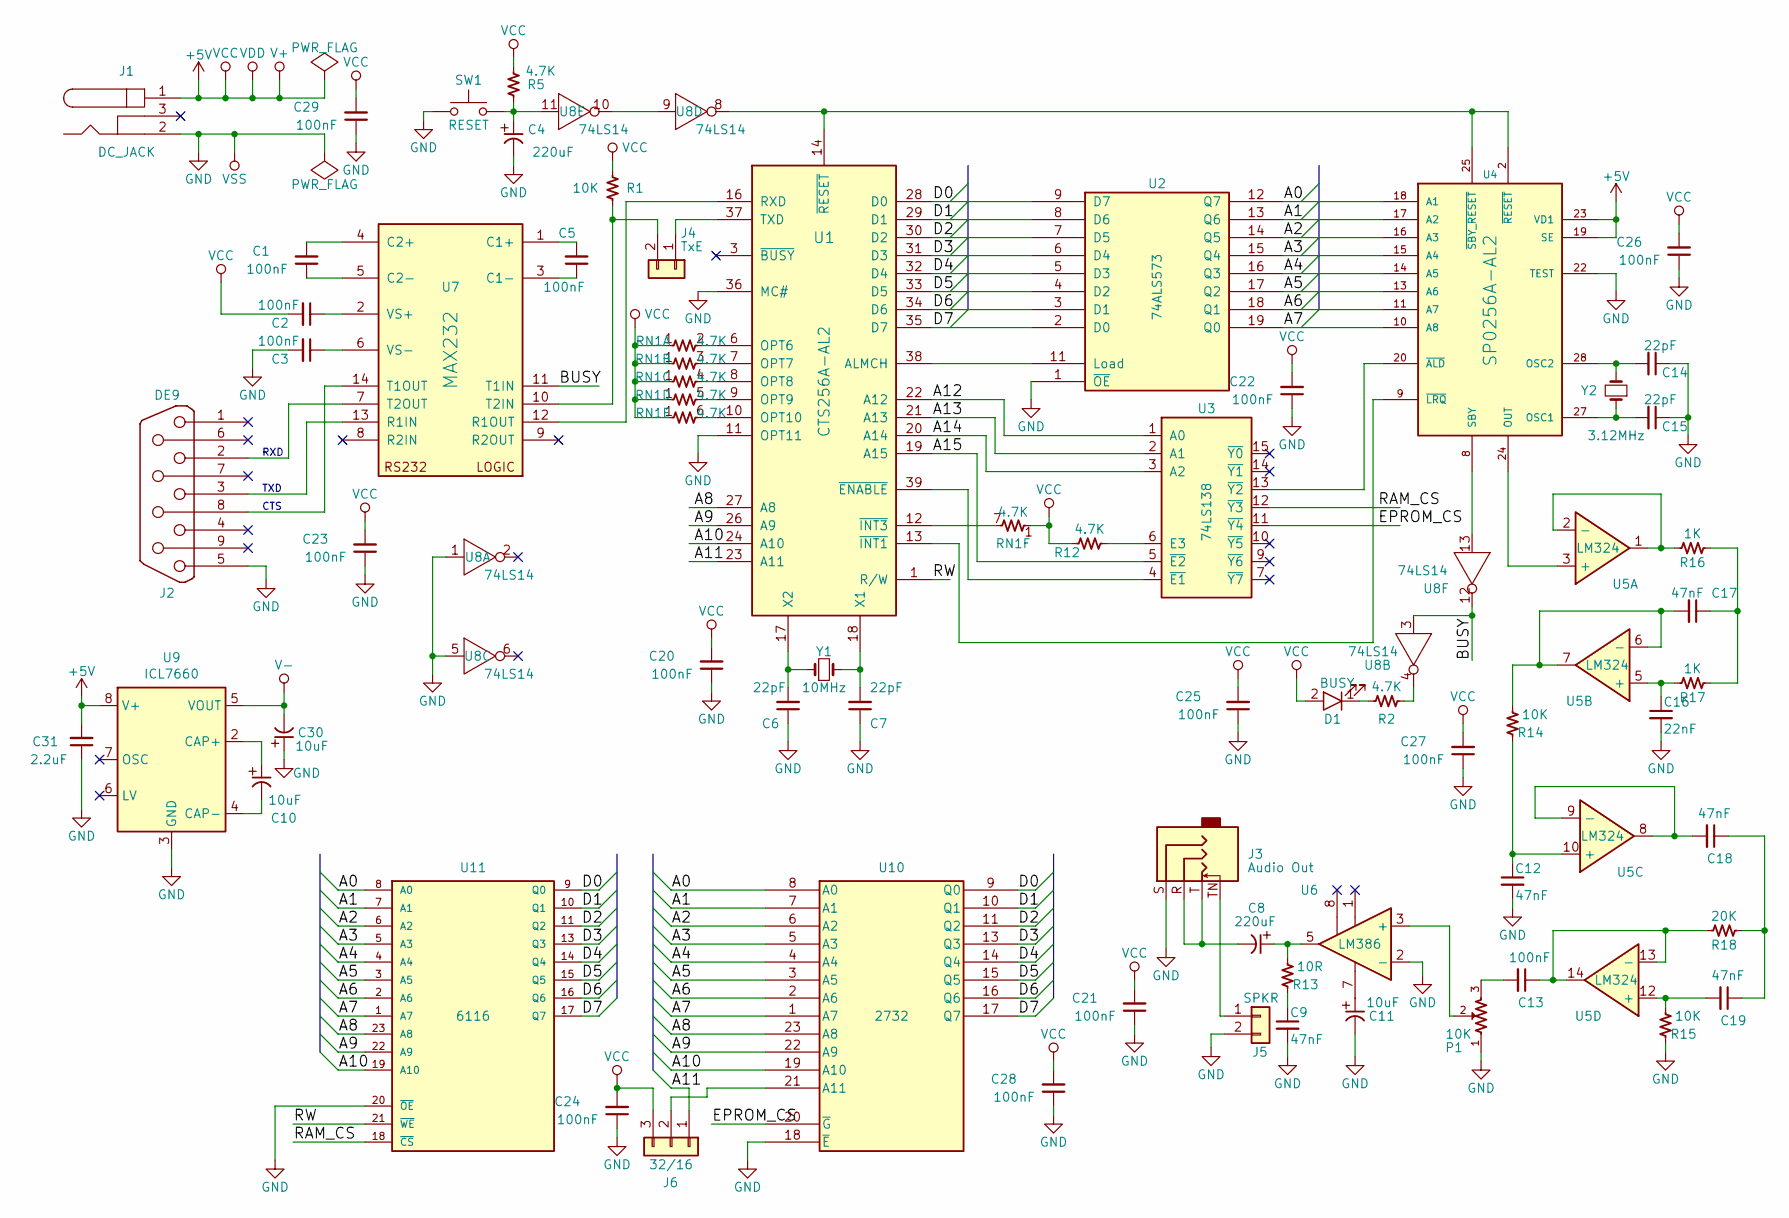
[picture p488: schematic Talker.sch]

Parts:
C1, C2, C3, C5, C13, C20, C21, C22, C23, C24, C25, C26, C27, C28, C29: 100nF; C_Disc_D3_P2.5
C4, C8: 220uF; CP_Radial_D6.3mm_P2.50mm
C6, C7, C14, C15: 22pF; C_Disc_D3_P2.5
C9, C12, C17, C18, C19: 47nF; C_Disc_D3_P2.5
C10, C11, C30: 10uF; CP_Radial_D5.0mm_P2.00mm
C16: 22nF; C_Disc_D3_P2.5
C31: 2.2uF; C_Disc_D3_P2.5
D1: BUSY; LED-3MM
J1: DC_JACK; BarrelJack_Horizontal
J2: DE9; DSUB-9_Female_Horizontal_Assmann_A-DF_09_A-KG-T2S
J3: Audio Out; Jack_3.5mm_CUI_SJ1-3544_Horizontal
J4: TxE; PinHeader_1x02_P2.54mm_Vertical
J5: SPKR; Molex_KK-254_AE-6410-02A_1x02_P2.54mm_Vertical
J6: 32/16; PinHeader_1x03_P2.54mm_Vertical
P1: 10K; Potentiometer_Bourns_PTV111-1_Single_Horizontal
R1, R14, R15: 10K; R3
R2, R5, R12: 4.7K; R3
R13: 10R; R3
R16, R17: 1K; R3
R18: 20K; R3
RN1: 4.7K; R_Array_SIP7
SW1: RESET; SW_PUSH_6mm
U1: CTS256A-AL2; DIP-40_W15.24mm_LongPads
U2: 74ALS573; DIP-20_W7.62mm_LongPads
U3: 74LS138; DIP-16_W7.62mm_LongPads
U4: SP0256A-AL2; DIP-28_W15.24mm_LongPads
U5: LM324; DIP-14_W7.62mm_LongPads
U6: LM386; DIP-8_W7.62mm_LongPads
U7: MAX232; DIP-16_W7.62mm_LongPads
U8: 74LS14; DIP-14_W7.62mm_LongPads
U9: ICL7660; DIP-8_W7.62mm_LongPads
U10: 2732; DIP-24_W15.24mm_LongPads
U11: 6116; DIP-24_W15.24mm_LongPads
Y1: 10MHz; Crystal_HC49-U_Vertical
Y2: 3.12MHz; Crystal_HC49-U_Vertical

Connections:
+5V: C2.2, C20.2, C21.2, C22.2, C23.2, C24.2, C25.2, C26.2, C27.2, C28.2, C29.2, C31.2, D1.2 (A), J1.1, J6.3, R1.1, R5.1, R12.2, RN1.1 (R1.1), U4.19 (SE), U4.23 (VD1), U9.8 (V+)
A0: U2.12 (Q7), U4.18 (A1), U10.8 (A0), U11.8 (A0)
A1: U2.13 (Q6), U4.17 (A2), U10.7 (A1), U11.7 (A1)
A2: U2.14 (Q5), U4.16 (A3), U10.6 (A2), U11.6 (A2)
A3: U2.15 (Q4), U4.15 (A4), U10.5 (A3), U11.5 (A3)
A4: U2.16 (Q3), U4.14 (A5), U10.4 (A4), U11.4 (A4)
A5: U2.17 (Q2), U4.13 (A6), U10.3 (A5), U11.3 (A5)
A6: U2.18 (Q1), U4.11 (A7), U10.2 (A6), U11.2 (A6)
A7: U2.19 (Q0), U4.10 (A8), U10.1 (A7), U11.1 (A7)
A8: U1.27 (A8), U10.23 (A8), U11.23 (A8)
A9: U1.26 (A9), U10.22 (A9), U11.22 (A9)
A10: U1.24 (A10), U10.19 (A10), U11.19 (A10)
A11: J6.1, U1.23 (A11)
A12: U1.22 (A12), U3.1 (A0)
A13: U1.21 (A13), U3.2 (A1)
A14: U1.20 (A14), U3.3 (A2)
A15: U1.19 (A15), U3.5 (~E2)
BUSY: U7.11 (T1IN), U8.3, U8.12
D0: U1.28 (D0), U2.9 (D7), U10.9 (Q0), U11.9 (Q0)
D1: U1.29 (D1), U2.8 (D6), U10.10 (Q1), U11.10 (Q1)
D2: U1.30 (D2), U2.7 (D5), U10.11 (Q2), U11.11 (Q2)
D3: U1.31 (D3), U2.6 (D4), U10.13 (Q3), U11.13 (Q3)
D4: U1.32 (D4), U2.5 (D3), U10.14 (Q4), U11.14 (Q4)
D5: U1.33 (D5), U2.4 (D2), U10.15 (Q5), U11.15 (Q5)
D6: U1.34 (D6), U2.3 (D1), U10.16 (Q6), U11.16 (Q6)
D7: U1.35 (D7), U2.2 (D0), U10.17 (Q7), U11.17 (Q7)
EPROM_CS: U3.11 (~Y4), U10.20 (~G)
GND: C3.2, C4.2, C6.1, C7.1, C9.2, C11.2, C12.2, C14.1, C15.1, C16.2, C20.1, C21.1, C22.1, C23.1, C24.1, C25.1, C26.1, C27.1, C28.1, C29.1, C30.1, C31.1, J1.2, J2.5, J3.S, J5.2, P1.1, R15.2, SW1.1, U1.11 (OPT11), U1.36 (MC#), U2.1 (~OE), U4.22 (TEST), U6.2 (-), U8.1, U8.5, U9.3 (GND), U10.18 (~E), U11.20 (~OE)
unnamed: C1.1, U7.5 (C2-)
unnamed: C1.2, U7.4 (C2+)
unnamed: C2.1, U7.2 (VS+)
unnamed: C3.1, U7.6 (VS-)
unnamed: C4.1, R5.2, SW1.2, U8.11
unnamed: C5.1, U7.3 (C1-)
unnamed: C5.2, U7.1 (C1+)
unnamed: C6.2, U1.17 (X2), Y1.1
unnamed: C7.2, U1.18 (X1), Y1.2
unnamed: C8.1, R13.1, U6.5
unnamed: C8.2, J3.R, J3.T
unnamed: C9.1, R13.2
unnamed: C10.1, U9.2 (CAP+)
unnamed: C10.2, U9.4 (CAP-)
unnamed: C11.1, U6.7
unnamed: C12.1, R14.2, U5.10 (+)
unnamed: C13.1, R18.2, U5.13 (-), U5.14
unnamed: C13.2, P1.3
unnamed: C14.2, U4.28 (OSC2), Y2.2
unnamed: C15.2, U4.27 (OSC1), Y2.1
unnamed: C16.1, R17.2, U5.5 (+)
unnamed: C17.1, R16.1, R17.1
unnamed: C17.2, R14.1, U5.6 (-), U5.7
unnamed: C18.1, C19.1, R18.1
unnamed: C18.2, U5.8, U5.9 (-)
unnamed: C19.2, R15.1, U5.12 (+)
unnamed: D1.1 (K), R2.2
unnamed: J2.2, U7.7 (T2OUT)
unnamed: J2.3, U7.13 (R1IN)
unnamed: J2.8, U7.14 (T1OUT)
unnamed: J3.TN, J5.1
unnamed: J4.1, U1.37 (TXD)
unnamed: J4.2, R1.2, U7.10 (T2IN)
unnamed: J6.2, U10.21 (A11)
unnamed: P1.2, U6.3 (+)
unnamed: R2.1, U8.4
unnamed: R12.1, U3.6 (E3)
unnamed: R16.2, U5.1, U5.2 (-)
unnamed: RN1.2 (R1.2), U1.6 (OPT6)
unnamed: RN1.3 (R1.2), U1.7 (OPT7)
unnamed: RN1.4 (R1.2), U1.8 (OPT8)
unnamed: RN1.5 (R1.2), U1.9 (OPT9)
unnamed: RN1.6 (R1.2), U1.10 (OPT10)
unnamed: RN1.7 (R1.2), U1.12 (~INT3)
unnamed: U1.13 (~INT1), U4.9 (~LRQ)
unnamed: U1.14 (~RESET), U4.2 (~RESET), U4.25 (~SBY_RESET), U8.8
unnamed: U1.16 (RXD), U7.12 (R1OUT)
unnamed: U1.38 (ALMCH), U2.11 (Load)
unnamed: U1.39 (~ENABLE), U3.4 (~E1)
unnamed: U3.13 (~Y2), U4.20 (~ALD)
unnamed: U4.8 (SBY), U8.13
unnamed: U4.24 (OUT), U5.3 (+)
unnamed: U8.9, U8.10
RAM_CS: U3.12 (~Y3), U11.18 (~CS)
RW: U1.1 (R/W), U11.21 (~WE)
V-: C30.2, U9.5 (VOUT)

Notes on the sheet:
RXD
TXD
CTS
