lynchaj/duodyne/17 input-output.DualESP32, V1.0/ESP1Firmware/src/pins.h

#pragma Once

#define RD 22
#define WR 23
#define OUTCLK 21
#define INCLK 19
#define OUTDATA 16
#define INDATA 17
#define BUSY 18
#define READY 5
#define RXPIN 3
#define TXPIN 1


#define MOUSEDATA  GPIO_NUM_32
#define MOUSECLOCK  GPIO_NUM_33
