lynchaj/duodyne/25 processor.80c188/firmware/BIOS/fpem/em187e.asm

; em187e.asm


;;;;;;;;;;;;;;;;;;;;;;;;;;;;;;;;;;;;;;;;;;;;;;;;;;;;;;;;;;;;;;;;;
;
; load IEEE 8-byte real to accumulator
;       es:di   points to value to load
;       si      points to accumulator to receive value
; uses: ax & dx
;;;;;;;;;;;;;;;;;;;;;;;;;;;;;;;;;;;;;;;;;;;;;;;;;;;;;;;;;;;;;;;;;
load_R64:	;	    proc    near
  es    mov     dx, word [di+6]     ;get exponent
        xor     ax,ax
        shl     dx,1            ; sign goes to carry
        rcl     al,1            ; sign goes to AL
        mov     byte [si+sign], al
        shr     dx,5            ;dx is biased exponent
        or      dx,dx           ; test for zero
        jz      lr6401
        cmp     dx,2047         ; test for max exponent
        je      lr6411
        mov     byte [si+tag], tag_valid

        sub     dx,1023         ; get correct exponent
        mov     word [si+expon],dx   ;set the exponent
  es    mov     dl,[di+6]    ;get hi-part of mantissa
  es    mov     ax,[di+4]    ;get second 16 bits
  es    mov     bx,[di+2]    ;get third 16 bits
%if BIG
  es    mov     di,[di]      ;get lowest order 16 bits
        xor     bp,bp           ;zap lo-bit receiver
%endif
        mov     cx,4            ;count 4 shifts
lr6493:
        shr     dx,1            ;shift into carry
        rcr     ax,1            ;shift into ax
        rcr     bx,1            ;shift into bx
%if BIG
        rcr     di,1            ;shift into di
        rcr     bp,1            ;shift into bp
%endif
        loop    lr6493
; have mantissa in AX:BX[:DI:BP]
        stc
        rcr     ax,1            ;shift into ax
        rcr     bx,1            ;shift into bx
%if BIG
        rcr     di,1            ;shift into di
        rcr     bp,1            ;shift into bp
        mov     [si+mantis+6],bp
lr6495:
        mov     [si+mantis+4],di
        mov     [si+mantis+2],bx    ; **
        mov     [si+mantis],ax  ;set the internal form
%else
lr6495:
        mov     [si+mantis+2],bx    ; **
        mov     [si+mantis],ax  ;set the internal form
%endif

lr6499:
        ret


; biased exponent was 0
lr6401:
  es    mov     al,[di+6]            ;get highest mantissa
  es    or      ax,[di+4]
  es    or      ax,[di+2]            ;test for real zero
  es    or      ax,[di]
        jnz     lr6402           ; not a real zero
; got real zero
        mov     byte [si+tag], tag_zero
        mov     word [si+expon], exp_of_FPzero
lr64015:
        mov     [si+mantis], ax
        mov     [si+mantis+2], ax
%if  BIG
        mov     [si+mantis+4], ax
        mov     [si+mantis+6], ax
%endif
        jmp     lr6499

; biased exponent was 2047 -- possible infinity
lr6411:
        xor     ax,ax
  es    mov     dl, [di+7]
        and     dx,000Fh            ;check for zero mantissa
  es    or      dx,[di+4]
  es    or      dx,[di+2]
  es    or      dx,[di]
        jnz     lr6415              ; if not zero in packed form, NaN
        mov     byte [si+tag], tag_infin
lr6413:
        mov     word [si+expon], exp_of_FPinf
        jmp     lr64015

lr6415:
        push    Iexcept             ;Invalid operation
        call    exception           ;   exception
        mov     byte [si+tag], tag_invalid
        jmp     lr6413


; not a real zero -- actually a denormal
lr6402:
        push    Dexcept             ;Denormalized operand
        call    exception           ;  exception

  es    mov     ax,[di+5]            ;AH gets 4 highest bits of mantissa
  es    mov     bx,[di+3]
  es    mov     dh,[di]
  es    mov     di,[di+1]            ;destroy ES:DI as pointer
        mov     cx,4                ;shift by 4, trying to normalize
lr6405:
%if BIG
        shl     dh,1
        rcl     di,1
%else
        shl     di,1
%endif
        rcl     bx,1
        rcl     ax,1
        loop    lr6405              ;now it may be normalized
; dl is zero at this point, shift until fraction is normalized
lr6406:
        test    ah,80h              ;test the hi-bit
        jnz     lr6407              ;jump when normalized
%if BIG
        shl     dh,1
        rcl     di,1
%else
        shl     di,1
%endif
        rcl     bx,1
        rcl     ax,1
        inc     dl                  ;count the shifts needed
        jmp     lr6406              ;loop back
lr6407:
%if BIG
        mov     bp,dx               ;save away dx
%endif
        xor     dh,dh               ;clear hi part of dh
        add     dx,1023             ;bias the exponent
        neg     dx                  ;really is negative
        mov     word [si+expon],dx       ;set exponent
%if BIG
        mov     [si+mantis+6],bp    ;set highest part of mantissa
%endif
        jmp     lr6495
;load_R64    endp

;;;;;;;;;;;;;;;;;;;;;;;;;;;;;;;;;;;;;;;;;;;
;
;   Store 64-bit real at ES:DI
;   SI points at accumulator to store
;
;;;;;;;;;;;;;;;;;;;;;;;;;;;;;;;;;;;;;;;;;;;
store_R64:	;	   proc    near
        cmp     byte [si+tag], tag_zero
        jae     sr64100                 ;go check on funny tag
        mov     bp,word [si+expon]           ;get exponent

        mov     ax,[si+mantis]
        mov     bx,[si+mantis+2]        ;get entire mantissa
        mov     dl,byte [si+sign]            ;sign to DL
%if BIG
        mov     dh,byte [si+mantis+7]
        mov     si,[si+mantis+4]        ;mantissa in AX:BX[:SI:DX]
        add     dh,04h                  ;round mantissa
        adc     si,0
        adc     bx,0
        adc     ax,0
        jc      sr64030
%else
        xor     dh,dh
        xor     si,si                   ;zero this word 
%endif

; discard the hidden bit
%if BIG
        shl     dh,1
        rcl     si,1
        rcl     bx,1
%else
        shl     bx,1
%endif
        rcl     ax,1
        clc
sr64030:
        adc     bp,0                    ;possible increment of exponent

        sub     bp,-1023                ;bias the exponent
        jle     sr64190                 ;return zero on underflow
        cmp     bp,2047                 ;test for maximum exponent
        jae     sr64210                 ;return infinity if overflow

;now move 4 bits into the result
        mov     cx,4
sr64060:
%if BIG
        shl     dh,1
        rcl     si,1
        rcl     bx,1
%else
        shl     bx,1
%endif
        rcl     ax,1
        rcl     bp,1
        loop    sr64060

        xor     dh,dh                   ;clear part of fraction
        ror     dx,1                    ;sign bit to hi position in DX
        or      dx,bp                   ;form final hi-word
  es    mov     [di],si              ;store low order
  es    mov     [di+2],bx
  es    mov     [di+4],ax
  es    mov     [di+6],dx            ;store sign & exponent
sr64099:
        ret


; skip to here on not (tag_valid)
sr64100:
        ja      sr64200                 ;further tag checking is needed

; store a real zero, signed if you please
sr64110:
        xor     ax,ax                   ;get a zero
sr64120:
        mov     bl,byte [si+sign]            ;get sign
        shr     bl,1                    ;sign to carry
        rcr     ax,1                    ;sign to hi-bit of word
sr64150:
  es    mov     [di+6],ax            ;store hi-word
        xor     bx,bx                   ;zap again for good measure
  es    mov     [di+4],bx            ;store second word
  es    mov     [di+2],bx
  es    mov     [di],bx
        jmp     sr64099                 ;go exit from one point

; store plus zero
sr64190:
        push    Uexcept                 ;underflow
        call    exception

        xor     ax,ax                   ;get +0.0
        jmp     sr64150

; tag is neither (tag_valid) nor (tag_zero)
sr64200:
        cmp     byte [si+tag], tag_infin     ;test for infinity
        je      sr64220
        jmp     short sr64250           ;return indefinite
; return signed infinity
sr64210:
        push    Oexcept                 ;overflow 
        call    exception
sr64220:
        mov     ax,7FF0h << 1          ;following code will put in sign
        jmp     sr64120
; return signed indefinite
sr64250:
        push    Iexcept                 ;invalid operation
        call    exception

        mov     ax,0FFF8h               ;following code will store value
        jmp     sr64150

;store_R64   endp

;;;;;;;;;;;;;;;;;;;;;;;;;;;;;;;;;;;;;;;;;;;
;
;   Store 16-bit integer at ES:DI
;   SI points at accumulator to store
;
;;;;;;;;;;;;;;;;;;;;;;;;;;;;;;;;;;;;;;;;;;;
store_I16:	;	   proc    near
        cmp     byte [si+tag], tag_zero
        jae     s16100              ;go do further checking
        mov     ax,word [si+expon]       ;get exponent
        cmp     ax,15
        jge     s16150              ;go store indefinite
        mov     cx,63               ;get shift count
        sub     cx,ax               ; shift to lowest order
        mov     bx,si               ;get argument
        call    vloadsh64           ;get AX:BX:CX:DX
        call    round_mag           ;
        cmp     byte [si+sign],0         ;check for plus
        je      s16050              ; **
        neg     dx                  ;negate result
s16050:
  es    mov     [di],dx          ;store low order
        ret

; tag is not (tag_valid), check for other tags
s16100:
        je      s16120              ;tag zero
        push    Iexcept             ;
        jmp     short s16160        ;invalid, empty, or indefinite
; tag is (tag_zero)
s16120:
        xor     dx,dx               ; **
        jmp     s16050              ;store and exit

; exponent is too big
s16150:
        push    Oexcept             ;overflow
s16160:
        call    exception
        mov     dx,08000h           ;indefinite result
        jmp     s16050

;store_I16   endp

;;;;;;;;;;;;;;;;;;;;;;;;;;;;;;;;;;;;;;;;;;;
;
;   Store 32-bit integer at ES:DI
;   SI points at accumulator to store
;
;;;;;;;;;;;;;;;;;;;;;;;;;;;;;;;;;;;;;;;;;;;
store_I32:	;	   proc    near
        cmp     byte [si+tag], tag_zero
        jae     s32100              ;go do further checking
        mov     ax,word [si+expon]       ;get exponent
        cmp     ax,31
        jge     s32150              ;go store indefinite
        mov     cx,63               ;get shift count
        sub     cx,ax               ; shift to lowest order
        mov     bx,si               ;get argument
        call    vloadsh64           ;get AX:BX:CX:DX
        call    round_mag           ;

        cmp     byte [si+sign],0         ;check for plus
        je      s32050              ; **
        not     cx                  ;is negative, negate the result
        neg     dx
        cmc
        adc     cx,0
s32050:
  es    mov     [di],dx          ;store low order
  es    mov     [di+2],cx        ;store high order
        ret
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
